x92120/x260911-002-KalasinEngineering/02_Electrical_and_eDrawing/05_Instrument_Manuals/CS-DS-01 pH Analyzer/Installation.jpg

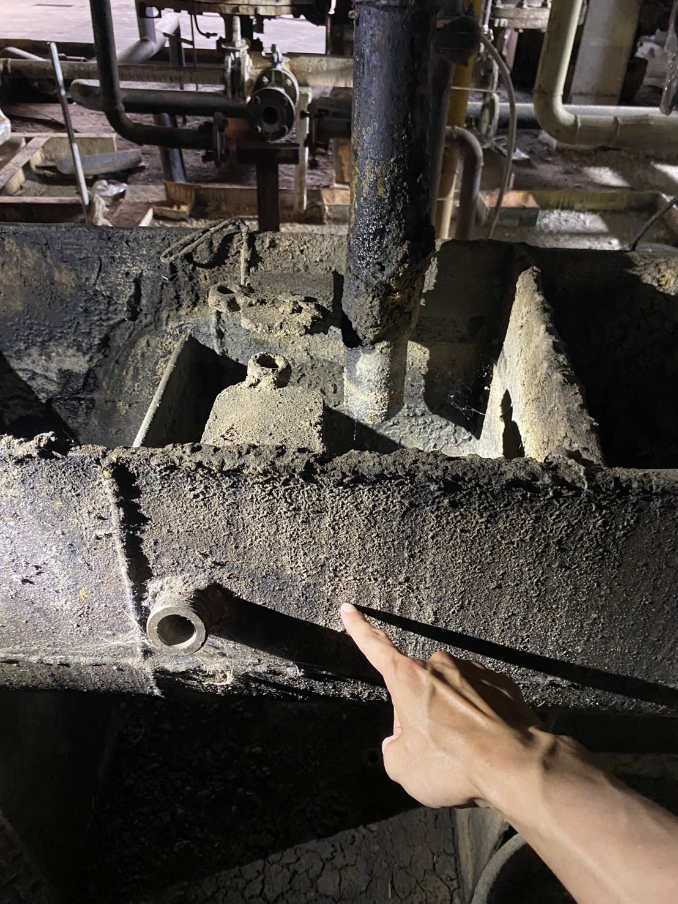
02_Electrical_and_eDrawing/05_Instrument_Manuals/CS-DS-01 pH Analyzer/Installation.jpg
