x92120/x260911-002-KalasinEngineering/02_Electrical_and_eDrawing/01_Source_Drawings_DWG/README.md

# 01_Source_Drawings_DWG — Original Vendor AutoCAD DWG Drawings

This directory contains the original vendor AutoCAD `.dwg` schematics, panel layouts, and wiring diagrams for the **Ingredion Kalasin Spray Dryer Plant** (Ref: `R5THS00138`).

---

## 📐 Source DWG File Inventory

| Filename | Description | Format |
| :--- | :--- | :---: |
| **`R5THS00138-000-SCD-10001_0.dwg`** | Master Control System Schematic Diagram | AutoCAD DWG |
| **`R5THS00138-FBR-LAY-20001_1.dwg`** | Silo Panel General Layout & Bill of Materials (BOM Rev 0) | AutoCAD DWG |
| **`R5THS00138-FBR-WIR-20001_3.dwg`** | Silo Panel Electrical Wiring Layout Diagram | AutoCAD DWG |
| **`R5THS00138-FBR-WIR-20001_3_recover.dwg`** | Recovered Backup Copy of Electrical Wiring Layout | AutoCAD DWG |

---

## 📌 Usage & Engineering Context

These drawings serve as the baseline source drawings provided by the vendor. They were used to extract wire numbers, device tags, terminal assignments, and panel layouts that feed into the automated DXF generation tools located in `04_Automation_Scripts`.
