x92120/x260911-002-KalasinEngineering/02_Electrical_and_eDrawing/03_CAD_Exports_DXF_SVG/README.md

# 03_CAD_Exports_DXF_SVG — Categorized DXF & SVG Drawing Deliverables

This directory contains categorized, production-grade AutoCAD DXF and SVG engineering drawing deliverables for the **Ingredion Kalasin Spray Dryer Plant**.

---

## 📁 Directory Layout & Sub-Module README Links

```text
03_CAD_Exports_DXF_SVG/
├── DI_Slot_Drawings/                     # 15 Digital Input (1756-IB32) Wiring Diagrams (One Slot per DXF)
│   └── README.md
├── DO_Slot_Drawings/                     # 9 Digital Output (1756-OB32 with SPDT Relay) Wiring Diagrams
│   └── README.md
├── IS_Barriers_CAD/                      # Pepperl+Fuchs Intrinsically Safe (IS) Barrier Schematics (DXF)
│   └── README.md
├── 01_PLC_IO_Wiring_DXF/                 # 40 Modular PLC I/O Schematics (KAL-JC-WIR-*)
├── 02_Instrument_Typical_DXF/            # 26 Instrument Hookup & Installation Typicals (KAL-JC-TYP-*)
├── 03_MCC_Panel_Layout/                  # 14 MCC Motor Control Center Panel Layouts (DXF + SVG)
├── 04_System_Architecture_CAD/           # 4 System & Network Architecture CAD Schematics
└── 05_SVG_Vector_Sheets/                 # 73 High-Fidelity SVG Presentation & Web Review Sheets
```

---

## 📊 Summary Breakdown

| Subfolder | Count | Format | Primary Content |
| :--- | :---: | :---: | :--- |
| **[DI_Slot_Drawings/](file:///e:/xApp-01/x260911-002-KalasinEngineering/02_Electrical_and_eDrawing/03_CAD_Exports_DXF_SVG/DI_Slot_Drawings/README.md)** | 15 | `.dxf` | Digital Input (1756-IB32) single-slot wiring schematics |
| **[DO_Slot_Drawings/](file:///e:/xApp-01/x260911-002-KalasinEngineering/02_Electrical_and_eDrawing/03_CAD_Exports_DXF_SVG/DO_Slot_Drawings/README.md)** | 9 | `.dxf` | Digital Output (1756-OB32 + Relay) single-slot wiring schematics |
| **[IS_Barriers_CAD/](file:///e:/xApp-01/x260911-002-KalasinEngineering/02_Electrical_and_eDrawing/03_CAD_Exports_DXF_SVG/IS_Barriers_CAD/README.md)** | 3 | `.dxf` | Pepperl+Fuchs K-System IS Barrier wiring diagrams |
| **01_PLC_IO_Wiring_DXF/** | 40 | `.dxf` | Full ControlLogix 1756 I/O wiring sheets (`KAL-JC-WIR-*`) |
| **02_Instrument_Typical_DXF/** | 26 | `.dxf` | Field instrument installation hookup drawings (`KAL-JC-TYP-*`) |
| **03_MCC_Panel_Layout/** | 14 | `.dxf`, `.svg` | Front elevation, internal GA, and panel layout sheets M1–M4 |
| **04_System_Architecture_CAD/** | 4 | `.dxf`, `.svg`, `.pdf` | Chassis C1–C8 slot-to-JB destination architecture |
| **05_SVG_Vector_Sheets/** | 73 | `.svg` | High-fidelity vector graphical presentation sheets |
