x92120/x260911-002-KalasinEngineering/03_IO_Lists_and_Schedules/IO_List-Bak/README.md

# IO_List-Bak — Historical Revisions & Master Excel Archives

This directory serves as the engineering archive for master Excel workbooks, tag revision history, change comparison audits, and printable PDF schedules for the **Ingredion Kalasin Spray Dryer Plant**.

---

## 📁 Key Deliverables & Historical Archives

### Master Reports & Workbooks
* **`Destination_IO_List_Master_Report.pdf`**: 82-Page master destination schedule (Print-ready PDF).
* **`Destination_IO_List_Master_Report.xlsx`**: Master 17-tab destination workbook.
* **`Chassis_and_Slot_IO_Source_Destination_Report.pdf`**: 99-Page master chassis & slot vector schedule.
* **`Chassis_IO_List_Per_Slot_Report.xlsx`**: Master 48-tab per-slot workbook.
* **`Instrument_IO_Mapping_with_Models_and_Cables.xlsx`**: Master instrument-to-cable schedule.
* **`IO_List_Sorted_by_Chassis_Slot.xlsx`**: Master hardware allocation sorted by chassis/slot.

### Revision Audits & Checklists
* **`IO_Comparison_Report_Tag35_vs_Dev36.xlsx`**: Tag audit and change verification report comparing Tag35 vs Dev36 releases.
* **`IO Check List.xlsx`** & **`IO Check List-1.xlsx`**: Quality assurance check sheets.
* **`Tags list PLC.xlsx`** & **`Tags list PLC-r02.xlsx`**: ControlLogix PLC tag databases.
* **`IO_List_xDev-R01-Tag35-1.xlsx` .. `Tag35-7.xlsx`**: Historical revision snapshots 1 through 7.
