x92120/x260911-002-KalasinEngineering/Datasheet/PF/README.md

# Datasheet/PF — Pepperl+Fuchs IS Barrier Technical Datasheets & DXF Page Exports

This folder contains official Pepperl+Fuchs K-System Intrinsically Safe (IS) Barrier technical datasheets in PDF format, alongside page-by-page converted AutoCAD `.dxf` CAD drawings.

---

## 📁 Document & DXF Register

| P+F Part No. | Model / Device Name | PDF Datasheet | Converted Master DXF | Converted DXF Page Files |
| :---: | :--- | :--- | :--- | :--- |
| **216711** | **HiC2821** Switch Amplifier (DI) | `216711_eng.pdf` | `PF_216711_HiC2821_DI_Master_All_Pages.dxf` | `PF_216711_HiC2821_DI_Page_01..05.dxf` |
| **233883** | **HiC2871** Solenoid Driver (DO) | `233883_eng.pdf` | `PF_233883_HiC2871_DO_Master_All_Pages.dxf` | `PF_233883_HiC2871_DO_Page_01..04.dxf` |
| **260436** | **HiCTB16** 16-Slot Motherboard | `260436_eng.pdf` | `PF_260436_HiCTB16_Master_All_Pages.dxf` | `PF_260436_HiCTB16_Page_01..05.dxf` |
| **321423** | **HiC2025** SMART Tx Supply (AI) | `321423_eng.pdf` | `PF_321423_HiC2025_AI_Master_All_Pages.dxf` | `PF_321423_HiC2025_AI_Page_01..05.dxf` |

---

## ⚙️ Conversion Utility

These DXF page drawings were rendered automatically from PDF datasheets using `04_Automation_Scripts/convert_pf_datasheet_to_dxf.py`.
