x92120/x260911-002-KalasinEngineering/02_Electrical_and_eDrawing/03_CAD_Exports_DXF_SVG/DI_Slot_Drawings/README.md

# DI_Slot_Drawings — Digital Input Slot CAD Drawings

This folder contains 15 individual AutoCAD `.dxf` wiring diagrams for ControlLogix 1756-IB32 32-Point 24VDC Digital Input modules.

---

## 📁 Drawing Inventory (15 DXF Files)

* `C1S4_DI_Wiring_Diagram.dxf` — Chassis 1, Slot 4 (1756-IB32)
* `C1S5_DI_Wiring_Diagram.dxf` — Chassis 1, Slot 5 (1756-IB32)
* `C1S6_DI_Wiring_Diagram.dxf` — Chassis 1, Slot 6 (1756-IB32)
* `C1S7_DI_Wiring_Diagram.dxf` — Chassis 1, Slot 7 (1756-IB32)
* `C2S1_DI_Wiring_Diagram.dxf` — Chassis 2, Slot 1 (1756-IB32)
* `C2S2_DI_Wiring_Diagram.dxf` — Chassis 2, Slot 2 (1756-IB32)
* `C2S3_DI_Wiring_Diagram.dxf` — Chassis 2, Slot 3 (1756-IB32)
* `C2S4_DI_Wiring_Diagram.dxf` — Chassis 2, Slot 4 (1756-IB32)
* `C2S5_DI_Wiring_Diagram.dxf` — Chassis 2, Slot 5 (1756-IB32)
* `C3S1_DI_Wiring_Diagram.dxf` — Chassis 3, Slot 1 (1756-IB32)
* `C3S2_DI_Wiring_Diagram.dxf` — Chassis 3, Slot 2 (1756-IB32)
* `C3S3_DI_Wiring_Diagram.dxf` — Chassis 3, Slot 3 (1756-IB32)
* `C4S1_DI_Wiring_Diagram.dxf` — Chassis 4, Slot 1 (1756-IB32)
* `C4S2_DI_Wiring_Diagram.dxf` — Chassis 4, Slot 2 (1756-IB32)
* `C4S3_DI_Wiring_Diagram.dxf` — Chassis 4, Slot 3 (1756-IB32)

---

## ⚙️ Technical Details

* **Hardware**: Rockwell Automation 1756-IB32 (36-Pin RTB).
* **Generation Script**: `04_Automation_Scripts/generate_di_slot_dxf_drawings.py`.
* **Template**: `eDrawingTemplate/template_DI-r02.dxf`.
