x92120/x260911-002-KalasinEngineering/02_Electrical_and_eDrawing/03_CAD_Exports_DXF_SVG/DO_Slot_Drawings/README.md

# DO_Slot_Drawings — Digital Output Slot CAD Drawings

This folder contains 9 individual AutoCAD `.dxf` wiring diagrams for ControlLogix 1756-OB32 32-Point 24VDC Digital Output modules (interfaced with SPDT interposing relays).

---

## 📁 Drawing Inventory (9 DXF Files)

* `C1S8_DO_Wiring_Diagram.dxf` — Chassis 1, Slot 8 (1756-OB32)
* `C1S9_DO_Wiring_Diagram.dxf` — Chassis 1, Slot 9 (1756-OB32)
* `C2S6_DO_Wiring_Diagram.dxf` — Chassis 2, Slot 6 (1756-OB32)
* `C2S7_DO_Wiring_Diagram.dxf` — Chassis 2, Slot 7 (1756-OB32)
* `C2S8_DO_Wiring_Diagram.dxf` — Chassis 2, Slot 8 (1756-OB32)
* `C3S4_DO_Wiring_Diagram.dxf` — Chassis 3, Slot 4 (1756-OB32)
* `C3S5_DO_Wiring_Diagram.dxf` — Chassis 3, Slot 5 (1756-OB32)
* `C4S4_DO_Wiring_Diagram.dxf` — Chassis 4, Slot 4 (1756-OB32)
* `C5S3_DO_Wiring_Diagram.dxf` — Chassis 5, Slot 3 (1756-OB32)

---

## ⚙️ Technical Details

* **Hardware**: Rockwell Automation 1756-OB32 with Finder / Phoenix Contact 24VDC SPDT Interposing Relays.
* **Generation Script**: `04_Automation_Scripts/generate_do_slot_dxf_drawings.py`.
* **Template**: `eDrawingTemplate/template_DO-r02.dxf`.
