x92120/x260911-002-KalasinEngineering/Panel_Layout/00_Panel_Layout_Master_Index.md

# Junction Box Panel Layout Drawings Master Register

**Project**: Sprint 18K TPA Spray Dryer / Jet Cooker  
**Client**: Ingredion (Thailand) Co., Ltd.  
**Contractor**: Kalasin Engineering Co., Ltd.  
**Source Directory**: `02_Electrical_and_eDrawing/02_ePlan_Exports/SPRINT 18K SPRAY DRYER`  
**Target Folder**: [`Panel_Layout`](file:///Users/x92120/xApp-001/x260911-002-KalasinEngineering/Panel_Layout)  

---

## 1. Junction Box Panel Layout Drawings (All 14 Enclosures)

| Sheet # | Junction Box ID | Enclosure Service & Location | Panel Layout DXF File | Original Sheet File | File Size |
| :---: | :--- | :--- | :--- | :--- | :---: |
| **10** | **RIO-Area 200** | Slurry Prep Remote I/O Marshalling Panel | [`Panel_Layout_RIO-Area_200.dxf`](file:///Users/x92120/xApp-001/x260911-002-KalasinEngineering/Panel_Layout/Panel_Layout_RIO-Area_200.dxf) | [`Sheet_10_RIO-Area_200_Panel_Layout.dxf`](file:///Users/x92120/xApp-001/x260911-002-KalasinEngineering/Panel_Layout/Sheet_10_RIO-Area_200_Panel_Layout.dxf) | 22.8 MB |
| **12** | **JB-401** | Infeed 2nd Floor Junction Box | [`Panel_Layout_JB-401.dxf`](file:///Users/x92120/xApp-001/x260911-002-KalasinEngineering/Panel_Layout/Panel_Layout_JB-401.dxf) | [`Sheet_12_JB-401_Panel_Layout.dxf`](file:///Users/x92120/xApp-001/x260911-002-KalasinEngineering/Panel_Layout/Sheet_12_JB-401_Panel_Layout.dxf) | 17.1 MB |
| **13** | **JB-402** | Infeed Ground Floor Junction Box | [`Panel_Layout_JB-402.dxf`](file:///Users/x92120/xApp-001/x260911-002-KalasinEngineering/Panel_Layout/Panel_Layout_JB-402.dxf) | [`Sheet_13_JB-402_Panel_Layout.dxf`](file:///Users/x92120/xApp-001/x260911-002-KalasinEngineering/Panel_Layout/Sheet_13_JB-402_Panel_Layout.dxf) | 8.6 MB |
| **14** | **JB-612** | Spray Dryer 3rd Floor Process Deck | [`Panel_Layout_JB-612.dxf`](file:///Users/x92120/xApp-001/x260911-002-KalasinEngineering/Panel_Layout/Panel_Layout_JB-612.dxf) | [`Sheet_14_JB-612_Panel_Layout.dxf`](file:///Users/x92120/xApp-001/x260911-002-KalasinEngineering/Panel_Layout/Sheet_14_JB-612_Panel_Layout.dxf) | 8.6 MB |
| **15** | **JB-618** | Exhaust Cyclone & Baghouse Deck | [`Panel_Layout_JB-618.dxf`](file:///Users/x92120/xApp-001/x260911-002-KalasinEngineering/Panel_Layout/Panel_Layout_JB-618.dxf) | [`Sheet_15_JB-618_Panel_Layout.dxf`](file:///Users/x92120/xApp-001/x260911-002-KalasinEngineering/Panel_Layout/Sheet_15_JB-618_Panel_Layout.dxf) | 6.9 MB |
| **16** | **IS-JB-612** | Intrinsically Safe Ex Deck (3rd Floor) | [`Panel_Layout_IS-JB-612.dxf`](file:///Users/x92120/xApp-001/x260911-002-KalasinEngineering/Panel_Layout/Panel_Layout_IS-JB-612.dxf) | [`Sheet_16_IS-JB-612_Panel_Layout.dxf`](file:///Users/x92120/xApp-001/x260911-002-KalasinEngineering/Panel_Layout/Sheet_16_IS-JB-612_Panel_Layout.dxf) | 3.6 MB |
| **17** | **IS-JB-618** | Intrinsically Safe Ex Cyclone Deck | [`Panel_Layout_IS-JB-618.dxf`](file:///Users/x92120/xApp-001/x260911-002-KalasinEngineering/Panel_Layout/Panel_Layout_IS-JB-618.dxf) | [`Sheet_17_IS-JB-618_Panel_Layout.dxf`](file:///Users/x92120/xApp-001/x260911-002-KalasinEngineering/Panel_Layout/Sheet_17_IS-JB-618_Panel_Layout.dxf) | 5.6 MB |
| **18** | **JB-601** | Feed Prep & Rotary Atomizer Deck | [`Panel_Layout_JB-601.dxf`](file:///Users/x92120/xApp-001/x260911-002-KalasinEngineering/Panel_Layout/Panel_Layout_JB-601.dxf) | [`Sheet_18_JB-601_Panel_Layout.dxf`](file:///Users/x92120/xApp-001/x260911-002-KalasinEngineering/Panel_Layout/Sheet_18_JB-601_Panel_Layout.dxf) | 11.1 MB |
| **19** | **JB-602** | Spray Dryer Chamber Tower | [`Panel_Layout_JB-602.dxf`](file:///Users/x92120/xApp-001/x260911-002-KalasinEngineering/Panel_Layout/Panel_Layout_JB-602.dxf) | [`Sheet_19_JB-602_Panel_Layout.dxf`](file:///Users/x92120/xApp-001/x260911-002-KalasinEngineering/Panel_Layout/Sheet_19_JB-602_Panel_Layout.dxf) | 15.4 MB |
| **20** | **JB-606** | Gas Burner & Process Air Heater Area | [`Panel_Layout_JB-606.dxf`](file:///Users/x92120/xApp-001/x260911-002-KalasinEngineering/Panel_Layout/Panel_Layout_JB-606.dxf) | [`Sheet_20_JB-606_Panel_Layout.dxf`](file:///Users/x92120/xApp-001/x260911-002-KalasinEngineering/Panel_Layout/Sheet_20_JB-606_Panel_Layout.dxf) | 2.2 MB |
| **21** | **JB-607** | Jet Cooker & Flash Tank Area | [`Panel_Layout_JB-607.dxf`](file:///Users/x92120/xApp-001/x260911-002-KalasinEngineering/Panel_Layout/Panel_Layout_JB-607.dxf) | [`Sheet_21_JB-607_Panel_Layout.dxf`](file:///Users/x92120/xApp-001/x260911-002-KalasinEngineering/Panel_Layout/Sheet_21_JB-607_Panel_Layout.dxf) | 34.2 MB |
| **22** | **JB-608** | Chemical Dosing & Additives Area | [`Panel_Layout_JB-608.dxf`](file:///Users/x92120/xApp-001/x260911-002-KalasinEngineering/Panel_Layout/Panel_Layout_JB-608.dxf) | [`Sheet_22_JB-608_Panel_Layout.dxf`](file:///Users/x92120/xApp-001/x260911-002-KalasinEngineering/Panel_Layout/Sheet_22_JB-608_Panel_Layout.dxf) | 0.88 MB |
| **23** | **IS-JB-603** | Intrinsically Safe Ex Tower Top Area | [`Panel_Layout_IS-JB-603.dxf`](file:///Users/x92120/xApp-001/x260911-002-KalasinEngineering/Panel_Layout/Panel_Layout_IS-JB-603.dxf) | [`Sheet_23_IS-JB-603_Panel_Layout.dxf`](file:///Users/x92120/xApp-001/x260911-002-KalasinEngineering/Panel_Layout/Sheet_23_IS-JB-603_Panel_Layout.dxf) | 5.2 MB |
| **24** | **IS-JB-608** | Intrinsically Safe Ex Flash Area | [`Panel_Layout_IS-JB-608.dxf`](file:///Users/x92120/xApp-001/x260911-002-KalasinEngineering/Panel_Layout/Panel_Layout_IS-JB-608.dxf) | [`Sheet_24_IS-JB-608_Panel_Layout.dxf`](file:///Users/x92120/xApp-001/x260911-002-KalasinEngineering/Panel_Layout/Sheet_24_IS-JB-608_Panel_Layout.dxf) | 3.9 MB |

---

## 2. Supporting Enclosure Drawings & BOM in `Panel_Legends_and_BOM/`

- **Sheet 09**: [`Sheet_09_Panel_Dimensions.dxf`](file:///Users/x92120/xApp-001/x260911-002-KalasinEngineering/Panel_Layout/Panel_Legends_and_BOM/Sheet_09_Panel_Dimensions.dxf) — Overall enclosure dimensions, mounting hole centers, and gland plate cutouts.
- **Sheet 11**: [`Sheet_11_RIO-Area_200_Panel_Legend.dxf`](file:///Users/x92120/xApp-001/x260911-002-KalasinEngineering/Panel_Layout/Panel_Legends_and_BOM/Sheet_11_RIO-Area_200_Panel_Legend.dxf) — Equipment legend and parts list for RIO-200.
- **Sheet 25**: [`Sheet_25_Summarized_Parts_List_BOM.dxf`](file:///Users/x92120/xApp-001/x260911-002-KalasinEngineering/Panel_Layout/Panel_Legends_and_BOM/Sheet_25_Summarized_Parts_List_BOM.dxf) — Complete Bill of Materials (BOM) for DIN rails, wire ducts, terminals, and grounding accessories.
- **Sheets 26 to 38**: `Sheet_26_Panel_Legend.dxf` through `Sheet_38_Panel_Legend.dxf` — Component legends and terminal block schedules for individual Junction Boxes.

---

## 3. Updated TAMCO CES-STL Enclosure Layouts

| Drawing Reference | Target Enclosure Model | Outer Dimensions (W x H x D) | Terminal Quantity & Type | Output Files |
| :--- | :--- | :--- | :--- | :--- |
| **IS-JB-603 / IS-JB-003** | **TAMCO CES-STL-02** (IP55 Stainless Steel) | **300 x 450 x 150 mm** | **30x Double-Level** (Phoenix Contact 3210567 = 60 wire terminations) | • [`PanelLayout_IS-JB-003-CES-STL.dxf`](file:///Users/x92120/xApp-001/x260911-002-KalasinEngineering/Panel_Layout/PanelLayout_IS-JB-003-CES-STL.dxf)<br>• [`PanelLayout_IS-JB-003-CES-STL.pdf`](file:///Users/x92120/xApp-001/x260911-002-KalasinEngineering/Panel_Layout/PanelLayout_IS-JB-003-CES-STL.pdf)<br>• [`PanelLayout_IS-JB-003-CES-STL.png`](file:///Users/x92120/xApp-001/x260911-002-KalasinEngineering/Panel_Layout/PanelLayout_IS-JB-003-CES-STL.png) |

> **Engineering Sizing Justification for IS-JB-603 (CES-STL-02)**:
> 1. **Terminal Strip Length**: 30 double-level terminals (5.2 mm each) + 2 end brackets + PE grounding clamp require ~185 mm mounting width.
> 2. **Wiring Ducts & Bending Radius**: Moving from original 200x300x150 mm to **300x450x150 mm** provides 50 mm clearance on each side for slotted wire ducts and generous 100+ mm top/bottom wire bending radius for 32 field instrument cables (16 DI + 16 AI).
> 3. **Intrinsically Safe (IS) Separation**: Meets IEC 60079-11 / IEC 60079-14 spacing requirements between IS terminal blocks and metallic enclosure sidewalls.
> 4. **Standardization**: Perfectly matches existing plant junction boxes `JB-402` and `IS-JB-618` (300 x 450 x 150 mm), streamlining spare parts and mounting brackets.

---

## 4. TAMCO Manufacturer Enclosure Libraries in `Panel_Layout/`

### A. TAMCO CES Stainless Series (CES-STL IP55)
- **Path**: [`TAMCO_CES_Stainless_Series/`](file:///Users/x92120/xApp-001/x260911-002-KalasinEngineering/Panel_Layout/TAMCO_CES_Stainless_Series/)
- **Documentation**: [`00_TAMCO_CES_Stainless_Series_Index.md`](file:///Users/x92120/xApp-001/x260911-002-KalasinEngineering/Panel_Layout/TAMCO_CES_Stainless_Series/00_TAMCO_CES_Stainless_Series_Index.md)
- **Excel Schedule**: [`TAMCO_CES_Stainless_Series_Catalog.xlsx`](file:///Users/x92120/xApp-001/x260911-002-KalasinEngineering/Panel_Layout/TAMCO_CES_Stainless_Series/TAMCO_CES_Stainless_Series_Catalog.xlsx)
- **Scope**: 14 Models (CES-STL-01 through 14) with full PDF datasheets, DWG CAD layouts, and DXF conversions.

### B. TAMCO CRS Series (CRS IP65 Compact Outdoor with Rain Canopy)
- **Path**: [`TAMCO_CRS_Series/`](file:///Users/x92120/xApp-001/x260911-002-KalasinEngineering/Panel_Layout/TAMCO_CRS_Series/)
- **Documentation**: [`00_TAMCO_CRS_Series_Index.md`](file:///Users/x92120/xApp-001/x260911-002-KalasinEngineering/Panel_Layout/TAMCO_CRS_Series/00_TAMCO_CRS_Series_Index.md)
- **Excel Schedule**: [`TAMCO_CRS_Series_Catalog.xlsx`](file:///Users/x92120/xApp-001/x260911-002-KalasinEngineering/Panel_Layout/TAMCO_CRS_Series/TAMCO_CRS_Series_Catalog.xlsx)
- **Scope**: 5 Models (CRS-01 through CRS-05) with full PDF datasheets, DWG CAD layouts, and DXF conversions.
