x92120/x260911-002-KalasinEngineering/Panel_Layout/TAMCO_CES_Stainless_Series/00_TAMCO_CES_Stainless_Series_Index.md

# TAMCO CES Stainless Series (CES-STL IP55) Enclosure Package

**Source URL**: [TAMCO Product Page](https://www.tamco.co.th/article/68afdff9421c340013316f25/content69f9b9c37569600013578f7868a3e55d24938a00131fc0fa_LP/69f9b9c37569600013578f78)  
**Manufacturer**: TAMCO (Thailand) Co., Ltd.  
**Series Designation**: CES-STL Stainless Steel Electrical Enclosure (Wall-Mount)  
**Ingress Protection Rating**: IP55  
**Directory Path**: [`Panel_Layout/TAMCO_CES_Stainless_Series/`](file:///Users/x92120/xApp-001/x260911-002-KalasinEngineering/Panel_Layout/TAMCO_CES_Stainless_Series/)

---

## 1. Product Overview

The **TAMCO CES Stainless Series (CES-STL)** is engineered for sanitary food & beverage, dairy, chemical, and demanding outdoor industrial environments where superior corrosion resistance and hygiene are required.

- **Material**: Stainless Steel Sheet AISI 304 (optional AISI 316L)
- **Protection**: IP55 Ingress Protection against dust and water jets
- **Sealing**: Continuous Polyurethane (PU) seamless gasket
- **Latching**: Stainless steel quarter-turn locking mechanism
- **Gland Plate / Flange**: Detachable bottom gland plate with gasket
- **Mounting**: Wall mounting brackets / direct rear enclosure mounting
- **Internal Plate**: Galvanized sheet steel sub-panel / mounting plate included

TAMCO CES-STL Enclosure

---

## 2. Master Model Dimension & File Matrix

| Item | Model Code | W (mm) | H (mm) | D (mm) | Datasheet (PDF) | CAD Drawing (DWG) | CAD Drawing (DXF) |
| :---: | :--- | :---: | :---: | :---: | :--- | :--- | :--- |
| **01** | **CES-STL-01** | 280 | 350 | 150 | [Datasheet_CES-STL-01.pdf](file:///Users/x92120/xApp-001/x260911-002-KalasinEngineering/Panel_Layout/TAMCO_CES_Stainless_Series/Datasheets_PDF/Datasheet_CES-STL-01.pdf) | [CES-STL-01-Layout.dwg](file:///Users/x92120/xApp-001/x260911-002-KalasinEngineering/Panel_Layout/TAMCO_CES_Stainless_Series/Drawings_DWG/CES-STL-01-Layout.dwg) | [CES-STL-01-Layout.dxf](file:///Users/x92120/xApp-001/x260911-002-KalasinEngineering/Panel_Layout/TAMCO_CES_Stainless_Series/Drawings_DXF/CES-STL-01-Layout.dxf) |
| **02** | **CES-STL-02** | 300 | 450 | 150 | [Datasheet_CES-STL-02.pdf](file:///Users/x92120/xApp-001/x260911-002-KalasinEngineering/Panel_Layout/TAMCO_CES_Stainless_Series/Datasheets_PDF/Datasheet_CES-STL-02.pdf) | [CES-STL-02-Layout.dwg](file:///Users/x92120/xApp-001/x260911-002-KalasinEngineering/Panel_Layout/TAMCO_CES_Stainless_Series/Drawings_DWG/CES-STL-02-Layout.dwg) | [CES-STL-02-Layout.dxf](file:///Users/x92120/xApp-001/x260911-002-KalasinEngineering/Panel_Layout/TAMCO_CES_Stainless_Series/Drawings_DXF/CES-STL-02-Layout.dxf) |
| **03** | **CES-STL-03** | 300 | 450 | 200 | [Datasheet_CES-STL-03.pdf](file:///Users/x92120/xApp-001/x260911-002-KalasinEngineering/Panel_Layout/TAMCO_CES_Stainless_Series/Datasheets_PDF/Datasheet_CES-STL-03.pdf) | [CES-STL-03-Layout.dwg](file:///Users/x92120/xApp-001/x260911-002-KalasinEngineering/Panel_Layout/TAMCO_CES_Stainless_Series/Drawings_DWG/CES-STL-03-Layout.dwg) | [CES-STL-03-Layout.dxf](file:///Users/x92120/xApp-001/x260911-002-KalasinEngineering/Panel_Layout/TAMCO_CES_Stainless_Series/Drawings_DXF/CES-STL-03-Layout.dxf) |
| **04** | **CES-STL-04** | 350 | 450 | 200 | [Datasheet_CES-STL-04.pdf](file:///Users/x92120/xApp-001/x260911-002-KalasinEngineering/Panel_Layout/TAMCO_CES_Stainless_Series/Datasheets_PDF/Datasheet_CES-STL-04.pdf) | [CES-STL-04-Layout.dwg](file:///Users/x92120/xApp-001/x260911-002-KalasinEngineering/Panel_Layout/TAMCO_CES_Stainless_Series/Drawings_DWG/CES-STL-04-Layout.dwg) | [CES-STL-04-Layout.dxf](file:///Users/x92120/xApp-001/x260911-002-KalasinEngineering/Panel_Layout/TAMCO_CES_Stainless_Series/Drawings_DXF/CES-STL-04-Layout.dxf) |
| **05** | **CES-STL-05** | 350 | 500 | 200 | [Datasheet_CES-STL-05.pdf](file:///Users/x92120/xApp-001/x260911-002-KalasinEngineering/Panel_Layout/TAMCO_CES_Stainless_Series/Datasheets_PDF/Datasheet_CES-STL-05.pdf) | [CES-STL-05-Layout.dwg](file:///Users/x92120/xApp-001/x260911-002-KalasinEngineering/Panel_Layout/TAMCO_CES_Stainless_Series/Drawings_DWG/CES-STL-05-Layout.dwg) | [CES-STL-05-Layout.dxf](file:///Users/x92120/xApp-001/x260911-002-KalasinEngineering/Panel_Layout/TAMCO_CES_Stainless_Series/Drawings_DXF/CES-STL-05-Layout.dxf) |
| **06** | **CES-STL-06** | 400 | 500 | 200 | [Datasheet_CES-STL-06.pdf](file:///Users/x92120/xApp-001/x260911-002-KalasinEngineering/Panel_Layout/TAMCO_CES_Stainless_Series/Datasheets_PDF/Datasheet_CES-STL-06.pdf) | [CES-STL-06-Layout.dwg](file:///Users/x92120/xApp-001/x260911-002-KalasinEngineering/Panel_Layout/TAMCO_CES_Stainless_Series/Drawings_DWG/CES-STL-06-Layout.dwg) | [CES-STL-06-Layout.dxf](file:///Users/x92120/xApp-001/x260911-002-KalasinEngineering/Panel_Layout/TAMCO_CES_Stainless_Series/Drawings_DXF/CES-STL-06-Layout.dxf) |
| **07** | **CES-STL-07** | 450 | 600 | 250 | [Datasheet_CES-STL-07.pdf](file:///Users/x92120/xApp-001/x260911-002-KalasinEngineering/Panel_Layout/TAMCO_CES_Stainless_Series/Datasheets_PDF/Datasheet_CES-STL-07.pdf) | [CES-STL-07-Layout.dwg](file:///Users/x92120/xApp-001/x260911-002-KalasinEngineering/Panel_Layout/TAMCO_CES_Stainless_Series/Drawings_DWG/CES-STL-07-Layout.dwg) | [CES-STL-07-Layout.dxf](file:///Users/x92120/xApp-001/x260911-002-KalasinEngineering/Panel_Layout/TAMCO_CES_Stainless_Series/Drawings_DXF/CES-STL-07-Layout.dxf) |
| **08** | **CES-STL-08** | 500 | 600 | 250 | [Datasheet_CES-STL-08.pdf](file:///Users/x92120/xApp-001/x260911-002-KalasinEngineering/Panel_Layout/TAMCO_CES_Stainless_Series/Datasheets_PDF/Datasheet_CES-STL-08.pdf) | [CES-STL-08-Layout.dwg](file:///Users/x92120/xApp-001/x260911-002-KalasinEngineering/Panel_Layout/TAMCO_CES_Stainless_Series/Drawings_DWG/CES-STL-08-Layout.dwg) | [CES-STL-08-Layout.dxf](file:///Users/x92120/xApp-001/x260911-002-KalasinEngineering/Panel_Layout/TAMCO_CES_Stainless_Series/Drawings_DXF/CES-STL-08-Layout.dxf) |
| **09** | **CES-STL-09** | 550 | 700 | 250 | [Datasheet_CES-STL-09.pdf](file:///Users/x92120/xApp-001/x260911-002-KalasinEngineering/Panel_Layout/TAMCO_CES_Stainless_Series/Datasheets_PDF/Datasheet_CES-STL-09.pdf) | [CES-STL-09-Layout.dwg](file:///Users/x92120/xApp-001/x260911-002-KalasinEngineering/Panel_Layout/TAMCO_CES_Stainless_Series/Drawings_DWG/CES-STL-09-Layout.dwg) | [CES-STL-09-Layout.dxf](file:///Users/x92120/xApp-001/x260911-002-KalasinEngineering/Panel_Layout/TAMCO_CES_Stainless_Series/Drawings_DXF/CES-STL-09-Layout.dxf) |
| **10** | **CES-STL-10** | 630 | 750 | 250 | [Datasheet_CES-STL-10.pdf](file:///Users/x92120/xApp-001/x260911-002-KalasinEngineering/Panel_Layout/TAMCO_CES_Stainless_Series/Datasheets_PDF/Datasheet_CES-STL-10.pdf) | [CES-STL-10-Layout.dwg](file:///Users/x92120/xApp-001/x260911-002-KalasinEngineering/Panel_Layout/TAMCO_CES_Stainless_Series/Drawings_DWG/CES-STL-10-Layout.dwg) | [CES-STL-10-Layout.dxf](file:///Users/x92120/xApp-001/x260911-002-KalasinEngineering/Panel_Layout/TAMCO_CES_Stainless_Series/Drawings_DXF/CES-STL-10-Layout.dxf) |
| **11** | **CES-STL-11** | 630 | 900 | 250 | [Datasheet_CES-STL-11.pdf](file:///Users/x92120/xApp-001/x260911-002-KalasinEngineering/Panel_Layout/TAMCO_CES_Stainless_Series/Datasheets_PDF/Datasheet_CES-STL-11.pdf) | [CES-STL-11-Layout.dwg](file:///Users/x92120/xApp-001/x260911-002-KalasinEngineering/Panel_Layout/TAMCO_CES_Stainless_Series/Drawings_DWG/CES-STL-11-Layout.dwg) | [CES-STL-11-Layout.dxf](file:///Users/x92120/xApp-001/x260911-002-KalasinEngineering/Panel_Layout/TAMCO_CES_Stainless_Series/Drawings_DXF/CES-STL-11-Layout.dxf) |
| **12** | **CES-STL-12** | 700 | 1100 | 250 | [Datasheet_CES-STL-12.pdf](file:///Users/x92120/xApp-001/x260911-002-KalasinEngineering/Panel_Layout/TAMCO_CES_Stainless_Series/Datasheets_PDF/Datasheet_CES-STL-12.pdf) | [CES-STL-12-Layout.dwg](file:///Users/x92120/xApp-001/x260911-002-KalasinEngineering/Panel_Layout/TAMCO_CES_Stainless_Series/Drawings_DWG/CES-STL-12-Layout.dwg) | [CES-STL-12-Layout.dxf](file:///Users/x92120/xApp-001/x260911-002-KalasinEngineering/Panel_Layout/TAMCO_CES_Stainless_Series/Drawings_DXF/CES-STL-12-Layout.dxf) |
| **13** | **CES-STL-13** | 800 | 1200 | 300 | [Datasheet_CES-STL-13.pdf](file:///Users/x92120/xApp-001/x260911-002-KalasinEngineering/Panel_Layout/TAMCO_CES_Stainless_Series/Datasheets_PDF/Datasheet_CES-STL-13.pdf) | [CES-STL-13-Layout.dwg](file:///Users/x92120/xApp-001/x260911-002-KalasinEngineering/Panel_Layout/TAMCO_CES_Stainless_Series/Drawings_DWG/CES-STL-13-Layout.dwg) | [CES-STL-13-Layout.dxf](file:///Users/x92120/xApp-001/x260911-002-KalasinEngineering/Panel_Layout/TAMCO_CES_Stainless_Series/Drawings_DWG/CES-STL-13-Layout.dxf) |
| **14** | **CES-STL-14** | 900 | 1200 | 300 | [Datasheet_CES-STL-14.pdf](file:///Users/x92120/xApp-001/x260911-002-KalasinEngineering/Panel_Layout/TAMCO_CES_Stainless_Series/Datasheets_PDF/Datasheet_CES-STL-14.pdf) | [CES-STL-14-Layout.dwg](file:///Users/x92120/xApp-001/x260911-002-KalasinEngineering/Panel_Layout/TAMCO_CES_Stainless_Series/Drawings_DWG/CES-STL-14-Layout.dwg) | [CES-STL-14-Layout.dxf](file:///Users/x92120/xApp-001/x260911-002-KalasinEngineering/Panel_Layout/TAMCO_CES_Stainless_Series/Drawings_DWG/CES-STL-14-Layout.dxf) |

---

## 3. Directory Structure

```text
Panel_Layout/TAMCO_CES_Stainless_Series/
├── 00_TAMCO_CES_Stainless_Series_Index.md
├── TAMCO_CES_Stainless_Series_Catalog.xlsx
├── Datasheets_PDF/
│   ├── Datasheet_CES-STL-01.pdf
│   ├── Datasheet_CES-STL-02.pdf
│   ├── ...
│   └── Datasheet_CES-STL-14.pdf
├── Drawings_DWG/
│   ├── CES-STL-01-Layout.dwg
│   ├── CES-STL-02-Layout.dwg
│   ├── ...
│   └── CES-STL-14-Layout.dwg
├── Drawings_DXF/
│   ├── CES-STL-01-Layout.dxf
│   ├── CES-STL-02-Layout.dxf
│   ├── ...
│   └── CES-STL-14-Layout.dxf
└── Product_Images/
    └── TAMCO_CES-STL_Enclosure.png
```
