x92120/x260911-002-KalasinEngineering/Panel_Layout/TAMCO_CRS_Series/00_TAMCO_CRS_Series_Index.md

# TAMCO CRS Series (CRS IP65 Compact Outdoor Enclosures with Integrated Canopy)

**Source URL**: [TAMCO CRS Series Product Page](https://www.tamco.co.th/%E0%B8%A3%E0%B8%B2%E0%B8%A2%E0%B8%A5%E0%B8%B0%E0%B9%80%E0%B8%AD%E0%B8%B5%E0%B8%A2%E0%B8%94/68afdff9421c340013316f25/CRS_Und_SERIES:!68a3e55d2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)  
**Manufacturer**: TAMCO (Thailand) Co., Ltd. / Thai Switchboard & Metal Work Co., Ltd.  
**Series Designation**: CRS Compact Outdoor Enclosure with Sloped Rain Canopy  
**Ingress Protection Rating**: IP65  
**Directory Path**: [`Panel_Layout/TAMCO_CRS_Series/`](file:///Users/x92120/xApp-001/x260911-002-KalasinEngineering/Panel_Layout/TAMCO_CRS_Series/)

---

## 1. Product Overview

The **TAMCO CRS Series** is designed specifically for harsh outdoor environments, outdoor process structures (such as Baghouse, Cyclone decks, and rooftop platforms), and washdown areas where rain, water runoff, and dust are present:

- **Integrated Sloped Rain Canopy**: Top rain shield prevents water pooling and direct dripping over the door gasket.
- **Protection**: IP65 Ingress Protection against water jets and heavy dust ingress.
- **Door Construction**: Formed concealed hinges with PU seamless gasket seal.
- **Latching**: Push-to-turn waterproof cam lock with key.
- **Gland Plate**: Detachable bottom gland plate with sealing gasket.
- **Mounting**: Wall mounting brackets / rear mounting holes.
- **Internal Plate**: Galvanized zinc-coated mounting sub-panel included.

TAMCO CRS Enclosure

---

## 2. Master Model Dimension & File Matrix

| Item | Model Code | W (mm) | H (mm) | D (mm) | Ingress Protection | Datasheet (PDF) | CAD Drawing (DWG) | CAD Drawing (DXF) |
| :---: | :--- | :---: | :---: | :---: | :---: | :--- | :--- | :--- |
| **01** | **CRS-01** | 280 | 405 | 150 | IP65 | [Datasheet_CRS-01.pdf](file:///Users/x92120/xApp-001/x260911-002-KalasinEngineering/Panel_Layout/TAMCO_CRS_Series/Datasheets_PDF/Datasheet_CRS-01.pdf) | [CRS-01-Layout.dwg](file:///Users/x92120/xApp-001/x260911-002-KalasinEngineering/Panel_Layout/TAMCO_CRS_Series/Drawings_DWG/CRS-01-Layout.dwg) | [CRS-01-Layout.dxf](file:///Users/x92120/xApp-001/x260911-002-KalasinEngineering/Panel_Layout/TAMCO_CRS_Series/Drawings_DXF/CRS-01-Layout.dxf) |
| **02** | **CRS-02** | 300 | 505 | 150 | IP65 | [Datasheet_CRS-02.pdf](file:///Users/x92120/xApp-001/x260911-002-KalasinEngineering/Panel_Layout/TAMCO_CRS_Series/Datasheets_PDF/Datasheet_CRS-02.pdf) | [CRS-02-Layout.dwg](file:///Users/x92120/xApp-001/x260911-002-KalasinEngineering/Panel_Layout/TAMCO_CRS_Series/Drawings_DWG/CRS-02-Layout.dwg) | [CRS-02-Layout.dxf](file:///Users/x92120/xApp-001/x260911-002-KalasinEngineering/Panel_Layout/TAMCO_CRS_Series/Drawings_DXF/CRS-02-Layout.dxf) |
| **03** | **CRS-03** | 300 | 505 | 200 | IP65 | [Datasheet_CRS-03.pdf](file:///Users/x92120/xApp-001/x260911-002-KalasinEngineering/Panel_Layout/TAMCO_CRS_Series/Datasheets_PDF/Datasheet_CRS-03.pdf) | [CRS-03-Layout.dwg](file:///Users/x92120/xApp-001/x260911-002-KalasinEngineering/Panel_Layout/TAMCO_CRS_Series/Drawings_DWG/CRS-03-Layout.dwg) | [CRS-03-Layout.dxf](file:///Users/x92120/xApp-001/x260911-002-KalasinEngineering/Panel_Layout/TAMCO_CRS_Series/Drawings_DXF/CRS-03-Layout.dxf) |
| **04** | **CRS-04** | 350 | 505 | 200 | IP65 | [Datasheet_CRS-04.pdf](file:///Users/x92120/xApp-001/x260911-002-KalasinEngineering/Panel_Layout/TAMCO_CRS_Series/Datasheets_PDF/Datasheet_CRS-04.pdf) | [CRS-04-Layout.dwg](file:///Users/x92120/xApp-001/x260911-002-KalasinEngineering/Panel_Layout/TAMCO_CRS_Series/Drawings_DWG/CRS-04-Layout.dwg) | [CRS-04-Layout.dxf](file:///Users/x92120/xApp-001/x260911-002-KalasinEngineering/Panel_Layout/TAMCO_CRS_Series/Drawings_DXF/CRS-04-Layout.dxf) |
| **05** | **CRS-05** | 350 | 555 | 200 | IP65 | [Datasheet_CRS-05.pdf](file:///Users/x92120/xApp-001/x260911-002-KalasinEngineering/Panel_Layout/TAMCO_CRS_Series/Datasheets_PDF/Datasheet_CRS-05.pdf) | [CRS-05-Layout.dwg](file:///Users/x92120/xApp-001/x260911-002-KalasinEngineering/Panel_Layout/TAMCO_CRS_Series/Drawings_DWG/CRS-05-Layout.dwg) | [CRS-05-Layout.dxf](file:///Users/x92120/xApp-001/x260911-002-KalasinEngineering/Panel_Layout/TAMCO_CRS_Series/Drawings_DXF/CRS-05-Layout.dxf) |

---

## 3. Directory Layout

```text
Panel_Layout/TAMCO_CRS_Series/
├── 00_TAMCO_CRS_Series_Index.md
├── TAMCO_CRS_Series_Catalog.xlsx
├── Datasheets_PDF/
│   ├── Datasheet_CRS-01.pdf
│   ├── Datasheet_CRS-02.pdf
│   ├── Datasheet_CRS-03.pdf
│   ├── Datasheet_CRS-04.pdf
│   └── Datasheet_CRS-05.pdf
├── Drawings_DWG/
│   ├── CRS-01-Layout.dwg
│   ├── CRS-02-Layout.dwg
│   ├── CRS-03-Layout.dwg
│   ├── CRS-04-Layout.dwg
│   └── CRS-05-Layout.dwg
├── Drawings_DXF/
│   ├── CRS-01-Layout.dxf
│   ├── CRS-02-Layout.dxf
│   ├── CRS-03-Layout.dxf
│   ├── CRS-04-Layout.dxf
│   └── CRS-05-Layout.dxf
└── Product_Images/
    └── TAMCO_CRS_Enclosure.png
```
