x92120/x260911-002-KalasinEngineering/02_Electrical_and_eDrawing/ePlanExport/SPRINT 18K SPRAY DRYER ELECTRICAL/ELECTRICAL_DRAWINGS_INDEX.md

# SPRINT 18K SPRAY DRYER ELECTRICAL DRAWINGS INDEX

**Source Directory:** `x900-eDrawing/ePlanExport/SPRINT 18K SPRAY DRYER ELECTRICAL`  
**Master Merged DXF File:** [`x260911-eDXF.dxf`](file:///e:/xApp-01/x260911-002-Kalasin-Process/x900-eDrawing/ePlanExport/SPRINT%2018K%20SPRAY%20DRYER%20ELECTRICAL/x260911-eDXF.dxf) | [`x260911-eDXF`](file:///e:/xApp-01/x260911-002-Kalasin-Process/x900-eDrawing/ePlanExport/SPRINT%2018K%20SPRAY%20DRYER%20ELECTRICAL/x260911-eDXF) (443 MB)  
**Total Drawing Files:** 39 Sheets  

| File | Sheet No. | Drawing / Page Title | Devices Count | Date | Designer |
|:---|:---:|:---|:---:|:---:|:---:|
| [1.dxf](file:///e:/xApp-01/x260911-002-Kalasin-Process/x900-eDrawing/ePlanExport/SPRINT 18K SPRAY DRYER ELECTRICAL/1.dxf) | **1** | Title page | 0 | 03/30/21 | EPL |
| [2.1.dxf](file:///e:/xApp-01/x260911-002-Kalasin-Process/x900-eDrawing/ePlanExport/SPRINT 18K SPRAY DRYER ELECTRICAL/2.1.dxf) | **2.1** | Table of contents : 33 - 38 | 0 | 09/20/26 | X9212 |
| [2.dxf](file:///e:/xApp-01/x260911-002-Kalasin-Process/x900-eDrawing/ePlanExport/SPRINT 18K SPRAY DRYER ELECTRICAL/2.dxf) | **2** | Table of contents : 1 - 32 | 0 | 09/20/26 | X9212 |
| [3.dxf](file:///e:/xApp-01/x260911-002-Kalasin-Process/x900-eDrawing/ePlanExport/SPRINT 18K SPRAY DRYER ELECTRICAL/3.dxf) | **3** | Power distribution | 18 | 08/10/26 | THUMWH |
| [4.dxf](file:///e:/xApp-01/x260911-002-Kalasin-Process/x900-eDrawing/ePlanExport/SPRINT 18K SPRAY DRYER ELECTRICAL/4.dxf) | **4** | Chassis 1 Slot 3 (Analog Input) | 1 | 09/01/26 | THUMWH |
| [5.dxf](file:///e:/xApp-01/x260911-002-Kalasin-Process/x900-eDrawing/ePlanExport/SPRINT 18K SPRAY DRYER ELECTRICAL/5.dxf) | **5** | Chassis 1 Slot 4 (Analog Input) | 1 | 09/01/26 | THUMWH |
| [6.dxf](file:///e:/xApp-01/x260911-002-Kalasin-Process/x900-eDrawing/ePlanExport/SPRINT 18K SPRAY DRYER ELECTRICAL/6.dxf) | **6** | Chassis 1 Slot 5 (Analog Input) | 1 | 08/25/26 | THUMWH |
| [7.dxf](file:///e:/xApp-01/x260911-002-Kalasin-Process/x900-eDrawing/ePlanExport/SPRINT 18K SPRAY DRYER ELECTRICAL/7.dxf) | **7** | Chassis 1 Slot 6 (Analog input) | 1 | 08/25/26 | THUMWH |
| [8.dxf](file:///e:/xApp-01/x260911-002-Kalasin-Process/x900-eDrawing/ePlanExport/SPRINT 18K SPRAY DRYER ELECTRICAL/8.dxf) | **8** | Chassis 1 Slot 7 (Analog input) | 1 | 08/25/26 | THUMWH |
| [9.dxf](file:///e:/xApp-01/x260911-002-Kalasin-Process/x900-eDrawing/ePlanExport/SPRINT 18K SPRAY DRYER ELECTRICAL/9.dxf) | **9** | Chassis 1 Slot 8 (Analog input) | 1 | 08/25/26 | THUMWH |
| [10.dxf](file:///e:/xApp-01/x260911-002-Kalasin-Process/x900-eDrawing/ePlanExport/SPRINT 18K SPRAY DRYER ELECTRICAL/10.dxf) | **10** | Chassis 1 Slot 9 (Analog input) | 1 | 08/25/26 | THUMWH |
| [11.dxf](file:///e:/xApp-01/x260911-002-Kalasin-Process/x900-eDrawing/ePlanExport/SPRINT 18K SPRAY DRYER ELECTRICAL/11.dxf) | **11** | Chassis 2 Slot 1 (Analog input) | 2 | 08/25/26 | THUMWH |
| [12.dxf](file:///e:/xApp-01/x260911-002-Kalasin-Process/x900-eDrawing/ePlanExport/SPRINT 18K SPRAY DRYER ELECTRICAL/12.dxf) | **12** | Chassis 2 Slot 2  (Analog Input) | 2 | 08/26/26 | THUMWH |
| [13.dxf](file:///e:/xApp-01/x260911-002-Kalasin-Process/x900-eDrawing/ePlanExport/SPRINT 18K SPRAY DRYER ELECTRICAL/13.dxf) | **13** | Chassis 2 Slot 3 (Analog Output) | 1 | 08/26/26 | THUMWH |
| [14.dxf](file:///e:/xApp-01/x260911-002-Kalasin-Process/x900-eDrawing/ePlanExport/SPRINT 18K SPRAY DRYER ELECTRICAL/14.dxf) | **14** | Chassis 2 Slot 4 (Digital Output) | 1 | 08/26/26 | THUMWH |
| [15.dxf](file:///e:/xApp-01/x260911-002-Kalasin-Process/x900-eDrawing/ePlanExport/SPRINT 18K SPRAY DRYER ELECTRICAL/15.dxf) | **15** | Chassis 2 Slot 5 (Digital Input) | 1 | 08/11/26 | THUMWH |
| [16.dxf](file:///e:/xApp-01/x260911-002-Kalasin-Process/x900-eDrawing/ePlanExport/SPRINT 18K SPRAY DRYER ELECTRICAL/16.dxf) | **16** | Chassis 2 Slot 6 (Digital Input) | 1 | 08/11/26 | THUMWH |
| [17.dxf](file:///e:/xApp-01/x260911-002-Kalasin-Process/x900-eDrawing/ePlanExport/SPRINT 18K SPRAY DRYER ELECTRICAL/17.dxf) | **17** | Chassis 2 Slot 7 (Digital Input) | 1 | 08/23/26 | THUMWH |
| [18.dxf](file:///e:/xApp-01/x260911-002-Kalasin-Process/x900-eDrawing/ePlanExport/SPRINT 18K SPRAY DRYER ELECTRICAL/18.dxf) | **18** | Chassis 2 Slot 8 (Digital input) | 3 | 08/23/26 | THUMWH |
| [19.dxf](file:///e:/xApp-01/x260911-002-Kalasin-Process/x900-eDrawing/ePlanExport/SPRINT 18K SPRAY DRYER ELECTRICAL/19.dxf) | **19** | Chassis 2 Slot 9 (Digital input) | 2 | 08/26/26 | THUMWH |
| [20.dxf](file:///e:/xApp-01/x260911-002-Kalasin-Process/x900-eDrawing/ePlanExport/SPRINT 18K SPRAY DRYER ELECTRICAL/20.dxf) | **20** | Chassis 3 Slot 1 (Digital Input) | 1 | 08/27/26 | THUMWH |
| [21.dxf](file:///e:/xApp-01/x260911-002-Kalasin-Process/x900-eDrawing/ePlanExport/SPRINT 18K SPRAY DRYER ELECTRICAL/21.dxf) | **21** | Chassis 3 Slot 2 (Digital Input) | 1 | 08/27/26 | THUMWH |
| [22.dxf](file:///e:/xApp-01/x260911-002-Kalasin-Process/x900-eDrawing/ePlanExport/SPRINT 18K SPRAY DRYER ELECTRICAL/22.dxf) | **22** | Chassis 3 Slot 3 (Digital Input) | 1 | 08/27/26 | THUMWH |
| [23.dxf](file:///e:/xApp-01/x260911-002-Kalasin-Process/x900-eDrawing/ePlanExport/SPRINT 18K SPRAY DRYER ELECTRICAL/23.dxf) | **23** | Chassis 3 Slot 4 (Digital Input) | 1 | 08/27/26 | THUMWH |
| [24.dxf](file:///e:/xApp-01/x260911-002-Kalasin-Process/x900-eDrawing/ePlanExport/SPRINT 18K SPRAY DRYER ELECTRICAL/24.dxf) | **24** | Chassis 3 Slot 5 (Digital Input) | 1 | 08/27/26 | THUMWH |
| [25.dxf](file:///e:/xApp-01/x260911-002-Kalasin-Process/x900-eDrawing/ePlanExport/SPRINT 18K SPRAY DRYER ELECTRICAL/25.dxf) | **25** | Chassis 3 Slot 6 (Digital Input) | 1 | 08/27/26 | THUMWH |
| [26.dxf](file:///e:/xApp-01/x260911-002-Kalasin-Process/x900-eDrawing/ePlanExport/SPRINT 18K SPRAY DRYER ELECTRICAL/26.dxf) | **26** | Chassis 3 Slot 7 (Digital Input) | 1 | 08/27/26 | THUMWH |
| [27.dxf](file:///e:/xApp-01/x260911-002-Kalasin-Process/x900-eDrawing/ePlanExport/SPRINT 18K SPRAY DRYER ELECTRICAL/27.dxf) | **27** | Chassis 3 Slot 8 (Digital Input) | 1 | 08/27/26 | THUMWH |
| [28.dxf](file:///e:/xApp-01/x260911-002-Kalasin-Process/x900-eDrawing/ePlanExport/SPRINT 18K SPRAY DRYER ELECTRICAL/28.dxf) | **28** | Chassis 3 Slot 9 (Digital Input) | 1 | 08/26/26 | THUMWH |
| [29.dxf](file:///e:/xApp-01/x260911-002-Kalasin-Process/x900-eDrawing/ePlanExport/SPRINT 18K SPRAY DRYER ELECTRICAL/29.dxf) | **29** | Chassis 4 Slot 1 (Digital Output) | 33 | 08/27/26 | THUMWH |
| [30.dxf](file:///e:/xApp-01/x260911-002-Kalasin-Process/x900-eDrawing/ePlanExport/SPRINT 18K SPRAY DRYER ELECTRICAL/30.dxf) | **30** | Chassis 4 Slot 2 (Digital Output) | 33 | 08/27/26 | THUMWH |
| [31.dxf](file:///e:/xApp-01/x260911-002-Kalasin-Process/x900-eDrawing/ePlanExport/SPRINT 18K SPRAY DRYER ELECTRICAL/31.dxf) | **31** | Chassis 4 Slot 3 (Digital Output) | 33 | 08/27/26 | THUMWH |
| [32.dxf](file:///e:/xApp-01/x260911-002-Kalasin-Process/x900-eDrawing/ePlanExport/SPRINT 18K SPRAY DRYER ELECTRICAL/32.dxf) | **32** | Chassis 4 Slot 4 (Digital Output) | 33 | 08/27/26 | THUMWH |
| [33.dxf](file:///e:/xApp-01/x260911-002-Kalasin-Process/x900-eDrawing/ePlanExport/SPRINT 18K SPRAY DRYER ELECTRICAL/33.dxf) | **33** | Chassis 4 Slot 5 (Digital Output) | 33 | 08/27/26 | THUMWH |
| [34.dxf](file:///e:/xApp-01/x260911-002-Kalasin-Process/x900-eDrawing/ePlanExport/SPRINT 18K SPRAY DRYER ELECTRICAL/34.dxf) | **34** | Chassis 4 Slot 6 (Digital Output) | 33 | 08/27/26 | THUMWH |
| [35.dxf](file:///e:/xApp-01/x260911-002-Kalasin-Process/x900-eDrawing/ePlanExport/SPRINT 18K SPRAY DRYER ELECTRICAL/35.dxf) | **35** | Chassis 5 Slot 1 (Digital Input) | 1 | 08/26/26 | THUMWH |
| [36.dxf](file:///e:/xApp-01/x260911-002-Kalasin-Process/x900-eDrawing/ePlanExport/SPRINT 18K SPRAY DRYER ELECTRICAL/36.dxf) | **36** | Chassis 5 Slot 2 (Digital Input) | 1 | 08/26/26 | THUMWH |
| [37.dxf](file:///e:/xApp-01/x260911-002-Kalasin-Process/x900-eDrawing/ePlanExport/SPRINT 18K SPRAY DRYER ELECTRICAL/37.dxf) | **37** | Chassis 5 Slot 3 (Digital Output) | 23 | 08/26/26 | THUMWH |
| [38.dxf](file:///e:/xApp-01/x260911-002-Kalasin-Process/x900-eDrawing/ePlanExport/SPRINT 18K SPRAY DRYER ELECTRICAL/38.dxf) | **38** | Chassis 5 Slot 4 (Analog input) | 2 | 08/26/26 | THUMWH |
| [R5THS00138-FBR-WIR-20001_3.dxf](file:///e:/xApp-01/x260911-002-Kalasin-Process/x900-eDrawing/ePlanExport/SPRINT 18K SPRAY DRYER ELECTRICAL/R5THS00138-FBR-WIR-20001_3.dxf) | **R5THS00138-FBR-WIR-20001_3** | (No title in attribute) | 0 |  |  |
