x92120/x260911-002-KalasinEngineering/02_Electrical_and_eDrawing/06_SCADA_Demo/PID_Loop_Control_Specification_Kalasin.pptx

INGREDION (THAILAND) CO., LTD. — KALASIN PLANT
Master PID Loop Control Specification
Project SPRINT: 18,000 TPA Spray Dryer Plant & Continuous Jet Cooker Unit
Complete Process Control Loop Architecture: 16 PID Loops | 5 Hardwired 4-20mA AO Valves & Burner Demand | 10 EtherNet/IP VFD Speed Controls | 1 Remote Utility AO | ControlLogix 5580 PIDE Platform

Document Ref: PRJ-2603001-PID-SPEC-R01 | Engineering Consultant: AEC Industrial Engineering | Rev 3.6 Master Aligned

🎯 CORE THERMAL LOOPS
5 Critical PID Loops
Direct Steam Jet Cooking (TCV-40222), Drying Air Inlet Temp (UY-FH-60210B), Pre-Heat Exchanger (TCV-60214), Steam Header (PCV-60201) & Camera Chilled Water (TCV-60202).

🛡️ DRAFT & AIR FLOW
4 Fast-Acting Loops
Drying Chamber Draft Pressure (PIC-60220 / FANE-21 VFD), Main Supply Air Flow (FIC-60210 / FANS-21), Burner Combustion Air Ratio (FIC-60211) & Conveying Fan (FIC-60201).

💧 QUALITY & MOISTURE
4 Process Loops
Chamber Outlet Temp / Moisture Cascade (TIC-60226 to PUPD-11 Slurry Pump VFD), Jet Cooker Slurry Mass Flow (FIC-40203) & pH Conditioning (pHTC-40201/40202).

⚡ HARDWARE ARCHITECTURE
ControlLogix 5580
1756-OF8 HART Module (Chassis C3 Slot 13), 20 PowerFlex VFDs over EtherNet/IP DLR (Chassis C7 Bus), 1756-IF16 HART Inputs & FT View SE Faceplates.

## Slide 2

PROCESS AUTOMATION & INSTRUMENTATION SPECIFICATION | INGREDION KALASIN — PROJECT SPRINT
PLANT PROCESS SCHEMATIC & PID CONTROL LOOP ALLOCATION MATRIX

ZONE 1 : SLURRY PREP & JET COOKER

pHTC-40201 / 40202
Slurry pH Adjustment
PV: pHT-40201/40202
CV: Dosing Pumps PD-40204/05
Target: 5.8 - 6.2 pH
P&ID: 325-01-402-PD-01

LIC-40203
Slurry Infeed Tank Level
PV: LT-40203 (0-100%)
CV: Upstream Feed Valve/Pump
Target: 60 - 75% Buffer
P&ID: 325-01-402-PD-02

FIC-40203
Jet Cooker Slurry Mass Flow
PV: FT-40221/40222 Coriolis
CV: PUCF-11 Feed Pump VFD
Target: 4.5 - 7.5 t/h
P&ID: 325-01-402-PD-02

TIC-40222 [CRITICAL]
Jet Cooker Steam Temp
PV: TT-40221/40222 Duplex RTD
CV: TCV-40222 (Samson 3241)
Target: 120 - 140 °C (Cooking)
Output: 4-20mA (C3S13,00)

ZONE 2 : DRYER AIR HEATING & STEAM

PIC-60201 [MASTER]
Steam Header Pressure
PV: PT-60201 (0-25 bar)
CV: PCV-60201 (Samson NPS 4")
Target: 16.0 bar(g) Steady
Output: 4-20mA (C3S13,03)

TIC-60214
Air Pre-Heater Temp (HXCH)
PV: TT-60214 (0-150°C)
CV: TCV-60214 (Samson NPS 2")
Target: 75 - 85 °C Pre-heat
Output: 4-20mA (C3S13,02)

TIC-60210 [THERMAL]
Dryer Inlet Air Temperature
PV: TT-60210/60211 (Hot Duct)
CV: UY-FH-60210B (BMS Demand)
Target: 185 - 205 °C Air Supply
Output: 4-20mA (C3S13,04)

FIC-60210 / 60211
Dryer Supply Air & Comb. Flow
PV: FT-60210/11 & PT-60216
CV: FANS-21 & FANC-21 VFDs
Target: 32,000 Nm³/h & Ratio
Interface: EtherNet/IP Bus

ZONE 3 : DRYING CHAMBER & DRAFT

PIC-60220 [SAFETY]
Chamber Draft Pressure
PV: PT-60220 (-10..+10 mbar)
CV: FANE-21 Exhaust Fan VFD
Target: -1.2 mbar (Negative Draft)
Fast-acting anti-puff loop

TIC-60226 / FIC-60205
Exhaust Temp / Moisture Cascade
PV: TT-60226 / TT-60240
CV: PUPD-11 Slurry Pump VFD
Target: 88 - 92 °C Outlet Air
Controls powder moisture ~6%

TIC-60202
Camera Purge Air Chilled Water
PV: TT-60202 (0-60°C)
CV: TCV-60202 (3-Way Samson)
Target: 22 - 25 °C Lens Cool
Output: 4-20mA (C3S13,01)

TIC-60215
Glycol Heat Recovery Loop
PV: TT-60215A/B Glycol Temp
CV: PUCF-21 Circulation Pump
Target: 60 °C Energy Recapture
Exhaust Dewpoint Protection

ZONE 4 : CONVEYING, LEV & UTILITY

FIC-60201
Powder Cooling Air Flow
PV: FT-60201 & PT-60203
CV: FANS-31 Conveying Fan VFD
Target: 18 - 22 m/s Velocity
Pneumatic Cyclone Discharge

PIC-61302
Silo & LEV Dust Extraction
PV: PT-61302 Vacuum Line
CV: BF-61302 LEV Blower VFD
Target: -15 mbar Negative Head
ATEX Dust Containment

LIC-61301
Packing Silo Level Balance
PV: LT-61301 Radar Level
CV: Cyclone Rotary Valves
Target: 20 - 80% Capacity
Continuous Bagging Feed

PIC-81001
Boiler Remote Setpoint Tracking
PV: Total Steam Demand (FT-60202)
CV: External Remote Setpoint
Target: Dynamic Steam Sync
Output: 4-20mA (RIO-200)

## Slide 3

PROCESS AUTOMATION & INSTRUMENTATION SPECIFICATION | INGREDION KALASIN — PROJECT SPRINT
AREA 402 : CONTINUOUS JET COOKER & SLURRY PREPARATION CONTROL LOOPS

JET COOKER THERMAL & HYDRAULIC CONTROL (P&ID: 325-01-402-PD-02)

TIC-40222 : Jet Cooker Direct Steam Cooking Temperature
• Process Variable (PV): Dual High-Precision RTDs TT-40221 & TT-40222 (Duplex Pt100, 0–150°C)
• Set Point (SP): Nominal 120.0 °C to 140.0 °C (Recipe selectable for complete starch gelatinization)
• Control Variable (CV): TCV-40222 (Samson Type 3241 Globe Valve w/ Trovis 3730-1 Positioner)
• Hardware Interface: 4–20 mA Analog Output @ Chassis C3 Slot 13 Channel 00 (TCV-40222_AO_1)
• Fail-Safe Action: Fail Closed (FC) / Spring Closes on power or air loss. High-speed steam shutoff
• Control Philosophy: Fast-acting reverse-acting PID (Increase steam increases temp). PIDE executed at 100ms periodic task with derivative filter. High/Low deviation alarms (+/- 2.0°C) with auto-interlock to slurry feed pump to prevent unburst starch discharge.

FIC-40203 : Jet Cooker Slurry Mass Feed Flow Rate Control
• Process Variable (PV): Coriolis Mass Flowmeter FT-40221 / FT-40222 (Dual channel mass flow + density)
• Set Point (SP): 4.50 to 7.50 t/h (Calibrated for exact reactor residence time)
• Control Variable (CV): PCY-40203 (Centrifugal Slurry Feed Pump PUCF-11 VFD Speed Reference)
• Hardware Interface: EtherNet/IP Industrial Bus link to MCC PowerFlex Drive (Chassis C7 Slot 00)
• Control Philosophy: Maintains constant mass flow regardless of slurry viscosity fluctuations. Tightly cascaded with Jet Cooker downstream infeed level (LT-40203) and interlocked with minimum flow switch FS-40205 to prevent pump cavitation.

SLURRY CONDITIONING & LEVEL BUFFER (P&ID: 325-01-402-PD-01)

pHTC-40201 & pHTC-40202 : pH Adjustment Tank 1 & Tank 2 Loops
• Process Variable (PV): pHT-40201 (Tank 1) & pHT-40202 (Tank 2) — Mettler Toledo InPro 3250i + M300
• Set Point (SP): 5.80 to 6.20 pH (Strict enzymatic / processing window for modified starch)
• Control Variable (CV): Acid / Caustic Dosing Pumps PD-40204 & PD-40205 (Stroke frequency / VSD)
• Hardware Interface: Modulated discrete pulse dosing / 4-20mA speed over RIO/MCC bus
• Control Philosophy: Dual-directional split-range neutralization PID. Non-linear gain scheduling applied around neutralization point (pH 7.0) to prevent severe reagent overshoot. Continuous automatic sensor cleaning cycle via SV-40201/02 water purge.

LIC-40201 / 40202 / 40203 : Buffer Tank Level Regulation
• Process Variable (PV): Hydrostatic / Radar Level Transmitters LT-40201, LT-40202, LT-40203 (0–100%)
• Set Point (SP): 65.0% Working Level (Provides 30-minute hydraulic buffer between units)
• Control Variable (CV): Slurry transfer valves XV-40201E / XV-40202F & transfer pumps PC-40201/02
• Safety Interlocks: Low-level cutoff (LSL) prevents pump dry-run; High-level cutoff (LSH) trips upstream feed and sounds audible plant horn.

## Slide 4

PROCESS AUTOMATION & INSTRUMENTATION SPECIFICATION | INGREDION KALASIN — PROJECT SPRINT
AREA 602 : SPRAY DRYER THERMAL & COMBUSTION CONTROL LOOPS

TIC-60210 : DRYER INLET AIR TEMP
Process Function:
Master Thermal Drying Energy Loop
Process Variable (PV):
TT-60210 & TT-60211 (Dual Duplex Thermocouples in Hot Air Duct DTHA-21, 0–300°C)
Set Point (SP):
185.0 °C to 205.0 °C (Product recipe dependent)
Control Variable (CV):
UY-FH-60210B (BMS Burner Demand Firing Rate 0–100%)
Hardware Channel:
4–20 mA AO @ Chassis C3 Slot 13 Channel 04
Actuator / Skid:
Direct-Fired Gas Air Heater AHTR-21 + Burner Controller
Fail-Safe State:
0% Firing Demand / Immediate Burner Trip on E-Stop
Tuning / Strategy:
High thermal inertia loop. Feedforward compensation from Main Airflow (FT-60210) dynamically adjusts fuel demand before duct temp sags. Interlocked with Burner Flame Safeguard.

TIC-60214 : AIR PRE-HEATER STEAM
Process Function:
Fresh Air Steam Pre-Heating (Energy Recovery)
Process Variable (PV):
TT-60214 (PT100 Transmitter downstream of Heat Exchanger HXCH-21, 0–150°C)
Set Point (SP):
75.0 °C to 85.0 °C (Pre-heat base temperature)
Control Variable (CV):
TCV-60214 (Samson Type 3241 Globe Valve, NPS 2", Class 300, Cv 47 + Trovis 3730-1)
Hardware Channel:
4–20 mA AO @ Chassis C3 Slot 13 Channel 02
Actuator / Skid:
Shell & Tube Steam Heat Exchanger HXCH-21
Fail-Safe State:
Fail Closed (FC) via internal mechanical spring
Tuning / Strategy:
Maximizes steam condensate energy before air enters gas burner, reducing LPG fuel consumption by up to 28%. Smooth PI control prevents thermal shock to exchanger tubes.

PIC-60201 : MAIN STEAM HEADER
Process Function:
Plant High-Pressure Steam Pressure Reducing Station
Process Variable (PV):
PT-60201 (Endress+Hauser Cerabar PMP51B, calibrated 0–25 bar(g)) + TT-60201 Temp
Set Point (SP):
16.0 bar(g) (Stable header supply pressure)
Control Variable (CV):
PCV-60201 (Samson Type 3241 Globe Valve, NPS 4", Class 300, Cv 190 + Trovis 3730-1)
Hardware Channel:
4–20 mA AO @ Chassis C3 Slot 13 Channel 03
Actuator / Skid:
Main Steam Header PRV Station (Area 602-PD-02)
Fail-Safe State:
Fail Closed (FC) / Tight Shut-off Class IV
Tuning / Strategy:
Fast-response pressure loop (50ms task). Mitigates boiler pressure surges (16–20 bar) down to stable 16.0 bar for the dryer coils and jet cooker, eliminating thermal hunting.

## Slide 5

PROCESS AUTOMATION & INSTRUMENTATION SPECIFICATION | INGREDION KALASIN — PROJECT SPRINT
AREA 602 : CHAMBER DRAFT, PRODUCT MOISTURE & OPTICAL COOLING LOOPS

PIC-60220 : CHAMBER DRAFT PRESSURE
Process Function:
Dryer Explosion & Dust Containment Safety Loop
Process Variable (PV):
PT-60220 (Chamber Differential Draft, -10.0 to +10.0 mbar range)
Set Point (SP):
-1.20 mbar (-120 Pa slight negative pressure)
Control Variable (CV):
BFY-60240 (Main Exhaust Fan FANE-21 VFD Speed Reference 0–50 Hz)
Hardware Channel:
EtherNet/IP Communication Bus to MCC (Chassis C7 Slot 00)
Safety Interlocks:
PSL-60220 Low Pressure Switch & PSH-60220 Chamber Overpressure Trip
Fail-Safe State:
Auto-Ramp to safe draft speed; immediate interlock trip on duct blockage
Control Strategy:
Highest safety priority in spray drying. If chamber goes positive (+mbar), hot flammable starch dust leaks into tower structure. High-speed anti-windup PIDE executes at 50ms with non-linear error filtering.

TIC-60226 : OUTLET TEMP / MOISTURE CASCADE
Process Function:
Final Starch Powder Moisture Regulation (~5.5-6.5%)
Process Variable (PV):
TT-60226 (Chamber Discharge Temp) & TT-60240 (Baghouse Inlet, 0–150°C)
Set Point (SP):
88.0 °C to 92.0 °C (Directly correlates to powder residual moisture)
Control Variable (CV):
PCY-60205 (High-Pressure Slurry Feed Pump PUPD-11 VFD Speed Reference)
Secondary Feedback:
16 Ultrasonic Flow Transmitters FT-60261FA..FT-60264FR (individual nozzles)
Hardware Channel:
EtherNet/IP Bus link to High Pressure Pump VFD (Area 602-PD-01)
Fail-Safe State:
Auto-cutback slurry feed upon high chamber moisture or flame loss
Control Strategy:
Master/Slave Cascade. Master temp loop adjusts slurry feed flow rate: If outlet temp drops (powder too wet), feed rate is automatically reduced; if outlet temp climbs, feed rate is increased.

TIC-60202 : CAMERA AIR CHILLED WATER
Process Function:
In-Chamber Optical Inspection Protection Loop
Process Variable (PV):
TT-60202 (Purge Air Temperature to High-Temp Camera ACAM-21, 0–60°C)
Set Point (SP):
22.0 °C to 25.0 °C (Maintains camera housing below electronics limit)
Control Variable (CV):
TCV-60202 / TV-60202 (Samson / ITQ40 3-Way Modulating Water Valve)
Hardware Channel:
4–20 mA AO @ Chassis C3 Slot 13 Channel 01 (TV-60202_AO_1)
Hardware Support:
FT-60207 (Purge Air Flow) & PT-60207 (Purge Air Pressure)
Fail-Safe State:
Fail-to-Port A (100% Chilled Water bypass to heat exchanger on power loss)
Control Strategy:
Standard PI loop modulating chilled water bypass. Prevents condensation fogging on optical lenses while protecting sensitive camera sensors from 200°C chamber ambient heat.

## Slide 6

PROCESS AUTOMATION & INSTRUMENTATION SPECIFICATION | INGREDION KALASIN — PROJECT SPRINT
AREA 602/613 & UTILITIES : HEAT RECOVERY, CONVEYING & BOILER SYNC

TIC-60215 : GLYCOL HEAT RECOVERY RUN-AROUND LOOP
• Process Service: Exhaust Waste Heat Recapture Skid (PUCF-21 / HXCR-21, P&ID: 325-01-602-PD-03)
• Process Variable (PV): TT-60215A & TT-60215B (Glycol Supply & Return Temp) + PT-60215 Pressure
• Set Point (SP): 55.0 °C to 65.0 °C (Maintains exhaust above acid/moisture condensation dew point)
• Control Variable (CV): PCY-60215 (Heat Recovery Centrifugal Circulation Pump PUCF-21 VFD Speed Reference)
• Control Strategy: Modulates 15% polypropylene glycol circulation rate between exhaust heat coil and fresh air preheater. Recovers up to 1.8 MW of thermal energy without fouling exhaust stack.

PIC-61302 : SILO VENTING & LEV DUST EXTRACTION VACUUM
• Process Service: Packaging Silo & Bagging Station Dust Capture (P&ID: 325-01-613-PD-01 to PD-05)
• Process Variable (PV): PT-61302 (Vacuum Duct Pressure) & DPT-61301/02 (Vent Filter Differential Pressure)
• Set Point (SP): -15.0 mbar Negative Pressure at LEV Pick-up Hoods
• Control Variable (CV): BFY-61302 (LEV Blower Fan BF-61302 VFD) & BFY-61303 (Fugitive Dust Fan VFD)
• Control Strategy: Maintains negative capture velocity across packing heads. Automatically triggers pulse-jet reverse air filter cleaning (SV-61310) when DPT exceeds 12.0 mbar.

FIC-60201 : POWDER COOLING & PNEUMATIC CONVEYING
• Process Service: Cyclone Discharge Powder Chilling & Conveying (P&ID: 325-01-602-PD-08)
• Process Variable (PV): FT-60201 (Cold Conveying Air Mass Flow) & PT-60203 (Duct Transport Pressure)
• Set Point (SP): 18.0 to 22.0 m/s Saltation Velocity (Prevents starch powder settling / line plugging)
• Control Variable (CV): BFY-60206 (Cooling / Conveying Fan FANS-31 VFD Speed Reference)
• Control Strategy: Rapidly cools warm powder exiting cyclone below starch glass transition point (45°C) to prevent caking and agglomeration during transfer to storage silos.

PIC-81001 : BOILER STEAM DEMAND REMOTE SETPOINT SYNC
• Process Service: Utility Boiler Steam Synchronization Skid (P&ID: 325-01-814-PD-01 / RIO-200)
• Process Variable (PV): Instantaneous Plant Steam Flow FT-60202 + FT-60203 & Steam Header Pressure PT-60201
• Set Point (SP): Dynamic Steam Demand Tracking (Feedforward compensation)
• Control Variable (CV): External Remote Setpoint (4–20 mA AO from RIO-200 to Boiler Modulation Skid)
• Control Strategy: Feedforward boiler firing setpoint sent before large steam valves (PCV-60201 / TCV-40222) ramp up, eliminating boiler pressure sags during plant startup and batch switching.

## Slide 7

PROCESS AUTOMATION & INSTRUMENTATION SPECIFICATION | INGREDION KALASIN — PROJECT SPRINT
MASTER PID LOOP ENGINEERING SCHEDULE & I/O ALLOCATION TABLE

Loop Tag | Process Service Description | P&ID Drawing | PV Sensor Tag(s) | Nominal SP | Final Control Element | I/O Interface | Action | Fail State
TIC-40222 | Jet Cooker Direct Steam Cooking Temp | 325-01-402-PD-02 | TT-40221 / TT-40222 | 120–140 °C | TCV-40222 (Samson 3241) | 4-20mA (C3S13,00) | Rev | Fail Closed
FIC-40203 | Jet Cooker Slurry Mass Flow Control | 325-01-402-PD-02 | FT-40221 / FT-40222 | 4.5–7.5 t/h | PUCF-11 Slurry Pump VFD | EtherNet/IP Bus | Rev | Stop on Fail
pHTC-40201 | pH Adjustment Tank 1 Conditioning | 325-01-402-PD-01 | pHT-40201 (0–14 pH) | 5.8–6.2 pH | PD-40204 Dosing Pump | Discrete/Speed | Split | Stop on Fail
pHTC-40202 | pH Adjustment Tank 2 Conditioning | 325-01-402-PD-01 | pHT-40202 (0–14 pH) | 5.8–6.2 pH | PD-40205 Dosing Pump | Discrete/Speed | Split | Stop on Fail
PIC-60201 | Spray Dryer Main Steam Header Press. | 325-01-602-PD-02 | PT-60201 (0–25 bar) | 16.0 bar(g) | PCV-60201 (Samson NPS 4") | 4-20mA (C3S13,03) | Rev | Fail Closed
TIC-60214 | Air Pre-Heater Steam Exchanger Temp | 325-01-602-PD-03 | TT-60214 (0–150°C) | 75–85 °C | TCV-60214 (Samson NPS 2") | 4-20mA (C3S13,02) | Rev | Fail Closed
TIC-60210 | Dryer Inlet Air Heating Temperature | 325-01-602-PD-06 | TT-60210 / TT-60211 | 185–205 °C | UY-FH-60210B (BMS Demand) | 4-20mA (C3S13,04) | Rev | 0% Demand
FIC-60210 | Main Supply Air Flow Rate Control | 325-01-602-PD-03 | FT-60210 / FT-60211 | 32,000 Nm³/h | FANS-21 Supply Fan VFD | EtherNet/IP Bus | Rev | Coast / Stop
FIC-60211 | Burner Combustion Air Flow / Ratio | 325-01-602-PD-03 | PT-60216 / TT-60216 | Ratio to Gas | FANC-21 Comb. Fan VFD | EtherNet/IP Bus | Rev | Coast / Purge
PIC-60220 | Dryer Chamber Draft Pressure (Safety) | 325-01-602-PD-04 | PT-60220 (-10..+10 mbar) | -1.20 mbar | FANE-21 Exhaust Fan VFD | EtherNet/IP Bus | Direct | Safe Ramp
TIC-60226 | Exhaust Temp / Moisture Cascade Loop | 325-01-602-PD-04 | TT-60226 / TT-60240 | 88–92 °C | PUPD-11 Slurry Pump VFD | EtherNet/IP Bus | Direct | Auto Cutback
TIC-60202 | Camera Purge Air Chilled Water Temp | 325-01-602-PD-07 | TT-60202 (0–60°C) | 22–25 °C | TCV-60202 (3-Way Valve) | 4-20mA (C3S13,01) | Direct | Fail Port A
TIC-60215 | Glycol Heat Recovery Circulation | 325-01-602-PD-03 | TT-60215A / TT-60215B | 55–65 °C | PUCF-21 Glycol Pump VFD | EtherNet/IP Bus | Rev | Modulate
FIC-60201 | Powder Cooling & Conveying Air Flow | 325-01-602-PD-08 | FT-60201 / PT-60203 | 18–22 m/s | FANS-31 Conveying Fan VFD | EtherNet/IP Bus | Rev | Coast / Stop
PIC-61302 | Packing Silo & LEV Extraction Vacuum | 325-01-613-PD-03 | PT-61302 (-50..0 mbar) | -15 mbar | BF-61302 LEV Blower VFD | EtherNet/IP Bus | Direct | Modulate
PIC-81001 | Boiler Steam Demand Remote Sync | 325-01-814-PD-01 | Total Steam (FT-60202) | Feedforward | Remote Setpoint to Boiler | 4-20mA (RIO-200) | Direct | Demand Safe

## Slide 8

PROCESS AUTOMATION & INSTRUMENTATION SPECIFICATION | INGREDION KALASIN — PROJECT SPRINT
ROCKWELL CONTROLLOGIX PIDE ARCHITECTURE & FACTORYTALK VIEW SE INTEGRATION

CONTROLLOGIX PIDE INSTRUCTION
Algorithm Type:
Enhanced PID (PIDE) in Function Block Diagram (FBD) / Periodic Tasks
Task Execution Rates:
• Pressure & Draft Loops (PIC-60220, PIC-60201): 50 ms Periodic Task
• Flow & Speed Loops (FIC-40203, FIC-60210): 100 ms Periodic Task
• Temperature & pH Loops (TIC-40222, TIC-60210): 250 ms Periodic Task
Operating Modes:
• Hand (Operator Manual CV override via HMI)
• Auto (Automatic regulation to Local Setpoint)
• Cascade (Remote Setpoint from supervisory cascade)
Anti-Windup & Clamping:
Built-in dynamic CV upper/lower limits (CVHighLimit = 100%, CVLowLimit = 0%) and programmable slew rate clamping (%/sec) to prevent actuator hammering.
Derivative Filtering:
Low-pass derivative filter applied to PV (not error) to eliminate electrical sensor noise spikes from kicking control output.

ADVANCED PROCESS STRATEGIES
Chamber Draft Feedforward:
Combines Exhaust Fan speed with Main Air Supply Fan speed feedforward (FANE-21 tracks FANS-21) to cancel transient draft surges during air startup.
Burner Firing Heat Decoupling:
Ratio decoupling between combustion airflow and gas demand (UY-FH-60210B) ensures stoichiometric flame profile during load ramps.
Slurry Moisture Cascade:
Outer Temperature Loop (TIC-60226) outputs Remote SP to Inner Slurry Mass Flow Loop (FIC-40205) for high-fidelity moisture containment.
Dual Duplex Sensor Validation:
High-temp RTDs/TCs (TT-40221/22 and TT-60210/11) utilize 2-out-of-2 deviation monitoring. Sensor drift (>3°C) generates preventive maintenance alarm.

FACTORYTALK VIEW SE HMI STANDARD
PlantPAx Faceplates:
Standardized ISA-101 high-performance HMI faceplates deployed across 3 Operator Workstations (OWS) and 1 EWS.
Operator Interaction:
• One-click Auto / Manual / Cascade toggling
• Visual SP / PV / CV real-time bar graphs
• Dedicated Tuning tab with P, I, D gains, Deadband & Filter coefficients
• Historical trending with 1-second sample rate
Alarm Management:
EEMUA 191 / ISA-18.2 compliant alarming:
• PV High-High (Emergency Interlock Trip)
• PV High / Low (Process Warning)
• Deviation Alarm (Control Loop Degradation)
• Transmitter Out-of-Range (Bad PV Quality)
