x92120/x260911-002-KalasinEngineering/02_Electrical_and_eDrawing/04_PDF_Reports_and_Drawings/JB_Report_IS-JB-603.pdf

INGREDION (THAILAND) CO., LTD. | PROJECT JET COOKER | AEC INDUSTRIAL ENGINEERING | REV. 3.6
ENCLOSURE: IS-JB-603 | TYPE: Intrinsically Safe Junction Box (Ex i / LS) | LOCATION: Spray Dryer 3rd Floor | SIZE: 300-200-150 mm
SUMMARY: Total Channels: 32 | Active: 22 | Spare: 10 (31.2%) | DI: 16 | DO: 0 | AI: 16 | AO: 0 | BUS: 0
No. | Terminal | Rack/Slot | Channel | I/O Module | Type Signal Characteristic Instrument Tag | | | PLC Tag Name | P&ID No. | Service / Equipment Description | Zone / Floor
1 | C3S01-X1 | C3/S1 | C3S01,00 | 1756-IB32-0 | DI | - | AT-40201 | AT-40201_DI_1 | - | - | Spray Dryer / 3rd
2 | C3S01-X1 | C3/S1 | C3S01,01 | 1756-IB32-1 | DI | - | AT-40202 | AT-40202_DI_1 | - | - | Spray Dryer / 3rd
3 | C3S01-X1 | C3/S1 | C3S01,02 | 1756-IB32-2 | DI | - | AT-40203 | AT-40203_DI_1 | - | - | Spray Dryer / 3rd
4 | C3S01-X1 | C3/S1 | C3S01,03 | 1756-IB32-3 | DI | Dry Contact | LSH-60230 | LSH-60230_DI_1 | 3-25-01-602-PD-04 | 0 | Spray Dryer / 1st
5 | C3S01-X1 | C3/S1 | C3S01,04 | 1756-IB32-4 | DI | Dry Contact | LSH-60231 | LSH-60231_DI_1 | 3-25-01-602-PD-04 | 0 | Spray Dryer / 1st
6 | C3S01-X1 | C3/S1 | C3S01,05 | 1756-IB32-5 | DI | Dry Contact | LSH-60240 | LSH-60240_DI_1 | 3-25-01-602-PD-05 | 0 | Spray Dryer / 1st
7 | C3S01-X1 | C3/S1 | C3S01,06 | 1756-IB32-6 | DI | - | PD-60202 | PD-60202_DI_1 | - | - | Spray Dryer / 3rd
8 | C3S04-X1 | C3/S4 | C3S04,00 | 1756-IF16-0 | AI | 4 - 20 mA | PT-60230 | PT-60230_AI_1 | 3-25-01-602-PD-04 | Pressure Transmitter | Spray Dryer / 4th
9 | C3S04-X1 | C3/S4 | C3S04,01 | 1756-IF16-1 | AI | 4 - 20 mA | PT-60231 | PT-60231_AI_1 | 3-25-01-602-PD-04 | Pressure Transmitter | Spray Dryer / 4th
10 | C3S01-X1 | C3/S1 | C3S01,07 | 1756-IB32-7 | DI | - | RV-60204 | RV-60204_DI_1 | - | - | Spray Dryer / 3rd
11 | C3S01-X1 | C3/S1 | C3S01,15 | 1756-IB32-15 | DI | - | Spare | Spare_DI_0 | - | Spare I/O Point | -
12 | C3S04-X1 | C3/S4 | C3S04,07 | 1756-IF16-7 | AI | - | Spare | Spare_AI_0 | - | Spare I/O Point | -
13 | C3S04-X1 | C3/S4 | C3S04,08 | 1756-IF16-8 | AI | - | Spare | Spare_AI_0 | - | Spare I/O Point | -
14 | C3S04-X1 | C3/S4 | C3S04,09 | 1756-IF16-9 | AI | - | Spare | Spare_AI_0 | - | Spare I/O Point | -
15 | C3S04-X1 | C3/S4 | C3S04,10 | 1756-IF16-10 | AI | - | Spare | Spare_AI_0 | - | Spare I/O Point | -
16 | C3S04-X1 | C3/S4 | C3S04,11 | 1756-IF16-11 | AI | - | Spare | Spare_AI_0 | - | Spare I/O Point | -
17 | C3S04-X1 | C3/S4 | C3S04,12 | 1756-IF16-12 | AI | - | Spare | Spare_AI_0 | - | Spare I/O Point | -
18 | C3S04-X1 | C3/S4 | C3S04,13 | 1756-IF16-13 | AI | - | Spare | Spare_AI_0 | - | Spare I/O Point | -
19 | C3S04-X1 | C3/S4 | C3S04,14 | 1756-IF16-14 | AI | - | Spare | Spare_AI_0 | - | Spare I/O Point | -
20 | C3S04-X1 | C3/S4 | C3S04,15 | 1756-IF16-15 | AI | - | Spare | Spare_AI_0 | - | Spare I/O Point | -
21 | C3S04-X1 | C3/S4 | C3S04,02 | 1756-IF16-2 | AI | 4 - 20 mA | TT-60224 | TT-60224_AI_1 | 3-25-01-602-PD-04 | 0 | Spray Dryer / 4th
22 | C3S04-X1 | C3/S4 | C3S04,03 | 1756-IF16-3 | AI | 4 - 20 mA | TT-60225 | TT-60225_AI_1 | 3-25-01-602-PD-04 | 0 | Spray Dryer / 3rd
23 | C3S04-X1 | C3/S4 | C3S04,04 | 1756-IF16-4 | AI | 4 - 20 mA | TT-60226 | TT-60226_AI_1 | 3-25-01-602-PD-04 | 0 | Spray Dryer / 2nd
24 | C3S04-X1 | C3/S4 | C3S04,05 | 1756-IF16-5 | AI | 4 - 20 mA | TT-60227 | TT-60227_AI_1 | 3-25-01-602-PD-04 | 0 | Spray Dryer / 1st
25 | C3S04-X1 | C3/S4 | C3S04,06 | 1756-IF16-6 | AI | 4 - 20 mA | TT-60230 | TT-60230_AI_1 | 3-25-01-602-PD-04 | 0 | Spray Dryer / 3rd
26 | C3S01-X1 | C3/S1 | C3S01,08 | 1756-IB32-8 | DI | Dry Contact | ZS-60201C | ZS-60201C_DI_1 | 3-25-01-602-PD-04 | 0 | Spray Dryer / 4th
27 | C3S01-X1 | C3/S1 | C3S01,09 | 1756-IB32-9 | DI | Dry Contact | ZS-60201D | ZS-60201D_DI_1 | 3-25-01-602-PD-04 | 0 | Spray Dryer / 4th
28 | C3S01-X1 | C3/S1 | C3S01,10 | 1756-IB32-10 | DI | Dry Contact | ZS-60201E | ZS-60201E_DI_1 | 3-25-01-602-PD-04 | 0 | Spray Dryer / 1st
29 | C3S01-X1 | C3/S1 | C3S01,11 | 1756-IB32-11 | DI | Dry Contact | ZS-60229 | ZS-60229_DI_1 | 3-25-01-602-PD-04 | 0 | Spray Dryer / 4th
30 | C3S01-X1 | C3/S1 | C3S01,12 | 1756-IB32-12 | DI | Dry Contact | ZS-60230 | ZS-60230_DI_1 | 3-25-01-602-PD-04 | 0 | Spray Dryer / 4th
31 | C3S01-X1 | C3/S1 | C3S01,13 | 1756-IB32-13 | DI | Dry Contact | ZS-60231A | ZS-60231A_DI_1 | 3-25-01-602-PD-05 | 0 | Spray Dryer / 4th
Doc No.: Instrument I/O List (Kalasin) - IS-JB-603 | Page 1 of 2 | CONFIDENTIAL | Generated: 2026-09-07

INGREDION (THAILAND) CO., LTD. | PROJECT JET COOKER | AEC INDUSTRIAL ENGINEERING | REV. 3.6
ENCLOSURE: IS-JB-603 | TYPE: Intrinsically Safe Junction Box (Ex i / LS) | LOCATION: Spray Dryer 3rd Floor | SIZE: 300-200-150 mm
SUMMARY: Total Channels: 32 | Active: 22 | Spare: 10 (31.2%) | DI: 16 | DO: 0 | AI: 16 | AO: 0 | BUS: 0
No. | Terminal | Rack/Slot | Channel | I/O Module | Type Signal Characteristic Instrument Tag | | | PLC Tag Name | P&ID No. | Service / Equipment Description | Zone / Floor
32 | C3S01-X1 | C3/S1 | C3S01,14 | 1756-IB32-14 | DI | Dry Contact | ZS-60231B | ZS-60231B_DI_1 | 3-25-01-602-PD-05 | 0 | Spray Dryer / 4th
Doc No.: Instrument I/O List (Kalasin) - IS-JB-603 | Page 2 of 2 | CONFIDENTIAL | Generated: 2026-09-07
