x92120/x260911-002-KalasinEngineering/02_Electrical_and_eDrawing/04_PDF_Reports_and_Drawings/JB_Report_IS-JB-608.pdf

INGREDION (THAILAND) CO., LTD. | PROJECT JET COOKER | AEC INDUSTRIAL ENGINEERING | REV. 3.6
ENCLOSURE: IS-JB-608 | TYPE: Intrinsically Safe Junction Box (Ex i / LS) | LOCATION: Spray Dryer 8th Floor | SIZE: 300-200-150 mm
SUMMARY: Total Channels: 32 | Active: 14 | Spare: 18 (56.2%) | DI: 16 | DO: 8 | AI: 8 | AO: 0 | BUS: 0
No. | Terminal | Rack/Slot | Channel | I/O Module | Type Signal Characteristic Instrument Tag | | | PLC Tag Name | P&ID No. | Service / Equipment Description | Zone / Floor
1 | C4S06-X1 | C4/S6 | C4S06,00 | 1756-IF16-0 | AI | 4 - 20 mA | PT-60220 | PT-60220_AI_1 | 3-25-01-602-PD-04 | Pressure Transmitter | Spray Dryer / 6th
2 | C4S01-X2 | C4/S1 | C4S01,23 | 1756-IB32-23 | DI | - | Spare | Spare_DI_0 | - | Spare I/O Point | -
3 | C4S01-X2 | C4/S1 | C4S01,24 | 1756-IB32-24 | DI | - | Spare | Spare_DI_0 | - | Spare I/O Point | -
4 | C4S01-X2 | C4/S1 | C4S01,25 | 1756-IB32-25 | DI | - | Spare | Spare_DI_0 | - | Spare I/O Point | -
5 | C4S01-X2 | C4/S1 | C4S01,26 | 1756-IB32-26 | DI | - | Spare | Spare_DI_0 | - | Spare I/O Point | -
6 | C4S01-X2 | C4/S1 | C4S01,27 | 1756-IB32-27 | DI | - | Spare | Spare_DI_0 | - | Spare I/O Point | -
7 | C4S01-X2 | C4/S1 | C4S01,28 | 1756-IB32-28 | DI | - | Spare | Spare_DI_0 | - | Spare I/O Point | -
8 | C4S01-X2 | C4/S1 | C4S01,29 | 1756-IB32-29 | DI | - | Spare | Spare_DI_0 | - | Spare I/O Point | -
9 | C4S01-X2 | C4/S1 | C4S01,30 | 1756-IB32-30 | DI | - | Spare | Spare_DI_0 | - | Spare I/O Point | -
10 | C4S01-X2 | C4/S1 | C4S01,31 | 1756-IB32-31 | DI | - | Spare | Spare_DI_0 | - | Spare I/O Point | -
11 | C4S04-X1 | C4/S4 | C4S04,09 | 1756-OB32-9 | DO | - | Spare | Spare_DO_0 | - | Spare I/O Point | -
12 | C4S04-X1 | C4/S4 | C4S04,10 | 1756-OB32-10 | DO | - | Spare | Spare_DO_0 | - | Spare I/O Point | -
13 | C4S04-X1 | C4/S4 | C4S04,11 | 1756-OB32-11 | DO | - | Spare | Spare_DO_0 | - | Spare I/O Point | -
14 | C4S04-X1 | C4/S4 | C4S04,12 | 1756-OB32-12 | DO | - | Spare | Spare_DO_0 | - | Spare I/O Point | -
15 | C4S04-X1 | C4/S4 | C4S04,13 | 1756-OB32-13 | DO | - | Spare | Spare_DO_0 | - | Spare I/O Point | -
16 | C4S04-X1 | C4/S4 | C4S04,14 | 1756-OB32-14 | DO | - | Spare | Spare_DO_0 | - | Spare I/O Point | -
17 | C4S04-X1 | C4/S4 | C4S04,15 | 1756-OB32-15 | DO | - | Spare | Spare_DO_0 | - | Spare I/O Point | -
18 | C4S05-X1 | C4/S5 | C4S05,06 | 1756-IF16-6 | AI | - | Spare | Spare_AI_0 | - | Spare I/O Point | -
19 | C4S05-X1 | C4/S5 | C4S05,07 | 1756-IF16-7 | AI | - | Spare | Spare_AI_0 | - | Spare I/O Point | -
20 | C4S06-X1 | C4/S6 | C4S06,01 | 1756-IF16-1 | AI | 4 - 20 mA | TT-60220 | TT-60220_AI_1 | 3-25-01-602-PD-04 | 0 | Spray Dryer / 6th
21 | C4S06-X1 | C4/S6 | C4S06,02 | 1756-IF16-2 | AI | 4 - 20 mA | TT-60221 | TT-60221_AI_1 | 3-25-01-602-PD-04 | 0 | Spray Dryer / 6th
22 | C4S06-X1 | C4/S6 | C4S06,03 | 1756-IF16-3 | AI | 4 - 20 mA | TT-60222 | TT-60222_AI_1 | 3-25-01-602-PD-04 | 0 | Spray Dryer / 5th
23 | C4S06-X1 | C4/S6 | C4S06,04 | 1756-IF16-4 | AI | 4 - 20 mA | TT-60223 | TT-60223_AI_1 | 3-25-01-602-PD-04 | 0 | Spray Dryer / 5th
24 | C4S04-X1 | C4/S4 | C4S04,08 | 1756-OB32-8 | DO | 4 - 20 mA | XA-60201 | XA-60201_DO_1 | 3-25-01-602-PD-03 | 0 | Spray Dryer / 5th
25 | C4S06-X1 | C4/S6 | C4S06,05 | 1756-IF16-5 | AI | 4 - 20 mA | XT-60201 | XT-60201_AI_1 | 3-25-01-602-PD-03 | 0 | Spray Dryer / 5th
26 | C4S01-X2 | C4/S1 | C4S01,16 | 1756-IB32-16 | DI | Dry Contact | ZS-60201A | ZS-60201A_DI_1 | 3-25-01-602-PD-04 | 0 | Spray Dryer / 6th
27 | C4S01-X2 | C4/S1 | C4S01,17 | 1756-IB32-17 | DI | Dry Contact | ZS-60201B | ZS-60201B_DI_1 | 3-25-01-602-PD-04 | 0 | Spray Dryer / 6th
28 | C4S01-X2 | C4/S1 | C4S01,18 | 1756-IB32-18 | DI | Dry Contact | ZS-60231C | ZS-60231C_DI_1 | 3-25-01-602-PD-04 | 0 | Spray Dryer / 5th
29 | C4S01-X2 | C4/S1 | C4S01,19 | 1756-IB32-19 | DI | Dry Contact | ZS-60231D | ZS-60231D_DI_1 | 3-25-01-602-PD-04 | 0 | Spray Dryer / 5th
30 | C4S01-X2 | C4/S1 | C4S01,20 | 1756-IB32-20 | DI | Dry Contact | ZS-60231E | ZS-60231E_DI_1 | 3-25-01-602-PD-05 | 0 | Spray Dryer / 5th
31 | C4S01-X2 | C4/S1 | C4S01,21 | 1756-IB32-21 | DI | Dry Contact | ZS-60231F | ZS-60231F_DI_1 | 3-25-01-602-PD-05 | 0 | Spray Dryer / 5th
Doc No.: Instrument I/O List (Kalasin) - IS-JB-608 | Page 1 of 2 | CONFIDENTIAL | Generated: 2026-09-07

INGREDION (THAILAND) CO., LTD. | PROJECT JET COOKER | AEC INDUSTRIAL ENGINEERING | REV. 3.6
ENCLOSURE: IS-JB-608 | TYPE: Intrinsically Safe Junction Box (Ex i / LS) | LOCATION: Spray Dryer 8th Floor | SIZE: 300-200-150 mm
SUMMARY: Total Channels: 32 | Active: 14 | Spare: 18 (56.2%) | DI: 16 | DO: 8 | AI: 8 | AO: 0 | BUS: 0
No. | Terminal | Rack/Slot | Channel | I/O Module | Type Signal Characteristic Instrument Tag | | | PLC Tag Name | P&ID No. | Service / Equipment Description | Zone / Floor
32 | C4S01-X2 | C4/S1 | C4S01,22 | 1756-IB32-22 | DI | Dry Contact | ZS-60240 | ZS-60240_DI_1 | 3-25-01-602-PD-05 | 0 | Spray Dryer / 6th
Doc No.: Instrument I/O List (Kalasin) - IS-JB-608 | Page 2 of 2 | CONFIDENTIAL | Generated: 2026-09-07
