x92120/x260911-002-KalasinEngineering/02_Electrical_and_eDrawing/04_PDF_Reports_and_Drawings/JB_Report_IS-JB-618.pdf

INGREDION (THAILAND) CO., LTD. | PROJECT JET COOKER | AEC INDUSTRIAL ENGINEERING | REV. 3.6
ENCLOSURE: IS-JB-618 | TYPE: Intrinsically Safe Junction Box (Ex i / LS) | LOCATION: Packing Tower 8th Floor | SIZE: 450-300-150 mm
SUMMARY: Total Channels: 44 | Active: 22 | Spare: 22 (50.0%) | DI: 32 | DO: 0 | AI: 12 | AO: 0 | BUS: 0
No. | Terminal | Rack/Slot | Channel | I/O Module | Type Signal Characteristic Instrument Tag | | | PLC Tag Name | P&ID No. | Service / Equipment Description | Zone / Floor
1 | C3S05-X1 | C3/S5 | C3S05,04 | 1756-IF16-4 | AI | 4 - 20 mA | DPT-61301 | DPT-61301_AI_1 | 3-25-01-613-PD-01 | Differential Pressure Transmitte | Packing Tower / ...
2 | C3S05-X1 | C3/S5 | C3S05,05 | 1756-IF16-5 | AI | 4 - 20 mA | DPT-61302 | DPT-61302_AI_1 | 3-25-01-613-PD-01 | Differential Pressure Transmitte | Packing Tower / ...
3 | C3S02-X1 | C3/S2 | C3S02,00 | 1756-IB32-0 | DI | - | ISV-61301 | ISV-61301_DI_1 | 3-25-01-613-PD-01 | - | Packing Tower / ...
4 | C3S02-X1 | C3/S2 | C3S02,01 | 1756-IB32-1 | DI | Dry Contact | LSH-61301 | LSH-61301_DI_1 | 3-25-01-613-PD-01 | 0 | Packing Tower / ...
5 | C3S02-X1 | C3/S2 | C3S02,02 | 1756-IB32-2 | DI | - | LSH-61303 | LSH-61303_DI_1 | 325-01-613-PD-01 | - | Packing Tower / ...
6 | C3S02-X1 | C3/S2 | C3S02,03 | 1756-IB32-3 | DI | Dry Contact | LSH-61306 | LSH-61306_DI_1 | 3-25-01-613-PD-01 | 0 | Packing Tower / ...
7 | C3S02-X1 | C3/S2 | C3S02,04 | 1756-IB32-4 | DI | Dry Contact | LSH-61308 | LSH-61308_DI_1 | 3-25-01-613-PD-01 | 0 | Packing Tower / ...
8 | C3S02-X1 | C3/S2 | C3S02,05 | 1756-IB32-5 | DI | Dry Contact | LSL-61302 | LSL-61302_DI_1 | 3-25-01-613-PD-01 | 0 | Packing Tower / ...
9 | C3S05-X1 | C3/S5 | C3S05,06 | 1756-IF16-6 | AI | 4 - 20 mA | LT-61301 | LT-61301_AI_1 | 3-25-01-613-PD-01 | Level Transmitter | Packing Tower / ...
10 | C3S02-X1 | C3/S2 | C3S02,06 | 1756-IB32-6 | DI | Dry Contact | PSE-61300 | PSE-61300_DI_1 | 3-25-01-613-PD-01 | 0 | Packing Tower / ...
11 | C3S02-X1 | C3/S2 | C3S02,07 | 1756-IB32-7 | DI | Dry Contact | PSE-61301 | PSE-61301_DI_1 | 3-25-01-613-PD-01 | 0 | Packing Tower / ...
12 | C3S02-X1 | C3/S2 | C3S02,08 | 1756-IB32-8 | DI | Dry Contact | PSE-61304 | PSE-61304_DI_1 | 3-25-01-613-PD-01 | 0 | Packing Tower / ...
13 | C3S02-X1 | C3/S2 | C3S02,09 | 1756-IB32-9 | DI | - | PSV-61301A | PSV-61301A_DI_1 | 325-01-613-PD-01 | - | Packing Tower / ...
14 | C3S02-X1 | C3/S2 | C3S02,10 | 1756-IB32-10 | DI | - | PSV-61301B | PSV-61301B_DI_1 | 325-01-613-PD-01 | - | Packing Tower / ...
15 | C3S05-X1 | C3/S5 | C3S05,07 | 1756-IF16-7 | AI | 4 - 20 mA | PT-61301 | PT-61301_AI_1 | 3-25-01-613-PD-01 | Pressure Transmitter | Packing Tower / ...
16 | C3S05-X1 | C3/S5 | C3S05,08 | 1756-IF16-8 | AI | 4 - 20 mA | PT-61303 | PT-61303_AI_1 | 3-25-01-613-PD-01 | Pressure Transmitter | Packing Tower / ...
17 | C3S05-X1 | C3/S5 | C3S05,09 | 1756-IF16-9 | AI | 4 - 20 mA | PT-61304 | PT-61304_AI_1 | 3-25-01-613-PD-01 | Pressure Transmitter | Packing Tower / ...
18 | C3S05-X1 | C3/S5 | C3S05,10 | 1756-IF16-10 | AI | 4 - 20 mA | PT-61305 | PT-61305_AI_1 | 3-25-01-613-PD-01 | Pressure Transmitter | Packing Tower / ...
19 | C3S02-X1 | C3/S2 | C3S02,13 | 1756-IB32-13 | DI | - | Spare | Spare_DI_0 | 3-25-01-613-PD-01 | Spare I/O Point | Packing Tower / ...
20 | C3S02-X1 | C3/S2 | C3S02,14 | 1756-IB32-14 | DI | - | Spare | Spare_DI_0 | 3-25-01-613-PD-01 | Spare I/O Point | Packing Tower / ...
21 | C3S02-X1 | C3/S2 | C3S02,15 | 1756-IB32-15 | DI | - | Spare | Spare_DI_0 | 3-25-01-613-PD-01 | Spare I/O Point | Packing Tower / ...
22 | C3S02-X2 | C3/S2 | C3S02,16 | 1756-IB32-16 | DI | - | Spare | Spare_DI_0 | 3-25-01-613-PD-01 | Spare I/O Point | Packing Tower / ...
23 | C3S02-X2 | C3/S2 | C3S02,17 | 1756-IB32-17 | DI | - | Spare | Spare_DI_0 | 3-25-01-613-PD-01 | Spare I/O Point | Packing Tower / ...
24 | C3S02-X2 | C3/S2 | C3S02,18 | 1756-IB32-18 | DI | - | Spare | Spare_DI_0 | 3-25-01-613-PD-01 | Spare I/O Point | Packing Tower / ...
25 | C3S02-X2 | C3/S2 | C3S02,19 | 1756-IB32-19 | DI | - | Spare | Spare_DI_0 | 3-25-01-613-PD-01 | Spare I/O Point | Packing Tower / ...
26 | C3S02-X2 | C3/S2 | C3S02,20 | 1756-IB32-20 | DI | - | Spare | Spare_DI_0 | 3-25-01-613-PD-01 | Spare I/O Point | Packing Tower / ...
27 | C3S02-X2 | C3/S2 | C3S02,21 | 1756-IB32-21 | DI | - | Spare | Spare_DI_0 | 3-25-01-613-PD-01 | Spare I/O Point | Packing Tower / ...
28 | C3S02-X2 | C3/S2 | C3S02,22 | 1756-IB32-22 | DI | - | Spare | Spare_DI_0 | 3-25-01-613-PD-01 | Spare I/O Point | Packing Tower / ...
29 | C3S02-X2 | C3/S2 | C3S02,23 | 1756-IB32-23 | DI | - | Spare | Spare_DI_0 | 3-25-01-613-PD-01 | Spare I/O Point | Packing Tower / ...
30 | C3S02-X2 | C3/S2 | C3S02,24 | 1756-IB32-24 | DI | - | Spare | Spare_DI_0 | 3-25-01-613-PD-01 | Spare I/O Point | Packing Tower / ...
31 | C3S02-X2 | C3/S2 | C3S02,25 | 1756-IB32-25 | DI | - | Spare | Spare_DI_0 | 3-25-01-613-PD-01 | Spare I/O Point | Packing Tower / ...
Doc No.: Instrument I/O List (Kalasin) - IS-JB-618 | Page 1 of 2 | CONFIDENTIAL | Generated: 2026-09-07

INGREDION (THAILAND) CO., LTD. | PROJECT JET COOKER | AEC INDUSTRIAL ENGINEERING | REV. 3.6
ENCLOSURE: IS-JB-618 | TYPE: Intrinsically Safe Junction Box (Ex i / LS) | LOCATION: Packing Tower 8th Floor | SIZE: 450-300-150 mm
SUMMARY: Total Channels: 44 | Active: 22 | Spare: 22 (50.0%) | DI: 32 | DO: 0 | AI: 12 | AO: 0 | BUS: 0
No. | Terminal | Rack/Slot | Channel | I/O Module | Type Signal Characteristic Instrument Tag | | | PLC Tag Name | P&ID No. | Service / Equipment Description | Zone / Floor
32 | C3S02-X2 | C3/S2 | C3S02,26 | 1756-IB32-26 | DI | - | Spare | Spare_DI_0 | 3-25-01-613-PD-01 | Spare I/O Point | Packing Tower / ...
33 | C3S02-X2 | C3/S2 | C3S02,27 | 1756-IB32-27 | DI | - | Spare | Spare_DI_0 | 3-25-01-613-PD-01 | Spare I/O Point | Packing Tower / ...
34 | C3S02-X2 | C3/S2 | C3S02,28 | 1756-IB32-28 | DI | - | Spare | Spare_DI_0 | 3-25-01-613-PD-01 | Spare I/O Point | Packing Tower / ...
35 | C3S02-X2 | C3/S2 | C3S02,29 | 1756-IB32-29 | DI | - | Spare | Spare_DI_0 | 3-25-01-613-PD-01 | Spare I/O Point | Packing Tower / ...
36 | C3S02-X2 | C3/S2 | C3S02,30 | 1756-IB32-30 | DI | - | Spare | Spare_DI_0 | 3-25-01-613-PD-01 | Spare I/O Point | Packing Tower / ...
37 | C3S02-X2 | C3/S2 | C3S02,31 | 1756-IB32-31 | DI | - | Spare | Spare_DI_0 | 3-25-01-613-PD-01 | Spare I/O Point | Packing Tower / ...
38 | C3S05-X1 | C3/S5 | C3S05,13 | 1756-IF16-13 | AI | - | Spare | Spare_AI_0 | - | Spare I/O Point | -
39 | C3S05-X1 | C3/S5 | C3S05,14 | 1756-IF16-14 | AI | - | Spare | Spare_AI_0 | - | Spare I/O Point | -
40 | C3S05-X1 | C3/S5 | C3S05,15 | 1756-IF16-15 | AI | - | Spare | Spare_AI_0 | - | Spare I/O Point | -
41 | C3S05-X1 | C3/S5 | C3S05,11 | 1756-IF16-11 | AI | 4 - 20 mA | TT-61301 | TT-61301_AI_1 | 3-25-01-613-PD-01 | 0 | Packing Tower / ...
42 | C3S05-X1 | C3/S5 | C3S05,12 | 1756-IF16-12 | AI | 4 - 20 mA | TT-61302 | TT-61302_AI_1 | 3-25-01-613-PD-01 | 0 | Packing Tower / ...
43 | C3S02-X1 | C3/S2 | C3S02,11 | 1756-IB32-11 | DI | Dry Contact | ZS-61310 | ZS-61310_DI_1 | 3-25-01-613-PD-01 | 0 | Packing Tower / ...
44 | C3S02-X1 | C3/S2 | C3S02,12 | 1756-IB32-12 | DI | Dry Contact | ZS-61311 | ZS-61311_DI_1 | 3-25-01-613-PD-01 | 0 | Packing Tower / ...
Doc No.: Instrument I/O List (Kalasin) - IS-JB-618 | Page 2 of 2 | CONFIDENTIAL | Generated: 2026-09-07
