x92120/x260911-002-KalasinEngineering/02_Electrical_and_eDrawing/04_PDF_Reports_and_Drawings/JB_Report_JB-402.pdf

INGREDION (THAILAND) CO., LTD. | PROJECT JET COOKER | AEC INDUSTRIAL ENGINEERING | REV. 3.6
ENCLOSURE: JB-402 | TYPE: Field Junction Box (Standard) | LOCATION: Jet Cooker 2nd Floor | SIZE: 450-300-150 mm
SUMMARY: Total Channels: 65 | Active: 41 | Spare: 24 (36.9%) | DI: 32 | DO: 16 | AI: 16 | AO: 1 | BUS: 0
No. | Terminal | Rack/Slot | Channel | I/O Module | Type Signal Characteristic Instrument Tag | | | PLC Tag Name | P&ID No. | Service / Equipment Description | Zone / Floor
1 | C2S01-X1 | C2/S1 | C2S01,00 | 1756-IB32-0 | DI | Dry Contact | FS-40204 | FS-40204_DI_1 | 325-01-402-PD-01 | Flow Switch | Jet Cooker / 2nd
2 | C2S01-X1 | C2/S1 | C2S01,01 | 1756-IB32-1 | DI | Dry Contact | FS-40205 | FS-40205_DI_1 | 325-01-402-PD-02 | Flow Switch | Jet Cooker / 2nd
3 | C2S01-X1 | C2/S1 | C2S01,02 | 1756-IB32-2 | DI | 4 - 20 mA,Pulse | FT-40221 | FT-40221_DI_1 | 325-01-402-PD-02 | Coriolis Flow Transmitter | Jet Cooker / 2nd
4 | C2S09-X1 | C2/S9 | C2S09,00 | 1756-IF16-0 | AI | 4 - 20 mA,Pulse | FT-40221 | FT-40221_AI_1 | 325-01-402-PD-02 | Coriolis Flow Transmitter | Jet Cooker / 2nd
5 | C2S09-X1 | C2/S9 | C2S09,01 | 1756-IF16-1 | AI | 4 - 20 mA,Pulse | FT-40221 | FT-40221_AI_2 | 325-01-402-PD-02 | Coriolis Flow Transmitter | Jet Cooker / 2nd
6 | C2S01-X1 | C2/S1 | C2S01,03 | 1756-IB32-3 | DI | 4 - 20 mA,Pulse | FT-40222 | FT-40222_DI_1 | 325-01-402-PD-02 | Coriolis Flow Transmitter | Jet Cooker / 2nd
7 | C2S09-X1 | C2/S9 | C2S09,02 | 1756-IF16-2 | AI | 4 - 20 mA,Pulse | FT-40222 | FT-40222_AI_1 | 325-01-402-PD-02 | Coriolis Flow Transmitter | Jet Cooker / 2nd
8 | C2S09-X1 | C2/S9 | C2S09,03 | 1756-IF16-3 | AI | 4 - 20 mA,Pulse | FT-40222 | FT-40222_AI_2 | 325-01-402-PD-02 | Coriolis Flow Transmitter | Jet Cooker / 2nd
9 | C2S01-X1 | C2/S1 | C2S01,04 | 1756-IB32-4 | DI | Dry Contact | HV-40207 | HV-40207_DI_1 | 325-01-402-PD-01 | Manual Valve With Position Switch | Jet Cooker / 2nd
10 | C2S01-X1 | C2/S1 | C2S01,05 | 1756-IB32-5 | DI | Dry Contact | HV-40208 | HV-40208_DI_1 | 325-01-402-PD-01 | Manual Valve With Position Switch | Jet Cooker / 2nd
11 | C2S09-X1 | C2/S9 | C2S09,04 | 1756-IF16-4 | AI | 4 - 20 mA | PT-40222 | PT-40222_AI_1 | 325-01-402-PD-02 | Pressure Transmitter | Jet Cooker / 2nd
12 | C2S01-X2 | C2/S1 | C2S01,24 | 1756-IB32-24 | DI | - | Spare | Spare_DI_2 | - | Spare I/O Point | Jet Cooker / 2nd
13 | C2S01-X2 | C2/S1 | C2S01,25 | 1756-IB32-25 | DI | - | Spare | Spare_DI_2 | - | Spare I/O Point | Jet Cooker / 2nd
14 | C2S01-X2 | C2/S1 | C2S01,26 | 1756-IB32-26 | DI | - | Spare | Spare_DI_2 | - | Spare I/O Point | Jet Cooker / 2nd
15 | C2S01-X2 | C2/S1 | C2S01,27 | 1756-IB32-27 | DI | - | Spare | Spare_DI_2 | - | Spare I/O Point | Jet Cooker / 2nd
16 | C2S01-X2 | C2/S1 | C2S01,28 | 1756-IB32-28 | DI | - | Spare | Spare_DI_2 | - | Spare I/O Point | Jet Cooker / 2nd
17 | C2S01-X2 | C2/S1 | C2S01,29 | 1756-IB32-29 | DI | - | Spare | Spare_DI_2 | - | Spare I/O Point | Jet Cooker / 2nd
18 | C2S01-X2 | C2/S1 | C2S01,30 | 1756-IB32-30 | DI | - | Spare | Spare_DI_2 | - | Spare I/O Point | Jet Cooker / 2nd
19 | C2S01-X2 | C2/S1 | C2S01,31 | 1756-IB32-31 | DI | - | Spare | Spare_DI_2 | - | Spare I/O Point | Jet Cooker / 2nd
20 | C2S06-X1 | C2/S6 | C2S06,09 | 1756-OB32-9 | DO | - | Spare | Spare_DO_0 | - | Spare I/O Point | -
21 | C2S06-X1 | C2/S6 | C2S06,10 | 1756-OB32-10 | DO | - | Spare | Spare_DO_0 | - | Spare I/O Point | -
22 | C2S06-X1 | C2/S6 | C2S06,11 | 1756-OB32-11 | DO | - | Spare | Spare_DO_0 | - | Spare I/O Point | -
23 | C2S06-X1 | C2/S6 | C2S06,12 | 1756-OB32-12 | DO | - | Spare | Spare_DO_0 | - | Spare I/O Point | -
24 | C2S06-X1 | C2/S6 | C2S06,13 | 1756-OB32-13 | DO | - | Spare | Spare_DO_0 | - | Spare I/O Point | -
25 | C2S06-X1 | C2/S6 | C2S06,14 | 1756-OB32-14 | DO | - | Spare | Spare_DO_0 | - | Spare I/O Point | -
26 | C2S06-X1 | C2/S6 | C2S06,15 | 1756-OB32-15 | DO | - | Spare | Spare_DO_0 | - | Spare I/O Point | -
27 | C2S09-X1 | C2/S9 | C2S09,07 | 1756-IF16-7 | AI | - | Spare | Spare_AI_0 | - | Spare I/O Point | -
28 | C2S09-X1 | C2/S9 | C2S09,08 | 1756-IF16-8 | AI | - | Spare | Spare_AI_0 | - | Spare I/O Point | -
29 | C2S09-X1 | C2/S9 | C2S09,09 | 1756-IF16-9 | AI | - | Spare | Spare_AI_0 | - | Spare I/O Point | -
30 | C2S09-X1 | C2/S9 | C2S09,10 | 1756-IF16-10 | AI | - | Spare | Spare_AI_0 | - | Spare I/O Point | -
31 | C2S09-X1 | C2/S9 | C2S09,11 | 1756-IF16-11 | AI | - | Spare | Spare_AI_0 | - | Spare I/O Point | -
Doc No.: Instrument I/O List (Kalasin) - JB-402 | Page 1 of 3 | CONFIDENTIAL | Generated: 2026-09-07

ENCLOSURE: JB-402 | TYPE: Field Junction Box (Standard) | LOCATION: Jet Cooker 2nd Floor | SIZE: 450-300-150 mm
SUMMARY: Total Channels: 65 | Active: 41 | Spare: 24 (36.9%) | DI: 32 | DO: 16 | AI: 16 | AO: 1 | BUS: 0
No. | Terminal | Rack/Slot | Channel | I/O Module | Type Signal Characteristic Instrument Tag | | | PLC Tag Name | P&ID No. | Service / Equipment Description | Zone / Floor
32 | C2S09-X1 | C2/S9 | C2S09,12 | 1756-IF16-12 | AI | - | Spare | Spare_AI_0 | - | Spare I/O Point | -
33 | C2S09-X1 | C2/S9 | C2S09,13 | 1756-IF16-13 | AI | - | Spare | Spare_AI_0 | - | Spare I/O Point | -
34 | C2S09-X1 | C2/S9 | C2S09,14 | 1756-IF16-14 | AI | - | Spare | Spare_AI_0 | - | Spare I/O Point | -
35 | C2S09-X1 | C2/S9 | C2S09,15 | 1756-IF16-15 | AI | - | Spare | Spare_AI_0 | - | Spare I/O Point | -
36 | C3S13-X1 | C3/S13 | C3S13,00 | 1756-OF8-0 | AO | 4 - 20 mA | TCV-40222 | TCV-40222_AO_1 | 325-01-402-PD-02 | 0 | Jet Cooker / 2nd
37 | C2S09-X1 | C2/S9 | C2S09,05 | 1756-IF16-5 | AI | 4 - 20 mA | TT-40221 | TT-40221_AI_1 | 325-01-402-PD-02 | 0 | Jet Cooker / 2nd
38 | C2S09-X1 | C2/S9 | C2S09,06 | 1756-IF16-6 | AI | 4 - 20 mA | TT-40222 | TT-40222_AI_1 | 325-01-402-PD-02 | 0 | Jet Cooker / 2nd
39 | C2S01-X1 | C2/S1 | C2S01,06 | 1756-IB32-6 | DI | 24 VDC energized | XV-40203F | XV-40203F_DI_1 | 325-01-402-PD-02 | 0 | Jet Cooker / 2nd
40 | C2S01-X1 | C2/S1 | C2S01,07 | 1756-IB32-7 | DI | 24 VDC energized | XV-40203F | XV-40203F_DI_2 | 325-01-402-PD-02 | 0 | Jet Cooker / 2nd
41 | C2S06-X1 | C2/S6 | C2S06,00 | 1756-OB32-0 | DO | 24 VDC energized | XV-40203F | XV-40203F_DO_1 | 325-01-402-PD-02 | 0 | Jet Cooker / 2nd
42 | C2S01-X1 | C2/S1 | C2S01,08 | 1756-IB32-8 | DI | 24 VDC energized | XV-40204B | XV-40204B_DI_1 | 325-01-402-PD-01 | 0 | Jet Cooker / 2nd
43 | C2S01-X1 | C2/S1 | C2S01,09 | 1756-IB32-9 | DI | 24 VDC energized | XV-40204B | XV-40204B_DI_2 | 325-01-402-PD-01 | 0 | Jet Cooker / 2nd
44 | C2S06-X1 | C2/S6 | C2S06,01 | 1756-OB32-1 | DO | 24 VDC energized | XV-40204B | XV-40204B_DO_1 | 325-01-402-PD-01 | 0 | Jet Cooker / 2nd
45 | C2S01-X1 | C2/S1 | C2S01,10 | 1756-IB32-10 | DI | 24 VDC energized | XV-40204C | XV-40204C_DI_1 | 325-01-402-PD-01 | 0 | Jet Cooker / 2nd
46 | C2S01-X1 | C2/S1 | C2S01,11 | 1756-IB32-11 | DI | 24 VDC energized | XV-40204C | XV-40204C_DI_2 | 325-01-402-PD-01 | 0 | Jet Cooker / 2nd
47 | C2S06-X1 | C2/S6 | C2S06,02 | 1756-OB32-2 | DO | 24 VDC energized | XV-40204C | XV-40204C_DO_1 | 325-01-402-PD-01 | 0 | Jet Cooker / 2nd
48 | C2S01-X1 | C2/S1 | C2S01,12 | 1756-IB32-12 | DI | 24 VDC energized | XV-40205A | XV-40205A_DI_1 | 325-01-402-PD-02 | 0 | Jet Cooker / 2nd
49 | C2S01-X1 | C2/S1 | C2S01,13 | 1756-IB32-13 | DI | 24 VDC energized | XV-40205A | XV-40205A_DI_2 | 325-01-402-PD-02 | 0 | Jet Cooker / 2nd
50 | C2S06-X1 | C2/S6 | C2S06,03 | 1756-OB32-3 | DO | 24 VDC energized | XV-40205A | XV-40205A_DO_1 | 325-01-402-PD-02 | 0 | Jet Cooker / 2nd
51 | C2S01-X1 | C2/S1 | C2S01,14 | 1756-IB32-14 | DI | 24 VDC energized | XV-40205B | XV-40205B_DI_1 | 325-01-402-PD-02 | 0 | Jet Cooker / 2nd
52 | C2S01-X1 | C2/S1 | C2S01,15 | 1756-IB32-15 | DI | 24 VDC energized | XV-40205B | XV-40205B_DI_2 | 325-01-402-PD-02 | 0 | Jet Cooker / 2nd
53 | C2S06-X1 | C2/S6 | C2S06,04 | 1756-OB32-4 | DO | 24 VDC energized | XV-40205B | XV-40205B_DO_1 | 325-01-402-PD-02 | 0 | Jet Cooker / 2nd
54 | C2S01-X2 | C2/S1 | C2S01,16 | 1756-IB32-16 | DI | 24 VDC energized | XV-40205C | XV-40205C_DI_1 | 325-01-402-PD-02 | 0 | Jet Cooker / 2nd
55 | C2S01-X2 | C2/S1 | C2S01,17 | 1756-IB32-17 | DI | 24 VDC energized | XV-40205C | XV-40205C_DI_2 | 325-01-402-PD-02 | 0 | Jet Cooker / 2nd
56 | C2S06-X1 | C2/S6 | C2S06,05 | 1756-OB32-5 | DO | 24 VDC energized | XV-40205C | XV-40205C_DO_1 | 325-01-402-PD-02 | 0 | Jet Cooker / 2nd
57 | C2S01-X2 | C2/S1 | C2S01,18 | 1756-IB32-18 | DI | 24 VDC energized | XV-40205D | XV-40205D_DI_1 | 325-01-402-PD-02 | 0 | Jet Cooker / 2nd
58 | C2S01-X2 | C2/S1 | C2S01,19 | 1756-IB32-19 | DI | 24 VDC energized | XV-40205D | XV-40205D_DI_2 | 325-01-402-PD-02 | 0 | Jet Cooker / 2nd
59 | C2S06-X1 | C2/S6 | C2S06,06 | 1756-OB32-6 | DO | 24 VDC energized | XV-40205D | XV-40205D_DO_1 | 325-01-402-PD-02 | 0 | Jet Cooker / 2nd
60 | C2S01-X2 | C2/S1 | C2S01,20 | 1756-IB32-20 | DI | 24 VDC energized | XV-40205F | XV-40205F_DI_1 | 325-01-402-PD-02 | 0 | Jet Cooker / 2nd
61 | C2S01-X2 | C2/S1 | C2S01,21 | 1756-IB32-21 | DI | 24 VDC energized | XV-40205F | XV-40205F_DI_2 | 325-01-402-PD-02 | 0 | Jet Cooker / 2nd
62 | C2S06-X1 | C2/S6 | C2S06,07 | 1756-OB32-7 | DO | 24 VDC energized | XV-40205F | XV-40205F_DO_1 | 325-01-402-PD-02 | 0 | Jet Cooker / 2nd
Doc No.: Instrument I/O List (Kalasin) - JB-402 | Page 2 of 3 | CONFIDENTIAL | Generated: 2026-09-07

ENCLOSURE: JB-402 | TYPE: Field Junction Box (Standard) | LOCATION: Jet Cooker 2nd Floor | SIZE: 450-300-150 mm
SUMMARY: Total Channels: 65 | Active: 41 | Spare: 24 (36.9%) | DI: 32 | DO: 16 | AI: 16 | AO: 1 | BUS: 0
No. | Terminal | Rack/Slot | Channel | I/O Module | Type Signal Characteristic Instrument Tag | | | PLC Tag Name | P&ID No. | Service / Equipment Description | Zone / Floor
63 | C2S01-X2 | C2/S1 | C2S01,22 | 1756-IB32-22 | DI | 24 VDC energized | XV-40222 | XV-40222_DI_1 | 325-01-402-PD-02 | 0 | Jet Cooker / 2nd
64 | C2S01-X2 | C2/S1 | C2S01,23 | 1756-IB32-23 | DI | 24 VDC energized | XV-40222 | XV-40222_DI_2 | - | 0 | Jet Cooker / 2nd
65 | C2S06-X1 | C2/S6 | C2S06,08 | 1756-OB32-8 | DO | 24 VDC energized | XV-40222 | XV-40222_DO_1 | 325-01-402-PD-02 | 0 | Jet Cooker / 2nd
Doc No.: Instrument I/O List (Kalasin) - JB-402 | Page 3 of 3 | CONFIDENTIAL | Generated: 2026-09-07
