x92120/x260911-002-KalasinEngineering/02_Electrical_and_eDrawing/04_PDF_Reports_and_Drawings/JB_Report_JB-602.pdf

INGREDION (THAILAND) CO., LTD. | PROJECT JET COOKER | AEC INDUSTRIAL ENGINEERING | REV. 3.6
ENCLOSURE: JB-602 | TYPE: Field Junction Box (Standard) | LOCATION: Spray Dryer 3rd Floor | SIZE: 800-600-250 mm
SUMMARY: Total Channels: 82 | Active: 57 | Spare: 25 (30.5%) | DI: 32 | DO: 16 | AI: 32 | AO: 2 | BUS: 0
No. | Terminal | Rack/Slot | Channel | I/O Module | Type Signal Characteristic Instrument Tag | | | PLC Tag Name | P&ID No. | Service / Equipment Description | Zone / Floor
1 | C2S10-X1 | C2/S10 | C2S10,00 | 1756-IF16-0 | AI | 4 - 20 mA | AT-60241 | AT-60241_AI_1 | 3-25-01-602-PD-05 | Dust Analyzer Transmitter | Spray Dryer / 5th
2 | C2S10-X1 | C2/S10 | C2S10,01 | 1756-IF16-1 | AI | 4 - 20 mA | DPT-60203 | DPT-60203_AI_1 | 3-25-01-602-PD-03 | Differential Pressure Transmitte | Spray Dryer / 5th
3 | C2S02-X1 | C2/S2 | C2S02,00 | 1756-IB32-0 | DI | 4 - 20 mA | FT-60202 | FT-60202_DI_1 | 3-25-01-602-PD-09 | 0 | Spray Dryer / 5th
4 | C2S10-X1 | C2/S10 | C2S10,02 | 1756-IF16-2 | AI | 4 - 20 mA | FT-60202 | FT-60202_AI_1 | 3-25-01-602-PD-09 | 0 | Spray Dryer / 5th
5 | C2S11-X1 | C2/S11 | C2S11,09 | 1756-IF16-9 | AI | 4 - 20 mA | FT-60210 | FT-60210_AI_1 | 3-25-01-602-PD-03 | 0 | Spray Dryer / 5th
6 | C2S11-X1 | C2/S11 | C2S11,11 | 1756-IF16-11 | AI | 4 - 20 mA | FT-60210 | FT-60210_AI_2 | 3-25-01-602-PD-03 | 0 | Spray Dryer / 5th
7 | C2S11-X1 | C2/S11 | C2S11,10 | 1756-IF16-10 | AI | 4 - 20 mA | FT-60211 | FT-60211_AI_1 | 3-25-01-602-PD-03 | 0 | Spray Dryer / 5th
8 | C2S11-X1 | C2/S11 | C2S11,12 | 1756-IF16-12 | AI | 4 - 20 mA | FT-60211 | FT-60211_AI_2 | 3-25-01-602-PD-03 | 0 | Spray Dryer / 5th
9 | C2S02-X1 | C2/S2 | C2S02,01 | 1756-IB32-1 | DI | Dry Contact | LSH-60251 | LSH-60251_DI_1 | 3-25-01-602-PD-04 | 0 | Spray Dryer / 4th
10 | C2S02-X1 | C2/S2 | C2S02,02 | 1756-IB32-2 | DI | Dry Contact | PSL-60220 | PSL-60220_DI_1 | 3-25-01-602-PD-04 | 0 | Spray Dryer / 5th
11 | C2S10-X1 | C2/S10 | C2S10,03 | 1756-IF16-3 | AI | 4 - 20 mA | PT-60210 | PT-60210_AI_1 | 3-25-01-602-PD-03 | Pressure Transmitter | Spray Dryer / 5th
12 | C2S10-X1 | C2/S10 | C2S10,04 | 1756-IF16-4 | AI | 4 - 20 mA | PT-60215 | PT-60215_AI_1 | 3-25-01-602-PD-03 | Pressure Transmitter | Spray Dryer / 5th
13 | C2S10-X1 | C2/S10 | C2S10,05 | 1756-IF16-5 | AI | 4 - 20 mA | PT-60216 | PT-60216_AI_1 | 3-25-01-602-PD-03 | Pressure Transmitter | Spray Dryer / 5th
14 | C2S10-X1 | C2/S10 | C2S10,06 | 1756-IF16-6 | AI | 4 - 20 mA | PT-60240 | PT-60240_AI_1 | 3-25-01-602-PD-05 | Pressure Transmitter | Spray Dryer / 5th
15 | C2S10-X1 | C2/S10 | C2S10,07 | 1756-IF16-7 | AI | 4 - 20 mA | PT-60241 | PT-60241_AI_1 | 3-25-01-602-PD-05 | Pressure Transmitter | Spray Dryer / 5th
16 | C2S02-X2 | C2/S2 | C2S02,23 | 1756-IB32-23 | DI | - | Spare | Spare_DI_0 | - | Spare I/O Point | -
17 | C2S02-X2 | C2/S2 | C2S02,24 | 1756-IB32-24 | DI | - | Spare | Spare_DI_0 | - | Spare I/O Point | -
18 | C2S02-X2 | C2/S2 | C2S02,25 | 1756-IB32-25 | DI | - | Spare | Spare_DI_0 | - | Spare I/O Point | -
19 | C2S02-X2 | C2/S2 | C2S02,26 | 1756-IB32-26 | DI | - | Spare | Spare_DI_0 | - | Spare I/O Point | -
20 | C2S02-X2 | C2/S2 | C2S02,27 | 1756-IB32-27 | DI | - | Spare | Spare_DI_0 | - | Spare I/O Point | -
21 | C2S02-X2 | C2/S2 | C2S02,28 | 1756-IB32-28 | DI | - | Spare | Spare_DI_0 | - | Spare I/O Point | -
22 | C2S02-X2 | C2/S2 | C2S02,29 | 1756-IB32-29 | DI | - | Spare | Spare_DI_0 | - | Spare I/O Point | -
23 | C2S02-X2 | C2/S2 | C2S02,30 | 1756-IB32-30 | DI | - | Spare | Spare_DI_0 | - | Spare I/O Point | -
24 | C2S02-X2 | C2/S2 | C2S02,31 | 1756-IB32-31 | DI | - | Spare | Spare_DI_0 | - | Spare I/O Point | -
25 | C2S06-X2 | C2/S6 | C2S06,19 | 1756-OB32-19 | DO | - | Spare | Spare_DO_0 | - | Spare I/O Point | Spray Dryer
26 | C2S06-X2 | C2/S6 | C2S06,20 | 1756-OB32-20 | DO | - | Spare | Spare_DO_0 | - | Spare I/O Point | Spray Dryer
27 | C2S06-X2 | C2/S6 | C2S06,21 | 1756-OB32-21 | DO | - | Spare | Spare_DO_0 | - | Spare I/O Point | Spray Dryer
28 | C2S06-X2 | C2/S6 | C2S06,22 | 1756-OB32-22 | DO | - | Spare | Spare_DO_0 | - | Spare I/O Point | Spray Dryer
29 | C2S06-X2 | C2/S6 | C2S06,23 | 1756-OB32-23 | DO | - | Spare | Spare_DO_0 | - | Spare I/O Point | Spray Dryer
30 | C2S06-X2 | C2/S6 | C2S06,24 | 1756-OB32-24 | DO | - | Spare | Spare_DO_0 | - | Spare I/O Point | Spray Dryer
31 | C2S06-X2 | C2/S6 | C2S06,25 | 1756-OB32-25 | DO | - | Spare | Spare_DO_0 | - | Spare I/O Point | Spray Dryer
Doc No.: Instrument I/O List (Kalasin) - JB-602 | Page 1 of 3 | CONFIDENTIAL | Generated: 2026-09-07

ENCLOSURE: JB-602 | TYPE: Field Junction Box (Standard) | LOCATION: Spray Dryer 3rd Floor | SIZE: 800-600-250 mm
SUMMARY: Total Channels: 82 | Active: 57 | Spare: 25 (30.5%) | DI: 32 | DO: 16 | AI: 32 | AO: 2 | BUS: 0
No. | Terminal | Rack/Slot | Channel | I/O Module | Type Signal Characteristic Instrument Tag | | | PLC Tag Name | P&ID No. | Service / Equipment Description | Zone / Floor
32 | C2S06-X2 | C2/S6 | C2S06,26 | 1756-OB32-26 | DO | - | Spare | Spare_DO_0 | - | Spare I/O Point | Spray Dryer
33 | C2S06-X2 | C2/S6 | C2S06,27 | 1756-OB32-27 | DO | - | Spare | Spare_DO_0 | - | Spare I/O Point | Spray Dryer
34 | C2S06-X2 | C2/S6 | C2S06,28 | 1756-OB32-28 | DO | - | Spare | Spare_DO_0 | - | Spare I/O Point | Spray Dryer
35 | C2S06-X2 | C2/S6 | C2S06,29 | 1756-OB32-29 | DO | - | Spare | Spare_DO_0 | - | Spare I/O Point | Spray Dryer
36 | C2S06-X2 | C2/S6 | C2S06,30 | 1756-OB32-30 | DO | - | Spare | Spare_DO_0 | - | Spare I/O Point | Spray Dryer
37 | C2S06-X2 | C2/S6 | C2S06,31 | 1756-OB32-31 | DO | - | Spare | Spare_DO_0 | - | Spare I/O Point | Spray Dryer
38 | C2S11-X1 | C2/S11 | C2S11,13 | 1756-IF16-13 | AI | - | Spare | Spare_AI_0 | - | Spare I/O Point | -
39 | C2S11-X1 | C2/S11 | C2S11,14 | 1756-IF16-14 | AI | - | Spare | Spare_AI_0 | - | Spare I/O Point | -
40 | C2S11-X1 | C2/S11 | C2S11,15 | 1756-IF16-15 | AI | - | Spare | Spare_AI_0 | - | Spare I/O Point | -
41 | C2S02-X1 | C2/S2 | C2S02,03 | 1756-IB32-3 | DI | Dry Contact | TSH-60230 | TSH-60230_DI_1 | 3-25-01-602-PD-04 | 0 | Spray Dryer / 3rd
42 | C2S02-X1 | C2/S2 | C2S02,04 | 1756-IB32-4 | DI | Dry Contact | TSH-60240 | TSH-60240_DI_1 | 3-25-01-602-PD-05 | 0 | Spray Dryer / 5th
43 | C2S02-X1 | C2/S2 | C2S02,05 | 1756-IB32-5 | DI | Dry Contact | TSH-60241A | TSH-60241A_DI_1 | 3-25-01-602-PD-05 | 0 | Spray Dryer / 4th
44 | C2S02-X1 | C2/S2 | C2S02,06 | 1756-IB32-6 | DI | Dry Contact | TSH-60242A | TSH-60242A_DI_1 | 3-25-01-602-PD-05 | 0 | Spray Dryer / 3rd
45 | C2S02-X1 | C2/S2 | C2S02,07 | 1756-IB32-7 | DI | Dry Contact | TSH-60243A | TSH-60243A_DI_1 | 3-25-01-602-PD-05 | 0 | Spray Dryer / 4th
46 | C2S02-X1 | C2/S2 | C2S02,08 | 1756-IB32-8 | DI | Dry Contact | TSL-60241B | TSL-60241B_DI_1 | 3-25-01-602-PD-05 | 0 | Spray Dryer / 4th
47 | C2S02-X1 | C2/S2 | C2S02,09 | 1756-IB32-9 | DI | Dry Contact | TSL-60242B | TSL-60242B_DI_1 | 3-25-01-602-PD-05 | 0 | Spray Dryer / 3rd
48 | C2S02-X1 | C2/S2 | C2S02,10 | 1756-IB32-10 | DI | Dry Contact | TSL-60243B | TSL-60243B_DI_1 | 3-25-01-602-PD-05 | 0 | Spray Dryer / 4th
49 | C2S10-X1 | C2/S10 | C2S10,08 | 1756-IF16-8 | AI | 4 - 20 mA | TT-60210 | TT-60210_AI_1 | 3-25-01-602-PD-03 | 0 | Spray Dryer / 5th
50 | C2S10-X1 | C2/S10 | C2S10,09 | 1756-IF16-9 | AI | - | TT-60210A | TT-60210A_AI_1 | 325-01-600-PD-03 | - | Spray Dryer / 5th
51 | C2S10-X1 | C2/S10 | C2S10,10 | 1756-IF16-10 | AI | - | TT-60210B | TT-60210B_AI_1 | 325-01-600-PD-03 | - | Spray Dryer / 5th
52 | C2S10-X1 | C2/S10 | C2S10,11 | 1756-IF16-11 | AI | 4 - 20 mA | TT-60211 | TT-60211_AI_1 | 3-25-01-602-PD-03 | 0 | Spray Dryer / 5th
53 | C2S10-X1 | C2/S10 | C2S10,12 | 1756-IF16-12 | AI | 4 - 20 mA | TT-60212A | TT-60212A_AI_1 | 3-25-01-602-PD-03 | 0 | Spray Dryer / 5th
54 | C2S10-X1 | C2/S10 | C2S10,13 | 1756-IF16-13 | AI | 4 - 20 mA | TT-60212B | TT-60212B_AI_1 | 3-25-01-602-PD-03 | 0 | Spray Dryer / 5th
55 | C2S10-X1 | C2/S10 | C2S10,14 | 1756-IF16-14 | AI | 4 - 20 mA | TT-60214 | TT-60214_AI_1 | 3-25-01-602-PD-03 | 0 | Spray Dryer / 5th
56 | C2S10-X1 | C2/S10 | C2S10,15 | 1756-IF16-15 | AI | 4 - 20 mA | TT-60215A | TT-60215A_AI_1 | 3-25-01-602-PD-03 | 0 | Spray Dryer / 5th
57 | C2S11-X1 | C2/S11 | C2S11,00 | 1756-IF16-0 | AI | 4 - 20 mA | TT-60215B | TT-60215B_AI_1 | 3-25-01-602-PD-03 | 0 | Spray Dryer / 5th
58 | C2S11-X1 | C2/S11 | C2S11,01 | 1756-IF16-1 | AI | 4 - 20 mA | TT-60216 | TT-60216_AI_1 | 3-25-01-602-PD-03 | 0 | Spray Dryer / 5th
59 | C2S11-X1 | C2/S11 | C2S11,02 | 1756-IF16-2 | AI | 4 - 20 mA | TT-60240 | TT-60240_AI_1 | 3-25-01-602-PD-05 | 0 | Spray Dryer / 5th
60 | C2S11-X1 | C2/S11 | C2S11,03 | 1756-IF16-3 | AI | 4 - 20 mA | TT-60241A | TT-60241A_AI_1 | 3-25-01-602-PD-05 | 0 | Spray Dryer / 5th
61 | C2S11-X1 | C2/S11 | C2S11,04 | 1756-IF16-4 | AI | 4 - 20 mA | TT-60241B | TT-60241B_AI_1 | 3-25-01-602-PD-05 | 0 | Spray Dryer / 5th
62 | C3S13-X1 | C3/S13 | C3S13,01 | 1756-OF8-1 | AO | - | TV-60202 | TV-60202_AO_1 | 3-25-01-602-PD-07 | - | Spray Dryer / 3rd
Doc No.: Instrument I/O List (Kalasin) - JB-602 | Page 2 of 3 | CONFIDENTIAL | Generated: 2026-09-07

ENCLOSURE: JB-602 | TYPE: Field Junction Box (Standard) | LOCATION: Spray Dryer 3rd Floor | SIZE: 800-600-250 mm
SUMMARY: Total Channels: 82 | Active: 57 | Spare: 25 (30.5%) | DI: 32 | DO: 16 | AI: 32 | AO: 2 | BUS: 0
No. | Terminal | Rack/Slot | Channel | I/O Module | Type Signal Characteristic Instrument Tag | | | PLC Tag Name | P&ID No. | Service / Equipment Description | Zone / Floor
63 | C3S13-X1 | C3/S13 | C3S13,02 | 1756-OF8-2 | AO | - | TV-60214 | TV-60214_AO_1 | 3-25-01-602-PD-03 | - | Spray Dryer / 5th
64 | C2S11-X1 | C2/S11 | C2S11,05 | 1756-IF16-5 | AI | 4 - 20 mA | VT-60210A | VT-60210A_AI_1 | 3-25-01-602-PD-03 | 0 | Spray Dryer / 5th
65 | C2S11-X1 | C2/S11 | C2S11,06 | 1756-IF16-6 | AI | 4 - 20 mA | VT-60210B | VT-60210B_AI_1 | 3-25-01-602-PD-03 | 0 | Spray Dryer / 5th
66 | C2S11-X1 | C2/S11 | C2S11,07 | 1756-IF16-7 | AI | 4 - 20 mA | VT-60241A | VT-60241A_AI_1 | 3-25-01-602-PD-05 | 0 | Spray Dryer / 5th
67 | C2S11-X1 | C2/S11 | C2S11,08 | 1756-IF16-8 | AI | 4 - 20 mA | VT-60241B | VT-60241B_AI_1 | 3-25-01-602-PD-05 | 0 | Spray Dryer / 5th
68 | C2S02-X1 | C2/S2 | C2S02,11 | 1756-IB32-11 | DI | Dry Contact | XA-60240A | XA-60240A_DI_1 | 325-01-600-PD-05 | 0 | Spray Dryer / 4th
69 | C2S02-X1 | C2/S2 | C2S02,12 | 1756-IB32-12 | DI | Dry Contact | XA-60240B | XA-60240B_DI_1 | 325-01-600-PD-05 | 0 | Spray Dryer / 4th
70 | C2S02-X1 | C2/S2 | C2S02,13 | 1756-IB32-13 | DI | Dry Contact | XA-60241A | XA-60241A_DI_1 | 325-01-600-PD-05 | 0 | Spray Dryer / 4th
71 | C2S02-X1 | C2/S2 | C2S02,14 | 1756-IB32-14 | DI | Dry Contact | XA-60241B | XA-60241B_DI_1 | 325-01-600-PD-05 | 0 | Spray Dryer / 4th
72 | C2S02-X1 | C2/S2 | C2S02,15 | 1756-IB32-15 | DI | Dry Contact | XA-60242A | XA-60242A_DI_1 | 325-01-600-PD-05 | 0 | Spray Dryer / 3rd
73 | C2S02-X2 | C2/S2 | C2S02,16 | 1756-IB32-16 | DI | Dry Contact | XA-60242B | XA-60242B_DI_1 | 325-01-600-PD-05 | 0 | Spray Dryer / 3rd
74 | C2S02-X2 | C2/S2 | C2S02,17 | 1756-IB32-17 | DI | Dry Contact | XA-60243A | XA-60243A_DI_1 | 325-01-600-PD-05 | 0 | Spray Dryer / 4th
75 | C2S02-X2 | C2/S2 | C2S02,18 | 1756-IB32-18 | DI | Dry Contact | XA-60243B | XA-60243B_DI_1 | 325-01-600-PD-05 | 0 | Spray Dryer / 4th
76 | C2S06-X2 | C2/S6 | C2S06,16 | 1756-OB32-16 | DO | Dry Contact | XS-60240B | XS-60240B_DO_1 | 325-01-600-PD-05 | 0 | Spray Dryer / 4th
77 | C2S02-X2 | C2/S2 | C2S02,19 | 1756-IB32-19 | DI | 24 VDC energized | XV-60214 | XV-60214_DI_1 | 3-25-01-602-PD-03 | 0 | Spray Dryer / 5th
78 | C2S02-X2 | C2/S2 | C2S02,20 | 1756-IB32-20 | DI | 24 VDC energized | XV-60214 | XV-60214_DI_2 | 3-25-01-602-PD-03 | 0 | Spray Dryer / 5th
79 | C2S06-X2 | C2/S6 | C2S06,17 | 1756-OB32-17 | DO | 24 VDC energized | XV-60214 | XV-60214_DO_1 | 3-25-01-602-PD-03 | 0 | Spray Dryer / 5th
80 | C2S02-X2 | C2/S2 | C2S02,21 | 1756-IB32-21 | DI | 24 VDC energized,... | XV-60241 | XV-60241_DI_1 | 3-25-01-602-PD-05 | 0 | Spray Dryer / 5th
81 | C2S02-X2 | C2/S2 | C2S02,22 | 1756-IB32-22 | DI | 24 VDC energized,... | XV-60241 | XV-60241_DI_2 | 3-25-01-602-PD-05 | 0 | Spray Dryer / 5th
82 | C2S06-X2 | C2/S6 | C2S06,18 | 1756-OB32-18 | DO | 24 VDC energized,... | XV-60241 | XV-60241_DO_1 | 3-25-01-602-PD-05 | 0 | Spray Dryer / 5th
Doc No.: Instrument I/O List (Kalasin) - JB-602 | Page 3 of 3 | CONFIDENTIAL | Generated: 2026-09-07
