x92120/x260911-002-KalasinEngineering/02_Electrical_and_eDrawing/04_PDF_Reports_and_Drawings/JB_Report_JB-608.pdf

INGREDION (THAILAND) CO., LTD. | PROJECT JET COOKER | AEC INDUSTRIAL ENGINEERING | REV. 3.6
ENCLOSURE: JB-608 | TYPE: Field Junction Box (Standard) | LOCATION: Spray Dryer 8th Floor | SIZE: 300-200-150 mm
SUMMARY: Total Channels: 6 | Active: 1 | Spare: 5 (83.3%) | DI: 0 | DO: 0 | AI: 6 | AO: 0 | BUS: 0
No. | Terminal | Rack/Slot | Channel | I/O Module | Type Signal Characteristic Instrument Tag | | | PLC Tag Name | P&ID No. | Service / Equipment Description | Zone / Floor
1 | C4S05-X1 | C4/S5 | C4S05,03 | 1756-IF16-3 | AI | - | Spare | Spare_AI_0 | - | Spare I/O Point | -
2 | C4S05-X1 | C4/S5 | C4S05,04 | 1756-IF16-4 | AI | - | Spare | Spare_AI_0 | - | Spare I/O Point | -
3 | C4S05-X1 | C4/S5 | C4S05,05 | 1756-IF16-5 | AI | - | Spare | Spare_AI_0 | - | Spare I/O Point | -
4 | C4S05-X1 | C4/S5 | C4S05,06 | 1756-IF16-6 | AI | - | Spare | Spare_AI_0 | - | Spare I/O Point | -
5 | C4S05-X1 | C4/S5 | C4S05,07 | 1756-IF16-7 | AI | - | Spare | Spare_AI_0 | - | Spare I/O Point | -
6 | C4S05-X1 | C4/S5 | C4S05,02 | 1756-IF16-2 | AI | 4 - 20 mA | TT-60245 | TT-60245_AI_1 | 3-25-01-602-PD-05 | 0 | Spray Dryer / 8th
Doc No.: Instrument I/O List (Kalasin) - JB-608 | Page 1 of 1 | CONFIDENTIAL | Generated: 2026-09-07
