x92120/x260911-002-KalasinEngineering/02_Electrical_and_eDrawing/04_PDF_Reports_and_Drawings/JB_Report_RIO-200.pdf

INGREDION (THAILAND) CO., LTD. | PROJECT JET COOKER | AEC INDUSTRIAL ENGINEERING | REV. 3.6
ENCLOSURE: RIO-200 | TYPE: Remote I/O Enclosure (RIO Panel) | LOCATION: Slurry - Out Building 2nd Floor | SIZE: 800-1000-400 mm
SUMMARY: Total Channels: 112 | Active: 57 | Spare: 55 (49.1%) | DI: 64 | DO: 32 | AI: 16 | AO: 0 | BUS: 0
No. | Terminal | Rack/Slot | Channel | I/O Module | Type Signal Characteristic Instrument Tag | | | PLC Tag Name | P&ID No. | Service / Equipment Description | Zone / Floor
1 | C5S04-X1 | C5/S4 | C5S04,00 | 1756-IF16-0 | AI | - | EXT-BIILER | EXT-BIILER_AI_1 | External Remote S... | - | Boiler System / 1st
2 | C5S01-X1 | C5/S1 | C5S01,00 | 1756-IB32-0 | DI | - | FS-20201 | FS-20201_DI_1 | 3-25-01-202-PD-01 | - | Slurry - Out Buildi...
3 | C5S01-X1 | C5/S1 | C5S01,01 | 1756-IB32-1 | DI | 4 - 20 mA,Pulse | FT-913201 | FT-913201_DI_1 | 3-25-01-913-PD-02 | 0 | LPG System / 1st
4 | C5S04-X1 | C5/S4 | C5S04,01 | 1756-IF16-1 | AI | 4 - 20 mA,Pulse | FT-913201 | FT-913201_AI_1 | 3-25-01-913-PD-02 | 0 | LPG System / 1st
5 | C5S04-X1 | C5/S4 | C5S04,02 | 1756-IF16-2 | AI | 4 - 20 mA,Pulse | FT-913201 | FT-913201_AI_2 | 3-25-01-913-PD-02 | 0 | LPG System / 1st
6 | C5S01-X1 | C5/S1 | C5S01,02 | 1756-IB32-2 | DI | 4 - 20 mA,Pulse | FT-936201 | FT-936201_DI_1 | 3-25-01-930-PD-08 | 0 | Process Water / ...
7 | C5S04-X1 | C5/S4 | C5S04,03 | 1756-IF16-3 | AI | 4 - 20 mA,Pulse | FT-936201 | FT-936201_AI_1 | 3-25-01-930-PD-08 | 0 | Process Water / ...
8 | C5S01-X1 | C5/S1 | C5S01,03 | 1756-IB32-3 | DI | 4 - 20 mA,Pulse | FT-936202 | FT-936202_DI_1 | 3-25-01-930-PD-07 | 0 | Process Water / ...
9 | C5S04-X1 | C5/S4 | C5S04,04 | 1756-IF16-4 | AI | 4 - 20 mA,Pulse | FT-936202 | FT-936202_AI_1 | 3-25-01-930-PD-07 | 0 | Process Water / ...
10 | C5S01-X1 | C5/S1 | C5S01,07 | 1756-IB32-7 | DI | Dry Contact | HV-20204 | HV-20204_DI_1 | 3-25-01-202-PD-01 | Manual Valve With Position Switch | Slurry - Out Buildi...
11 | C5S01-X1 | C5/S1 | C5S01,08 | 1756-IB32-8 | DI | Dry Contact | HV-20205 | HV-20205_DI_1 | 3-25-01-202-PD-01 | Manual Valve With Position Switch | Slurry - Out Buildi...
12 | C5S01-X1 | C5/S1 | C5S01,09 | 1756-IB32-9 | DI | Dry Contact | HV-20206 | HV-20206_DI_1 | 3-25-01-202-PD-01 | Manual Valve With Position Switch | Slurry - Out Buildi...
13 | C5S01-X1 | C5/S1 | C5S01,10 | 1756-IB32-10 | DI | Dry Contact | HV-20207 | HV-20207_DI_1 | 3-25-01-202-PD-01 | Manual Valve With Position Switch | Slurry - Out Buildi...
14 | C5S01-X1 | C5/S1 | C5S01,11 | 1756-IB32-11 | DI | Dry Contact | HV-20208 | HV-20208_DI_1 | 3-25-01-202-PD-02 | Manual Valve With Position Switch | Slurry - Out Buildi...
15 | C5S01-X1 | C5/S1 | C5S01,12 | 1756-IB32-12 | DI | Dry Contact | HV-20209 | HV-20209_DI_1 | 3-25-01-202-PD-02 | Manual Valve With Position Switch | Slurry - Out Buildi...
16 | C5S01-X1 | C5/S1 | C5S01,13 | 1756-IB32-13 | DI | Dry Contact | HV-20210 | HV-20210_DI_1 | 3-25-01-202-PD-02 | Manual Valve With Position Switch | Slurry - Out Buildi...
17 | C5S01-X1 | C5/S1 | C5S01,04 | 1756-IB32-4 | DI | Dry Contact | LSL-814201 | LSL-814201_DI_1 | 3-25-01-814-PD-01 | 0 | CIP Water Syste...
18 | C5S04-X1 | C5/S4 | C5S04,05 | 1756-IF16-5 | AI | 4 - 20 mA | LT-913201 | LT-913201_AI_1 | 3-25-01-913-PD-01 | Level Transmitter | LPG System / 1st
19 | C5S01-X1 | C5/S1 | C5S01,05 | 1756-IB32-5 | DI | - | PK-913201 | PK-913201_DI_1 | - | - | LPG System / 1st
20 | C5S01-X1 | C5/S1 | C5S01,06 | 1756-IB32-6 | DI | - | PK-913202 | PK-913202_DI_1 | - | - | LPG System / 1st
21 | C5S04-X1 | C5/S4 | C5S04,06 | 1756-IF16-6 | AI | 4 - 20 mA | PT-913201 | PT-913201_AI_1 | 3-25-01-913-PD-02 | Pressure Transmitter | LPG System / 1st
22 | C5S02-X1 | C5/S2 | C5S02,08 | 1756-IB32-8 | DI | - | Spare | Spare_DI_0 | - | Spare I/O Point | -
23 | C5S02-X1 | C5/S2 | C5S02,09 | 1756-IB32-9 | DI | - | Spare | Spare_DI_0 | - | Spare I/O Point | -
24 | C5S02-X1 | C5/S2 | C5S02,10 | 1756-IB32-10 | DI | - | Spare | Spare_DI_0 | - | Spare I/O Point | -
25 | C5S02-X1 | C5/S2 | C5S02,11 | 1756-IB32-11 | DI | - | Spare | Spare_DI_0 | - | Spare I/O Point | -
26 | C5S02-X1 | C5/S2 | C5S02,12 | 1756-IB32-12 | DI | - | Spare | Spare_DI_0 | - | Spare I/O Point | -
27 | C5S02-X1 | C5/S2 | C5S02,13 | 1756-IB32-13 | DI | - | Spare | Spare_DI_0 | - | Spare I/O Point | -
28 | C5S02-X1 | C5/S2 | C5S02,14 | 1756-IB32-14 | DI | - | Spare | Spare_DI_0 | - | Spare I/O Point | -
29 | C5S02-X1 | C5/S2 | C5S02,15 | 1756-IB32-15 | DI | - | Spare | Spare_DI_0 | - | Spare I/O Point | -
30 | C5S02-X2 | C5/S2 | C5S02,16 | 1756-IB32-16 | DI | - | Spare | Spare_DI_0 | - | Spare I/O Point | -
31 | C5S02-X2 | C5/S2 | C5S02,17 | 1756-IB32-17 | DI | - | Spare | Spare_DI_0 | - | Spare I/O Point | -
Doc No.: Instrument I/O List (Kalasin) - RIO-200 | Page 1 of 4 | CONFIDENTIAL | Generated: 2026-09-07

ENCLOSURE: RIO-200 | TYPE: Remote I/O Enclosure (RIO Panel) | LOCATION: Slurry - Out Building 2nd Floor | SIZE: 800-1000-400 mm
SUMMARY: Total Channels: 112 | Active: 57 | Spare: 55 (49.1%) | DI: 64 | DO: 32 | AI: 16 | AO: 0 | BUS: 0
No. | Terminal | Rack/Slot | Channel | I/O Module | Type Signal Characteristic Instrument Tag | | | PLC Tag Name | P&ID No. | Service / Equipment Description | Zone / Floor
32 | C5S02-X2 | C5/S2 | C5S02,18 | 1756-IB32-18 | DI | - | Spare | Spare_DI_0 | - | Spare I/O Point | -
33 | C5S02-X2 | C5/S2 | C5S02,19 | 1756-IB32-19 | DI | - | Spare | Spare_DI_0 | - | Spare I/O Point | -
34 | C5S02-X2 | C5/S2 | C5S02,20 | 1756-IB32-20 | DI | - | Spare | Spare_DI_0 | - | Spare I/O Point | -
35 | C5S02-X2 | C5/S2 | C5S02,21 | 1756-IB32-21 | DI | - | Spare | Spare_DI_0 | - | Spare I/O Point | -
36 | C5S02-X2 | C5/S2 | C5S02,22 | 1756-IB32-22 | DI | - | Spare | Spare_DI_0 | - | Spare I/O Point | -
37 | C5S02-X2 | C5/S2 | C5S02,23 | 1756-IB32-23 | DI | - | Spare | Spare_DI_0 | - | Spare I/O Point | -
38 | C5S02-X2 | C5/S2 | C5S02,24 | 1756-IB32-24 | DI | - | Spare | Spare_DI_0 | - | Spare I/O Point | -
39 | C5S02-X2 | C5/S2 | C5S02,25 | 1756-IB32-25 | DI | - | Spare | Spare_DI_0 | - | Spare I/O Point | -
40 | C5S02-X2 | C5/S2 | C5S02,26 | 1756-IB32-26 | DI | - | Spare | Spare_DI_0 | - | Spare I/O Point | -
41 | C5S02-X2 | C5/S2 | C5S02,27 | 1756-IB32-27 | DI | - | Spare | Spare_DI_0 | - | Spare I/O Point | -
42 | C5S02-X2 | C5/S2 | C5S02,28 | 1756-IB32-28 | DI | - | Spare | Spare_DI_0 | - | Spare I/O Point | -
43 | C5S02-X2 | C5/S2 | C5S02,29 | 1756-IB32-29 | DI | - | Spare | Spare_DI_0 | - | Spare I/O Point | -
44 | C5S02-X2 | C5/S2 | C5S02,30 | 1756-IB32-30 | DI | - | Spare | Spare_DI_0 | - | Spare I/O Point | -
45 | C5S02-X2 | C5/S2 | C5S02,31 | 1756-IB32-31 | DI | - | Spare | Spare_DI_0 | - | Spare I/O Point | -
46 | C5S03-X1 | C5/S3 | C5S03,08 | 1756-OB32-8 | DO | - | Spare | Spare_DO_0 | - | Spare I/O Point | -
47 | C5S03-X1 | C5/S3 | C5S03,09 | 1756-OB32-9 | DO | - | Spare | Spare_DO_0 | - | Spare I/O Point | -
48 | C5S03-X1 | C5/S3 | C5S03,10 | 1756-OB32-10 | DO | - | Spare | Spare_DO_0 | - | Spare I/O Point | -
49 | C5S03-X1 | C5/S3 | C5S03,11 | 1756-OB32-11 | DO | - | Spare | Spare_DO_0 | - | Spare I/O Point | -
50 | C5S03-X1 | C5/S3 | C5S03,12 | 1756-OB32-12 | DO | - | Spare | Spare_DO_0 | - | Spare I/O Point | -
51 | C5S03-X1 | C5/S3 | C5S03,13 | 1756-OB32-13 | DO | - | Spare | Spare_DO_0 | - | Spare I/O Point | -
52 | C5S03-X1 | C5/S3 | C5S03,14 | 1756-OB32-14 | DO | - | Spare | Spare_DO_0 | - | Spare I/O Point | -
53 | C5S03-X1 | C5/S3 | C5S03,15 | 1756-OB32-15 | DO | - | Spare | Spare_DO_0 | - | Spare I/O Point | -
54 | C5S03-X2 | C5/S3 | C5S03,16 | 1756-OB32-16 | DO | - | Spare | Spare_DO_0 | - | Spare I/O Point | -
55 | C5S03-X2 | C5/S3 | C5S03,17 | 1756-OB32-17 | DO | - | Spare | Spare_DO_0 | - | Spare I/O Point | -
56 | C5S03-X2 | C5/S3 | C5S03,18 | 1756-OB32-18 | DO | - | Spare | Spare_DO_0 | - | Spare I/O Point | -
57 | C5S03-X2 | C5/S3 | C5S03,19 | 1756-OB32-19 | DO | - | Spare | Spare_DO_0 | - | Spare I/O Point | -
58 | C5S03-X2 | C5/S3 | C5S03,20 | 1756-OB32-20 | DO | - | Spare | Spare_DO_0 | - | Spare I/O Point | -
59 | C5S03-X2 | C5/S3 | C5S03,21 | 1756-OB32-21 | DO | - | Spare | Spare_DO_0 | - | Spare I/O Point | -
60 | C5S03-X2 | C5/S3 | C5S03,22 | 1756-OB32-22 | DO | - | Spare | Spare_DO_0 | - | Spare I/O Point | -
61 | C5S03-X2 | C5/S3 | C5S03,23 | 1756-OB32-23 | DO | - | Spare | Spare_DO_0 | - | Spare I/O Point | -
62 | C5S03-X2 | C5/S3 | C5S03,24 | 1756-OB32-24 | DO | - | Spare | Spare_DO_0 | - | Spare I/O Point | -
Doc No.: Instrument I/O List (Kalasin) - RIO-200 | Page 2 of 4 | CONFIDENTIAL | Generated: 2026-09-07

ENCLOSURE: RIO-200 | TYPE: Remote I/O Enclosure (RIO Panel) | LOCATION: Slurry - Out Building 2nd Floor | SIZE: 800-1000-400 mm
SUMMARY: Total Channels: 112 | Active: 57 | Spare: 55 (49.1%) | DI: 64 | DO: 32 | AI: 16 | AO: 0 | BUS: 0
No. | Terminal | Rack/Slot | Channel | I/O Module | Type Signal Characteristic Instrument Tag | | | PLC Tag Name | P&ID No. | Service / Equipment Description | Zone / Floor
63 | C5S03-X2 | C5/S3 | C5S03,25 | 1756-OB32-25 | DO | - | Spare | Spare_DO_0 | - | Spare I/O Point | -
64 | C5S03-X2 | C5/S3 | C5S03,26 | 1756-OB32-26 | DO | - | Spare | Spare_DO_0 | - | Spare I/O Point | -
65 | C5S03-X2 | C5/S3 | C5S03,27 | 1756-OB32-27 | DO | - | Spare | Spare_DO_0 | - | Spare I/O Point | -
66 | C5S03-X2 | C5/S3 | C5S03,28 | 1756-OB32-28 | DO | - | Spare | Spare_DO_0 | - | Spare I/O Point | -
67 | C5S03-X2 | C5/S3 | C5S03,29 | 1756-OB32-29 | DO | - | Spare | Spare_DO_0 | - | Spare I/O Point | -
68 | C5S03-X2 | C5/S3 | C5S03,30 | 1756-OB32-30 | DO | - | Spare | Spare_DO_0 | - | Spare I/O Point | -
69 | C5S03-X2 | C5/S3 | C5S03,31 | 1756-OB32-31 | DO | - | Spare | Spare_DO_0 | - | Spare I/O Point | -
70 | C5S04-X1 | C5/S4 | C5S04,09 | 1756-IF16-9 | AI | - | Spare | Spare_AI_0 | 3-25-01-913-PD-02 | Spare I/O Point | LPG System / 1st
71 | C5S04-X1 | C5/S4 | C5S04,10 | 1756-IF16-10 | AI | - | Spare | Spare_AI_0 | 3-25-01-913-PD-02 | Spare I/O Point | LPG System / 1st
72 | C5S04-X1 | C5/S4 | C5S04,11 | 1756-IF16-11 | AI | - | Spare | Spare_AI_0 | 3-25-01-913-PD-02 | Spare I/O Point | LPG System / 1st
73 | C5S04-X1 | C5/S4 | C5S04,12 | 1756-IF16-12 | AI | - | Spare | Spare_AI_0 | 3-25-01-913-PD-02 | Spare I/O Point | LPG System / 1st
74 | C5S04-X1 | C5/S4 | C5S04,13 | 1756-IF16-13 | AI | - | Spare | Spare_AI_0 | 3-25-01-913-PD-02 | Spare I/O Point | LPG System / 1st
75 | C5S04-X1 | C5/S4 | C5S04,14 | 1756-IF16-14 | AI | - | Spare | Spare_AI_0 | - | Spare I/O Point | -
76 | C5S04-X1 | C5/S4 | C5S04,15 | 1756-IF16-15 | AI | - | Spare | Spare_AI_0 | - | Spare I/O Point | -
77 | C5S01-X1 | C5/S1 | C5S01,14 | 1756-IB32-14 | DI | Dry Contact | XA-80305A | XA-80305A_DI_1 | 325-01-803-PD-02 | 0 | LPG System / 1st
78 | C5S01-X1 | C5/S1 | C5S01,15 | 1756-IB32-15 | DI | Dry Contact | XA-80305B | XA-80305B_DI_1 | 325-01-803-PD-02 | 0 | LPG System / 1st
79 | C5S01-X2 | C5/S1 | C5S01,16 | 1756-IB32-16 | DI | Dry Contact | XA-80305C | XA-80305C_DI_1 | 325-01-803-PD-02 | 0 | LPG System / 1st
80 | C5S01-X2 | C5/S1 | C5S01,17 | 1756-IB32-17 | DI | Dry Contact | XA-80305D | XA-80305D_DI_1 | 325-01-803-PD-02 | 0 | LPG System / 1st
81 | C5S01-X2 | C5/S1 | C5S01,18 | 1756-IB32-18 | DI | Dry Contact | XA-80305E | XA-80305E_DI_1 | 325-01-803-PD-02 | 0 | LPG System / 1st
82 | C5S01-X2 | C5/S1 | C5S01,19 | 1756-IB32-19 | DI | Dry Contact | XA-80305F | XA-80305F_DI_1 | 325-01-803-PD-02 | 0 | LPG System / 1st
83 | C5S01-X2 | C5/S1 | C5S01,20 | 1756-IB32-20 | DI | Dry Contact | XA-80306A | XA-80306A_DI_1 | 325-01-803-PD-02 | 0 | LPG System / 1st
84 | C5S01-X2 | C5/S1 | C5S01,21 | 1756-IB32-21 | DI | Dry Contact | XA-80306B | XA-80306B_DI_1 | 325-01-803-PD-02 | 0 | LPG System / 1st
85 | C5S01-X2 | C5/S1 | C5S01,22 | 1756-IB32-22 | DI | Dry Contact | XA-80306C | XA-80306C_DI_1 | 325-01-803-PD-02 | 0 | LPG System / 1st
86 | C5S01-X2 | C5/S1 | C5S01,23 | 1756-IB32-23 | DI | Dry Contact | XA-80306D | XA-80306D_DI_1 | 325-01-803-PD-02 | 0 | LPG System / 1st
87 | C5S01-X2 | C5/S1 | C5S01,24 | 1756-IB32-24 | DI | Dry Contact | XA-80306E | XA-80306E_DI_1 | 325-01-803-PD-02 | 0 | LPG System / 1st
88 | C5S01-X2 | C5/S1 | C5S01,25 | 1756-IB32-25 | DI | Dry Contact | XA-80306F | XA-80306F_DI_1 | 325-01-803-PD-02 | 0 | LPG System / 1st
89 | C5S03-X1 | C5/S3 | C5S03,00 | 1756-OB32-0 | DO | 4 - 20 mA | XA-92201 | XA-92201_DO_1 | 3-25-01-922-PD-03 | 0 | Boiler System / 1st
90 | C5S04-X1 | C5/S4 | C5S04,07 | 1756-IF16-7 | AI | 4 - 20 mA | XT-92201 | XT-92201_AI_1 | 3-25-01-922-PD-03 | 0 | Boiler System / 1st
91 | C5S01-X2 | C5/S1 | C5S01,26 | 1756-IB32-26 | DI | 24 VDC energized | XV-20201 | XV-20201_DI_1 | 3-25-01-202-PD-01 | 0 | Slurry - Out Buildi...
92 | C5S01-X2 | C5/S1 | C5S01,27 | 1756-IB32-27 | DI | 24 VDC energized | XV-20201 | XV-20201_DI_2 | 3-25-01-202-PD-01 | 0 | Slurry - Out Buildi...
93 | C5S03-X1 | C5/S3 | C5S03,01 | 1756-OB32-1 | DO | 24 VDC energized | XV-20201 | XV-20201_DO_1 | 3-25-01-202-PD-01 | 0 | Slurry - Out Buildi...
Doc No.: Instrument I/O List (Kalasin) - RIO-200 | Page 3 of 4 | CONFIDENTIAL | Generated: 2026-09-07

ENCLOSURE: RIO-200 | TYPE: Remote I/O Enclosure (RIO Panel) | LOCATION: Slurry - Out Building 2nd Floor | SIZE: 800-1000-400 mm
SUMMARY: Total Channels: 112 | Active: 57 | Spare: 55 (49.1%) | DI: 64 | DO: 32 | AI: 16 | AO: 0 | BUS: 0
No. | Terminal | Rack/Slot | Channel | I/O Module | Type Signal Characteristic Instrument Tag | | | PLC Tag Name | P&ID No. | Service / Equipment Description | Zone / Floor
94 | C5S01-X2 | C5/S1 | C5S01,28 | 1756-IB32-28 | DI | 24 VDC energized | XV-20202 | XV-20202_DI_1 | 3-25-01-202-PD-01 | 0 | Slurry - Out Buildi...
95 | C5S01-X2 | C5/S1 | C5S01,29 | 1756-IB32-29 | DI | 24 VDC energized | XV-20202 | XV-20202_DI_2 | 3-25-01-202-PD-01 | 0 | Slurry - Out Buildi...
96 | C5S03-X1 | C5/S3 | C5S03,02 | 1756-OB32-2 | DO | 24 VDC energized | XV-20202 | XV-20202_DO_1 | 3-25-01-202-PD-01 | 0 | Slurry - Out Buildi...
97 | C5S01-X2 | C5/S1 | C5S01,30 | 1756-IB32-30 | DI | 24 VDC energized | XV-20203 | XV-20203_DI_1 | 3-25-01-202-PD-01 | 0 | Slurry - Out Buildi...
98 | C5S01-X2 | C5/S1 | C5S01,31 | 1756-IB32-31 | DI | 24 VDC energized | XV-20203 | XV-20203_DI_2 | 3-25-01-202-PD-01 | 0 | Slurry - Out Buildi...
99 | C5S03-X1 | C5/S3 | C5S03,03 | 1756-OB32-3 | DO | 24 VDC energized | XV-20203 | XV-20203_DO_1 | 3-25-01-202-PD-01 | 0 | Slurry - Out Buildi...
100 | C5S02-X1 | C5/S2 | C5S02,00 | 1756-IB32-0 | DI | 24 VDC energized | XV-20211 | XV-20211_DI_1 | 3-25-01-202-PD-01 | 0 | Slurry - Out Buildi...
101 | C5S02-X1 | C5/S2 | C5S02,01 | 1756-IB32-1 | DI | 24 VDC energized | XV-20211 | XV-20211_DI_2 | 3-25-01-202-PD-01 | 0 | Slurry - Out Buildi...
102 | C5S03-X1 | C5/S3 | C5S03,04 | 1756-OB32-4 | DO | 24 VDC energized | XV-20211 | XV-20211_DO_1 | 3-25-01-202-PD-01 | 0 | Slurry - Out Buildi...
103 | C5S02-X1 | C5/S2 | C5S02,02 | 1756-IB32-2 | DI | 24 VDC energized | XV-20212 | XV-20212_DI_1 | 3-25-01-202-PD-01 | 0 | Slurry - Out Buildi...
104 | C5S02-X1 | C5/S2 | C5S02,03 | 1756-IB32-3 | DI | 24 VDC energized | XV-20212 | XV-20212_DI_2 | 3-25-01-202-PD-01 | 0 | Slurry - Out Buildi...
105 | C5S03-X1 | C5/S3 | C5S03,05 | 1756-OB32-5 | DO | 24 VDC energized | XV-20212 | XV-20212_DO_1 | 3-25-01-202-PD-01 | 0 | Slurry - Out Buildi...
106 | C5S02-X1 | C5/S2 | C5S02,04 | 1756-IB32-4 | DI | 24 VDC energized | XV-20213 | XV-20213_DI_1 | 3-25-01-202-PD-01 | 0 | Slurry - Out Buildi...
107 | C5S02-X1 | C5/S2 | C5S02,05 | 1756-IB32-5 | DI | 24 VDC energized | XV-20213 | XV-20213_DI_2 | 3-25-01-202-PD-01 | 0 | Slurry - Out Buildi...
108 | C5S03-X1 | C5/S3 | C5S03,06 | 1756-OB32-6 | DO | 24 VDC energized | XV-20213 | XV-20213_DO_1 | 3-25-01-202-PD-01 | 0 | Slurry - Out Buildi...
109 | C5S02-X1 | C5/S2 | C5S02,06 | 1756-IB32-6 | DI | 24 VDC energized | XV-913201 | XV-913201_DI_1 | 3-25-01-913-PD-02 | 0 | LPG System / 1st
110 | C5S02-X1 | C5/S2 | C5S02,07 | 1756-IB32-7 | DI | 24 VDC energized | XV-913201 | XV-913201_DI_1 | 3-25-01-913-PD-02 | 0 | LPG System / 1st
111 | C5S03-X1 | C5/S3 | C5S03,07 | 1756-OB32-7 | DO | 24 VDC energized | XV-913201 | XV-913201_DO_1 | 3-25-01-913-PD-02 | 0 | LPG System / 1st
112 | C5S04-X1 | C5/S4 | C5S04,08 | 1756-IF16-8 | AI | 24 VDC energized | XV-913201 | XV-913201_AI_1 | 3-25-01-913-PD-02 | 0 | LPG System / 1st
Doc No.: Instrument I/O List (Kalasin) - RIO-200 | Page 4 of 4 | CONFIDENTIAL | Generated: 2026-09-07
