x92120/x260911-002-KalasinEngineering/03_IO_Lists_and_Schedules/IO_List-Bak/C1_C8_Slot_to_Destination_JB_Architecture_Diagram.pdf

# This page contains the following errors:

# error on line 276 at column 72: xmlParseEntityRef: no name

Below is a rendering of the page up to the first error.

9/29/26, 1:11 PM

file:///Users/x92120/xApp-001/x260911-002-KalasinEngineering/02_Electrical_and_eDrawing/03_CAD_Exports_DXF_SVG/C1_C8_Slot_to_Destination_JB_Archi… 1/3

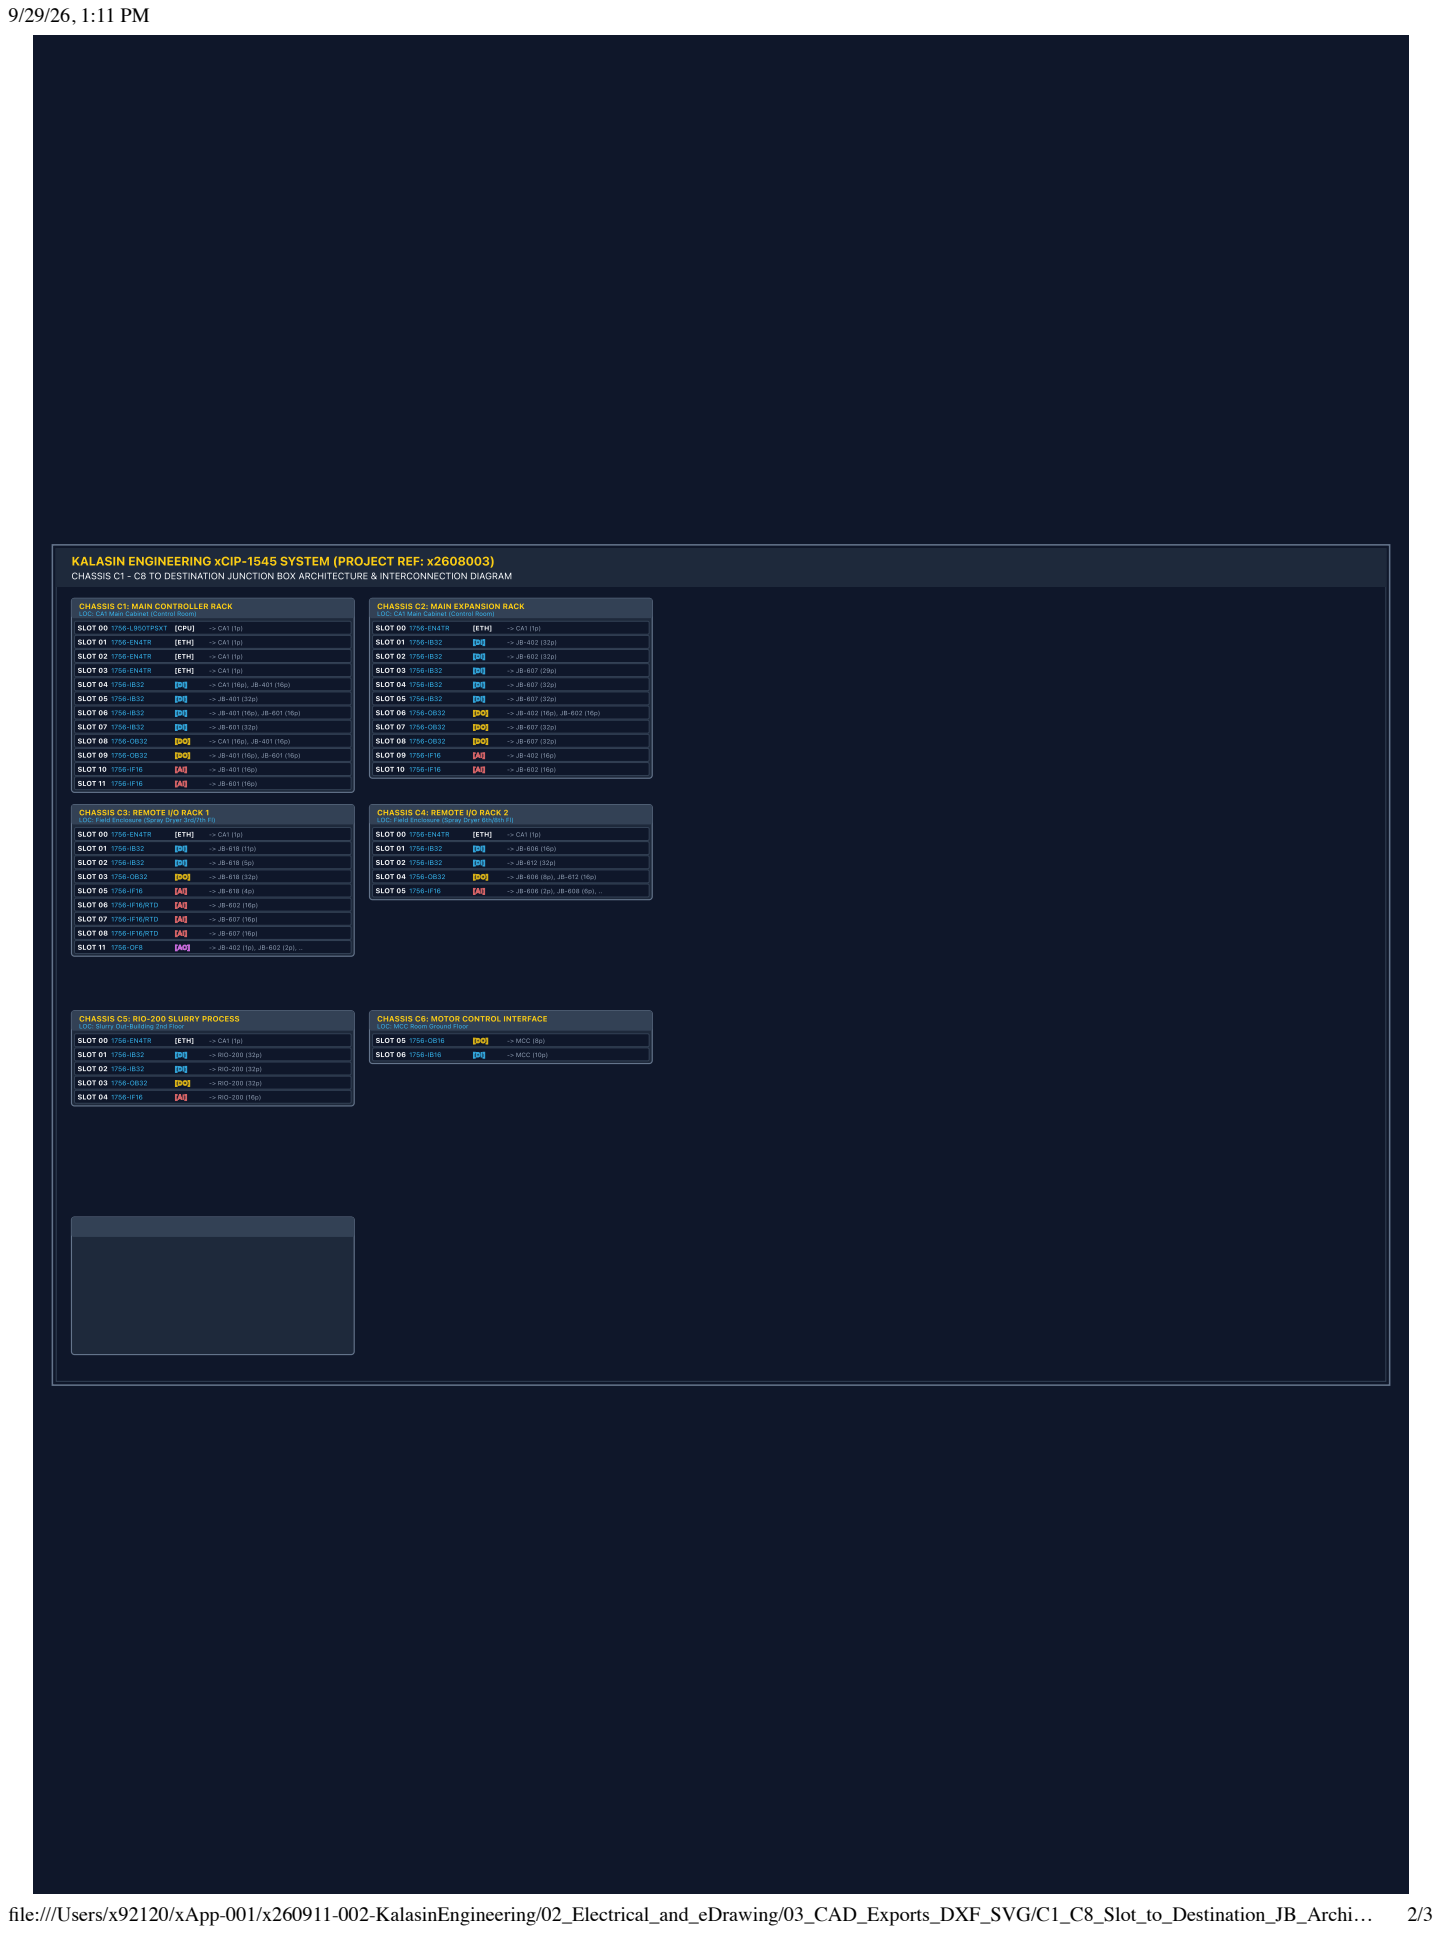
[picture p35: page 2]
SLOT 00 1756-L950TPSXT [CPU]; SLOT 01 1756-EN4TR; [ETH]; SLOT 02 1756-EN4TR; SLOT 03 1756-EN4TR; SLOT 04 1756-IB32; SLOT 05 1756-IB32; SLOT 06 1756-IB32; SLOT 07 1756-IB32; SLOT 08 1756-OB32; SLOT 09 1756-OB32; SLOT 10 1756-IF16; SLOT 11 1756-IF16; SLOT 00 1756-EN4TR; SLOT 01 1756-IB32; SLOT 02 1756-IB32; SLOT 03 1756-IB32; SLOT 06 1756-OB32; SLOT 07 1756-OB32; SLOT 09 1756-IF16; SLOT 03 1756-OB32; SLOT 05 1756-IF16; SLOT 06 1756-IF16/RTD; SLOT 07 1756-IF16/RTD; SLOT 08 1756-IF16/RTD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

KALASIN ENGINEERING xCIP-1545 SYSTEM (PROJECT REF: x2608003)
CHASSIS C1 - C8 TO DESTINATION JUNCTION BOX ARCHITECTURE & INTERCONNECTION DIAGRAM

CHASSIS C1: MAIN CONTROLLER RACK
LOC: CA1 Main Cabinet (Control Room)

CHASSIS C2: MAIN EXPANSION RACK

CHASSIS C3: REMOTE I/O RACK 1
LOC: Field Enclosure (Spray Dryer 3rd/7th Fl)

CHASSIS C4: REMOTE I/O RACK 2
LOC: Field Enclosure (Spray Dryer 6th/8th Fl)

CHASSIS C5: RIO-200 SLURRY PROCESS
LOC: Slurry Out-Building 2nd Floor

CHASSIS C6: MOTOR CONTROL INTERFACE
LOC: MCC Room Ground Floor

file:///Users/x92120/xApp-001/x260911-002-KalasinEngineering/02_Electrical_and_eDrawing/03_CAD_Exports_DXF_SVG/C1_C8_Slot_to_Destination_JB_Archi… 3/3
