x92120/x260911-002-KalasinEngineering/03_IO_Lists_and_Schedules/IO_List-Bak/Chassis_C1_Destination_and_IO_Summary_Report.pdf

KALASIN ENGINEERING | Turnkey xCIP-1545 Automation System (Ref: x2608003) | Chassis C1 Destination & I/O Summary Report | Page 1

## CHASSIS C1: DESTINATION ROUTING & I/O POINT SUMMARY

ROCKWELL 1756 CONTROLLOGIX PROCESSOR RACK (CA1) — POINT COUNT & FIELD ROUTING SCHEDULE

| Project: Kalasin xCIP Turnkey Controller: 1756-L950TPSXT Rack Enclosure: Control Cabinet CA1

## 1. Executive Summary & Routing Breakdown

TOTAL C1 CHANNELS

# 228 Points

Configured across Slots 00–11

ACTIVE SIGNALS

# 138 Points

60.5% Active Field Instruments

SPARE CAPACITY

# 90 Points

39.5% Expansion Reserve

DESTINATIONS

# 3 Locations

CA1, JB-401, JB-601

Destination | Plant Location / Role | Total Pts | Active | Spare | DI (24V) | DO (24V) | AI (4-20mA) | CPU / Comm
CA1 | Main Control Room (Local Cabinet Spares & Network) | 36 | 0 | 36 | 16 | 16 | 0 | 4
JB-401 | Infeed 2nd Floor (Raw Material Prep & Cooking Infeed) | 112 | 85 | 27 | 64 | 32 | 16 | 0
JB-601 | Spray Dryer 1st Floor (Chamber Bottom Discharge & Pumps) | 80 | 53 | 27 | 48 | 16 | 16 | 0
TOTAL | Chassis C1 Master Total | 228 | 138 | 90 | 128 | 64 | 32 | 4

## 2. Chassis C1 Slot-to-Destination Routing Schedule

Slot | Hardware Card | Type | Destination | Points | Active | Spare | Connected Equipment / Purpose
00 | 1756-L950TPSXT | CPU | CA1 | 1 | 0 | 1 | ControlLogix Main Controller Head
01 | 1756-EN4TR | ETH-1 | CA1 | 1 | 0 | 1 | Plant Network Port 1 (Enterprise / SCADA)
02 | 1756-EN4TR | ETH-2 | CA1 | 1 | 0 | 1 | DLR Device Level Ring Supervisor Node
03 | 1756-EN4TR | ETH-3 | CA1 | 1 | 0 | 1 | Historian & Auxiliary Communications Link
04 | 1756-IB32 | DI | CA1 | 16 | 0 | 16 | Local Cabinet Spare DI Bank (Channel 00–15)
04 | 1756-IB32 | DI | JB-401 | 16 | 16 | 0 | Infeed Flow & Limit Switches (FS-40101, FS-40102, ZS-40101)
05 | 1756-IB32 | DI | JB-401 | 32 | 32 | 0 | Infeed Level Switches (LSH/LSL-40101–08) & Valve Feedback
06 | 1756-IB32 | DI | JB-401 | 16 | 2 | 14 | Infeed Interlocks & Permissives
06 | 1756-IB32 | DI | JB-601 | 16 | 10 | 6 | Spray Dryer Chamber Bottom Level & Safety Switches
07 | 1756-IB32 | DI | JB-601 | 32 | 23 | 9 | Spray Dryer 1st Fl Flow & Pressure (FS-60101, PSH-60101)
08 | 1756-OB32 | DO | CA1 | 16 | 0 | 16 | Local Cabinet Spare DO Bank (Channel 00–15)
08 | 1756-OB32 | DO | JB-401 | 16 | 16 | 0 | Infeed Solenoid Valves (XV-40101–XV-40116)
Client: Ingredion (Thailand) Co., Ltd. / ISHITON | Document Ref: KAL-IO-REP-C1-001 | Source File: IO_List_xDev-R01-Tag35-7.xlsx | Approved Rev: 3.6

KALASIN ENGINEERING | Turnkey xCIP-1545 Automation System (Ref: x2608003) | Chassis C1 Destination & I/O Summary Report | Page 2
09 | 1756-OB32 | DO | JB-401 | 16 | 8 | 8 | Infeed Process Valves (XV-40117–XV-40124)
09 | 1756-OB32 | DO | JB-601 | 16 | 12 | 4 | Spray Dryer Discharge Solenoids (XV-60101–XV-60112)
10 | 1756-IF16 | AI | JB-401 | 16 | 11 | 5 | Infeed Transmitters (PT-40101, TT-40101–04, FT-40101)
11 | 1756-IF16 | AI | JB-601 | 16 | 8 | 8 | Spray Dryer 1st Fl Pressure & Temp (PT-60101, TT-60101–06)

KALASIN ENGINEERING | Turnkey xCIP-1545 Automation System (Ref: x2608003) | Chassis C1 Destination & I/O Summary Report | Page 3

## 3. Chassis C1 Complete Point-by-Point Wiring & Loop Schedule (228 Channels)

Slot | Pt | Terminal | Type | Tag | Description | Dest JB | P&ID No. | Status
00 | 00 | C1S00-X1 | CPU | SPARE | Spare Reserve Channel | CA1 | - | SPARE
01 | 00 | C1S01-X1 | ETH-1 | SPARE | Spare Reserve Channel | CA1 | - | SPARE
02 | 00 | C1S02-X1 | ETH-2 | SPARE | Spare Reserve Channel | CA1 | - | SPARE
03 | 00 | C1S03-X1 | ETH-3 | SPARE | Spare Reserve Channel | CA1 | - | SPARE
04 | 00 | C1S04-X1 | DI | SPARE | Spare Reserve Channel | CA1 | - | SPARE
04 | 01 | C1S04-X1 | DI | SPARE | Spare Reserve Channel | CA1 | - | SPARE
04 | 02 | C1S04-X1 | DI | SPARE | Spare Reserve Channel | CA1 | - | SPARE
04 | 03 | C1S04-X1 | DI | SPARE | Spare Reserve Channel | CA1 | - | SPARE
04 | 04 | C1S04-X1 | DI | SPARE | Spare Reserve Channel | CA1 | - | SPARE
04 | 05 | C1S04-X1 | DI | SPARE | Spare Reserve Channel | CA1 | - | SPARE
04 | 06 | C1S04-X1 | DI | SPARE | Spare Reserve Channel | CA1 | - | SPARE
04 | 07 | C1S04-X1 | DI | SPARE | Spare Reserve Channel | CA1 | - | SPARE
04 | 08 | C1S04-X1 | DI | SPARE | Spare Reserve Channel | CA1 | - | SPARE
04 | 09 | C1S04-X1 | DI | SPARE | Spare Reserve Channel | CA1 | - | SPARE
04 | 10 | C1S04-X1 | DI | SPARE | Spare Reserve Channel | CA1 | - | SPARE
04 | 11 | C1S04-X1 | DI | SPARE | Spare Reserve Channel | CA1 | - | SPARE
04 | 12 | C1S04-X1 | DI | SPARE | Spare Reserve Channel | CA1 | - | SPARE
04 | 13 | C1S04-X1 | DI | SPARE | Spare Reserve Channel | CA1 | - | SPARE
04 | 14 | C1S04-X1 | DI | SPARE | Spare Reserve Channel | CA1 | - | SPARE
04 | 15 | C1S04-X1 | DI | SPARE | Spare Reserve Channel | CA1 | - | SPARE
04 | 16 | C1S04-X2 | DI | FSL-40201 | Flow Switch | JB-401 | - | ACTIVE
04 | 17 | C1S04-X2 | DI | FSL-40202 | Flow Switch | JB-401 | - | ACTIVE
04 | 18 | C1S04-X2 | DI | FT-40201 | Coriolis Flow Transmitter | JB-401 | 325-01-400-PD-02 | ACTIVE
04 | 19 | C1S04-X2 | DI | FT-40202 | Magnetic Flow Transmitter | JB-401 | 325-01-400-PD-02 | ACTIVE
04 | 20 | C1S04-X2 | DI | HV-40201 | Manual Valve With Position Switch | JB-401 | 325-01-400-PD-01 | ACTIVE
04 | 21 | C1S04-X2 | DI | HV-40202 | Manual Valve With Position Switch | JB-401 | 325-01-400-PD-01 | ACTIVE
04 | 22 | C1S04-X2 | DI | HV-40203 | Manual Valve With Position Switch | JB-401 | 325-01-400-PD-01 | ACTIVE
04 | 23 | C1S04-X2 | DI | HV-40204 | Manual Valve With Position Switch | JB-401 | 325-01-400-PD-01 | ACTIVE
04 | 24 | C1S04-X2 | DI | HV-40205 | Manual Valve With Position Switch | JB-401 | 325-01-400-PD-01 | ACTIVE
04 | 25 | C1S04-X2 | DI | HV-40206 | Manual Valve With Position Switch | JB-401 | 325-01-400-PD-01 | ACTIVE
04 | 26 | C1S04-X2 | DI | XV-40201A | - | JB-401 | - | ACTIVE

KALASIN ENGINEERING | Turnkey xCIP-1545 Automation System (Ref: x2608003) | Chassis C1 Destination & I/O Summary Report | Page 4
04 | 27 | C1S04-X2 | DI | XV-40201A | - | JB-401 | - | ACTIVE
04 | 28 | C1S04-X2 | DI | XV-40201B | - | JB-401 | 325-01-400-PD-01 | ACTIVE
04 | 29 | C1S04-X2 | DI | XV-40201B | - | JB-401 | 325-01-400-PD-01 | ACTIVE
04 | 30 | C1S04-X2 | DI | XV-40201C | - | JB-401 | 325-01-400-PD-01 | ACTIVE
04 | 31 | C1S04-X2 | DI | XV-40201C | - | JB-401 | 325-01-400-PD-01 | ACTIVE
05 | 00 | C1S05-X1 | DI | XV-40201D | - | JB-401 | 325-01-400-PD-01 | ACTIVE
05 | 01 | C1S05-X1 | DI | XV-40201D | - | JB-401 | 325-01-400-PD-01 | ACTIVE
05 | 02 | C1S05-X1 | DI | XV-40201E | - | JB-401 | 325-01-400-PD-01 | ACTIVE
05 | 03 | C1S05-X1 | DI | XV-40201E | - | JB-401 | 325-01-400-PD-01 | ACTIVE
05 | 04 | C1S05-X1 | DI | XV-40201F | - | JB-401 | 325-01-400-PD-01 | ACTIVE
05 | 05 | C1S05-X1 | DI | XV-40201F | - | JB-401 | 325-01-400-PD-01 | ACTIVE
05 | 06 | C1S05-X1 | DI | XV-40201G | - | JB-401 | 325-01-400-PD-01 | ACTIVE
05 | 07 | C1S05-X1 | DI | XV-40201G | - | JB-401 | 325-01-400-PD-01 | ACTIVE
05 | 08 | C1S05-X1 | DI | XV-40201H | - | JB-401 | 325-01-400-PD-01 | ACTIVE
05 | 09 | C1S05-X1 | DI | XV-40201H | - | JB-401 | 325-01-400-PD-01 | ACTIVE
05 | 11 | C1S05-X1 | DI | XV-40202A | - | JB-401 | 325-01-400-PD-01 | ACTIVE
05 | 12 | C1S05-X1 | DI | XV-40202B | - | JB-401 | 325-01-400-PD-01 | ACTIVE
05 | 13 | C1S05-X1 | DI | XV-40202B | - | JB-401 | 325-01-400-PD-01 | ACTIVE
05 | 14 | C1S05-X1 | DI | XV-40202C | - | JB-401 | 325-01-400-PD-01 | ACTIVE
05 | 15 | C1S05-X1 | DI | XV-40202C | - | JB-401 | 325-01-400-PD-01 | ACTIVE
05 | 16 | C1S05-X2 | DI | XV-40202D | - | JB-401 | 325-01-400-PD-01 | ACTIVE
05 | 17 | C1S05-X2 | DI | XV-40202D | - | JB-401 | 325-01-400-PD-01 | ACTIVE

KALASIN ENGINEERING | Turnkey xCIP-1545 Automation System (Ref: x2608003) | Chassis C1 Destination & I/O Summary Report | Page 5
05 | 18 | C1S05-X2 | DI | XV-40202E | - | JB-401 | 325-01-400-PD-01 | ACTIVE
05 | 19 | C1S05-X2 | DI | XV-40202A | - | JB-401 | 325-01-400-PD-01 | ACTIVE
05 | 19 | C1S05-X2 | DI | XV-40202E | - | JB-401 | 325-01-400-PD-01 | ACTIVE
05 | 20 | C1S05-X2 | DI | XV-40202F | - | JB-401 | 325-01-400-PD-01 | ACTIVE
05 | 21 | C1S05-X2 | DI | XV-40202F | - | JB-401 | 325-01-400-PD-01 | ACTIVE
05 | 22 | C1S05-X2 | DI | XV-40202G | - | JB-401 | 325-01-400-PD-01 | ACTIVE
05 | 23 | C1S05-X2 | DI | XV-40202G | - | JB-401 | 325-01-400-PD-01 | ACTIVE
05 | 24 | C1S05-X2 | DI | XV-40202H | - | JB-401 | 325-01-400-PD-01 | ACTIVE
05 | 25 | C1S05-X2 | DI | XV-40202H | - | JB-401 | 325-01-400-PD-01 | ACTIVE
05 | 26 | C1S05-X2 | DI | XV-40203B | - | JB-401 | 325-01-400-PD-02 | ACTIVE
05 | 27 | C1S05-X2 | DI | XV-40203B | - | JB-401 | 325-01-400-PD-02 | ACTIVE
05 | 28 | C1S05-X2 | DI | XV-40203C | - | JB-401 | 325-01-400-PD-02 | ACTIVE
05 | 29 | C1S05-X2 | DI | XV-40203C | - | JB-401 | 325-01-400-PD-02 | ACTIVE
05 | 30 | C1S05-X2 | DI | XV-40203D | - | JB-401 | 325-01-400-PD-02 | ACTIVE
05 | 31 | C1S05-X2 | DI | XV-40203D | - | JB-401 | 325-01-400-PD-02 | ACTIVE
06 | 00 | C1S06-X1 | DI | XV-40203E | - | JB-401 | 325-01-400-PD-02 | ACTIVE
06 | 01 | C1S06-X1 | DI | XV-40203E | - | JB-401 | 325-01-400-PD-02 | ACTIVE
06 | 02 | C1S06-X1 | DI | SPARE | Spare Reserve Channel | JB-401 | | SPARE
06 | 03 | C1S06-X1 | DI | SPARE | Spare Reserve Channel | JB-401 | | SPARE
06 | 04 | C1S06-X1 | DI | SPARE | Spare Reserve Channel | JB-401 | | SPARE
06 | 05 | C1S06-X1 | DI | SPARE | Spare Reserve Channel | JB-401 | | SPARE
06 | 06 | C1S06-X1 | DI | SPARE | Spare Reserve Channel | JB-401 | | SPARE
06 | 07 | C1S06-X1 | DI | SPARE | Spare Reserve Channel | JB-401 | | SPARE
06 | 08 | C1S06-X1 | DI | SPARE | Spare Reserve Channel | JB-401 | | SPARE
06 | 09 | C1S06-X1 | DI | SPARE | Spare Reserve Channel | JB-401 | | SPARE
06 | 10 | C1S06-X1 | DI | SPARE | Spare Reserve Channel | JB-401 | | SPARE

KALASIN ENGINEERING | Turnkey xCIP-1545 Automation System (Ref: x2608003) | Chassis C1 Destination & I/O Summary Report | Page 6
06 | 11 | C1S06-X1 | DI | SPARE | Spare Reserve Channel | JB-401 | | SPARE
06 | 12 | C1S06-X1 | DI | SPARE | Spare Reserve Channel | JB-401 | | SPARE
06 | 13 | C1S06-X1 | DI | SPARE | Spare Reserve Channel | JB-401 | | SPARE
06 | 14 | C1S06-X1 | DI | SPARE | Spare Reserve Channel | JB-401 | | SPARE
06 | 15 | C1S06-X1 | DI | SPARE | Spare Reserve Channel | JB-401 | | SPARE
06 | 16 | C1S06-X2 | DI | ES-60202 | - | JB-601 | 325-01-600-PD-01 | ACTIVE
06 | 17 | C1S06-X2 | DI | FS-60205 | Flow Switch | JB-601 | 325-01-600-PD-01 | ACTIVE
06 | 18 | C1S06-X2 | DI | LSL-60201 | - | JB-601 | 325-01-600-PD-11 | ACTIVE
06 | 19 | C1S06-X2 | DI | SV-60201 | - | JB-601 | 325-01-600-PD-08 | ACTIVE
06 | 20 | C1S06-X2 | DI | SV-60201 | - | JB-601 | 325-01-600-PD-08 | ACTIVE
06 | 21 | C1S06-X2 | DI | SV-60202 | - | JB-601 | 325-01-600-PD-08 | ACTIVE
06 | 22 | C1S06-X2 | DI | SV-60202 | - | JB-601 | 325-01-600-PD-08 | ACTIVE
06 | 23 | C1S06-X2 | DI | SV-60203 | - | JB-601 | 325-01-600-PD-08 | ACTIVE
06 | 24 | C1S06-X2 | DI | SV-60203 | - | JB-601 | 325-01-600-PD-08 | ACTIVE
06 | 25 | C1S06-X2 | DI | VS-60205 | Vibration Switch | JB-601 | 325-01-600-PD-01 | ACTIVE
06 | 26 | C1S06-X2 | DI | SPARE | Spare Reserve Channel | JB-601 | | SPARE
06 | 27 | C1S06-X2 | DI | SPARE | Spare Reserve Channel | JB-601 | | SPARE
06 | 28 | C1S06-X2 | DI | SPARE | Spare Reserve Channel | JB-601 | | SPARE
06 | 29 | C1S06-X2 | DI | SPARE | Spare Reserve Channel | JB-601 | | SPARE
06 | 30 | C1S06-X2 | DI | SPARE | Spare Reserve Channel | JB-601 | | SPARE
06 | 31 | C1S06-X2 | DI | SPARE | Spare Reserve Channel | JB-601 | | SPARE
07 | 00 | C1S07-X1 | DI | XA-60202A | - | JB-601 | 325-01-600-PD-08 | ACTIVE
07 | 01 | C1S07-X1 | DI | XA-60202B | - | JB-601 | 325-01-600-PD-08 | ACTIVE
07 | 02 | C1S07-X1 | DI | XA-60202C | - | JB-601 | 325-01-600-PD-08 | ACTIVE
07 | 03 | C1S07-X1 | DI | XA-60202D | - | JB-601 | 325-01-600-PD-08 | ACTIVE
07 | 04 | C1S07-X1 | DI | XA-60202E | - | JB-601 | 325-01-600-PD-08 | ACTIVE
07 | 05 | C1S07-X1 | DI | XA-60202F | - | JB-601 | 325-01-600-PD-08 | ACTIVE

KALASIN ENGINEERING | Turnkey xCIP-1545 Automation System (Ref: x2608003) | Chassis C1 Destination & I/O Summary Report | Page 7
07 | 06 | C1S07-X1 | DI | XA-60202G | - | JB-601 | 325-01-600-PD-08 | ACTIVE
07 | 07 | C1S07-X1 | DI | XA-60202H | - | JB-601 | 325-01-600-PD-08 | ACTIVE
07 | 08 | C1S07-X1 | DI | XA-60202I | - | JB-601 | 325-01-600-PD-08 | ACTIVE
07 | 09 | C1S07-X1 | DI | XA-60202J | - | JB-601 | 325-01-600-PD-08 | ACTIVE
07 | 10 | C1S07-X1 | DI | XA-60202K | - | JB-601 | 325-01-600-PD-08 | ACTIVE
07 | 11 | C1S07-X1 | DI | XA-60202L | - | JB-601 | 325-01-600-PD-08 | ACTIVE
07 | 12 | C1S07-X1 | DI | XA-60202M | - | JB-601 | 325-01-600-PD-08 | ACTIVE
07 | 13 | C1S07-X1 | DI | XV-60202 | - | JB-601 | 325-01-600-PD-11 | ACTIVE
07 | 14 | C1S07-X1 | DI | XV-60202 | - | JB-601 | 325-01-600-PD-11 | ACTIVE
07 | 15 | C1S07-X1 | DI | XV-60205A | - | JB-601 | 325-01-600-PD-01 | ACTIVE
07 | 16 | C1S07-X2 | DI | XV-60205A | - | JB-601 | 325-01-600-PD-01 | ACTIVE
07 | 17 | C1S07-X2 | DI | XV-60240D | - | JB-601 | 325-01-600-PD-05 | ACTIVE
07 | 18 | C1S07-X2 | DI | XV-60240D | - | JB-601 | 325-01-600-PD-08 | ACTIVE
07 | 19 | C1S07-X2 | DI | XV-60240D | - | JB-601 | 325-01-600-PD-05 | ACTIVE
07 | 20 | C1S07-X2 | DI | XV-60240D | - | JB-601 | 325-01-600-PD-08 | ACTIVE
07 | 21 | C1S07-X2 | DI | YA-60205 | - | JB-601 | 325-01-600-PD-01 | ACTIVE
07 | 22 | C1S07-X2 | DI | YI-60205 | - | JB-601 | 325-01-600-PD-01 | ACTIVE
07 | 23 | C1S07-X2 | DI | SPARE | Spare Reserve Channel | JB-601 | - | SPARE
07 | 24 | C1S07-X2 | DI | SPARE | Spare Reserve Channel | JB-601 | - | SPARE
07 | 25 | C1S07-X2 | DI | SPARE | Spare Reserve Channel | JB-601 | - | SPARE
07 | 26 | C1S07-X2 | DI | SPARE | Spare Reserve Channel | JB-601 | - | SPARE
07 | 27 | C1S07-X2 | DI | SPARE | Spare Reserve Channel | JB-601 | - | SPARE
07 | 28 | C1S07-X2 | DI | SPARE | Spare Reserve Channel | JB-601 | - | SPARE
07 | 29 | C1S07-X2 | DI | SPARE | Spare Reserve Channel | JB-601 | - | SPARE
07 | 30 | C1S07-X2 | DI | SPARE | Spare Reserve Channel | JB-601 | - | SPARE
07 | 31 | C1S07-X2 | DI | SPARE | Spare Reserve Channel | JB-601 | - | SPARE

KALASIN ENGINEERING | Turnkey xCIP-1545 Automation System (Ref: x2608003) | Chassis C1 Destination & I/O Summary Report | Page 8
08 | 00 | C1S08-X1 | DO | SPARE | Spare Reserve Channel | CA1 | | SPARE
08 | 01 | C1S08-X1 | DO | SPARE | Spare Reserve Channel | CA1 | | SPARE
08 | 02 | C1S08-X1 | DO | SPARE | Spare Reserve Channel | CA1 | | SPARE
08 | 03 | C1S08-X1 | DO | SPARE | Spare Reserve Channel | CA1 | | SPARE
08 | 04 | C1S08-X1 | DO | SPARE | Spare Reserve Channel | CA1 | | SPARE
08 | 05 | C1S08-X1 | DO | SPARE | Spare Reserve Channel | CA1 | | SPARE
08 | 06 | C1S08-X1 | DO | SPARE | Spare Reserve Channel | CA1 | | SPARE
08 | 07 | C1S08-X1 | DO | SPARE | Spare Reserve Channel | CA1 | | SPARE
08 | 08 | C1S08-X1 | DO | SPARE | Spare Reserve Channel | CA1 | | SPARE
08 | 09 | C1S08-X1 | DO | SPARE | Spare Reserve Channel | CA1 | | SPARE
08 | 10 | C1S08-X1 | DO | SPARE | Spare Reserve Channel | CA1 | | SPARE
08 | 11 | C1S08-X1 | DO | SPARE | Spare Reserve Channel | CA1 | | SPARE
08 | 12 | C1S08-X1 | DO | SPARE | Spare Reserve Channel | CA1 | | SPARE
08 | 13 | C1S08-X1 | DO | SPARE | Spare Reserve Channel | CA1 | | SPARE
08 | 14 | C1S08-X1 | DO | SPARE | Spare Reserve Channel | CA1 | | SPARE
08 | 15 | C1S08-X1 | DO | SPARE | Spare Reserve Channel | CA1 | | SPARE
08 | 16 | C1S08-X2 | DO | XV-40202E | - | JB-401 | 325-01-400-PD-01 | ACTIVE
08 | 17 | C1S08-X2 | DO | XV-40202F | - | JB-401 | 325-01-400-PD-01 | ACTIVE
08 | 18 | C1S08-X2 | DO | XV-40202G | - | JB-401 | 325-01-400-PD-01 | ACTIVE
08 | 19 | C1S08-X2 | DO | XV-40202H | - | JB-401 | 325-01-400-PD-01 | ACTIVE
08 | 20 | C1S08-X2 | DO | XV-40203B | - | JB-401 | 325-01-400-PD-02 | ACTIVE
08 | 21 | C1S08-X2 | DO | XV-40203C | - | JB-401 | 325-01-400-PD-02 | ACTIVE
08 | 22 | C1S08-X2 | DO | XV-40203D | - | JB-401 | 325-01-400-PD-02 | ACTIVE
08 | 23 | C1S08-X2 | DO | XV-40203E | - | JB-401 | 325-01-400-PD-02 | ACTIVE
08 | 24 | C1S08-X2 | DO | SV-40201 | - | JB-401 | 325-01-400-PD-01 | ACTIVE
08 | 25 | C1S08-X2 | DO | SV-40202 | - | JB-401 | 325-01-400-PD-01 | ACTIVE
08 | 26 | C1S08-X2 | DO | SV-40203 | - | JB-401 | 325-01-400-PD-01 | ACTIVE
08 | 27 | C1S08-X2 | DO | SV-40204 | - | JB-401 | 325-01-400-PD-01 | ACTIVE
08 | 28 | C1S08-X2 | DO | XV-40201A | - | JB-401 | - | ACTIVE
08 | 29 | C1S08-X2 | DO | XV-40201B | - | JB-401 | 325-01-400-PD-01 | ACTIVE

KALASIN ENGINEERING | Turnkey xCIP-1545 Automation System (Ref: x2608003) | Chassis C1 Destination & I/O Summary Report | Page 9
08 | 30 | C1S08-X2 | DO | XV-40201C | - | JB-401 | 325-01-400-PD-01 | ACTIVE
08 | 31 | C1S08-X2 | DO | XV-40201D | - | JB-401 | 325-01-400-PD-01 | ACTIVE
09 | 00 | C1S09-X1 | DO | XV-40201E | - | JB-401 | 325-01-400-PD-01 | ACTIVE
09 | 01 | C1S09-X1 | DO | XV-40201F | - | JB-401 | 325-01-400-PD-01 | ACTIVE
09 | 02 | C1S09-X1 | DO | XV-40201G | - | JB-401 | 325-01-400-PD-01 | ACTIVE
09 | 03 | C1S09-X1 | DO | XV-40201H | - | JB-401 | 325-01-400-PD-01 | ACTIVE
09 | 04 | C1S09-X1 | DO | XV-40202A | - | JB-401 | 325-01-400-PD-01 | ACTIVE
09 | 05 | C1S09-X1 | DO | XV-40202B | - | JB-401 | 325-01-400-PD-01 | ACTIVE
09 | 06 | C1S09-X1 | DO | XV-40202C | - | JB-401 | 325-01-400-PD-01 | ACTIVE
09 | 07 | C1S09-X1 | DO | XV-40202D | - | JB-401 | 325-01-400-PD-01 | ACTIVE
09 | 08 | C1S09-X1 | DO | SPARE | Spare Reserve Channel | JB-401 | | SPARE
09 | 09 | C1S09-X1 | DO | SPARE | Spare Reserve Channel | JB-401 | | SPARE
09 | 10 | C1S09-X1 | DO | SPARE | Spare Reserve Channel | JB-401 | | SPARE
09 | 11 | C1S09-X1 | DO | SPARE | Spare Reserve Channel | JB-401 | | SPARE
09 | 12 | C1S09-X1 | DO | SPARE | Spare Reserve Channel | JB-401 | | SPARE
09 | 13 | C1S09-X1 | DO | SPARE | Spare Reserve Channel | JB-401 | | SPARE
09 | 14 | C1S09-X1 | DO | SPARE | Spare Reserve Channel | JB-401 | | SPARE
09 | 15 | C1S09-X1 | DO | SPARE | Spare Reserve Channel | JB-401 | | SPARE
09 | 16 | C1S09-X2 | DO | SV-60201 | - | JB-601 | 325-01-600-PD-08 | ACTIVE
09 | 17 | C1S09-X2 | DO | SV-60202 | - | JB-601 | 325-01-600-PD-08 | ACTIVE
09 | 18 | C1S09-X2 | DO | SV-60230 | - | JB-601 | 325-01-600-PD-04 | ACTIVE
09 | 19 | C1S09-X2 | DO | SV-60203 | - | JB-601 | 325-01-600-PD-08 | ACTIVE
09 | 20 | C1S09-X2 | DO | SV-60240A | - | JB-601 | 325-01-600-PD-05 | ACTIVE
09 | 21 | C1S09-X2 | DO | SV-60231 | - | JB-601 | 325-01-600-PD-04 | ACTIVE
09 | 22 | C1S09-X2 | DO | SV-60240B | - | JB-601 | 325-01-600-PD-05 | ACTIVE
09 | 23 | C1S09-X2 | DO | SV-60240C | - | JB-601 | 325-01-600-PD-05 | ACTIVE

KALASIN ENGINEERING | Turnkey xCIP-1545 Automation System (Ref: x2608003) | Chassis C1 Destination & I/O Summary Report | Page 10
09 | 24 | C1S09-X2 | DO | XV-60240D | - | JB-601 | 325-01-600-PD-05 | ACTIVE
09 | 25 | C1S09-X2 | DO | XV-60251 | - | JB-601 | 325-01-600-PD-01 | ACTIVE
09 | 26 | C1S09-X2 | DO | XV-60202 | - | JB-601 | 325-01-600-PD-11 | ACTIVE
09 | 27 | C1S09-X2 | DO | XV-60205A | - | JB-601 | 325-01-600-PD-01 | ACTIVE
09 | 28 | C1S09-X2 | DO | SPARE | Spare Reserve Channel | JB-601 | | SPARE
09 | 29 | C1S09-X2 | DO | SPARE | Spare Reserve Channel | JB-601 | | SPARE
09 | 30 | C1S09-X2 | DO | SPARE | Spare Reserve Channel | JB-601 | | SPARE
09 | 31 | C1S09-X2 | DO | SPARE | Spare Reserve Channel | JB-601 | | SPARE
10 | 00 | C1S10-X1 | AI | FT-40201 | Coriolis Flow Transmitter | JB-401 | 325-01-400-PD-02 | ACTIVE
10 | 01 | C1S10-X1 | AI | FT-40201 | Coriolis Flow Transmitter | JB-401 | 325-01-400-PD-02 | ACTIVE
10 | 02 | C1S10-X1 | AI | FT-40202 | Magnetic Flow Transmitter | JB-401 | 325-01-400-PD-02 | ACTIVE
10 | 03 | C1S10-X1 | AI | LT-40203 | Level Transmitter | JB-401 | 325-01-400-PD-02 | ACTIVE
10 | 04 | C1S10-X1 | AI | LT-40201 | Level Transmitter | JB-401 | 325-01-400-PD-01 | ACTIVE
10 | 05 | C1S10-X1 | AI | LT-40202 | Level Transmitter | JB-401 | 325-01-400-PD-01 | ACTIVE
10 | 06 | C1S10-X1 | AI | pHT-40201 | PH Transmitter | JB-401 | 325-01-400-PD-01 | ACTIVE
10 | 07 | C1S10-X1 | AI | pHT-40202 | PH Transmitter | JB-401 | 325-01-400-PD-01 | ACTIVE
10 | 08 | C1S10-X1 | AI | PT-40201 | Pressure Transmitter | JB-401 | 325-01-400-PD-02 | ACTIVE
10 | 09 | C1S10-X1 | AI | PT-40202 | Pressure Transmitter | JB-401 | 325-01-400-PD-02 | ACTIVE
10 | 10 | C1S10-X1 | AI | PT-60202 | Pressure Transmitter | JB-401 | 325-01-600-PD-01 | ACTIVE
10 | 11 | C1S10-X1 | AI | SPARE | Spare Reserve Channel | JB-401 | | SPARE
10 | 12 | C1S10-X1 | AI | SPARE | Spare Reserve Channel | JB-401 | | SPARE
10 | 13 | C1S10-X1 | AI | SPARE | Spare Reserve Channel | JB-401 | | SPARE
10 | 14 | C1S10-X1 | AI | SPARE | Spare Reserve Channel | JB-401 | | SPARE
10 | 15 | C1S10-X1 | AI | SPARE | Spare Reserve Channel | JB-401 | | SPARE
11 | 00 | C1S11-X1 | AI | DPI-60240 | - | JB-601 | 325-01-600-PD-05 | ACTIVE
11 | 01 | C1S11-X1 | AI | DPT-60202 | Differential Pressure Transmitte | JB-601 | 325-01-600-PD-08 | ACTIVE

KALASIN ENGINEERING | Turnkey xCIP-1545 Automation System (Ref: x2608003) | Chassis C1 Destination & I/O Summary Report | Page 11
11 | 02 | C1S11-X1 | AI | FT-60201 | - | JB-601 | 325-01-600-PD-08 | ACTIVE
11 | 03 | C1S11-X1 | AI | FT-60204 | - | JB-601 | 325-01-600-PD-10 | ACTIVE
11 | 04 | C1S11-X1 | AI | FT-61307 | - | JB-601 | - | ACTIVE
11 | 05 | C1S11-X1 | AI | PT-60203 | Pressure Transmitter | JB-601 | 325-01-600-PD-08 | ACTIVE
11 | 06 | C1S11-X1 | AI | PT-60204 | Pressure Transmitter | JB-601 | 325-01-600-PD-10 | ACTIVE
11 | 07 | C1S11-X1 | AI | PT-60205 | Pressure Transmitter | JB-601 | 325-01-600-PD-01 | ACTIVE
11 | 08 | C1S11-X1 | AI | SPARE | Spare Reserve Channel | JB-601 | | SPARE
11 | 09 | C1S11-X1 | AI | SPARE | Spare Reserve Channel | JB-601 | | SPARE
11 | 10 | C1S11-X1 | AI | SPARE | Spare Reserve Channel | JB-601 | | SPARE
11 | 11 | C1S11-X1 | AI | SPARE | Spare Reserve Channel | JB-601 | | SPARE
11 | 12 | C1S11-X1 | AI | SPARE | Spare Reserve Channel | JB-601 | | SPARE
11 | 13 | C1S11-X1 | AI | SPARE | Spare Reserve Channel | JB-601 | | SPARE
11 | 14 | C1S11-X1 | AI | SPARE | Spare Reserve Channel | JB-601 | | SPARE
11 | 15 | C1S11-X1 | AI | SPARE | Spare Reserve Channel | JB-601 | | SPARE
