x92120/x260911-002-KalasinEngineering/02_Electrical_and_eDrawing/04_PDF_Reports_and_Drawings/individual_sheets_pdf/KAL-JC-TYP-Sheet_02.pdf

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
INGREDION (THAILAND) CO., LTD.
KALASIN STARCH PLANT - JET COOKER PROJECT

### AEC INDUSTRIAL ENGINEERING

SYSTEMS INTEGRATION & AUTOMATION

### INSTRUMENT TEMPLATE DRAWING DIRECTORY

INSTRUMENT HOOK-UP & TYPICAL LOOP DIAGRAM

### DWG NO: KAL-JC-TYP-000-IDX

REV: 3.6 DATE: 2026-09-08

DRAWN: AEC-ENG

CHECKED: LEAD-PE

STATUS: APPROVED

SCALE: N.T.S.

PROJECT NO:

R5THS00138-JC

| SHEET NO: 02 / 25

## MASTER DRAWING INDEX - 23 INSTRUMENT HOOK-UP & LOOP DIAGRAM TEMPLATES

SHT | DRAWING NO | EQUIPMENT CATEGORY / TEMPLATE TITLE | REV | STATUS
03 | KAL-JC-TYP-001 | DUST / PARTICULATE ANALYZER HOOK-UP & LO.. Mfr: ENVEA / PCME | Model: PCME QAL 991 (Electrodynamic | 3.6 | APPROVED
04 | KAL-JC-TYP-002 | COMBUSTIBLE LEL GAS DETECTOR HOOK-UP & L..
| | Mfr: Sensidyne / SmartGas | Model: 925FGD Explosionproof Hydroc
3.6 | APPROVED
05 | KAL-JC-TYP-003 | pH ANALYTICAL MEASUREMENT LOOP HOOK-UP &..
| | Mfr: Mettler Toledo | Model: M300G2 4-Wire Transmitter +
3.6 | APPROVED
06 | KAL-JC-TYP-004 | DIFFERENTIAL PRESSURE GAUGE HOOK-UP & ME..
| | Mfr: Ashcroft | Model: Model 1132 (Piston-Type Diff
3.6 | APPROVED
07 | KAL-JC-TYP-005 | DIFFERENTIAL PRESSURE TRANSMITTER HOOK-U..
| | Mfr: Endress+Hauser | Model: Deltabar PMD55B (Piezoresist
3.6 | APPROVED
08 | KAL-JC-TYP-006 | CORIOLIS MASS FLOWMETER HOOK-UP & LOOP D..
| | Mfr: Endress+Hauser | Model: Promass E 300 (8E3B50 / Dual
3.6 | APPROVED
09 | KAL-JC-TYP-007 | ELECTROMAGNETIC FLOWMETER HOOK-UP & LOOP..
| | Mfr: Endress+Hauser | Model: Promag P 300 (5P3B50 / 80 /
3.6 | APPROVED
10 | KAL-JC-TYP-008 | VORTEX STEAM FLOWMETER HOOK-UP & LOOP DI..
| | Mfr: Endress+Hauser | Model: Prowirl F 200 (7F2C80 / 1H w
3.6 | APPROVED
11 | KAL-JC-TYP-009 | THERMAL MASS GAS FLOWMETER HOOK-UP & LOO..
| | Mfr: Endress+Hauser | Model: t-mass F 300 / I 300 (6F3B /
3.6 | APPROVED
12 | KAL-JC-TYP-010 | ULTRASONIC CLAMP-ON FLOWMETER HOOK-UP & ..
| | Mfr: Keyence | Model: FD-H Series (FD-H20 / FD-H32
3.6 | APPROVED
13 | KAL-JC-TYP-011 | MANUAL HAND VALVE POSITION SWITCH HOOK-U..
| | Mfr: TeroFox / APL-HKC | Model: TF-20DFS Ball Valve + APL-21
3.6 | APPROVED
14 | KAL-JC-TYP-012 | LIQUID LEVEL SWITCH (VIBRATING FORK) HOO..
| | Mfr: Endress+Hauser | Model: Liquiphant FTL51B (Tuning Fo
3.6 | APPROVED
15 | KAL-JC-TYP-013 | SOLID LEVEL SWITCH (POWDER FORK) HOOK-UP..
| | Mfr: Endress+Hauser | Model: Soliphant FTM51 (Vibrating F
3.6 | APPROVED
SHT | DRAWING NO | EQUIPMENT CATEGORY / TEMPLATE TITLE | REV | STATUS
16 | KAL-JC-TYP-014 | RADAR LEVEL TRANSMITTER (80 GHz) HOOK-UP.. Mfr: Endress+Hauser | Model: Micropilot FMR67B (80 GHz Hi | 3.6 | APPROVED
17 | KAL-JC-TYP-015 | PRESSURE GAUGE & SIPHON HOOK-UP & MECHAN..
| | Mfr: Ashcroft | Model: Model T5500 (100mm Dial All-
3.6 | APPROVED
18 | KAL-JC-TYP-016 | ELECTRONIC PRESSURE SWITCH HOOK-UP & LOO..
| | Mfr: Endress+Hauser | Model: Ceraphant PTC31B (Ceramic Se
3.6 | APPROVED
19 | KAL-JC-TYP-017 | PRESSURE TRANSMITTER HOOK-UP & LOOP DIAG..
| | Mfr: Endress+Hauser | Model: Cerabar PMP51B / PMC51B (Met
3.6 | APPROVED
20 | KAL-JC-TYP-018 | BIMETAL TEMPERATURE GAUGE & THERMOWELL H..
| | Mfr: Ashcroft | Model: Model FI (100mm Dial Everyan
3.6 | APPROVED
21 | KAL-JC-TYP-019 | TEMPERATURE TRANSMITTER (RTD Pt100) HOOK..
| | Mfr: Endress+Hauser | Model: iTEMP TMT71 + Omnigrad M TM4
3.6 | APPROVED
22 | KAL-JC-TYP-020 | PNEUMATIC ON-OFF CONTROL VALVE HOOK-UP &..
| | Mfr: TeroFox / El-O-Matic | Model: TF-20DFS Ball Valve + F-Seri
3.6 | APPROVED
23 | KAL-JC-TYP-021 | MODULATING GLOBE CONTROL VALVE HOOK-UP &..
| | Mfr: Samson | Model: Type 3241 Globe Valve + Trov
3.6 | APPROVED
24 | KAL-JC-TYP-022 | ELECTRONIC TEMPERATURE SWITCH HOOK-UP & ..
| | Mfr: Endress+Hauser | Model: Thermophant TTR35 (Compact P
3.6 | APPROVED
25 | KAL-JC-TYP-023 | PNEUMATIC TURBINE VIBRATOR HOOK-UP & LOO..
| | Mfr: Netter Vibration | Model: NCT 5 Pneumatic Turbine Vibr
3.6 | APPROVED
