x92120/x260911-002-KalasinEngineering/01_Network_Design/05_Drawings_and_Schematics/README.md

# 05_Drawings_and_Schematics — Network Master Drawings & HTML Viewers

This directory contains the master vector network drawings, AutoCAD DXF files, print-ready PDFs, high-resolution PNGs, and interactive HTML viewers for the **Ingredion Kalasin Spray Dryer Plant** network architecture.

---

## 🎨 Master Deliverable Drawings

### 1. SPRINT 18K Control Layout & System Architecture
Matching hand-drawn engineering draft `S__103251990`:
* 📐 **AutoCAD DXF (R2010)**: [SPRINT_18K_Control_Layout_System_Architecture.dxf](file:///e:/xApp-01/x260911-002-KalasinEngineering/01_Network_Design/05_Drawings_and_Schematics/SPRINT_18K_Control_Layout_System_Architecture.dxf)
* 🎨 **Vector SVG**: [SPRINT_18K_Control_Layout_System_Architecture.svg](file:///e:/xApp-01/x260911-002-KalasinEngineering/01_Network_Design/05_Drawings_and_Schematics/SPRINT_18K_Control_Layout_System_Architecture.svg)
* 📄 **Printable PDF (A1/A2 Landscape)**: [SPRINT_18K_Control_Layout_System_Architecture.pdf](file:///e:/xApp-01/x260911-002-KalasinEngineering/01_Network_Design/05_Drawings_and_Schematics/SPRINT_18K_Control_Layout_System_Architecture.pdf)
* 🖼️ **High-Res PNG**: [SPRINT_18K_Control_Layout_System_Architecture.png](file:///e:/xApp-01/x260911-002-KalasinEngineering/01_Network_Design/05_Drawings_and_Schematics/SPRINT_18K_Control_Layout_System_Architecture.png)
* 🌐 **Interactive Web Viewer**: [Viewer_SPRINT_18K_Control_Layout.html](file:///e:/xApp-01/x260911-002-KalasinEngineering/01_Network_Design/05_Drawings_and_Schematics/Viewer_SPRINT_18K_Control_Layout.html)
* ⚙️ **Python Generator Script**: [build_sprint18k_control_layout_dxf.py](file:///e:/xApp-01/x260911-002-KalasinEngineering/01_Network_Design/05_Drawings_and_Schematics/build_sprint18k_control_layout_dxf.py)

### 2. ControlLogix 5-Chassis DLR Network & 13-Slot Rack Redesign
* 🎨 **Vector SVG**: [ControlLogix_5Chassis_DLR_Network_and_Rack_Design.svg](file:///e:/xApp-01/x260911-002-KalasinEngineering/01_Network_Design/05_Drawings_and_Schematics/ControlLogix_5Chassis_DLR_Network_and_Rack_Design.svg)
* 📄 **Printable PDF**: [ControlLogix_5Chassis_DLR_Network_and_Rack_Design.pdf](file:///e:/xApp-01/x260911-002-KalasinEngineering/01_Network_Design/05_Drawings_and_Schematics/ControlLogix_5Chassis_DLR_Network_and_Rack_Design.pdf)
* 🖼️ **High-Res PNG**: [ControlLogix_5Chassis_DLR_Network_and_Rack_Design.png](file:///e:/xApp-01/x260911-002-KalasinEngineering/01_Network_Design/05_Drawings_and_Schematics/ControlLogix_5Chassis_DLR_Network_and_Rack_Design.png)
* 🌐 **Interactive Web Viewer**: [Viewer_Network_and_Rack_Design.html](file:///e:/xApp-01/x260911-002-KalasinEngineering/01_Network_Design/05_Drawings_and_Schematics/Viewer_Network_and_Rack_Design.html)
* ⚙️ **Python Generator Script**: [generate_network_and_slot_svg.py](file:///e:/xApp-01/x260911-002-KalasinEngineering/01_Network_Design/05_Drawings_and_Schematics/generate_network_and_slot_svg.py)

### 3. Redundant Cisco Core Switches & Redundant Server Infrastructure
HSRP v2, Dual-Homing, MCC Trunk, Server Fiber:
* 🎨 **Vector SVG**: [Redundant_Cisco_Core_and_Server_Network_Diagram.svg](file:///e:/xApp-01/x260911-002-KalasinEngineering/01_Network_Design/05_Drawings_and_Schematics/Redundant_Cisco_Core_and_Server_Network_Diagram.svg)
* 📄 **Printable PDF (A1/A2 Landscape)**: [Redundant_Cisco_Core_and_Server_Network_Diagram.pdf](file:///e:/xApp-01/x260911-002-KalasinEngineering/01_Network_Design/05_Drawings_and_Schematics/Redundant_Cisco_Core_and_Server_Network_Diagram.pdf)
* 🖼️ **Ultra High-Res PNG**: [Redundant_Cisco_Core_and_Server_Network_Diagram.png](file:///e:/xApp-01/x260911-002-KalasinEngineering/01_Network_Design/05_Drawings_and_Schematics/Redundant_Cisco_Core_and_Server_Network_Diagram.png)
* 🌐 **Interactive Web Viewer**: [Viewer_Redundant_Network_Diagram.html](file:///e:/xApp-01/x260911-002-KalasinEngineering/01_Network_Design/05_Drawings_and_Schematics/Viewer_Redundant_Network_Diagram.html)
* ⚙️ **Python Generator Script**: [build_redundant_network_diagram.py](file:///e:/xApp-01/x260911-002-KalasinEngineering/01_Network_Design/05_Drawings_and_Schematics/build_redundant_network_diagram.py)
