x92120/x260911-002-KalasinEngineering/01_Network_Design/05_Drawings_and_Schematics/Viewer_Redundant_Network_Diagram.html

# Ingredion Kalasin — Redundant Cisco & Server Infrastructure DWG-260911-NET-02 (LIGHT STYLE)

HSRP v2 Layer-3 High Availability • Server Dual-Homing & Heartbeat • MCC 802.1Q Trunk • 10G Server Fiber

➕ Zoom In ➖ Zoom Out 🎯 Fit Screen 🔄 100% 📄 View PDF 🖼️ View PNG

VLAN 10: SCADA Servers (HSRP .1)

VLAN 20: HMI Clients (HSRP .1)

VLAN 30: PLC Control (HSRP .1)

VLAN 50: MCC Drives Trunk (HSRP .1)

10G Fiber: Server Room

Heartbeat: 10.10.10.x/30 Direct

100%
