x92120/x260911-002-KalasinEngineering/02_Electrical_and_eDrawing/06_SCADA_Demo/Automation_Architecture_Project_SPRINT_Kalasin.pptx

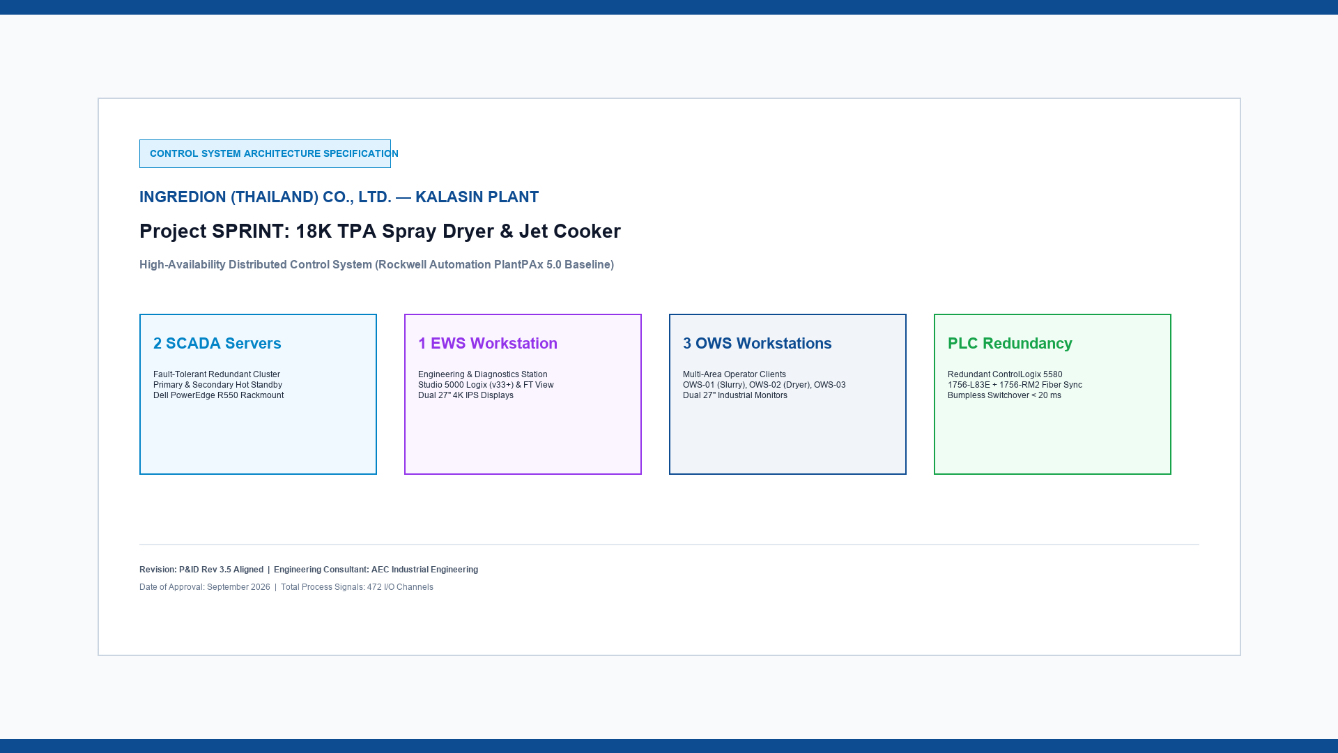
[picture p36: figure]

## Slide 2

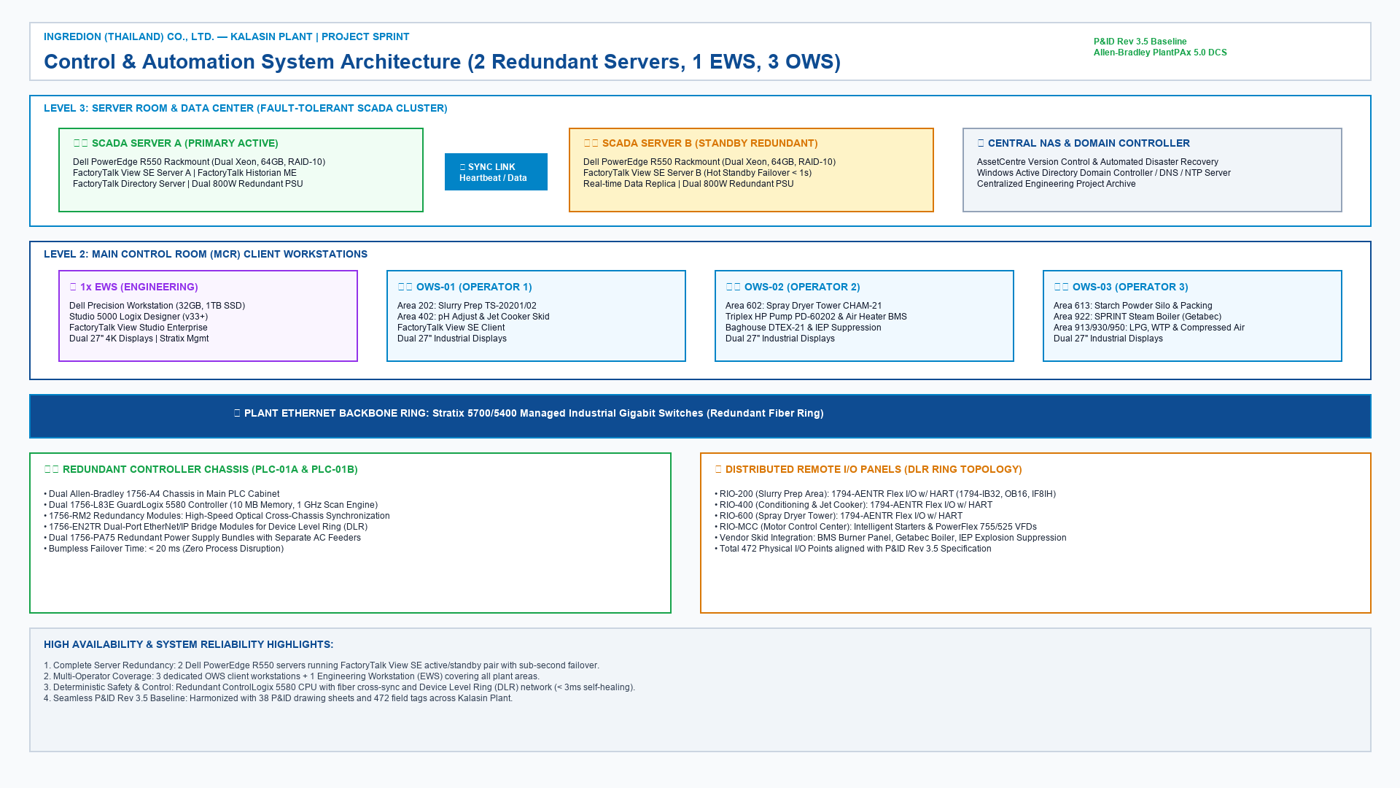
[picture p37: figure]

## Slide 3

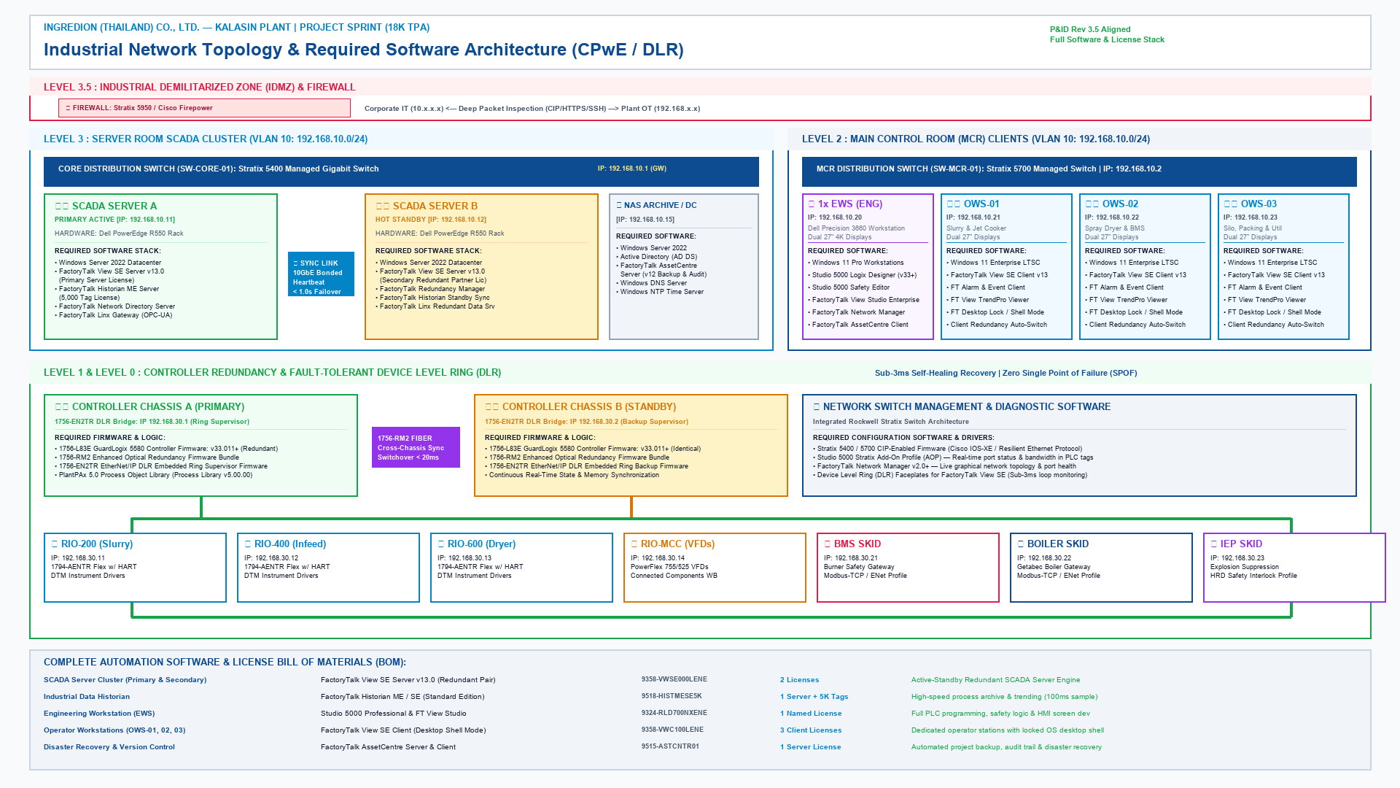
[picture p38: figure]

## Slide 4

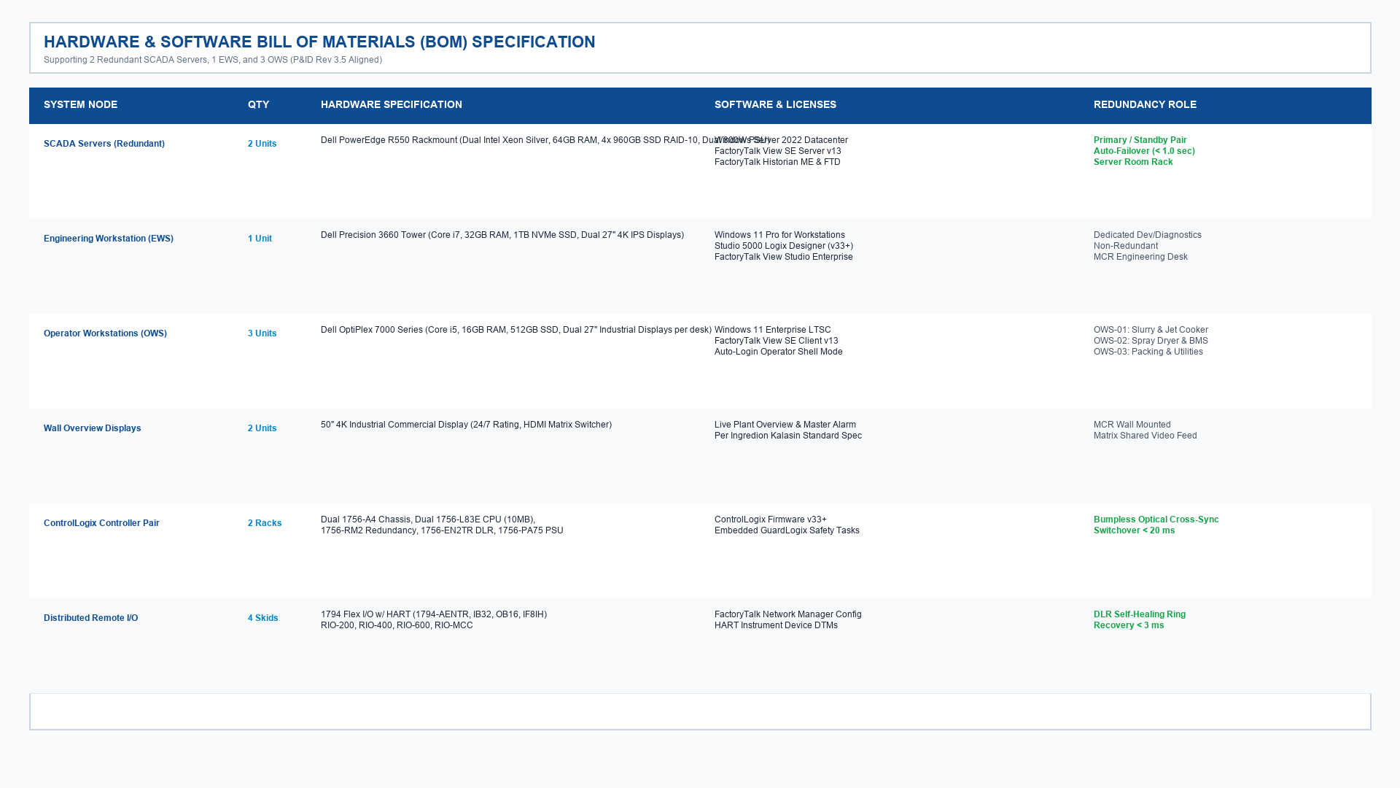
[picture p39: figure]

## Slide 5

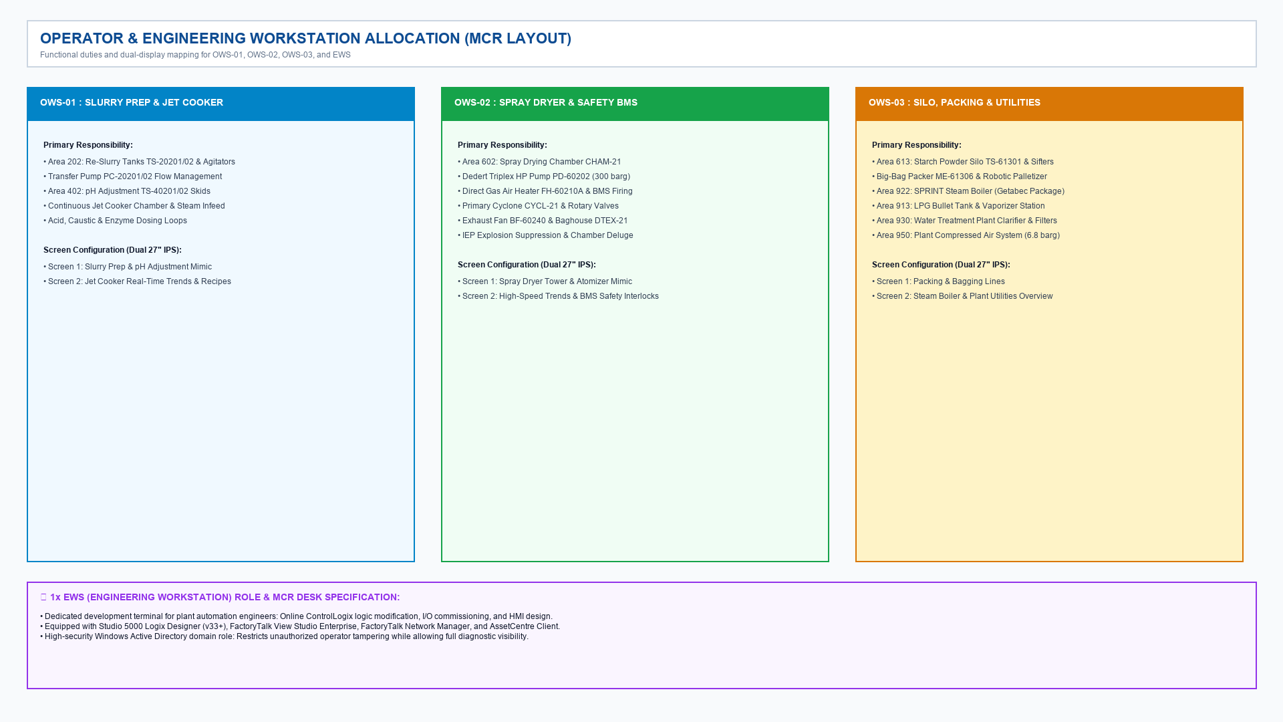
[picture p40: figure]

## Slide 6

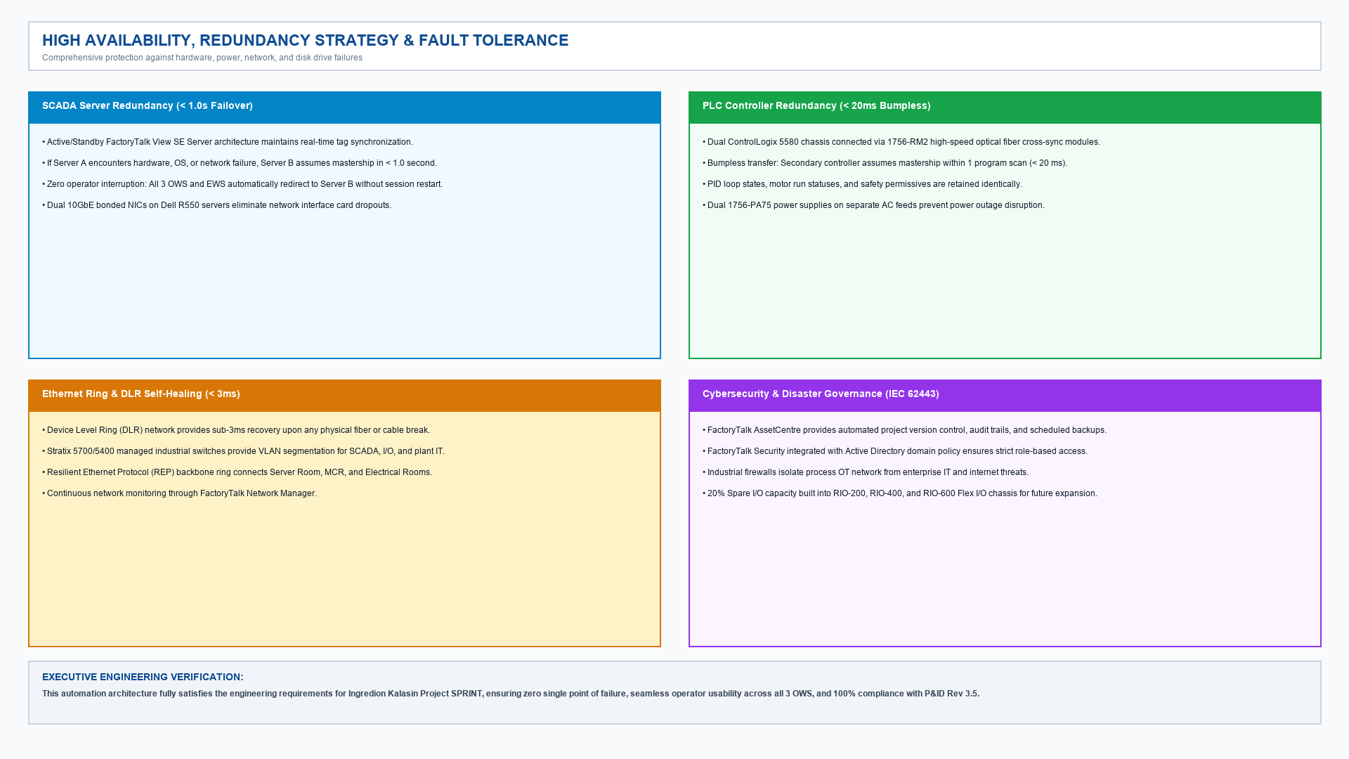
[picture p41: figure]

## Slide 7

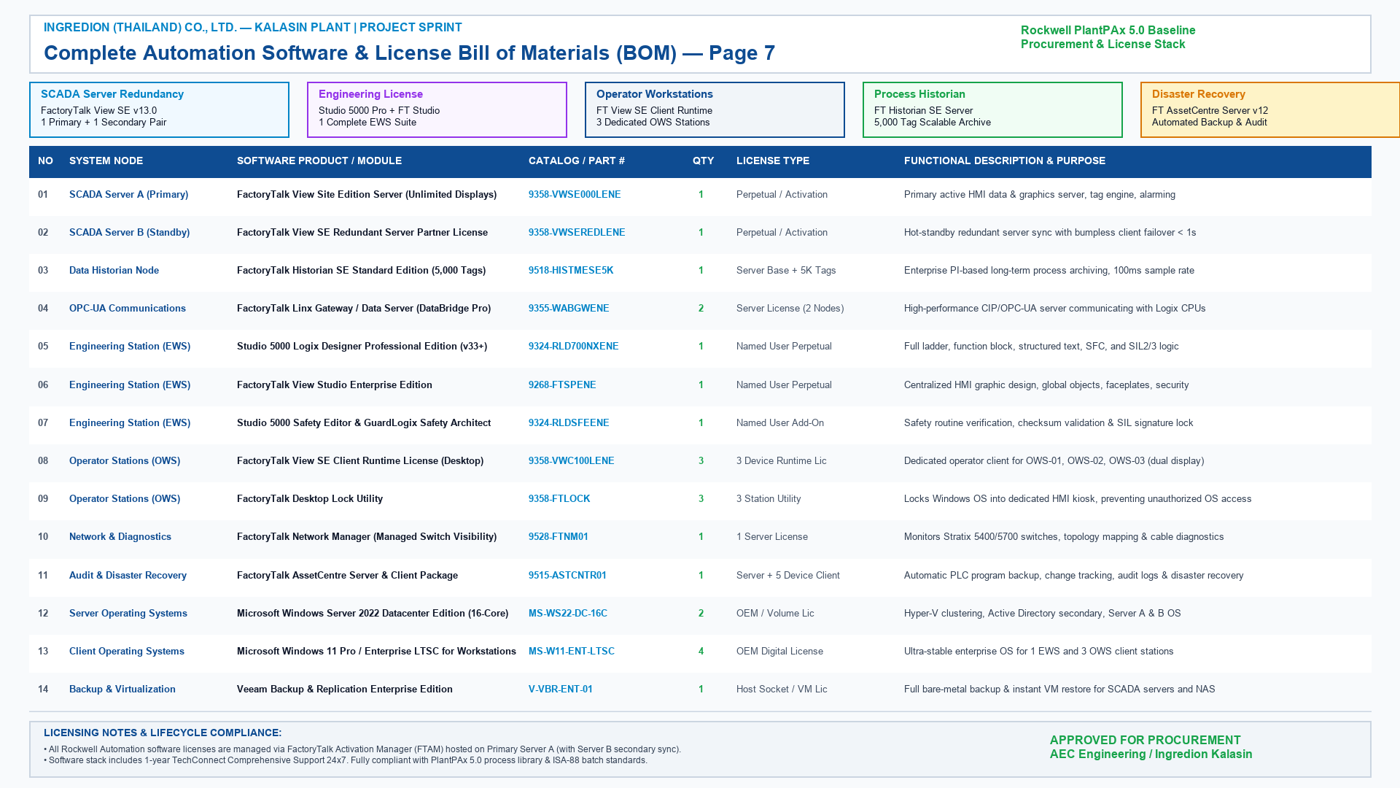
[picture p42: figure]
