x92120/x260911-002-KalasinEngineering/02_Electrical_and_eDrawing/04_PDF_Reports_and_Drawings/JB_Report_CA1.pdf

INGREDION (THAILAND) CO., LTD. | PROJECT JET COOKER | AEC INDUSTRIAL ENGINEERING | REV. 3.6
ENCLOSURE: CA1 | TYPE: Main Control Cabinet (PLC CA1) | LOCATION: Main Control Cabinet | SIZE: 1600-2000-800 mm
SUMMARY: Total Channels: 32 | Active: 0 | Spare: 32 (100.0%) | DI: 16 | DO: 16 | AI: 0 | AO: 0 | BUS: 0
No. | Terminal | Rack/Slot | Channel | I/O Module | Type Signal Characteristic Instrument Tag | | | PLC Tag Name | P&ID No. | Service / Equipment Description | Zone / Floor
1 | C1S03-X1 | C1/S3 | C1S03,00 | 1756-IB32-0 | DI | - | Spare | Spare_DI_0 | - | Spare I/O Point | Main Control Cab...
2 | C1S03-X1 | C1/S3 | C1S03,01 | 1756-IB32-1 | DI | - | Spare | Spare_DI_0 | - | Spare I/O Point | Main Control Cab...
3 | C1S03-X1 | C1/S3 | C1S03,02 | 1756-IB32-2 | DI | - | Spare | Spare_DI_0 | - | Spare I/O Point | Main Control Cab...
4 | C1S03-X1 | C1/S3 | C1S03,03 | 1756-IB32-3 | DI | - | Spare | Spare_DI_0 | - | Spare I/O Point | Main Control Cab...
5 | C1S03-X1 | C1/S3 | C1S03,04 | 1756-IB32-4 | DI | - | Spare | Spare_DI_0 | - | Spare I/O Point | Main Control Cab...
6 | C1S03-X1 | C1/S3 | C1S03,05 | 1756-IB32-5 | DI | - | Spare | Spare_DI_0 | - | Spare I/O Point | Main Control Cab...
7 | C1S03-X1 | C1/S3 | C1S03,06 | 1756-IB32-6 | DI | - | Spare | Spare_DI_0 | - | Spare I/O Point | Main Control Cab...
8 | C1S03-X1 | C1/S3 | C1S03,07 | 1756-IB32-7 | DI | - | Spare | Spare_DI_0 | - | Spare I/O Point | Main Control Cab...
9 | C1S03-X1 | C1/S3 | C1S03,08 | 1756-IB32-8 | DI | - | Spare | Spare_DI_0 | - | Spare I/O Point | Main Control Cab...
10 | C1S03-X1 | C1/S3 | C1S03,09 | 1756-IB32-9 | DI | - | Spare | Spare_DI_0 | - | Spare I/O Point | Main Control Cab...
11 | C1S03-X1 | C1/S3 | C1S03,10 | 1756-IB32-10 | DI | - | Spare | Spare_DI_0 | - | Spare I/O Point | Main Control Cab...
12 | C1S03-X1 | C1/S3 | C1S03,11 | 1756-IB32-11 | DI | - | Spare | Spare_DI_0 | - | Spare I/O Point | Main Control Cab...
13 | C1S03-X1 | C1/S3 | C1S03,12 | 1756-IB32-12 | DI | - | Spare | Spare_DI_0 | - | Spare I/O Point | Main Control Cab...
14 | C1S03-X1 | C1/S3 | C1S03,13 | 1756-IB32-13 | DI | - | Spare | Spare_DI_0 | - | Spare I/O Point | Main Control Cab...
15 | C1S03-X1 | C1/S3 | C1S03,14 | 1756-IB32-14 | DI | - | Spare | Spare_DI_0 | - | Spare I/O Point | Main Control Cab...
16 | C1S03-X1 | C1/S3 | C1S03,15 | 1756-IB32-15 | DI | - | Spare | Spare_DI_0 | - | Spare I/O Point | Main Control Cab...
17 | C1S07-X1 | C1/S7 | C1S07,00 | 1756-OB32-0 | DO | - | Spare | Spare_DO_0 | - | Spare I/O Point | -
18 | C1S07-X1 | C1/S7 | C1S07,01 | 1756-OB32-1 | DO | - | Spare | Spare_DO_0 | - | Spare I/O Point | -
19 | C1S07-X1 | C1/S7 | C1S07,02 | 1756-OB32-2 | DO | - | Spare | Spare_DO_0 | - | Spare I/O Point | -
20 | C1S07-X1 | C1/S7 | C1S07,03 | 1756-OB32-3 | DO | - | Spare | Spare_DO_0 | - | Spare I/O Point | -
21 | C1S07-X1 | C1/S7 | C1S07,04 | 1756-OB32-4 | DO | - | Spare | Spare_DO_0 | - | Spare I/O Point | -
22 | C1S07-X1 | C1/S7 | C1S07,05 | 1756-OB32-5 | DO | - | Spare | Spare_DO_0 | - | Spare I/O Point | -
23 | C1S07-X1 | C1/S7 | C1S07,06 | 1756-OB32-6 | DO | - | Spare | Spare_DO_0 | - | Spare I/O Point | -
24 | C1S07-X1 | C1/S7 | C1S07,07 | 1756-OB32-7 | DO | - | Spare | Spare_DO_0 | - | Spare I/O Point | -
25 | C1S07-X1 | C1/S7 | C1S07,08 | 1756-OB32-8 | DO | - | Spare | Spare_DO_0 | - | Spare I/O Point | -
26 | C1S07-X1 | C1/S7 | C1S07,09 | 1756-OB32-9 | DO | - | Spare | Spare_DO_0 | - | Spare I/O Point | -
27 | C1S07-X1 | C1/S7 | C1S07,10 | 1756-OB32-10 | DO | - | Spare | Spare_DO_0 | - | Spare I/O Point | -
28 | C1S07-X1 | C1/S7 | C1S07,11 | 1756-OB32-11 | DO | - | Spare | Spare_DO_0 | - | Spare I/O Point | -
29 | C1S07-X1 | C1/S7 | C1S07,12 | 1756-OB32-12 | DO | - | Spare | Spare_DO_0 | - | Spare I/O Point | -
30 | C1S07-X1 | C1/S7 | C1S07,13 | 1756-OB32-13 | DO | - | Spare | Spare_DO_0 | - | Spare I/O Point | -
31 | C1S07-X1 | C1/S7 | C1S07,14 | 1756-OB32-14 | DO | - | Spare | Spare_DO_0 | - | Spare I/O Point | -
Doc No.: Instrument I/O List (Kalasin) - CA1 | Page 1 of 2 | CONFIDENTIAL | Generated: 2026-09-07

INGREDION (THAILAND) CO., LTD. | PROJECT JET COOKER | AEC INDUSTRIAL ENGINEERING | REV. 3.6
ENCLOSURE: CA1 | TYPE: Main Control Cabinet (PLC CA1) | LOCATION: Main Control Cabinet | SIZE: 1600-2000-800 mm
SUMMARY: Total Channels: 32 | Active: 0 | Spare: 32 (100.0%) | DI: 16 | DO: 16 | AI: 0 | AO: 0 | BUS: 0
No. | Terminal | Rack/Slot | Channel | I/O Module | Type Signal Characteristic Instrument Tag | | | PLC Tag Name | P&ID No. | Service / Equipment Description | Zone / Floor
32 | C1S07-X1 | C1/S7 | C1S07,15 | 1756-OB32-15 | DO | - | Spare | Spare_DO_0 | - | Spare I/O Point | -
Doc No.: Instrument I/O List (Kalasin) - CA1 | Page 2 of 2 | CONFIDENTIAL | Generated: 2026-09-07
