x92120/x260911-002-KalasinEngineering/02_Electrical_and_eDrawing/04_PDF_Reports_and_Drawings/JB_Report_IS-JB-612.pdf

INGREDION (THAILAND) CO., LTD. | PROJECT JET COOKER | AEC INDUSTRIAL ENGINEERING | REV. 3.6
ENCLOSURE: IS-JB-612 | TYPE: Intrinsically Safe Junction Box (Ex i / LS) | LOCATION: Packing Tower 2th Floor | SIZE: 300-200-150 mm
SUMMARY: Total Channels: 41 | Active: 17 | Spare: 24 (58.5%) | DI: 31 | DO: 0 | AI: 10 | AO: 0 | BUS: 0
No. | Terminal | Rack/Slot | Channel | I/O Module | Type Signal Characteristic Instrument Tag | | | PLC Tag Name | P&ID No. | Service / Equipment Description | Zone / Floor
1 | C4S06-X1 | C4/S6 | C4S06,06 | 1756-IF16-6 | AI | 4 - 20 mA | DPT-61310 | DPT-61310_AI_1 | 3-25-01-613-PD-03 | Differential Pressure Transmitte | Packing Tower / ...
2 | C4S06-X1 | C4/S6 | C4S06,07 | 1756-IF16-7 | AI | - | DPT-61312 | DPT-61312_AI_1 | 3-25-01-613-PD-05 | - | Packing Tower / ...
3 | C4S03-X1 | C4/S3 | C4S03,00 | 1756-IB32-0 | DI | Dry Contact | ISV-61303 | ISV-61303_DI_1 | 3-25-01-613-PD-03 | 0 | Packing Tower / ...
4 | C4S03-X1 | C4/S3 | C4S03,01 | 1756-IB32-1 | DI | Dry Contact | ISV-61304 | ISV-61304_DI_1 | 3-25-01-613-PD-05 | 0 | Packing Tower / ...
5 | C4S03-X1 | C4/S3 | C4S03,02 | 1756-IB32-2 | DI | Dry Contact | LSH-61304 | LSH-61304_DI_1 | 3-25-01-613-PD-03 | 0 | Packing Tower / ...
6 | C4S03-X1 | C4/S3 | C4S03,03 | 1756-IB32-3 | DI | Dry Contact | LSH-61305 | LSH-61305_DI_1 | 3-25-01-613-PD-05 | 0 | Packing Tower / ...
7 | C4S03-X1 | C4/S3 | C4S03,04 | 1756-IB32-4 | DI | Dry Contact | LSH-61307 | LSH-61307_DI_1 | 3-25-01-613-PD-01 | 0 | Packing Tower / ...
8 | C4S03-X1 | C4/S3 | C4S03,05 | 1756-IB32-5 | DI | Dry Contact | LSH-61312 | LSH-61312_DI_1 | 3-25-01-613-PD-05 | 0 | Packing Tower / ...
9 | C4S03-X1 | C4/S3 | C4S03,06 | 1756-IB32-6 | DI | Dry Contact | PSE-61302 | PSE-61302_DI_1 | 3-25-01-613-PD-03 | 0 | Packing Tower / ...
10 | C4S03-X1 | C4/S3 | C4S03,07 | 1756-IB32-7 | DI | Dry Contact | PSE-61303 | PSE-61303_DI_1 | 3-25-01-613-PD-05 | 0 | Packing Tower / ...
11 | C4S03-X1 | C4/S3 | C4S03,09 | 1756-IB32-9 | DI | - | RV-61301 | RV-61301_DI_1 | - | - | Packing Tower / ...
12 | C4S03-X1 | C4/S3 | C4S03,10 | 1756-IB32-10 | DI | - | RV-61304 | RV-61304_DI_1 | - | - | Packing Tower / ...
13 | C4S03-X1 | C4/S3 | C4S03,11 | 1756-IB32-11 | DI | - | RV-61305 | RV-61305_DI_1 | - | - | Packing Tower / ...
14 | C4S03-X1 | C4/S3 | C4S03,12 | 1756-IB32-12 | DI | - | SC-61301 | SC-61301_DI_1 | - | - | Packing Tower / ...
15 | C4S03-X1 | C4/S3 | C4S03,13 | 1756-IB32-13 | DI | - | SC-61302 | SC-61302_DI_1 | - | - | Packing Tower / ...
16 | C4S03-X2 | C4/S3 | C4S03,16 | 1756-IB32-16 | DI | - | Spare | Spare_DI_0 | - | Spare I/O Point | -
17 | C4S03-X2 | C4/S3 | C4S03,17 | 1756-IB32-17 | DI | - | Spare | Spare_DI_0 | - | Spare I/O Point | -
18 | C4S03-X2 | C4/S3 | C4S03,18 | 1756-IB32-18 | DI | - | Spare | Spare_DI_0 | - | Spare I/O Point | -
19 | C4S03-X2 | C4/S3 | C4S03,19 | 1756-IB32-19 | DI | - | Spare | Spare_DI_0 | - | Spare I/O Point | -
20 | C4S03-X2 | C4/S3 | C4S03,20 | 1756-IB32-20 | DI | - | Spare | Spare_DI_0 | - | Spare I/O Point | -
21 | C4S03-X2 | C4/S3 | C4S03,21 | 1756-IB32-21 | DI | - | Spare | Spare_DI_0 | - | Spare I/O Point | -
22 | C4S03-X2 | C4/S3 | C4S03,22 | 1756-IB32-22 | DI | - | Spare | Spare_DI_0 | - | Spare I/O Point | -
23 | C4S03-X2 | C4/S3 | C4S03,23 | 1756-IB32-23 | DI | - | Spare | Spare_DI_0 | - | Spare I/O Point | -
24 | C4S03-X2 | C4/S3 | C4S03,24 | 1756-IB32-24 | DI | - | Spare | Spare_DI_0 | - | Spare I/O Point | -
25 | C4S03-X2 | C4/S3 | C4S03,25 | 1756-IB32-25 | DI | - | Spare | Spare_DI_0 | - | Spare I/O Point | -
26 | C4S03-X2 | C4/S3 | C4S03,26 | 1756-IB32-26 | DI | - | Spare | Spare_DI_0 | - | Spare I/O Point | -
27 | C4S03-X2 | C4/S3 | C4S03,27 | 1756-IB32-27 | DI | - | Spare | Spare_DI_0 | - | Spare I/O Point | -
28 | C4S03-X2 | C4/S3 | C4S03,28 | 1756-IB32-28 | DI | - | Spare | Spare_DI_0 | - | Spare I/O Point | -
29 | C4S03-X2 | C4/S3 | C4S03,29 | 1756-IB32-29 | DI | - | Spare | Spare_DI_0 | - | Spare I/O Point | -
30 | C4S03-X2 | C4/S3 | C4S03,30 | 1756-IB32-30 | DI | - | Spare | Spare_DI_0 | - | Spare I/O Point | -
31 | C4S03-X2 | C4/S3 | C4S03,31 | 1756-IB32-31 | DI | - | Spare | Spare_DI_0 | - | Spare I/O Point | -
Doc No.: Instrument I/O List (Kalasin) - IS-JB-612 | Page 1 of 2 | CONFIDENTIAL | Generated: 2026-09-07

INGREDION (THAILAND) CO., LTD. | PROJECT JET COOKER | AEC INDUSTRIAL ENGINEERING | REV. 3.6
ENCLOSURE: IS-JB-612 | TYPE: Intrinsically Safe Junction Box (Ex i / LS) | LOCATION: Packing Tower 2th Floor | SIZE: 300-200-150 mm
SUMMARY: Total Channels: 41 | Active: 17 | Spare: 24 (58.5%) | DI: 31 | DO: 0 | AI: 10 | AO: 0 | BUS: 0
No. | Terminal | Rack/Slot | Channel | I/O Module | Type Signal Characteristic Instrument Tag | | | PLC Tag Name | P&ID No. | Service / Equipment Description | Zone / Floor
32 | C4S05-X1 | C4/S5 | C4S05,14 | 1756-IF16-14 | AI | - | Spare | Spare_AI_0 | - | Spare I/O Point | -
33 | C4S05-X1 | C4/S5 | C4S05,14 | 1756-IF16-14 | AI | - | Spare | Spare_AI_0 | - | Spare I/O Point | -
34 | C4S05-X1 | C4/S5 | C4S05,14 | 1756-IF16-14 | AI | - | Spare | Spare_AI_0 | - | Spare I/O Point | -
35 | C4S05-X1 | C4/S5 | C4S05,14 | 1756-IF16-14 | AI | - | Spare | Spare_AI_0 | - | Spare I/O Point | -
36 | C4S05-X1 | C4/S5 | C4S05,14 | 1756-IF16-14 | AI | - | Spare | Spare_AI_0 | - | Spare I/O Point | -
37 | C4S05-X1 | C4/S5 | C4S05,14 | 1756-IF16-14 | AI | - | Spare | Spare_AI_0 | - | Spare I/O Point | -
38 | C4S05-X1 | C4/S5 | C4S05,14 | 1756-IF16-14 | AI | - | Spare | Spare_AI_0 | - | Spare I/O Point | -
39 | C4S05-X1 | C4/S5 | C4S05,14 | 1756-IF16-14 | AI | - | Spare | Spare_AI_0 | - | Spare I/O Point | -
40 | C4S03-X1 | C4/S3 | C4S03,14 | 1756-IB32-14 | DI | Dry Contact | ZS-61312 | ZS-61312_DI_1 | 3-25-01-613-PD-01 | 0 | Packing Tower / ...
41 | C4S03-X1 | C4/S3 | C4S03,15 | 1756-IB32-15 | DI | Dry Contact | ZS-61313 | ZS-61313_DI_1 | 3-25-01-613-PD-01 | 0 | Packing Tower / ...
Doc No.: Instrument I/O List (Kalasin) - IS-JB-612 | Page 2 of 2 | CONFIDENTIAL | Generated: 2026-09-07
