x92120/x260911-002-KalasinEngineering/02_Electrical_and_eDrawing/04_PDF_Reports_and_Drawings/JB_Report_JB-601.pdf

INGREDION (THAILAND) CO., LTD. | PROJECT JET COOKER | AEC INDUSTRIAL ENGINEERING | REV. 3.6
ENCLOSURE: JB-601 | TYPE: Field Junction Box (Standard) | LOCATION: Spray Dryer 1st Floor | SIZE: 500-400-200 mm
SUMMARY: Total Channels: 85 | Active: 58 | Spare: 27 (31.8%) | DI: 51 | DO: 17 | AI: 16 | AO: 0 | BUS: 1
No. | Terminal | Rack/Slot | Channel | I/O Module | Type Signal Characteristic Instrument Tag | | | PLC Tag Name | P&ID No. | Service / Equipment Description | Zone / Floor
1 | C1S10-X1 | C1/S10 | C1S10,00 | 1756-IF16-0 | AI | 4 - 20 mA | DPI-60240 | DPI-60240_AI_1 | 325-01-600-PD-05 | 0 | Spray Dryer / 1st
2 | C1S10-X1 | C1/S10 | C1S10,01 | 1756-IF16-1 | AI | 4 - 20 mA | DPT-60202 | DPT-60202_AI_1 | 3-25-01-602-PD-08 | Differential Pressure Transmitte | Spray Dryer / 1st
3 | C1S05-X2 | C1/S5 | C1S05,16 | 1756-IB32-16 | DI | 0 | ES-60202 | ES-60202_DI_1 | 325-01-600-PD-01 | 0 | Spray Dryer / 1st
4 | C1S05-X2 | C1/S5 | C1S05,17 | 1756-IB32-17 | DI | 0 | FS-60205 | FS-60205_DI_1 | 3-25-01-602-PD-01 | Flow Switch | Spray Dryer / 1st
5 | C1S10-X1 | C1/S10 | C1S10,02 | 1756-IF16-2 | AI | 4 - 20 mA | FT-60201 | FT-60201_AI_1 | 3-25-01-602-PD-08 | 0 | Spray Dryer / 1st
6 | C1S10-X1 | C1/S10 | C1S10,03 | 1756-IF16-3 | AI | 4 - 20 mA | FT-60204 | FT-60204_AI_1 | 3-25-01-602-PD-10 | 0 | Spray Dryer / 1st
7 | C1S10-X1 | C1/S10 | C1S10,04 | 1756-IF16-4 | AI | 4 - 20 mA | FT-61307 | FT-61307_AI_1 | 3-25-01-613-PD-04 | 0 | Spray Dryer / 1st
8 | C1S05-X2 | C1/S5 | C1S05,18 | 1756-IB32-18 | DI | Dry Contact | LSL-60201 | LSL-60201_DI_1 | 3-25-01-602-PD-11 | 0 | Spray Dryer / 1st
9 | C7S00- | C7/S0 | C7S00,00 | - | BUS | BUS | PCY-60205 | PCY-60205_BUS_1 | 325-01-600-PD-01 | - | Spray Dryer / 1st
10 | C7S02- | C7/S2 | C7S02,03 | - | DI | - | PCY-60205 | PCY-60205_DI_1 | 325-01-600-PD-01 | - | Spray Dryer / 1st
11 | C7S02- | C7/S2 | C7S02,04 | - | DI | - | PCY-60205 | PCY-60205_DI_2 | 325-01-600-PD-01 | - | Spray Dryer / 1st
12 | C7S03- | C7/S3 | C7S03,25 | - | DI | - | PCY-60205 | PCY-60205_DI_3 | 325-01-600-PD-01 | - | Spray Dryer / 1st
13 | C7S06- | C7/S6 | C7S06,31 | - | DO | - | PCY-60205 | PCY-60205_DO_1 | 325-01-600-PD-01 | - | Spray Dryer / 1st
14 | C1S10-X1 | C1/S10 | C1S10,05 | 1756-IF16-5 | AI | 4 - 20 mA | PT-60203 | PT-60203_AI_1 | 3-25-01-602-PD-08 | Pressure Transmitter | Spray Dryer / 1st
15 | C1S10-X1 | C1/S10 | C1S10,06 | 1756-IF16-6 | AI | 4 - 20 mA | PT-60204 | PT-60204_AI_1 | 3-25-01-602-PD-10 | Pressure Transmitter | Spray Dryer / 1st
16 | C1S10-X1 | C1/S10 | C1S10,07 | 1756-IF16-7 | AI | 4 - 20 mA | PT-60205 | PT-60205_AI_1 | 3-25-01-602-PD-01 | Pressure Transmitter | Spray Dryer / 1st
17 | C1S05-X2 | C1/S5 | C1S05,26 | 1756-IB32-26 | DI | - | Spare | Spare_DI_0 | - | Spare I/O Point | -
18 | C1S05-X2 | C1/S5 | C1S05,27 | 1756-IB32-27 | DI | - | Spare | Spare_DI_0 | - | Spare I/O Point | -
19 | C1S05-X2 | C1/S5 | C1S05,28 | 1756-IB32-28 | DI | - | Spare | Spare_DI_0 | - | Spare I/O Point | -
20 | C1S05-X2 | C1/S5 | C1S05,29 | 1756-IB32-29 | DI | - | Spare | Spare_DI_0 | - | Spare I/O Point | -
21 | C1S05-X2 | C1/S5 | C1S05,30 | 1756-IB32-30 | DI | - | Spare | Spare_DI_0 | - | Spare I/O Point | -
22 | C1S05-X2 | C1/S5 | C1S05,31 | 1756-IB32-31 | DI | - | Spare | Spare_DI_0 | - | Spare I/O Point | -
23 | C1S06-X2 | C1/S6 | C1S06,23 | 1756-IB32-23 | DI | - | Spare | Spare_DI_0 | - | Spare I/O Point | Spray Dryer / 1st
24 | C1S06-X2 | C1/S6 | C1S06,24 | 1756-IB32-24 | DI | - | Spare | Spare_DI_0 | - | Spare I/O Point | Spray Dryer / 1st
25 | C1S06-X2 | C1/S6 | C1S06,25 | 1756-IB32-25 | DI | - | Spare | Spare_DI_0 | - | Spare I/O Point | Spray Dryer / 1st
26 | C1S06-X2 | C1/S6 | C1S06,26 | 1756-IB32-26 | DI | - | Spare | Spare_DI_0 | - | Spare I/O Point | Spray Dryer / 1st
27 | C1S06-X2 | C1/S6 | C1S06,27 | 1756-IB32-27 | DI | - | Spare | Spare_DI_0 | - | Spare I/O Point | Spray Dryer / 1st
28 | C1S06-X2 | C1/S6 | C1S06,28 | 1756-IB32-28 | DI | - | Spare | Spare_DI_0 | - | Spare I/O Point | Spray Dryer / 1st
29 | C1S06-X2 | C1/S6 | C1S06,29 | 1756-IB32-29 | DI | - | Spare | Spare_DI_0 | - | Spare I/O Point | Spray Dryer / 1st
30 | C1S06-X2 | C1/S6 | C1S06,30 | 1756-IB32-30 | DI | - | Spare | Spare_DI_0 | - | Spare I/O Point | Spray Dryer / 1st
31 | C1S06-X2 | C1/S6 | C1S06,31 | 1756-IB32-31 | DI | - | Spare | Spare_DI_0 | - | Spare I/O Point | Spray Dryer / 1st
Doc No.: Instrument I/O List (Kalasin) - JB-601 | Page 1 of 3 | CONFIDENTIAL | Generated: 2026-09-07

ENCLOSURE: JB-601 | TYPE: Field Junction Box (Standard) | LOCATION: Spray Dryer 1st Floor | SIZE: 500-400-200 mm
SUMMARY: Total Channels: 85 | Active: 58 | Spare: 27 (31.8%) | DI: 51 | DO: 17 | AI: 16 | AO: 0 | BUS: 1
No. | Terminal | Rack/Slot | Channel | I/O Module | Type Signal Characteristic Instrument Tag | | | PLC Tag Name | P&ID No. | Service / Equipment Description | Zone / Floor
32 | C1S08-X2 | C1/S8 | C1S08,28 | 1756-OB32-28 | DO | - | Spare | Spare_DO_0 | - | Spare I/O Point | -
33 | C1S08-X2 | C1/S8 | C1S08,29 | 1756-OB32-29 | DO | - | Spare | Spare_DO_0 | - | Spare I/O Point | -
34 | C1S08-X2 | C1/S8 | C1S08,30 | 1756-OB32-30 | DO | - | Spare | Spare_DO_0 | - | Spare I/O Point | -
35 | C1S08-X2 | C1/S8 | C1S08,31 | 1756-OB32-31 | DO | - | Spare | Spare_DO_0 | - | Spare I/O Point | -
36 | C1S10-X1 | C1/S10 | C1S10,08 | 1756-IF16-8 | AI | - | Spare | Spare_AI_0 | - | Spare I/O Point | -
37 | C1S10-X1 | C1/S10 | C1S10,09 | 1756-IF16-9 | AI | - | Spare | Spare_AI_0 | - | Spare I/O Point | -
38 | C1S10-X1 | C1/S10 | C1S10,10 | 1756-IF16-10 | AI | - | Spare | Spare_AI_0 | - | Spare I/O Point | -
39 | C1S10-X1 | C1/S10 | C1S10,11 | 1756-IF16-11 | AI | - | Spare | Spare_AI_0 | - | Spare I/O Point | -
40 | C1S10-X1 | C1/S10 | C1S10,12 | 1756-IF16-12 | AI | - | Spare | Spare_AI_0 | - | Spare I/O Point | -
41 | C1S10-X1 | C1/S10 | C1S10,13 | 1756-IF16-13 | AI | - | Spare | Spare_AI_0 | - | Spare I/O Point | -
42 | C1S10-X1 | C1/S10 | C1S10,14 | 1756-IF16-14 | AI | - | Spare | Spare_AI_0 | - | Spare I/O Point | -
43 | C1S10-X1 | C1/S10 | C1S10,15 | 1756-IF16-15 | AI | - | Spare | Spare_AI_0 | - | Spare I/O Point | -
44 | C1S05-X2 | C1/S5 | C1S05,19 | 1756-IB32-19 | DI | 24 VDC energized | SV-60201 | SV-60201_DI_1 | 3-25-01-602-PD-08 | 0 | Spray Dryer / 1st
45 | C1S05-X2 | C1/S5 | C1S05,20 | 1756-IB32-20 | DI | 24 VDC energized | SV-60201 | SV-60201_DI_2 | 3-25-01-602-PD-08 | 0 | Spray Dryer / 1st
46 | C1S08-X2 | C1/S8 | C1S08,16 | 1756-OB32-16 | DO | 24 VDC energized | SV-60201 | SV-60201_DO_1 | 3-25-01-602-PD-08 | 0 | Spray Dryer / 1st
47 | C1S05-X2 | C1/S5 | C1S05,21 | 1756-IB32-21 | DI | 24 VDC energized | SV-60202 | SV-60202_DI_1 | 3-25-01-602-PD-08 | 0 | Spray Dryer / 1st
48 | C1S05-X2 | C1/S5 | C1S05,22 | 1756-IB32-22 | DI | 24 VDC energized | SV-60202 | SV-60202_DI_2 | 3-25-01-602-PD-08 | 0 | Spray Dryer / 1st
49 | C1S08-X2 | C1/S8 | C1S08,17 | 1756-OB32-17 | DO | 24 VDC energized | SV-60202 | SV-60202_DO_1 | 3-25-01-602-PD-08 | 0 | Spray Dryer / 1st
50 | C1S05-X2 | C1/S5 | C1S05,23 | 1756-IB32-23 | DI | 24 VDC energized | SV-60203 | SV-60203_DI_1 | 3-25-01-602-PD-08 | 0 | Spray Dryer / 1st
51 | C1S05-X2 | C1/S5 | C1S05,24 | 1756-IB32-24 | DI | 24 VDC energized | SV-60203 | SV-60203_DI_2 | 3-25-01-602-PD-08 | 0 | Spray Dryer / 1st
52 | C1S08-X2 | C1/S8 | C1S08,19 | 1756-OB32-19 | DO | 24 VDC energized | SV-60203 | SV-60203_DO_1 | 3-25-01-602-PD-08 | 0 | Spray Dryer / 1st
53 | C1S08-X2 | C1/S8 | C1S08,18 | 1756-OB32-18 | DO | 24 VDC energized | SV-60230 | SV-60230_DO_1 | 3-25-01-602-PD-04 | 0 | Spray Dryer / 1st
54 | C1S08-X2 | C1/S8 | C1S08,21 | 1756-OB32-21 | DO | 24 VDC energized | SV-60231 | SV-60231_DO_1 | 3-25-01-602-PD-04 | 0 | Spray Dryer / 1st
55 | C1S08-X2 | C1/S8 | C1S08,20 | 1756-OB32-20 | DO | 24 VDC energized | SV-60240A | SV-60240A_DO_1 | 3-25-01-602-PD-05 | 0 | Spray Dryer / 1st
56 | C1S08-X2 | C1/S8 | C1S08,22 | 1756-OB32-22 | DO | 24 VDC energized | SV-60240B | SV-60240B_DO_1 | 3-25-01-602-PD-05 | 0 | Spray Dryer / 1st
57 | C1S08-X2 | C1/S8 | C1S08,23 | 1756-OB32-23 | DO | 24 VDC energized | SV-60240C | SV-60240C_DO_1 | 3-25-01-602-PD-05 | 0 | Spray Dryer / 1st
58 | C1S05-X2 | C1/S5 | C1S05,25 | 1756-IB32-25 | DI | Dry Contact | VS-60205 | VS-60205_DI_1 | 3-25-01-602-PD-01 | Vibration Switch | Spray Dryer / 1st
59 | C1S06-X1 | C1/S6 | C1S06,00 | 1756-IB32-0 | DI | Dry Contact | XA-60202A | XA-60202A_DI_1 | 325-01-600-PD-08 | 0 | Spray Dryer / 1st
60 | C1S06-X1 | C1/S6 | C1S06,01 | 1756-IB32-1 | DI | Dry Contact | XA-60202B | XA-60202B_DI_1 | 325-01-600-PD-08 | 0 | Spray Dryer / 1st
61 | C1S06-X1 | C1/S6 | C1S06,02 | 1756-IB32-2 | DI | Dry Contact | XA-60202C | XA-60202C_DI_1 | 325-01-600-PD-08 | 0 | Spray Dryer / 1st
62 | C1S06-X1 | C1/S6 | C1S06,03 | 1756-IB32-3 | DI | Dry Contact | XA-60202D | XA-60202D_DI_1 | 325-01-600-PD-08 | 0 | Spray Dryer / 1st
Doc No.: Instrument I/O List (Kalasin) - JB-601 | Page 2 of 3 | CONFIDENTIAL | Generated: 2026-09-07

ENCLOSURE: JB-601 | TYPE: Field Junction Box (Standard) | LOCATION: Spray Dryer 1st Floor | SIZE: 500-400-200 mm
SUMMARY: Total Channels: 85 | Active: 58 | Spare: 27 (31.8%) | DI: 51 | DO: 17 | AI: 16 | AO: 0 | BUS: 1
No. | Terminal | Rack/Slot | Channel | I/O Module | Type Signal Characteristic Instrument Tag | | | PLC Tag Name | P&ID No. | Service / Equipment Description | Zone / Floor
63 | C1S06-X1 | C1/S6 | C1S06,04 | 1756-IB32-4 | DI | Dry Contact | XA-60202E | XA-60202E_DI_1 | 325-01-600-PD-08 | 0 | Spray Dryer / 1st
64 | C1S06-X1 | C1/S6 | C1S06,05 | 1756-IB32-5 | DI | Dry Contact | XA-60202F | XA-60202F_DI_1 | 325-01-600-PD-08 | 0 | Spray Dryer / 1st
65 | C1S06-X1 | C1/S6 | C1S06,06 | 1756-IB32-6 | DI | Dry Contact | XA-60202G | XA-60202G_DI_1 | 325-01-600-PD-08 | 0 | Spray Dryer / 1st
66 | C1S06-X1 | C1/S6 | C1S06,07 | 1756-IB32-7 | DI | Dry Contact | XA-60202H | XA-60202H_DI_1 | 325-01-600-PD-08 | 0 | Spray Dryer / 1st
67 | C1S06-X1 | C1/S6 | C1S06,08 | 1756-IB32-8 | DI | - | XA-60202I | XA-60202I_DI_1 | 325-01-600-PD-08 | - | Spray Dryer / 1st
68 | C1S06-X1 | C1/S6 | C1S06,09 | 1756-IB32-9 | DI | Dry Contact | XA-60202J | XA-60202J_DI_1 | 325-01-600-PD-08 | 0 | Spray Dryer / 1st
69 | C1S06-X1 | C1/S6 | C1S06,10 | 1756-IB32-10 | DI | Dry Contact | XA-60202K | XA-60202K_DI_1 | 325-01-600-PD-08 | 0 | Spray Dryer / 1st
70 | C1S06-X1 | C1/S6 | C1S06,11 | 1756-IB32-11 | DI | Dry Contact | XA-60202L | XA-60202L_DI_1 | 325-01-600-PD-08 | 0 | Spray Dryer / 1st
71 | C1S06-X1 | C1/S6 | C1S06,12 | 1756-IB32-12 | DI | Dry Contact | XA-60202M | XA-60202M_DI_1 | 325-01-600-PD-08 | 0 | Spray Dryer / 1st
72 | C1S06-X1 | C1/S6 | C1S06,13 | 1756-IB32-13 | DI | 24 VDC energized | XV-60202 | XV-60202_DI_1 | 3-25-01-602-PD-11 | 0 | Spray Dryer / 1st
73 | C1S06-X1 | C1/S6 | C1S06,14 | 1756-IB32-14 | DI | 24 VDC energized | XV-60202 | XV-60202_DI_2 | 3-25-01-602-PD-11 | 0 | Spray Dryer / 1st
74 | C1S08-X2 | C1/S8 | C1S08,26 | 1756-OB32-26 | DO | 24 VDC energized | XV-60202 | XV-60202_DO_1 | 3-25-01-602-PD-11 | 0 | Spray Dryer / 1st
75 | C1S06-X1 | C1/S6 | C1S06,15 | 1756-IB32-15 | DI | 24 VDC energized,... | XV-60205A | XV-60205A_DI_1 | 3-25-01-602-PD-01 | 0 | Spray Dryer / 1st
76 | C1S06-X2 | C1/S6 | C1S06,16 | 1756-IB32-16 | DI | 24 VDC energized,... | XV-60205A | XV-60205A_DI_2 | 3-25-01-602-PD-01 | 0 | Spray Dryer / 1st
77 | C1S08-X2 | C1/S8 | C1S08,27 | 1756-OB32-27 | DO | 24 VDC energized,... | XV-60205A | XV-60205A_DO_1 | 3-25-01-602-PD-01 | 0 | Spray Dryer / 1st
78 | C1S06-X2 | C1/S6 | C1S06,17 | 1756-IB32-17 | DI | - | XV-60240D | XV-60240D_DI_1 | 325-01-600-PD-05 | - | Spray Dryer / 1st
79 | C1S06-X2 | C1/S6 | C1S06,18 | 1756-IB32-18 | DI | - | XV-60240D | XV-60240D_DI_2 | 3-25-01-602-PD-05 | - | Spray Dryer / 1st
80 | C1S06-X2 | C1/S6 | C1S06,19 | 1756-IB32-19 | DI | - | XV-60240D | XV-60240D_DI_1 | 325-01-600-PD-05 | - | Spray Dryer / 1st
81 | C1S06-X2 | C1/S6 | C1S06,20 | 1756-IB32-20 | DI | - | XV-60240D | XV-60240D_DI_2 | 3-25-01-602-PD-05 | - | Spray Dryer / 1st
82 | C1S08-X2 | C1/S8 | C1S08,24 | 1756-OB32-24 | DO | - | XV-60240D | XV-60240D_DO_1 | 325-01-600-PD-05 | - | Spray Dryer / 1st
83 | C1S08-X2 | C1/S8 | C1S08,25 | 1756-OB32-25 | DO | 24 VDC energized | XV-60251 | XV-60251_DO_1 | 3-25-01-602-PD-01 | 0 | Infeed Tank / 1st
84 | C1S06-X2 | C1/S6 | C1S06,21 | 1756-IB32-21 | DI | 0 | YA-60205 | YA-60205_DI_1 | 325-01-600-PD-01 | 0 | Spray Dryer / 1st
85 | C1S06-X2 | C1/S6 | C1S06,22 | 1756-IB32-22 | DI | 0 | YI-60205 | YI-60205_DI_1 | 325-01-600-PD-01 | 0 | Spray Dryer / 1st
Doc No.: Instrument I/O List (Kalasin) - JB-601 | Page 3 of 3 | CONFIDENTIAL | Generated: 2026-09-07
