x92120/x260911-002-KalasinEngineering/02_Electrical_and_eDrawing/04_PDF_Reports_and_Drawings/JB_Report_JB-606.pdf

INGREDION (THAILAND) CO., LTD. | PROJECT JET COOKER | AEC INDUSTRIAL ENGINEERING | REV. 3.6
ENCLOSURE: JB-606 | TYPE: Field Junction Box (Standard) | LOCATION: Spray Dryer 6th Floor | SIZE: 300-200-150 mm
SUMMARY: Total Channels: 26 | Active: 7 | Spare: 19 (73.1%) | DI: 16 | DO: 8 | AI: 2 | AO: 0 | BUS: 0
No. | Terminal | Rack/Slot | Channel | I/O Module | Type Signal Characteristic Instrument Tag | | | PLC Tag Name | P&ID No. | Service / Equipment Description | Zone / Floor
1 | C4S05-X1 | C4/S5 | C4S05,00 | 1756-IF16-0 | AI | 4 - 20 mA | DPT-60201 | DPT-60201_AI_1 | 3-25-01-602-PD-09 | Differential Pressure Transmitte | Spray Dryer / 6th
2 | C4S01-X1 | C4/S1 | C4S01,00 | 1756-IB32-0 | DI | 4 - 20 mA | FT-60203 | FT-60203_DI_1 | 3-25-01-602-PD-09 | 0 | Spray Dryer / 6th
3 | C4S05-X1 | C4/S5 | C4S05,01 | 1756-IF16-1 | AI | 4 - 20 mA | FT-60203 | FT-60203_AI_1 | 3-25-01-602-PD-09 | 0 | Spray Dryer / 6th
4 | C4S01-X1 | C4/S1 | C4S01,01 | 1756-IB32-1 | DI | Dry Contact | LSH-60250 | LSH-60250_DI_1 | 3-25-01-602-PD-05 | 0 | Spray Dryer / 6th
5 | C4S01-X1 | C4/S1 | C4S01,04 | 1756-IB32-4 | DI | - | Spare | Spare_DI_0 | - | Spare I/O Point | -
6 | C4S01-X1 | C4/S1 | C4S01,05 | 1756-IB32-5 | DI | - | Spare | Spare_DI_0 | - | Spare I/O Point | -
7 | C4S01-X1 | C4/S1 | C4S01,06 | 1756-IB32-6 | DI | - | Spare | Spare_DI_0 | - | Spare I/O Point | -
8 | C4S01-X1 | C4/S1 | C4S01,07 | 1756-IB32-7 | DI | - | Spare | Spare_DI_0 | - | Spare I/O Point | -
9 | C4S01-X1 | C4/S1 | C4S01,08 | 1756-IB32-8 | DI | - | Spare | Spare_DI_0 | - | Spare I/O Point | -
10 | C4S01-X1 | C4/S1 | C4S01,09 | 1756-IB32-9 | DI | - | Spare | Spare_DI_0 | - | Spare I/O Point | -
11 | C4S01-X1 | C4/S1 | C4S01,10 | 1756-IB32-10 | DI | - | Spare | Spare_DI_0 | - | Spare I/O Point | -
12 | C4S01-X1 | C4/S1 | C4S01,11 | 1756-IB32-11 | DI | - | Spare | Spare_DI_0 | - | Spare I/O Point | -
13 | C4S01-X1 | C4/S1 | C4S01,12 | 1756-IB32-12 | DI | - | Spare | Spare_DI_0 | - | Spare I/O Point | -
14 | C4S01-X1 | C4/S1 | C4S01,13 | 1756-IB32-13 | DI | - | Spare | Spare_DI_0 | - | Spare I/O Point | -
15 | C4S01-X1 | C4/S1 | C4S01,14 | 1756-IB32-14 | DI | - | Spare | Spare_DI_0 | - | Spare I/O Point | -
16 | C4S01-X1 | C4/S1 | C4S01,15 | 1756-IB32-15 | DI | - | Spare | Spare_DI_0 | - | Spare I/O Point | -
17 | C4S04-X1 | C4/S4 | C4S04,01 | 1756-OB32-1 | DO | - | Spare | Spare_DO_0 | - | Spare I/O Point | Spray Dryer
18 | C4S04-X1 | C4/S4 | C4S04,02 | 1756-OB32-2 | DO | - | Spare | Spare_DO_0 | - | Spare I/O Point | Spray Dryer
19 | C4S04-X1 | C4/S4 | C4S04,03 | 1756-OB32-3 | DO | - | Spare | Spare_DO_0 | - | Spare I/O Point | Spray Dryer
20 | C4S04-X1 | C4/S4 | C4S04,04 | 1756-OB32-4 | DO | - | Spare | Spare_DO_0 | - | Spare I/O Point | Spray Dryer
21 | C4S04-X1 | C4/S4 | C4S04,05 | 1756-OB32-5 | DO | - | Spare | Spare_DO_0 | - | Spare I/O Point | Spray Dryer
22 | C4S04-X1 | C4/S4 | C4S04,06 | 1756-OB32-6 | DO | - | Spare | Spare_DO_0 | - | Spare I/O Point | Spray Dryer
23 | C4S04-X1 | C4/S4 | C4S04,07 | 1756-OB32-7 | DO | - | Spare | Spare_DO_0 | - | Spare I/O Point | Spray Dryer
24 | C4S04-X1 | C4/S4 | C4S04,00 | 1756-OB32-0 | DO | 24 VDC energized | SV-60220 | SV-60220_DO_1 | 3-25-01-602-PD-04 | 0 | Spray Dryer / 6th
25 | C4S01-X1 | C4/S1 | C4S01,02 | 1756-IB32-2 | DI | Dry Contact | XA-60261 | XA-60261_DI_1 | 325-01-600-PD-05 | 0 | Spray Dryer / 6th
26 | C4S01-X1 | C4/S1 | C4S01,03 | 1756-IB32-3 | DI | Dry Contact | XA-60262 | XA-60262_DI_1 | 325-01-600-PD-05 | 0 | Spray Dryer / 6th
Doc No.: Instrument I/O List (Kalasin) - JB-606 | Page 1 of 1 | CONFIDENTIAL | Generated: 2026-09-07
