x92120/x260911-002-KalasinEngineering/02_Electrical_and_eDrawing/04_PDF_Reports_and_Drawings/JB_Report_JB-607.pdf

INGREDION (THAILAND) CO., LTD. | PROJECT JET COOKER | AEC INDUSTRIAL ENGINEERING | REV. 3.6
ENCLOSURE: JB-607 | TYPE: Field Junction Box (Standard) | LOCATION: Spray Dryer 7th Floor | SIZE: 800-600-250 mm
SUMMARY: Total Channels: 195 | Active: 151 | Spare: 44 (22.6%) | DI: 93 | DO: 64 | AI: 32 | AO: 5 | BUS: 1
No. | Terminal | Rack/Slot | Channel | I/O Module | Type Signal Characteristic Instrument Tag | | | PLC Tag Name | P&ID No. | Service / Equipment Description | Zone / Floor
1 | C7S00- | C7/S0 | C7S00,00 | - | BUS | BUS | COM-FH-60210B | COM-FH-60210B_BUS... | 325-01-600-PD-06 | 0 | Spray Dryer / 7th
2 | C2S12-X1 | C2/S12 | C2S12,00 | 1756-IF16-0 | AI | 4 - 20 mA | FT-60207 | FT-60207_AI_1 | 3-25-01-602-PD-07 | 0 | Spray Dryer / 7th
3 | C2S12-X1 | C2/S12 | C2S12,01 | 1756-IF16-1 | AI | 4 - 20 mA | FT-60221 | FT-60221_AI_1 | 3-25-01-602-PD-04 | 0 | Spray Dryer / 7th
4 | C2S12-X1 | C2/S12 | C2S12,02 | 1756-IF16-2 | AI | 4 - 20 mA | FT-60261FA | FT-60261FA_AI_1 | 3-25-01-602-PD-02 | 0 | Spray Dryer / 7th
5 | C2S12-X1 | C2/S12 | C2S12,03 | 1756-IF16-3 | AI | 4 - 20 mA | FT-60261FB | FT-60261FB_AI_1 | 3-25-01-602-PD-02 | 0 | Spray Dryer / 7th
6 | C2S12-X1 | C2/S12 | C2S12,04 | 1756-IF16-4 | AI | 4 - 20 mA | FT-60261FC | FT-60261FC_AI_1 | 3-25-01-602-PD-02 | 0 | Spray Dryer / 7th
7 | C2S12-X1 | C2/S12 | C2S12,05 | 1756-IF16-5 | AI | 4 - 20 mA | FT-60261FD | FT-60261FD_AI_1 | 3-25-01-602-PD-02 | 0 | Spray Dryer / 7th
8 | C2S12-X1 | C2/S12 | C2S12,06 | 1756-IF16-6 | AI | 4 - 20 mA | FT-60262FE | FT-60262FE_AI_1 | 3-25-01-602-PD-02 | 0 | Spray Dryer / 7th
9 | C2S12-X1 | C2/S12 | C2S12,07 | 1756-IF16-7 | AI | 4 - 20 mA | FT-60262FF | FT-60262FF_AI_1 | 3-25-01-602-PD-02 | 0 | Spray Dryer / 7th
10 | C2S12-X1 | C2/S12 | C2S12,08 | 1756-IF16-8 | AI | 4 - 20 mA | FT-60262FG | FT-60262FG_AI_1 | 3-25-01-602-PD-02 | 0 | Spray Dryer / 7th
11 | C2S12-X1 | C2/S12 | C2S12,09 | 1756-IF16-9 | AI | 4 - 20 mA | FT-60262FH | FT-60262FH_AI_1 | 3-25-01-602-PD-02 | 0 | Spray Dryer / 7th
12 | C2S12-X1 | C2/S12 | C2S12,10 | 1756-IF16-10 | AI | 4 - 20 mA | FT-60263FJ | FT-60263FJ_AI_1 | 3-25-01-602-PD-02 | 0 | Spray Dryer / 7th
13 | C2S12-X1 | C2/S12 | C2S12,11 | 1756-IF16-11 | AI | 4 - 20 mA | FT-60263FK | FT-60263FK_AI_1 | 3-25-01-602-PD-02 | 0 | Spray Dryer / 7th
14 | C2S12-X1 | C2/S12 | C2S12,12 | 1756-IF16-12 | AI | 4 - 20 mA | FT-60263FL | FT-60263FL_AI_1 | 3-25-01-602-PD-02 | 0 | Spray Dryer / 7th
15 | C2S12-X1 | C2/S12 | C2S12,13 | 1756-IF16-13 | AI | 4 - 20 mA | FT-60263FM | FT-60263FM_AI_1 | 3-25-01-602-PD-02 | 0 | Spray Dryer / 7th
16 | C2S12-X1 | C2/S12 | C2S12,14 | 1756-IF16-14 | AI | 4 - 20 mA | FT-60264FN | FT-60264FN_AI_1 | 3-25-01-602-PD-02 | 0 | Spray Dryer / 7th
17 | C2S12-X1 | C2/S12 | C2S12,15 | 1756-IF16-15 | AI | 4 - 20 mA | FT-60264FP | FT-60264FP_AI_1 | 3-25-01-602-PD-02 | 0 | Spray Dryer / 7th
18 | C2S13-X1 | C2/S13 | C2S13,00 | 1756-IF16-0 | AI | 4 - 20 mA | FT-60264FQ | FT-60264FQ_AI_1 | 3-25-01-602-PD-02 | 0 | Spray Dryer / 7th
19 | C2S13-X1 | C2/S13 | C2S13,01 | 1756-IF16-1 | AI | 4 - 20 mA | FT-60264FR | FT-60264FR_AI_1 | 3-25-01-602-PD-02 | 0 | Spray Dryer / 7th
20 | C2S13-X1 | C2/S13 | C2S13,02 | 1756-IF16-2 | AI | 4 - 20 mA | PT-60201 | PT-60201_AI_1 | 3-25-01-602-PD-02 | Pressure Transmitter | Spray Dryer / 7th
21 | C2S13-X1 | C2/S13 | C2S13,03 | 1756-IF16-3 | AI | 4 - 20 mA | PT-60207 | PT-60207_AI_1 | 3-25-01-602-PD-07 | Pressure Transmitter | Spray Dryer / 7th
22 | C2S13-X1 | C2/S13 | C2S13,04 | 1756-IF16-4 | AI | 4 - 20 mA | PT-60221 | PT-60221_AI_1 | 3-25-01-602-PD-04 | Pressure Transmitter | Spray Dryer / 7th
23 | C2S13-X1 | C2/S13 | C2S13,05 | 1756-IF16-5 | AI | 4 - 20 mA | PT-60221 | PT-60221_AI_1 | 3-25-01-602-PD-04 | Pressure Transmitter | Spray Dryer / 7th
24 | C3S13-X1 | C3/S13 | C3S13,03 | 1756-OF8-3 | AO | - | PV-60201 | PV-60201_AO_1 | 3-25-01-602-PD-02 | - | Spray Dryer / 7th
25 | C2S05-X2 | C2/S5 | C2S05,20 | 1756-IB32-20 | DI | - | Spare | Spare_DI_0 | - | Spare I/O Point | Spray Dryer
26 | C2S05-X2 | C2/S5 | C2S05,21 | 1756-IB32-21 | DI | - | Spare | Spare_DI_0 | - | Spare I/O Point | Spray Dryer
27 | C2S05-X2 | C2/S5 | C2S05,22 | 1756-IB32-22 | DI | - | Spare | Spare_DI_0 | - | Spare I/O Point | Spray Dryer
28 | C2S05-X2 | C2/S5 | C2S05,23 | 1756-IB32-23 | DI | - | Spare | Spare_DI_0 | - | Spare I/O Point | Spray Dryer
29 | C2S05-X2 | C2/S5 | C2S05,24 | 1756-IB32-24 | DI | - | Spare | Spare_DI_0 | - | Spare I/O Point | Spray Dryer
30 | C2S05-X2 | C2/S5 | C2S05,25 | 1756-IB32-25 | DI | - | Spare | Spare_DI_0 | - | Spare I/O Point | Spray Dryer
31 | C2S05-X2 | C2/S5 | C2S05,26 | 1756-IB32-26 | DI | - | Spare | Spare_DI_0 | - | Spare I/O Point | Spray Dryer
Doc No.: Instrument I/O List (Kalasin) - JB-607 | Page 1 of 7 | CONFIDENTIAL | Generated: 2026-09-07

ENCLOSURE: JB-607 | TYPE: Field Junction Box (Standard) | LOCATION: Spray Dryer 7th Floor | SIZE: 800-600-250 mm
SUMMARY: Total Channels: 195 | Active: 151 | Spare: 44 (22.6%) | DI: 93 | DO: 64 | AI: 32 | AO: 5 | BUS: 1
No. | Terminal | Rack/Slot | Channel | I/O Module | Type Signal Characteristic Instrument Tag | | | PLC Tag Name | P&ID No. | Service / Equipment Description | Zone / Floor
32 | C2S05-X2 | C2/S5 | C2S05,27 | 1756-IB32-27 | DI | - | Spare | Spare_DI_0 | - | Spare I/O Point | Spray Dryer
33 | C2S05-X2 | C2/S5 | C2S05,28 | 1756-IB32-28 | DI | - | Spare | Spare_DI_0 | - | Spare I/O Point | Spray Dryer
34 | C2S05-X2 | C2/S5 | C2S05,29 | 1756-IB32-29 | DI | - | Spare | Spare_DI_0 | - | Spare I/O Point | Spray Dryer
35 | C2S05-X2 | C2/S5 | C2S05,30 | 1756-IB32-30 | DI | - | Spare | Spare_DI_0 | - | Spare I/O Point | Spray Dryer
36 | C2S05-X2 | C2/S5 | C2S05,31 | 1756-IB32-31 | DI | - | Spare | Spare_DI_0 | - | Spare I/O Point | Spray Dryer
37 | C2S07-X2 | C2/S7 | C2S07,31 | 1756-OB32-31 | DO | - | Spare | Spare_DO_0 | - | Spare I/O Point | -
38 | C2S08-X1 | C2/S8 | C2S08,09 | 1756-OB32-9 | DO | - | Spare | Spare_DO_0 | - | Spare I/O Point | -
39 | C2S08-X1 | C2/S8 | C2S08,10 | 1756-OB32-10 | DO | - | Spare | Spare_DO_0 | - | Spare I/O Point | -
40 | C2S08-X1 | C2/S8 | C2S08,11 | 1756-OB32-11 | DO | - | Spare | Spare_DO_0 | - | Spare I/O Point | -
41 | C2S08-X1 | C2/S8 | C2S08,12 | 1756-OB32-12 | DO | - | Spare | Spare_DO_0 | - | Spare I/O Point | -
42 | C2S08-X1 | C2/S8 | C2S08,13 | 1756-OB32-13 | DO | - | Spare | Spare_DO_0 | - | Spare I/O Point | -
43 | C2S08-X1 | C2/S8 | C2S08,14 | 1756-OB32-14 | DO | - | Spare | Spare_DO_0 | - | Spare I/O Point | -
44 | C2S08-X1 | C2/S8 | C2S08,15 | 1756-OB32-15 | DO | - | Spare | Spare_DO_0 | - | Spare I/O Point | -
45 | C2S08-X2 | C2/S8 | C2S08,16 | 1756-OB32-16 | DO | - | Spare | Spare_DO_0 | - | Spare I/O Point | -
46 | C2S08-X2 | C2/S8 | C2S08,17 | 1756-OB32-17 | DO | - | Spare | Spare_DO_0 | - | Spare I/O Point | -
47 | C2S08-X2 | C2/S8 | C2S08,18 | 1756-OB32-18 | DO | - | Spare | Spare_DO_0 | - | Spare I/O Point | -
48 | C2S08-X2 | C2/S8 | C2S08,19 | 1756-OB32-19 | DO | - | Spare | Spare_DO_0 | - | Spare I/O Point | -
49 | C2S08-X2 | C2/S8 | C2S08,20 | 1756-OB32-20 | DO | - | Spare | Spare_DO_0 | - | Spare I/O Point | -
50 | C2S08-X2 | C2/S8 | C2S08,21 | 1756-OB32-21 | DO | - | Spare | Spare_DO_0 | - | Spare I/O Point | -
51 | C2S08-X2 | C2/S8 | C2S08,22 | 1756-OB32-22 | DO | - | Spare | Spare_DO_0 | - | Spare I/O Point | -
52 | C2S08-X2 | C2/S8 | C2S08,23 | 1756-OB32-23 | DO | - | Spare | Spare_DO_0 | - | Spare I/O Point | -
53 | C2S08-X2 | C2/S8 | C2S08,24 | 1756-OB32-24 | DO | - | Spare | Spare_DO_0 | - | Spare I/O Point | -
54 | C2S08-X2 | C2/S8 | C2S08,25 | 1756-OB32-25 | DO | - | Spare | Spare_DO_0 | - | Spare I/O Point | -
55 | C2S08-X2 | C2/S8 | C2S08,26 | 1756-OB32-26 | DO | - | Spare | Spare_DO_0 | - | Spare I/O Point | -
56 | C2S08-X2 | C2/S8 | C2S08,27 | 1756-OB32-27 | DO | - | Spare | Spare_DO_0 | - | Spare I/O Point | -
57 | C2S08-X2 | C2/S8 | C2S08,28 | 1756-OB32-28 | DO | - | Spare | Spare_DO_0 | - | Spare I/O Point | -
58 | C2S08-X2 | C2/S8 | C2S08,29 | 1756-OB32-29 | DO | - | Spare | Spare_DO_0 | - | Spare I/O Point | -
59 | C2S08-X2 | C2/S8 | C2S08,30 | 1756-OB32-30 | DO | - | Spare | Spare_DO_0 | - | Spare I/O Point | -
60 | C2S08-X2 | C2/S8 | C2S08,31 | 1756-OB32-31 | DO | - | Spare | Spare_DO_0 | - | Spare I/O Point | -
61 | C2S13-X1 | C2/S13 | C2S13,11 | 1756-IF16-11 | AI | - | Spare | Spare_AI_0 | - | Spare I/O Point | -
62 | C2S13-X1 | C2/S13 | C2S13,12 | 1756-IF16-12 | AI | - | Spare | Spare_AI_0 | - | Spare I/O Point | -
Doc No.: Instrument I/O List (Kalasin) - JB-607 | Page 2 of 7 | CONFIDENTIAL | Generated: 2026-09-07

ENCLOSURE: JB-607 | TYPE: Field Junction Box (Standard) | LOCATION: Spray Dryer 7th Floor | SIZE: 800-600-250 mm
SUMMARY: Total Channels: 195 | Active: 151 | Spare: 44 (22.6%) | DI: 93 | DO: 64 | AI: 32 | AO: 5 | BUS: 1
No. | Terminal | Rack/Slot | Channel | I/O Module | Type Signal Characteristic Instrument Tag | | | PLC Tag Name | P&ID No. | Service / Equipment Description | Zone / Floor
63 | C2S13-X1 | C2/S13 | C2S13,13 | 1756-IF16-13 | AI | - | Spare | Spare_AI_0 | - | Spare I/O Point | -
64 | C2S13-X1 | C2/S13 | C2S13,14 | 1756-IF16-14 | AI | - | Spare | Spare_AI_0 | - | Spare I/O Point | -
65 | C2S13-X1 | C2/S13 | C2S13,15 | 1756-IF16-15 | AI | - | Spare | Spare_AI_0 | - | Spare I/O Point | -
66 | C3S13-X1 | C3/S13 | C3S13,05 | 1756-OF8-5 | AO | - | Spare | Spare_AO_0 | - | Spare I/O Point | -
67 | C3S13-X1 | C3/S13 | C3S13,06 | 1756-OF8-6 | AO | - | Spare | Spare_AO_0 | - | Spare I/O Point | -
68 | C3S13-X1 | C3/S13 | C3S13,07 | 1756-OF8-7 | AO | - | Spare | Spare_AO_0 | - | Spare I/O Point | -
69 | C2S03-X1 | C2/S3 | C2S03,08 | 1756-IB32-8 | DI | 24 VDC energized | SV-60207 | SV-60207_DI_1 | 3-25-01-602-PD-07 | 0 | Spray Dryer / 7th
70 | C2S03-X1 | C2/S3 | C2S03,09 | 1756-IB32-9 | DI | 24 VDC energized | SV-60207 | SV-60207_DI_2 | 3-25-01-602-PD-07 | 0 | Spray Dryer / 7th
71 | C2S07-X1 | C2/S7 | C2S07,00 | 1756-OB32-0 | DO | 24 VDC energized | SV-60207 | SV-60207_DO_1 | 3-25-01-602-PD-07 | 0 | Spray Dryer / 7th
72 | C2S13-X1 | C2/S13 | C2S13,06 | 1756-IF16-6 | AI | 4 - 20 mA | TI-FH-60210 | TI-FH-60210_AI_1 | 325-01-600-PD-06 | 0 | Spray Dryer / 7th
73 | C2S13-X1 | C2/S13 | C2S13,07 | 1756-IF16-7 | AI | 4 - 20 mA | TT-60201 | TT-60201_AI_1 | 3-25-01-602-PD-02 | 0 | Spray Dryer / 7th
74 | C2S13-X1 | C2/S13 | C2S13,08 | 1756-IF16-8 | AI | 4 - 20 mA | TT-60202 | TT-60202_AI_1 | 3-25-01-602-PD-07 | 0 | Spray Dryer / 7th
75 | C2S13-X1 | C2/S13 | C2S13,09 | 1756-IF16-9 | AI | 4 - 20 mA | TT-60207 | TT-60207_AI_1 | 3-25-01-602-PD-07 | 0 | Spray Dryer / 7th
76 | C2S13-X1 | C2/S13 | C2S13,10 | 1756-IF16-10 | AI | 4 - 20 mA | UY-FH-60210A | UY-FH-60210A_AI_1 | 325-01-600-PD-06 | 0 | Spray Dryer / 7th
77 | C3S13-X1 | C3/S13 | C3S13,04 | 1756-OF8-4 | AO | 4 - 20 mA | UY-FH-60210B | UY-FH-60210B_AO_1 | 325-01-600-PD-06 | 0 | Spray Dryer / 7th
78 | C2S03-X1 | C2/S3 | C2S03,00 | 1756-IB32-0 | DI | Dry Contact | XA-FH-60210A | XA-FH-60210A_DI_1 | 325-01-600-PD-06 | 0 | Spray Dryer / 7th
79 | C2S03-X1 | C2/S3 | C2S03,01 | 1756-IB32-1 | DI | Dry Contact | XA-FH-60210B | XA-FH-60210B_DI_1 | 325-01-600-PD-06 | 0 | Spray Dryer / 7th
80 | C2S03-X1 | C2/S3 | C2S03,02 | 1756-IB32-2 | DI | Dry Contact | XA-FH-60210C | XA-FH-60210C_DI_1 | 325-01-600-PD-06 | 0 | Spray Dryer / 7th
81 | C2S03-X1 | C2/S3 | C2S03,03 | 1756-IB32-3 | DI | Dry Contact | XA-FH-60210D | XA-FH-60210D_DI_1 | 325-01-600-PD-06 | 0 | Spray Dryer / 7th
82 | C2S03-X1 | C2/S3 | C2S03,04 | 1756-IB32-4 | DI | Dry Contact | XA-FH-60210E | XA-FH-60210E_DI_1 | 325-01-600-PD-06 | 0 | Spray Dryer / 7th
83 | C2S07-X1 | C2/S7 | C2S07,01 | 1756-OB32-1 | DO | Dry Contact | XS-FH-60210C | XS-FH-60210C_DO_1 | 325-01-600-PD-06 | 0 | Spray Dryer / 7th
84 | C2S07-X1 | C2/S7 | C2S07,02 | 1756-OB32-2 | DO | Dry Contact | XS-FH-60210D | XS-FH-60210D_DO_1 | 325-01-600-PD-06 | 0 | Spray Dryer / 7th
85 | C2S03-X2 | C2/S3 | C2S03,16 | 1756-IB32-16 | DI | 24 VDC energized | XV-60201 | XV-60201_DI_1 | 3-25-01-602-PD-02 | 0 | Spray Dryer / 7th
86 | C2S03-X2 | C2/S3 | C2S03,17 | 1756-IB32-17 | DI | 24 VDC energized | XV-60201 | XV-60201_DI_2 | 3-25-01-602-PD-02 | 0 | Spray Dryer / 7th
87 | C2S07-X1 | C2/S7 | C2S07,03 | 1756-OB32-3 | DO | 24 VDC energized | XV-60201 | XV-60201_DO_1 | 3-25-01-602-PD-02 | 0 | Spray Dryer / 7th
88 | C2S03-X2 | C2/S3 | C2S03,20 | 1756-IB32-20 | DI | - | XV-60261 | XV-60261_DI_1 | 325-01-600-PD-02 | - | Spray Dryer / 7th
89 | C2S03-X2 | C2/S3 | C2S03,21 | 1756-IB32-21 | DI | - | XV-60261 | XV-60261_DI_2 | 325-01-600-PD-02 | - | Spray Dryer / 7th
90 | C2S07-X1 | C2/S7 | C2S07,04 | 1756-OB32-4 | DO | - | XV-60261 | XV-60261_DO_1 | 325-01-600-PD-02 | - | Spray Dryer / 7th
91 | C2S03-X2 | C2/S3 | C2S03,24 | 1756-IB32-24 | DI | 24 VDC energized,... | XV-60261FA | XV-60261FA_DI_1 | 3-25-01-602-PD-02 | 0 | Spray Dryer / 7th
92 | C2S03-X2 | C2/S3 | C2S03,25 | 1756-IB32-25 | DI | 24 VDC energized,... | XV-60261FA | XV-60261FA_DI_2 | 3-25-01-602-PD-02 | 0 | Spray Dryer / 7th
93 | C2S07-X1 | C2/S7 | C2S07,05 | 1756-OB32-5 | DO | 24 VDC energized,... | XV-60261FA | XV-60261FA_DO_1 | 3-25-01-602-PD-02 | 0 | Spray Dryer / 7th
Doc No.: Instrument I/O List (Kalasin) - JB-607 | Page 3 of 7 | CONFIDENTIAL | Generated: 2026-09-07

ENCLOSURE: JB-607 | TYPE: Field Junction Box (Standard) | LOCATION: Spray Dryer 7th Floor | SIZE: 800-600-250 mm
SUMMARY: Total Channels: 195 | Active: 151 | Spare: 44 (22.6%) | DI: 93 | DO: 64 | AI: 32 | AO: 5 | BUS: 1
No. | Terminal | Rack/Slot | Channel | I/O Module | Type Signal Characteristic Instrument Tag | | | PLC Tag Name | P&ID No. | Service / Equipment Description | Zone / Floor
94 | C2S03-X2 | C2/S3 | C2S03,28 | 1756-IB32-28 | DI | 24 VDC energized,... | XV-60261FB | XV-60261FB_DI_1 | 3-25-01-602-PD-02 | 0 | Spray Dryer / 7th
95 | C2S03-X2 | C2/S3 | C2S03,29 | 1756-IB32-29 | DI | 24 VDC energized,... | XV-60261FB | XV-60261FB_DI_2 | 3-25-01-602-PD-02 | 0 | Spray Dryer / 7th
96 | C2S07-X1 | C2/S7 | C2S07,06 | 1756-OB32-6 | DO | 24 VDC energized,... | XV-60261FB | XV-60261FB_DO_1 | 3-25-01-602-PD-02 | 0 | Spray Dryer / 7th
97 | C2S04-X1 | C2/S4 | C2S04,00 | 1756-IB32-0 | DI | 24 VDC energized,... | XV-60261FC | XV-60261FC_DI_1 | 3-25-01-602-PD-02 | 0 | Spray Dryer / 7th
98 | C2S04-X1 | C2/S4 | C2S04,01 | 1756-IB32-1 | DI | 24 VDC energized,... | XV-60261FC | XV-60261FC_DI_2 | 3-25-01-602-PD-02 | 0 | Spray Dryer / 7th
99 | C2S07-X1 | C2/S7 | C2S07,07 | 1756-OB32-7 | DO | 24 VDC energized,... | XV-60261FC | XV-60261FC_DO_1 | 3-25-01-602-PD-02 | 0 | Spray Dryer / 7th
100 | C2S04-X1 | C2/S4 | C2S04,04 | 1756-IB32-4 | DI | 24 VDC energized,... | XV-60261FD | XV-60261FD_DI_1 | 3-25-01-602-PD-02 | 0 | Spray Dryer / 7th
101 | C2S04-X1 | C2/S4 | C2S04,05 | 1756-IB32-5 | DI | 24 VDC energized,... | XV-60261FD | XV-60261FD_DI_2 | 3-25-01-602-PD-02 | 0 | Spray Dryer / 7th
102 | C2S07-X1 | C2/S7 | C2S07,08 | 1756-OB32-8 | DO | 24 VDC energized,... | XV-60261FD | XV-60261FD_DO_1 | 3-25-01-602-PD-02 | 0 | Spray Dryer / 7th
103 | C2S04-X1 | C2/S4 | C2S04,08 | 1756-IB32-8 | DI | 24 VDC energized,... | XV-60261SA | XV-60261SA_DI_1 | 3-25-01-602-PD-02 | 0 | Spray Dryer / 7th
104 | C2S04-X1 | C2/S4 | C2S04,09 | 1756-IB32-9 | DI | 24 VDC energized,... | XV-60261SA | XV-60261SA_DI_2 | 3-25-01-602-PD-02 | 0 | Spray Dryer / 7th
105 | C2S07-X1 | C2/S7 | C2S07,09 | 1756-OB32-9 | DO | 24 VDC energized,... | XV-60261SA | XV-60261SA_DO_1 | 3-25-01-602-PD-02 | 0 | Spray Dryer / 7th
106 | C2S04-X1 | C2/S4 | C2S04,10 | 1756-IB32-10 | DI | 24 VDC energized,... | XV-60261SB | XV-60261SB_DI_1 | 3-25-01-602-PD-02 | 0 | Spray Dryer / 7th
107 | C2S04-X1 | C2/S4 | C2S04,11 | 1756-IB32-11 | DI | 24 VDC energized,... | XV-60261SB | XV-60261SB_DI_2 | 3-25-01-602-PD-02 | 0 | Spray Dryer / 7th
108 | C2S07-X1 | C2/S7 | C2S07,10 | 1756-OB32-10 | DO | 24 VDC energized,... | XV-60261SB | XV-60261SB_DO_1 | 3-25-01-602-PD-02 | 0 | Spray Dryer / 7th
109 | C2S04-X1 | C2/S4 | C2S04,12 | 1756-IB32-12 | DI | 24 VDC energized,... | XV-60261SC | XV-60261SC_DI_1 | 3-25-01-602-PD-02 | 0 | Spray Dryer / 7th
110 | C2S04-X1 | C2/S4 | C2S04,13 | 1756-IB32-13 | DI | 24 VDC energized,... | XV-60261SC | XV-60261SC_DI_2 | 3-25-01-602-PD-02 | 0 | Spray Dryer / 7th
111 | C2S07-X1 | C2/S7 | C2S07,11 | 1756-OB32-11 | DO | 24 VDC energized,... | XV-60261SC | XV-60261SC_DO_1 | 3-25-01-602-PD-02 | 0 | Spray Dryer / 7th
112 | C2S04-X1 | C2/S4 | C2S04,14 | 1756-IB32-14 | DI | 24 VDC energized,... | XV-60261SD | XV-60261SD_DI_1 | 3-25-01-602-PD-02 | 0 | Spray Dryer / 7th
113 | C2S04-X1 | C2/S4 | C2S04,15 | 1756-IB32-15 | DI | 24 VDC energized,... | XV-60261SD | XV-60261SD_DI_2 | 3-25-01-602-PD-02 | 0 | Spray Dryer / 7th
114 | C2S07-X1 | C2/S7 | C2S07,12 | 1756-OB32-12 | DO | 24 VDC energized,... | XV-60261SD | XV-60261SD_DO_1 | 3-25-01-602-PD-02 | 0 | Spray Dryer / 7th
115 | C2S04-X2 | C2/S4 | C2S04,16 | 1756-IB32-16 | DI | - | XV-60262 | XV-60262_DI_1 | 325-01-600-PD-02 | - | Spray Dryer / 7th
116 | C2S04-X2 | C2/S4 | C2S04,17 | 1756-IB32-17 | DI | - | XV-60262 | XV-60262_DI_2 | 325-01-600-PD-02 | - | Spray Dryer / 7th
117 | C2S07-X1 | C2/S7 | C2S07,13 | 1756-OB32-13 | DO | - | XV-60262 | XV-60262_DO_1 | 325-01-600-PD-02 | - | Spray Dryer / 7th
118 | C2S04-X2 | C2/S4 | C2S04,18 | 1756-IB32-18 | DI | 24 VDC energized,... | XV-60262FE | XV-60262FE_DI_1 | 3-25-01-602-PD-02 | 0 | Spray Dryer / 7th
119 | C2S04-X2 | C2/S4 | C2S04,19 | 1756-IB32-19 | DI | 24 VDC energized,... | XV-60262FE | XV-60262FE_DI_2 | 3-25-01-602-PD-02 | 0 | Spray Dryer / 7th
120 | C2S07-X1 | C2/S7 | C2S07,14 | 1756-OB32-14 | DO | 24 VDC energized,... | XV-60262FE | XV-60262FE_DO_1 | 3-25-01-602-PD-02 | 0 | Spray Dryer / 7th
121 | C2S04-X2 | C2/S4 | C2S04,20 | 1756-IB32-20 | DI | 24 VDC energized,... | XV-60262FF | XV-60262FF_DI_1 | 3-25-01-602-PD-02 | 0 | Spray Dryer / 7th
122 | C2S04-X2 | C2/S4 | C2S04,21 | 1756-IB32-21 | DI | 24 VDC energized,... | XV-60262FF | XV-60262FF_DI_2 | 3-25-01-602-PD-02 | 0 | Spray Dryer / 7th
123 | C2S07-X1 | C2/S7 | C2S07,15 | 1756-OB32-15 | DO | 24 VDC energized,... | XV-60262FF | XV-60262FF_DO_1 | 3-25-01-602-PD-02 | 0 | Spray Dryer / 7th
124 | C2S04-X2 | C2/S4 | C2S04,22 | 1756-IB32-22 | DI | 24 VDC energized,... | XV-60262FG | XV-60262FG_DI_1 | 3-25-01-602-PD-02 | 0 | Spray Dryer / 7th
Doc No.: Instrument I/O List (Kalasin) - JB-607 | Page 4 of 7 | CONFIDENTIAL | Generated: 2026-09-07

ENCLOSURE: JB-607 | TYPE: Field Junction Box (Standard) | LOCATION: Spray Dryer 7th Floor | SIZE: 800-600-250 mm
SUMMARY: Total Channels: 195 | Active: 151 | Spare: 44 (22.6%) | DI: 93 | DO: 64 | AI: 32 | AO: 5 | BUS: 1
No. | Terminal | Rack/Slot | Channel | I/O Module | Type Signal Characteristic Instrument Tag | | | PLC Tag Name | P&ID No. | Service / Equipment Description | Zone / Floor
125 | C2S04-X2 | C2/S4 | C2S04,23 | 1756-IB32-23 | DI | 24 VDC energized,... | XV-60262FG | XV-60262FG_DI_2 | 3-25-01-602-PD-02 | 0 | Spray Dryer / 7th
126 | C2S07-X2 | C2/S7 | C2S07,16 | 1756-OB32-16 | DO | 24 VDC energized,... | XV-60262FG | XV-60262FG_DO_1 | 3-25-01-602-PD-02 | 0 | Spray Dryer / 7th
127 | C2S04-X2 | C2/S4 | C2S04,24 | 1756-IB32-24 | DI | 24 VDC energized,... | XV-60262FH | XV-60262FH_DI_1 | 3-25-01-602-PD-02 | 0 | Spray Dryer / 7th
128 | C2S04-X2 | C2/S4 | C2S04,25 | 1756-IB32-25 | DI | 24 VDC energized,... | XV-60262FH | XV-60262FH_DI_2 | 3-25-01-602-PD-02 | 0 | Spray Dryer / 7th
129 | C2S07-X2 | C2/S7 | C2S07,17 | 1756-OB32-17 | DO | 24 VDC energized,... | XV-60262FH | XV-60262FH_DO_1 | 3-25-01-602-PD-02 | 0 | Spray Dryer / 7th
130 | C2S04-X2 | C2/S4 | C2S04,26 | 1756-IB32-26 | DI | 24 VDC energized,... | XV-60262SE | XV-60262SE_DI_1 | 3-25-01-602-PD-02 | 0 | Spray Dryer / 7th
131 | C2S04-X2 | C2/S4 | C2S04,27 | 1756-IB32-27 | DI | 24 VDC energized,... | XV-60262SE | XV-60262SE_DI_2 | 3-25-01-602-PD-02 | 0 | Spray Dryer / 7th
132 | C2S07-X2 | C2/S7 | C2S07,18 | 1756-OB32-18 | DO | 24 VDC energized,... | XV-60262SE | XV-60262SE_DO_1 | 3-25-01-602-PD-02 | 0 | Spray Dryer / 7th
133 | C2S04-X2 | C2/S4 | C2S04,28 | 1756-IB32-28 | DI | 24 VDC energized,... | XV-60262SF | XV-60262SF_DI_1 | 3-25-01-602-PD-02 | 0 | Spray Dryer / 7th
134 | C2S04-X2 | C2/S4 | C2S04,29 | 1756-IB32-29 | DI | 24 VDC energized,... | XV-60262SF | XV-60262SF_DI_2 | 3-25-01-602-PD-02 | 0 | Spray Dryer / 7th
135 | C2S07-X2 | C2/S7 | C2S07,19 | 1756-OB32-19 | DO | 24 VDC energized,... | XV-60262SF | XV-60262SF_DO_1 | 3-25-01-602-PD-02 | 0 | Spray Dryer / 7th
136 | C2S04-X2 | C2/S4 | C2S04,30 | 1756-IB32-30 | DI | 24 VDC energized,... | XV-60262SG | XV-60262SG_DI_1 | 3-25-01-602-PD-02 | 0 | Spray Dryer / 7th
137 | C2S04-X2 | C2/S4 | C2S04,31 | 1756-IB32-31 | DI | 24 VDC energized,... | XV-60262SG | XV-60262SG_DI_2 | 3-25-01-602-PD-02 | 0 | Spray Dryer / 7th
138 | C2S07-X2 | C2/S7 | C2S07,20 | 1756-OB32-20 | DO | 24 VDC energized,... | XV-60262SG | XV-60262SG_DO_1 | 3-25-01-602-PD-02 | 0 | Spray Dryer / 7th
139 | C2S05-X1 | C2/S5 | C2S05,00 | 1756-IB32-0 | DI | 24 VDC energized,... | XV-60262SH | XV-60262SH_DI_1 | 3-25-01-602-PD-02 | 0 | Spray Dryer / 7th
140 | C2S05-X1 | C2/S5 | C2S05,01 | 1756-IB32-1 | DI | 24 VDC energized,... | XV-60262SH | XV-60262SH_DI_2 | 3-25-01-602-PD-02 | 0 | Spray Dryer / 7th
141 | C2S07-X2 | C2/S7 | C2S07,21 | 1756-OB32-21 | DO | 24 VDC energized,... | XV-60262SH | XV-60262SH_DO_1 | 3-25-01-602-PD-02 | 0 | Spray Dryer / 7th
142 | C2S05-X1 | C2/S5 | C2S05,02 | 1756-IB32-2 | DI | - | XV-60263 | XV-60263_DI_1 | 325-01-600-PD-02 | - | Spray Dryer / 7th
143 | C2S05-X1 | C2/S5 | C2S05,03 | 1756-IB32-3 | DI | - | XV-60263 | XV-60263_DI_2 | 325-01-600-PD-02 | - | Spray Dryer / 7th
144 | C2S07-X2 | C2/S7 | C2S07,22 | 1756-OB32-22 | DO | - | XV-60263 | XV-60263_DO_1 | 325-01-600-PD-02 | - | Spray Dryer / 7th
145 | C2S05-X1 | C2/S5 | C2S05,04 | 1756-IB32-4 | DI | 24 VDC energized,... | XV-60263FJ | XV-60263FJ_DI_1 | 3-25-01-602-PD-02 | 0 | Spray Dryer / 7th
146 | C2S05-X1 | C2/S5 | C2S05,05 | 1756-IB32-5 | DI | 24 VDC energized,... | XV-60263FJ | XV-60263FJ_DI_2 | 3-25-01-602-PD-02 | 0 | Spray Dryer / 7th
147 | C2S07-X2 | C2/S7 | C2S07,23 | 1756-OB32-23 | DO | 24 VDC energized,... | XV-60263FJ | XV-60263FJ_DO_1 | 3-25-01-602-PD-02 | 0 | Spray Dryer / 7th
148 | C2S05-X1 | C2/S5 | C2S05,06 | 1756-IB32-6 | DI | 24 VDC energized,... | XV-60263FK | XV-60263FK_DI_1 | 3-25-01-602-PD-02 | 0 | Spray Dryer / 7th
149 | C2S05-X1 | C2/S5 | C2S05,07 | 1756-IB32-7 | DI | 24 VDC energized,... | XV-60263FK | XV-60263FK_DI_2 | 3-25-01-602-PD-02 | 0 | Spray Dryer / 7th
150 | C2S07-X2 | C2/S7 | C2S07,24 | 1756-OB32-24 | DO | 24 VDC energized,... | XV-60263FK | XV-60263FK_DO_1 | 3-25-01-602-PD-02 | 0 | Spray Dryer / 7th
151 | C2S05-X1 | C2/S5 | C2S05,08 | 1756-IB32-8 | DI | 24 VDC energized,... | XV-60263FL | XV-60263FL_DI_1 | 3-25-01-602-PD-02 | 0 | Spray Dryer / 7th
152 | C2S05-X1 | C2/S5 | C2S05,09 | 1756-IB32-9 | DI | 24 VDC energized,... | XV-60263FL | XV-60263FL_DI_2 | 3-25-01-602-PD-02 | 0 | Spray Dryer / 7th
153 | C2S07-X2 | C2/S7 | C2S07,25 | 1756-OB32-25 | DO | 24 VDC energized,... | XV-60263FL | XV-60263FL_DO_1 | 3-25-01-602-PD-02 | 0 | Spray Dryer / 7th
154 | C2S05-X1 | C2/S5 | C2S05,10 | 1756-IB32-10 | DI | 24 VDC energized,... | XV-60263FM | XV-60263FM_DI_1 | 3-25-01-602-PD-02 | 0 | Spray Dryer / 7th
155 | C2S05-X1 | C2/S5 | C2S05,11 | 1756-IB32-11 | DI | 24 VDC energized,... | XV-60263FM | XV-60263FM_DI_2 | 3-25-01-602-PD-02 | 0 | Spray Dryer / 7th
Doc No.: Instrument I/O List (Kalasin) - JB-607 | Page 5 of 7 | CONFIDENTIAL | Generated: 2026-09-07
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
