x92120/x260911-002-KalasinEngineering/02_Electrical_and_eDrawing/04_PDF_Reports_and_Drawings/JB_Report_JB-612.pdf

INGREDION (THAILAND) CO., LTD. | PROJECT JET COOKER | AEC INDUSTRIAL ENGINEERING | REV. 3.6
ENCLOSURE: JB-612 | TYPE: Field Junction Box (Standard) | LOCATION: Packing Tower 2th Floor | SIZE: 450-300-150 mm
SUMMARY: Total Channels: 57 | Active: 37 | Spare: 20 (35.1%) | DI: 32 | DO: 16 | AI: 8 | AO: 0 | BUS: 1
No. | Terminal | Rack/Slot | Channel | I/O Module | Type Signal Characteristic Instrument Tag | | | PLC Tag Name | P&ID No. | Service / Equipment Description | Zone / Floor
1 | C7S00- | C7/S0 | C7S00,00 | - | BUS | BUS | Communication S... | Communication Signa... | 325-01-613-PD-02 | - | Packing Tower / ...
2 | C4S02-X1 | C4/S2 | C4S02,00 | 1756-IB32-0 | DI | Dry Contact | PSL-61305 | PSL-61305_DI_1 | 3-25-01-613-PD-03 | 0 | Packing Tower / ...
3 | C4S02-X1 | C4/S2 | C4S02,01 | 1756-IB32-1 | DI | Dry Contact | PSL-61306 | PSL-61306_DI_1 | 3-25-01-613-PD-05 | 0 | Packing Tower / ...
4 | C4S05-X1 | C4/S5 | C4S05,08 | 1756-IF16-8 | AI | 4 - 20 mA | PT-61302 | PT-61302_AI_1 | 3-25-01-613-PD-03 | Pressure Transmitter | Packing Tower / ...
5 | C4S05-X1 | C4/S5 | C4S05,12 | 1756-IF16-12 | AI | 4 - 20 mA | PT-61302 | PT-61302_AI_1 | 3-25-01-613-PD-03 | Pressure Transmitter | Packing Tower / ...
6 | C4S05-X1 | C4/S5 | C4S05,09 | 1756-IF16-9 | AI | 4 - 20 mA | PT-61309 | PT-61309_AI_1 | 3-25-01-613-PD-04 | Pressure Transmitter | Packing Tower / ...
7 | C4S05-X1 | C4/S5 | C4S05,13 | 1756-IF16-13 | AI | 4 - 20 mA | PT-61309 | PT-61309_AI_1 | 3-25-01-613-PD-04 | Pressure Transmitter | Packing Tower / ...
8 | C4S02-X1 | C4/S2 | C4S02,02 | 1756-IB32-2 | DI | - | PVM-61301 | PVM-61301_DI_1 | 325-01-613-PD-03 | - | Packing Tower / ...
9 | C4S02-X1 | C4/S2 | C4S02,03 | 1756-IB32-3 | DI | - | PVM-61301 | PVM-61301_DI_2 | 325-01-613-PD-03 | - | Packing Tower / ...
10 | C4S04-X2 | C4/S4 | C4S04,16 | 1756-OB32-16 | DO | - | PVM-61301 | PVM-61301_DO_1 | 325-01-613-PD-03 | - | Packing Tower / ...
11 | C4S04-X2 | C4/S4 | C4S04,17 | 1756-OB32-17 | DO | - | PVM-61301 | PVM-61301_DO_2 | 325-01-613-PD-03 | - | Packing Tower / ...
12 | C4S02-X2 | C4/S2 | C4S02,17 | 1756-IB32-17 | DI | - | Spare | Spare_DI_0 | - | Spare I/O Point | -
13 | C4S02-X2 | C4/S2 | C4S02,18 | 1756-IB32-18 | DI | - | Spare | Spare_DI_0 | - | Spare I/O Point | -
14 | C4S02-X2 | C4/S2 | C4S02,19 | 1756-IB32-19 | DI | - | Spare | Spare_DI_0 | - | Spare I/O Point | -
15 | C4S02-X2 | C4/S2 | C4S02,20 | 1756-IB32-20 | DI | - | Spare | Spare_DI_0 | - | Spare I/O Point | -
16 | C4S02-X2 | C4/S2 | C4S02,21 | 1756-IB32-21 | DI | - | Spare | Spare_DI_0 | - | Spare I/O Point | -
17 | C4S02-X2 | C4/S2 | C4S02,22 | 1756-IB32-22 | DI | - | Spare | Spare_DI_0 | - | Spare I/O Point | -
18 | C4S02-X2 | C4/S2 | C4S02,23 | 1756-IB32-23 | DI | - | Spare | Spare_DI_0 | - | Spare I/O Point | -
19 | C4S02-X2 | C4/S2 | C4S02,24 | 1756-IB32-24 | DI | - | Spare | Spare_DI_0 | - | Spare I/O Point | -
20 | C4S02-X2 | C4/S2 | C4S02,25 | 1756-IB32-25 | DI | - | Spare | Spare_DI_0 | - | Spare I/O Point | -
21 | C4S02-X2 | C4/S2 | C4S02,26 | 1756-IB32-26 | DI | - | Spare | Spare_DI_0 | - | Spare I/O Point | -
22 | C4S02-X2 | C4/S2 | C4S02,27 | 1756-IB32-27 | DI | - | Spare | Spare_DI_0 | - | Spare I/O Point | -
23 | C4S02-X2 | C4/S2 | C4S02,28 | 1756-IB32-28 | DI | - | Spare | Spare_DI_0 | - | Spare I/O Point | -
24 | C4S02-X2 | C4/S2 | C4S02,29 | 1756-IB32-29 | DI | - | Spare | Spare_DI_0 | - | Spare I/O Point | -
25 | C4S02-X2 | C4/S2 | C4S02,30 | 1756-IB32-30 | DI | - | Spare | Spare_DI_0 | - | Spare I/O Point | -
26 | C4S02-X2 | C4/S2 | C4S02,31 | 1756-IB32-31 | DI | - | Spare | Spare_DI_0 | - | Spare I/O Point | -
27 | C4S04-X2 | C4/S4 | C4S04,31 | 1756-OB32-31 | DO | - | Spare | Spare_DO_0 | - | Spare I/O Point | Packing Tower
28 | C4S05-X1 | C4/S5 | C4S05,10 | 1756-IF16-10 | AI | - | Spare | Spare_AI_0 | - | Spare I/O Point | -
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
