x92120/x260911-002-KalasinEngineering/01_Network_Design/05_Drawings_and_Schematics/ControlLogix_5Chassis_DLR_Network_and_Rack_Design.png

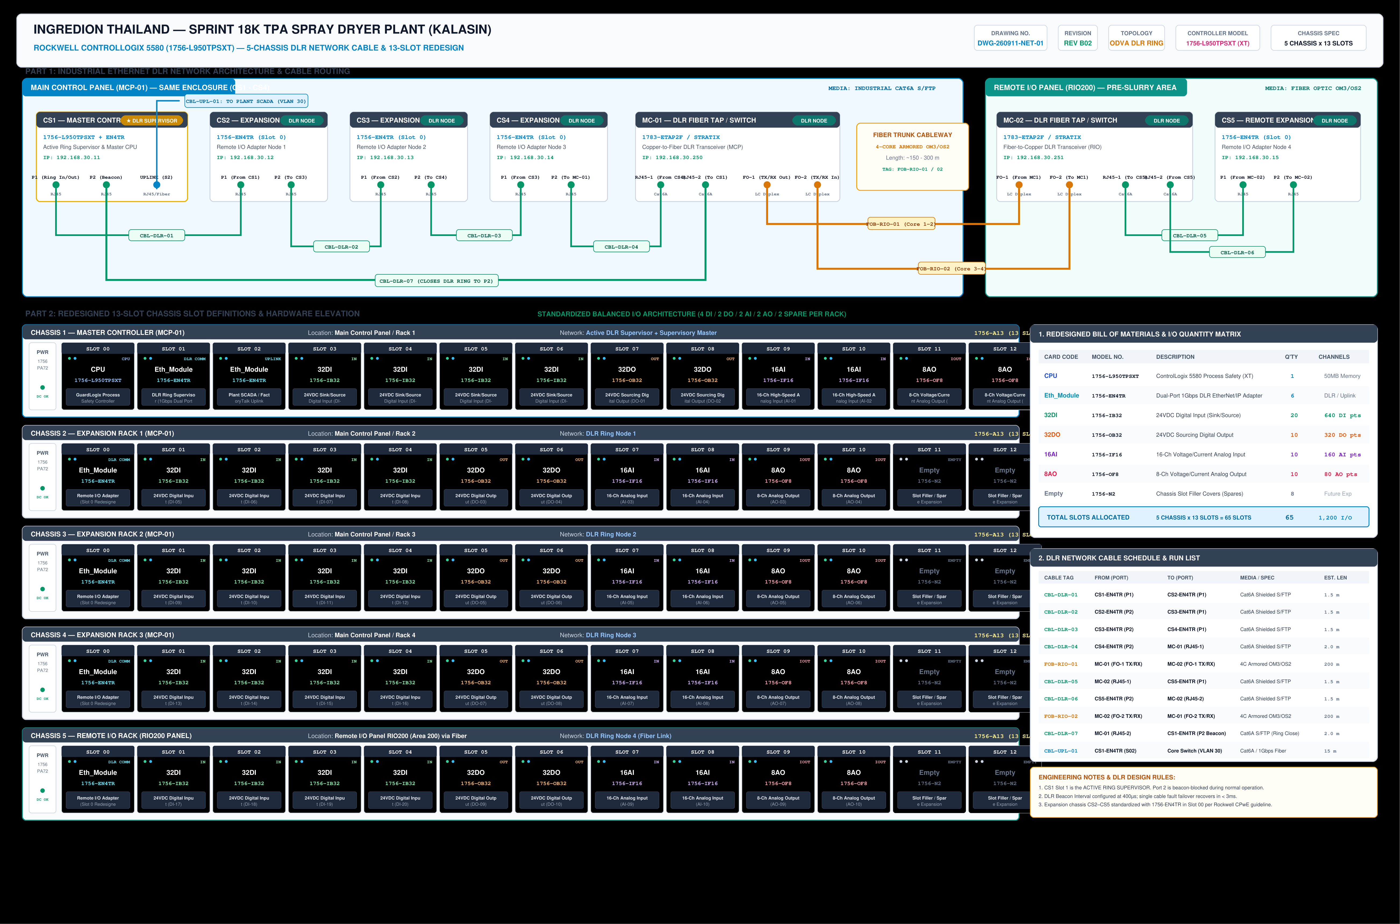
01_Network_Design/05_Drawings_and_Schematics/ControlLogix_5Chassis_DLR_Network_and_Rack_Design.png
