x92120/x260911-002-KalasinEngineering/01_Network_Design/05_Drawings_and_Schematics/Redundant_Cisco_Core_and_Server_Network_Diagram.png

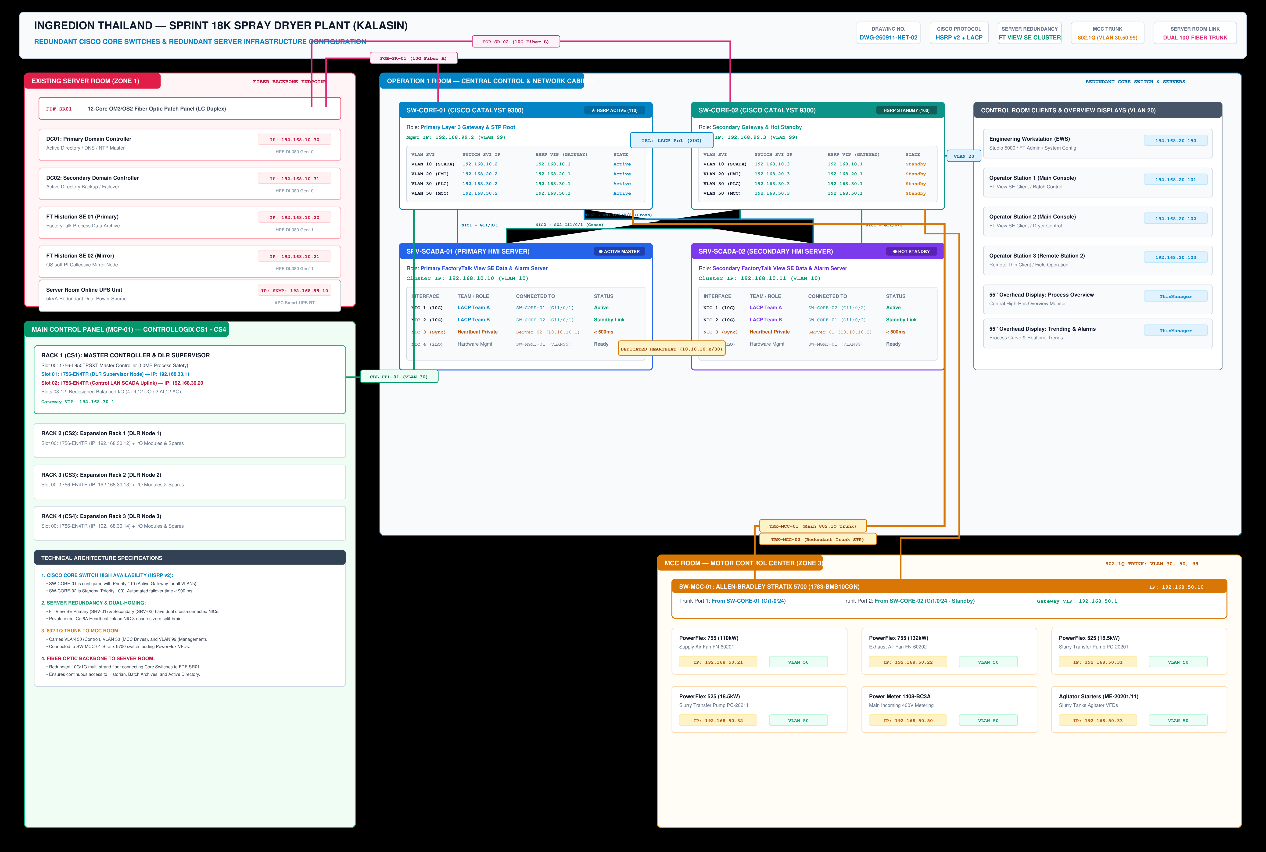
01_Network_Design/05_Drawings_and_Schematics/Redundant_Cisco_Core_and_Server_Network_Diagram.png
