x92120/x260911-002-KalasinEngineering/01_Network_Design/05_Drawings_and_Schematics/SPRINT_18K_Control_Layout_System_Architecture.png

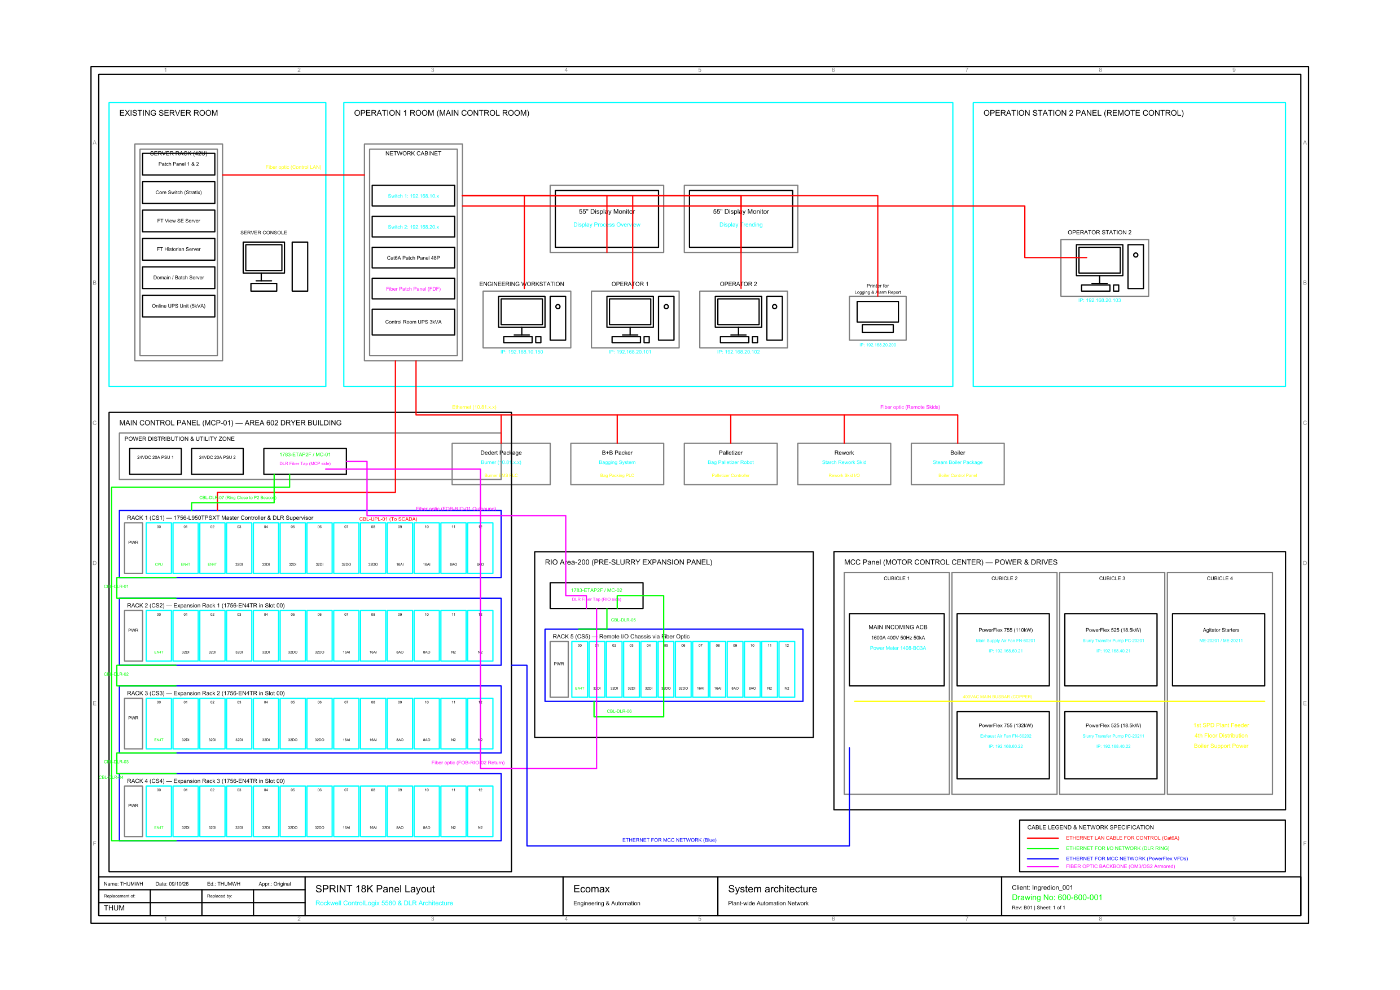
01_Network_Design/05_Drawings_and_Schematics/SPRINT_18K_Control_Layout_System_Architecture.png
