x92120/x260911-002-KalasinEngineering/02_Electrical_and_eDrawing/04_PDF_Reports_and_Drawings/cable_schedule_slide_8.png

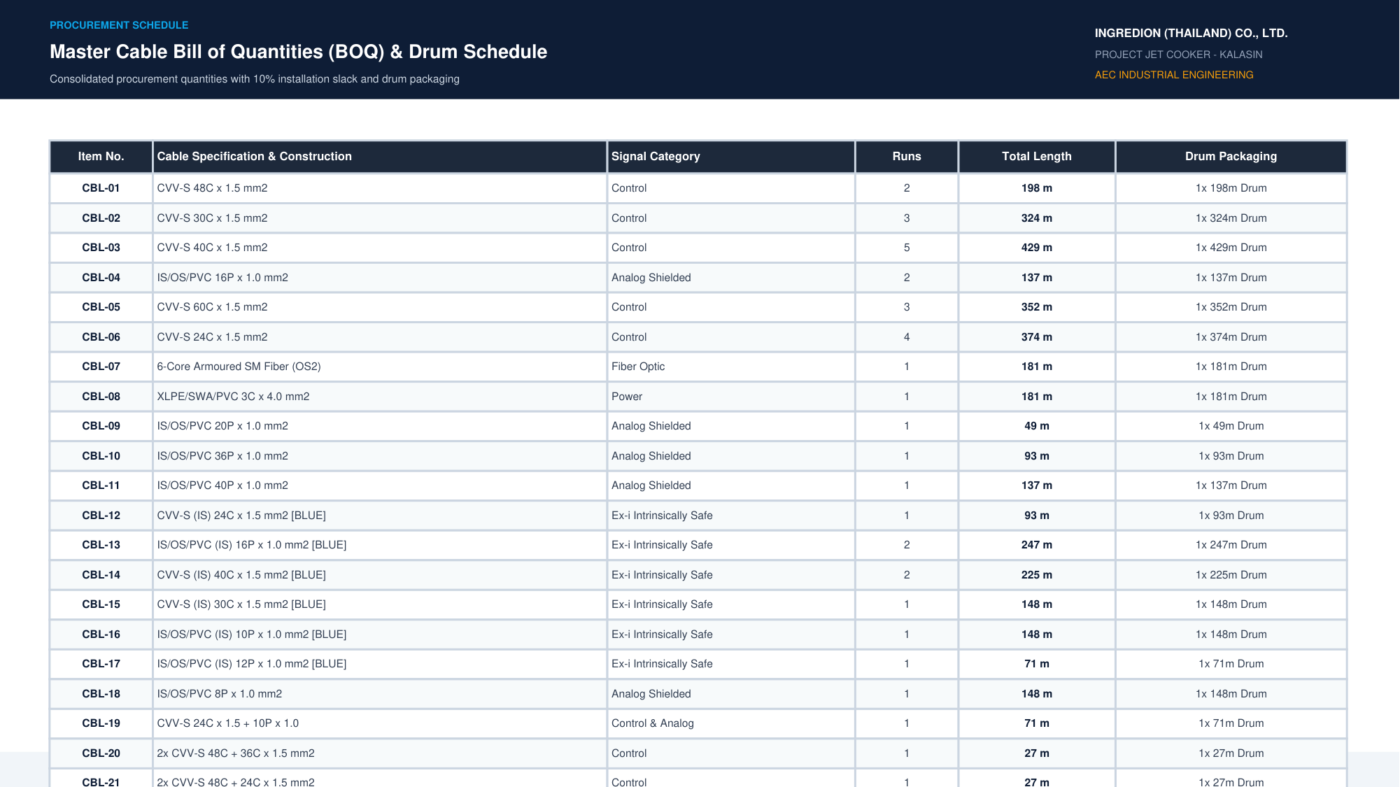
02_Electrical_and_eDrawing/04_PDF_Reports_and_Drawings/cable_schedule_slide_8.png
