x92120/x260911-002-KalasinEngineering/02_Electrical_and_eDrawing/06_SCADA_Demo/01_Plant_Overview_HMI.png

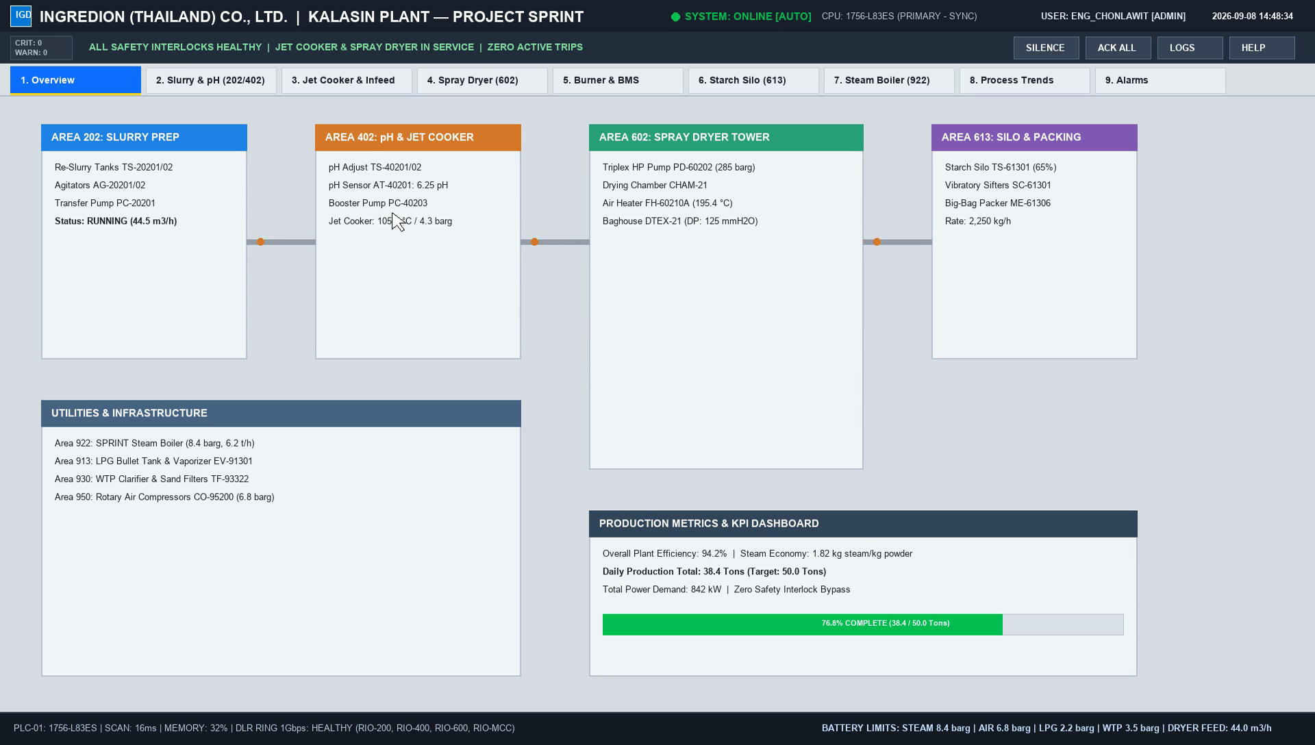
02_Electrical_and_eDrawing/06_SCADA_Demo/01_Plant_Overview_HMI.png
