x92120/x260911-002-KalasinEngineering/02_Electrical_and_eDrawing/06_SCADA_Demo/02_Area202_402_Slurry_JetCooker.png

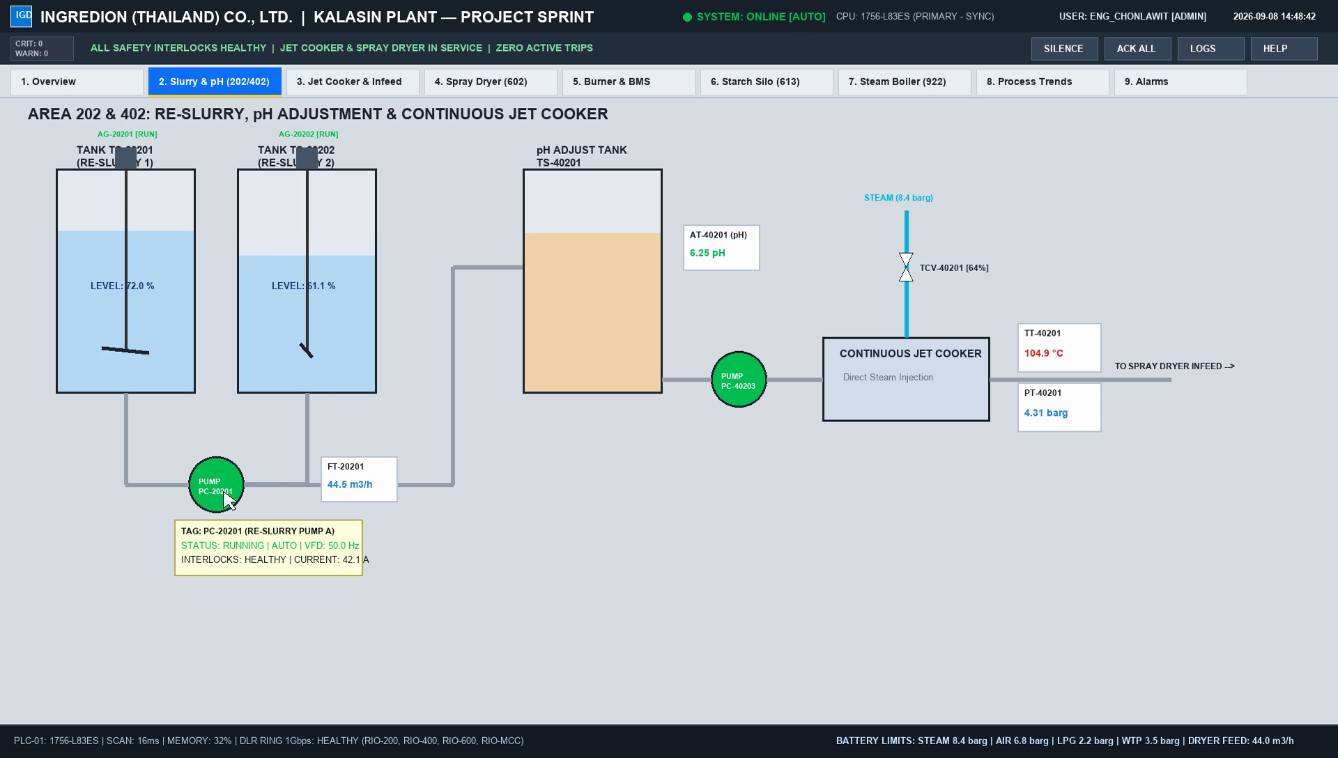
02_Electrical_and_eDrawing/06_SCADA_Demo/02_Area202_402_Slurry_JetCooker.png
