x92120/x260911-002-KalasinEngineering/02_Electrical_and_eDrawing/06_SCADA_Demo/03_Area602_Spray_Dryer_Tower.png

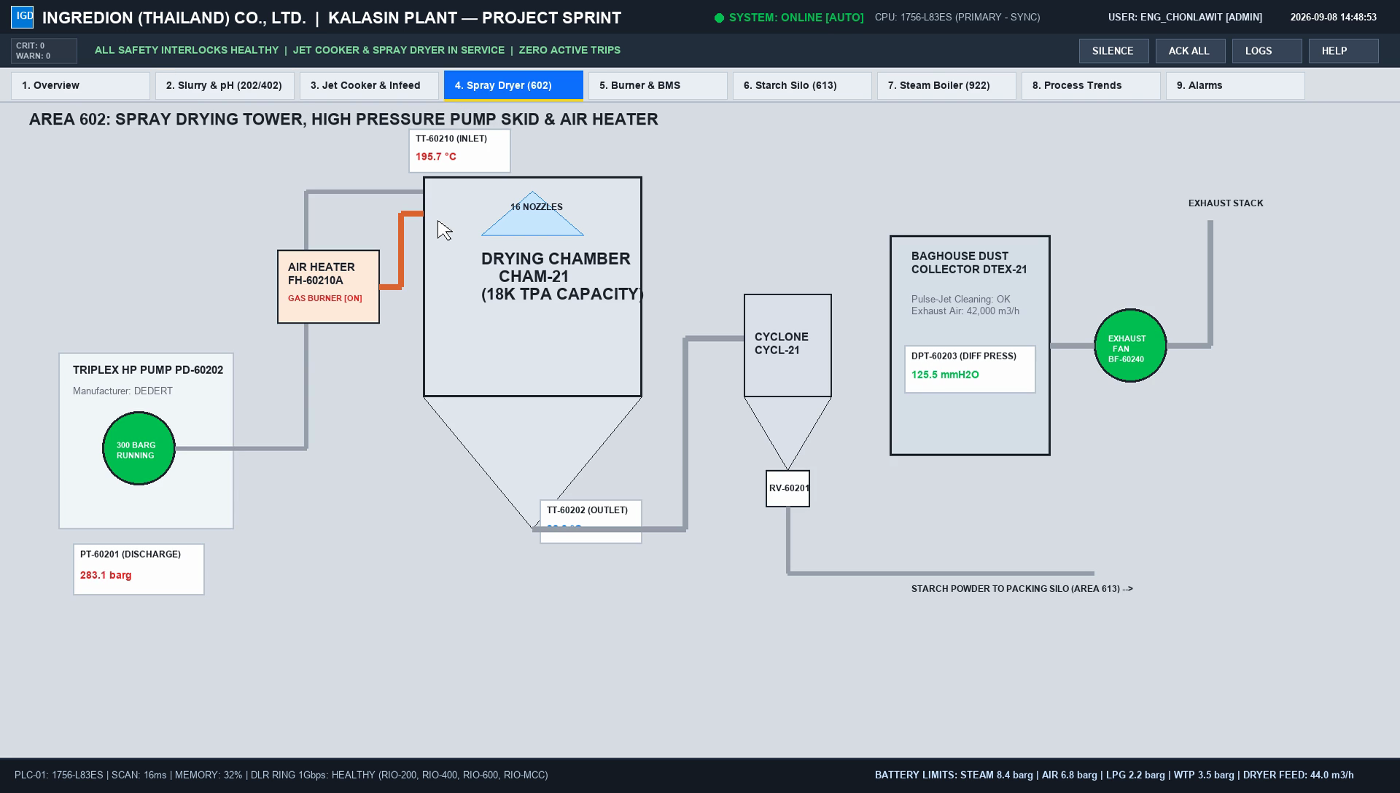
02_Electrical_and_eDrawing/06_SCADA_Demo/03_Area602_Spray_Dryer_Tower.png
