x92120/x260911-002-KalasinEngineering/02_Electrical_and_eDrawing/06_SCADA_Demo/04_PlantPAx_Faceplate_Interaction.png

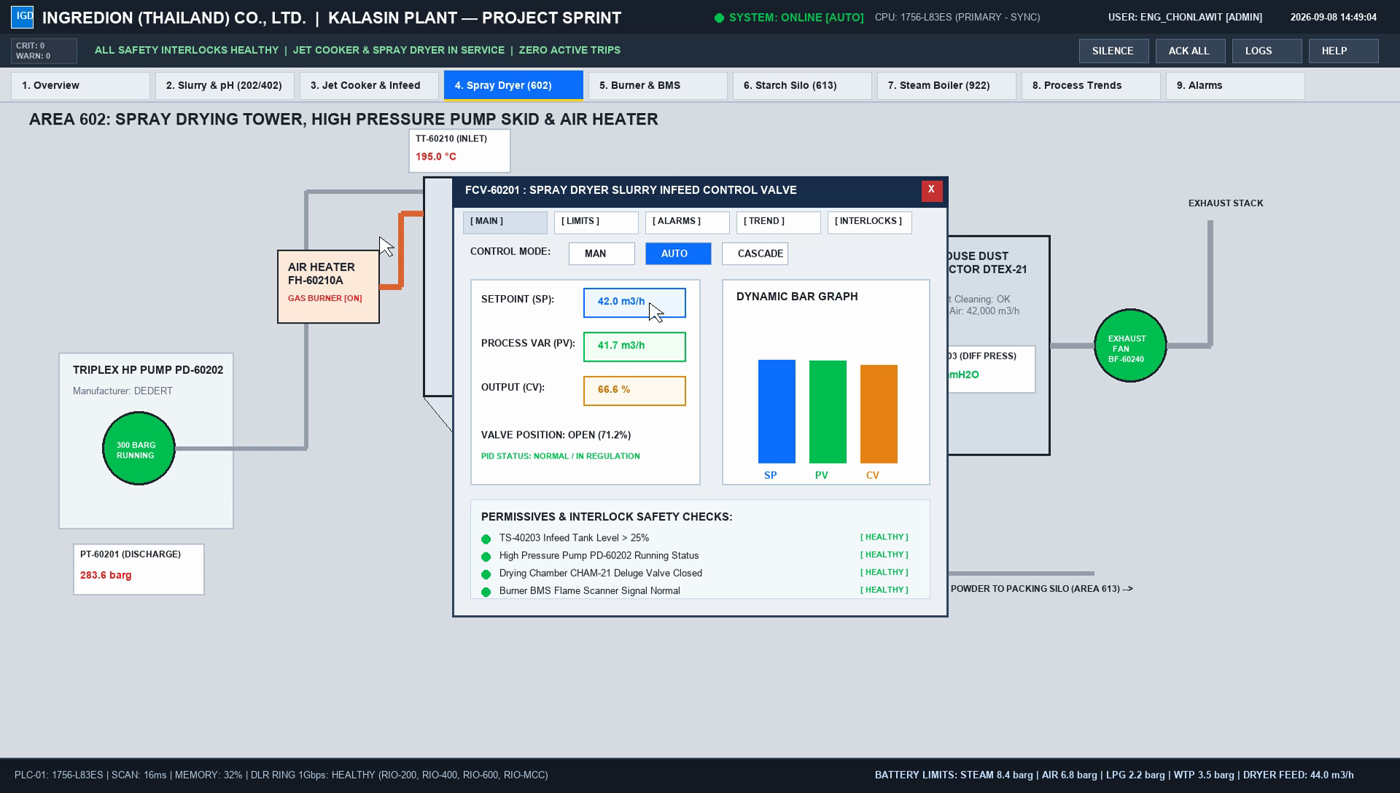
02_Electrical_and_eDrawing/06_SCADA_Demo/04_PlantPAx_Faceplate_Interaction.png
