x92120/x260911-002-KalasinEngineering/02_Electrical_and_eDrawing/06_SCADA_Demo/05_Active_Alarm_Warning_Event.png

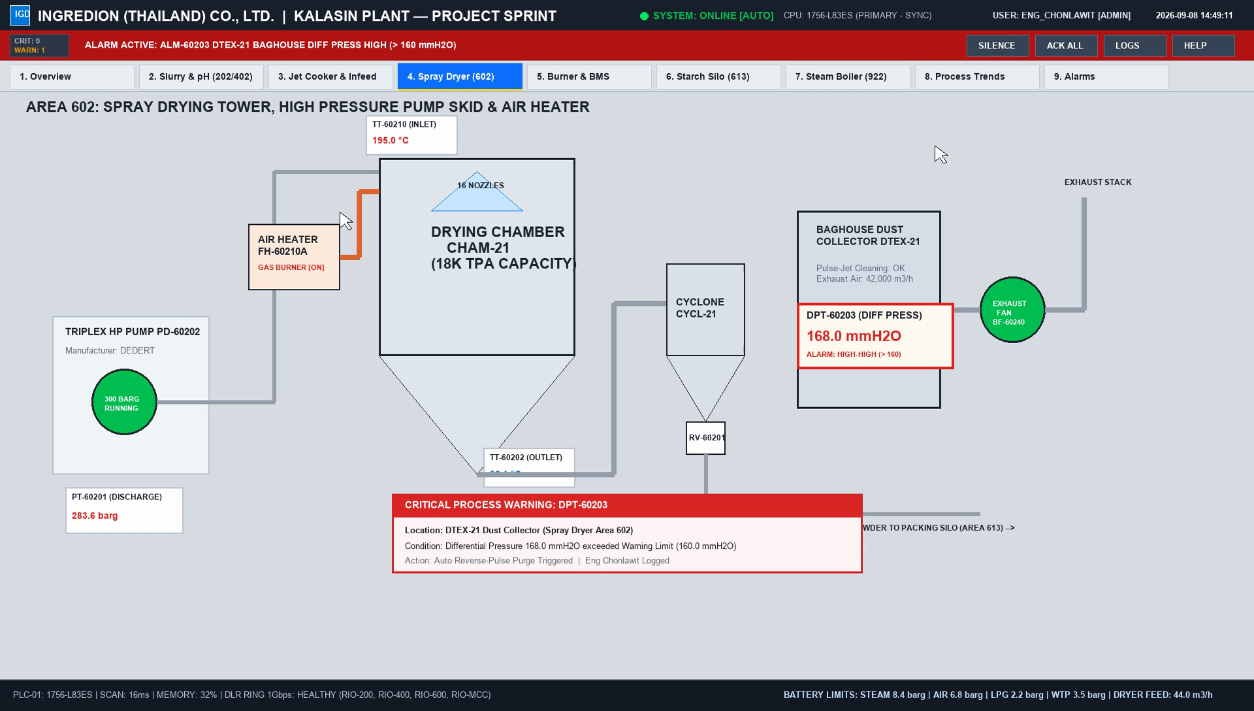
02_Electrical_and_eDrawing/06_SCADA_Demo/05_Active_Alarm_Warning_Event.png
