x92120/x260911-002-KalasinEngineering/02_Electrical_and_eDrawing/06_SCADA_Demo/06_RealTime_Process_Trends.png

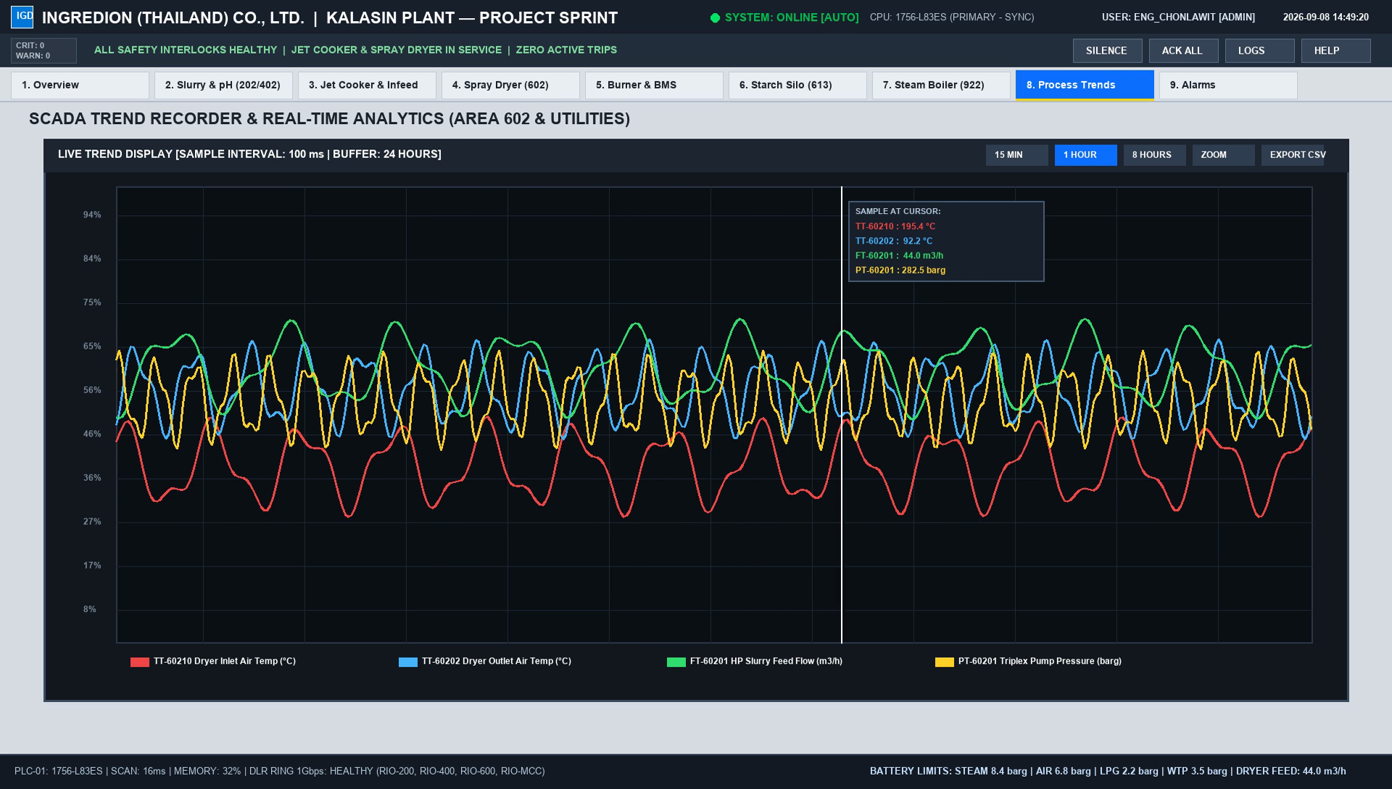
02_Electrical_and_eDrawing/06_SCADA_Demo/06_RealTime_Process_Trends.png
