x92120/x260911-002-KalasinEngineering/02_Electrical_and_eDrawing/06_SCADA_Demo/Automation_Architecture_Slide_Diagram.png

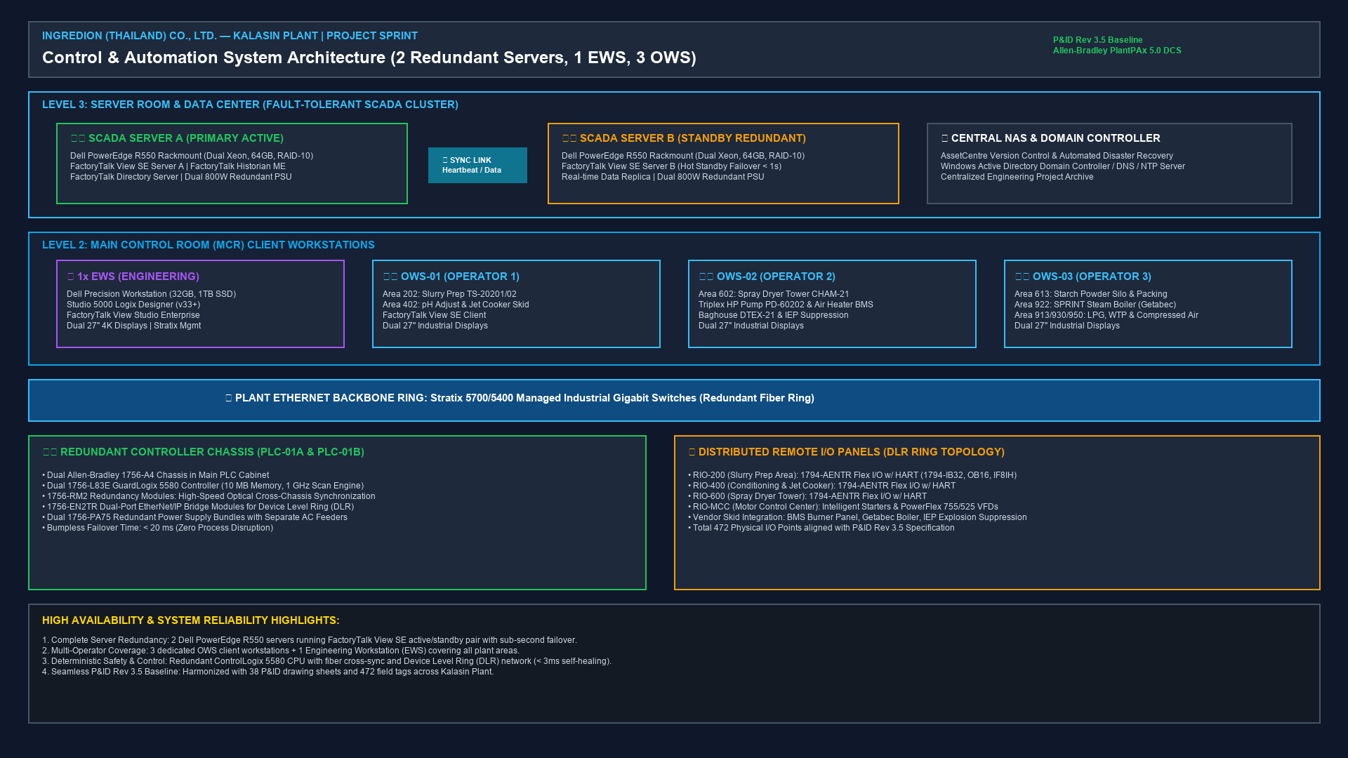
02_Electrical_and_eDrawing/06_SCADA_Demo/Automation_Architecture_Slide_Diagram.png
