x92120/x260911-002-KalasinEngineering/02_Electrical_and_eDrawing/Panel_Layout/PanelLayout_IS-JB-003-CES-STL.png

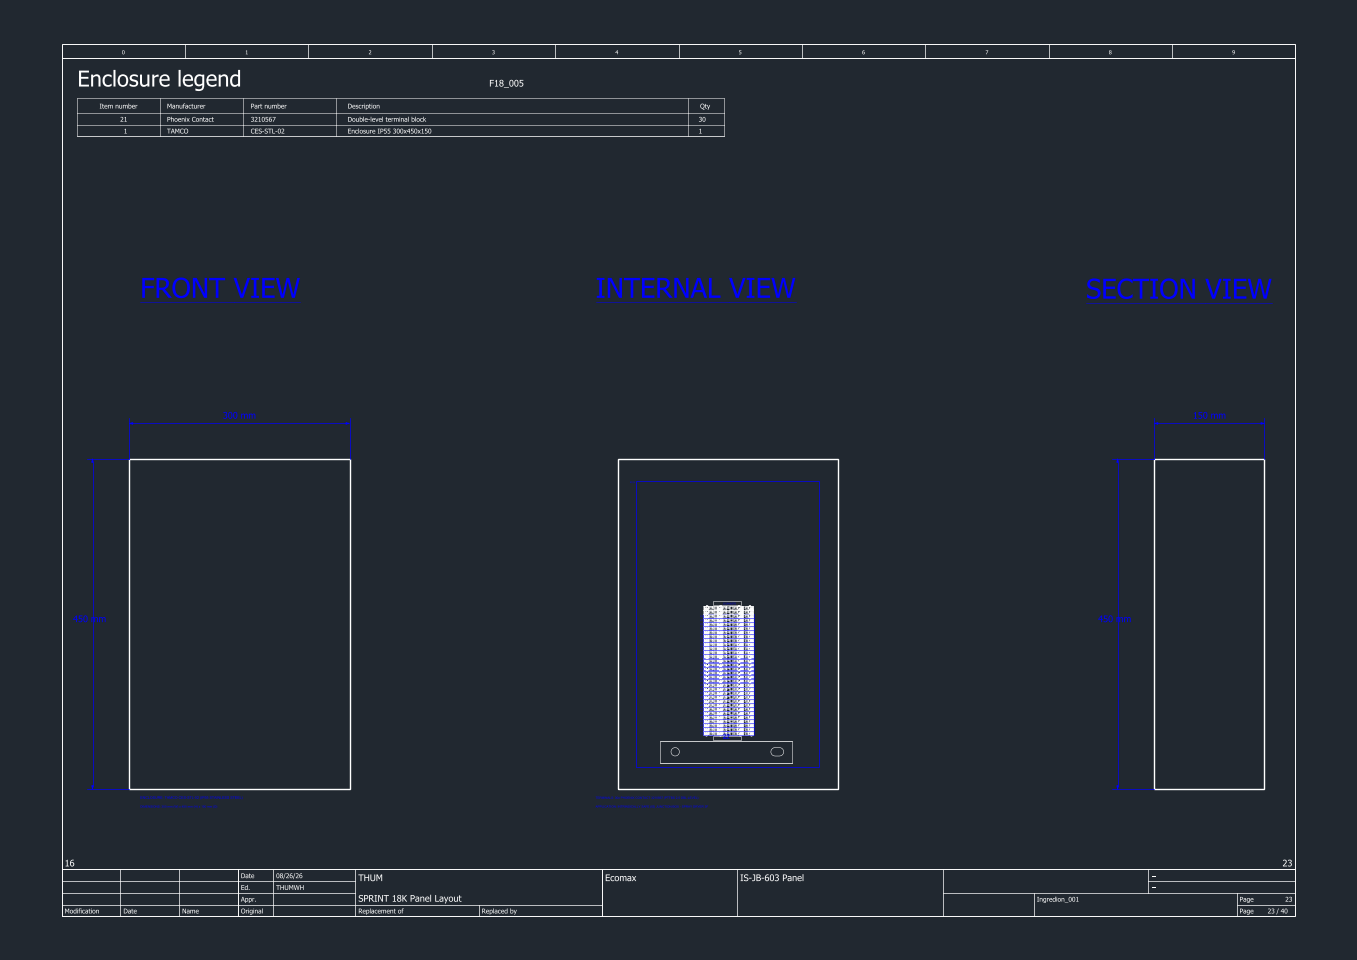
02_Electrical_and_eDrawing/Panel_Layout/PanelLayout_IS-JB-003-CES-STL.png
