x92120/x260911-002-KalasinEngineering/02_Electrical_and_eDrawing/Panel_Layout/TAMCO_CES_Stainless_Series/Product_Images/TAMCO_CES-STL_Enclosure.png

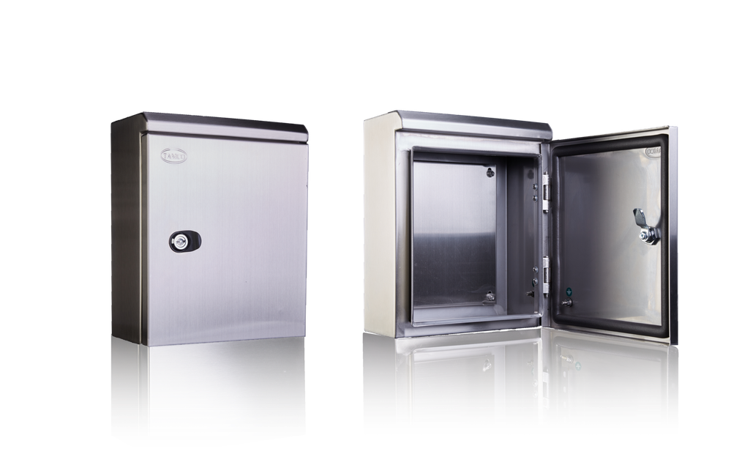
02_Electrical_and_eDrawing/Panel_Layout/TAMCO_CES_Stainless_Series/Product_Images/TAMCO_CES-STL_Enclosure.png
