x92120/x260911-002-KalasinEngineering/02_Electrical_and_eDrawing/Panel_Layout/TAMCO_CRS_Series/Product_Images/TAMCO_CRS_Enclosure.png

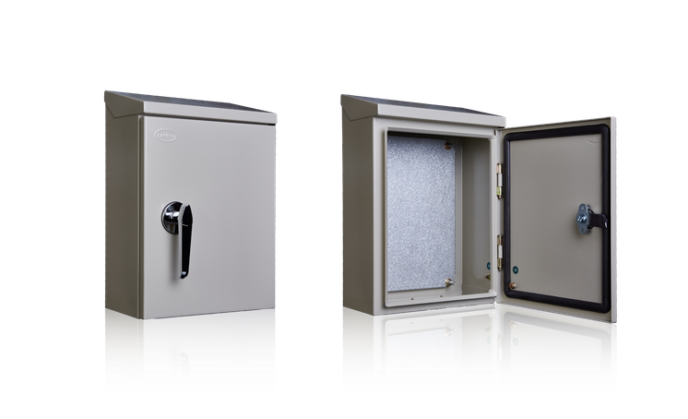
02_Electrical_and_eDrawing/Panel_Layout/TAMCO_CRS_Series/Product_Images/TAMCO_CRS_Enclosure.png
