x92120/x260911-002-KalasinEngineering/06_Enclosure_Ventilation_Calculation/assets/airflow_vs_temperature_curve.png

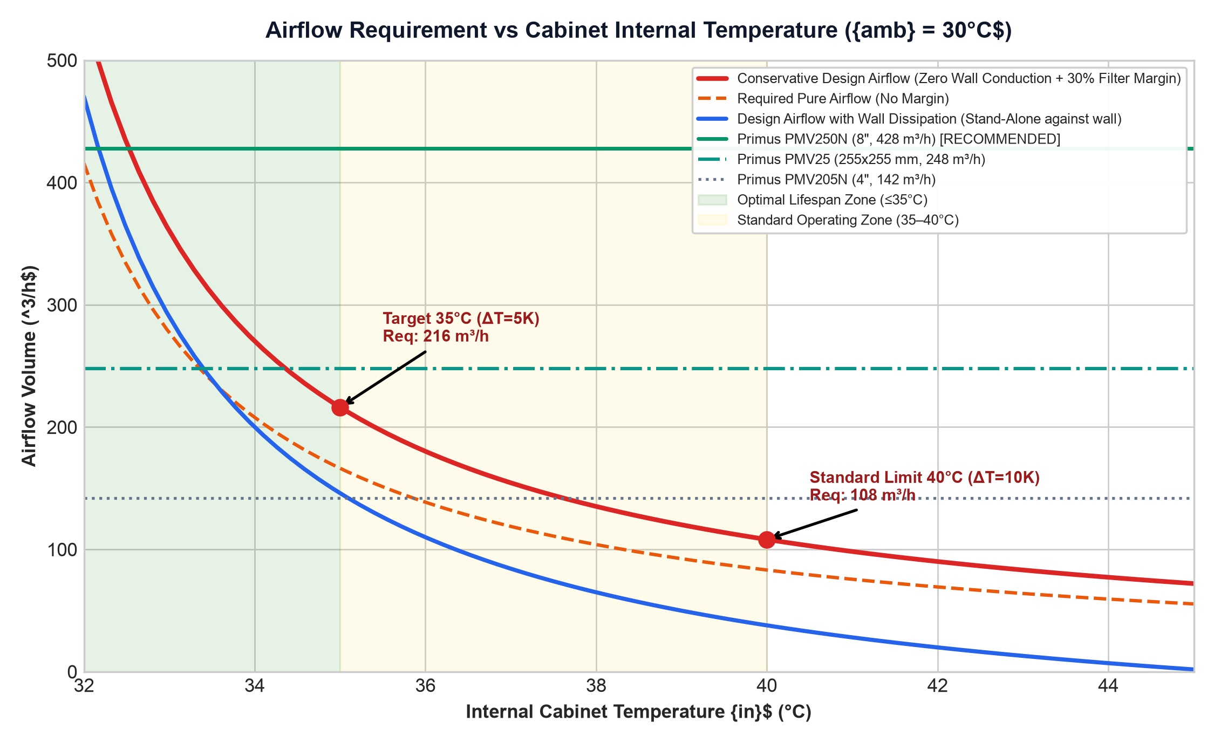
06_Enclosure_Ventilation_Calculation/assets/airflow_vs_temperature_curve.png
