x92120/x260911-002-KalasinEngineering/06_Enclosure_Ventilation_Calculation/assets/enclosure_ventilation_diagram.png

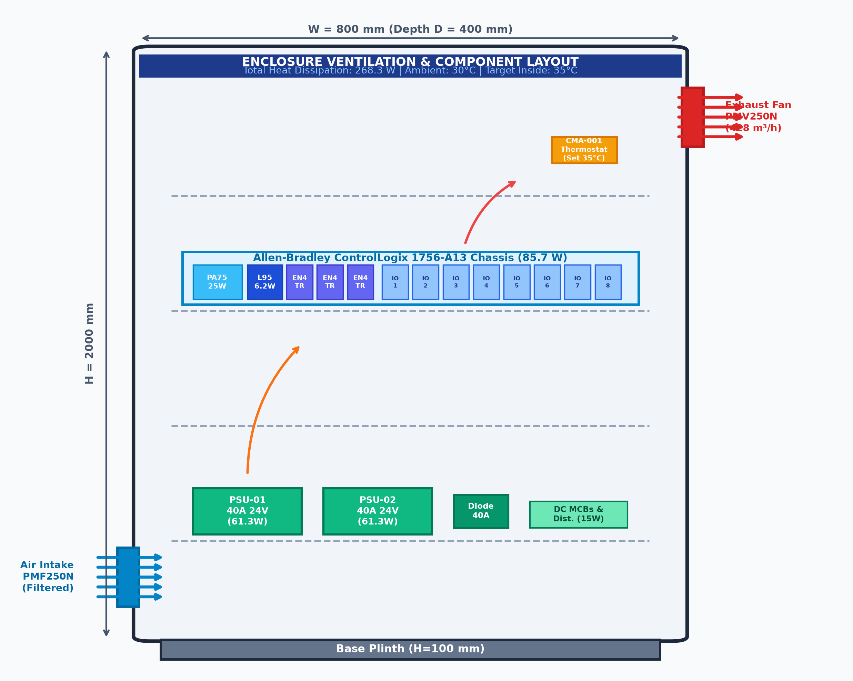
06_Enclosure_Ventilation_Calculation/assets/enclosure_ventilation_diagram.png
