x92120/x260911-002-KalasinEngineering/06_Enclosure_Ventilation_Calculation/assets/page_3.png

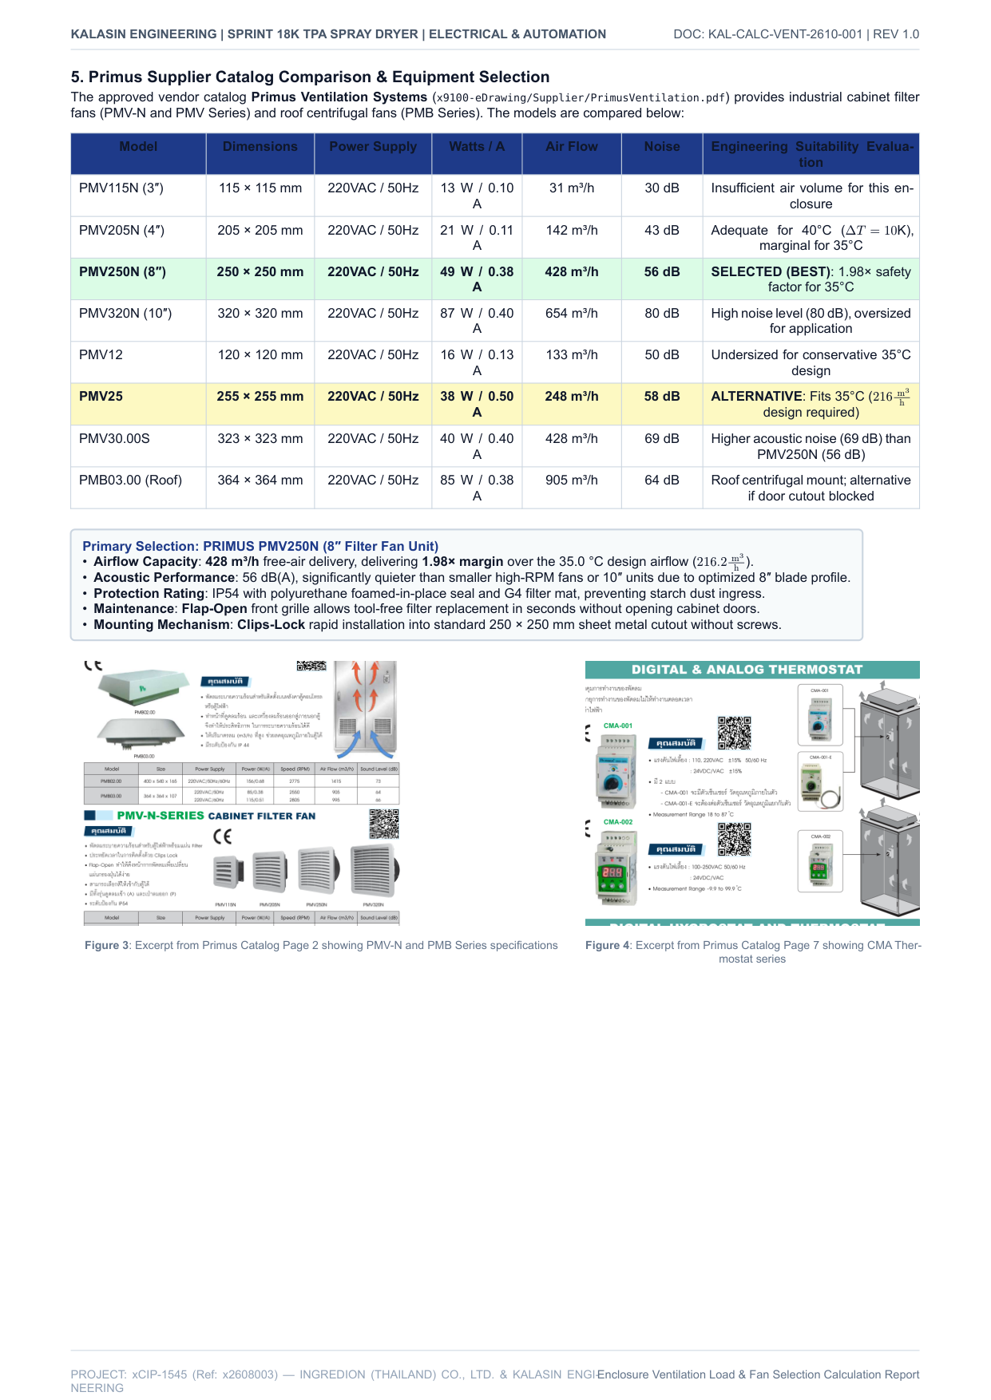
06_Enclosure_Ventilation_Calculation/assets/page_3.png
