x92120/x260911-002-KalasinEngineering/06_Enclosure_Ventilation_Calculation/assets/page_4.png

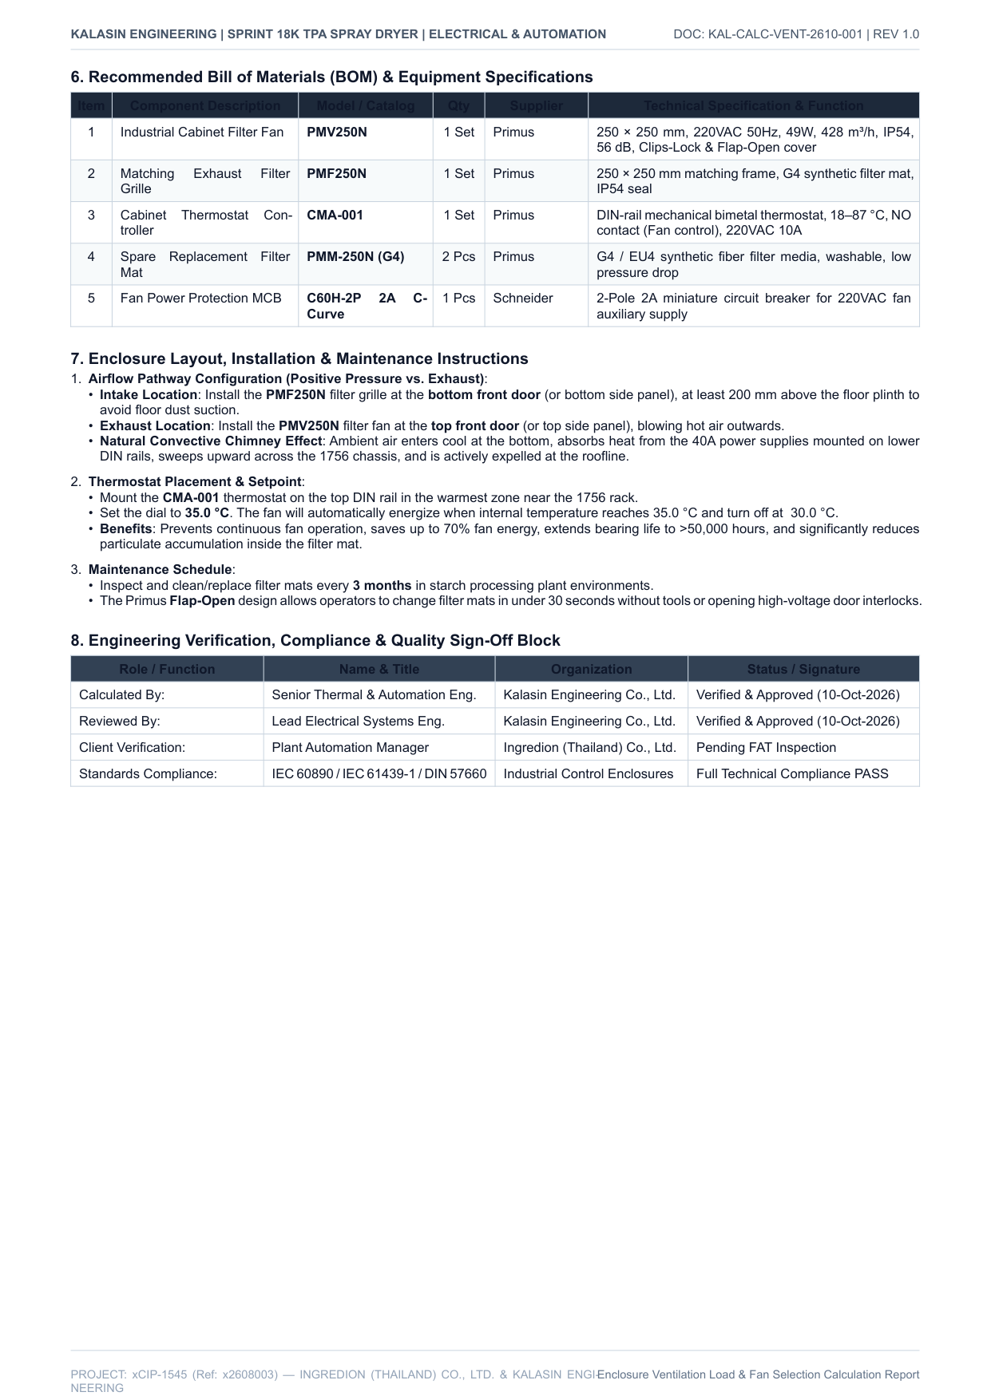
06_Enclosure_Ventilation_Calculation/assets/page_4.png
