x92120/x260911-002-KalasinEngineering/06_Enclosure_Ventilation_Calculation/assets/primus_page_7_full.png

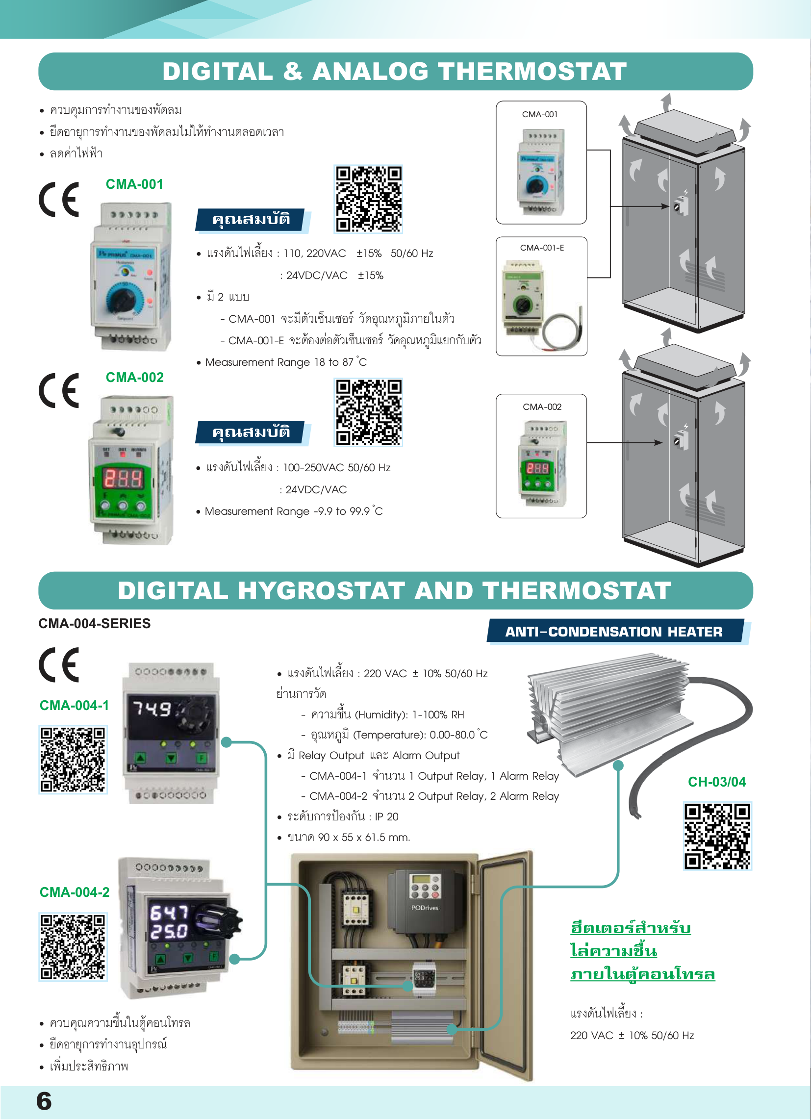
06_Enclosure_Ventilation_Calculation/assets/primus_page_7_full.png
