x92120/x260911-002-KalasinEngineering/05-LoopTest/Loop_Test_Plan_and_Schedule.xlsx

Sheet: 00_Executive_Summary
KALASIN ENGINEERING | xCIP-1545 AUTOMATION SYSTEM (Ref: x2608003)
MASTER INSTRUMENT LOOP TESTING PLAN, PROCEDURE & COMMISSIONING SCHEDULE — SPRINT 18K TPA SPRAY DRYER / JET COOKER
TOTAL INSTRUMENT LOOPS |  | COLD LOOP INSPECTION |  | HOT LOOP CALIBRATION |  | COMMISSIONING SCHEDULE |  | STANDARD COMPLIANCE |  | PUNCHLIST TRACKING
560 Loops |  | 100% Verified |  | 5-Point Simulation |  | 4 Weeks (20 Days) |  | IEC 62381 / ISA |  | Cat A & B System
Master Client Schedule Rev 3.6a |  | Continuity, Megger 500VDC, Polarity |  | 0%, 25%, 50%, 75%, 100% Range |  | Mobilization to Client Handover |  | Field Instrument Loop Check Standard |  | 100% Pre-commissioning Sign-off
1. LOOP TESTING SCOPE & SUBSYSTEM WORK BREAKDOWN
Subsystem / Plant Area | Target Field Enclosures | Associated PLC Rack | Total Loops | Discrete DI/DO | Analog AI/AO | Hazardous Area Zone | Primary Test Protocol | Estimated Duration | Scheduled Window | Responsible Team Lead | Witness / QA/QC | Status
Jet Cooker Infeed & Pre-Treatment | JB-401 (Floor 2F) | Chassis C1 (Panel P1) | 96 | 74 | 22 | Safe Area | Cold + 4-20mA Flow/Press Sim | 3 Working Days | Week 1 (Day 3–5) | Lead Inst. Eng (Kalasin) | Ingredion QA/QC | READY FOR EXECUTION
Jet Cooker Thermal Cooking Skid | JB-402 (Floor 2F) | Chassis C2 (Panel P2) | 48 | 33 | 15 | Safe Area | Temp RTD + Steam PRV Stroke | 2 Working Days | Week 2 (Day 6–7) | Senior Comm. Eng | Ingredion QA/QC | READY FOR EXECUTION
Spray Dryer Base & Powder Discharge | JB-601 (Floor 1F) | Chassis C1 (Panel P1) | 61 | 45 | 16 | Safe Area | Rotary Valve + Pressure Trans | 2 Working Days | Week 2 (Day 8–9) | Lead Inst. Eng (Kalasin) | Ingredion QA/QC | READY FOR EXECUTION
Spray Dryer Cyclone & Exhaust Section | JB-602 (Floor 3F) | Chassis C2 (Panel P2) | 86 | 26 | 60 | Safe Area | Diff Pressure DP + Temp RTDs | 3 Working Days | Week 2 (Day 9–10) | Senior Comm. Eng | Ingredion QA/QC | READY FOR EXECUTION
Spray Dryer Direct Burner & Air Heater | JB-606 (Floor 6F) | Chassis C3 (Panel P3) | 9 | 5 | 4 | Classified / Burner | Combustible Gas + Thermal Flow | 1 Working Day | Week 3 (Day 11) | Lead Inst. Eng (Kalasin) | Burner Specialist | READY FOR EXECUTION
Spray Dryer Main Mid-Tower Section | JB-607, JB-608 (4F) | Chassis C2 & C3 (P2/P3) | 179 | 121 | 58 | Dust Zone 22 (Ext) | High-Density Transmitters & Valves | 4 Working Days | Week 3 (Day 12–14) | Lead Inst. Eng (Kalasin) | Ingredion QA/QC | READY FOR EXECUTION
Spray Dryer Upper Tower & Atomizer | JB-612 (Floor 6/8F) | Chassis C4 (Panel P4) | 40 | 32 | 8 | Dust Zone 21/22 | Atomizer Speed + Vent Pressure | 2 Working Days | Week 3 (Day 14–15) | Senior Comm. Eng | Ingredion QA/QC | READY FOR EXECUTION
Packing Tower Feed & Silo Discharge | JB-618 (Packing) | Chassis C3 (Panel P3) | 29 | 21 | 8 | Dust Zone 22 | Powder Silo Fork + Sieve DI | 2 Working Days | Week 4 (Day 16–17) | Lead Inst. Eng (Kalasin) | Ingredion QA/QC | READY FOR EXECUTION
Hazardous Area Intrinsically Safe Loops | IS-JB-603/608/612/618 | Chassis C4 (P4 IS) | 99 | 50 | 49 | ATEX Zone 1/21 (Ex ia) | P&F IS Barrier Insulation & Loop Check | 3 Working Days | Week 4 (Day 17–18) | Ex-Certified Inspector | TUV / Client Safety | READY FOR EXECUTION
Slurry Preparation Outbuilding | RIO-200 (Slurry 2F) | Chassis C5 (RIO-200) | 66 | 48 | 18 | Safe Area | 1Gbps DLR Ring + Slurry pH/Mass Flow | 2 Working Days | Week 4 (Day 18–19) | Senior Comm. Eng | Ingredion QA/QC | READY FOR EXECUTION
Integrated Interlocks & Handover | CA1 Central MCP | Master Chassis C1-C5 | 560 | 334 | 226 | Central Control | Full ESD Trip & SCADA Graphic Verification | 2 Working Days | Week 4 (Day 19–20) | Project Commissioning Mgr | Ingredion Project Mgr | PLANNED
2. REQUIRED TEST INSTRUMENTS, CALIBRATORS & COMMISSIONING TOOL SPECIFICATIONS
Item # | Equipment Description | Manufacturer & Model | Calibration Parameter | Operating Range | Accuracy / Tolerance | Valid Calibration Certificate | Calibration Expiry Date | Dedicated Testing Purpose | Quantity Required | Serial Number | Certification Agency | Status
1 | Precision Documenting Process Calibrator | Fluke 754 | 4-20mA, Volts, RTD, TC, HART | -10 to 55 mA / 0-30V / Pt100 | ±0.01% of Reading | ISO/IEC 17025 Certified | 31-DEC-2026 | Analog 4-20mA 5-Point Loop Simulation & HART Config | 2 Units | FLK-754-98421 | NIST / Thai Metrology | CERTIFIED ACTIVE
2 | Precision Digital Pressure Calibrator | Druck DPI 611 | Gauge & Differential Pressure | -1 to 20 bar (Hydraulic/Pneu) | ±0.0185% FS | ISO/IEC 17025 Certified | 15-NOV-2026 | Pressure & Differential Transmitter Calibration Check | 1 Unit | DRK-611-34901 | Baker Hughes Cal Lab | CERTIFIED ACTIVE
3 | True RMS Digital Industrial Multimeter | Fluke 87V | AC/DC Volts, Amps, Resistance, Continuity | 0 - 1000V DC / 0 - 20A / 50MΩ | ±0.05% Accuracy | Factory Calibrated | 28-FEB-2027 | Cold continuity check, 24VDC loop power verification | 3 Units | FLK-87V-11204 | Fluke Service Center | CERTIFIED ACTIVE
4 | High-Voltage Insulation Resistance Tester | Megger MIT410/2 | Insulation Resistance @ 250V/500VDC | 10 kΩ to 100 GΩ | ±2% ±2 digits | Annual Certified | 15-JAN-2027 | Pre-power cable insulation & shield isolation (>20MΩ) | 2 Units | MEG-410-88319 | Megger Calibration Lab | CERTIFIED ACTIVE
5 | Pneumatic Hand Test Pump w/ Vernier | Ralston Instruments AP-002 | Pneumatic Air Pressure / Vacuum | 0 to 300 psi (20 bar) | Fine Vernier 0.01 psi | Traceable Reference | 31-DEC-2026 | Field Pressure Transmitter 5-point mechanical test | 2 Units | RAL-AP-55201 | Ralston Metrology | CERTIFIED ACTIVE
6 | Industrial 2-Way VHF/UHF Radios | Motorola Mototrbo DP4801e | Intrinsically Safe ATEX Comms | 136 - 174 MHz | ATEX Gas/Dust Certified | Radio License Compliant | Permanent | Direct Field-to-Control Room voice coordination | 6 Units | MOT-DP-4801-SET | NBTC Thailand | INSPECTED ACTIVE

Sheet: 03_Loop_Test_Master_List
KALASIN ENGINEERING | MASTER INSTRUMENT LOOP TESTING & CALIBRATION VERIFICATION SCHEDULE
Point-by-Point Field Loop Check Record (Rev. 3.6a Master) Cross-Referenced with CAD Loop Typical Diagrams (DWG/DXF)
Item # | Active Tag No. | Legacy Tag | P&ID No. | Instrument Service Description | Instrument Type / Name | Signal Type | Calibrated Range | CAD Typical ID | CAD Strip Type | CAD DWG Reference | Field Junction Box | Terminal Block ID | PLC Rack / Slot | Wire Tag (PLC Side) | Wire Tag (Terminal Side) | PLC Tag Name | Cold Continuity (<2Ω) | Cold Megger (>20MΩ) | Hot Power (24VDC) | Calibration 0% (4mA) | Calibration 50% (12mA) | Calibration 100% (20mA) | Stroke / Trip Response | Testing Status | QA/QC Sign-off & Date
1 | AT-60241 | - | 325-01-602-PD-05 | Dust Analyzer Transmitter for Exhaust Duct (DTEX-22) | Dust Analyzer Transmitter | 4 - 20 mA | 5000 mg | TYP-AI-02 | TBAI | LOOP DIAGRAM WRING.dwg | JB-602 | P2-TBAI2-1(B) | C2/C2S10 | C2S10-1/P2-TBAI2-1(B) | P2-TBAI2-1(B)/C2S10-1 | AT-60241_AI_1 | [ ] Pass | ____ MΩ | [ ] 24V | ____ mA | ____ mA | ____ mA | [ ] Pass | READY FOR TEST | Pending Sign-off
2 | DPT-60201 | DPT-60901 | 325-01-602-PD-09 | Steam filter pressure | Differential Pressure Transmitter | 4 - 20 mA | 0-1 barg | TYP-AI-01 | TBAI | LOOP DIAGRAM WRING.dwg | JB-606 | P3-TBAI1-15(B) | C3/C3S6 | C3S6-33/P3-TBAI1-15(B) | P3-TBAI1-15(B)/C3S6-33 | DPT-60201_AI_1 | [ ] Pass | ____ MΩ | [ ] 24V | ____ mA | ____ mA | ____ mA | [ ] Pass | READY FOR TEST | Pending Sign-off
3 | DPT-61301 | - | 325-01-613-PD-01 | Vent filter pressure | Differential Pressure Transmitter | 4 - 20 mA | - | TYP-AI-01 | TBAI | LOOP DIAGRAM WRING.dwg | IS-JB-618 | P4-TBAI2-5(B) | C4/C4S6 | C4S6-11/P4-TBAI2-5(B) | P4-TBAI2-5(B)/C4S6-11 | DPT-61301_AI_1 | [ ] Pass | ____ MΩ | [ ] 24V | ____ mA | ____ mA | ____ mA | [ ] Pass | READY FOR TEST | Pending Sign-off
4 | DPT-61302 | - | 325-01-613-PD-01 | Vent filter pressure | Differential Pressure Transmitter | 4 - 20 mA | - | TYP-AI-01 | TBAI | LOOP DIAGRAM WRING.dwg | IS-JB-618 | P4-TBAI2-6(B) | C4/C4S6 | C4S6-13/P4-TBAI2-6(B) | P4-TBAI2-6(B)/C4S6-13 | DPT-61302_AI_1 | [ ] Pass | ____ MΩ | [ ] 24V | ____ mA | ____ mA | ____ mA | [ ] Pass | READY FOR TEST | Pending Sign-off
5 | DPT-61310 | - | 325-01-613-PD-03 | Vent filter pressure | Differential Pressure Transmitter | 4 - 20 mA | - | TYP-AI-01 | TBAI | LOOP DIAGRAM WRING.dwg | IS-JB-612 | P4-TBAI2-1(B) | C4/C4S6 | C4S6-1/P4-TBAI2-1(B) | P4-TBAI2-1(B)/C4S6-1 | DPT-61310_AI_1 | [ ] Pass | ____ MΩ | [ ] 24V | ____ mA | ____ mA | ____ mA | [ ] Pass | READY FOR TEST | Pending Sign-off
6 | DPT-61312 | - | 325-01-613-PD-05 | Vent filter pressure | Differential Pressure Transmitter | 4 - 20 mA | - | TYP-AI-01 | TBAI | LOOP DIAGRAM WRING.dwg | IS-JB-612 | P4-TBAI2-2(B) | C4/C4S6 | C4S6-3/P4-TBAI2-2(B) | P4-TBAI2-2(B)/C4S6-3 | DPT-61312_AI_1 | [ ] Pass | ____ MΩ | [ ] 24V | ____ mA | ____ mA | ____ mA | [ ] Pass | READY FOR TEST | Pending Sign-off
7 | DPT-60202 | - | 325-01-602-PD-08 | Gas Pressure Differential Transmitter for Air Filter (FICA-31) | Differential Pressure Transmitter | 4 - 20 mA | -100 to 500 mBar | TYP-AI-01 | TBAI | LOOP DIAGRAM WRING.dwg | JB-601 | P1-TBAI2-2(B) | C1/C1S11 | C1S11-3/P1-TBAI2-2(B) | P1-TBAI2-2(B)/C1S11-3 | DPT-60202_AI_1 | [ ] Pass | ____ MΩ | [ ] 24V | ____ mA | ____ mA | ____ mA | [ ] Pass | READY FOR TEST | Pending Sign-off
8 | DPT-60203 | - | 325-01-602-PD-03 | Gas Pressure Differential Transmitter for Air Filter (FICA-21) | Differential Pressure Transmitter | 4 - 20 mA | -100 to 500 mBar | TYP-AI-01 | TBAI | LOOP DIAGRAM WRING.dwg | JB-602 | P2-TBAI2-2(B) | C2/C2S10 | C2S10-3/P2-TBAI2-2(B) | P2-TBAI2-2(B)/C2S10-3 | DPT-60203_AI_1 | [ ] Pass | ____ MΩ | [ ] 24V | ____ mA | ____ mA | ____ mA | [ ] Pass | READY FOR TEST | Pending Sign-off
9 | FSL-20201 |  | 325-01-202-PD-01 | Slurry low flow | Flow Switch | Dry Contact | - | TYP-DI-01 | TBDI | PANEL WIRING DIAGRAM.dwg | PLC | - | - | - | - | - | [ ] Pass | ____ MΩ | [ ] 24V | ____ mA | ____ mA | ____ mA | [ ] Pass | RESERVE ALLOC | Pending Sign-off
10 | FSL-40201 |  | 325-01-402-PD-01 | Slurry low flow | Flow Switch | Dry Contact | - | TYP-DI-01 | TBDI | PANEL WIRING DIAGRAM.dwg | JB-401 | P1-TBDI1-17 | C1/C1S4 | C1S4-19/P1-TBDI1-17 | P1-TBDI1-17/C1S4-19 | FSL-40201_DI_1 | [ ] Pass | ____ MΩ | [ ] 24V | ____ mA | ____ mA | ____ mA | [ ] Pass | READY FOR TEST | Pending Sign-off
11 | FSL-40202 |  | 325-01-402-PD-01 | Slurry low flow | Flow Switch | Dry Contact | - | TYP-DI-01 | TBDI | PANEL WIRING DIAGRAM.dwg | JB-401 | P1-TBDI1-18 | C1/C1S4 | C1S4-20/P1-TBDI1-18 | P1-TBDI1-18/C1S4-20 | FSL-40202_DI_1 | [ ] Pass | ____ MΩ | [ ] 24V | ____ mA | ____ mA | ____ mA | [ ] Pass | READY FOR TEST | Pending Sign-off
12 | FS-40204 |  | 325-01-402-PD-01 | Jet Cooker | Flow Switch | Dry Contact | - | TYP-DI-01 | TBDI | PANEL WIRING DIAGRAM.dwg | JB-402 | P2-TBDI1-1 | C2/C2S1 | C2S1-1/P2-TBDI1-1 | P2-TBDI1-1/C2S1-1 | FS-40204_DI_1 | [ ] Pass | ____ MΩ | [ ] 24V | ____ mA | ____ mA | ____ mA | [ ] Pass | READY FOR TEST | Pending Sign-off
13 | FS-40205 |  | 325-01-402-PD-02 | Jet Cooker | Flow Switch | Dry Contact | - | TYP-DI-01 | TBDI | PANEL WIRING DIAGRAM.dwg | JB-402 | P2-TBDI1-2 | C2/C2S1 | C2S1-2/P2-TBDI1-2 | P2-TBDI1-2/C2S1-2 | FS-40205_DI_1 | [ ] Pass | ____ MΩ | [ ] 24V | ____ mA | ____ mA | ____ mA | [ ] Pass | READY FOR TEST | Pending Sign-off
14 | FT-40201 | - | 325-01-402-PD-02 | Slurry flowrate & density check transfer line | Coriolis Flow Transmitter | 4 - 20 mA,Pulse | 0-15 m³/hr | TYP-DI-01 | TBDI | PANEL WIRING DIAGRAM.dwg | JB-401 | P1-TBDI1-19 | C1/C1S4 | C1S4-21/P1-TBDI1-19 | P1-TBDI1-19/C1S4-21 | FT-40201_DI_1 | [ ] Pass | ____ MΩ | [ ] 24V | ____ mA | ____ mA | ____ mA | [ ] Pass | READY FOR TEST | Pending Sign-off
15 | FT-40202 | - | 325-01-402-PD-02 | Feed Slurry Flow Transmitter for Pipe (PIPE) | Magnetic Flow Transmitter | 4 - 20 mA,Pulse | 0 to 8,000 m³/hr | TYP-AI-02 | TBAI | LOOP DIAGRAM WRING.dwg | JB-401 | P1-TBDI1-20 | C1/C1S4 | C1S4-22/P1-TBDI1-20 | P1-TBDI1-20/C1S4-22 | FT-40202_DI_1 | [ ] Pass | ____ MΩ | [ ] 24V | ____ mA | ____ mA | ____ mA | [ ] Pass | READY FOR TEST | Pending Sign-off
16 | FT-40221 |  | 325-01-402-PD-02 | Jet Cooker | Coriolis Flow Transmitter | 4 - 20 mA,Pulse | 0-6 m³/hr | TYP-DI-01 | TBDI | PANEL WIRING DIAGRAM.dwg | JB-402 | P2-TBDI1-3 | C2/C2S1 | C2S1-3/P2-TBDI1-3 | P2-TBDI1-3/C2S1-3 | FT-40221_DI_1 | [ ] Pass | ____ MΩ | [ ] 24V | ____ mA | ____ mA | ____ mA | [ ] Pass | READY FOR TEST | Pending Sign-off
17 | FT-40222 |  | 325-01-402-PD-02 | Jet Cooker | Coriolis Flow Transmitter | 4 - 20 mA,Pulse | 0-850 kg/hr | TYP-DI-01 | TBDI | PANEL WIRING DIAGRAM.dwg | JB-402 | P2-TBDI1-4 | C2/C2S1 | C2S1-4/P2-TBDI1-4 | P2-TBDI1-4/C2S1-4 | FT-40222_DI_1 | [ ] Pass | ____ MΩ | [ ] 24V | ____ mA | ____ mA | ____ mA | [ ] Pass | READY FOR TEST | Pending Sign-off
18 | FT-60221 | - | 325-01-602-PD-04 | Cool air Flow | Thermal Mass Flow Transmitter | 4 - 20 mA | 2500 m3/h | TYP-AI-02 | TBAI | LOOP DIAGRAM WRING.dwg | JB-607 | P3-TBAI2-2(B) | C3/C3S7 | C3S7-3/P3-TBAI2-2(B) | P3-TBAI2-2(B)/C3S7-3 | FT-60221_AI_1 | [ ] Pass | ____ MΩ | [ ] 24V | ____ mA | ____ mA | ____ mA | [ ] Pass | READY FOR TEST | Pending Sign-off
19 | FT-60201 | - | 325-01-602-PD-08 | Gas Flow Transmitter for Cooling Conveying Cold Air Duct (DTCA-32) | Thermal Mass Flow Transmitter | 4 - 20 mA | 70000 m3/h | TYP-AI-02 | TBAI | LOOP DIAGRAM WRING.dwg | JB-601 | P1-TBAI2-3(B) | C1/C1S11 | C1S11-5/P1-TBAI2-3(B) | P1-TBAI2-3(B)/C1S11-5 | FT-60201_AI_1 | [ ] Pass | ____ MΩ | [ ] 24V | ____ mA | ____ mA | ____ mA | [ ] Pass | READY FOR TEST | Pending Sign-off
20 | FT-60210 | - | 325-01-602-PD-03 | Gas Flow Element for Dryer Hot Air Duct (DTHA-21B) | Thermal Mass Flow Transmitter | 4 - 20 mA | 126000 m3/h | TYP-GEN-01 | TBCI | LOOP DIAGRAM WRING.dwg | JB-602 | P3-TBAI1-10(B) | C3/C3S6 | C3S6-21/P3-TBAI1-10(B) | P3-TBAI1-10(B)/C3S6-21 | FT-60210_AI_1 | [ ] Pass | ____ MΩ | [ ] 24V | ____ mA | ____ mA | ____ mA | [ ] Pass | READY FOR TEST | Pending Sign-off
21 | FT-60211 | - | 325-01-602-PD-03 | Gas Flow Element for Dryer Hot Air Duct (DTHA-21A) | Thermal Mass Flow Transmitter | 4 - 20 mA | 126000 m3/h | TYP-GEN-01 | TBCI | LOOP DIAGRAM WRING.dwg | JB-602 | P3-TBAI1-11(B) | C3/C3S6 | C3S6-23/P3-TBAI1-11(B) | P3-TBAI1-11(B)/C3S6-23 | FT-60211_AI_1 | [ ] Pass | ____ MΩ | [ ] 24V | ____ mA | ____ mA | ____ mA | [ ] Pass | READY FOR TEST | Pending Sign-off
22 | FT-60261FA | - | 325-01-602-PD-02 | Feed Slurry Flow Transmitter for Nozzle #1 (AMTV-11A) | Ultrasonic Flow Transmitter | 4 - 20 mA | 0 to 100 l/h | TYP-AI-02 | TBAI | LOOP DIAGRAM WRING.dwg | JB-607 | P3-TBAI2-3(B) | C3/C3S7 | C3S7-5/P3-TBAI2-3(B) | P3-TBAI2-3(B)/C3S7-5 | FT-60261FA_AI_1 | [ ] Pass | ____ MΩ | [ ] 24V | ____ mA | ____ mA | ____ mA | [ ] Pass | READY FOR TEST | Pending Sign-off
23 | FT-60261FB | - | 325-01-602-PD-02 | Feed Slurry Flow Transmitter for Nozzle #2 (AMTV-11A) | Ultrasonic Flow Transmitter | 4 - 20 mA | 0 to 100 l/h | TYP-AI-02 | TBAI | LOOP DIAGRAM WRING.dwg | JB-607 | P3-TBAI2-4(B) | C3/C3S7 | C3S7-7/P3-TBAI2-4(B) | P3-TBAI2-4(B)/C3S7-7 | FT-60261FB_AI_1 | [ ] Pass | ____ MΩ | [ ] 24V | ____ mA | ____ mA | ____ mA | [ ] Pass | READY FOR TEST | Pending Sign-off
24 | FT-60261FC | - | 325-01-602-PD-02 | Feed Slurry Flow Transmitter for Nozzle #3 (AMTV-11A) | Ultrasonic Flow Transmitter | 4 - 20 mA | 0 to 100 l/h | TYP-AI-02 | TBAI | LOOP DIAGRAM WRING.dwg | JB-607 | P3-TBAI2-5(B) | C3/C3S7 | C3S7-11/P3-TBAI2-5(B) | P3-TBAI2-5(B)/C3S7-11 | FT-60261FC_AI_1 | [ ] Pass | ____ MΩ | [ ] 24V | ____ mA | ____ mA | ____ mA | [ ] Pass | READY FOR TEST | Pending Sign-off
25 | FT-60261FD | - | 325-01-602-PD-02 | Feed Slurry Flow Transmitter for Nozzle #4 (AMTV-11A) | Ultrasonic Flow Transmitter | 4 - 20 mA | 0 to 100 l/h | TYP-AI-02 | TBAI | LOOP DIAGRAM WRING.dwg | JB-607 | P3-TBAI2-6(B) | C3/C3S7 | C3S7-13/P3-TBAI2-6(B) | P3-TBAI2-6(B)/C3S7-13 | FT-60261FD_AI_1 | [ ] Pass | ____ MΩ | [ ] 24V | ____ mA | ____ mA | ____ mA | [ ] Pass | READY FOR TEST | Pending Sign-off
26 | FT-60262FE | - | 325-01-602-PD-02 | Feed Slurry Flow Transmitter for Nozzle #5 (AMTV-11B) | Ultrasonic Flow Transmitter | 4 - 20 mA | 0 to 100 l/h | TYP-AI-02 | TBAI | LOOP DIAGRAM WRING.dwg | JB-607 | P3-TBAI2-7(B) | C3/C3S7 | C3S7-15/P3-TBAI2-7(B) | P3-TBAI2-7(B)/C3S7-15 | FT-60262FE_AI_1 | [ ] Pass | ____ MΩ | [ ] 24V | ____ mA | ____ mA | ____ mA | [ ] Pass | READY FOR TEST | Pending Sign-off
27 | FT-60262FF | - | 325-01-602-PD-02 | Feed Slurry Flow Transmitter for Nozzle #6 (AMTV-11B) | Ultrasonic Flow Transmitter | 4 - 20 mA | 0 to 100 l/h | TYP-AI-02 | TBAI | LOOP DIAGRAM WRING.dwg | JB-607 | P3-TBAI2-8(B) | C3/C3S7 | C3S7-17/P3-TBAI2-8(B) | P3-TBAI2-8(B)/C3S7-17 | FT-60262FF_AI_1 | [ ] Pass | ____ MΩ | [ ] 24V | ____ mA | ____ mA | ____ mA | [ ] Pass | READY FOR TEST | Pending Sign-off
28 | FT-60262FG | - | 325-01-602-PD-02 | Feed Slurry Flow Transmitter for Nozzle #7 (AMTV-11B) | Ultrasonic Flow Transmitter | 4 - 20 mA | 0 to 100 l/h | TYP-AI-02 | TBAI | LOOP DIAGRAM WRING.dwg | JB-607 | P3-TBAI2-9(B) | C3/C3S7 | C3S7-19/P3-TBAI2-9(B) | P3-TBAI2-9(B)/C3S7-19 | FT-60262FG_AI_1 | [ ] Pass | ____ MΩ | [ ] 24V | ____ mA | ____ mA | ____ mA | [ ] Pass | READY FOR TEST | Pending Sign-off
29 | FT-60262FH | - | 325-01-602-PD-02 | Feed Slurry Flow Transmitter for Nozzle #8 (AMTV-11B) | Ultrasonic Flow Transmitter | 4 - 20 mA | 0 to 100 l/h | TYP-AI-02 | TBAI | LOOP DIAGRAM WRING.dwg | JB-607 | P3-TBAI2-10(B) | C3/C3S7 | C3S7-21/P3-TBAI2-10(B) | P3-TBAI2-10(B)/C3S7-21 | FT-60262FH_AI_1 | [ ] Pass | ____ MΩ | [ ] 24V | ____ mA | ____ mA | ____ mA | [ ] Pass | READY FOR TEST | Pending Sign-off
30 | FT-60263FJ | - | 325-01-602-PD-02 | Feed Slurry Flow Transmitter for Nozzle #9 (AMTV-11C) | Ultrasonic Flow Transmitter | 4 - 20 mA | 0 to 100 l/h | TYP-AI-02 | TBAI | LOOP DIAGRAM WRING.dwg | JB-607 | P3-TBAI2-11(B) | C3/C3S7 | C3S7-23/P3-TBAI2-11(B) | P3-TBAI2-11(B)/C3S7-23 | FT-60263FJ_AI_1 | [ ] Pass | ____ MΩ | [ ] 24V | ____ mA | ____ mA | ____ mA | [ ] Pass | READY FOR TEST | Pending Sign-off
31 | FT-60263FK | - | 325-01-602-PD-02 | Feed Slurry Flow Transmitter for Nozzle #10 (AMTV-11C) | Ultrasonic Flow Transmitter | 4 - 20 mA | 0 to 100 l/h | TYP-AI-02 | TBAI | LOOP DIAGRAM WRING.dwg | JB-607 | P3-TBAI2-12(B) | C3/C3S7 | C3S7-25/P3-TBAI2-12(B) | P3-TBAI2-12(B)/C3S7-25 | FT-60263FK_AI_1 | [ ] Pass | ____ MΩ | [ ] 24V | ____ mA | ____ mA | ____ mA | [ ] Pass | READY FOR TEST | Pending Sign-off
32 | FT-60263FL | - | 325-01-602-PD-02 | Feed Slurry Flow Transmitter for Nozzle #11 (AMTV-11C) | Ultrasonic Flow Transmitter | 4 - 20 mA | 0 to 100 l/h | TYP-AI-02 | TBAI | LOOP DIAGRAM WRING.dwg | JB-607 | P3-TBAI2-13(B) | C3/C3S7 | C3S7-29/P3-TBAI2-13(B) | P3-TBAI2-13(B)/C3S7-29 | FT-60263FL_AI_1 | [ ] Pass | ____ MΩ | [ ] 24V | ____ mA | ____ mA | ____ mA | [ ] Pass | READY FOR TEST | Pending Sign-off
33 | FT-60263FM | - | 325-01-602-PD-02 | Feed Slurry Flow Transmitter for Nozzle #12 (AMTV-11C) | Ultrasonic Flow Transmitter | 4 - 20 mA | 0 to 100 l/h | TYP-AI-02 | TBAI | LOOP DIAGRAM WRING.dwg | JB-607 | P3-TBAI2-14(B) | C3/C3S7 | C3S7-31/P3-TBAI2-14(B) | P3-TBAI2-14(B)/C3S7-31 | FT-60263FM_AI_1 | [ ] Pass | ____ MΩ | [ ] 24V | ____ mA | ____ mA | ____ mA | [ ] Pass | READY FOR TEST | Pending Sign-off
34 | FT-60264FN | - | 325-01-602-PD-02 | Feed Slurry Flow Transmitter for Nozzle #13 (AMTV-11D) | Ultrasonic Flow Transmitter | 4 - 20 mA | 0 to 100 l/h | TYP-AI-02 | TBAI | LOOP DIAGRAM WRING.dwg | JB-607 | P3-TBAI2-15(B) | C3/C3S7 | C3S7-33/P3-TBAI2-15(B) | P3-TBAI2-15(B)/C3S7-33 | FT-60264FN_AI_1 | [ ] Pass | ____ MΩ | [ ] 24V | ____ mA | ____ mA | ____ mA | [ ] Pass | READY FOR TEST | Pending Sign-off
35 | FT-60264FP | - | 325-01-602-PD-02 | Feed Slurry Flow Transmitter for Nozzle #14 (AMTV-11D) | Ultrasonic Flow Transmitter | 4 - 20 mA | 0 to 100 l/h | TYP-AI-02 | TBAI | LOOP DIAGRAM WRING.dwg | JB-607 | P3-TBAI2-16(B) | C3/C3S7 | C3S7-35/P3-TBAI2-16(B) | P3-TBAI2-16(B)/C3S7-35 | FT-60264FP_AI_1 | [ ] Pass | ____ MΩ | [ ] 24V | ____ mA | ____ mA | ____ mA | [ ] Pass | READY FOR TEST | Pending Sign-off
36 | FT-60264FQ | - | 325-01-602-PD-02 | Feed Slurry Flow Transmitter for Nozzle #15 (AMTV-11D) | Ultrasonic Flow Transmitter | 4 - 20 mA | 0 to 100 l/h | TYP-AI-02 | TBAI | LOOP DIAGRAM WRING.dwg | JB-607 | P3-TBAI3-1(B) | C3/C3S8 | C3S8-1/P3-TBAI3-1(B) | P3-TBAI3-1(B)/C3S8-1 | FT-60264FQ_AI_1 | [ ] Pass | ____ MΩ | [ ] 24V | ____ mA | ____ mA | ____ mA | [ ] Pass | READY FOR TEST | Pending Sign-off
37 | FT-60264FR | - | 325-01-602-PD-02 | Feed Slurry Flow Transmitter for Nozzle #16 (AMTV-11D) | Ultrasonic Flow Transmitter | 4 - 20 mA | 0 to 100 l/h | TYP-AI-02 | TBAI | LOOP DIAGRAM WRING.dwg | JB-607 | P3-TBAI3-2(B) | C3/C3S8 | C3S8-3/P3-TBAI3-2(B) | P3-TBAI3-2(B)/C3S8-3 | FT-60264FR_AI_1 | [ ] Pass | ____ MΩ | [ ] 24V | ____ mA | ____ mA | ____ mA | [ ] Pass | READY FOR TEST | Pending Sign-off
38 | FT-61307 | - | 325-01-613-PD-04 | Compressed air Flow | Thermal Mass Flow Transmitter | 4 - 20 mA | 0 - 1000 m3/hr | TYP-AI-02 | TBAI | LOOP DIAGRAM WRING.dwg | JB-601 | P1-TBAI2-5(B) | C1/C1S11 | C1S11-11/P1-TBAI2-5(B) | P1-TBAI2-5(B)/C1S11-11 | FT-61307_AI_1 | [ ] Pass | ____ MΩ | [ ] 24V | ____ mA | ____ mA | ____ mA | [ ] Pass | READY FOR TEST | Pending Sign-off
39 | FT-60203 | FT-60901 | 325-01-602-PD-09 | Culinary steam feed to Spray dryer | Vortex Flow Transmitter | 4 - 20 mA | 0 - 7000 kg/hr | TYP-AI-02 | TBAI | LOOP DIAGRAM WRING.dwg | JB-606 | P3-TBDI1-17 | C3/C3S1 | C3S1-19/P3-TBDI1-17 | P3-TBDI1-17/C3S1-19 | FT-60203_DI_1 | [ ] Pass | ____ MΩ | [ ] 24V | ____ mA | ____ mA | ____ mA | [ ] Pass | READY FOR TEST | Pending Sign-off
40 | FT-60202 | FT-60902 | 325-01-602-PD-09 | Steam feed to Spray dryer | Vortex Flow Transmitter | 4 - 20 mA | 0 - 2000 kg/hr | TYP-AI-02 | TBAI | LOOP DIAGRAM WRING.dwg | JB-602 | P2-TBDI2-1 | C2/C2S2 | C2S2-1/P2-TBDI2-1 | P2-TBDI2-1/C2S2-1 | FT-60202_DI_1 | [ ] Pass | ____ MΩ | [ ] 24V | ____ mA | ____ mA | ____ mA | [ ] Pass | READY FOR TEST | Pending Sign-off
41 | FT-60204 | FT-61101 | 325-01-602-PD-10 | Compressed air Flow | Thermal Mass Flow Transmitter | 4 - 20 mA | 0 - 1000 m3/hr | TYP-AI-02 | TBAI | LOOP DIAGRAM WRING.dwg | JB-601 | P1-TBAI2-4(B) | C1/C1S11 | C1S11-7/P1-TBAI2-4(B) | P1-TBAI2-4(B)/C1S11-7 | FT-60204_AI_1 | [ ] Pass | ____ MΩ | [ ] 24V | ____ mA | ____ mA | ____ mA | [ ] Pass | READY FOR TEST | Pending Sign-off
42 | FT-936201 | FT-90301 | 325-01-930-PD-01 | Process Water | Magnetic Flow Transmitter | 4 - 20 mA,Pulse | 0-1000kg/m³ | TYP-AI-02 | TBAI | LOOP DIAGRAM WRING.dwg | RIO-200 | P5-TBDI1-3 | C5/C5S1 | C5S1-3/P5-TBDI1-3 | P5-TBDI1-3/C5S1-3 | FT-936201_DI_1 | [ ] Pass | ____ MΩ | [ ] 24V | ____ mA | ____ mA | ____ mA | [ ] Pass | READY FOR TEST | Pending Sign-off
43 | FT-936202 | FT-93001 | 325-01-930-PD-02 | Process Water | Magnetic Flow Transmitter | 4 - 20 mA,Pulse | 0 - 20 m3/ hr | TYP-AI-02 | TBAI | LOOP DIAGRAM WRING.dwg | RIO-200 | P5-TBDI1-4 | C5/C5S1 | C5S1-4/P5-TBDI1-4 | P5-TBDI1-4/C5S1-4 | FT-936202_DI_1 | [ ] Pass | ____ MΩ | [ ] 24V | ____ mA | ____ mA | ____ mA | [ ] Pass | READY FOR TEST | Pending Sign-off
44 | HS-61307A | - | 325-01-613-PD-03 | Start/Stop | Hand Switch | Dry Contact | - | TYP-GEN-01 | TBCI | LOOP DIAGRAM WRING.dwg | PLC | - | - | - | - | - | [ ] Pass | ____ MΩ | [ ] 24V | ____ mA | ____ mA | ____ mA | [ ] Pass | RESERVE ALLOC | Pending Sign-off
45 | HS-61307B | - | 325-01-613-PD-03 | Start/Stop | Hand Switch | Dry Contact | - | TYP-GEN-01 | TBCI | LOOP DIAGRAM WRING.dwg | PLC | - | - | - | - | - | [ ] Pass | ____ MΩ | [ ] 24V | ____ mA | ____ mA | ____ mA | [ ] Pass | RESERVE ALLOC | Pending Sign-off
46 | HS-61307C | - | 325-01-613-PD-03 | Start/Stop | Hand Switch | Dry Contact | - | TYP-GEN-01 | TBCI | LOOP DIAGRAM WRING.dwg | PLC | - | - | - | - | - | [ ] Pass | ____ MΩ | [ ] 24V | ____ mA | ____ mA | ____ mA | [ ] Pass | RESERVE ALLOC | Pending Sign-off
47 | HS-61307D | - | 325-01-613-PD-03 | Start/Stop | Hand Switch | Dry Contact | - | TYP-GEN-01 | TBCI | LOOP DIAGRAM WRING.dwg | PLC | - | - | - | - | - | [ ] Pass | ____ MΩ | [ ] 24V | ____ mA | ____ mA | ____ mA | [ ] Pass | RESERVE ALLOC | Pending Sign-off
48 | HS-61307E | - | 325-01-613-PD-03 | Start/Stop | Hand Switch | Dry Contact | - | TYP-GEN-01 | TBCI | LOOP DIAGRAM WRING.dwg | PLC | - | - | - | - | - | [ ] Pass | ____ MΩ | [ ] 24V | ____ mA | ____ mA | ____ mA | [ ] Pass | RESERVE ALLOC | Pending Sign-off
49 | HS-61307F | - | 325-01-613-PD-03 | Start/Stop | Hand Switch | Dry Contact | - | TYP-GEN-01 | TBCI | LOOP DIAGRAM WRING.dwg | PLC | - | - | - | - | - | [ ] Pass | ____ MΩ | [ ] 24V | ____ mA | ____ mA | ____ mA | [ ] Pass | RESERVE ALLOC | Pending Sign-off
50 | HS-61307G | - | 325-01-613-PD-03 | Start/Stop | Hand Switch | Dry Contact | - | TYP-GEN-01 | TBCI | LOOP DIAGRAM WRING.dwg | PLC | - | - | - | - | - | [ ] Pass | ____ MΩ | [ ] 24V | ____ mA | ____ mA | ____ mA | [ ] Pass | RESERVE ALLOC | Pending Sign-off
51 | HS-61307H | - | 325-01-613-PD-03 | Start/Stop | Hand Switch | Dry Contact | - | TYP-GEN-01 | TBCI | LOOP DIAGRAM WRING.dwg | PLC | - | - | - | - | - | [ ] Pass | ____ MΩ | [ ] 24V | ____ mA | ____ mA | ____ mA | [ ] Pass | RESERVE ALLOC | Pending Sign-off
52 | HS-61307I | - | 325-01-613-PD-03 | Start/Stop | Hand Switch | Dry Contact | - | TYP-GEN-01 | TBCI | LOOP DIAGRAM WRING.dwg | PLC | - | - | - | - | - | [ ] Pass | ____ MΩ | [ ] 24V | ____ mA | ____ mA | ____ mA | [ ] Pass | RESERVE ALLOC | Pending Sign-off
53 | HS-61307J | - | 325-01-613-PD-03 | Start/Stop | Hand Switch | Dry Contact | - | TYP-GEN-01 | TBCI | LOOP DIAGRAM WRING.dwg | PLC | - | - | - | - | - | [ ] Pass | ____ MΩ | [ ] 24V | ____ mA | ____ mA | ____ mA | [ ] Pass | RESERVE ALLOC | Pending Sign-off
54 | HS-61307K | - | 325-01-613-PD-03 | Start/Stop | Hand Switch | Dry Contact | - | TYP-GEN-01 | TBCI | LOOP DIAGRAM WRING.dwg | PLC | - | - | - | - | - | [ ] Pass | ____ MΩ | [ ] 24V | ____ mA | ____ mA | ____ mA | [ ] Pass | RESERVE ALLOC | Pending Sign-off
55 | HS-61307L | - | 325-01-613-PD-03 | Start/Stop | Hand Switch | Dry Contact | - | TYP-GEN-01 | TBCI | LOOP DIAGRAM WRING.dwg | PLC | - | - | - | - | - | [ ] Pass | ____ MΩ | [ ] 24V | ____ mA | ____ mA | ____ mA | [ ] Pass | RESERVE ALLOC | Pending Sign-off
56 | HS-61307M | - | 325-01-613-PD-03 | Start/Stop | Hand Switch | Dry Contact | - | TYP-GEN-01 | TBCI | LOOP DIAGRAM WRING.dwg | PLC | - | - | - | - | - | [ ] Pass | ____ MΩ | [ ] 24V | ____ mA | ____ mA | ____ mA | [ ] Pass | RESERVE ALLOC | Pending Sign-off
57 | HS-61307N | - | 325-01-613-PD-03 | Start/Stop | Hand Switch | Dry Contact | - | TYP-GEN-01 | TBCI | LOOP DIAGRAM WRING.dwg | PLC | - | - | - | - | - | [ ] Pass | ____ MΩ | [ ] 24V | ____ mA | ____ mA | ____ mA | [ ] Pass | RESERVE ALLOC | Pending Sign-off
58 | HS-61307O | - | 325-01-613-PD-03 | Start/Stop | Hand Switch | Dry Contact | - | TYP-GEN-01 | TBCI | LOOP DIAGRAM WRING.dwg | PLC | - | - | - | - | - | [ ] Pass | ____ MΩ | [ ] 24V | ____ mA | ____ mA | ____ mA | [ ] Pass | RESERVE ALLOC | Pending Sign-off
59 | HS-61307P | - | 325-01-613-PD-03 | Start/Stop | Hand Switch | Dry Contact | - | TYP-GEN-01 | TBCI | LOOP DIAGRAM WRING.dwg | PLC | - | - | - | - | - | [ ] Pass | ____ MΩ | [ ] 24V | ____ mA | ____ mA | ____ mA | [ ] Pass | RESERVE ALLOC | Pending Sign-off
60 | HS-61307Q | - | 325-01-613-PD-03 | Start/Stop | Hand Switch | Dry Contact | - | TYP-GEN-01 | TBCI | LOOP DIAGRAM WRING.dwg | PLC | - | - | - | - | - | [ ] Pass | ____ MΩ | [ ] 24V | ____ mA | ____ mA | ____ mA | [ ] Pass | RESERVE ALLOC | Pending Sign-off
61 | HS-61307R | - | 325-01-613-PD-03 | Start/Stop | Hand Switch | Dry Contact | - | TYP-GEN-01 | TBCI | LOOP DIAGRAM WRING.dwg | PLC | - | - | - | - | - | [ ] Pass | ____ MΩ | [ ] 24V | ____ mA | ____ mA | ____ mA | [ ] Pass | RESERVE ALLOC | Pending Sign-off
62 | HV-40203 | HV-4106 | 325-01-402-PD-01 | Slurry Drain tank TS-40201 | Valve With Position Switch | Dry Contact | On-Off | TYP-DI-01 | TBDI | PANEL WIRING DIAGRAM.dwg | JB-401 | P1-TBDI1-23 | C1/C1S4 | C1S4-25/P1-TBDI1-23 | P1-TBDI1-23/C1S4-25 | HV-40203_DI_1 | [ ] Pass | ____ MΩ | [ ] 24V | ____ mA | ____ mA | ____ mA | [ ] Pass | READY FOR TEST | Pending Sign-off
63 | HV-40201 | HV-4108 | 325-01-402-PD-01 | Slurry Drain line | Valve With Position Switch | Dry Contact | On-Off | TYP-DI-01 | TBDI | PANEL WIRING DIAGRAM.dwg | JB-401 | P1-TBDI1-21 | C1/C1S4 | C1S4-23/P1-TBDI1-21 | P1-TBDI1-21/C1S4-23 | HV-40201_DI_1 | [ ] Pass | ____ MΩ | [ ] 24V | ____ mA | ____ mA | ____ mA | [ ] Pass | READY FOR TEST | Pending Sign-off
64 | HV-40204 | HV-4126 | 325-01-402-PD-01 | Slurry Drain tank TS-40202 | Valve With Position Switch | Dry Contact | On-Off | TYP-DI-01 | TBDI | PANEL WIRING DIAGRAM.dwg | JB-401 | P1-TBDI1-24 | C1/C1S4 | C1S4-26/P1-TBDI1-24 | P1-TBDI1-24/C1S4-26 | HV-40204_DI_1 | [ ] Pass | ____ MΩ | [ ] 24V | ____ mA | ____ mA | ____ mA | [ ] Pass | READY FOR TEST | Pending Sign-off
65 | HV-40202 | HV-4128 | 325-01-402-PD-01 | Slurry Drain line | Valve With Position Switch | Dry Contact | On-Off | TYP-DI-01 | TBDI | PANEL WIRING DIAGRAM.dwg | JB-401 | P1-TBDI1-22 | C1/C1S4 | C1S4-24/P1-TBDI1-22 | P1-TBDI1-22/C1S4-24 | HV-40202_DI_1 | [ ] Pass | ____ MΩ | [ ] 24V | ____ mA | ____ mA | ____ mA | [ ] Pass | READY FOR TEST | Pending Sign-off
66 | HV-40206 | HV-4208 | 325-01-402-PD-01 | Slurry Drain tank TS-40203 | Valve With Position Switch | Dry Contact | On-Off | TYP-DI-01 | TBDI | PANEL WIRING DIAGRAM.dwg | JB-401 | P1-TBDI1-26 | C1/C1S4 | C1S4-28/P1-TBDI1-26 | P1-TBDI1-26/C1S4-28 | HV-40206_DI_1 | [ ] Pass | ____ MΩ | [ ] 24V | ____ mA | ____ mA | ____ mA | [ ] Pass | READY FOR TEST | Pending Sign-off
67 | HV-40205 | HV-4210 | 325-01-402-PD-01 | Slurry Drain line | Valve With Position Switch | Dry Contact | On-Off | TYP-DI-01 | TBDI | PANEL WIRING DIAGRAM.dwg | JB-401 | P1-TBDI1-25 | C1/C1S4 | C1S4-27/P1-TBDI1-25 | P1-TBDI1-25/C1S4-27 | HV-40205_DI_1 | [ ] Pass | ____ MΩ | [ ] 24V | ____ mA | ____ mA | ____ mA | [ ] Pass | READY FOR TEST | Pending Sign-off
68 | HV-40207 |  | 325-01-402-PD-01 | Jet Cooker | Valve With Position Switch | Dry Contact | On-Off | TYP-DI-01 | TBDI | PANEL WIRING DIAGRAM.dwg | JB-402 | P2-TBDI1-5 | C2/C2S1 | C2S1-5/P2-TBDI1-5 | P2-TBDI1-5/C2S1-5 | HV-40207_DI_1 | [ ] Pass | ____ MΩ | [ ] 24V | ____ mA | ____ mA | ____ mA | [ ] Pass | READY FOR TEST | Pending Sign-off
69 | HV-40208 |  | 325-01-402-PD-01 | Jet Cooker | Valve With Position Switch | Dry Contact | On-Off | TYP-DI-01 | TBDI | PANEL WIRING DIAGRAM.dwg | JB-402 | P2-TBDI1-6 | C2/C2S1 | C2S1-6/P2-TBDI1-6 | P2-TBDI1-6/C2S1-6 | HV-40208_DI_1 | [ ] Pass | ____ MΩ | [ ] 24V | ____ mA | ____ mA | ____ mA | [ ] Pass | READY FOR TEST | Pending Sign-off
70 | LSH-60230 | - | 325-01-602-PD-04 | Powder Level Switch High for Cyclone (CYCL-21) | Level switch | Dry Contact | - | TYP-DI-01 | TBDI | PANEL WIRING DIAGRAM.dwg | IS-JB-603 | P4-TBDI1-4 | C4/C4S1 | C4S1-4/P4-TBDI1-4 | P4-TBDI1-4/C4S1-4 | LSH-60230_DI_1 | [ ] Pass | ____ MΩ | [ ] 24V | ____ mA | ____ mA | ____ mA | [ ] Pass | READY FOR TEST | Pending Sign-off
71 | LSH-60231 | - | 325-01-602-PD-04 | Powder Level Switch High for Cyclone (CYCL-22) | Level switch | Dry Contact | - | TYP-DI-01 | TBDI | PANEL WIRING DIAGRAM.dwg | IS-JB-603 | P4-TBDI1-5 | C4/C4S1 | C4S1-5/P4-TBDI1-5 | P4-TBDI1-5/C4S1-5 | LSH-60231_DI_1 | [ ] Pass | ____ MΩ | [ ] 24V | ____ mA | ____ mA | ____ mA | [ ] Pass | READY FOR TEST | Pending Sign-off
72 | LSH-60240 | - | 325-01-602-PD-05 | Powder Level Switch High for Bag House (BGHS-21) | Level switch | Dry Contact | - | TYP-DI-01 | TBDI | PANEL WIRING DIAGRAM.dwg | IS-JB-603 | P4-TBDI1-6 | C4/C4S1 | C4S1-6/P4-TBDI1-6 | P4-TBDI1-6/C4S1-6 | LSH-60240_DI_1 | [ ] Pass | ____ MΩ | [ ] 24V | ____ mA | ____ mA | ____ mA | [ ] Pass | READY FOR TEST | Pending Sign-off
73 | LSH-60250 | - | 325-01-602-PD-05 | Water Level Switch High for Fire Deluge Pipe (FWDP-21) | Level switch | Dry Contact | - | TYP-DI-01 | TBDI | PANEL WIRING DIAGRAM.dwg | JB-606 | P3-TBDI1-18 | C3/C3S1 | C3S1-20/P3-TBDI1-18 | P3-TBDI1-18/C3S1-20 | LSH-60250_DI_1 | [ ] Pass | ____ MΩ | [ ] 24V | ____ mA | ____ mA | ____ mA | [ ] Pass | READY FOR TEST | Pending Sign-off
74 | LSH-60251 | - | 325-01-602-PD-04 | Water Level Switch High for Fire Deluge Pipe (FWDP-22) | Level switch | Dry Contact | - | TYP-DI-01 | TBDI | PANEL WIRING DIAGRAM.dwg | JB-602 | P2-TBDI2-2 | C2/C2S2 | C2S2-2/P2-TBDI2-2 | P2-TBDI2-2/C2S2-2 | LSH-60251_DI_1 | [ ] Pass | ____ MΩ | [ ] 24V | ____ mA | ____ mA | ____ mA | [ ] Pass | READY FOR TEST | Pending Sign-off
75 | LSL-60201 | LSL-61101 | 325-01-602-PD-11 | Level low switch | Level switch | Dry Contact | - | TYP-DI-01 | TBDI | PANEL WIRING DIAGRAM.dwg | JB-601 | P1-TBDI3-19 | C1/C1S6 | C1S6-21/P1-TBDI3-19 | P1-TBDI3-19/C1S6-21 | LSL-60201_DI_1 | [ ] Pass | ____ MΩ | [ ] 24V | ____ mA | ____ mA | ____ mA | [ ] Pass | READY FOR TEST | Pending Sign-off
76 | LSH-61301 | - | 325-01-613-PD-01 | Level alarm high | Level switch | Dry Contact | - | TYP-DI-01 | TBDI | PANEL WIRING DIAGRAM.dwg | IS-JB-618 | P4-TBDI3-2 | C4/C4S3 | C4S3-2/P4-TBDI3-2 | P4-TBDI3-2/C4S3-2 | LSH-61301_DI_1 | [ ] Pass | ____ MΩ | [ ] 24V | ____ mA | ____ mA | ____ mA | [ ] Pass | READY FOR TEST | Pending Sign-off
77 | LSL-61302 | - | 325-01-613-PD-01 | Level alarm low | Level switch | Dry Contact | - | TYP-DI-01 | TBDI | PANEL WIRING DIAGRAM.dwg | IS-JB-618 | P4-TBDI3-6 | C4/C4S3 | C4S3-6/P4-TBDI3-6 | P4-TBDI3-6/C4S3-6 | LSL-61302_DI_1 | [ ] Pass | ____ MΩ | [ ] 24V | ____ mA | ____ mA | ____ mA | [ ] Pass | READY FOR TEST | Pending Sign-off
78 | LS-61303 | - | 325-01-613-PD-01 | Level switch | Level switch | Dry Contact | - | TYP-DI-01 | TBDI | PANEL WIRING DIAGRAM.dwg | JB-618 | P3-TBDI3-5 | C3/C3S3 | C3S3-5/P3-TBDI3-5 | P3-TBDI3-5/C3S3-5 | LS-61303_DI_1 | [ ] Pass | ____ MΩ | [ ] 24V | ____ mA | ____ mA | ____ mA | [ ] Pass | READY FOR TEST | Pending Sign-off
79 | LSH-61304 | - | 325-01-613-PD-03 | Big bag level alarm high | Level switch | Dry Contact | - | TYP-DI-01 | TBDI | PANEL WIRING DIAGRAM.dwg | IS-JB-612 | P4-TBDI2-3 | C4/C4S2 | C4S2-3/P4-TBDI2-3 | P4-TBDI2-3/C4S2-3 | LSH-61304_DI_1 | [ ] Pass | ____ MΩ | [ ] 24V | ____ mA | ____ mA | ____ mA | [ ] Pass | READY FOR TEST | Pending Sign-off
80 | LSH-61305 | - | 325-01-613-PD-05 | Big bag level alarm high | Level switch | Dry Contact | - | TYP-DI-01 | TBDI | PANEL WIRING DIAGRAM.dwg | IS-JB-612 | P4-TBDI2-4 | C4/C4S2 | C4S2-4/P4-TBDI2-4 | P4-TBDI2-4/C4S2-4 | LSH-61305_DI_1 | [ ] Pass | ____ MΩ | [ ] 24V | ____ mA | ____ mA | ____ mA | [ ] Pass | READY FOR TEST | Pending Sign-off
81 | LSH-61306 | - | 325-01-613-PD-01 | Level alarm high | Level switch | Dry Contact | - | TYP-DI-01 | TBDI | PANEL WIRING DIAGRAM.dwg | IS-JB-618 | P4-TBDI3-4 | C4/C4S3 | C4S3-4/P4-TBDI3-4 | P4-TBDI3-4/C4S3-4 | LSH-61306_DI_1 | [ ] Pass | ____ MΩ | [ ] 24V | ____ mA | ____ mA | ____ mA | [ ] Pass | READY FOR TEST | Pending Sign-off
82 | LSH-61307 |  | 325-01-613-PD-01 | High Level alarm reject screen | Level switch | Dry Contact | - | TYP-DI-01 | TBDI | PANEL WIRING DIAGRAM.dwg | IS-JB-612 | P4-TBDI2-5 | C4/C4S2 | C4S2-5/P4-TBDI2-5 | P4-TBDI2-5/C4S2-5 | LSH-61307_DI_1 | [ ] Pass | ____ MΩ | [ ] 24V | ____ mA | ____ mA | ____ mA | [ ] Pass | READY FOR TEST | Pending Sign-off
83 | LSH-61308 |  | 325-01-613-PD-01 | High Level alarm Cooling cyclone | Level switch | Dry Contact | - | TYP-DI-01 | TBDI | PANEL WIRING DIAGRAM.dwg | IS-JB-618 | P4-TBDI3-5 | C4/C4S3 | C4S3-5/P4-TBDI3-5 | P4-TBDI3-5/C4S3-5 | LSH-61308_DI_1 | [ ] Pass | ____ MΩ | [ ] 24V | ____ mA | ____ mA | ____ mA | [ ] Pass | READY FOR TEST | Pending Sign-off
84 | LSH-61312 | - | 325-01-613-PD-05 | Level alarm high | Level switch | Dry Contact | - | TYP-DI-01 | TBDI | PANEL WIRING DIAGRAM.dwg | IS-JB-612 | P4-TBDI2-6 | C4/C4S2 | C4S2-6/P4-TBDI2-6 | P4-TBDI2-6/C4S2-6 | LSH-61312_DI_1 | [ ] Pass | ____ MΩ | [ ] 24V | ____ mA | ____ mA | ____ mA | [ ] Pass | READY FOR TEST | Pending Sign-off
85 | LSL-814201 | LSL-81001 | 325-01-814-PD-01 | Low Level alarm |  | Dry Contact | - | TYP-DI-01 | TBDI | PANEL WIRING DIAGRAM.dwg | RIO-200 | P5-TBDI1-5 | C5/C5S1 | C5S1-5/P5-TBDI1-5 | P5-TBDI1-5/C5S1-5 | LSL-814201_DI_1 | [ ] Pass | ____ MΩ | [ ] 24V | ____ mA | ____ mA | ____ mA | [ ] Pass | READY FOR TEST | Pending Sign-off
86 | LT-40201 | LT-40101 | 325-01-402-PD-01 | Level transmitter in pH Adjustment tank 1 | Level transmitter | 4 - 20 mA | 0 - 10 m. | TYP-AI-01 | TBAI | LOOP DIAGRAM WRING.dwg | JB-401 | P1-TBAI1-5(B) | C1/C1S10 | C1S10-11/P1-TBAI1-5(B) | P1-TBAI1-5(B)/C1S10-11 | LT-40201_AI_1 | [ ] Pass | ____ MΩ | [ ] 24V | ____ mA | ____ mA | ____ mA | [ ] Pass | READY FOR TEST | Pending Sign-off
87 | LT-40202 | LT-40102 | 325-01-402-PD-01 | Level transmitter in pH Adjustment tank 2 | Level transmitter | 4 - 20 mA | 0 - 10 m. | TYP-AI-01 | TBAI | LOOP DIAGRAM WRING.dwg | JB-401 | P1-TBAI1-6(B) | C1/C1S10 | C1S10-13/P1-TBAI1-6(B) | P1-TBAI1-6(B)/C1S10-13 | LT-40202_AI_1 | [ ] Pass | ____ MΩ | [ ] 24V | ____ mA | ____ mA | ____ mA | [ ] Pass | READY FOR TEST | Pending Sign-off
88 | LT-40203 | LT-40201 | 325-01-402-PD-02 | Level transmitter in Spray dryer infeed tank | Level transmitter | 4 - 20 mA | 0 - 10 m. | TYP-AI-01 | TBAI | LOOP DIAGRAM WRING.dwg | JB-401 | P1-TBAI1-4(B) | C1/C1S10 | C1S10-7/P1-TBAI1-4(B) | P1-TBAI1-4(B)/C1S10-7 | LT-40203_AI_1 | [ ] Pass | ____ MΩ | [ ] 24V | ____ mA | ____ mA | ____ mA | [ ] Pass | READY FOR TEST | Pending Sign-off
89 | LT-61301 | - | 325-01-613-PD-01 | Level powder in silo | Level transmitter | 4 - 20 mA | - | TYP-AI-01 | TBAI | LOOP DIAGRAM WRING.dwg | IS-JB-618 | P4-TBAI2-7(B) | C4/C4S6 | C4S6-15/P4-TBAI2-7(B) | P4-TBAI2-7(B)/C4S6-15 | LT-61301_AI_1 | [ ] Pass | ____ MΩ | [ ] 24V | ____ mA | ____ mA | ____ mA | [ ] Pass | READY FOR TEST | Pending Sign-off
90 | pHT-40201 | pHT-40101 | 325-01-402-PD-01 | pH analyzer in pH Adjustment tank 1 | pH Analyzer | 4 - 20 mA | 0-14 | TYP-AI-01 | TBAI | LOOP DIAGRAM WRING.dwg | JB-401 | P1-TBAI1-7(B) | C1/C1S10 | C1S10-15/P1-TBAI1-7(B) | P1-TBAI1-7(B)/C1S10-15 | pHT-40201_AI_1 | [ ] Pass | ____ MΩ | [ ] 24V | ____ mA | ____ mA | ____ mA | [ ] Pass | READY FOR TEST | Pending Sign-off
91 | pHT-40202 | pHT-40102 | 325-01-402-PD-01 | pH analyzer in pH Adjustment tank 2 | pH Analyzer | 4 - 20 mA | 0-14 | TYP-AI-01 | TBAI | LOOP DIAGRAM WRING.dwg | JB-401 | P1-TBAI1-8(B) | C1/C1S10 | C1S10-17/P1-TBAI1-8(B) | P1-TBAI1-8(B)/C1S10-17 | pHT-40202_AI_1 | [ ] Pass | ____ MΩ | [ ] 24V | ____ mA | ____ mA | ____ mA | [ ] Pass | READY FOR TEST | Pending Sign-off
92 | PSL-60220 | - | 325-01-602-PD-04 | Gas Pressure Switch Low for Spray Chamber (CHAM-21) | Pressure switch | Dry Contact | -0.01 mbar | TYP-DI-01 | TBDI | PANEL WIRING DIAGRAM.dwg | JB-602 | P2-TBDI2-3 | C2/C2S2 | C2S2-3/P2-TBDI2-3 | P2-TBDI2-3/C2S2-3 | PSL-60220_DI_1 | [ ] Pass | ____ MΩ | [ ] 24V | ____ mA | ____ mA | ____ mA | [ ] Pass | READY FOR TEST | Pending Sign-off
93 | PSL-61301 |  | 325-01-613-PD-01 | Pressure alarm low | Pressure switch | Dry Contact | 0.3-0.7barg | TYP-DI-01 | TBDI | PANEL WIRING DIAGRAM.dwg | JB-618 | P3-TBDI3-6 | C3/C3S3 | C3S3-6/P3-TBDI3-6 | P3-TBDI3-6/C3S3-6 | PSL-61301_DI_1 | [ ] Pass | ____ MΩ | [ ] 24V | ____ mA | ____ mA | ____ mA | [ ] Pass | READY FOR TEST | Pending Sign-off
94 | PSL-61302 | - | 325-01-613-PD-01 | Pressure alarm low | Pressure switch | Dry Contact | 40 mbarg | TYP-DI-01 | TBDI | PANEL WIRING DIAGRAM.dwg | JB-618 | P3-TBDI3-7 | C3/C3S3 | C3S3-7/P3-TBDI3-7 | P3-TBDI3-7/C3S3-7 | PSL-61302_DI_1 | [ ] Pass | ____ MΩ | [ ] 24V | ____ mA | ____ mA | ____ mA | [ ] Pass | READY FOR TEST | Pending Sign-off
95 | PSL-61305 | - | 325-01-613-PD-03 | Pressure alarm low | Pressure switch | Dry Contact | - | TYP-DI-01 | TBDI | PANEL WIRING DIAGRAM.dwg | JB-612 | P3-TBDI2-1 | C3/C3S2 | C3S2-1/P3-TBDI2-1 | P3-TBDI2-1/C3S2-1 | PSL-61305_DI_1 | [ ] Pass | ____ MΩ | [ ] 24V | ____ mA | ____ mA | ____ mA | [ ] Pass | READY FOR TEST | Pending Sign-off
96 | PSL-61306 | - | 325-01-613-PD-05 | Pressure alarm low | Pressure switch | Dry Contact | - | TYP-DI-01 | TBDI | PANEL WIRING DIAGRAM.dwg | JB-612 | P3-TBDI2-2 | C3/C3S2 | C3S2-2/P3-TBDI2-2 | P3-TBDI2-2/C3S2-2 | PSL-61306_DI_1 | [ ] Pass | ____ MΩ | [ ] 24V | ____ mA | ____ mA | ____ mA | [ ] Pass | READY FOR TEST | Pending Sign-off
97 | PSL-61311 | - | 325-01-613-PD-04 | Pressure alarm low | Pressure switch | Dry Contact | - | TYP-DI-01 | TBDI | PANEL WIRING DIAGRAM.dwg | JB-618 | P3-TBDI3-8 | C3/C3S3 | C3S3-8/P3-TBDI3-8 | P3-TBDI3-8/C3S3-8 | PSL-61311_DI_1 | [ ] Pass | ____ MΩ | [ ] 24V | ____ mA | ____ mA | ____ mA | [ ] Pass | READY FOR TEST | Pending Sign-off
98 | PT-40201 | - | 325-01-402-PD-02 | Pressure Transmitter for Inlet Filter Strainer (FSTR-11) | Pressure Transmitter | 4 - 20 mA | -100 to 500 mBar | TYP-AI-01 | TBAI | LOOP DIAGRAM WRING.dwg | JB-401 | P1-TBAI1-9(B) | C1/C1S10 | C1S10-19/P1-TBAI1-9(B) | P1-TBAI1-9(B)/C1S10-19 | PT-40201_AI_1 | [ ] Pass | ____ MΩ | [ ] 24V | ____ mA | ____ mA | ____ mA | [ ] Pass | READY FOR TEST | Pending Sign-off
99 | PT-40202 | - | 325-01-402-PD-02 | Feed Slurry Pressure Transmitter for Pipe (PIPE) | Pressure Transmitter | 4 - 20 mA | 0 - 10'barg | TYP-AI-01 | TBAI | LOOP DIAGRAM WRING.dwg | JB-401 | P1-TBAI1-10(B) | C1/C1S10 | C1S10-21/P1-TBAI1-10(B) | P1-TBAI1-10(B)/C1S10-21 | PT-40202_AI_1 | [ ] Pass | ____ MΩ | [ ] 24V | ____ mA | ____ mA | ____ mA | [ ] Pass | READY FOR TEST | Pending Sign-off
100 | PT-40222 |  | 325-01-402-PD-02 | Jet Cooker | Pressure Transmitter | 4 - 20 mA | 0 - 12'barg | TYP-AI-01 | TBAI | LOOP DIAGRAM WRING.dwg | JB-402 | P2-TBAI1-5(B) | C2/C2S9 | C2S9-11/P2-TBAI1-5(B) | P2-TBAI1-5(B)/C2S9-11 | PT-40222_AI_1 | [ ] Pass | ____ MΩ | [ ] 24V | ____ mA | ____ mA | ____ mA | [ ] Pass | READY FOR TEST | Pending Sign-off
101 | PT-60201 | - | 325-01-602-PD-02 | Steam feed to Spray dryer | Pressure Transmitter | 4 - 20 mA | 0 - 20 bar | TYP-AI-01 | TBAI | LOOP DIAGRAM WRING.dwg | JB-607 | P3-TBAI3-3(B) | C3/C3S8 | C3S8-5/P3-TBAI3-3(B) | P3-TBAI3-3(B)/C3S8-5 | PT-60201_AI_1 | [ ] Pass | ____ MΩ | [ ] 24V | ____ mA | ____ mA | ____ mA | [ ] Pass | READY FOR TEST | Pending Sign-off
102 | PT-60202 | - | 325-01-602-PD-01 | Feed Slurry Pressure Transmitter for High Pressure Pump Outlet (PUPD-11) | Pressure Transmitter | 4 - 20 mA | 0 to 500 bar | TYP-AI-01 | TBAI | LOOP DIAGRAM WRING.dwg | JB-401 | P1-TBAI1-11(B) | C1/C1S10 | C1S10-23/P1-TBAI1-11(B) | P1-TBAI1-11(B)/C1S10-23 | PT-60202_AI_1 | [ ] Pass | ____ MΩ | [ ] 24V | ____ mA | ____ mA | ____ mA | [ ] Pass | READY FOR TEST | Pending Sign-off
103 | PT-60203 | - | 325-01-602-PD-08 | Gas Pressure Transmitter for Cool Air Duct (DTCA-32) | Pressure Transmitter | 4 - 20 mA | 0 - 0.1 mbar | TYP-AI-01 | TBAI | LOOP DIAGRAM WRING.dwg | JB-601 | P1-TBAI2-6(B) | C1/C1S11 | C1S11-13/P1-TBAI2-6(B) | P1-TBAI2-6(B)/C1S11-13 | PT-60203_AI_1 | [ ] Pass | ____ MΩ | [ ] 24V | ____ mA | ____ mA | ____ mA | [ ] Pass | READY FOR TEST | Pending Sign-off
104 | PT-60210 | - | 325-01-602-PD-03 | Gas Pressure Transmitter for Hot Air Duct (DTHA-21) | Pressure Transmitter | 4 - 20 mA | 0 - 0.1 mbar | TYP-AI-01 | TBAI | LOOP DIAGRAM WRING.dwg | JB-602 | P2-TBAI2-4(B) | C2/C2S10 | C2S10-7/P2-TBAI2-4(B) | P2-TBAI2-4(B)/C2S10-7 | PT-60210_AI_1 | [ ] Pass | ____ MΩ | [ ] 24V | ____ mA | ____ mA | ____ mA | [ ] Pass | READY FOR TEST | Pending Sign-off
105 | PT-60215 | - | 325-01-602-PD-03 | 15% Polypropylene Glycol Pressure Indicator Transmitter for Heat Recovery Pumping Skid (PUCF-21) | Pressure Transmitter | 4 - 20 mA | 0 - 6 bar | TYP-AI-01 | TBAI | LOOP DIAGRAM WRING.dwg | JB-602 | P2-TBAI2-5(B) | C2/C2S10 | C2S10-11/P2-TBAI2-5(B) | P2-TBAI2-5(B)/C2S10-11 | PT-60215_AI_1 | [ ] Pass | ____ MΩ | [ ] 24V | ____ mA | ____ mA | ____ mA | [ ] Pass | READY FOR TEST | Pending Sign-off
106 | PT-60216 | - | 325-01-602-PD-03 | Gas Pressure Transmitter for Combustion Air Burner Duct (DTCB-21) | Pressure Transmitter | 4 - 20 mA | 0 - 100 mbar | TYP-AI-01 | TBAI | LOOP DIAGRAM WRING.dwg | JB-602 | P2-TBAI2-6(B) | C2/C2S10 | C2S10-13/P2-TBAI2-6(B) | P2-TBAI2-6(B)/C2S10-13 | PT-60216_AI_1 | [ ] Pass | ____ MΩ | [ ] 24V | ____ mA | ____ mA | ____ mA | [ ] Pass | READY FOR TEST | Pending Sign-off
107 | PT-60220 | - | 325-01-602-PD-04 | Gas Pressure Transmitter for Chamber (CHAM-21) | Pressure Transmitter | 4 - 20 mA | -100 - 100 mbar | TYP-AI-01 | TBAI | LOOP DIAGRAM WRING.dwg | IS-JB-608 | P4-TBAI1-9(B) | C4/C4S5 | C4S5-19/P4-TBAI1-9(B) | P4-TBAI1-9(B)/C4S5-19 | PT-60220_AI_1 | [ ] Pass | ____ MΩ | [ ] 24V | ____ mA | ____ mA | ____ mA | [ ] Pass | READY FOR TEST | Pending Sign-off
108 | PT-60221 | - | 325-01-602-PD-04 | Gas Pressure Transmitter for Cooling Air Duct (DTCA-25) | Pressure Transmitter | 4 - 20 mA | 0 - 0.1 mbar | TYP-AI-01 | TBAI | LOOP DIAGRAM WRING.dwg | JB-607 | P3-TBAI3-5(B) | C3/C3S8 | C3S8-11/P3-TBAI3-5(B) | P3-TBAI3-5(B)/C3S8-11 | PT-60221_AI_1 | [ ] Pass | ____ MΩ | [ ] 24V | ____ mA | ____ mA | ____ mA | [ ] Pass | READY FOR TEST | Pending Sign-off
109 | PT-60230 | - | 325-01-602-PD-04 | Gas Pressure Transmitter for Conveying Duct (DTCO-21) | Pressure Transmitter | 4 - 20 mA | 0 - 0.1 mbar | TYP-AI-01 | TBAI | LOOP DIAGRAM WRING.dwg | IS-JB-603 | P4-TBAI1-1(B) | C4/C4S5 | C4S5-1/P4-TBAI1-1(B) | P4-TBAI1-1(B)/C4S5-1 | PT-60230_AI_1 | [ ] Pass | ____ MΩ | [ ] 24V | ____ mA | ____ mA | ____ mA | [ ] Pass | READY FOR TEST | Pending Sign-off
110 | PT-60231 | - | 325-01-602-PD-04 | Gas Pressure Transmitter for Cyclone Exhaust Duct (DTCE-21) | Pressure Transmitter | 4 - 20 mA | -100 to 200 mbar | TYP-AI-01 | TBAI | LOOP DIAGRAM WRING.dwg | IS-JB-603 | P4-TBAI1-2(B) | C4/C4S5 | C4S5-3/P4-TBAI1-2(B) | P4-TBAI1-2(B)/C4S5-3 | PT-60231_AI_1 | [ ] Pass | ____ MΩ | [ ] 24V | ____ mA | ____ mA | ____ mA | [ ] Pass | READY FOR TEST | Pending Sign-off
111 | PT-60240 | - | 325-01-602-PD-05 | Gas Pressure Transmitter for Bag House Exhaust Duct (DTEX-22) | Pressure Transmitter | 4 - 20 mA | -100 to 200 mbar | TYP-AI-01 | TBAI | LOOP DIAGRAM WRING.dwg | JB-602 | P2-TBAI2-7(B) | C2/C2S10 | C2S10-15/P2-TBAI2-7(B) | P2-TBAI2-7(B)/C2S10-15 | PT-60240_AI_1 | [ ] Pass | ____ MΩ | [ ] 24V | ____ mA | ____ mA | ____ mA | [ ] Pass | READY FOR TEST | Pending Sign-off
112 | PT-60241 | - | 325-01-602-PD-05 | Gas Pressure Transmitter for Exhaust Fan (FANE-21) | Pressure Transmitter | 4 - 20 mA | 0 - 0.1 mbar | TYP-AI-01 | TBAI | LOOP DIAGRAM WRING.dwg | JB-602 | P2-TBAI2-8(B) | C2/C2S10 | C2S10-17/P2-TBAI2-8(B) | P2-TBAI2-8(B)/C2S10-17 | PT-60241_AI_1 | [ ] Pass | ____ MΩ | [ ] 24V | ____ mA | ____ mA | ____ mA | [ ] Pass | READY FOR TEST | Pending Sign-off
113 | PT-60204 | PT-61101 | 325-01-602-PD-10 | Pressure transmitter | Pressure Transmitter | 4 - 20 mA | 0 - 10 barg | TYP-AI-01 | TBAI | LOOP DIAGRAM WRING.dwg | JB-601 | P1-TBAI2-7(B) | C1/C1S11 | C1S11-15/P1-TBAI2-7(B) | P1-TBAI2-7(B)/C1S11-15 | PT-60204_AI_1 | [ ] Pass | ____ MΩ | [ ] 24V | ____ mA | ____ mA | ____ mA | [ ] Pass | READY FOR TEST | Pending Sign-off
114 | PT-61301 | - | 325-01-613-PD-01 | Pressure in silo | Pressure Transmitter | 4 - 20 mA | 0 - 1 barg | TYP-AI-01 | TBAI | LOOP DIAGRAM WRING.dwg | IS-JB-618 | P4-TBAI2-8(B) | C4/C4S6 | C4S6-17/P4-TBAI2-8(B) | P4-TBAI2-8(B)/C4S6-17 | PT-61301_AI_1 | [ ] Pass | ____ MΩ | [ ] 24V | ____ mA | ____ mA | ____ mA | [ ] Pass | READY FOR TEST | Pending Sign-off
115 | PT-61302 | - | 325-01-613-PD-03 | Pressure in vacuum line | Pressure Transmitter | 4 - 20 mA | -100 - 100 mbarg | TYP-AI-01 | TBAI | LOOP DIAGRAM WRING.dwg | JB-612 | P3-TBAI4-9(B) | C3/C3S9 | C3S9-19/P3-TBAI4-9(B) | P3-TBAI4-9(B)/C3S9-19 | PT-61302_AI_1 | [ ] Pass | ____ MΩ | [ ] 24V | ____ mA | ____ mA | ____ mA | [ ] Pass | READY FOR TEST | Pending Sign-off
116 | PT-61303 | - | 325-01-613-PD-01 | Powder Pressure Transmitter for Cooling / Conveyor Cyclone (CYCL-31) | Pressure Transmitter | 4 - 20 mA | -100 to 200 mbar | TYP-AI-01 | TBAI | LOOP DIAGRAM WRING.dwg | JB-618 | P3-TBAI4-1(B) | C3/C3S9 | C3S9-1/P3-TBAI4-1(B) | P3-TBAI4-1(B)/C3S9-1 | PT-61303_AI_1 | [ ] Pass | ____ MΩ | [ ] 24V | ____ mA | ____ mA | ____ mA | [ ] Pass | READY FOR TEST | Pending Sign-off
117 | PT-61304 | - | 325-01-613-PD-01 | Gas Pressure Transmitter for Storage Bin Cyclone Inlet Duct (CYCL-31) | Pressure Transmitter | 4 - 20 mA | -100 to 200 mbar | TYP-AI-01 | TBAI | LOOP DIAGRAM WRING.dwg | IS-JB-618 | P4-TBAI2-10(B) | C4/C4S6 | C4S6-21/P4-TBAI2-10(B) | P4-TBAI2-10(B)/C4S6-21 | PT-61304_AI_1 | [ ] Pass | ____ MΩ | [ ] 24V | ____ mA | ____ mA | ____ mA | [ ] Pass | READY FOR TEST | Pending Sign-off
118 | PT-61305 | - | 325-01-613-PD-01 | Gas Pressure Transmitter for Exhaust Duct (DTEX-31) | Pressure Transmitter | 4 - 20 mA | -100 to 200 mbar | TYP-AI-01 | TBAI | LOOP DIAGRAM WRING.dwg | IS-JB-618 | P4-TBAI2-11(B) | C4/C4S6 | C4S6-23/P4-TBAI2-11(B) | P4-TBAI2-11(B)/C4S6-23 | PT-61305_AI_1 | [ ] Pass | ____ MΩ | [ ] 24V | ____ mA | ____ mA | ____ mA | [ ] Pass | READY FOR TEST | Pending Sign-off
119 | PT-61309 | - | 325-01-613-PD-04 | Pressure transmitter | Pressure Transmitter | 4 - 20 mA | 0 - 10 barg | TYP-AI-01 | TBAI | LOOP DIAGRAM WRING.dwg | JB-612 | P3-TBAI4-10(B) | C3/C3S9 | C3S9-21/P3-TBAI4-10(B) | P3-TBAI4-10(B)/C3S9-21 | PT-61309_AI_1 | [ ] Pass | ____ MΩ | [ ] 24V | ____ mA | ____ mA | ____ mA | [ ] Pass | READY FOR TEST | Pending Sign-off
120 | PCV-60201 | PV-60201 | 325-01-602-PD-02 | Steam feed to Spray dryer | Automatic Control valve | 4 - 20 mA | 0 - 100% | TYP-AO-01 | TBAO | LOOP DIAGRAM WRING.dwg | JB-607 | P3-TBAO1-4 | C3/C3S12 | C3S12-19/P3-TBAO1-4 | P3-TBAO1-4/C3S12-19 | PV-60201_AO_1 | [ ] Pass | ____ MΩ | [ ] 24V | ____ mA | ____ mA | ____ mA | [ ] Pass | READY FOR TEST | Pending Sign-off
121 | SV-40201 | SV-40101 | 325-01-402-PD-01 | Water service pH analyzer in pH Adjustment tank 1 | Solenoid valve | 24 VDC energized | On-Off | TYP-DO-01 | TBDO | PANEL WIRING DIAGRAM.dwg | JB-401 | P1-TBRL1-25 | C1/C1S8 | C1S8-27/P1-TBRL1-25 | P1-TBRL1-25/C1S8-27 | SV-40201_DO_1 | [ ] Pass | ____ MΩ | [ ] 24V | ____ mA | ____ mA | ____ mA | [ ] Pass | READY FOR TEST | Pending Sign-off
122 | SV-40202 | SV-40102 | 325-01-402-PD-01 | Water service pH analyzer in pH Adjustment tank 2 | Solenoid valve | 24 VDC energized | On-Off | TYP-DO-01 | TBDO | PANEL WIRING DIAGRAM.dwg | JB-401 | P1-TBRL1-26 | C1/C1S8 | C1S8-28/P1-TBRL1-26 | P1-TBRL1-26/C1S8-28 | SV-40202_DO_1 | [ ] Pass | ____ MΩ | [ ] 24V | ____ mA | ____ mA | ____ mA | [ ] Pass | READY FOR TEST | Pending Sign-off
123 | SV-40203 | SV-40103 | 325-01-402-PD-01 | Air service pH analyzer in pH Adjustment tank 1 | Solenoid valve | 24 VDC energized | On-Off | TYP-DO-01 | TBDO | PANEL WIRING DIAGRAM.dwg | JB-401 | P1-TBRL1-27 | C1/C1S8 | C1S8-29/P1-TBRL1-27 | P1-TBRL1-27/C1S8-29 | SV-40203_DO_1 | [ ] Pass | ____ MΩ | [ ] 24V | ____ mA | ____ mA | ____ mA | [ ] Pass | READY FOR TEST | Pending Sign-off
124 | SV-40204 | SV-40104 | 325-01-402-PD-01 | Air service pH analyzer in pH Adjustment tank 2 | Solenoid valve | 24 VDC energized | On-Off | TYP-DO-01 | TBDO | PANEL WIRING DIAGRAM.dwg | JB-401 | P1-TBRL1-28 | C1/C1S8 | C1S8-30/P1-TBRL1-28 | P1-TBRL1-28/C1S8-30 | SV-40204_DO_1 | [ ] Pass | ____ MΩ | [ ] 24V | ____ mA | ____ mA | ____ mA | [ ] Pass | READY FOR TEST | Pending Sign-off
125 | SV-60220 | - | 325-01-602-PD-04 | PA On/Off Valve for Chamber PSE purge air (CHAM-21) | Solenoid valve | 24 VDC energized | On-Off | TYP-DO-01 | TBDO | PANEL WIRING DIAGRAM.dwg | JB-606 | P3-TBRL1-9 | C3/C3S4 | C3S4-9/P3-TBRL1-9 | P3-TBRL1-9/C3S4-9 | SV-60220_DO_1 | [ ] Pass | ____ MΩ | [ ] 24V | ____ mA | ____ mA | ____ mA | [ ] Pass | READY FOR TEST | Pending Sign-off
126 | SV-60230 | - | 325-01-602-PD-04 | PA On/Off Valve for Cyclone Air Hammer 27 (CYCL-21) | Solenoid valve | 24 VDC energized | On-Off | TYP-DO-01 | TBDO | PANEL WIRING DIAGRAM.dwg | JB-601 | P1-TBRL2-19 | C1/C1S9 | C1S9-21/P1-TBRL2-19 | P1-TBRL2-19/C1S9-21 | SV-60230_DO_1 | [ ] Pass | ____ MΩ | [ ] 24V | ____ mA | ____ mA | ____ mA | [ ] Pass | READY FOR TEST | Pending Sign-off
127 | SV-60231 | - | 325-01-602-PD-04 | PA On/Off Valve for Cyclone Air Hammer 28 (CYCL-22) | Solenoid valve | 24 VDC energized | On-Off | TYP-DO-01 | TBDO | PANEL WIRING DIAGRAM.dwg | JB-601 | P1-TBRL2-22 | C1/C1S9 | C1S9-24/P1-TBRL2-22 | P1-TBRL2-22/C1S9-24 | SV-60231_DO_1 | [ ] Pass | ____ MΩ | [ ] 24V | ____ mA | ____ mA | ____ mA | [ ] Pass | READY FOR TEST | Pending Sign-off
128 | SV-60240A | - | 325-01-602-PD-05 | PA On/Off Valve for Cyclone Air Hammer 29A (BGHS-21) | Solenoid valve | 24 VDC energized | On-Off | TYP-DO-01 | TBDO | PANEL WIRING DIAGRAM.dwg | JB-601 | P1-TBRL2-21 | C1/C1S9 | C1S9-23/P1-TBRL2-21 | P1-TBRL2-21/C1S9-23 | SV-60240A_DO_1 | [ ] Pass | ____ MΩ | [ ] 24V | ____ mA | ____ mA | ____ mA | [ ] Pass | READY FOR TEST | Pending Sign-off
129 | SV-60240B | - | 325-01-602-PD-05 | PA On/Off Valve for Cyclone Air Hammer 29B (BGHS-21) | Solenoid valve | 24 VDC energized | On-Off | TYP-DO-01 | TBDO | PANEL WIRING DIAGRAM.dwg | JB-601 | P1-TBRL2-23 | C1/C1S9 | C1S9-25/P1-TBRL2-23 | P1-TBRL2-23/C1S9-25 | SV-60240B_DO_1 | [ ] Pass | ____ MΩ | [ ] 24V | ____ mA | ____ mA | ____ mA | [ ] Pass | READY FOR TEST | Pending Sign-off
130 | SV-60240C | - | 325-01-602-PD-05 | PA On/Off Valve for Cyclone Air Hammer 29C (BGHS-21) | Solenoid valve | 24 VDC energized | On-Off | TYP-DO-01 | TBDO | PANEL WIRING DIAGRAM.dwg | JB-601 | P1-TBRL2-24 | C1/C1S9 | C1S9-26/P1-TBRL2-24 | P1-TBRL2-24/C1S9-26 | SV-60240C_DO_1 | [ ] Pass | ____ MΩ | [ ] 24V | ____ mA | ____ mA | ____ mA | [ ] Pass | READY FOR TEST | Pending Sign-off
131 | SV-61301 | - | 325-01-613-PD-01 | Timer compress air pluse solenoid valve | Solenoid valve | 24 VDC energized | On-Off | TYP-DO-01 | TBDO | PANEL WIRING DIAGRAM.dwg | JB-618 | P3-TBRL2-3 | C3/C3S5 | C3S5-3/P3-TBRL2-3 | P3-TBRL2-3/C3S5-3 | SV-61301_DO_1 | [ ] Pass | ____ MΩ | [ ] 24V | ____ mA | ____ mA | ____ mA | [ ] Pass | READY FOR TEST | Pending Sign-off
132 | SV-61302 | - | 325-01-613-PD-01 | Air service | Solenoid valve | 24 VDC energized | On-Off | TYP-DO-01 | TBDO | PANEL WIRING DIAGRAM.dwg | JB-618 | P3-TBRL2-4 | C3/C3S5 | C3S5-4/P3-TBRL2-4 | P3-TBRL2-4/C3S5-4 | SV-61302_DO_1 | [ ] Pass | ____ MΩ | [ ] 24V | ____ mA | ____ mA | ____ mA | [ ] Pass | READY FOR TEST | Pending Sign-off
132 | SV-61306 |  | 325-01-613-PD-01 | Air service | Solenoid valve | 24 VDC energized | On-Off | TYP-DO-01 | TBDO | PANEL WIRING DIAGRAM.dwg | JB-618 | P3-TBRL2-8 | C3/C3S5 | C3S5-8/P3-TBRL2-8 | P3-TBRL2-8/C3S5-8 | SV-61306_DO_1 | [ ] Pass | ____ MΩ | [ ] 24V | ____ mA | ____ mA | ____ mA | [ ] Pass | READY FOR TEST | Pending Sign-off
133 | SV-61303 | - | 325-01-613-PD-01 | Timer compress air pluse solenoid valve | Solenoid valve | 24 VDC energized | On-Off | TYP-DO-01 | TBDO | PANEL WIRING DIAGRAM.dwg | JB-618 | P3-TBRL2-5 | C3/C3S5 | C3S5-5/P3-TBRL2-5 | P3-TBRL2-5/C3S5-5 | SV-61303_DO_1 | [ ] Pass | ____ MΩ | [ ] 24V | ____ mA | ____ mA | ____ mA | [ ] Pass | READY FOR TEST | Pending Sign-off
134 | SV-61305 | - | 325-01-613-PD-01 | Air service | Solenoid valve | 24 VDC energized | On-Off | TYP-DO-01 | TBDO | PANEL WIRING DIAGRAM.dwg | JB-618 | P3-TBRL2-7 | C3/C3S5 | C3S5-7/P3-TBRL2-7 | P3-TBRL2-7/C3S5-7 | SV-61305_DO_1 | [ ] Pass | ____ MΩ | [ ] 24V | ____ mA | ____ mA | ____ mA | [ ] Pass | READY FOR TEST | Pending Sign-off
135 | SV-61308 | - | 325-01-613-PD-03 | Timer compress air pluse solenoid valve | Solenoid valve | 24 VDC energized | On-Off | TYP-DO-01 | TBDO | PANEL WIRING DIAGRAM.dwg | JB-612 | P3-TBRL1-20 | C3/C3S4 | C3S4-22/P3-TBRL1-20 | P3-TBRL1-20/C3S4-22 | SV-61308_DO_1 | [ ] Pass | ____ MΩ | [ ] 24V | ____ mA | ____ mA | ____ mA | [ ] Pass | READY FOR TEST | Pending Sign-off
136 | SV-61309 | - | 325-01-613-PD-03 | Air service | Solenoid valve | 24 VDC energized | On-Off | TYP-DO-01 | TBDO | PANEL WIRING DIAGRAM.dwg | JB-612 | P3-TBRL1-21 | C3/C3S4 | C3S4-23/P3-TBRL1-21 | P3-TBRL1-21/C3S4-23 | SV-61309_DO_1 | [ ] Pass | ____ MΩ | [ ] 24V | ____ mA | ____ mA | ____ mA | [ ] Pass | READY FOR TEST | Pending Sign-off
137 | SV-61310 | - | 325-01-613-PD-05 | Timer compress air pluse solenoid valve | Solenoid valve | 24 VDC energized | On-Off | TYP-DO-01 | TBDO | PANEL WIRING DIAGRAM.dwg | JB-612 | P3-TBRL1-22 | C3/C3S4 | C3S4-24/P3-TBRL1-22 | P3-TBRL1-22/C3S4-24 | SV-61310_DO_1 | [ ] Pass | ____ MΩ | [ ] 24V | ____ mA | ____ mA | ____ mA | [ ] Pass | READY FOR TEST | Pending Sign-off
138 | SV-61311 | - | 325-01-613-PD-05 | Air service | Solenoid valve | 24 VDC energized | On-Off | TYP-DO-01 | TBDO | PANEL WIRING DIAGRAM.dwg | JB-612 | P3-TBRL1-23 | C3/C3S4 | C3S4-25/P3-TBRL1-23 | P3-TBRL1-23/C3S4-25 | SV-61311_DO_1 | [ ] Pass | ____ MΩ | [ ] 24V | ____ mA | ____ mA | ____ mA | [ ] Pass | READY FOR TEST | Pending Sign-off
139 | TSH-60230 | - | 325-01-602-PD-04 | Gas and Powder Temperature Switch High for Conveying Duct (DTCO-21) | Temperature Switch | Dry Contact | 0 - 140 C | TYP-DI-01 | TBDI | PANEL WIRING DIAGRAM.dwg | JB-602 | P2-TBDI2-4 | C2/C2S2 | C2S2-4/P2-TBDI2-4 | P2-TBDI2-4/C2S2-4 | TSH-60230_DI_1 | [ ] Pass | ____ MΩ | [ ] 24V | ____ mA | ____ mA | ____ mA | [ ] Pass | READY FOR TEST | Pending Sign-off
140 | TSH-60240 | - | 325-01-602-PD-05 | Gas and Powder Temperature Switch High for Exhaust Duct (DTEX-22) | Temperature Switch | Dry Contact | 0 - 140 C | TYP-DI-01 | TBDI | PANEL WIRING DIAGRAM.dwg | JB-602 | P2-TBDI2-5 | C2/C2S2 | C2S2-5/P2-TBDI2-5 | P2-TBDI2-5/C2S2-5 | TSH-60240_DI_1 | [ ] Pass | ____ MΩ | [ ] 24V | ____ mA | ____ mA | ____ mA | [ ] Pass | READY FOR TEST | Pending Sign-off
141 | TT-40221 |  | 325-01-402-PD-02 | Jet Cooker | Temperature Transmitter | 4 - 20 mA | 0 - 120 C | TYP-AI-01 | TBAI | LOOP DIAGRAM WRING.dwg | JB-402 | P2-TBAI1-6(B) | C2/C2S9 | C2S9-13/P2-TBAI1-6(B) | P2-TBAI1-6(B)/C2S9-13 | TT-40221_AI_1 | [ ] Pass | ____ MΩ | [ ] 24V | ____ mA | ____ mA | ____ mA | [ ] Pass | READY FOR TEST | Pending Sign-off
142 | TT-40222 |  | 325-01-402-PD-02 | Jet Cooker | Temperature Transmitter | 4 - 20 mA | 0 - 200 C | TYP-AI-01 | TBAI | LOOP DIAGRAM WRING.dwg | JB-402 | P2-TBAI1-7(B) | C2/C2S9 | C2S9-15/P2-TBAI1-7(B) | P2-TBAI1-7(B)/C2S9-15 | TT-40222_AI_1 | [ ] Pass | ____ MΩ | [ ] 24V | ____ mA | ____ mA | ____ mA | [ ] Pass | READY FOR TEST | Pending Sign-off
143 | TT-60201 | - | 325-01-602-PD-02 | Steam feed to Spray dryer | Temperature Transmitter | 4 - 20 mA | 0 - 300 C | TYP-AI-01 | TBAI | LOOP DIAGRAM WRING.dwg | JB-607 | P3-TBAI3-8(B) | C3/C3S8 | C3S8-17/P3-TBAI3-8(B) | P3-TBAI3-8(B)/C3S8-17 | TT-60201_AI_1 | [ ] Pass | ____ MΩ | [ ] 24V | ____ mA | ____ mA | ____ mA | [ ] Pass | READY FOR TEST | Pending Sign-off
144 | TT-60210 | - | 325-01-602-PD-03 | Gas Temperature Element for Hot Air Duct (DTHA-21) | Temperature Transmitter | 4 - 20 mA | 0 - 400'°C | TYP-AI-01 | TBAI | LOOP DIAGRAM WRING.dwg | JB-602 | P2-TBAI2-9(B) | C2/C2S10 | C2S10-19/P2-TBAI2-9(B) | P2-TBAI2-9(B)/C2S10-19 | TT-60210_AI_1 | [ ] Pass | ____ MΩ | [ ] 24V | ____ mA | ____ mA | ____ mA | [ ] Pass | READY FOR TEST | Pending Sign-off
145 | TT-60210A | TT-60212A | 325-01-602-PD-03 | Bearing Temperature Transmitter for Main Supply Air Fan (FANS-21) | Temperature Transmitter | 4 - 20 mA | 0 - 100 C | TYP-AI-01 | TBAI | LOOP DIAGRAM WRING.dwg | JB-602 | P2-TBAI2-10(B) | C2/C2S10 | C2S10-21/P2-TBAI2-10(B) | P2-TBAI2-10(B)/C2S10-21 | TT-60210A_AI_1 | [ ] Pass | ____ MΩ | [ ] 24V | ____ mA | ____ mA | ____ mA | [ ] Pass | READY FOR TEST | Pending Sign-off
146 | TT-60210B | TT-60212B | 325-01-602-PD-03 | Bearing Temperature Transmitter for Main Supply Air Fan (FANS-21) | Temperature Transmitter | 4 - 20 mA | 0 - 100 C | TYP-AI-01 | TBAI | LOOP DIAGRAM WRING.dwg | JB-602 | P2-TBAI2-11(B) | C2/C2S10 | C2S10-23/P2-TBAI2-11(B) | P2-TBAI2-11(B)/C2S10-23 | TT-60210B_AI_1 | [ ] Pass | ____ MΩ | [ ] 24V | ____ mA | ____ mA | ____ mA | [ ] Pass | READY FOR TEST | Pending Sign-off
147 | TT-60211 | - | 325-01-602-PD-03 | Gas Temperature Element for Hot Air Duct (DTHA-21) | Temperature Transmitter | 4 - 20 mA | 0 - 400'°C | TYP-AI-01 | TBAI | LOOP DIAGRAM WRING.dwg | JB-602 | P2-TBAI2-12(B) | C2/C2S10 | C2S10-25/P2-TBAI2-12(B) | P2-TBAI2-12(B)/C2S10-25 | TT-60211_AI_1 | [ ] Pass | ____ MΩ | [ ] 24V | ____ mA | ____ mA | ____ mA | [ ] Pass | READY FOR TEST | Pending Sign-off
148 | TT-60214 | - | 325-01-602-PD-03 | Steam Temperature Transmitter for Cold Air Duct (DTCA-23) | Temperature Transmitter | 4 - 20 mA | -10 to 250°C | TYP-AI-01 | TBAI | LOOP DIAGRAM WRING.dwg | JB-602 | P2-TBAI2-15(B) | C2/C2S10 | C2S10-33/P2-TBAI2-15(B) | P2-TBAI2-15(B)/C2S10-33 | TT-60214_AI_1 | [ ] Pass | ____ MΩ | [ ] 24V | ____ mA | ____ mA | ____ mA | [ ] Pass | READY FOR TEST | Pending Sign-off
149 | TT-60215A | - | 325-01-602-PD-03 | Liquid Temperature Transmitter for Heat Recovery (HXCR-21) | Temperature Transmitter | 4 - 20 mA | -10 to 150°C | TYP-AI-01 | TBAI | LOOP DIAGRAM WRING.dwg | JB-602 | P2-TBAI2-16(B) | C2/C2S10 | C2S10-35/P2-TBAI2-16(B) | P2-TBAI2-16(B)/C2S10-35 | TT-60215A_AI_1 | [ ] Pass | ____ MΩ | [ ] 24V | ____ mA | ____ mA | ____ mA | [ ] Pass | READY FOR TEST | Pending Sign-off
150 | TT-60215B | - | 325-01-602-PD-03 | Liquid Temperature Transmitter for Heat Recovery (HXCR-21) | Temperature Transmitter | 4 - 20 mA | -10 to 150°C | TYP-AI-01 | TBAI | LOOP DIAGRAM WRING.dwg | JB-602 | P3-TBAI1-1(B) | C3/C3S6 | C3S6-1/P3-TBAI1-1(B) | P3-TBAI1-1(B)/C3S6-1 | TT-60215B_AI_1 | [ ] Pass | ____ MΩ | [ ] 24V | ____ mA | ____ mA | ____ mA | [ ] Pass | READY FOR TEST | Pending Sign-off
151 | TT-60216 | - | 325-01-602-PD-03 | Gas Temperature Transmitter for Combustion Air Burner Duct (DTCB-21) | Temperature Transmitter | 4 - 20 mA | 0 - 200'°C | TYP-AI-01 | TBAI | LOOP DIAGRAM WRING.dwg | JB-602 | P3-TBAI1-2(B) | C3/C3S6 | C3S6-3/P3-TBAI1-2(B) | P3-TBAI1-2(B)/C3S6-3 | TT-60216_AI_1 | [ ] Pass | ____ MΩ | [ ] 24V | ____ mA | ____ mA | ____ mA | [ ] Pass | READY FOR TEST | Pending Sign-off
152 | TT-60220 | - | 325-01-602-PD-04 | Gas and Powder Temperature Transmitter for Spray Chamber (CHAM-21) | Temperature Transmitter | 4 - 20 mA | 0 - 400'°C | TYP-AI-01 | TBAI | LOOP DIAGRAM WRING.dwg | IS-JB-608 | P4-TBAI1-10(B) | C4/C4S5 | C4S5-21/P4-TBAI1-10(B) | P4-TBAI1-10(B)/C4S5-21 | TT-60220_AI_1 | [ ] Pass | ____ MΩ | [ ] 24V | ____ mA | ____ mA | ____ mA | [ ] Pass | READY FOR TEST | Pending Sign-off
153 | TT-60221 | - | 325-01-602-PD-04 | Gas and Powder Temperature Transmitter for Spray Chamber (CHAM-21) | Temperature Transmitter | 4 - 20 mA | 0 - 400'°C | TYP-AI-01 | TBAI | LOOP DIAGRAM WRING.dwg | IS-JB-608 | P4-TBAI1-11(B) | C4/C4S5 | C4S5-23/P4-TBAI1-11(B) | P4-TBAI1-11(B)/C4S5-23 | TT-60221_AI_1 | [ ] Pass | ____ MΩ | [ ] 24V | ____ mA | ____ mA | ____ mA | [ ] Pass | READY FOR TEST | Pending Sign-off
154 | TT-60222 | - | 325-01-602-PD-04 | Gas and Powder Temperature Transmitter for Spray Chamber (CHAM-21) | Temperature Transmitter | 4 - 20 mA | 0 - 400'°C | TYP-AI-01 | TBAI | LOOP DIAGRAM WRING.dwg | IS-JB-608 | P4-TBAI1-12(B) | C4/C4S5 | C4S5-25/P4-TBAI1-12(B) | P4-TBAI1-12(B)/C4S5-25 | TT-60222_AI_1 | [ ] Pass | ____ MΩ | [ ] 24V | ____ mA | ____ mA | ____ mA | [ ] Pass | READY FOR TEST | Pending Sign-off
155 | TT-60223 | - | 325-01-602-PD-04 | Gas and Powder Temperature Transmitter for Spray Chamber (CHAM-21) | Temperature Transmitter | 4 - 20 mA | 0 - 400'°C | TYP-AI-01 | TBAI | LOOP DIAGRAM WRING.dwg | IS-JB-608 | P4-TBAI1-13(B) | C4/C4S5 | C4S5-29/P4-TBAI1-13(B) | P4-TBAI1-13(B)/C4S5-29 | TT-60223_AI_1 | [ ] Pass | ____ MΩ | [ ] 24V | ____ mA | ____ mA | ____ mA | [ ] Pass | READY FOR TEST | Pending Sign-off
156 | TT-60224 | - | 325-01-602-PD-04 | Gas and Powder Temperature Transmitter for Spray Chamber (CHAM-21) | Temperature Transmitter | 4 - 20 mA | 0 - 400'°C | TYP-AI-01 | TBAI | LOOP DIAGRAM WRING.dwg | IS-JB-603 | P4-TBAI1-3(B) | C4/C4S5 | C4S5-5/P4-TBAI1-3(B) | P4-TBAI1-3(B)/C4S5-5 | TT-60224_AI_1 | [ ] Pass | ____ MΩ | [ ] 24V | ____ mA | ____ mA | ____ mA | [ ] Pass | READY FOR TEST | Pending Sign-off
157 | TT-60225 | - | 325-01-602-PD-04 | Gas and Powder Temperature Transmitter for Spray Chamber (CHAM-21) | Temperature Transmitter | 4 - 20 mA | 0 - 400'°C | TYP-AI-01 | TBAI | LOOP DIAGRAM WRING.dwg | IS-JB-603 | P4-TBAI1-4(B) | C4/C4S5 | C4S5-7/P4-TBAI1-4(B) | P4-TBAI1-4(B)/C4S5-7 | TT-60225_AI_1 | [ ] Pass | ____ MΩ | [ ] 24V | ____ mA | ____ mA | ____ mA | [ ] Pass | READY FOR TEST | Pending Sign-off
158 | TT-60226 | - | 325-01-602-PD-04 | Gas and Powder Temperature Transmitter for Spray Chamber (CHAM-21) | Temperature Transmitter | 4 - 20 mA | 0 - 400'°C | TYP-AI-01 | TBAI | LOOP DIAGRAM WRING.dwg | IS-JB-603 | P4-TBAI1-5(B) | C4/C4S5 | C4S5-11/P4-TBAI1-5(B) | P4-TBAI1-5(B)/C4S5-11 | TT-60226_AI_1 | [ ] Pass | ____ MΩ | [ ] 24V | ____ mA | ____ mA | ____ mA | [ ] Pass | READY FOR TEST | Pending Sign-off
159 | TT-60227 | - | 325-01-602-PD-04 | Gas and Powder Temperature Transmitter for Spray Chamber (CHAM-21) | Temperature Transmitter | 4 - 20 mA | 0 - 400'°C | TYP-AI-01 | TBAI | LOOP DIAGRAM WRING.dwg | IS-JB-603 | P4-TBAI1-6(B) | C4/C4S5 | C4S5-13/P4-TBAI1-6(B) | P4-TBAI1-6(B)/C4S5-13 | TT-60227_AI_1 | [ ] Pass | ____ MΩ | [ ] 24V | ____ mA | ____ mA | ____ mA | [ ] Pass | READY FOR TEST | Pending Sign-off
160 | TT-60230 | - | 325-01-602-PD-04 | Gas and Powder Temperature Transmitter for Conveying Duct (DTCO-21) | Temperature Transmitter | 4 - 20 mA | 0 - 400'°C | TYP-AI-01 | TBAI | LOOP DIAGRAM WRING.dwg | IS-JB-603 | P4-TBAI1-7(B) | C4/C4S5 | C4S5-15/P4-TBAI1-7(B) | P4-TBAI1-7(B)/C4S5-15 | TT-60230_AI_1 | [ ] Pass | ____ MΩ | [ ] 24V | ____ mA | ____ mA | ____ mA | [ ] Pass | READY FOR TEST | Pending Sign-off
161 | TT-60240 | - | 325-01-602-PD-05 | Gas Temperature Transmitter for Exhaust Fan (FANE-21) | Temperature Transmitter | 4 - 20 mA | 0 - 400'°C | TYP-AI-01 | TBAI | LOOP DIAGRAM WRING.dwg | JB-602 | P3-TBAI1-3(B) | C3/C3S6 | C3S6-5/P3-TBAI1-3(B) | P3-TBAI1-3(B)/C3S6-5 | TT-60240_AI_1 | [ ] Pass | ____ MΩ | [ ] 24V | ____ mA | ____ mA | ____ mA | [ ] Pass | READY FOR TEST | Pending Sign-off
162 | TT-60241A | - | 325-01-602-PD-05 | Bearing Temperature Transmitter for Main Exhaust Air Fan (FANE-21) | Temperature Transmitter | 4 - 20 mA | 0 - 100 C | TYP-AI-01 | TBAI | LOOP DIAGRAM WRING.dwg | JB-602 | P3-TBAI1-4(B) | C3/C3S6 | C3S6-7/P3-TBAI1-4(B) | P3-TBAI1-4(B)/C3S6-7 | TT-60241A_AI_1 | [ ] Pass | ____ MΩ | [ ] 24V | ____ mA | ____ mA | ____ mA | [ ] Pass | READY FOR TEST | Pending Sign-off
163 | TT-60241B | - | 325-01-602-PD-05 | Bearing Temperature Transmitter for Main Exhaust Air Fan (FANE-21) | Temperature Transmitter | 4 - 20 mA | 0 - 100 C | TYP-AI-01 | TBAI | LOOP DIAGRAM WRING.dwg | JB-602 | P3-TBAI1-5(B) | C3/C3S6 | C3S6-11/P3-TBAI1-5(B) | P3-TBAI1-5(B)/C3S6-11 | TT-60241B_AI_1 | [ ] Pass | ____ MΩ | [ ] 24V | ____ mA | ____ mA | ____ mA | [ ] Pass | READY FOR TEST | Pending Sign-off
164 | TT-60245 | - | 325-01-602-PD-05 | Gas Temperature Transmitter for Exhaust Stack (DTXS-21) | Temperature Transmitter | 4 - 20 mA | -10 to 150°C | TYP-AI-01 | TBAI | LOOP DIAGRAM WRING.dwg | JB-608 | P3-TBAI3-16(B) | C3/C3S8 | C3S8-35/P3-TBAI3-16(B) | P3-TBAI3-16(B)/C3S8-35 | TT-60245_AI_1 | [ ] Pass | ____ MΩ | [ ] 24V | ____ mA | ____ mA | ____ mA | [ ] Pass | READY FOR TEST | Pending Sign-off
165 | TT-60202 | TT-60702 | 325-01-602-PD-07 | Compress air temp to camera | Temperature Transmitter | 4 - 20 mA | 0 - 40 C | TYP-AI-01 | TBAI | LOOP DIAGRAM WRING.dwg | JB-607 | P3-TBAI3-9(B) | C3/C3S8 | C3S8-19/P3-TBAI3-9(B) | P3-TBAI3-9(B)/C3S8-19 | TT-60202_AI_1 | [ ] Pass | ____ MΩ | [ ] 24V | ____ mA | ____ mA | ____ mA | [ ] Pass | READY FOR TEST | Pending Sign-off
166 | TT-61301 | - | 325-01-613-PD-01 | Gas Temperature Transmitter for Cold Air Duct (DTCA-32) | Temperature Transmitter | 4 - 20 mA | 0 - 400'°C | TYP-AI-01 | TBAI | LOOP DIAGRAM WRING.dwg | IS-JB-618 | P4-TBAI2-12(B) | C4/C4S6 | C4S6-25/P4-TBAI2-12(B) | P4-TBAI2-12(B)/C4S6-25 | TT-61301_AI_1 | [ ] Pass | ____ MΩ | [ ] 24V | ____ mA | ____ mA | ____ mA | [ ] Pass | READY FOR TEST | Pending Sign-off
167 | TT-61302 | - | 325-01-613-PD-01 | Gas and Powder Temperature Transmitter for Cooling Cyclone (CYCL-31) | Temperature Transmitter | 4 - 20 mA | 0 - 400'°C | TYP-AI-01 | TBAI | LOOP DIAGRAM WRING.dwg | IS-JB-618 | P4-TBAI2-13(B) | C4/C4S6 | C4S6-29/P4-TBAI2-13(B) | P4-TBAI2-13(B)/C4S6-29 | TT-61302_AI_1 | [ ] Pass | ____ MΩ | [ ] 24V | ____ mA | ____ mA | ____ mA | [ ] Pass | READY FOR TEST | Pending Sign-off
168 | TCV-40222 |  | 325-01-402-PD-02 | Jet Cooker | Automatic Control valve | 4 - 20 mA | 0 - 100% | TYP-AO-01 | TBAO | LOOP DIAGRAM WRING.dwg | JB-402 | P3-TBAO1-1 | C3/C3S12 | C3S12-3/P3-TBAO1-1 | P3-TBAO1-1/C3S12-3 | TCV-40222_AO_1 | [ ] Pass | ____ MΩ | [ ] 24V | ____ mA | ____ mA | ____ mA | [ ] Pass | READY FOR TEST | Pending Sign-off
169 | TCV-60214 | TV-60214 | 325-01-602-PD-03 | Steam Temperature Valve for Pre-Heat Steam Heat Exchanger (HXCH-21) | Automatic Control valve | 4 - 20 mA | 0 - 100% | TYP-AO-01 | TBAO | LOOP DIAGRAM WRING.dwg | JB-602 | P3-TBAO1-3 | C3/C3S12 | C3S12-13/P3-TBAO1-3 | P3-TBAO1-3/C3S12-13 | TV-60214_AO_1 | [ ] Pass | ____ MΩ | [ ] 24V | ____ mA | ____ mA | ____ mA | [ ] Pass | READY FOR TEST | Pending Sign-off
170 | TCV-60202 | TV-60702 | 325-01-602-PD-07 | Chiller water control valve | 3-way Control valve | 4 - 20 mA | 0 - 100% | TYP-AO-01 | TBAO | LOOP DIAGRAM WRING.dwg | PLC | - | - | - | - | - | [ ] Pass | ____ MΩ | [ ] 24V | ____ mA | ____ mA | ____ mA | [ ] Pass | RESERVE ALLOC | Pending Sign-off
171 | VT-60210A | - | 325-01-602-PD-03 | Vibration Transmitter for Main Supply Air Fan (FANS-21) | Vibration Transmitter | 4 - 20 mA | mm/sec | TYP-AI-01 | TBAI | LOOP DIAGRAM WRING.dwg | JB-602 | P3-TBAI1-6(B) | C3/C3S6 | C3S6-13/P3-TBAI1-6(B) | P3-TBAI1-6(B)/C3S6-13 | VT-60210A_AI_1 | [ ] Pass | ____ MΩ | [ ] 24V | ____ mA | ____ mA | ____ mA | [ ] Pass | READY FOR TEST | Pending Sign-off
172 | VT-60210B | - | 325-01-602-PD-03 | Vibration Transmitter for Main Supply Air Fan (FANS-21) | Vibration Transmitter | 4 - 20 mA | mm/sec | TYP-AI-01 | TBAI | LOOP DIAGRAM WRING.dwg | JB-602 | P3-TBAI1-7(B) | C3/C3S6 | C3S6-15/P3-TBAI1-7(B) | P3-TBAI1-7(B)/C3S6-15 | VT-60210B_AI_1 | [ ] Pass | ____ MΩ | [ ] 24V | ____ mA | ____ mA | ____ mA | [ ] Pass | READY FOR TEST | Pending Sign-off
173 | VT-60241A | - | 325-01-602-PD-05 | Vibration Transmitter for Main Exhaust Air Fan (FANE-21) | Vibration Transmitter | 4 - 20 mA | mm/sec | TYP-AI-01 | TBAI | LOOP DIAGRAM WRING.dwg | JB-602 | P3-TBAI1-8(B) | C3/C3S6 | C3S6-17/P3-TBAI1-8(B) | P3-TBAI1-8(B)/C3S6-17 | VT-60241A_AI_1 | [ ] Pass | ____ MΩ | [ ] 24V | ____ mA | ____ mA | ____ mA | [ ] Pass | READY FOR TEST | Pending Sign-off
174 | VT-60241B | - | 325-01-602-PD-05 | Vibration Transmitter for Main Exhaust Air Fan (FANE-21) | Vibration Transmitter | 4 - 20 mA | mm/sec | TYP-AI-01 | TBAI | LOOP DIAGRAM WRING.dwg | JB-602 | P3-TBAI1-9(B) | C3/C3S6 | C3S6-19/P3-TBAI1-9(B) | P3-TBAI1-9(B)/C3S6-19 | VT-60241B_AI_1 | [ ] Pass | ____ MΩ | [ ] 24V | ____ mA | ____ mA | ____ mA | [ ] Pass | READY FOR TEST | Pending Sign-off
175 | XT-60201 | XT-60301 | 325-01-402-PD-03 | LEL gas analyzer | Gas detector | 4 - 20 mA | 0-10%LEL | TYP-AI-01 | TBAI | LOOP DIAGRAM WRING.dwg | IS-JB-608 | P4-TBAI1-14(B) | C4/C4S5 | C4S5-31/P4-TBAI1-14(B) | P4-TBAI1-14(B)/C4S5-31 | XT-60201_AI_1 | [ ] Pass | ____ MΩ | [ ] 24V | ____ mA | ____ mA | ____ mA | [ ] Pass | READY FOR TEST | Pending Sign-off
176 | XA-60201 | XA-60301 | 325-01-402-PD-03 | LEL gas Buzzer Alarm | Gas detector | 4 - 20 mA | 0-10%LEL | TYP-DO-01 | TBDO | PANEL WIRING DIAGRAM.dwg | IS-JB-608 | P4-TBRL1-9 | C4/C4S4 | C4S4-9/P4-TBRL1-9 | P4-TBRL1-9/C4S4-9 | XA-60201_DO_1 | [ ] Pass | ____ MΩ | [ ] 24V | ____ mA | ____ mA | ____ mA | [ ] Pass | READY FOR TEST | Pending Sign-off
177 | XT-92201 | - | 325-01-923-PD-03 | LEL gas analyzer | Gas detector | 4 - 20 mA | 0-10%LEL | TYP-AI-01 | TBAI | LOOP DIAGRAM WRING.dwg | RIO-200 | P5-TBAI1-8(B) | C5/C5S4 | C5S4-17/P5-TBAI1-8(B) | P5-TBAI1-8(B)/C5S4-17 | XT-92201_AI_1 | [ ] Pass | ____ MΩ | [ ] 24V | ____ mA | ____ mA | ____ mA | [ ] Pass | READY FOR TEST | Pending Sign-off
178 | XA-92201 | - | 325-01-923-PD-03 | LEL gas Buzzer Alarm | Gas detector | 4 - 20 mA | 0-10%LEL | TYP-DO-01 | TBDO | PANEL WIRING DIAGRAM.dwg | RIO-200 | P5-TBRL1-1 | C5/C5S3 | C5S3-1/P5-TBRL1-1 | P5-TBRL1-1/C5S3-1 | XA-92201_DO_1 | [ ] Pass | ____ MΩ | [ ] 24V | ____ mA | ____ mA | ____ mA | [ ] Pass | READY FOR TEST | Pending Sign-off
179 | XV-40201A | XV-40101A | 325-01-402-PD-01 | Slurry feed-in pH Adjustment tank 1 | Automatic on/off valve | 24 VDC energized | On-Off | TYP-DO-01 | TBDO | PANEL WIRING DIAGRAM.dwg | JB-401 | P1-TBDI1-27 | C1/C1S4 | C1S4-29/P1-TBDI1-27 | P1-TBDI1-27/C1S4-29 | XV-40201A_DI_1 | [ ] Pass | ____ MΩ | [ ] 24V | ____ mA | ____ mA | ____ mA | [ ] Pass | READY FOR TEST | Pending Sign-off
180 | XV-40201B | XV-40101B | 325-01-402-PD-01 | Slurry feed-out pH Adjustment tank 1 | Automatic on/off valve | 24 VDC energized | On-Off | TYP-DO-01 | TBDO | PANEL WIRING DIAGRAM.dwg | JB-401 | P1-TBDI1-29 | C1/C1S4 | C1S4-31/P1-TBDI1-29 | P1-TBDI1-29/C1S4-31 | XV-40201B_DI_1 | [ ] Pass | ____ MΩ | [ ] 24V | ____ mA | ____ mA | ____ mA | [ ] Pass | READY FOR TEST | Pending Sign-off
181 | XV-40201C | XV-40101C | 325-01-402-PD-01 | Water washing line outlet pH Adjustment tank 1 | Automatic on/off valve | 24 VDC energized | On-Off | TYP-DO-01 | TBDO | PANEL WIRING DIAGRAM.dwg | JB-401 | P1-TBDI1-31 | C1/C1S4 | C1S4-33/P1-TBDI1-31 | P1-TBDI1-31/C1S4-33 | XV-40201C_DI_1 | [ ] Pass | ____ MΩ | [ ] 24V | ____ mA | ____ mA | ____ mA | [ ] Pass | READY FOR TEST | Pending Sign-off
182 | XV-40201D | XV-40101D | 325-01-402-PD-01 | Slurry circulation pH Adjustment tank 1 | Automatic on/off valve | 24 VDC energized | On-Off | TYP-DO-01 | TBDO | PANEL WIRING DIAGRAM.dwg | JB-401 | P1-TBDI2-1 | C1/C1S5 | C1S5-1/P1-TBDI2-1 | P1-TBDI2-1/C1S5-1 | XV-40201D_DI_1 | [ ] Pass | ____ MΩ | [ ] 24V | ____ mA | ____ mA | ____ mA | [ ] Pass | READY FOR TEST | Pending Sign-off
183 | XV-40201E | XV-40101E | 325-01-402-PD-01 | Slurry pH Adjustment tank 1 transfer to pH Adjustment tank 2 | Automatic on/off valve | 24 VDC energized | On-Off | TYP-DO-01 | TBDO | PANEL WIRING DIAGRAM.dwg | JB-401 | P1-TBDI2-3 | C1/C1S5 | C1S5-3/P1-TBDI2-3 | P1-TBDI2-3/C1S5-3 | XV-40201E_DI_1 | [ ] Pass | ____ MΩ | [ ] 24V | ____ mA | ____ mA | ____ mA | [ ] Pass | READY FOR TEST | Pending Sign-off
184 | XV-40201F | XV-40101F | 325-01-402-PD-01 | Slurry feed-to spray dry tank | Automatic on/off valve | 24 VDC energized | On-Off | TYP-DO-01 | TBDO | PANEL WIRING DIAGRAM.dwg | JB-401 | P1-TBDI2-5 | C1/C1S5 | C1S5-5/P1-TBDI2-5 | P1-TBDI2-5/C1S5-5 | XV-40201F_DI_1 | [ ] Pass | ____ MΩ | [ ] 24V | ____ mA | ____ mA | ____ mA | [ ] Pass | READY FOR TEST | Pending Sign-off
185 | XV-40201G | XV-40101G | 325-01-402-PD-01 | CIP water washing pH Adjustment tank 1 | Automatic on/off valve | 24 VDC energized | On-Off | TYP-DO-01 | TBDO | PANEL WIRING DIAGRAM.dwg | JB-401 | P1-TBDI2-7 | C1/C1S5 | C1S5-7/P1-TBDI2-7 | P1-TBDI2-7/C1S5-7 | XV-40201G_DI_1 | [ ] Pass | ____ MΩ | [ ] 24V | ____ mA | ____ mA | ____ mA | [ ] Pass | READY FOR TEST | Pending Sign-off
186 | XV-40201H | XV-40101H | 325-01-402-PD-01 | CIP Hight pressure water washing pH Adjustment tank 1 | Automatic on/off valve | 24 VDC energized | On-Off | TYP-DO-01 | TBDO | PANEL WIRING DIAGRAM.dwg | JB-401 | P1-TBDI2-9 | C1/C1S5 | C1S5-9/P1-TBDI2-9 | P1-TBDI2-9/C1S5-9 | XV-40201H_DI_1 | [ ] Pass | ____ MΩ | [ ] 24V | ____ mA | ____ mA | ____ mA | [ ] Pass | READY FOR TEST | Pending Sign-off
187 | XV-40202A | XV-40102A | 325-01-402-PD-01 | Slurry feed-in pH Adjustment tank 2 | Automatic on/off valve | 24 VDC energized | On-Off | TYP-DO-01 | TBDO | PANEL WIRING DIAGRAM.dwg | JB-401 | P1-TBDI2-11 | C1/C1S5 | C1S5-11/P1-TBDI2-11 | P1-TBDI2-11/C1S5-11 | XV-40202A_DI_2 | [ ] Pass | ____ MΩ | [ ] 24V | ____ mA | ____ mA | ____ mA | [ ] Pass | READY FOR TEST | Pending Sign-off
188 | XV-40202B | XV-40102B | 325-01-402-PD-01 | Slurry feed-out pH Adjustment tank 2 | Automatic on/off valve | 24 VDC energized | On-Off | TYP-DO-01 | TBDO | PANEL WIRING DIAGRAM.dwg | JB-401 | P1-TBDI2-12 | C1/C1S5 | C1S5-12/P1-TBDI2-12 | P1-TBDI2-12/C1S5-12 | XV-40202B_DI_1 | [ ] Pass | ____ MΩ | [ ] 24V | ____ mA | ____ mA | ____ mA | [ ] Pass | READY FOR TEST | Pending Sign-off
189 | XV-40202C | XV-40102C | 325-01-402-PD-01 | Water washing line outlet pH Adjustment tank 2 | Automatic on/off valve | 24 VDC energized | On-Off | TYP-DO-01 | TBDO | PANEL WIRING DIAGRAM.dwg | JB-401 | P1-TBDI2-14 | C1/C1S5 | C1S5-14/P1-TBDI2-14 | P1-TBDI2-14/C1S5-14 | XV-40202C_DI_1 | [ ] Pass | ____ MΩ | [ ] 24V | ____ mA | ____ mA | ____ mA | [ ] Pass | READY FOR TEST | Pending Sign-off
190 | XV-40202D | XV-40102D | 325-01-402-PD-01 | Slurry circulation pH Adjustment tank 2 | Automatic on/off valve | 24 VDC energized | On-Off | TYP-DO-01 | TBDO | PANEL WIRING DIAGRAM.dwg | JB-401 | P1-TBDI2-16 | C1/C1S5 | C1S5-16/P1-TBDI2-16 | P1-TBDI2-16/C1S5-16 | XV-40202D_DI_1 | [ ] Pass | ____ MΩ | [ ] 24V | ____ mA | ____ mA | ____ mA | [ ] Pass | READY FOR TEST | Pending Sign-off
191 | XV-40202E | XV-40102E | 325-01-402-PD-01 | Slurry pH Adjustment tank 2 transfer to pH Adjustment tank 1 | Automatic on/off valve | 24 VDC energized | On-Off | TYP-DO-01 | TBDO | PANEL WIRING DIAGRAM.dwg | JB-401 | P1-TBDI2-18 | C1/C1S5 | C1S5-20/P1-TBDI2-18 | P1-TBDI2-18/C1S5-20 | XV-40202E_DI_1 | [ ] Pass | ____ MΩ | [ ] 24V | ____ mA | ____ mA | ____ mA | [ ] Pass | READY FOR TEST | Pending Sign-off
192 | XV-40202F | XV-40102F | 325-01-402-PD-01 | Slurry feed-to spray dry tank | Automatic on/off valve | 24 VDC energized | On-Off | TYP-DO-01 | TBDO | PANEL WIRING DIAGRAM.dwg | JB-401 | P1-TBDI2-21 | C1/C1S5 | C1S5-23/P1-TBDI2-21 | P1-TBDI2-21/C1S5-23 | XV-40202F_DI_1 | [ ] Pass | ____ MΩ | [ ] 24V | ____ mA | ____ mA | ____ mA | [ ] Pass | READY FOR TEST | Pending Sign-off
193 | XV-40202G | XV-40102G | 325-01-402-PD-01 | CIP water washing pH Adjustment tank 2 | Automatic on/off valve | 24 VDC energized | On-Off | TYP-DO-01 | TBDO | PANEL WIRING DIAGRAM.dwg | JB-401 | P1-TBDI2-23 | C1/C1S5 | C1S5-25/P1-TBDI2-23 | P1-TBDI2-23/C1S5-25 | XV-40202G_DI_1 | [ ] Pass | ____ MΩ | [ ] 24V | ____ mA | ____ mA | ____ mA | [ ] Pass | READY FOR TEST | Pending Sign-off
194 | XV-40202H | XV-40102H | 325-01-402-PD-01 | CIP Hight pressure water washing pH Adjustment tank 2 | Automatic on/off valve | 24 VDC energized | On-Off | TYP-DO-01 | TBDO | PANEL WIRING DIAGRAM.dwg | JB-401 | P1-TBDI2-25 | C1/C1S5 | C1S5-27/P1-TBDI2-25 | P1-TBDI2-25/C1S5-27 | XV-40202H_DI_1 | [ ] Pass | ____ MΩ | [ ] 24V | ____ mA | ____ mA | ____ mA | [ ] Pass | READY FOR TEST | Pending Sign-off
195 | XV-40203B | XV-40201B | 325-01-402-PD-02 | Slurry feed-out Spray dryer infeed tank | Automatic on/off valve | 24 VDC energized | On-Off | TYP-DO-01 | TBDO | PANEL WIRING DIAGRAM.dwg | JB-401 | P1-TBDI2-27 | C1/C1S5 | C1S5-29/P1-TBDI2-27 | P1-TBDI2-27/C1S5-29 | XV-40203B_DI_1 | [ ] Pass | ____ MΩ | [ ] 24V | ____ mA | ____ mA | ____ mA | [ ] Pass | READY FOR TEST | Pending Sign-off
196 | XV-40203C | XV-40201C | 325-01-402-PD-02 | Water washing line outlet Spray dryer infeed tank | Automatic on/off valve | 24 VDC energized | On-Off | TYP-DO-01 | TBDO | PANEL WIRING DIAGRAM.dwg | JB-401 | P1-TBDI2-29 | C1/C1S5 | C1S5-31/P1-TBDI2-29 | P1-TBDI2-29/C1S5-31 | XV-40203C_DI_1 | [ ] Pass | ____ MΩ | [ ] 24V | ____ mA | ____ mA | ____ mA | [ ] Pass | READY FOR TEST | Pending Sign-off
197 | XV-40203D | XV-40201D | 325-01-402-PD-02 | CIP water washing Spray dryer infeed tank | Automatic on/off valve | 24 VDC energized | On-Off | TYP-DO-01 | TBDO | PANEL WIRING DIAGRAM.dwg | JB-401 | P1-TBDI2-31 | C1/C1S5 | C1S5-33/P1-TBDI2-31 | P1-TBDI2-31/C1S5-33 | XV-40203D_DI_1 | [ ] Pass | ____ MΩ | [ ] 24V | ____ mA | ____ mA | ____ mA | [ ] Pass | READY FOR TEST | Pending Sign-off
198 | XV-40203E | XV-40201E | 325-01-402-PD-02 | CIP hight pressure water washing Spray dryer infeed tank | Automatic on/off valve | 24 VDC energized | On-Off | TYP-DO-01 | TBDO | PANEL WIRING DIAGRAM.dwg | JB-401 | P1-TBDI3-1 | C1/C1S6 | C1S6-1/P1-TBDI3-1 | P1-TBDI3-1/C1S6-1 | XV-40203E_DI_1 | [ ] Pass | ____ MΩ | [ ] 24V | ____ mA | ____ mA | ____ mA | [ ] Pass | READY FOR TEST | Pending Sign-off
199 | XV-40203F |  | 325-01-402-PD-02 | Jet Cooker | Automatic on/off valve | 24 VDC energized | On-Off | TYP-DO-01 | TBDO | PANEL WIRING DIAGRAM.dwg | JB-402 | P2-TBDI1-7 | C2/C2S1 | C2S1-7/P2-TBDI1-7 | P2-TBDI1-7/C2S1-7 | XV-40203F_DI_1 | [ ] Pass | ____ MΩ | [ ] 24V | ____ mA | ____ mA | ____ mA | [ ] Pass | READY FOR TEST | Pending Sign-off
200 | XV-40204B |  | 325-01-402-PD-01 | Jet Cooker | Automatic on/off valve | 24 VDC energized | On-Off | TYP-DO-01 | TBDO | PANEL WIRING DIAGRAM.dwg | JB-402 | P2-TBDI1-9 | C2/C2S1 | C2S1-9/P2-TBDI1-9 | P2-TBDI1-9/C2S1-9 | XV-40204B_DI_1 | [ ] Pass | ____ MΩ | [ ] 24V | ____ mA | ____ mA | ____ mA | [ ] Pass | READY FOR TEST | Pending Sign-off
201 | XV-40204C |  | 325-01-402-PD-01 | Jet Cooker | Automatic on/off valve | 24 VDC energized | On-Off | TYP-DO-01 | TBDO | PANEL WIRING DIAGRAM.dwg | JB-402 | P2-TBDI1-11 | C2/C2S1 | C2S1-11/P2-TBDI1-11 | P2-TBDI1-11/C2S1-11 | XV-40204C_DI_1 | [ ] Pass | ____ MΩ | [ ] 24V | ____ mA | ____ mA | ____ mA | [ ] Pass | READY FOR TEST | Pending Sign-off
202 | XV-40205A |  | 325-01-402-PD-02 | Jet Cooker | Automatic on/off valve | 24 VDC energized | On-Off | TYP-DO-01 | TBDO | PANEL WIRING DIAGRAM.dwg | JB-402 | P2-TBDI1-13 | C2/C2S1 | C2S1-13/P2-TBDI1-13 | P2-TBDI1-13/C2S1-13 | XV-40205A_DI_1 | [ ] Pass | ____ MΩ | [ ] 24V | ____ mA | ____ mA | ____ mA | [ ] Pass | READY FOR TEST | Pending Sign-off
203 | XV-40205B |  | 325-01-402-PD-02 | Jet Cooker | Automatic on/off valve | 24 VDC energized | On-Off | TYP-DO-01 | TBDO | PANEL WIRING DIAGRAM.dwg | JB-402 | P2-TBDI1-15 | C2/C2S1 | C2S1-15/P2-TBDI1-15 | P2-TBDI1-15/C2S1-15 | XV-40205B_DI_1 | [ ] Pass | ____ MΩ | [ ] 24V | ____ mA | ____ mA | ____ mA | [ ] Pass | READY FOR TEST | Pending Sign-off
204 | XV-40205C |  | 325-01-402-PD-02 | Jet Cooker | Automatic on/off valve | 24 VDC energized | On-Off | TYP-DO-01 | TBDO | PANEL WIRING DIAGRAM.dwg | JB-402 | P2-TBDI1-17 | C2/C2S1 | C2S1-19/P2-TBDI1-17 | P2-TBDI1-17/C2S1-19 | XV-40205C_DI_1 | [ ] Pass | ____ MΩ | [ ] 24V | ____ mA | ____ mA | ____ mA | [ ] Pass | READY FOR TEST | Pending Sign-off
205 | XV-40205D |  | 325-01-402-PD-02 | Jet Cooker | Automatic on/off valve | 24 VDC energized | On-Off | TYP-DO-01 | TBDO | PANEL WIRING DIAGRAM.dwg | JB-402 | P2-TBDI1-19 | C2/C2S1 | C2S1-21/P2-TBDI1-19 | P2-TBDI1-19/C2S1-21 | XV-40205D_DI_1 | [ ] Pass | ____ MΩ | [ ] 24V | ____ mA | ____ mA | ____ mA | [ ] Pass | READY FOR TEST | Pending Sign-off
206 | XV-40205F |  | 325-01-402-PD-02 | Jet Cooker | Automatic on/off valve | 24 VDC energized | On-Off | TYP-DO-01 | TBDO | PANEL WIRING DIAGRAM.dwg | JB-402 | P2-TBDI1-21 | C2/C2S1 | C2S1-23/P2-TBDI1-21 | P2-TBDI1-21/C2S1-23 | XV-40205F_DI_1 | [ ] Pass | ____ MΩ | [ ] 24V | ____ mA | ____ mA | ____ mA | [ ] Pass | READY FOR TEST | Pending Sign-off
207 | XV-40222 |  | 325-01-402-PD-02 | Jet Cooker | Automatic on/off valve | 24 VDC energized | On-Off | TYP-DO-01 | TBDO | PANEL WIRING DIAGRAM.dwg | JB-402 | P2-TBDI1-23 | C2/C2S1 | C2S1-25/P2-TBDI1-23 | P2-TBDI1-23/C2S1-25 | XV-40222_DI_1 | [ ] Pass | ____ MΩ | [ ] 24V | ____ mA | ____ mA | ____ mA | [ ] Pass | READY FOR TEST | Pending Sign-off
208 | XV-60201 | - | 325-01-602-PD-02 | Steam feed to Spray dryer | Automatic on/off valve | 24 VDC energized | On-Off | TYP-DO-01 | TBDO | PANEL WIRING DIAGRAM.dwg | JB-607 | P2-TBDI3-17 | C2/C2S3 | C2S3-19/P2-TBDI3-17 | P2-TBDI3-17/C2S3-19 | XV-60201_DI_1 | [ ] Pass | ____ MΩ | [ ] 24V | ____ mA | ____ mA | ____ mA | [ ] Pass | READY FOR TEST | Pending Sign-off
209 | XV-60251 | - | 325-01-602-PD-01 | Liquid On/Off Valve for Drain Pipe (PIPE) | Automatic on/off valve | 24 VDC energized | On-Off | TYP-DO-01 | TBDO | PANEL WIRING DIAGRAM.dwg | JB-601 | P1-TBRL2-26 | C1/C1S9 | C1S9-28/P1-TBRL2-26 | P1-TBRL2-26/C1S9-28 | XV-60251_DO_1 | [ ] Pass | ____ MΩ | [ ] 24V | ____ mA | ____ mA | ____ mA | [ ] Pass | READY FOR TEST | Pending Sign-off
210 | XV-60214 | XV-60301 | 325-01-602-PD-03 | Steam feed to Spray dryer | Automatic on/off valve | 24 VDC energized | On-Off | TYP-DO-01 | TBDO | PANEL WIRING DIAGRAM.dwg | JB-602 | P2-TBDI2-20 | C2/C2S2 | C2S2-22/P2-TBDI2-20 | P2-TBDI2-20/C2S2-22 | XV-60214_DI_1 | [ ] Pass | ____ MΩ | [ ] 24V | ____ mA | ____ mA | ____ mA | [ ] Pass | READY FOR TEST | Pending Sign-off
211 | XV-60202 | XV-61101 | 325-01-602-PD-11 | High Pressure Water On/Off Valve for Drain Pipe | Automatic on/off valve | 24 VDC energized | On-Off | TYP-DO-01 | TBDO | PANEL WIRING DIAGRAM.dwg | JB-601 | P1-TBDI4-14 | C1/C1S7 | C1S7-14/P1-TBDI4-14 | P1-TBDI4-14/C1S7-14 | XV-60202_DI_1 | [ ] Pass | ____ MΩ | [ ] 24V | ____ mA | ____ mA | ____ mA | [ ] Pass | READY FOR TEST | Pending Sign-off
212 | XV-61301 | HV-61301 | 325-01-613-PD-01 | Product feed-out Packing silo | Automatic on/off valve | 24 VDC energized | On-Off | TYP-DO-01 | TBDO | PANEL WIRING DIAGRAM.dwg | JB-618 | P3-TBDI3-11 | C3/C3S3 | C3S3-11/P3-TBDI3-11 | P3-TBDI3-11/C3S3-11 | XV-61301_DI_1 | [ ] Pass | ____ MΩ | [ ] 24V | ____ mA | ____ mA | ____ mA | [ ] Pass | READY FOR TEST | Pending Sign-off
213 | XV-61302 | - | 325-01-613-PD-02 | Dust collector feed vent | Automatic on/off valve | 24 VDC energized | On-Off | TYP-DO-01 | TBDO | PANEL WIRING DIAGRAM.dwg | JB-612 | P3-TBDI2-14 | C3/C3S2 | C3S2-14/P3-TBDI2-14 | P3-TBDI2-14/C3S2-14 | XV-61302_DI_1 | [ ] Pass | ____ MΩ | [ ] 24V | ____ mA | ____ mA | ____ mA | [ ] Pass | READY FOR TEST | Pending Sign-off
214 | XV-61303 | - | 325-01-613-PD-02 | Dust collector feed from packer | Automatic on/off valve | 24 VDC energized | On-Off | TYP-DO-01 | TBDO | PANEL WIRING DIAGRAM.dwg | JB-612 | P3-TBDI2-16 | C3/C3S2 | C3S2-16/P3-TBDI2-16 | P3-TBDI2-16/C3S2-16 | XV-61303_DI_1 | [ ] Pass | ____ MΩ | [ ] 24V | ____ mA | ____ mA | ____ mA | [ ] Pass | READY FOR TEST | Pending Sign-off
215 | DV-61301 |  | 325-01-613-PD-01 | On/Off Valve for Diverter Valve DV-61301 | Automatic on/off valve | 24 VDC energized | On-Off | TYP-DO-01 | TBDO | PANEL WIRING DIAGRAM.dwg | JB-618 | P3-TBDI3-1 | C3/C3S3 | C3S3-1/P3-TBDI3-1 | P3-TBDI3-1/C3S3-1 | DV-61301_DI_1 | [ ] Pass | ____ MΩ | [ ] 24V | ____ mA | ____ mA | ____ mA | [ ] Pass | READY FOR TEST | Pending Sign-off
216 | DV-61302 |  | 325-01-613-PD-01 | On/Off Valve for Diverter Valve DV-61302 | Automatic on/off valve | 24 VDC energized | On-Off | TYP-DO-01 | TBDO | PANEL WIRING DIAGRAM.dwg | JB-618 | P3-TBDI3-3 | C3/C3S3 | C3S3-3/P3-TBDI3-3 | P3-TBDI3-3/C3S3-3 | DV-61302_DI_1 | [ ] Pass | ____ MΩ | [ ] 24V | ____ mA | ____ mA | ____ mA | [ ] Pass | READY FOR TEST | Pending Sign-off
217 | ZS-60201A | - | 325-01-602-PD-04 | Limit Switch for CHAM-21 (Spray Chamber) | Limit Switch | Dry Contact | On-Off | TYP-DI-01 | TBDI | PANEL WIRING DIAGRAM.dwg | IS-JB-608 | P4-TBDI1-17 | C4/C4S1 | C4S1-19/P4-TBDI1-17 | P4-TBDI1-17/C4S1-19 | ZS-60201A_DI_1 | [ ] Pass | ____ MΩ | [ ] 24V | ____ mA | ____ mA | ____ mA | [ ] Pass | READY FOR TEST | Pending Sign-off
218 | ZS-60201B | - | 325-01-602-PD-04 | Limit Switch for CHAM-21 (Spray Chamber) | Limit Switch | Dry Contact | On-Off | TYP-DI-01 | TBDI | PANEL WIRING DIAGRAM.dwg | IS-JB-608 | P4-TBDI1-18 | C4/C4S1 | C4S1-20/P4-TBDI1-18 | P4-TBDI1-18/C4S1-20 | ZS-60201B_DI_1 | [ ] Pass | ____ MΩ | [ ] 24V | ____ mA | ____ mA | ____ mA | [ ] Pass | READY FOR TEST | Pending Sign-off
219 | ZS-60201C | - | 325-01-602-PD-04 | Limit Switch for CHAM-21 (Spray Chamber) | Limit Switch | Dry Contact | On-Off | TYP-DI-01 | TBDI | PANEL WIRING DIAGRAM.dwg | IS-JB-603 | P4-TBDI1-9 | C4/C4S1 | C4S1-9/P4-TBDI1-9 | P4-TBDI1-9/C4S1-9 | ZS-60201C_DI_1 | [ ] Pass | ____ MΩ | [ ] 24V | ____ mA | ____ mA | ____ mA | [ ] Pass | READY FOR TEST | Pending Sign-off
220 | ZS-60201D | - | 325-01-602-PD-04 | Limit Switch for CHAM-21 (Spray Chamber) | Limit Switch | Dry Contact | On-Off | TYP-DI-01 | TBDI | PANEL WIRING DIAGRAM.dwg | IS-JB-603 | P4-TBDI1-10 | C4/C4S1 | C4S1-10/P4-TBDI1-10 | P4-TBDI1-10/C4S1-10 | ZS-60201D_DI_1 | [ ] Pass | ____ MΩ | [ ] 24V | ____ mA | ____ mA | ____ mA | [ ] Pass | READY FOR TEST | Pending Sign-off
221 | ZS-60201E | - | 325-01-602-PD-04 | Limit Switch for CHAM-21 (Spray Chamber) | Limit Switch | Dry Contact | On-Off | TYP-DI-01 | TBDI | PANEL WIRING DIAGRAM.dwg | IS-JB-603 | P4-TBDI1-11 | C4/C4S1 | C4S1-11/P4-TBDI1-11 | P4-TBDI1-11/C4S1-11 | ZS-60201E_DI_1 | [ ] Pass | ____ MΩ | [ ] 24V | ____ mA | ____ mA | ____ mA | [ ] Pass | READY FOR TEST | Pending Sign-off
222 | ZS-60229 |  | 325-01-602-PD-04 | Limit Switch for CY-60230 (Door Service) | Limit Switch | Switch PNP | On-Off | TYP-DI-01 | TBDI | PANEL WIRING DIAGRAM.dwg | IS-JB-603 | P4-TBDI1-12 | C4/C4S1 | C4S1-12/P4-TBDI1-12 | P4-TBDI1-12/C4S1-12 | ZS-60229_DI_1 | [ ] Pass | ____ MΩ | [ ] 24V | ____ mA | ____ mA | ____ mA | [ ] Pass | READY FOR TEST | Pending Sign-off
223 | ZS-60230 |  | 325-01-602-PD-04 | Limit Switch for CY-60231 (Door Service) | Limit Switch | Switch PNP | On-Off | TYP-DI-01 | TBDI | PANEL WIRING DIAGRAM.dwg | IS-JB-603 | P4-TBDI1-13 | C4/C4S1 | C4S1-13/P4-TBDI1-13 | P4-TBDI1-13/C4S1-13 | ZS-60230_DI_1 | [ ] Pass | ____ MΩ | [ ] 24V | ____ mA | ____ mA | ____ mA | [ ] Pass | READY FOR TEST | Pending Sign-off
224 | ZS-60231A | - | 325-01-602-PD-05 | Gas Limit Switch for DTEX-21 (Bag House Face Spectacle Inserted) | Limit Switch | Dry Contact | On-Off | TYP-DI-01 | TBDI | PANEL WIRING DIAGRAM.dwg | IS-JB-603 | P4-TBDI1-14 | C4/C4S1 | C4S1-14/P4-TBDI1-14 | P4-TBDI1-14/C4S1-14 | ZS-60231A_DI_1 | [ ] Pass | ____ MΩ | [ ] 24V | ____ mA | ____ mA | ____ mA | [ ] Pass | READY FOR TEST | Pending Sign-off
225 | ZS-60231B | - | 325-01-602-PD-05 | Gas Limit Switch for DTEX-21 (Bag House Face Blind Inserted) | Limit Switch | Dry Contact | On-Off | TYP-DI-01 | TBDI | PANEL WIRING DIAGRAM.dwg | IS-JB-603 | P4-TBDI1-15 | C4/C4S1 | C4S1-15/P4-TBDI1-15 | P4-TBDI1-15/C4S1-15 | ZS-60231B_DI_1 | [ ] Pass | ____ MΩ | [ ] 24V | ____ mA | ____ mA | ____ mA | [ ] Pass | READY FOR TEST | Pending Sign-off
226 | ZS-60231C | - | 325-01-602-PD-05 | Gas Limit Switch for DTEX-23 (Bag House By-Pass Inlet Spool Inserted) | Limit Switch | Switch PNP | On-Off | TYP-DI-01 | TBDI | PANEL WIRING DIAGRAM.dwg | IS-JB-608 | P4-TBDI1-19 | C4/C4S1 | C4S1-21/P4-TBDI1-19 | P4-TBDI1-19/C4S1-21 | ZS-60231C_DI_1 | [ ] Pass | ____ MΩ | [ ] 24V | ____ mA | ____ mA | ____ mA | [ ] Pass | READY FOR TEST | Pending Sign-off
227 | ZS-60231D | - | 325-01-602-PD-05 | Gas Limit Switch for DTEX-23 (Bag House By-Pass Inlet Blind Inserted) | Limit Switch | Switch PNP | On-Off | TYP-DI-01 | TBDI | PANEL WIRING DIAGRAM.dwg | IS-JB-608 | P4-TBDI1-20 | C4/C4S1 | C4S1-22/P4-TBDI1-20 | P4-TBDI1-20/C4S1-22 | ZS-60231D_DI_1 | [ ] Pass | ____ MΩ | [ ] 24V | ____ mA | ____ mA | ____ mA | [ ] Pass | READY FOR TEST | Pending Sign-off
228 | ZS-60231E | - | 325-01-602-PD-05 | Gas Limit Switch for DTEX-23 (Bag House By-Pass Outlet Spool Inserted) | Limit Switch | Switch PNP | On-Off | TYP-DI-01 | TBDI | PANEL WIRING DIAGRAM.dwg | IS-JB-608 | P4-TBDI1-21 | C4/C4S1 | C4S1-23/P4-TBDI1-21 | P4-TBDI1-21/C4S1-23 | ZS-60231E_DI_1 | [ ] Pass | ____ MΩ | [ ] 24V | ____ mA | ____ mA | ____ mA | [ ] Pass | READY FOR TEST | Pending Sign-off
229 | ZS-60231F | - | 325-01-602-PD-05 | Gas Limit Switch for DTEX-23 (Bag House By-Pass Outlet Blind Inserted) | Limit Switch | Switch PNP | On-Off | TYP-DI-01 | TBDI | PANEL WIRING DIAGRAM.dwg | IS-JB-608 | P4-TBDI1-22 | C4/C4S1 | C4S1-24/P4-TBDI1-22 | P4-TBDI1-22/C4S1-24 | ZS-60231F_DI_1 | [ ] Pass | ____ MΩ | [ ] 24V | ____ mA | ____ mA | ____ mA | [ ] Pass | READY FOR TEST | Pending Sign-off
230 | ZS-60240 |  | 325-01-602-PD-05 | Limit Switch for FA-60240 (Door Service) | Limit Switch | Switch PNP | On-Off | TYP-DI-01 | TBDI | PANEL WIRING DIAGRAM.dwg | IS-JB-608 | P4-TBDI1-23 | C4/C4S1 | C4S1-25/P4-TBDI1-23 | P4-TBDI1-23/C4S1-25 | ZS-60240_DI_1 | [ ] Pass | ____ MΩ | [ ] 24V | ____ mA | ____ mA | ____ mA | [ ] Pass | READY FOR TEST | Pending Sign-off
231 | ZS-61310 | - | 325-01-613-PD-01 | Position Magnet Door | Limit Switch | Dry Contact | On-Off | TYP-DI-01 | TBDI | PANEL WIRING DIAGRAM.dwg | IS-JB-618 | P4-TBDI3-12 | C4/C4S3 | C4S3-12/P4-TBDI3-12 | P4-TBDI3-12/C4S3-12 | ZS-61310_DI_1 | [ ] Pass | ____ MΩ | [ ] 24V | ____ mA | ____ mA | ____ mA | [ ] Pass | READY FOR TEST | Pending Sign-off
232 | ZS-61311 | - | 325-01-613-PD-01 | Position Magnet Door | Limit Switch | Dry Contact | On-Off | TYP-DI-01 | TBDI | PANEL WIRING DIAGRAM.dwg | IS-JB-618 | P4-TBDI3-13 | C4/C4S3 | C4S3-13/P4-TBDI3-13 | P4-TBDI3-13/C4S3-13 | ZS-61311_DI_1 | [ ] Pass | ____ MΩ | [ ] 24V | ____ mA | ____ mA | ____ mA | [ ] Pass | READY FOR TEST | Pending Sign-off
233 | ZS-61312 | - | 325-01-613-PD-01 | Position Magnet Door | Limit Switch | Dry Contact | On-Off | TYP-DI-01 | TBDI | PANEL WIRING DIAGRAM.dwg | IS-JB-612 | P4-TBDI2-14 | C4/C4S2 | C4S2-14/P4-TBDI2-14 | P4-TBDI2-14/C4S2-14 | ZS-61312_DI_1 | [ ] Pass | ____ MΩ | [ ] 24V | ____ mA | ____ mA | ____ mA | [ ] Pass | READY FOR TEST | Pending Sign-off
234 | ZS-61313 | - | 325-01-613-PD-01 | Position Magnet Door | Limit Switch | Dry Contact | On-Off | TYP-DI-01 | TBDI | PANEL WIRING DIAGRAM.dwg | IS-JB-612 | P4-TBDI2-15 | C4/C4S2 | C4S2-15/P4-TBDI2-15 | P4-TBDI2-15/C4S2-15 | ZS-61313_DI_1 | [ ] Pass | ____ MΩ | [ ] 24V | ____ mA | ____ mA | ____ mA | [ ] Pass | READY FOR TEST | Pending Sign-off
235 |  | - | - | Lototo-01 | Position switch | Dry Contact | On-Off | TYP-DI-01 | TBDI | PANEL WIRING DIAGRAM.dwg | PLC | - | - | - | - | - | [ ] Pass | ____ MΩ | [ ] 24V | ____ mA | ____ mA | ____ mA | [ ] Pass | RESERVE ALLOC | Pending Sign-off
236 |  | - | - | Lototo-02 | Position switch | Dry Contact | On-Off | TYP-DI-01 | TBDI | PANEL WIRING DIAGRAM.dwg | PLC | - | - | - | - | - | [ ] Pass | ____ MΩ | [ ] 24V | ____ mA | ____ mA | ____ mA | [ ] Pass | RESERVE ALLOC | Pending Sign-off
237 |  | - | - | Lototo-03 | Position switch | Dry Contact | On-Off | TYP-DI-01 | TBDI | PANEL WIRING DIAGRAM.dwg | PLC | - | - | - | - | - | [ ] Pass | ____ MΩ | [ ] 24V | ____ mA | ____ mA | ____ mA | [ ] Pass | RESERVE ALLOC | Pending Sign-off
238 |  | - | - | Lototo-04 | Position switch | Dry Contact | On-Off | TYP-DI-01 | TBDI | PANEL WIRING DIAGRAM.dwg | PLC | - | - | - | - | - | [ ] Pass | ____ MΩ | [ ] 24V | ____ mA | ____ mA | ____ mA | [ ] Pass | RESERVE ALLOC | Pending Sign-off
239 |  | - | - | Lototo-05 | Position switch | Dry Contact | On-Off | TYP-DI-01 | TBDI | PANEL WIRING DIAGRAM.dwg | PLC | - | - | - | - | - | [ ] Pass | ____ MΩ | [ ] 24V | ____ mA | ____ mA | ____ mA | [ ] Pass | RESERVE ALLOC | Pending Sign-off
240 |  | - | - | Lototo-06 | Position switch | Dry Contact | On-Off | TYP-DI-01 | TBDI | PANEL WIRING DIAGRAM.dwg | PLC | - | - | - | - | - | [ ] Pass | ____ MΩ | [ ] 24V | ____ mA | ____ mA | ____ mA | [ ] Pass | RESERVE ALLOC | Pending Sign-off
241 |  | - | - | Lototo-07 | Position switch | Dry Contact | On-Off | TYP-DI-01 | TBDI | PANEL WIRING DIAGRAM.dwg | PLC | - | - | - | - | - | [ ] Pass | ____ MΩ | [ ] 24V | ____ mA | ____ mA | ____ mA | [ ] Pass | RESERVE ALLOC | Pending Sign-off
242 |  | - | - | Lototo-08 | Position switch | Dry Contact | On-Off | TYP-DI-01 | TBDI | PANEL WIRING DIAGRAM.dwg | PLC | - | - | - | - | - | [ ] Pass | ____ MΩ | [ ] 24V | ____ mA | ____ mA | ____ mA | [ ] Pass | RESERVE ALLOC | Pending Sign-off
243 |  | - | - | Lototo-09 | Position switch | Dry Contact | On-Off | TYP-DI-01 | TBDI | PANEL WIRING DIAGRAM.dwg | PLC | - | - | - | - | - | [ ] Pass | ____ MΩ | [ ] 24V | ____ mA | ____ mA | ____ mA | [ ] Pass | RESERVE ALLOC | Pending Sign-off
244 |  | - | - | Lototo-10 | Position switch | Dry Contact | On-Off | TYP-DI-01 | TBDI | PANEL WIRING DIAGRAM.dwg | PLC | - | - | - | - | - | [ ] Pass | ____ MΩ | [ ] 24V | ____ mA | ____ mA | ____ mA | [ ] Pass | RESERVE ALLOC | Pending Sign-off
245 |  | - | - | Lototo-11 | Position switch | Dry Contact | On-Off | TYP-DI-01 | TBDI | PANEL WIRING DIAGRAM.dwg | PLC | - | - | - | - | - | [ ] Pass | ____ MΩ | [ ] 24V | ____ mA | ____ mA | ____ mA | [ ] Pass | RESERVE ALLOC | Pending Sign-off
246 |  | - | - | Lototo-12 | Position switch | Dry Contact | On-Off | TYP-DI-01 | TBDI | PANEL WIRING DIAGRAM.dwg | PLC | - | - | - | - | - | [ ] Pass | ____ MΩ | [ ] 24V | ____ mA | ____ mA | ____ mA | [ ] Pass | RESERVE ALLOC | Pending Sign-off
246 | ES-60201 |  | - | Emergency stop activated @ Spray Nozzle 7th Floor | E-Stop Swtich | Dry Contact | On-Off | TYP-DI-01 | TBDI | PANEL WIRING DIAGRAM.dwg | PLC | - | - | - | - | - | [ ] Pass | ____ MΩ | [ ] 24V | ____ mA | ____ mA | ____ mA | [ ] Pass | RESERVE ALLOC | Pending Sign-off
246 | ES-60202 |  | - | Emergency stop activated @ Sight glass 6th Floor | E-Stop Swtich | Dry Contact | On-Off | TYP-DI-01 | TBDI | PANEL WIRING DIAGRAM.dwg | JB-601 | P1-TBDI3-17 | C1/C1S6 | C1S6-19/P1-TBDI3-17 | P1-TBDI3-17/C1S6-19 | ES-60202_DI_1 | [ ] Pass | ____ MΩ | [ ] 24V | ____ mA | ____ mA | ____ mA | [ ] Pass | READY FOR TEST | Pending Sign-off
246 | ES-60203 |  | - | Emergency stop activated @ Control Room | E-Stop Swtich | Dry Contact | On-Off | TYP-DI-01 | TBDI | PANEL WIRING DIAGRAM.dwg | PLC | - | - | - | - | - | [ ] Pass | ____ MΩ | [ ] 24V | ____ mA | ____ mA | ____ mA | [ ] Pass | RESERVE ALLOC | Pending Sign-off
246 | ES-61301 |  | - | Emergency stop activated @ SC-61301,SC-61302 | E-Stop Swtich | Dry Contact | On-Off | TYP-DI-01 | TBDI | PANEL WIRING DIAGRAM.dwg | PLC | - | - | - | - | - | [ ] Pass | ____ MΩ | [ ] 24V | ____ mA | ____ mA | ____ mA | [ ] Pass | RESERVE ALLOC | Pending Sign-off
247 | DEDERT SUPPLY EQUIPMENT | - | - |  |  | - | - | TYP-MECH | N/A | Standard Mechanical Typical | Local Dial | - | - | - | - | - | [ ] Pass | ____ MΩ | [ ] 24V | ____ mA | ____ mA | ____ mA | [ ] Pass | MECHANICAL | Pending Sign-off
248 | FT-60207 | FT-60701 | 325-01-602-PD-07 | Instr. Air Flow Transmitter for Camera #4 (ACAM-21) | Flow Transmitter | 4 - 20 mA | - | TYP-AI-02 | TBAI | LOOP DIAGRAM WRING.dwg | JB-607 | P3-TBAI2-1(B) | C3/C3S7 | C3S7-1/P3-TBAI2-1(B) | P3-TBAI2-1(B)/C3S7-1 | FT-60207_AI_1 | [ ] Pass | ____ MΩ | [ ] 24V | ____ mA | ____ mA | ____ mA | [ ] Pass | READY FOR TEST | Pending Sign-off
249 | PT-60207 | PT-60701 | 325-01-602-PD-07 | Instr. Air Pressure Transmitter for Camera #4 (ACAM-21) | Pressure Transmitter | 4 - 20 mA | - | TYP-AI-01 | TBAI | LOOP DIAGRAM WRING.dwg | JB-607 | P3-TBAI3-4(B) | C3/C3S8 | C3S8-7/P3-TBAI3-4(B) | P3-TBAI3-4(B)/C3S8-7 | PT-60207_AI_1 | [ ] Pass | ____ MΩ | [ ] 24V | ____ mA | ____ mA | ____ mA | [ ] Pass | READY FOR TEST | Pending Sign-off
250 | XV-60240D | SV-60240D | 325-01-602-PD-05 | PA On/Off Valve for Bag House Tank Valve (BGHS-21) | On/Off Valve | 24 VDC energized,Dry Contact | On-Off | TYP-DO-01 | TBDO | PANEL WIRING DIAGRAM.dwg | JB-601 | P1-TBDI4-18 | C1/C1S7 | C1S7-20/P1-TBDI4-18 | P1-TBDI4-18/C1S7-20 | XV-60240D_DI_1 | [ ] Pass | ____ MΩ | [ ] 24V | ____ mA | ____ mA | ____ mA | [ ] Pass | READY FOR TEST | Pending Sign-off
251 | SV-60207 | SV-60701 | 325-01-602-PD-07 | Instr. Air On/Off Valve for Camera #4 (ACAM-21) | On/Off Valve | 24 VDC energized | On-Off | TYP-DO-01 | TBDO | PANEL WIRING DIAGRAM.dwg | JB-607 | P2-TBDI3-9 | C2/C2S3 | C2S3-9/P2-TBDI3-9 | P2-TBDI3-9/C2S3-9 | SV-60207_DI_1 | [ ] Pass | ____ MΩ | [ ] 24V | ____ mA | ____ mA | ____ mA | [ ] Pass | READY FOR TEST | Pending Sign-off
252 | SV-60201 | - | 325-01-602-PD-08 | PA On/Off Valve for Cyclone-21 Rotary Valve (RVAL-21) | On/Off Valve | 24 VDC energized | On-Off | TYP-DO-01 | TBDO | PANEL WIRING DIAGRAM.dwg | JB-601 | P1-TBDI3-20 | C1/C1S6 | C1S6-22/P1-TBDI3-20 | P1-TBDI3-20/C1S6-22 | SV-60201_DI_1 | [ ] Pass | ____ MΩ | [ ] 24V | ____ mA | ____ mA | ____ mA | [ ] Pass | READY FOR TEST | Pending Sign-off
 | SSL-60201 |  | 325-01-602-PD-08 | Speed Switch Low for Bin Cyclone Rotary Valve (RVAL-21) | Low Speed Switch | Switch PNP | On-Off | TYP-DI-01 | TBDI | PANEL WIRING DIAGRAM.dwg | PLC | - | - | - | - | - | [ ] Pass | ____ MΩ | [ ] 24V | ____ mA | ____ mA | ____ mA | [ ] Pass | RESERVE ALLOC | Pending Sign-off
 | ZS-60201 |  | 325-01-602-PD-08 | Position - Rotary Valve (RVAL-21/ RV-60201) Casing Closed | Position switch | Dry Contact | On-Off | TYP-DI-01 | TBDI | PANEL WIRING DIAGRAM.dwg | PLC | - | - | - | - | - | [ ] Pass | ____ MΩ | [ ] 24V | ____ mA | ____ mA | ____ mA | [ ] Pass | RESERVE ALLOC | Pending Sign-off
253 | SV-60202 | - | 325-01-602-PD-08 | PA On/Off Valve for Cyclone-22 Rotary Valve (RVAL-22) | On/Off Valve | 24 VDC energized | On-Off | TYP-DO-01 | TBDO | PANEL WIRING DIAGRAM.dwg | JB-601 | P1-TBDI3-22 | C1/C1S6 | C1S6-24/P1-TBDI3-22 | P1-TBDI3-22/C1S6-24 | SV-60202_DI_1 | [ ] Pass | ____ MΩ | [ ] 24V | ____ mA | ____ mA | ____ mA | [ ] Pass | READY FOR TEST | Pending Sign-off
 | SSL-60202 |  | 325-01-602-PD-08 | Speed Switch Low for Bin Cyclone Rotary Valve (RVAL-22) | Low Speed Switch | Switch PNP | On-Off | TYP-DI-01 | TBDI | PANEL WIRING DIAGRAM.dwg | PLC | - | - | - | - | - | [ ] Pass | ____ MΩ | [ ] 24V | ____ mA | ____ mA | ____ mA | [ ] Pass | RESERVE ALLOC | Pending Sign-off
 | ZS-60202 |  | 325-01-602-PD-08 | Position - Rotary Valve (RVAL-22/ RV-60202) Casing Closed | Position switch | Dry Contact | On-Off | TYP-DI-01 | TBDI | PANEL WIRING DIAGRAM.dwg | PLC | - | - | - | - | - | [ ] Pass | ____ MΩ | [ ] 24V | ____ mA | ____ mA | ____ mA | [ ] Pass | RESERVE ALLOC | Pending Sign-off
254 | SV-60203 | - | 325-01-602-PD-08 | PA On/Off Valve for Bag House Rotary Valve (RVAL-23) | On/Off Valve | 24 VDC energized | On-Off | TYP-DO-01 | TBDO | PANEL WIRING DIAGRAM.dwg | JB-601 | P1-TBDI3-24 | C1/C1S6 | C1S6-26/P1-TBDI3-24 | P1-TBDI3-24/C1S6-26 | SV-60203_DI_1 | [ ] Pass | ____ MΩ | [ ] 24V | ____ mA | ____ mA | ____ mA | [ ] Pass | READY FOR TEST | Pending Sign-off
 | SSL-60203 |  | 325-01-602-PD-08 | Speed Switch Low for Bin Cyclone Rotary Valve (RVAL-23) | Low Speed Switch | Switch PNP | On-Off | TYP-DI-01 | TBDI | PANEL WIRING DIAGRAM.dwg | PLC | - | - | - | - | - | [ ] Pass | ____ MΩ | [ ] 24V | ____ mA | ____ mA | ____ mA | [ ] Pass | RESERVE ALLOC | Pending Sign-off
 | ZS-60203 |  | 325-01-602-PD-08 | Position - Rotary Valve (RVAL-23/ RV-60203) Casing Closed | Position switch | Dry Contact | On-Off | TYP-DI-01 | TBDI | PANEL WIRING DIAGRAM.dwg | PLC | - | - | - | - | - | [ ] Pass | ____ MΩ | [ ] 24V | ____ mA | ____ mA | ____ mA | [ ] Pass | RESERVE ALLOC | Pending Sign-off
255 | SV-61304 | - | 325-01-613-PD-01 | PA On/Off Valve for Conveying Cooler Cyclone-31 Rotary Valve (RV-61304) | On/Off Valve | 24 VDC energized | On-Off | TYP-DO-01 | TBDO | PANEL WIRING DIAGRAM.dwg | JB-618 | P3-TBDI3-9 | C3/C3S3 | C3S3-9/P3-TBDI3-9 | P3-TBDI3-9/C3S3-9 | SV-61304_DI_1 | [ ] Pass | ____ MΩ | [ ] 24V | ____ mA | ____ mA | ____ mA | [ ] Pass | READY FOR TEST | Pending Sign-off
 | SSL-61304 |  | 325-01-613-PD-01 | Speed Switch Low for Bin Cyclone Rotary Valve (RVAL-31) | Low Speed Switch | Switch PNP | On-Off | TYP-DI-01 | TBDI | PANEL WIRING DIAGRAM.dwg | PLC | - | - | - | - | - | [ ] Pass | ____ MΩ | [ ] 24V | ____ mA | ____ mA | ____ mA | [ ] Pass | RESERVE ALLOC | Pending Sign-off
 | ZS-61304 |  | 325-01-613-PD-01 | Position - Rotary Valve (RVAL-31/ RV-61304) Casing Closed | Position switch | Dry Contact | On-Off | TYP-DI-01 | TBDI | PANEL WIRING DIAGRAM.dwg | PLC | - | - | - | - | - | [ ] Pass | ____ MΩ | [ ] 24V | ____ mA | ____ mA | ____ mA | [ ] Pass | RESERVE ALLOC | Pending Sign-off
256 | TT-60207 | TT-60701 | 325-01-602-PD-07 | Instr. Air Temperature Transmitter for Air Manifold - Camera #4 (ACAM-21) | Temperature Transmitter | 4 - 20 mA | - | TYP-AI-01 | TBAI | LOOP DIAGRAM WRING.dwg | JB-607 | P3-TBAI3-10(B) | C3/C3S8 | C3S8-21/P3-TBAI3-10(B) | P3-TBAI3-10(B)/C3S8-21 | TT-60207_AI_1 | [ ] Pass | ____ MΩ | [ ] 24V | ____ mA | ____ mA | ____ mA | [ ] Pass | READY FOR TEST | Pending Sign-off
257 | XV-60261FA | - | 325-01-602-PD-02 | Feed Slurry On/Off Valve for Nozzle #1 (ATVM-11A) | On/Off Valve | 24 VDC energized,Dry Contact | On-Off | TYP-DO-01 | TBDO | PANEL WIRING DIAGRAM.dwg | JB-607 | P2-TBDI3-25 | C2/C2S3 | C2S3-27/P2-TBDI3-25 | P2-TBDI3-25/C2S3-27 | XV-60261FA_DI_1 | [ ] Pass | ____ MΩ | [ ] 24V | ____ mA | ____ mA | ____ mA | [ ] Pass | READY FOR TEST | Pending Sign-off
258 | XV-60261FB | - | 325-01-602-PD-02 | Feed Slurry On/Off Valve for Nozzle #2 (ATVM-11A) | On/Off Valve | 24 VDC energized,Dry Contact | On-Off | TYP-DO-01 | TBDO | PANEL WIRING DIAGRAM.dwg | JB-607 | P2-TBDI3-29 | C2/C2S3 | C2S3-31/P2-TBDI3-29 | P2-TBDI3-29/C2S3-31 | XV-60261FB_DI_1 | [ ] Pass | ____ MΩ | [ ] 24V | ____ mA | ____ mA | ____ mA | [ ] Pass | READY FOR TEST | Pending Sign-off
259 | XV-60261FC | - | 325-01-602-PD-02 | Feed Slurry On/Off Valve for Nozzle #3 (ATVM-11A) | On/Off Valve | 24 VDC energized,Dry Contact | On-Off | TYP-DO-01 | TBDO | PANEL WIRING DIAGRAM.dwg | JB-607 | P2-TBDI4-1 | C2/C2S4 | C2S4-1/P2-TBDI4-1 | P2-TBDI4-1/C2S4-1 | XV-60261FC_DI_1 | [ ] Pass | ____ MΩ | [ ] 24V | ____ mA | ____ mA | ____ mA | [ ] Pass | READY FOR TEST | Pending Sign-off
260 | XV-60261FD | - | 325-01-602-PD-02 | Feed Slurry On/Off Valve for Nozzle #4 (ATVM-11A) | On/Off Valve | 24 VDC energized,Dry Contact | On-Off | TYP-DO-01 | TBDO | PANEL WIRING DIAGRAM.dwg | JB-607 | P2-TBDI4-5 | C2/C2S4 | C2S4-5/P2-TBDI4-5 | P2-TBDI4-5/C2S4-5 | XV-60261FD_DI_1 | [ ] Pass | ____ MΩ | [ ] 24V | ____ mA | ____ mA | ____ mA | [ ] Pass | READY FOR TEST | Pending Sign-off
261 | XV-60261SA | - | 325-01-602-PD-02 | Steam On/Off Valve for Nozzle #1 (ATVM-11A) | On/Off Valve | 24 VDC energized,Dry Contact | On-Off | TYP-DO-01 | TBDO | PANEL WIRING DIAGRAM.dwg | JB-607 | P2-TBDI4-9 | C2/C2S4 | C2S4-9/P2-TBDI4-9 | P2-TBDI4-9/C2S4-9 | XV-60261SA_DI_1 | [ ] Pass | ____ MΩ | [ ] 24V | ____ mA | ____ mA | ____ mA | [ ] Pass | READY FOR TEST | Pending Sign-off
262 | XV-60261SB | - | 325-01-602-PD-02 | Steam On/Off Valve for Nozzle #2 (ATVM-11A) | On/Off Valve | 24 VDC energized,Dry Contact | On-Off | TYP-DO-01 | TBDO | PANEL WIRING DIAGRAM.dwg | JB-607 | P2-TBDI4-11 | C2/C2S4 | C2S4-11/P2-TBDI4-11 | P2-TBDI4-11/C2S4-11 | XV-60261SB_DI_1 | [ ] Pass | ____ MΩ | [ ] 24V | ____ mA | ____ mA | ____ mA | [ ] Pass | READY FOR TEST | Pending Sign-off
263 | XV-60261SC | - | 325-01-602-PD-02 | Steam On/Off Valve for Nozzle #3 (ATVM-11A) | On/Off Valve | 24 VDC energized,Dry Contact | On-Off | TYP-DO-01 | TBDO | PANEL WIRING DIAGRAM.dwg | JB-607 | P2-TBDI4-13 | C2/C2S4 | C2S4-13/P2-TBDI4-13 | P2-TBDI4-13/C2S4-13 | XV-60261SC_DI_1 | [ ] Pass | ____ MΩ | [ ] 24V | ____ mA | ____ mA | ____ mA | [ ] Pass | READY FOR TEST | Pending Sign-off
264 | XV-60261SD | - | 325-01-602-PD-02 | Steam On/Off Valve for Nozzle #4 (ATVM-11A) | On/Off Valve | 24 VDC energized,Dry Contact | On-Off | TYP-DO-01 | TBDO | PANEL WIRING DIAGRAM.dwg | JB-607 | P2-TBDI4-15 | C2/C2S4 | C2S4-15/P2-TBDI4-15 | P2-TBDI4-15/C2S4-15 | XV-60261SD_DI_1 | [ ] Pass | ____ MΩ | [ ] 24V | ____ mA | ____ mA | ____ mA | [ ] Pass | READY FOR TEST | Pending Sign-off
265 | XV-60262FE | - | 325-01-602-PD-02 | Feed Slurry On/Off Valve for Nozzle #5 (ATVM-11B) | On/Off Valve | 24 VDC energized,Dry Contact | On-Off | TYP-DO-01 | TBDO | PANEL WIRING DIAGRAM.dwg | JB-607 | P2-TBDI4-19 | C2/C2S4 | C2S4-21/P2-TBDI4-19 | P2-TBDI4-19/C2S4-21 | XV-60262FE_DI_1 | [ ] Pass | ____ MΩ | [ ] 24V | ____ mA | ____ mA | ____ mA | [ ] Pass | READY FOR TEST | Pending Sign-off
266 | XV-60262FF | - | 325-01-602-PD-02 | Feed Slurry On/Off Valve for Nozzle #6 (ATVM-11B) | On/Off Valve | 24 VDC energized,Dry Contact | On-Off | TYP-DO-01 | TBDO | PANEL WIRING DIAGRAM.dwg | JB-607 | P2-TBDI4-21 | C2/C2S4 | C2S4-23/P2-TBDI4-21 | P2-TBDI4-21/C2S4-23 | XV-60262FF_DI_1 | [ ] Pass | ____ MΩ | [ ] 24V | ____ mA | ____ mA | ____ mA | [ ] Pass | READY FOR TEST | Pending Sign-off
267 | XV-60262FG | - | 325-01-602-PD-02 | Feed Slurry On/Off Valve for Nozzle #7 (ATVM-11B) | On/Off Valve | 24 VDC energized,Dry Contact | On-Off | TYP-DO-01 | TBDO | PANEL WIRING DIAGRAM.dwg | JB-607 | P2-TBDI4-23 | C2/C2S4 | C2S4-25/P2-TBDI4-23 | P2-TBDI4-23/C2S4-25 | XV-60262FG_DI_1 | [ ] Pass | ____ MΩ | [ ] 24V | ____ mA | ____ mA | ____ mA | [ ] Pass | READY FOR TEST | Pending Sign-off
268 | XV-60262FH | - | 325-01-602-PD-02 | Feed Slurry On/Off Valve for Nozzle #8 (ATVM-11B) | On/Off Valve | 24 VDC energized,Dry Contact | On-Off | TYP-DO-01 | TBDO | PANEL WIRING DIAGRAM.dwg | JB-607 | P2-TBDI4-25 | C2/C2S4 | C2S4-27/P2-TBDI4-25 | P2-TBDI4-25/C2S4-27 | XV-60262FH_DI_1 | [ ] Pass | ____ MΩ | [ ] 24V | ____ mA | ____ mA | ____ mA | [ ] Pass | READY FOR TEST | Pending Sign-off
269 | XV-60262SE | - | 325-01-602-PD-02 | Steam On/Off Valve for Nozzle #5 (ATVM-11B) | On/Off Valve | 24 VDC energized,Dry Contact | On-Off | TYP-DO-01 | TBDO | PANEL WIRING DIAGRAM.dwg | JB-607 | P2-TBDI4-27 | C2/C2S4 | C2S4-29/P2-TBDI4-27 | P2-TBDI4-27/C2S4-29 | XV-60262SE_DI_1 | [ ] Pass | ____ MΩ | [ ] 24V | ____ mA | ____ mA | ____ mA | [ ] Pass | READY FOR TEST | Pending Sign-off
270 | XV-60262SF | - | 325-01-602-PD-02 | Steam On/Off Valve for Nozzle #6 (ATVM-11B) | On/Off Valve | 24 VDC energized,Dry Contact | On-Off | TYP-DO-01 | TBDO | PANEL WIRING DIAGRAM.dwg | JB-607 | P2-TBDI4-29 | C2/C2S4 | C2S4-31/P2-TBDI4-29 | P2-TBDI4-29/C2S4-31 | XV-60262SF_DI_1 | [ ] Pass | ____ MΩ | [ ] 24V | ____ mA | ____ mA | ____ mA | [ ] Pass | READY FOR TEST | Pending Sign-off
271 | XV-60262SG | - | 325-01-602-PD-02 | Steam On/Off Valve for Nozzle #7 (ATVM-11B) | On/Off Valve | 24 VDC energized,Dry Contact | On-Off | TYP-DO-01 | TBDO | PANEL WIRING DIAGRAM.dwg | JB-607 | P2-TBDI4-31 | C2/C2S4 | C2S4-33/P2-TBDI4-31 | P2-TBDI4-31/C2S4-33 | XV-60262SG_DI_1 | [ ] Pass | ____ MΩ | [ ] 24V | ____ mA | ____ mA | ____ mA | [ ] Pass | READY FOR TEST | Pending Sign-off
272 | XV-60262SH | - | 325-01-602-PD-02 | Steam On/Off Valve for Nozzle #8 (ATVM-11B) | On/Off Valve | 24 VDC energized,Dry Contact | On-Off | TYP-DO-01 | TBDO | PANEL WIRING DIAGRAM.dwg | JB-607 | P2-TBDI5-1 | C2/C2S5 | C2S5-1/P2-TBDI5-1 | P2-TBDI5-1/C2S5-1 | XV-60262SH_DI_1 | [ ] Pass | ____ MΩ | [ ] 24V | ____ mA | ____ mA | ____ mA | [ ] Pass | READY FOR TEST | Pending Sign-off
273 | XV-60263FJ | - | 325-01-602-PD-02 | Feed Slurry On/Off Valve for Nozzle #9 (ATVM-11C) | On/Off Valve | 24 VDC energized,Dry Contact | On-Off | TYP-DO-01 | TBDO | PANEL WIRING DIAGRAM.dwg | JB-607 | P2-TBDI5-5 | C2/C2S5 | C2S5-5/P2-TBDI5-5 | P2-TBDI5-5/C2S5-5 | XV-60263FJ_DI_1 | [ ] Pass | ____ MΩ | [ ] 24V | ____ mA | ____ mA | ____ mA | [ ] Pass | READY FOR TEST | Pending Sign-off
274 | XV-60263FK | - | 325-01-602-PD-02 | Feed Slurry On/Off Valve for Nozzle #10 (ATVM-11C) | On/Off Valve | 24 VDC energized,Dry Contact | On-Off | TYP-DO-01 | TBDO | PANEL WIRING DIAGRAM.dwg | JB-607 | P2-TBDI5-7 | C2/C2S5 | C2S5-7/P2-TBDI5-7 | P2-TBDI5-7/C2S5-7 | XV-60263FK_DI_1 | [ ] Pass | ____ MΩ | [ ] 24V | ____ mA | ____ mA | ____ mA | [ ] Pass | READY FOR TEST | Pending Sign-off
275 | XV-60263FL | - | 325-01-602-PD-02 | Feed Slurry On/Off Valve for Nozzle #11 (ATVM-11C) | On/Off Valve | 24 VDC energized,Dry Contact | On-Off | TYP-DO-01 | TBDO | PANEL WIRING DIAGRAM.dwg | JB-607 | P2-TBDI5-9 | C2/C2S5 | C2S5-9/P2-TBDI5-9 | P2-TBDI5-9/C2S5-9 | XV-60263FL_DI_1 | [ ] Pass | ____ MΩ | [ ] 24V | ____ mA | ____ mA | ____ mA | [ ] Pass | READY FOR TEST | Pending Sign-off
276 | XV-60263FM | - | 325-01-602-PD-02 | Feed Slurry On/Off Valve for Nozzle #12 (ATVM-11C) | On/Off Valve | 24 VDC energized,Dry Contact | On-Off | TYP-DO-01 | TBDO | PANEL WIRING DIAGRAM.dwg | JB-607 | P2-TBDI5-11 | C2/C2S5 | C2S5-11/P2-TBDI5-11 | P2-TBDI5-11/C2S5-11 | XV-60263FM_DI_1 | [ ] Pass | ____ MΩ | [ ] 24V | ____ mA | ____ mA | ____ mA | [ ] Pass | READY FOR TEST | Pending Sign-off
277 | XV-60263SJ | - | 325-01-602-PD-02 | Steam On/Off Valve for Nozzle #9 (ATVM-11C) | On/Off Valve | 24 VDC energized,Dry Contact | On-Off | TYP-DO-01 | TBDO | PANEL WIRING DIAGRAM.dwg | JB-607 | P2-TBDI5-13 | C2/C2S5 | C2S5-13/P2-TBDI5-13 | P2-TBDI5-13/C2S5-13 | XV-60263SJ_DI_1 | [ ] Pass | ____ MΩ | [ ] 24V | ____ mA | ____ mA | ____ mA | [ ] Pass | READY FOR TEST | Pending Sign-off
278 | XV-60263SK | - | 325-01-602-PD-02 | Steam On/Off Valve for Nozzle #10 (ATVM-11C) | On/Off Valve | 24 VDC energized,Dry Contact | On-Off | TYP-DO-01 | TBDO | PANEL WIRING DIAGRAM.dwg | JB-607 | P2-TBDI5-15 | C2/C2S5 | C2S5-15/P2-TBDI5-15 | P2-TBDI5-15/C2S5-15 | XV-60263SK_DI_1 | [ ] Pass | ____ MΩ | [ ] 24V | ____ mA | ____ mA | ____ mA | [ ] Pass | READY FOR TEST | Pending Sign-off
279 | XV-60263SL | - | 325-01-602-PD-02 | Steam On/Off Valve for Nozzle #11 (ATVM-11C) | On/Off Valve | 24 VDC energized,Dry Contact | On-Off | TYP-DO-01 | TBDO | PANEL WIRING DIAGRAM.dwg | JB-607 | P2-TBDI5-17 | C2/C2S5 | C2S5-19/P2-TBDI5-17 | P2-TBDI5-17/C2S5-19 | XV-60263SL_DI_1 | [ ] Pass | ____ MΩ | [ ] 24V | ____ mA | ____ mA | ____ mA | [ ] Pass | READY FOR TEST | Pending Sign-off
280 | XV-60263SM | - | 325-01-602-PD-02 | Steam On/Off Valve for Nozzle #12 (ATVM-11C) | On/Off Valve | 24 VDC energized,Dry Contact | On-Off | TYP-DO-01 | TBDO | PANEL WIRING DIAGRAM.dwg | JB-607 | P2-TBDI5-19 | C2/C2S5 | C2S5-21/P2-TBDI5-19 | P2-TBDI5-19/C2S5-21 | XV-60263SM_DI_1 | [ ] Pass | ____ MΩ | [ ] 24V | ____ mA | ____ mA | ____ mA | [ ] Pass | READY FOR TEST | Pending Sign-off
281 | XV-60264FN | - | 325-01-602-PD-02 | Feed Slurry On/Off Valve for Nozzle #13 (ATVM-11D) | On/Off Valve | 24 VDC energized,Dry Contact | On-Off | TYP-DO-01 | TBDO | PANEL WIRING DIAGRAM.dwg | JB-607 | P2-TBDI3-13 | C2/C2S3 | C2S3-13/P2-TBDI3-13 | P2-TBDI3-13/C2S3-13 | XV-60264FN_DI_1 | [ ] Pass | ____ MΩ | [ ] 24V | ____ mA | ____ mA | ____ mA | [ ] Pass | READY FOR TEST | Pending Sign-off
282 | XV-60264FP | - | 325-01-602-PD-02 | Feed Slurry On/Off Valve for Nozzle #14 (ATVM-11D) | On/Off Valve | 24 VDC energized,Dry Contact | On-Off | TYP-DO-01 | TBDO | PANEL WIRING DIAGRAM.dwg | JB-607 | P2-TBDI3-15 | C2/C2S3 | C2S3-15/P2-TBDI3-15 | P2-TBDI3-15/C2S3-15 | XV-60264FP_DI_1 | [ ] Pass | ____ MΩ | [ ] 24V | ____ mA | ____ mA | ____ mA | [ ] Pass | READY FOR TEST | Pending Sign-off
283 | XV-60264FQ | - | 325-01-602-PD-02 | Feed Slurry On/Off Valve for Nozzle #15 (ATVM-11D) | On/Off Valve | 24 VDC energized,Dry Contact | On-Off | TYP-DO-01 | TBDO | PANEL WIRING DIAGRAM.dwg | JB-607 | P2-TBDI3-19 | C2/C2S3 | C2S3-21/P2-TBDI3-19 | P2-TBDI3-19/C2S3-21 | XV-60264FQ_DI_1 | [ ] Pass | ____ MΩ | [ ] 24V | ____ mA | ____ mA | ____ mA | [ ] Pass | READY FOR TEST | Pending Sign-off
284 | XV-60264FR | - | 325-01-602-PD-02 | Feed Slurry On/Off Valve for Nozzle #16 (ATVM-11D) | On/Off Valve | 24 VDC energized,Dry Contact | On-Off | TYP-DO-01 | TBDO | PANEL WIRING DIAGRAM.dwg | JB-607 | P2-TBDI3-23 | C2/C2S3 | C2S3-25/P2-TBDI3-23 | P2-TBDI3-23/C2S3-25 | XV-60264FR_DI_1 | [ ] Pass | ____ MΩ | [ ] 24V | ____ mA | ____ mA | ____ mA | [ ] Pass | READY FOR TEST | Pending Sign-off
285 | XV-60264SN | - | 325-01-602-PD-02 | Steam On/Off Valve for Nozzle #13 (ATVM-11D) | On/Off Valve | 24 VDC energized,Dry Contact | On-Off | TYP-DO-01 | TBDO | PANEL WIRING DIAGRAM.dwg | JB-607 | P2-TBDI3-27 | C2/C2S3 | C2S3-29/P2-TBDI3-27 | P2-TBDI3-27/C2S3-29 | XV-60264SN_DI_1 | [ ] Pass | ____ MΩ | [ ] 24V | ____ mA | ____ mA | ____ mA | [ ] Pass | READY FOR TEST | Pending Sign-off
286 | XV-60264SP | - | 325-01-602-PD-02 | Steam On/Off Valve for Nozzle #14 (ATVM-11D) | On/Off Valve | 24 VDC energized,Dry Contact | On-Off | TYP-DO-01 | TBDO | PANEL WIRING DIAGRAM.dwg | JB-607 | P2-TBDI3-31 | C2/C2S3 | C2S3-33/P2-TBDI3-31 | P2-TBDI3-31/C2S3-33 | XV-60264SP_DI_1 | [ ] Pass | ____ MΩ | [ ] 24V | ____ mA | ____ mA | ____ mA | [ ] Pass | READY FOR TEST | Pending Sign-off
287 | XV-60264SQ | - | 325-01-602-PD-02 | Steam On/Off Valve for Nozzle #15 (ATVM-11D) | On/Off Valve | 24 VDC energized,Dry Contact | On-Off | TYP-DO-01 | TBDO | PANEL WIRING DIAGRAM.dwg | JB-607 | P2-TBDI4-3 | C2/C2S4 | C2S4-3/P2-TBDI4-3 | P2-TBDI4-3/C2S4-3 | XV-60264SQ_DI_1 | [ ] Pass | ____ MΩ | [ ] 24V | ____ mA | ____ mA | ____ mA | [ ] Pass | READY FOR TEST | Pending Sign-off
288 | XV-60264SR | - | 325-01-602-PD-02 | Steam On/Off Valve for Nozzle #16 (ATVM-11D) | On/Off Valve | 24 VDC energized,Dry Contact | On-Off | TYP-DO-01 | TBDO | PANEL WIRING DIAGRAM.dwg | JB-607 | P2-TBDI4-7 | C2/C2S4 | C2S4-7/P2-TBDI4-7 | P2-TBDI4-7/C2S4-7 | XV-60264SR_DI_1 | [ ] Pass | ____ MΩ | [ ] 24V | ____ mA | ____ mA | ____ mA | [ ] Pass | READY FOR TEST | Pending Sign-off
289 | XV-60261DA |  | 325-01-602-PD-02 | Slurry Drain On/Off Valve for ATVM-11A | On/Off Valve | 24 VDC energized,Dry Contact | On-Off | TYP-DO-01 | TBDO | PANEL WIRING DIAGRAM.dwg | PLC | - | - | - | - | - | [ ] Pass | ____ MΩ | [ ] 24V | ____ mA | ____ mA | ____ mA | [ ] Pass | RESERVE ALLOC | Pending Sign-off

Sheet: 04_ITP_Inspection_Plan
KALASIN ENGINEERING | INSPECTION & TEST PLAN (ITP) — INSTRUMENTATION & CONTROL SYSTEMS
Quality Assurance & Control Verification Matrix (H = Hold Point, W = Witness Point, R = Review of Records)
Item # | Activity / Inspection Description | Reference Standard / Spec | Acceptance Criteria | Verifying Document | Contractor (Kalasin) | Client (Ingredion) | Third Party / TUV | Milestone Stage
1 | Receiving Inspection of Field Instruments & Transmitters | Project Instrument Datasheets | Damage-free, correct model, serial no., tag plate | Material Receiving Report (MRR) | H (Perform) | W (Witness) | R (Review) | Pre-Installation
2 | Cable Tray, Conduit & Field Gland Integrity Inspection | IEC 60079-14 / NEC 500 | Proper earthing, fire stops, Ex d/e rated glands | Cable Installation Record | H (Perform) | W (Witness) | R (Review) | Pre-Commissioning
3 | Field Instrument Mechanical Mounting & Impulse Piping | P&ID / Hook-up Drawings | Vibration-free, correct slopes, 5-valve manifolds tight | Mechanical Completion Cert | H (Perform) | W (Witness) | R (Review) | Pre-Commissioning
4 | Cable Continuity & Insulation Resistance (Megger Test) | IEC 62381 Clause 5.2 | Core-Core & Core-Earth > 20 MΩ @ 500VDC | Cold Loop Check Sheet | H (Perform) | W (Witness) | R (Review) | Loop Test Phase 1
5 | Shield Single-Point Earthing & Barrier Ground Bar | ISA-RP60.8 / IEC 60079-11 | Single-point earth at CA1 only. IS ground < 1.0 Ω | Earthing Test Certificate | H (Perform) | H (Hold) | W (Witness) | Loop Test Phase 1
6 | Hot Loop 24VDC Power Verification & Polarity Check | ControlLogix Wiring Diagram | Voltage 24VDC ±10%. Correct polarity without shorts | Power-Up Inspection Log | H (Perform) | R (Review) | R (Review) | Loop Test Phase 2
7 | Analog Transmitter 5-Point Calibration Simulation (AI) | IEC 62381 Clause 5.3 | Accuracy ≤ ±0.5% span at 0, 25, 50, 75, 100% | Loop Calibration Record | H (Perform) | W (Witness) | R (Review) | Loop Test Phase 3
8 | Control Valve Modulation Stroke & Fail-Safe Test (AO) | ISA-75.05 / IEC 60534 | Stroke error ≤ 1.0%. Fail-safe action < 2 sec | Valve Stroke Test Sheet | H (Perform) | H (Hold) | R (Review) | Loop Test Phase 4
9 | Discrete Limit Switch & Solenoid Valve Function Check | P&ID & Logic Diagram | 100% position switch fidelity & travel time < 3 sec | Discrete Check Sheet | H (Perform) | W (Witness) | R (Review) | Loop Test Phase 4
10 | Safety Interlock Trip & Emergency Shutdown (ESD) Test | Process Cause & Effect Matrix | 100% trip execution, alarm banner flashing, horn | Safety Trip Protocol | H (Perform) | H (Hold) | H (Hold) | Loop Test Phase 5
11 | SCADA Graphic HMI Representation & Alarm Logging | SCADA Architecture Spec | Real-time updates, engineering units, alarm logs | HMI Verification Log | H (Perform) | W (Witness) | R (Review) | Loop Test Phase 5
12 | Punchlist Clearance (Category A Zero-Defect Handover) | Contract Commissioning Spec | Zero Category A items. Cat B clearance schedule agreed | Punchlist Clearance Form | H (Perform) | H (Hold) | R (Review) | Final Handover
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
