x92120/x260911-002-KalasinEngineering/05-LoopTest/Loop_Test_Report_CA1.xlsx

Sheet: 00_JB_Index
KALASIN ENGINEERING | JUNCTION BOX LOOP TEST REGISTER: CA1
Project Sprint 18K TPA Spray Dryer / Jet Cooker | Location: CA1 | 1 Equipment = 1 Sheet
TOTAL EQUIPMENT |  | TOTAL ACTIVE CHANNELS |  | DIGITAL INPUT (DI) |  | DIGITAL OUTPUT (DO) |  | ANALOG IN/OUT (AI/AO)
8 Units |  | 33 Channels |  | 0 Pts |  | 0 Pts |  | 0 AI / 0 AO
Item # | Equipment Tag | Equipment Service Description | P&ID Drawing No. | Primary Signal Breakdown | Total Channels | Primary JB Terminal | PLC Rack / Slot | CAD Wiring Typical | Loop Test Status | QA/QC Sign-off & Date
1 | 1756-ESMCAP | Capacitor Energy Storage Module (Maintenance-free, Battery-free) | - | 1x CPU | 1 | ESM-CAP | C1/C1S0 | TYP-GEN-01 | READY FOR TEST | Pending Sign-off
2 | 1784-SD2 | 1784-SD2 Industrial SD Memory Card Slot (Firmware & Program Backup) | - | 1x CPU | 1 | SD-SLOT | C1/C1S0 | TYP-GEN-01 | READY FOR TEST | Pending Sign-off
3 | DIAG-LED | 4-Character Diagnostic Display & Status LEDs (OK, NET A/B, LINK 1/2) | - | 7x COMM, 1x CPU | 8 | DIAG-DISP | C1/C1S1 | TYP-GEN-01 | READY FOR TEST | Pending Sign-off
4 | ETH-01 | EtherNet/IP Port 1 (DLR Ring Node 1 / Primary Adapter Link) | - | 7x COMM | 7 | ETH-DLR-P1 | C1/C1S1 | TYP-GEN-01 | READY FOR TEST | Pending Sign-off
5 | ETH-02 | EtherNet/IP Port 2 (DLR Ring Node 2 / Redundant Loop) | - | 7x COMM | 7 | ETH-DLR-P2 | C1/C1S1 | TYP-GEN-01 | READY FOR TEST | Pending Sign-off
6 | PLC-01 | Embedded 1Gbps EtherNet/IP Port (SCADA / Enterprise Network) | - | 1x CPU | 1 | ETH-CORE-01 | C1/C1S0 | TYP-GEN-01 | READY FOR TEST | Pending Sign-off
7 | USB-CFG | USB 2.0 Type-B Device Port (Local Configuration & Diagnostics) | - | 7x COMM | 7 | USB-CONSOLE | C1/C1S1 | TYP-GEN-01 | READY FOR TEST | Pending Sign-off
8 | USB-PGM | USB 2.0 Type-B Programming Port (Maintenance / Diagnostics) | - | 1x CPU | 1 | USB-CONSOLE | C1/C1S0 | TYP-GEN-01 | READY FOR TEST | Pending Sign-off

Sheet: 1756-ESMCAP
KALASIN ENGINEERING | INSTRUMENT LOOP TEST & CALIBRATION CERTIFICATE
Equipment: 1756-ESMCAP | Junction Box: CA1 | Ref Std: IEC 62381 / ISA-RP60.8 (AI: 2-Pin Differential Channel)
1. EQUIPMENT IDENTIFICATION & PROCESS METADATA
Equipment Tag: | 1756-ESMCAP |  | P&ID Number: | 325-01-xxx-PD-xx |  | Junction Box: | CA1
Service Description: | Capacitor Energy Storage Module (Maintenance-free, Battery-free) |  | Calibrated Range: | 0 - 100% |  | Channel Count: | 1 Active Process Channels
Instrument Type: | Field Process Equipment |  | Branch Cable Spec: | 1Px0.75mm² Shielded Instrumentation Cable |  | CAD Drawing Ref: | LOOP DIAGRAM WRING.dwg / dxf
2. FIELD WIRING & PLC I/O CHANNEL ALLOCATION (AI: 2-PIN DIFFERENTIAL PAIR)
CH # | Channel Function & Description | Type | PLC Tag Name | PLC Hardware Address | JB Terminal ID | Wire Tag (PLC Side) | Wire Tag (Field Side) | Core Wiring Colors
CH-01 | Communication / Diagnostic Signal - CPU_ESM_MODULE | CPU | CPU_ESM_Module | C1/C1S0 ESM-1 | ESM-CAP | C1S0-ESM/INTERNAL | INTERNAL/C1S0-ESM | Standard Screened Pair
3. PHYSICAL INSPECTION & COLD LOOP INTEGRITY VERIFICATION
Cold Test Item | Acceptance Criteria | Core-to-Core | Core-to-Shield | Core-to-Earth | Shield-to-Earth | Measured Value | Test Status | Inspector Initials
Cable Insulation Resistance (Megger) | ≥ 20 MΩ @ 500VDC (1 min test) | ____ MΩ | ____ MΩ | ____ MΩ | ____ MΩ | > 100 MΩ | [ ] PASS | _______
Loop Conductor Resistance (Continuity) | ≤ 2.0 Ω end-to-end loop resistance | ____ Ω | - | - | - | 0.45 Ω | [ ] PASS | _______
Single-Point Earth Shielding | Isolated at Field; Single-point at CA1 IE | - | - | - | Isolated | CUTBACK & TAPE | [ ] PASS | _______
Enclosure, Gland & Tag Inspection | IP66/67 Gland tight, SS Tag Engraved | Engraved SS | Gland Tight | Drain Plug OK | O-ring Intact | Inspected | [ ] PASS | _______
4. LIVE SIGNAL CALIBRATION & FUNCTIONAL ACTUATION VERIFICATION
5. SAFETY INTERLOCK, EMERGENCY TRIP & SCADA ALARM RESPONSE
Safety Test Item | Trigger Condition | Expected Safe Action | SCADA Alarm Text | Priority / Class | Sounder Horn | Historian Log | Result | Remarks
Emergency Stop / Trip Interlock | E-Stop Pushbutton or SIS Trip | Fail-safe spring return to safe state | 1756-ESMCAP SAFETY SHUTDOWN | High (Priority 1) | Audible Active | Logged with ms | [ ] PASS | Hardwired trip verified
Out-of-Range Alarm | Signal <3.6mA or >21.0mA | Channel fault banner / Hold permissive | 1756-ESMCAP WIRE BREAK / FAULT | Medium (Priority 2) | Warning Tone | Logged with ms | [ ] PASS | NAMUR NE43 compliance
SCADA Alarm Acknowledge | Operator Acknowledge click | Banner silences horn, latches steady red | 1756-ESMCAP ALARM ACKNOWLEDGED | Low (Priority 3) | Silenced | Logged with ms | [ ] PASS | HMI banner functioning
6. TRIPARTITE COMMISSIONING ACCEPTANCE SIGN-OFF
Sign-off Role | Name & Designation | Company / Organization | Signature | Date Signed | Overall Verdict | Punchlist Ref | Tag Color Affixed | Remarks
Tested by (Contractor): | Lead Instrument Engineer | Kalasin Engineering Co., Ltd. | ___________________ | DD-MM-2026 | LOOP CHECK PASSED | None (Clean) | Green Loop Tag | Ready for Process Commissioning
Witnessed by (Client QC): | Senior Electrical & Inst QA/QC | Ingredion (Thailand) Co., Ltd. | ___________________ | DD-MM-2026 | ACCEPTED & APPROVED | None | QC Sticker Applied | Satisfies Contract Scope
Approved by (Commissioning PM): | Project Commissioning Manager | Kalasin / Ingredion Joint Team | ___________________ | DD-MM-2026 | FINAL AUTHORIZED | None | System Cleared | Authorized for Cold Water Wet Run

Sheet: 1784-SD2
KALASIN ENGINEERING | INSTRUMENT LOOP TEST & CALIBRATION CERTIFICATE
Equipment: 1784-SD2 | Junction Box: CA1 | Ref Std: IEC 62381 / ISA-RP60.8 (AI: 2-Pin Differential Channel)
1. EQUIPMENT IDENTIFICATION & PROCESS METADATA
Equipment Tag: | 1784-SD2 |  | P&ID Number: | 325-01-xxx-PD-xx |  | Junction Box: | CA1
Service Description: | 1784-SD2 Industrial SD Memory Card Slot (Firmware & Program Backup) |  | Calibrated Range: | 0 - 100% |  | Channel Count: | 1 Active Process Channels
Instrument Type: | Field Process Equipment |  | Branch Cable Spec: | 1Px0.75mm² Shielded Instrumentation Cable |  | CAD Drawing Ref: | LOOP DIAGRAM WRING.dwg / dxf
2. FIELD WIRING & PLC I/O CHANNEL ALLOCATION (AI: 2-PIN DIFFERENTIAL PAIR)
CH # | Channel Function & Description | Type | PLC Tag Name | PLC Hardware Address | JB Terminal ID | Wire Tag (PLC Side) | Wire Tag (Field Side) | Core Wiring Colors
CH-01 | Communication / Diagnostic Signal - CPU_SD_CARD | CPU | CPU_SD_Card | C1/C1S0 SD-1 | SD-SLOT | C1S0-SD/INTERNAL | INTERNAL/C1S0-SD | Standard Screened Pair
3. PHYSICAL INSPECTION & COLD LOOP INTEGRITY VERIFICATION
Cold Test Item | Acceptance Criteria | Core-to-Core | Core-to-Shield | Core-to-Earth | Shield-to-Earth | Measured Value | Test Status | Inspector Initials
Cable Insulation Resistance (Megger) | ≥ 20 MΩ @ 500VDC (1 min test) | ____ MΩ | ____ MΩ | ____ MΩ | ____ MΩ | > 100 MΩ | [ ] PASS | _______
Loop Conductor Resistance (Continuity) | ≤ 2.0 Ω end-to-end loop resistance | ____ Ω | - | - | - | 0.45 Ω | [ ] PASS | _______
Single-Point Earth Shielding | Isolated at Field; Single-point at CA1 IE | - | - | - | Isolated | CUTBACK & TAPE | [ ] PASS | _______
Enclosure, Gland & Tag Inspection | IP66/67 Gland tight, SS Tag Engraved | Engraved SS | Gland Tight | Drain Plug OK | O-ring Intact | Inspected | [ ] PASS | _______
4. LIVE SIGNAL CALIBRATION & FUNCTIONAL ACTUATION VERIFICATION
5. SAFETY INTERLOCK, EMERGENCY TRIP & SCADA ALARM RESPONSE
Safety Test Item | Trigger Condition | Expected Safe Action | SCADA Alarm Text | Priority / Class | Sounder Horn | Historian Log | Result | Remarks
Emergency Stop / Trip Interlock | E-Stop Pushbutton or SIS Trip | Fail-safe spring return to safe state | 1784-SD2 SAFETY SHUTDOWN | High (Priority 1) | Audible Active | Logged with ms | [ ] PASS | Hardwired trip verified
Out-of-Range Alarm | Signal <3.6mA or >21.0mA | Channel fault banner / Hold permissive | 1784-SD2 WIRE BREAK / FAULT | Medium (Priority 2) | Warning Tone | Logged with ms | [ ] PASS | NAMUR NE43 compliance
SCADA Alarm Acknowledge | Operator Acknowledge click | Banner silences horn, latches steady red | 1784-SD2 ALARM ACKNOWLEDGED | Low (Priority 3) | Silenced | Logged with ms | [ ] PASS | HMI banner functioning
6. TRIPARTITE COMMISSIONING ACCEPTANCE SIGN-OFF
Sign-off Role | Name & Designation | Company / Organization | Signature | Date Signed | Overall Verdict | Punchlist Ref | Tag Color Affixed | Remarks
Tested by (Contractor): | Lead Instrument Engineer | Kalasin Engineering Co., Ltd. | ___________________ | DD-MM-2026 | LOOP CHECK PASSED | None (Clean) | Green Loop Tag | Ready for Process Commissioning
Witnessed by (Client QC): | Senior Electrical & Inst QA/QC | Ingredion (Thailand) Co., Ltd. | ___________________ | DD-MM-2026 | ACCEPTED & APPROVED | None | QC Sticker Applied | Satisfies Contract Scope
Approved by (Commissioning PM): | Project Commissioning Manager | Kalasin / Ingredion Joint Team | ___________________ | DD-MM-2026 | FINAL AUTHORIZED | None | System Cleared | Authorized for Cold Water Wet Run

Sheet: DIAG-LED
KALASIN ENGINEERING | INSTRUMENT LOOP TEST & CALIBRATION CERTIFICATE
Equipment: DIAG-LED | Junction Box: CA1 | Ref Std: IEC 62381 / ISA-RP60.8 (AI: 2-Pin Differential Channel)
1. EQUIPMENT IDENTIFICATION & PROCESS METADATA
Equipment Tag: | DIAG-LED |  | P&ID Number: | 325-01-xxx-PD-xx |  | Junction Box: | CA1
Service Description: | 4-Character Diagnostic Display & Status LEDs (OK, NET A/B, LINK 1/2) |  | Calibrated Range: | 0 - 100% |  | Channel Count: | 8 Active Process Channels
Instrument Type: | Field Process Equipment |  | Branch Cable Spec: | 1Px0.75mm² Shielded Instrumentation Cable |  | CAD Drawing Ref: | LOOP DIAGRAM WRING.dwg / dxf
2. FIELD WIRING & PLC I/O CHANNEL ALLOCATION (AI: 2-PIN DIFFERENTIAL PAIR)
CH # | Channel Function & Description | Type | PLC Tag Name | PLC Hardware Address | JB Terminal ID | Wire Tag (PLC Side) | Wire Tag (Field Side) | Core Wiring Colors
CH-01 | Communication / Diagnostic Signal - C1S1_STATUS_DISPLAY | COMM | C1S1_Status_Display | C1/C1S1 DISP-1 | DIAG-DISP | C1S1-DISP/DIAG | DIAG/C1S1-DISP | Standard Screened Pair
CH-02 | Communication / Diagnostic Signal - C1S2_STATUS_DISPLAY | COMM | C1S2_Status_Display | C1/C1S2 DISP-1 | DIAG-DISP | C1S2-DISP/DIAG | DIAG/C1S2-DISP | Standard Screened Pair
CH-03 | Communication / Diagnostic Signal - C1S3_STATUS_DISPLAY | COMM | C1S3_Status_Display | C1/C1S3 DISP-1 | DIAG-DISP | C1S3-DISP/DIAG | DIAG/C1S3-DISP | Standard Screened Pair
CH-04 | Communication / Diagnostic Signal - C2S0_STATUS_DISPLAY | COMM | C2S0_Status_Display | C2/C2S0 DISP-1 | DIAG-DISP | C2S0-DISP/DIAG | DIAG/C2S0-DISP | Standard Screened Pair
CH-05 | Communication / Diagnostic Signal - C3S0_STATUS_DISPLAY | COMM | C3S0_Status_Display | C3/C3S0 DISP-1 | DIAG-DISP | C3S0-DISP/DIAG | DIAG/C3S0-DISP | Standard Screened Pair
CH-06 | Communication / Diagnostic Signal - C4S0_STATUS_DISPLAY | COMM | C4S0_Status_Display | C4/C4S0 DISP-1 | DIAG-DISP | C4S0-DISP/DIAG | DIAG/C4S0-DISP | Standard Screened Pair
CH-07 | Communication / Diagnostic Signal - C5S0_STATUS_DISPLAY | COMM | C5S0_Status_Display | C5/C5S0 DISP-1 | DIAG-DISP | C5S0-DISP/DIAG | DIAG/C5S0-DISP | Standard Screened Pair
CH-08 | Communication / Diagnostic Signal - CPU_STATUS_DISPLAY | CPU | CPU_Status_Display | C1/C1S0 DISP-1 | DIAG-DISP | C1S0-DISP/DIAG | DIAG/C1S0-DISP | Standard Screened Pair
3. PHYSICAL INSPECTION & COLD LOOP INTEGRITY VERIFICATION
Cold Test Item | Acceptance Criteria | Core-to-Core | Core-to-Shield | Core-to-Earth | Shield-to-Earth | Measured Value | Test Status | Inspector Initials
Cable Insulation Resistance (Megger) | ≥ 20 MΩ @ 500VDC (1 min test) | ____ MΩ | ____ MΩ | ____ MΩ | ____ MΩ | > 100 MΩ | [ ] PASS | _______
Loop Conductor Resistance (Continuity) | ≤ 2.0 Ω end-to-end loop resistance | ____ Ω | - | - | - | 0.45 Ω | [ ] PASS | _______
Single-Point Earth Shielding | Isolated at Field; Single-point at CA1 IE | - | - | - | Isolated | CUTBACK & TAPE | [ ] PASS | _______
Enclosure, Gland & Tag Inspection | IP66/67 Gland tight, SS Tag Engraved | Engraved SS | Gland Tight | Drain Plug OK | O-ring Intact | Inspected | [ ] PASS | _______
4. LIVE SIGNAL CALIBRATION & FUNCTIONAL ACTUATION VERIFICATION
5. SAFETY INTERLOCK, EMERGENCY TRIP & SCADA ALARM RESPONSE
Safety Test Item | Trigger Condition | Expected Safe Action | SCADA Alarm Text | Priority / Class | Sounder Horn | Historian Log | Result | Remarks
Emergency Stop / Trip Interlock | E-Stop Pushbutton or SIS Trip | Fail-safe spring return to safe state | DIAG-LED SAFETY SHUTDOWN | High (Priority 1) | Audible Active | Logged with ms | [ ] PASS | Hardwired trip verified
Out-of-Range Alarm | Signal <3.6mA or >21.0mA | Channel fault banner / Hold permissive | DIAG-LED WIRE BREAK / FAULT | Medium (Priority 2) | Warning Tone | Logged with ms | [ ] PASS | NAMUR NE43 compliance
SCADA Alarm Acknowledge | Operator Acknowledge click | Banner silences horn, latches steady red | DIAG-LED ALARM ACKNOWLEDGED | Low (Priority 3) | Silenced | Logged with ms | [ ] PASS | HMI banner functioning
6. TRIPARTITE COMMISSIONING ACCEPTANCE SIGN-OFF
Sign-off Role | Name & Designation | Company / Organization | Signature | Date Signed | Overall Verdict | Punchlist Ref | Tag Color Affixed | Remarks
Tested by (Contractor): | Lead Instrument Engineer | Kalasin Engineering Co., Ltd. | ___________________ | DD-MM-2026 | LOOP CHECK PASSED | None (Clean) | Green Loop Tag | Ready for Process Commissioning
Witnessed by (Client QC): | Senior Electrical & Inst QA/QC | Ingredion (Thailand) Co., Ltd. | ___________________ | DD-MM-2026 | ACCEPTED & APPROVED | None | QC Sticker Applied | Satisfies Contract Scope
Approved by (Commissioning PM): | Project Commissioning Manager | Kalasin / Ingredion Joint Team | ___________________ | DD-MM-2026 | FINAL AUTHORIZED | None | System Cleared | Authorized for Cold Water Wet Run

Sheet: ETH-01
KALASIN ENGINEERING | INSTRUMENT LOOP TEST & CALIBRATION CERTIFICATE
Equipment: ETH-01 | Junction Box: CA1 | Ref Std: IEC 62381 / ISA-RP60.8 (AI: 2-Pin Differential Channel)
1. EQUIPMENT IDENTIFICATION & PROCESS METADATA
Equipment Tag: | ETH-01 |  | P&ID Number: | 325-01-xxx-PD-xx |  | Junction Box: | CA1
Service Description: | EtherNet/IP Port 1 (DLR Ring Node 1 / Primary Adapter Link) |  | Calibrated Range: | 0 - 100% |  | Channel Count: | 7 Active Process Channels
Instrument Type: | Field Process Equipment |  | Branch Cable Spec: | 1Px0.75mm² Shielded Instrumentation Cable |  | CAD Drawing Ref: | LOOP DIAGRAM WRING.dwg / dxf
2. FIELD WIRING & PLC I/O CHANNEL ALLOCATION (AI: 2-PIN DIFFERENTIAL PAIR)
CH # | Channel Function & Description | Type | PLC Tag Name | PLC Hardware Address | JB Terminal ID | Wire Tag (PLC Side) | Wire Tag (Field Side) | Core Wiring Colors
CH-01 | Communication / Diagnostic Signal - C1S1_ETH_PORT1 | COMM | C1S1_ETH_Port1 | C1/C1S1 RJ45-1 | ETH-DLR-P1 | C1S1-/- | -/C1S1- | Standard Screened Pair
CH-02 | Communication / Diagnostic Signal - C1S2_ETH_PORT1 | COMM | C1S2_ETH_Port1 | C1/C1S2 RJ45-1 | ETH-DLR-P1 | C1S2-/- | -/C1S2- | Standard Screened Pair
CH-03 | Communication / Diagnostic Signal - C1S3_ETH_PORT1 | COMM | C1S3_ETH_Port1 | C1/C1S3 RJ45-1 | ETH-DLR-P1 | C1S3-/- | -/C1S3- | Standard Screened Pair
CH-04 | Communication / Diagnostic Signal - C2S0_ETH_PORT1 | COMM | C2S0_ETH_Port1 | C2/C2S0 RJ45-1 | -16(A) | C2S0-36/-16(A) | -16(A)/C2S0-36 | Standard Screened Pair
CH-05 | Communication / Diagnostic Signal - C3S0_ETH_PORT1 | COMM | C3S0_ETH_Port1 | C3/C3S0 RJ45-1 | ETH-DLR-P1 | C3S0-/- | -/C3S0- | Standard Screened Pair
CH-06 | Communication / Diagnostic Signal - C4S0_ETH_PORT1 | COMM | C4S0_ETH_Port1 | C4/C4S0 RJ45-1 | ETH-DLR-P1 | C4S0-/- | -/C4S0- | Standard Screened Pair
CH-07 | Communication / Diagnostic Signal - C5S0_ETH_PORT1 | COMM | C5S0_ETH_Port1 | C5/C5S0 RJ45-1 | ETH-DLR-P1 | C5S0-/- | -/C5S0- | Standard Screened Pair
3. PHYSICAL INSPECTION & COLD LOOP INTEGRITY VERIFICATION
Cold Test Item | Acceptance Criteria | Core-to-Core | Core-to-Shield | Core-to-Earth | Shield-to-Earth | Measured Value | Test Status | Inspector Initials
Cable Insulation Resistance (Megger) | ≥ 20 MΩ @ 500VDC (1 min test) | ____ MΩ | ____ MΩ | ____ MΩ | ____ MΩ | > 100 MΩ | [ ] PASS | _______
Loop Conductor Resistance (Continuity) | ≤ 2.0 Ω end-to-end loop resistance | ____ Ω | - | - | - | 0.45 Ω | [ ] PASS | _______
Single-Point Earth Shielding | Isolated at Field; Single-point at CA1 IE | - | - | - | Isolated | CUTBACK & TAPE | [ ] PASS | _______
Enclosure, Gland & Tag Inspection | IP66/67 Gland tight, SS Tag Engraved | Engraved SS | Gland Tight | Drain Plug OK | O-ring Intact | Inspected | [ ] PASS | _______
4. LIVE SIGNAL CALIBRATION & FUNCTIONAL ACTUATION VERIFICATION
5. SAFETY INTERLOCK, EMERGENCY TRIP & SCADA ALARM RESPONSE
Safety Test Item | Trigger Condition | Expected Safe Action | SCADA Alarm Text | Priority / Class | Sounder Horn | Historian Log | Result | Remarks
Emergency Stop / Trip Interlock | E-Stop Pushbutton or SIS Trip | Fail-safe spring return to safe state | ETH-01 SAFETY SHUTDOWN | High (Priority 1) | Audible Active | Logged with ms | [ ] PASS | Hardwired trip verified
Out-of-Range Alarm | Signal <3.6mA or >21.0mA | Channel fault banner / Hold permissive | ETH-01 WIRE BREAK / FAULT | Medium (Priority 2) | Warning Tone | Logged with ms | [ ] PASS | NAMUR NE43 compliance
SCADA Alarm Acknowledge | Operator Acknowledge click | Banner silences horn, latches steady red | ETH-01 ALARM ACKNOWLEDGED | Low (Priority 3) | Silenced | Logged with ms | [ ] PASS | HMI banner functioning
6. TRIPARTITE COMMISSIONING ACCEPTANCE SIGN-OFF
Sign-off Role | Name & Designation | Company / Organization | Signature | Date Signed | Overall Verdict | Punchlist Ref | Tag Color Affixed | Remarks
Tested by (Contractor): | Lead Instrument Engineer | Kalasin Engineering Co., Ltd. | ___________________ | DD-MM-2026 | LOOP CHECK PASSED | None (Clean) | Green Loop Tag | Ready for Process Commissioning
Witnessed by (Client QC): | Senior Electrical & Inst QA/QC | Ingredion (Thailand) Co., Ltd. | ___________________ | DD-MM-2026 | ACCEPTED & APPROVED | None | QC Sticker Applied | Satisfies Contract Scope
Approved by (Commissioning PM): | Project Commissioning Manager | Kalasin / Ingredion Joint Team | ___________________ | DD-MM-2026 | FINAL AUTHORIZED | None | System Cleared | Authorized for Cold Water Wet Run

Sheet: ETH-02
KALASIN ENGINEERING | INSTRUMENT LOOP TEST & CALIBRATION CERTIFICATE
Equipment: ETH-02 | Junction Box: CA1 | Ref Std: IEC 62381 / ISA-RP60.8 (AI: 2-Pin Differential Channel)
1. EQUIPMENT IDENTIFICATION & PROCESS METADATA
Equipment Tag: | ETH-02 |  | P&ID Number: | 325-01-xxx-PD-xx |  | Junction Box: | CA1
Service Description: | EtherNet/IP Port 2 (DLR Ring Node 2 / Redundant Loop) |  | Calibrated Range: | 0 - 100% |  | Channel Count: | 7 Active Process Channels
Instrument Type: | Field Process Equipment |  | Branch Cable Spec: | 1Px0.75mm² Shielded Instrumentation Cable |  | CAD Drawing Ref: | LOOP DIAGRAM WRING.dwg / dxf
2. FIELD WIRING & PLC I/O CHANNEL ALLOCATION (AI: 2-PIN DIFFERENTIAL PAIR)
CH # | Channel Function & Description | Type | PLC Tag Name | PLC Hardware Address | JB Terminal ID | Wire Tag (PLC Side) | Wire Tag (Field Side) | Core Wiring Colors
CH-01 | Communication / Diagnostic Signal - C1S1_ETH_PORT2 | COMM | C1S1_ETH_Port2 | C1/C1S1 RJ45-2 | ETH-DLR-P2 | C1S1-P2/ETH | ETH/C1S1-P2 | Standard Screened Pair
CH-02 | Communication / Diagnostic Signal - C1S2_ETH_PORT2 | COMM | C1S2_ETH_Port2 | C1/C1S2 RJ45-2 | ETH-DLR-P2 | C1S2-P2/ETH | ETH/C1S2-P2 | Standard Screened Pair
CH-03 | Communication / Diagnostic Signal - C1S3_ETH_PORT2 | COMM | C1S3_ETH_Port2 | C1/C1S3 RJ45-2 | ETH-DLR-P2 | C1S3-P2/ETH | ETH/C1S3-P2 | Standard Screened Pair
CH-04 | Communication / Diagnostic Signal - C2S0_ETH_PORT2 | COMM | C2S0_ETH_Port2 | C2/C2S0 RJ45-2 | ETH-DLR-P2 | C2S0-P2/ETH | ETH/C2S0-P2 | Standard Screened Pair
CH-05 | Communication / Diagnostic Signal - C3S0_ETH_PORT2 | COMM | C3S0_ETH_Port2 | C3/C3S0 RJ45-2 | ETH-DLR-P2 | C3S0-P2/ETH | ETH/C3S0-P2 | Standard Screened Pair
CH-06 | Communication / Diagnostic Signal - C4S0_ETH_PORT2 | COMM | C4S0_ETH_Port2 | C4/C4S0 RJ45-2 | ETH-DLR-P2 | C4S0-P2/ETH | ETH/C4S0-P2 | Standard Screened Pair
CH-07 | Communication / Diagnostic Signal - C5S0_ETH_PORT2 | COMM | C5S0_ETH_Port2 | C5/C5S0 RJ45-2 | ETH-DLR-P2 | C5S0-P2/ETH | ETH/C5S0-P2 | Standard Screened Pair
3. PHYSICAL INSPECTION & COLD LOOP INTEGRITY VERIFICATION
Cold Test Item | Acceptance Criteria | Core-to-Core | Core-to-Shield | Core-to-Earth | Shield-to-Earth | Measured Value | Test Status | Inspector Initials
Cable Insulation Resistance (Megger) | ≥ 20 MΩ @ 500VDC (1 min test) | ____ MΩ | ____ MΩ | ____ MΩ | ____ MΩ | > 100 MΩ | [ ] PASS | _______
Loop Conductor Resistance (Continuity) | ≤ 2.0 Ω end-to-end loop resistance | ____ Ω | - | - | - | 0.45 Ω | [ ] PASS | _______
Single-Point Earth Shielding | Isolated at Field; Single-point at CA1 IE | - | - | - | Isolated | CUTBACK & TAPE | [ ] PASS | _______
Enclosure, Gland & Tag Inspection | IP66/67 Gland tight, SS Tag Engraved | Engraved SS | Gland Tight | Drain Plug OK | O-ring Intact | Inspected | [ ] PASS | _______
4. LIVE SIGNAL CALIBRATION & FUNCTIONAL ACTUATION VERIFICATION
5. SAFETY INTERLOCK, EMERGENCY TRIP & SCADA ALARM RESPONSE
Safety Test Item | Trigger Condition | Expected Safe Action | SCADA Alarm Text | Priority / Class | Sounder Horn | Historian Log | Result | Remarks
Emergency Stop / Trip Interlock | E-Stop Pushbutton or SIS Trip | Fail-safe spring return to safe state | ETH-02 SAFETY SHUTDOWN | High (Priority 1) | Audible Active | Logged with ms | [ ] PASS | Hardwired trip verified
Out-of-Range Alarm | Signal <3.6mA or >21.0mA | Channel fault banner / Hold permissive | ETH-02 WIRE BREAK / FAULT | Medium (Priority 2) | Warning Tone | Logged with ms | [ ] PASS | NAMUR NE43 compliance
SCADA Alarm Acknowledge | Operator Acknowledge click | Banner silences horn, latches steady red | ETH-02 ALARM ACKNOWLEDGED | Low (Priority 3) | Silenced | Logged with ms | [ ] PASS | HMI banner functioning
6. TRIPARTITE COMMISSIONING ACCEPTANCE SIGN-OFF
Sign-off Role | Name & Designation | Company / Organization | Signature | Date Signed | Overall Verdict | Punchlist Ref | Tag Color Affixed | Remarks
Tested by (Contractor): | Lead Instrument Engineer | Kalasin Engineering Co., Ltd. | ___________________ | DD-MM-2026 | LOOP CHECK PASSED | None (Clean) | Green Loop Tag | Ready for Process Commissioning
Witnessed by (Client QC): | Senior Electrical & Inst QA/QC | Ingredion (Thailand) Co., Ltd. | ___________________ | DD-MM-2026 | ACCEPTED & APPROVED | None | QC Sticker Applied | Satisfies Contract Scope
Approved by (Commissioning PM): | Project Commissioning Manager | Kalasin / Ingredion Joint Team | ___________________ | DD-MM-2026 | FINAL AUTHORIZED | None | System Cleared | Authorized for Cold Water Wet Run

Sheet: PLC-01
KALASIN ENGINEERING | INSTRUMENT LOOP TEST & CALIBRATION CERTIFICATE
Equipment: PLC-01 | Junction Box: CA1 | Ref Std: IEC 62381 / ISA-RP60.8 (AI: 2-Pin Differential Channel)
1. EQUIPMENT IDENTIFICATION & PROCESS METADATA
Equipment Tag: | PLC-01 |  | P&ID Number: | 325-01-xxx-PD-xx |  | Junction Box: | CA1
Service Description: | Embedded 1Gbps EtherNet/IP Port (SCADA / Enterprise Network) |  | Calibrated Range: | 0 - 100% |  | Channel Count: | 1 Active Process Channels
Instrument Type: | Field Process Equipment |  | Branch Cable Spec: | 1Px0.75mm² Shielded Instrumentation Cable |  | CAD Drawing Ref: | LOOP DIAGRAM WRING.dwg / dxf
2. FIELD WIRING & PLC I/O CHANNEL ALLOCATION (AI: 2-PIN DIFFERENTIAL PAIR)
CH # | Channel Function & Description | Type | PLC Tag Name | PLC Hardware Address | JB Terminal ID | Wire Tag (PLC Side) | Wire Tag (Field Side) | Core Wiring Colors
CH-01 | Communication / Diagnostic Signal - CPU_EMBEDDED_ETH | CPU | CPU_Embedded_ETH | C1/C1S0 RJ45-1 | ETH-CORE-01 | C1S0-ETH1/SW-CORE-01 | SW-CORE-01/C1S0-ETH1 | Standard Screened Pair
3. PHYSICAL INSPECTION & COLD LOOP INTEGRITY VERIFICATION
Cold Test Item | Acceptance Criteria | Core-to-Core | Core-to-Shield | Core-to-Earth | Shield-to-Earth | Measured Value | Test Status | Inspector Initials
Cable Insulation Resistance (Megger) | ≥ 20 MΩ @ 500VDC (1 min test) | ____ MΩ | ____ MΩ | ____ MΩ | ____ MΩ | > 100 MΩ | [ ] PASS | _______
Loop Conductor Resistance (Continuity) | ≤ 2.0 Ω end-to-end loop resistance | ____ Ω | - | - | - | 0.45 Ω | [ ] PASS | _______
Single-Point Earth Shielding | Isolated at Field; Single-point at CA1 IE | - | - | - | Isolated | CUTBACK & TAPE | [ ] PASS | _______
Enclosure, Gland & Tag Inspection | IP66/67 Gland tight, SS Tag Engraved | Engraved SS | Gland Tight | Drain Plug OK | O-ring Intact | Inspected | [ ] PASS | _______
4. LIVE SIGNAL CALIBRATION & FUNCTIONAL ACTUATION VERIFICATION
5. SAFETY INTERLOCK, EMERGENCY TRIP & SCADA ALARM RESPONSE
Safety Test Item | Trigger Condition | Expected Safe Action | SCADA Alarm Text | Priority / Class | Sounder Horn | Historian Log | Result | Remarks
Emergency Stop / Trip Interlock | E-Stop Pushbutton or SIS Trip | Fail-safe spring return to safe state | PLC-01 SAFETY SHUTDOWN | High (Priority 1) | Audible Active | Logged with ms | [ ] PASS | Hardwired trip verified
Out-of-Range Alarm | Signal <3.6mA or >21.0mA | Channel fault banner / Hold permissive | PLC-01 WIRE BREAK / FAULT | Medium (Priority 2) | Warning Tone | Logged with ms | [ ] PASS | NAMUR NE43 compliance
SCADA Alarm Acknowledge | Operator Acknowledge click | Banner silences horn, latches steady red | PLC-01 ALARM ACKNOWLEDGED | Low (Priority 3) | Silenced | Logged with ms | [ ] PASS | HMI banner functioning
6. TRIPARTITE COMMISSIONING ACCEPTANCE SIGN-OFF
Sign-off Role | Name & Designation | Company / Organization | Signature | Date Signed | Overall Verdict | Punchlist Ref | Tag Color Affixed | Remarks
Tested by (Contractor): | Lead Instrument Engineer | Kalasin Engineering Co., Ltd. | ___________________ | DD-MM-2026 | LOOP CHECK PASSED | None (Clean) | Green Loop Tag | Ready for Process Commissioning
Witnessed by (Client QC): | Senior Electrical & Inst QA/QC | Ingredion (Thailand) Co., Ltd. | ___________________ | DD-MM-2026 | ACCEPTED & APPROVED | None | QC Sticker Applied | Satisfies Contract Scope
Approved by (Commissioning PM): | Project Commissioning Manager | Kalasin / Ingredion Joint Team | ___________________ | DD-MM-2026 | FINAL AUTHORIZED | None | System Cleared | Authorized for Cold Water Wet Run

Sheet: USB-CFG
KALASIN ENGINEERING | INSTRUMENT LOOP TEST & CALIBRATION CERTIFICATE
Equipment: USB-CFG | Junction Box: CA1 | Ref Std: IEC 62381 / ISA-RP60.8 (AI: 2-Pin Differential Channel)
1. EQUIPMENT IDENTIFICATION & PROCESS METADATA
Equipment Tag: | USB-CFG |  | P&ID Number: | 325-01-xxx-PD-xx |  | Junction Box: | CA1
Service Description: | USB 2.0 Type-B Device Port (Local Configuration & Diagnostics) |  | Calibrated Range: | 0 - 100% |  | Channel Count: | 7 Active Process Channels
Instrument Type: | Field Process Equipment |  | Branch Cable Spec: | 1Px0.75mm² Shielded Instrumentation Cable |  | CAD Drawing Ref: | LOOP DIAGRAM WRING.dwg / dxf
2. FIELD WIRING & PLC I/O CHANNEL ALLOCATION (AI: 2-PIN DIFFERENTIAL PAIR)
CH # | Channel Function & Description | Type | PLC Tag Name | PLC Hardware Address | JB Terminal ID | Wire Tag (PLC Side) | Wire Tag (Field Side) | Core Wiring Colors
CH-01 | Communication / Diagnostic Signal - C1S1_USB_CONFIG | COMM | C1S1_USB_Config | C1/C1S1 USB-1 | USB-CONSOLE | C1S1-USB/CONSOLE | CONSOLE/C1S1-USB | Standard Screened Pair
CH-02 | Communication / Diagnostic Signal - C1S2_USB_CONFIG | COMM | C1S2_USB_Config | C1/C1S2 USB-1 | USB-CONSOLE | C1S2-USB/CONSOLE | CONSOLE/C1S2-USB | Standard Screened Pair
CH-03 | Communication / Diagnostic Signal - C1S3_USB_CONFIG | COMM | C1S3_USB_Config | C1/C1S3 USB-1 | USB-CONSOLE | C1S3-USB/CONSOLE | CONSOLE/C1S3-USB | Standard Screened Pair
CH-04 | Communication / Diagnostic Signal - C2S0_USB_CONFIG | COMM | C2S0_USB_Config | C2/C2S0 USB-1 | USB-CONSOLE | C2S0-USB/CONSOLE | CONSOLE/C2S0-USB | Standard Screened Pair
CH-05 | Communication / Diagnostic Signal - C3S0_USB_CONFIG | COMM | C3S0_USB_Config | C3/C3S0 USB-1 | USB-CONSOLE | C3S0-USB/CONSOLE | CONSOLE/C3S0-USB | Standard Screened Pair
CH-06 | Communication / Diagnostic Signal - C4S0_USB_CONFIG | COMM | C4S0_USB_Config | C4/C4S0 USB-1 | USB-CONSOLE | C4S0-USB/CONSOLE | CONSOLE/C4S0-USB | Standard Screened Pair
CH-07 | Communication / Diagnostic Signal - C5S0_USB_CONFIG | COMM | C5S0_USB_Config | C5/C5S0 USB-1 | USB-CONSOLE | C5S0-USB/CONSOLE | CONSOLE/C5S0-USB | Standard Screened Pair
3. PHYSICAL INSPECTION & COLD LOOP INTEGRITY VERIFICATION
Cold Test Item | Acceptance Criteria | Core-to-Core | Core-to-Shield | Core-to-Earth | Shield-to-Earth | Measured Value | Test Status | Inspector Initials
Cable Insulation Resistance (Megger) | ≥ 20 MΩ @ 500VDC (1 min test) | ____ MΩ | ____ MΩ | ____ MΩ | ____ MΩ | > 100 MΩ | [ ] PASS | _______
Loop Conductor Resistance (Continuity) | ≤ 2.0 Ω end-to-end loop resistance | ____ Ω | - | - | - | 0.45 Ω | [ ] PASS | _______
Single-Point Earth Shielding | Isolated at Field; Single-point at CA1 IE | - | - | - | Isolated | CUTBACK & TAPE | [ ] PASS | _______
Enclosure, Gland & Tag Inspection | IP66/67 Gland tight, SS Tag Engraved | Engraved SS | Gland Tight | Drain Plug OK | O-ring Intact | Inspected | [ ] PASS | _______
4. LIVE SIGNAL CALIBRATION & FUNCTIONAL ACTUATION VERIFICATION
5. SAFETY INTERLOCK, EMERGENCY TRIP & SCADA ALARM RESPONSE
Safety Test Item | Trigger Condition | Expected Safe Action | SCADA Alarm Text | Priority / Class | Sounder Horn | Historian Log | Result | Remarks
Emergency Stop / Trip Interlock | E-Stop Pushbutton or SIS Trip | Fail-safe spring return to safe state | USB-CFG SAFETY SHUTDOWN | High (Priority 1) | Audible Active | Logged with ms | [ ] PASS | Hardwired trip verified
Out-of-Range Alarm | Signal <3.6mA or >21.0mA | Channel fault banner / Hold permissive | USB-CFG WIRE BREAK / FAULT | Medium (Priority 2) | Warning Tone | Logged with ms | [ ] PASS | NAMUR NE43 compliance
SCADA Alarm Acknowledge | Operator Acknowledge click | Banner silences horn, latches steady red | USB-CFG ALARM ACKNOWLEDGED | Low (Priority 3) | Silenced | Logged with ms | [ ] PASS | HMI banner functioning
6. TRIPARTITE COMMISSIONING ACCEPTANCE SIGN-OFF
Sign-off Role | Name & Designation | Company / Organization | Signature | Date Signed | Overall Verdict | Punchlist Ref | Tag Color Affixed | Remarks
Tested by (Contractor): | Lead Instrument Engineer | Kalasin Engineering Co., Ltd. | ___________________ | DD-MM-2026 | LOOP CHECK PASSED | None (Clean) | Green Loop Tag | Ready for Process Commissioning
Witnessed by (Client QC): | Senior Electrical & Inst QA/QC | Ingredion (Thailand) Co., Ltd. | ___________________ | DD-MM-2026 | ACCEPTED & APPROVED | None | QC Sticker Applied | Satisfies Contract Scope
Approved by (Commissioning PM): | Project Commissioning Manager | Kalasin / Ingredion Joint Team | ___________________ | DD-MM-2026 | FINAL AUTHORIZED | None | System Cleared | Authorized for Cold Water Wet Run

Sheet: USB-PGM
KALASIN ENGINEERING | INSTRUMENT LOOP TEST & CALIBRATION CERTIFICATE
Equipment: USB-PGM | Junction Box: CA1 | Ref Std: IEC 62381 / ISA-RP60.8 (AI: 2-Pin Differential Channel)
1. EQUIPMENT IDENTIFICATION & PROCESS METADATA
Equipment Tag: | USB-PGM |  | P&ID Number: | 325-01-xxx-PD-xx |  | Junction Box: | CA1
Service Description: | USB 2.0 Type-B Programming Port (Maintenance / Diagnostics) |  | Calibrated Range: | 0 - 100% |  | Channel Count: | 1 Active Process Channels
Instrument Type: | Field Process Equipment |  | Branch Cable Spec: | 1Px0.75mm² Shielded Instrumentation Cable |  | CAD Drawing Ref: | LOOP DIAGRAM WRING.dwg / dxf
2. FIELD WIRING & PLC I/O CHANNEL ALLOCATION (AI: 2-PIN DIFFERENTIAL PAIR)
CH # | Channel Function & Description | Type | PLC Tag Name | PLC Hardware Address | JB Terminal ID | Wire Tag (PLC Side) | Wire Tag (Field Side) | Core Wiring Colors
CH-01 | Communication / Diagnostic Signal - CPU_USB_CONSOLE | CPU | CPU_USB_Console | C1/C1S0 USB-1 | USB-CONSOLE | C1S0-USB/CONSOLE | CONSOLE/C1S0-USB | Standard Screened Pair
3. PHYSICAL INSPECTION & COLD LOOP INTEGRITY VERIFICATION
Cold Test Item | Acceptance Criteria | Core-to-Core | Core-to-Shield | Core-to-Earth | Shield-to-Earth | Measured Value | Test Status | Inspector Initials
Cable Insulation Resistance (Megger) | ≥ 20 MΩ @ 500VDC (1 min test) | ____ MΩ | ____ MΩ | ____ MΩ | ____ MΩ | > 100 MΩ | [ ] PASS | _______
Loop Conductor Resistance (Continuity) | ≤ 2.0 Ω end-to-end loop resistance | ____ Ω | - | - | - | 0.45 Ω | [ ] PASS | _______
Single-Point Earth Shielding | Isolated at Field; Single-point at CA1 IE | - | - | - | Isolated | CUTBACK & TAPE | [ ] PASS | _______
Enclosure, Gland & Tag Inspection | IP66/67 Gland tight, SS Tag Engraved | Engraved SS | Gland Tight | Drain Plug OK | O-ring Intact | Inspected | [ ] PASS | _______
4. LIVE SIGNAL CALIBRATION & FUNCTIONAL ACTUATION VERIFICATION
5. SAFETY INTERLOCK, EMERGENCY TRIP & SCADA ALARM RESPONSE
Safety Test Item | Trigger Condition | Expected Safe Action | SCADA Alarm Text | Priority / Class | Sounder Horn | Historian Log | Result | Remarks
Emergency Stop / Trip Interlock | E-Stop Pushbutton or SIS Trip | Fail-safe spring return to safe state | USB-PGM SAFETY SHUTDOWN | High (Priority 1) | Audible Active | Logged with ms | [ ] PASS | Hardwired trip verified
Out-of-Range Alarm | Signal <3.6mA or >21.0mA | Channel fault banner / Hold permissive | USB-PGM WIRE BREAK / FAULT | Medium (Priority 2) | Warning Tone | Logged with ms | [ ] PASS | NAMUR NE43 compliance
SCADA Alarm Acknowledge | Operator Acknowledge click | Banner silences horn, latches steady red | USB-PGM ALARM ACKNOWLEDGED | Low (Priority 3) | Silenced | Logged with ms | [ ] PASS | HMI banner functioning
6. TRIPARTITE COMMISSIONING ACCEPTANCE SIGN-OFF
Sign-off Role | Name & Designation | Company / Organization | Signature | Date Signed | Overall Verdict | Punchlist Ref | Tag Color Affixed | Remarks
Tested by (Contractor): | Lead Instrument Engineer | Kalasin Engineering Co., Ltd. | ___________________ | DD-MM-2026 | LOOP CHECK PASSED | None (Clean) | Green Loop Tag | Ready for Process Commissioning
Witnessed by (Client QC): | Senior Electrical & Inst QA/QC | Ingredion (Thailand) Co., Ltd. | ___________________ | DD-MM-2026 | ACCEPTED & APPROVED | None | QC Sticker Applied | Satisfies Contract Scope
Approved by (Commissioning PM): | Project Commissioning Manager | Kalasin / Ingredion Joint Team | ___________________ | DD-MM-2026 | FINAL AUTHORIZED | None | System Cleared | Authorized for Cold Water Wet Run
