x92120/x260911-002-KalasinEngineering/05-LoopTest/Loop_Test_Report_IS-JB-603.xlsx

Sheet: 00_JB_Index
KALASIN ENGINEERING | JUNCTION BOX LOOP TEST REGISTER: IS-JB-603
Project Sprint 18K TPA Spray Dryer / Jet Cooker | Location: IS-JB-603 | 1 Equipment = 1 Sheet
TOTAL EQUIPMENT |  | TOTAL ACTIVE CHANNELS |  | DIGITAL INPUT (DI) |  | DIGITAL OUTPUT (DO) |  | ANALOG IN/OUT (AI/AO)
22 Units |  | 22 Channels |  | 15 Pts |  | 0 Pts |  | 7 AI / 0 AO
Item # | Equipment Tag | Equipment Service Description | P&ID Drawing No. | Primary Signal Breakdown | Total Channels | Primary JB Terminal | PLC Rack / Slot | CAD Wiring Typical | Loop Test Status | QA/QC Sign-off & Date
1 | AT-40201 | Start / Stop Command for VSD AT-40201 | 325-01-402-PD-01 | 1x DI | 1 | P4-TBDI1-1 | C4/C4S1 | TYP-IS-01 / BARRIER | READY FOR TEST | Pending Sign-off
2 | AT-40202 | Start / Stop Command for VSD AT-40202 | 325-01-402-PD-01 | 1x DI | 1 | P4-TBDI1-2 | C4/C4S1 | TYP-IS-01 / BARRIER | READY FOR TEST | Pending Sign-off
3 | AT-40203 | Start / Stop Command for VSD AT-40203 | 325-01-402-PD-02 | 1x DI | 1 | P4-TBDI1-3 | C4/C4S1 | TYP-IS-01 / BARRIER | READY FOR TEST | Pending Sign-off
4 | LSH-60230 | Powder Level Switch High for Cyclone (CYCL-21) | 325-01-602-PD-04 | 1x DI | 1 | P4-TBDI1-4 | C4/C4S1 | TYP-DI-01 / SWITCH | READY FOR TEST | Pending Sign-off
5 | LSH-60231 | Powder Level Switch High for Cyclone (CYCL-22) | 325-01-602-PD-04 | 1x DI | 1 | P4-TBDI1-5 | C4/C4S1 | TYP-DI-01 / SWITCH | READY FOR TEST | Pending Sign-off
6 | LSH-60240 | Powder Level Switch High for Bag House (BGHS-21) | 325-01-602-PD-05 | 1x DI | 1 | P4-TBDI1-6 | C4/C4S1 | TYP-DI-01 / SWITCH | READY FOR TEST | Pending Sign-off
7 | PD-60202 | IN-6 | - | 1x DI | 1 | P4-TBDI1-7 | C4/C4S1 | TYP-IS-01 / BARRIER | READY FOR TEST | Pending Sign-off
8 | PT-60230 | Gas Pressure Transmitter for Conveying Duct (DTCO-21) | 325-01-602-PD-04 | 1x AI | 1 | P4-TBAI1-1(A/B) | C4/C4S5 | TYP-AI-01 / 2-WIRE | READY FOR TEST | Pending Sign-off
9 | PT-60231 | Gas Pressure Transmitter for Cyclone Exhaust Duct (DTCE-21) | 325-01-602-PD-04 | 1x AI | 1 | P4-TBAI1-2(A/B) | C4/C4S5 | TYP-AI-01 / 2-WIRE | READY FOR TEST | Pending Sign-off
10 | RV-60204 | IN-7 | - | 1x DI (Solenoid + FB) | 1 | P4-TBDI1-8 | C4/C4S1 | TYP-IS-01 / BARRIER | READY FOR TEST | Pending Sign-off
11 | TT-60224 | Gas and Powder Temperature Transmitter for Spray Chamber (CHAM-21) | 325-01-602-PD-04 | 1x AI | 1 | P4-TBAI1-3(A/B) | C4/C4S5 | TYP-AI-01 / 2-WIRE | READY FOR TEST | Pending Sign-off
12 | TT-60225 | Gas and Powder Temperature Transmitter for Spray Chamber (CHAM-21) | 325-01-602-PD-04 | 1x AI | 1 | P4-TBAI1-4(A/B) | C4/C4S5 | TYP-AI-01 / 2-WIRE | READY FOR TEST | Pending Sign-off
13 | TT-60226 | Gas and Powder Temperature Transmitter for Spray Chamber (CHAM-21) | 325-01-602-PD-04 | 1x AI | 1 | P4-TBAI1-5(A/B) | C4/C4S5 | TYP-AI-01 / 2-WIRE | READY FOR TEST | Pending Sign-off
14 | TT-60227 | Gas and Powder Temperature Transmitter for Spray Chamber (CHAM-21) | 325-01-602-PD-04 | 1x AI | 1 | P4-TBAI1-6(A/B) | C4/C4S5 | TYP-AI-01 / 2-WIRE | READY FOR TEST | Pending Sign-off
15 | TT-60230 | Gas and Powder Temperature Transmitter for Conveying Duct (DTCO-21) | 325-01-602-PD-04 | 1x AI | 1 | P4-TBAI1-7(A/B) | C4/C4S5 | TYP-AI-01 / 2-WIRE | READY FOR TEST | Pending Sign-off
16 | ZS-60201C | Limit Switch for CHAM-21 (Spray Chamber) | 325-01-602-PD-04 | 1x DI | 1 | P4-TBDI1-9 | C4/C4S1 | TYP-IS-01 / BARRIER | READY FOR TEST | Pending Sign-off
17 | ZS-60201D | Limit Switch for CHAM-21 (Spray Chamber) | 325-01-602-PD-04 | 1x DI | 1 | P4-TBDI1-10 | C4/C4S1 | TYP-IS-01 / BARRIER | READY FOR TEST | Pending Sign-off
18 | ZS-60201E | Limit Switch for CHAM-21 (Spray Chamber) | 325-01-602-PD-04 | 1x DI | 1 | P4-TBDI1-11 | C4/C4S1 | TYP-IS-01 / BARRIER | READY FOR TEST | Pending Sign-off
19 | ZS-60229 | Limit Switch for CY-60230 (Door Service) | 325-01-602-PD-04 | 1x DI | 1 | P4-TBDI1-12 | C4/C4S1 | TYP-IS-01 / BARRIER | READY FOR TEST | Pending Sign-off
20 | ZS-60230 | Limit Switch for CY-60231 (Door Service) | 325-01-602-PD-04 | 1x DI | 1 | P4-TBDI1-13 | C4/C4S1 | TYP-IS-01 / BARRIER | READY FOR TEST | Pending Sign-off
21 | ZS-60231A | Gas Limit Switch for DTEX-21 (Bag House Face Spectacle Inserted) | 325-01-602-PD-05 | 1x DI | 1 | P4-TBDI1-14 | C4/C4S1 | TYP-IS-01 / BARRIER | READY FOR TEST | Pending Sign-off
22 | ZS-60231B | Gas Limit Switch for DTEX-21 (Bag House Face Blind Inserted) | 325-01-602-PD-05 | 1x DI | 1 | P4-TBDI1-15 | C4/C4S1 | TYP-IS-01 / BARRIER | READY FOR TEST | Pending Sign-off

Sheet: AT-40201
KALASIN ENGINEERING | INSTRUMENT LOOP TEST & CALIBRATION CERTIFICATE
Equipment: AT-40201 | Junction Box: IS-JB-603 | Ref Std: IEC 62381 / ISA-RP60.8 (AI: 2-Pin Differential Channel)
1. EQUIPMENT IDENTIFICATION & PROCESS METADATA
Equipment Tag: | AT-40201 |  | P&ID Number: | 325-01-402-PD-01 |  | Junction Box: | IS-JB-603
Service Description: | Start / Stop Command for VSD AT-40201 |  | Calibrated Range: | On-Off |  | Channel Count: | 1 Active Process Channels
Instrument Type: | Field Process Equipment |  | Branch Cable Spec: | 1Px0.75mm² Shielded Instrumentation Cable |  | CAD Drawing Ref: | LOOP DIAGRAM WRING.dwg / dxf
2. FIELD WIRING & PLC I/O CHANNEL ALLOCATION (AI: 2-PIN DIFFERENTIAL PAIR)
CH # | Channel Function & Description | Type | PLC Tag Name | PLC Hardware Address | JB Terminal ID | Wire Tag (PLC Side) | Wire Tag (Field Side) | Core Wiring Colors
CH-01 | Discrete Input Status Contact (24VDC DI) - AT-40201_DI_1 | DI | AT-40201_DI_1 | C4/C4S1 1 | P4-TBDI1-1 | C4S1-1/P4-TBDI1-1 | P4-TBDI1-1/C4S1-1 | White (Sig), Grey (24VDC)
PWR | Instrument Auxiliary Power Supply (24VDC / 220VAC) | PWR | AT-40201_PWR | CA1 PSU1/2 Redundant Bus | IS-JB-603-TB24V / 0V | CA1-PSU-24V | AT-40201-V+ | Brown (+), Blue (-)
3. PHYSICAL INSPECTION & COLD LOOP INTEGRITY VERIFICATION
Cold Test Item | Acceptance Criteria | Core-to-Core | Core-to-Shield | Core-to-Earth | Shield-to-Earth | Measured Value | Test Status | Inspector Initials
Cable Insulation Resistance (Megger) | ≥ 20 MΩ @ 500VDC (1 min test) | ____ MΩ | ____ MΩ | ____ MΩ | ____ MΩ | > 100 MΩ | [ ] PASS | _______
Loop Conductor Resistance (Continuity) | ≤ 2.0 Ω end-to-end loop resistance | ____ Ω | - | - | - | 0.45 Ω | [ ] PASS | _______
Single-Point Earth Shielding | Isolated at Field; Single-point at CA1 IE | - | - | - | Isolated | CUTBACK & TAPE | [ ] PASS | _______
Enclosure, Gland & Tag Inspection | IP66/67 Gland tight, SS Tag Engraved | Engraved SS | Gland Tight | Drain Plug OK | O-ring Intact | Inspected | [ ] PASS | _______
4. LIVE SIGNAL CALIBRATION & FUNCTIONAL ACTUATION VERIFICATION
4.1 DISCRETE ACTUATION & FEEDBACK STATUS VERIFICATION
Signal Item | Command / State | Field Voltage / Contact | PLC Bit Status | SCADA Graphic State | Feedback Travel Angle | Response Time | Result | Remarks
Discrete Field Sensor | Normal Condition | 24.0 VDC / Contact Closed | Bit = 1 (Healthy) | Status Healthy (Green) | - | < 0.1 sec | [ ] PASS | Normal state confirmed
Discrete Field Sensor | Trip / Alarm Condition | 0.0 VDC / Contact Open | Bit = 0 (Tripped) | Status Alarm (Red Blink) | - | < 0.1 sec | [ ] PASS | Alarm latching confirmed
5. SAFETY INTERLOCK, EMERGENCY TRIP & SCADA ALARM RESPONSE
Safety Test Item | Trigger Condition | Expected Safe Action | SCADA Alarm Text | Priority / Class | Sounder Horn | Historian Log | Result | Remarks
Emergency Stop / Trip Interlock | E-Stop Pushbutton or SIS Trip | Fail-safe spring return to safe state | AT-40201 SAFETY SHUTDOWN | High (Priority 1) | Audible Active | Logged with ms | [ ] PASS | Hardwired trip verified
Out-of-Range Alarm | Signal <3.6mA or >21.0mA | Channel fault banner / Hold permissive | AT-40201 WIRE BREAK / FAULT | Medium (Priority 2) | Warning Tone | Logged with ms | [ ] PASS | NAMUR NE43 compliance
SCADA Alarm Acknowledge | Operator Acknowledge click | Banner silences horn, latches steady red | AT-40201 ALARM ACKNOWLEDGED | Low (Priority 3) | Silenced | Logged with ms | [ ] PASS | HMI banner functioning
6. TRIPARTITE COMMISSIONING ACCEPTANCE SIGN-OFF
Sign-off Role | Name & Designation | Company / Organization | Signature | Date Signed | Overall Verdict | Punchlist Ref | Tag Color Affixed | Remarks
Tested by (Contractor): | Lead Instrument Engineer | Kalasin Engineering Co., Ltd. | ___________________ | DD-MM-2026 | LOOP CHECK PASSED | None (Clean) | Green Loop Tag | Ready for Process Commissioning
Witnessed by (Client QC): | Senior Electrical & Inst QA/QC | Ingredion (Thailand) Co., Ltd. | ___________________ | DD-MM-2026 | ACCEPTED & APPROVED | None | QC Sticker Applied | Satisfies Contract Scope
Approved by (Commissioning PM): | Project Commissioning Manager | Kalasin / Ingredion Joint Team | ___________________ | DD-MM-2026 | FINAL AUTHORIZED | None | System Cleared | Authorized for Cold Water Wet Run

Sheet: AT-40202
KALASIN ENGINEERING | INSTRUMENT LOOP TEST & CALIBRATION CERTIFICATE
Equipment: AT-40202 | Junction Box: IS-JB-603 | Ref Std: IEC 62381 / ISA-RP60.8 (AI: 2-Pin Differential Channel)
1. EQUIPMENT IDENTIFICATION & PROCESS METADATA
Equipment Tag: | AT-40202 |  | P&ID Number: | 325-01-402-PD-01 |  | Junction Box: | IS-JB-603
Service Description: | Start / Stop Command for VSD AT-40202 |  | Calibrated Range: | On-Off |  | Channel Count: | 1 Active Process Channels
Instrument Type: | Field Process Equipment |  | Branch Cable Spec: | 1Px0.75mm² Shielded Instrumentation Cable |  | CAD Drawing Ref: | LOOP DIAGRAM WRING.dwg / dxf
2. FIELD WIRING & PLC I/O CHANNEL ALLOCATION (AI: 2-PIN DIFFERENTIAL PAIR)
CH # | Channel Function & Description | Type | PLC Tag Name | PLC Hardware Address | JB Terminal ID | Wire Tag (PLC Side) | Wire Tag (Field Side) | Core Wiring Colors
CH-01 | Discrete Input Status Contact (24VDC DI) - AT-40202_DI_1 | DI | AT-40202_DI_1 | C4/C4S1 2 | P4-TBDI1-2 | C4S1-2/P4-TBDI1-2 | P4-TBDI1-2/C4S1-2 | White (Sig), Grey (24VDC)
PWR | Instrument Auxiliary Power Supply (24VDC / 220VAC) | PWR | AT-40202_PWR | CA1 PSU1/2 Redundant Bus | IS-JB-603-TB24V / 0V | CA1-PSU-24V | AT-40202-V+ | Brown (+), Blue (-)
3. PHYSICAL INSPECTION & COLD LOOP INTEGRITY VERIFICATION
Cold Test Item | Acceptance Criteria | Core-to-Core | Core-to-Shield | Core-to-Earth | Shield-to-Earth | Measured Value | Test Status | Inspector Initials
Cable Insulation Resistance (Megger) | ≥ 20 MΩ @ 500VDC (1 min test) | ____ MΩ | ____ MΩ | ____ MΩ | ____ MΩ | > 100 MΩ | [ ] PASS | _______
Loop Conductor Resistance (Continuity) | ≤ 2.0 Ω end-to-end loop resistance | ____ Ω | - | - | - | 0.45 Ω | [ ] PASS | _______
Single-Point Earth Shielding | Isolated at Field; Single-point at CA1 IE | - | - | - | Isolated | CUTBACK & TAPE | [ ] PASS | _______
Enclosure, Gland & Tag Inspection | IP66/67 Gland tight, SS Tag Engraved | Engraved SS | Gland Tight | Drain Plug OK | O-ring Intact | Inspected | [ ] PASS | _______
4. LIVE SIGNAL CALIBRATION & FUNCTIONAL ACTUATION VERIFICATION
4.1 DISCRETE ACTUATION & FEEDBACK STATUS VERIFICATION
Signal Item | Command / State | Field Voltage / Contact | PLC Bit Status | SCADA Graphic State | Feedback Travel Angle | Response Time | Result | Remarks
Discrete Field Sensor | Normal Condition | 24.0 VDC / Contact Closed | Bit = 1 (Healthy) | Status Healthy (Green) | - | < 0.1 sec | [ ] PASS | Normal state confirmed
Discrete Field Sensor | Trip / Alarm Condition | 0.0 VDC / Contact Open | Bit = 0 (Tripped) | Status Alarm (Red Blink) | - | < 0.1 sec | [ ] PASS | Alarm latching confirmed
5. SAFETY INTERLOCK, EMERGENCY TRIP & SCADA ALARM RESPONSE
Safety Test Item | Trigger Condition | Expected Safe Action | SCADA Alarm Text | Priority / Class | Sounder Horn | Historian Log | Result | Remarks
Emergency Stop / Trip Interlock | E-Stop Pushbutton or SIS Trip | Fail-safe spring return to safe state | AT-40202 SAFETY SHUTDOWN | High (Priority 1) | Audible Active | Logged with ms | [ ] PASS | Hardwired trip verified
Out-of-Range Alarm | Signal <3.6mA or >21.0mA | Channel fault banner / Hold permissive | AT-40202 WIRE BREAK / FAULT | Medium (Priority 2) | Warning Tone | Logged with ms | [ ] PASS | NAMUR NE43 compliance
SCADA Alarm Acknowledge | Operator Acknowledge click | Banner silences horn, latches steady red | AT-40202 ALARM ACKNOWLEDGED | Low (Priority 3) | Silenced | Logged with ms | [ ] PASS | HMI banner functioning
6. TRIPARTITE COMMISSIONING ACCEPTANCE SIGN-OFF
Sign-off Role | Name & Designation | Company / Organization | Signature | Date Signed | Overall Verdict | Punchlist Ref | Tag Color Affixed | Remarks
Tested by (Contractor): | Lead Instrument Engineer | Kalasin Engineering Co., Ltd. | ___________________ | DD-MM-2026 | LOOP CHECK PASSED | None (Clean) | Green Loop Tag | Ready for Process Commissioning
Witnessed by (Client QC): | Senior Electrical & Inst QA/QC | Ingredion (Thailand) Co., Ltd. | ___________________ | DD-MM-2026 | ACCEPTED & APPROVED | None | QC Sticker Applied | Satisfies Contract Scope
Approved by (Commissioning PM): | Project Commissioning Manager | Kalasin / Ingredion Joint Team | ___________________ | DD-MM-2026 | FINAL AUTHORIZED | None | System Cleared | Authorized for Cold Water Wet Run

Sheet: AT-40203
KALASIN ENGINEERING | INSTRUMENT LOOP TEST & CALIBRATION CERTIFICATE
Equipment: AT-40203 | Junction Box: IS-JB-603 | Ref Std: IEC 62381 / ISA-RP60.8 (AI: 2-Pin Differential Channel)
1. EQUIPMENT IDENTIFICATION & PROCESS METADATA
Equipment Tag: | AT-40203 |  | P&ID Number: | 325-01-402-PD-02 |  | Junction Box: | IS-JB-603
Service Description: | Start / Stop Command for VSD AT-40203 |  | Calibrated Range: | On-Off |  | Channel Count: | 1 Active Process Channels
Instrument Type: | Field Process Equipment |  | Branch Cable Spec: | 1Px0.75mm² Shielded Instrumentation Cable |  | CAD Drawing Ref: | LOOP DIAGRAM WRING.dwg / dxf
2. FIELD WIRING & PLC I/O CHANNEL ALLOCATION (AI: 2-PIN DIFFERENTIAL PAIR)
CH # | Channel Function & Description | Type | PLC Tag Name | PLC Hardware Address | JB Terminal ID | Wire Tag (PLC Side) | Wire Tag (Field Side) | Core Wiring Colors
CH-01 | Discrete Input Status Contact (24VDC DI) - AT-40203_DI_1 | DI | AT-40203_DI_1 | C4/C4S1 3 | P4-TBDI1-3 | C4S1-3/P4-TBDI1-3 | P4-TBDI1-3/C4S1-3 | White (Sig), Grey (24VDC)
PWR | Instrument Auxiliary Power Supply (24VDC / 220VAC) | PWR | AT-40203_PWR | CA1 PSU1/2 Redundant Bus | IS-JB-603-TB24V / 0V | CA1-PSU-24V | AT-40203-V+ | Brown (+), Blue (-)
3. PHYSICAL INSPECTION & COLD LOOP INTEGRITY VERIFICATION
Cold Test Item | Acceptance Criteria | Core-to-Core | Core-to-Shield | Core-to-Earth | Shield-to-Earth | Measured Value | Test Status | Inspector Initials
Cable Insulation Resistance (Megger) | ≥ 20 MΩ @ 500VDC (1 min test) | ____ MΩ | ____ MΩ | ____ MΩ | ____ MΩ | > 100 MΩ | [ ] PASS | _______
Loop Conductor Resistance (Continuity) | ≤ 2.0 Ω end-to-end loop resistance | ____ Ω | - | - | - | 0.45 Ω | [ ] PASS | _______
Single-Point Earth Shielding | Isolated at Field; Single-point at CA1 IE | - | - | - | Isolated | CUTBACK & TAPE | [ ] PASS | _______
Enclosure, Gland & Tag Inspection | IP66/67 Gland tight, SS Tag Engraved | Engraved SS | Gland Tight | Drain Plug OK | O-ring Intact | Inspected | [ ] PASS | _______
4. LIVE SIGNAL CALIBRATION & FUNCTIONAL ACTUATION VERIFICATION
4.1 DISCRETE ACTUATION & FEEDBACK STATUS VERIFICATION
Signal Item | Command / State | Field Voltage / Contact | PLC Bit Status | SCADA Graphic State | Feedback Travel Angle | Response Time | Result | Remarks
Discrete Field Sensor | Normal Condition | 24.0 VDC / Contact Closed | Bit = 1 (Healthy) | Status Healthy (Green) | - | < 0.1 sec | [ ] PASS | Normal state confirmed
Discrete Field Sensor | Trip / Alarm Condition | 0.0 VDC / Contact Open | Bit = 0 (Tripped) | Status Alarm (Red Blink) | - | < 0.1 sec | [ ] PASS | Alarm latching confirmed
5. SAFETY INTERLOCK, EMERGENCY TRIP & SCADA ALARM RESPONSE
Safety Test Item | Trigger Condition | Expected Safe Action | SCADA Alarm Text | Priority / Class | Sounder Horn | Historian Log | Result | Remarks
Emergency Stop / Trip Interlock | E-Stop Pushbutton or SIS Trip | Fail-safe spring return to safe state | AT-40203 SAFETY SHUTDOWN | High (Priority 1) | Audible Active | Logged with ms | [ ] PASS | Hardwired trip verified
Out-of-Range Alarm | Signal <3.6mA or >21.0mA | Channel fault banner / Hold permissive | AT-40203 WIRE BREAK / FAULT | Medium (Priority 2) | Warning Tone | Logged with ms | [ ] PASS | NAMUR NE43 compliance
SCADA Alarm Acknowledge | Operator Acknowledge click | Banner silences horn, latches steady red | AT-40203 ALARM ACKNOWLEDGED | Low (Priority 3) | Silenced | Logged with ms | [ ] PASS | HMI banner functioning
6. TRIPARTITE COMMISSIONING ACCEPTANCE SIGN-OFF
Sign-off Role | Name & Designation | Company / Organization | Signature | Date Signed | Overall Verdict | Punchlist Ref | Tag Color Affixed | Remarks
Tested by (Contractor): | Lead Instrument Engineer | Kalasin Engineering Co., Ltd. | ___________________ | DD-MM-2026 | LOOP CHECK PASSED | None (Clean) | Green Loop Tag | Ready for Process Commissioning
Witnessed by (Client QC): | Senior Electrical & Inst QA/QC | Ingredion (Thailand) Co., Ltd. | ___________________ | DD-MM-2026 | ACCEPTED & APPROVED | None | QC Sticker Applied | Satisfies Contract Scope
Approved by (Commissioning PM): | Project Commissioning Manager | Kalasin / Ingredion Joint Team | ___________________ | DD-MM-2026 | FINAL AUTHORIZED | None | System Cleared | Authorized for Cold Water Wet Run

Sheet: LSH-60230
KALASIN ENGINEERING | INSTRUMENT LOOP TEST & CALIBRATION CERTIFICATE
Equipment: LSH-60230 | Junction Box: IS-JB-603 | Ref Std: IEC 62381 / ISA-RP60.8 (AI: 2-Pin Differential Channel)
1. EQUIPMENT IDENTIFICATION & PROCESS METADATA
Equipment Tag: | LSH-60230 |  | P&ID Number: | 325-01-602-PD-04 |  | Junction Box: | IS-JB-603
Service Description: | Powder Level Switch High for Cyclone (CYCL-21) |  | Calibrated Range: | 0 - 100% |  | Channel Count: | 1 Active Process Channels
Instrument Type: | Level switch |  | Branch Cable Spec: | 1Px0.75mm² Shielded Instrumentation Cable |  | CAD Drawing Ref: | LOOP DIAGRAM WRING.dwg / dxf
2. FIELD WIRING & PLC I/O CHANNEL ALLOCATION (AI: 2-PIN DIFFERENTIAL PAIR)
CH # | Channel Function & Description | Type | PLC Tag Name | PLC Hardware Address | JB Terminal ID | Wire Tag (PLC Side) | Wire Tag (Field Side) | Core Wiring Colors
CH-01 | Liquid / Powder Level Switch Trip Status (DI) | DI | LSH-60230_DI_1 | C4/C4S1 4 | P4-TBDI1-4 | C4S1-4/P4-TBDI1-4 | P4-TBDI1-4/C4S1-4 | White (Sig), Grey (24VDC)
3. PHYSICAL INSPECTION & COLD LOOP INTEGRITY VERIFICATION
Cold Test Item | Acceptance Criteria | Core-to-Core | Core-to-Shield | Core-to-Earth | Shield-to-Earth | Measured Value | Test Status | Inspector Initials
Cable Insulation Resistance (Megger) | ≥ 20 MΩ @ 500VDC (1 min test) | ____ MΩ | ____ MΩ | ____ MΩ | ____ MΩ | > 100 MΩ | [ ] PASS | _______
Loop Conductor Resistance (Continuity) | ≤ 2.0 Ω end-to-end loop resistance | ____ Ω | - | - | - | 0.45 Ω | [ ] PASS | _______
Single-Point Earth Shielding | Isolated at Field; Single-point at CA1 IE | - | - | - | Isolated | CUTBACK & TAPE | [ ] PASS | _______
Enclosure, Gland & Tag Inspection | IP66/67 Gland tight, SS Tag Engraved | Engraved SS | Gland Tight | Drain Plug OK | O-ring Intact | Inspected | [ ] PASS | _______
4. LIVE SIGNAL CALIBRATION & FUNCTIONAL ACTUATION VERIFICATION
4.1 DISCRETE ACTUATION & FEEDBACK STATUS VERIFICATION
Signal Item | Command / State | Field Voltage / Contact | PLC Bit Status | SCADA Graphic State | Feedback Travel Angle | Response Time | Result | Remarks
Discrete Field Sensor | Normal Condition | 24.0 VDC / Contact Closed | Bit = 1 (Healthy) | Status Healthy (Green) | - | < 0.1 sec | [ ] PASS | Normal state confirmed
Discrete Field Sensor | Trip / Alarm Condition | 0.0 VDC / Contact Open | Bit = 0 (Tripped) | Status Alarm (Red Blink) | - | < 0.1 sec | [ ] PASS | Alarm latching confirmed
5. SAFETY INTERLOCK, EMERGENCY TRIP & SCADA ALARM RESPONSE
Safety Test Item | Trigger Condition | Expected Safe Action | SCADA Alarm Text | Priority / Class | Sounder Horn | Historian Log | Result | Remarks
Emergency Stop / Trip Interlock | E-Stop Pushbutton or SIS Trip | Fail-safe spring return to safe state | LSH-60230 SAFETY SHUTDOWN | High (Priority 1) | Audible Active | Logged with ms | [ ] PASS | Hardwired trip verified
Out-of-Range Alarm | Signal <3.6mA or >21.0mA | Channel fault banner / Hold permissive | LSH-60230 WIRE BREAK / FAULT | Medium (Priority 2) | Warning Tone | Logged with ms | [ ] PASS | NAMUR NE43 compliance
SCADA Alarm Acknowledge | Operator Acknowledge click | Banner silences horn, latches steady red | LSH-60230 ALARM ACKNOWLEDGED | Low (Priority 3) | Silenced | Logged with ms | [ ] PASS | HMI banner functioning
6. TRIPARTITE COMMISSIONING ACCEPTANCE SIGN-OFF
Sign-off Role | Name & Designation | Company / Organization | Signature | Date Signed | Overall Verdict | Punchlist Ref | Tag Color Affixed | Remarks
Tested by (Contractor): | Lead Instrument Engineer | Kalasin Engineering Co., Ltd. | ___________________ | DD-MM-2026 | LOOP CHECK PASSED | None (Clean) | Green Loop Tag | Ready for Process Commissioning
Witnessed by (Client QC): | Senior Electrical & Inst QA/QC | Ingredion (Thailand) Co., Ltd. | ___________________ | DD-MM-2026 | ACCEPTED & APPROVED | None | QC Sticker Applied | Satisfies Contract Scope
Approved by (Commissioning PM): | Project Commissioning Manager | Kalasin / Ingredion Joint Team | ___________________ | DD-MM-2026 | FINAL AUTHORIZED | None | System Cleared | Authorized for Cold Water Wet Run

Sheet: LSH-60231
KALASIN ENGINEERING | INSTRUMENT LOOP TEST & CALIBRATION CERTIFICATE
Equipment: LSH-60231 | Junction Box: IS-JB-603 | Ref Std: IEC 62381 / ISA-RP60.8 (AI: 2-Pin Differential Channel)
1. EQUIPMENT IDENTIFICATION & PROCESS METADATA
Equipment Tag: | LSH-60231 |  | P&ID Number: | 325-01-602-PD-04 |  | Junction Box: | IS-JB-603
Service Description: | Powder Level Switch High for Cyclone (CYCL-22) |  | Calibrated Range: | 0 - 100% |  | Channel Count: | 1 Active Process Channels
Instrument Type: | Level switch |  | Branch Cable Spec: | 1Px0.75mm² Shielded Instrumentation Cable |  | CAD Drawing Ref: | LOOP DIAGRAM WRING.dwg / dxf
2. FIELD WIRING & PLC I/O CHANNEL ALLOCATION (AI: 2-PIN DIFFERENTIAL PAIR)
CH # | Channel Function & Description | Type | PLC Tag Name | PLC Hardware Address | JB Terminal ID | Wire Tag (PLC Side) | Wire Tag (Field Side) | Core Wiring Colors
CH-01 | Liquid / Powder Level Switch Trip Status (DI) | DI | LSH-60231_DI_1 | C4/C4S1 5 | P4-TBDI1-5 | C4S1-5/P4-TBDI1-5 | P4-TBDI1-5/C4S1-5 | White (Sig), Grey (24VDC)
3. PHYSICAL INSPECTION & COLD LOOP INTEGRITY VERIFICATION
Cold Test Item | Acceptance Criteria | Core-to-Core | Core-to-Shield | Core-to-Earth | Shield-to-Earth | Measured Value | Test Status | Inspector Initials
Cable Insulation Resistance (Megger) | ≥ 20 MΩ @ 500VDC (1 min test) | ____ MΩ | ____ MΩ | ____ MΩ | ____ MΩ | > 100 MΩ | [ ] PASS | _______
Loop Conductor Resistance (Continuity) | ≤ 2.0 Ω end-to-end loop resistance | ____ Ω | - | - | - | 0.45 Ω | [ ] PASS | _______
Single-Point Earth Shielding | Isolated at Field; Single-point at CA1 IE | - | - | - | Isolated | CUTBACK & TAPE | [ ] PASS | _______
Enclosure, Gland & Tag Inspection | IP66/67 Gland tight, SS Tag Engraved | Engraved SS | Gland Tight | Drain Plug OK | O-ring Intact | Inspected | [ ] PASS | _______
4. LIVE SIGNAL CALIBRATION & FUNCTIONAL ACTUATION VERIFICATION
4.1 DISCRETE ACTUATION & FEEDBACK STATUS VERIFICATION
Signal Item | Command / State | Field Voltage / Contact | PLC Bit Status | SCADA Graphic State | Feedback Travel Angle | Response Time | Result | Remarks
Discrete Field Sensor | Normal Condition | 24.0 VDC / Contact Closed | Bit = 1 (Healthy) | Status Healthy (Green) | - | < 0.1 sec | [ ] PASS | Normal state confirmed
Discrete Field Sensor | Trip / Alarm Condition | 0.0 VDC / Contact Open | Bit = 0 (Tripped) | Status Alarm (Red Blink) | - | < 0.1 sec | [ ] PASS | Alarm latching confirmed
5. SAFETY INTERLOCK, EMERGENCY TRIP & SCADA ALARM RESPONSE
Safety Test Item | Trigger Condition | Expected Safe Action | SCADA Alarm Text | Priority / Class | Sounder Horn | Historian Log | Result | Remarks
Emergency Stop / Trip Interlock | E-Stop Pushbutton or SIS Trip | Fail-safe spring return to safe state | LSH-60231 SAFETY SHUTDOWN | High (Priority 1) | Audible Active | Logged with ms | [ ] PASS | Hardwired trip verified
Out-of-Range Alarm | Signal <3.6mA or >21.0mA | Channel fault banner / Hold permissive | LSH-60231 WIRE BREAK / FAULT | Medium (Priority 2) | Warning Tone | Logged with ms | [ ] PASS | NAMUR NE43 compliance
SCADA Alarm Acknowledge | Operator Acknowledge click | Banner silences horn, latches steady red | LSH-60231 ALARM ACKNOWLEDGED | Low (Priority 3) | Silenced | Logged with ms | [ ] PASS | HMI banner functioning
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
