x92120/x260911-002-KalasinEngineering/05-LoopTest/Loop_Test_Report_IS-JB-608.xlsx

Sheet: 00_JB_Index
KALASIN ENGINEERING | JUNCTION BOX LOOP TEST REGISTER: IS-JB-608
Project Sprint 18K TPA Spray Dryer / Jet Cooker | Location: IS-JB-608 | 1 Equipment = 1 Sheet
TOTAL EQUIPMENT |  | TOTAL ACTIVE CHANNELS |  | DIGITAL INPUT (DI) |  | DIGITAL OUTPUT (DO) |  | ANALOG IN/OUT (AI/AO)
14 Units |  | 14 Channels |  | 7 Pts |  | 1 Pts |  | 6 AI / 0 AO
Item # | Equipment Tag | Equipment Service Description | P&ID Drawing No. | Primary Signal Breakdown | Total Channels | Primary JB Terminal | PLC Rack / Slot | CAD Wiring Typical | Loop Test Status | QA/QC Sign-off & Date
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
