x92120/x260911-002-KalasinEngineering/02_Electrical_and_eDrawing/Panel_Layout/TAMCO_CRS_Series/Drawings_DXF/CRS-03-Layout.dxf

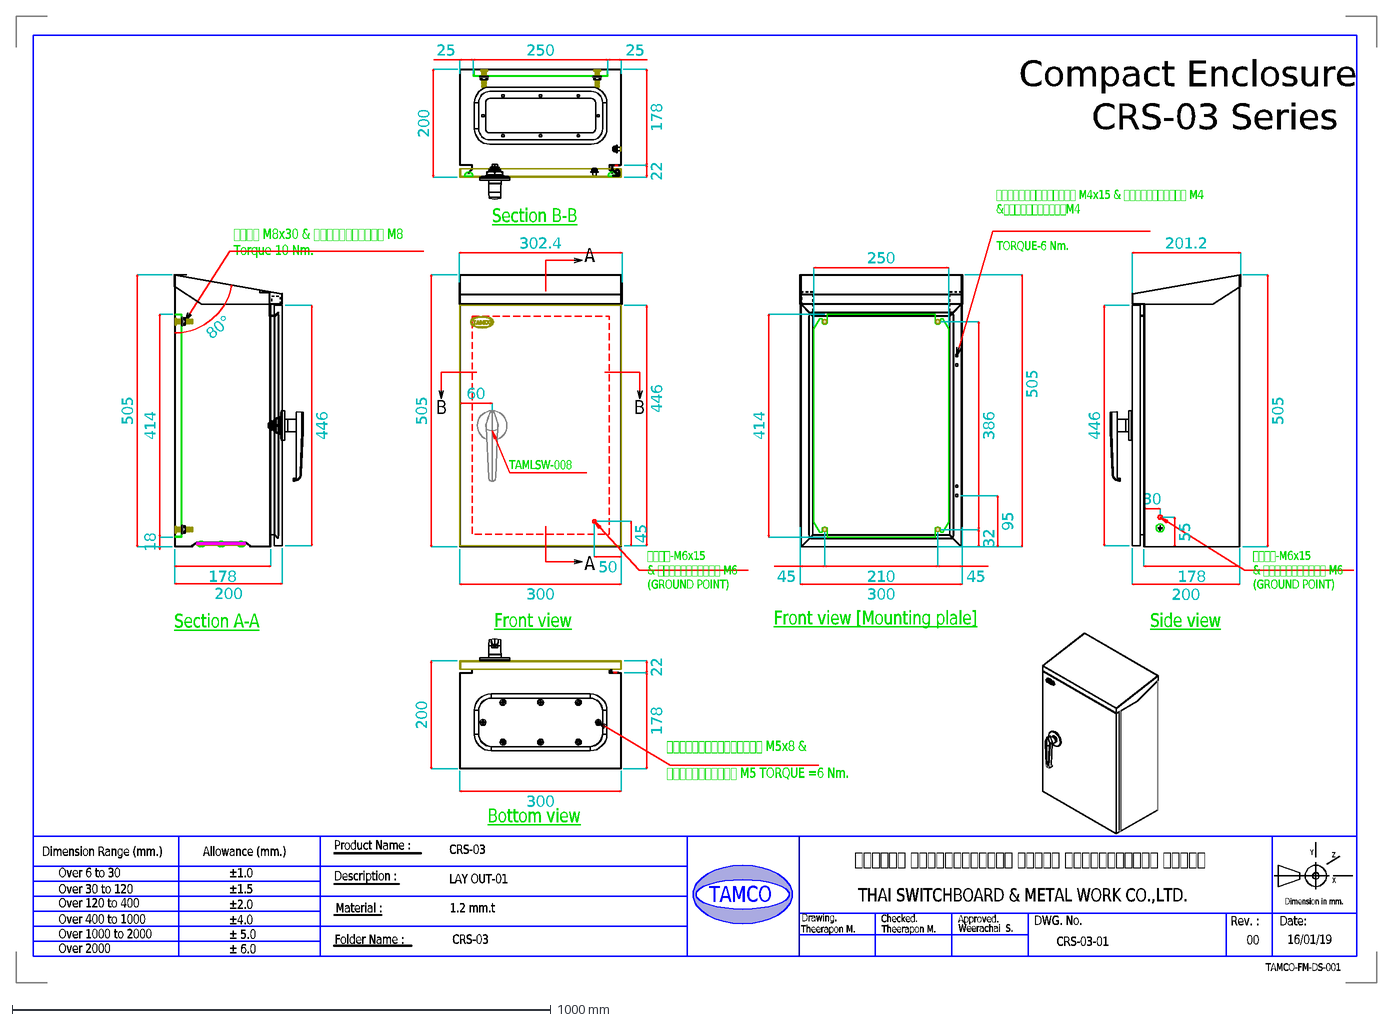
[picture p95: CAD file, 2026-10-07]
02_Electrical_and_eDrawing/Panel_Layout/TAMCO_CRS_Series/Drawings_DXF/CRS-03-Layout.dxf
DWG. No.
THAI SWITCHBOARD & METAL WORK CO.,LTD.
Checked.
Approved.
16/01/19
Date:
Drawing.
Product Name :
Description :
Material :
Folder Name :
Rev. :
00
TAMCO-FM-DS-001
CRS-03-01
1.2 mm.t
CRS-03
Theerapon M.
Weerachai S.
LAY OUT-01
Dimension Range (mm.)
Over 6 to 30
Over 30 to 120
Over 120 to 400
Over 400 to 1000
Over 1000 to 2000
Over 2000
Allowance (mm.)
±1.5
±1.0
±2.0
±4.0
± 5.0
± 6.0
TAMCO
Z
X
Y
Dimension in mm.
Compact Enclosure
CRS-03 Series
200
505
201.2
60
TAMLSW-008
446
300
178
18
414
302.4
250
386
32
45
210
A
B
50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
