x92120/x260911-002-KalasinEngineering/Panel_Layout/Panel_Layout_JB-612.dxf

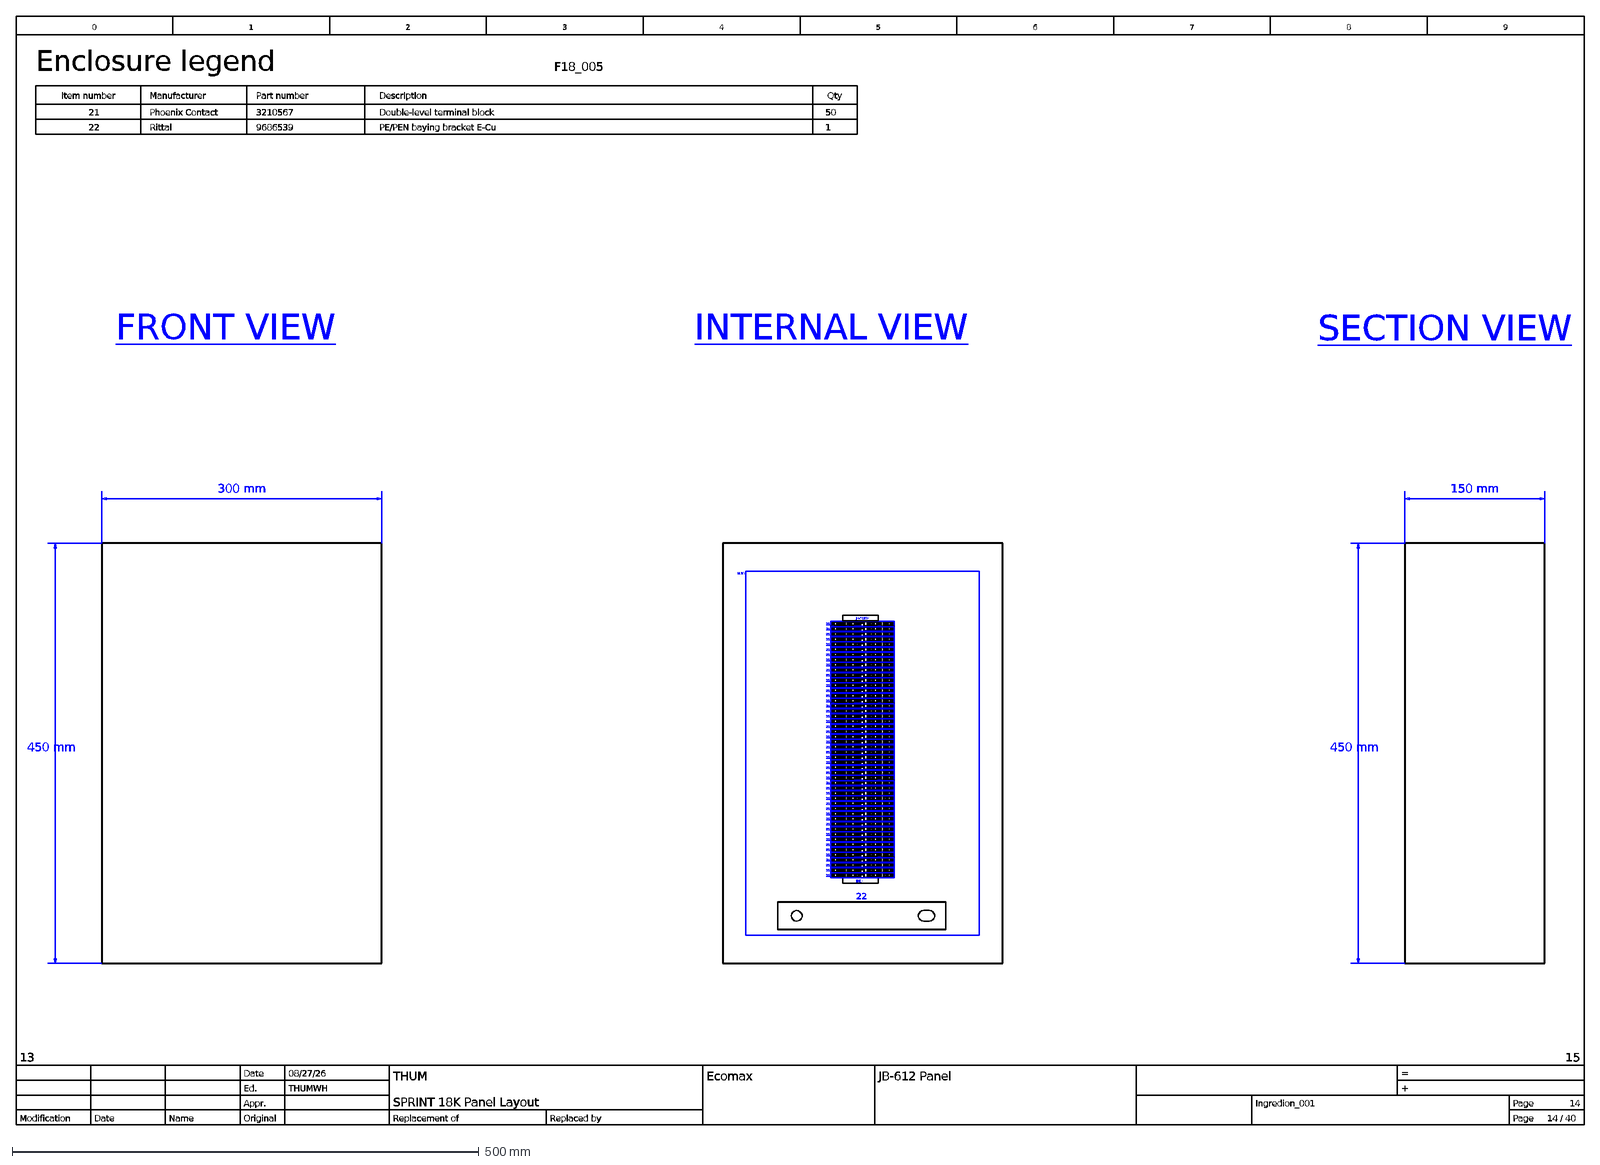
[picture p97: CAD file, 2026-10-07]
Panel_Layout/Panel_Layout_JB-612.dxf
SPRINT 18K Panel Layout
13
Ingredion_001
THUM
THUMWH
JB-612 Panel
1
0
7
6
8
9
3
40
15
4
08/27/26
Ecomax
14
2
5
Page
Ed.
Original
+
Date
Replaced by
Modification
Appr.
Replacement of
=
Name
/
Enclosure legend
F18_005
Part number
Manufacturer
Item number
Qty
Description
Phoenix Contact
3210567
21
50
Double-level terminal block
Rittal
9686539
22
PE/PEN baying bracket E-Cu
END
450 mm
300 mm
150 mm
FRONT VIEW
INTERNAL VIEW
SECTION VIEW
JB-612TB
M.30
