x92120/x260911-002-KalasinEngineering/Panel_Layout/Panel_Legends_and_BOM/Sheet_25_Summarized_Parts_List_BOM.dxf

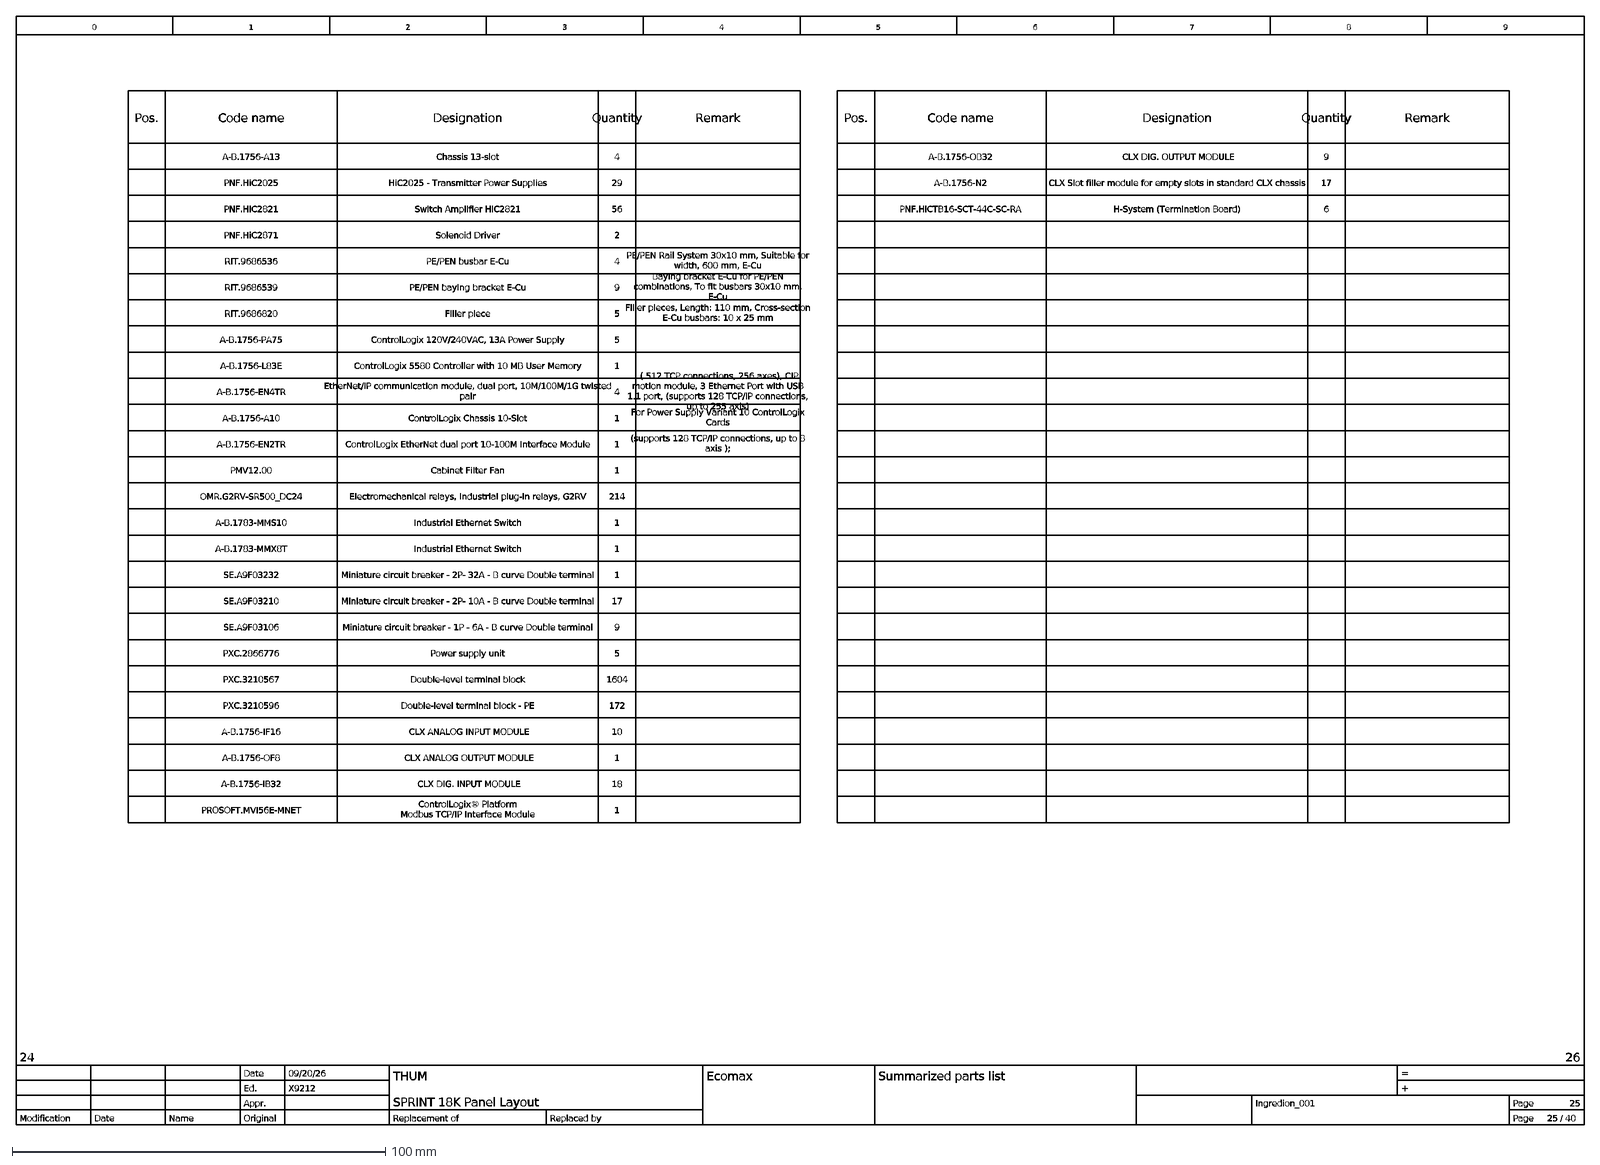
[picture p98: CAD file, 2026-10-07]
Panel_Layout/Panel_Legends_and_BOM/Sheet_25_Summarized_Parts_List_BOM.dxf
Designation
Quantity
Remark
Pos.
Code name
SPRINT 18K Panel Layout
24
Ingredion_001
THUM
X9212
Summarized parts list
1
0
7
6
8
9
3
40
26
4
09/20/26
Ecomax
25
2
5
Page
Ed.
Original
+
Date
Replaced by
Modification
Appr.
Replacement of
=
Name
/
Chassis 13-slot
A-B.1756-A13
HiC2025 - Transmitter Power Supplies
PNF.HiC2025
29
Switch Amplifier HiC2821
PNF.HiC2821
56
Solenoid Driver
PNF.HiC2871
PE/PEN busbar E-Cu
RIT.9686536
PE/PEN Rail System 30x10 mm, Suitable for width, 600 mm, E-Cu
PE/PEN baying bracket E-Cu
RIT.9686539
Filler piece
RIT.9686820
ControlLogix 120V/240VAC, 13A Power Supply
A-B.1756-PA75
ControlLogix 5580 Controller with 10 MB User Memory
A-B.1756-L83E
EtherNet/IP communication module, dual port, 10M/100M/1G twisted pair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
