x92120/x260911-002-KalasinEngineering/Panel_Layout/TAMCO_CES_Stainless_Series/Drawings_DXF/CES-STL-12-Layout.dxf

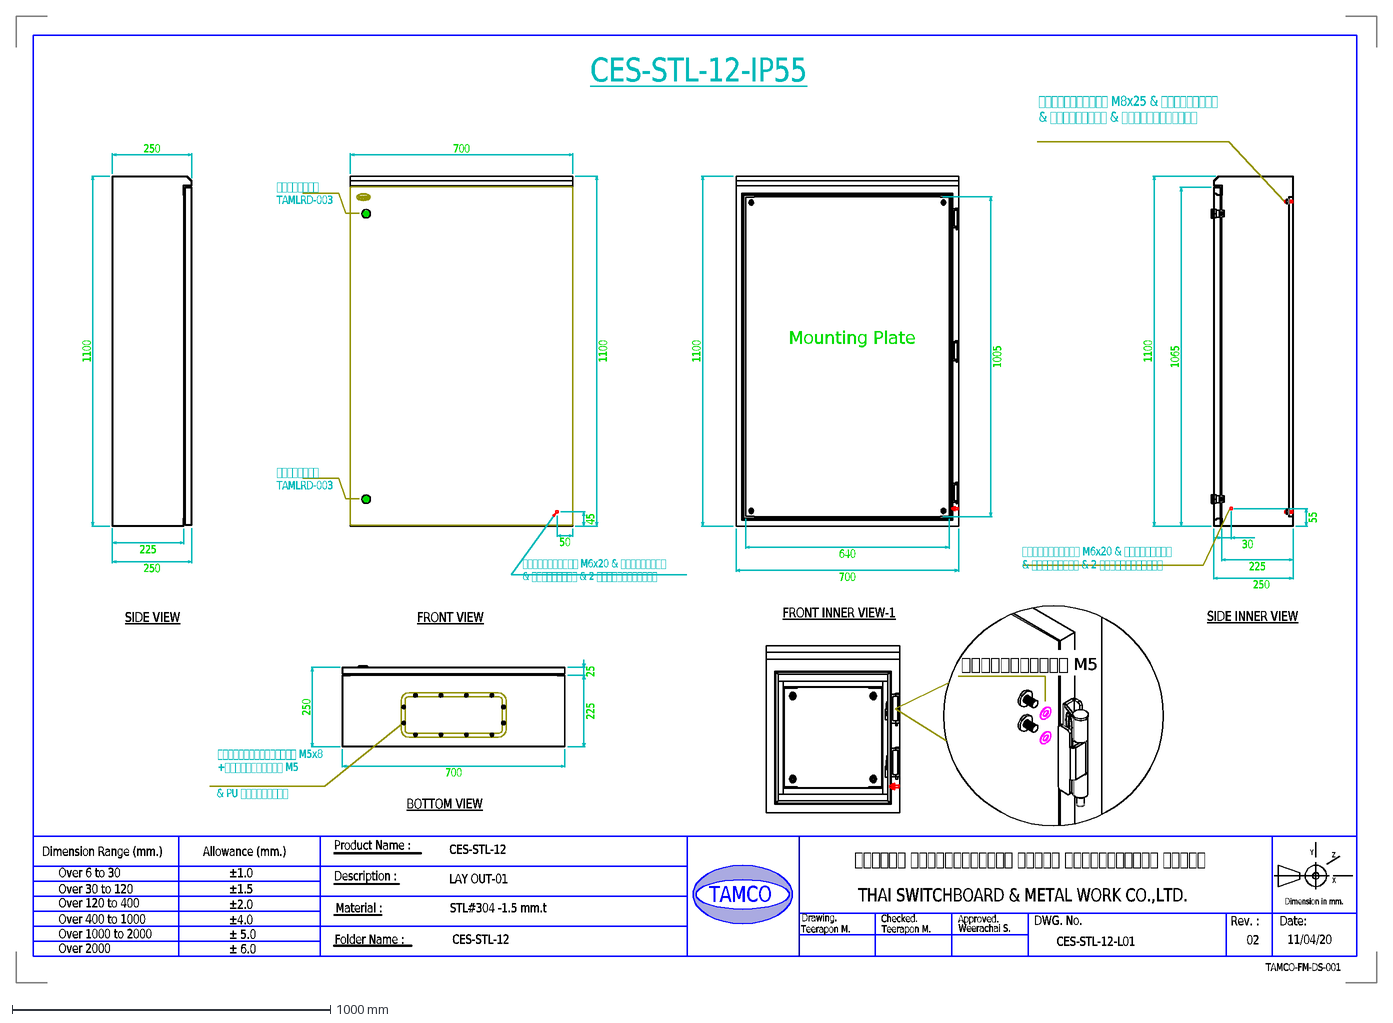
[picture p99: CAD file, 2026-10-07]
Panel_Layout/TAMCO_CES_Stainless_Series/Drawings_DXF/CES-STL-12-Layout.dxf
DWG. No.
THAI SWITCHBOARD & METAL WORK CO.,LTD.
Checked.
Approved.
Date:
Drawing.
Product Name :
Description :
Material :
Folder Name :
Rev. :
TAMCO-FM-DS-001
CES-STL-12
Weerachai S.
LAY OUT-01
Dimension Range (mm.)
Over 6 to 30
Over 30 to 120
Over 120 to 400
Over 400 to 1000
Over 1000 to 2000
Over 2000
Allowance (mm.)
±1.5
±1.0
±2.0
±4.0
± 5.0
± 6.0
TAMCO
Teerapon M.
Z
X
Y
Dimension in mm.
11/04/20
02
CES-STL-12-L01
STL#304 -1.5 mm.t
CES-STL-12-IP55
1100
250
225
25
700
1065
SIDE VIEW
FRONT VIEW
SIDE INNER VIEW
BOTTOM VIEW
55
30
FRONT INNER VIEW-1
Mounting Plate
640
1005
50
45
