x92120/x260911-002-KalasinEngineering/02_Electrical_and_eDrawing/02_ePlan_Exports/SPRINT 18K SPRAY DRYER/1.dxf

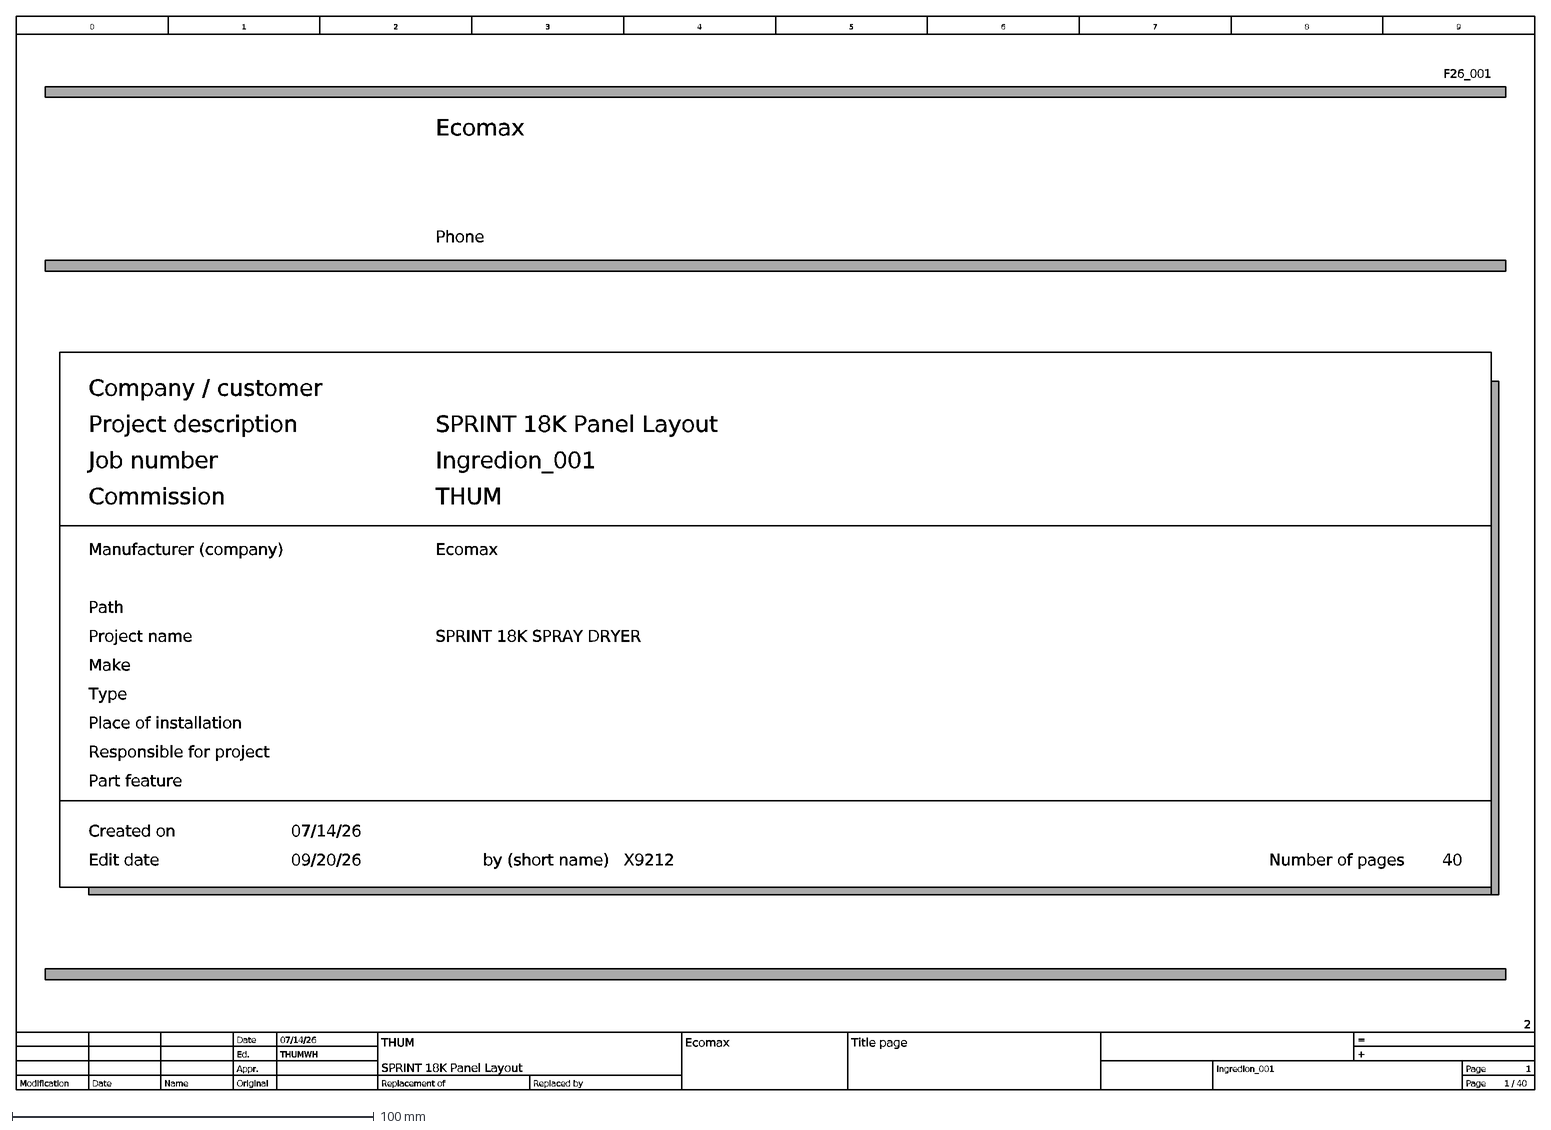
[picture p100: CAD file, 2026-10-07]
02_Electrical_and_eDrawing/02_ePlan_Exports/SPRINT 18K SPRAY DRYER/1.dxf
Ecomax
SPRINT 18K Panel Layout
07/14/26
Ingredion_001
40
F26_001
X9212
SPRINT 18K SPRAY DRYER
09/20/26
THUM
Project description
Number of pages
Commission
Edit date
Created on
Job number
Make
Part feature
Path
Manufacturer (company)
Project name
Responsible for project
Phone
Type
Company / customer
Place of installation
by (short name)
THUMWH
Title page
1
0
7
6
8
9
3
2
4
5
Page
Ed.
Original
+
Date
Replaced by
Modification
Appr.
Replacement of
=
Name
/
