x92120/x260911-002-KalasinEngineering/02_Electrical_and_eDrawing/03_CAD_Exports_DXF_SVG/01_PLC_IO_Wiring_DXF/KAL-JC-WIR-00002_Sheet02_Index.dxf

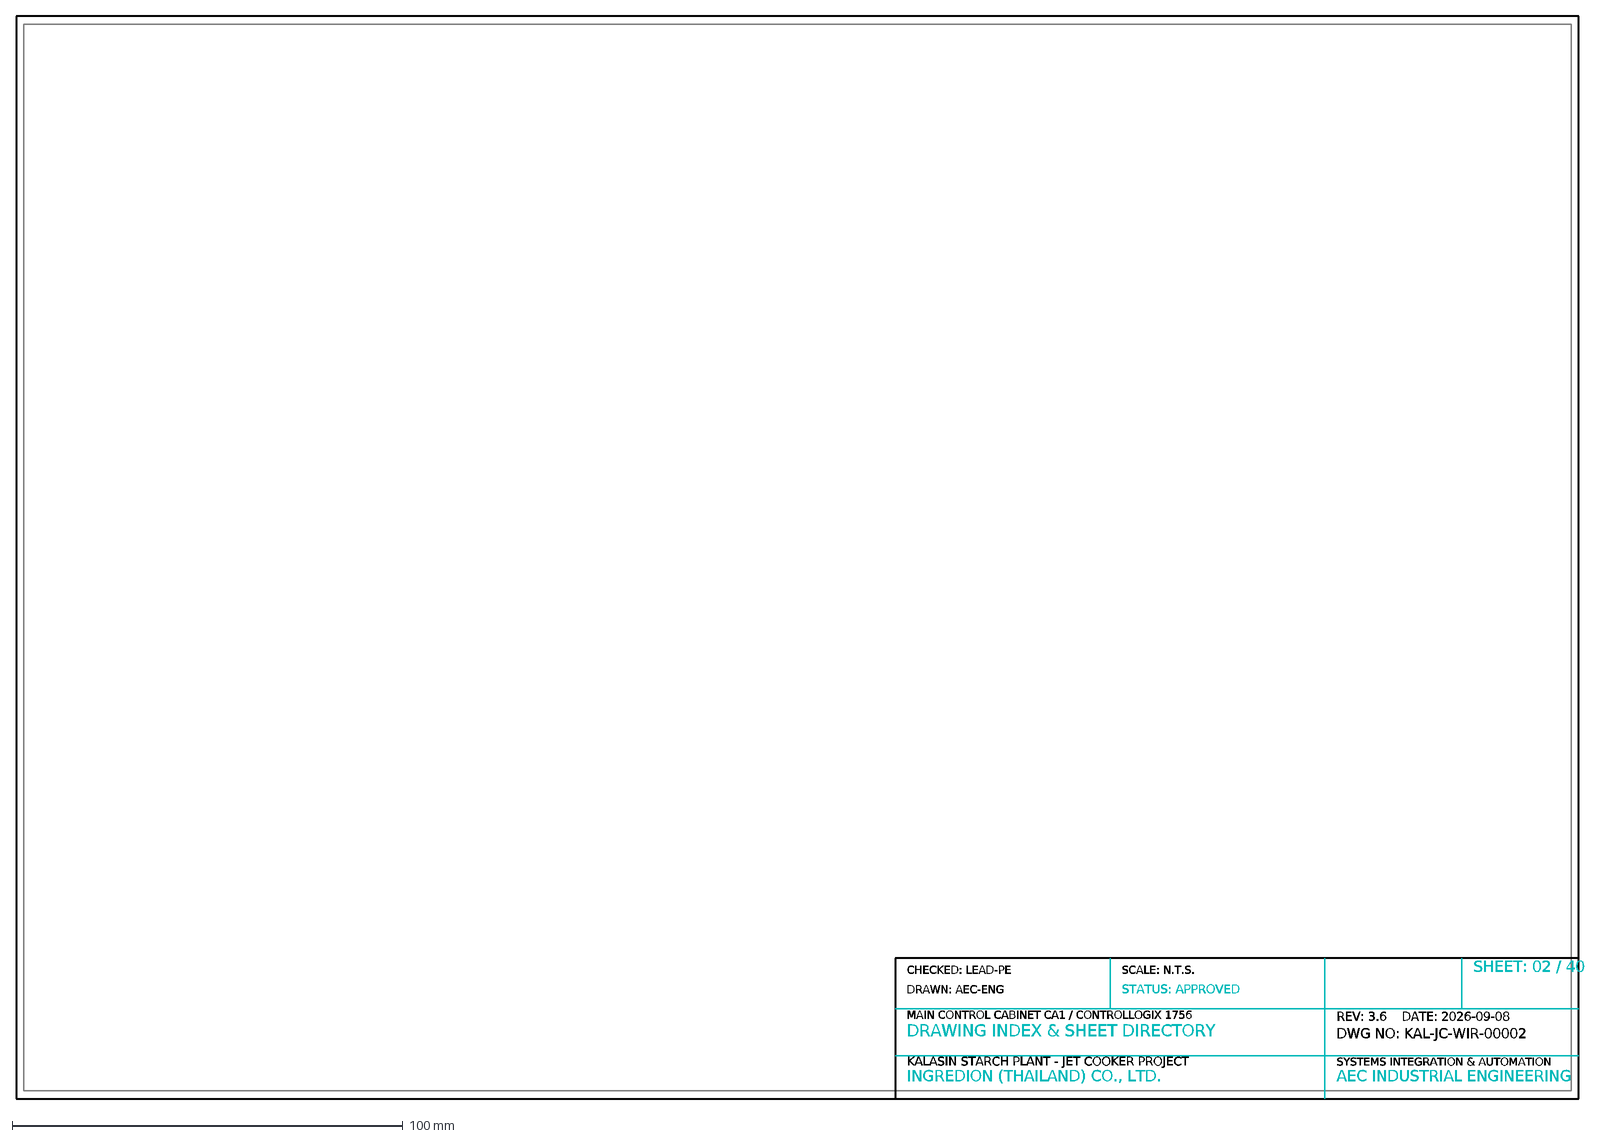
[picture p101: CAD file, 2026-09-29]
02_Electrical_and_eDrawing/03_CAD_Exports_DXF_SVG/01_PLC_IO_Wiring_DXF/KAL-JC-WIR-00002_Sheet02_Index.dxf
INGREDION (THAILAND) CO., LTD.
KALASIN STARCH PLANT - JET COOKER PROJECT
AEC INDUSTRIAL ENGINEERING
SYSTEMS INTEGRATION & AUTOMATION
DRAWING INDEX & SHEET DIRECTORY
MAIN CONTROL CABINET CA1 / CONTROLLOGIX 1756
DWG NO: KAL-JC-WIR-00002
REV: 3.6 DATE: 2026-09-08
DRAWN: AEC-ENG
CHECKED: LEAD-PE
STATUS: APPROVED
SCALE: N.T.S.
SHEET: 02 / 40
