x92120/x260911-002-KalasinEngineering/02_Electrical_and_eDrawing/03_CAD_Exports_DXF_SVG/02_Instrument_Typical_DXF/KAL-JC-TYP-023_Sheet25_TYP-23_Pneumatic_Turbine_Vibrator.dxf

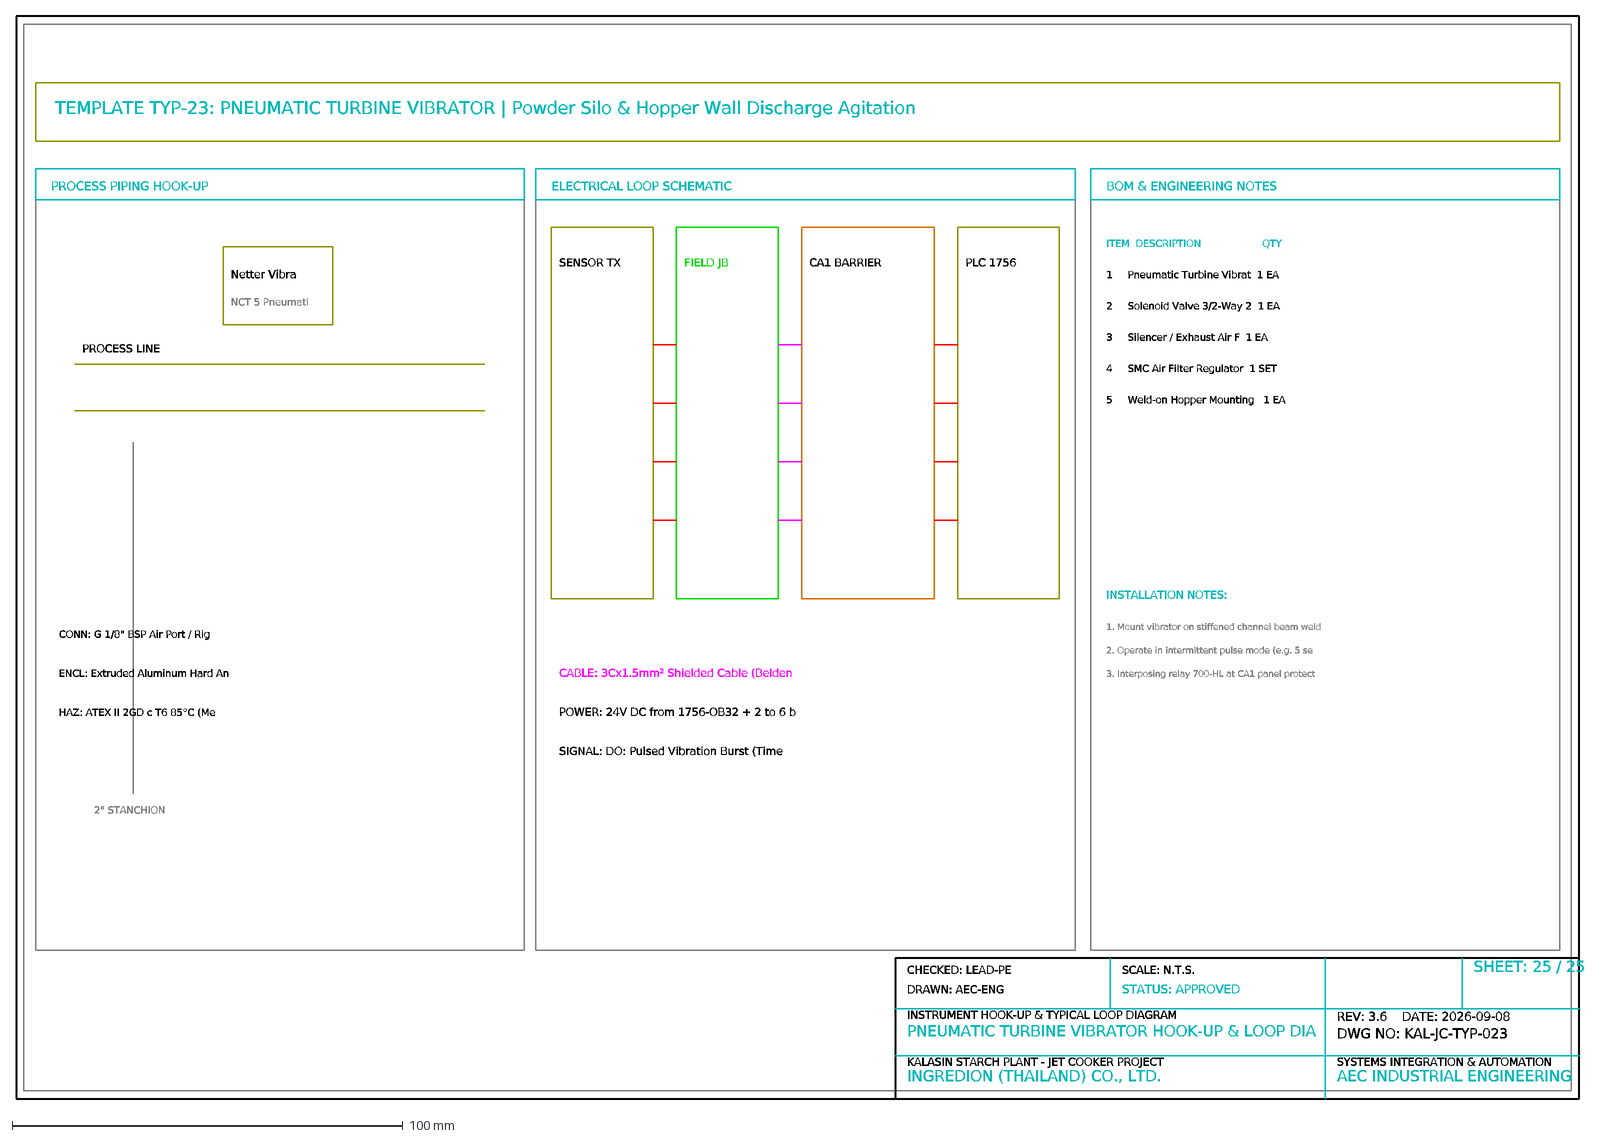
[picture p102: CAD file, 2026-09-29]
02_Electrical_and_eDrawing/03_CAD_Exports_DXF_SVG/02_Instrument_Typical_DXF/KAL-JC-TYP-023_Sheet25_TYP-23_Pneumatic_Turbine_Vibrator.dxf
INGREDION (THAILAND) CO., LTD.
KALASIN STARCH PLANT - JET COOKER PROJECT
AEC INDUSTRIAL ENGINEERING
SYSTEMS INTEGRATION & AUTOMATION
PNEUMATIC TURBINE VIBRATOR HOOK-UP & LOOP DIA
INSTRUMENT HOOK-UP & TYPICAL LOOP DIAGRAM
DWG NO: KAL-JC-TYP-023
REV: 3.6 DATE: 2026-09-08
DRAWN: AEC-ENG
CHECKED: LEAD-PE
STATUS: APPROVED
SCALE: N.T.S.
SHEET: 25 / 25
TEMPLATE TYP-23: PNEUMATIC TURBINE VIBRATOR | Powder Silo & Hopper Wall Discharge Agitation
PROCESS PIPING HOOK-UP
PROCESS LINE
Netter Vibra
NCT 5 Pneumati
2" STANCHION
CONN: G 1/8" BSP Air Port / Rig
ENCL: Extruded Aluminum Hard An
HAZ: ATEX II 2GD c T6 85°C (Me
ELECTRICAL LOOP SCHEMATIC
SENSOR TX
FIELD JB
CA1 BARRIER
PLC 1756
CABLE: 3Cx1.5mm² Shielded Cable (Belden
POWER: 24V DC from 1756-OB32 + 2 to 6 b
SIGNAL: DO: Pulsed Vibration Burst (Time
BOM & ENGINEERING NOTES
ITEM DESCRIPTION QTY
1 Pneumatic Turbine Vibrat 1 EA
2 Solenoid Valve 3/2-Way 2 1 EA
3 Silencer / Exhaust Air F 1 EA
4 SMC Air Filter Regulator 1 SET
5 Weld-on Hopper Mounting 1 EA
INSTALLATION NOTES:
1. Mount vibrator on stiffened channel beam weld
2. Operate in intermittent pulse mode (e.g. 5 se
3. Interposing relay 700-HL at CA1 panel protect
