x92120/x260911-002-KalasinEngineering/02_Electrical_and_eDrawing/03_CAD_Exports_DXF_SVG/IS_Barriers_CAD/KAL-JC-IS-003_HiC2025_SMART_Transmitter_Power_Supply_AI.dxf

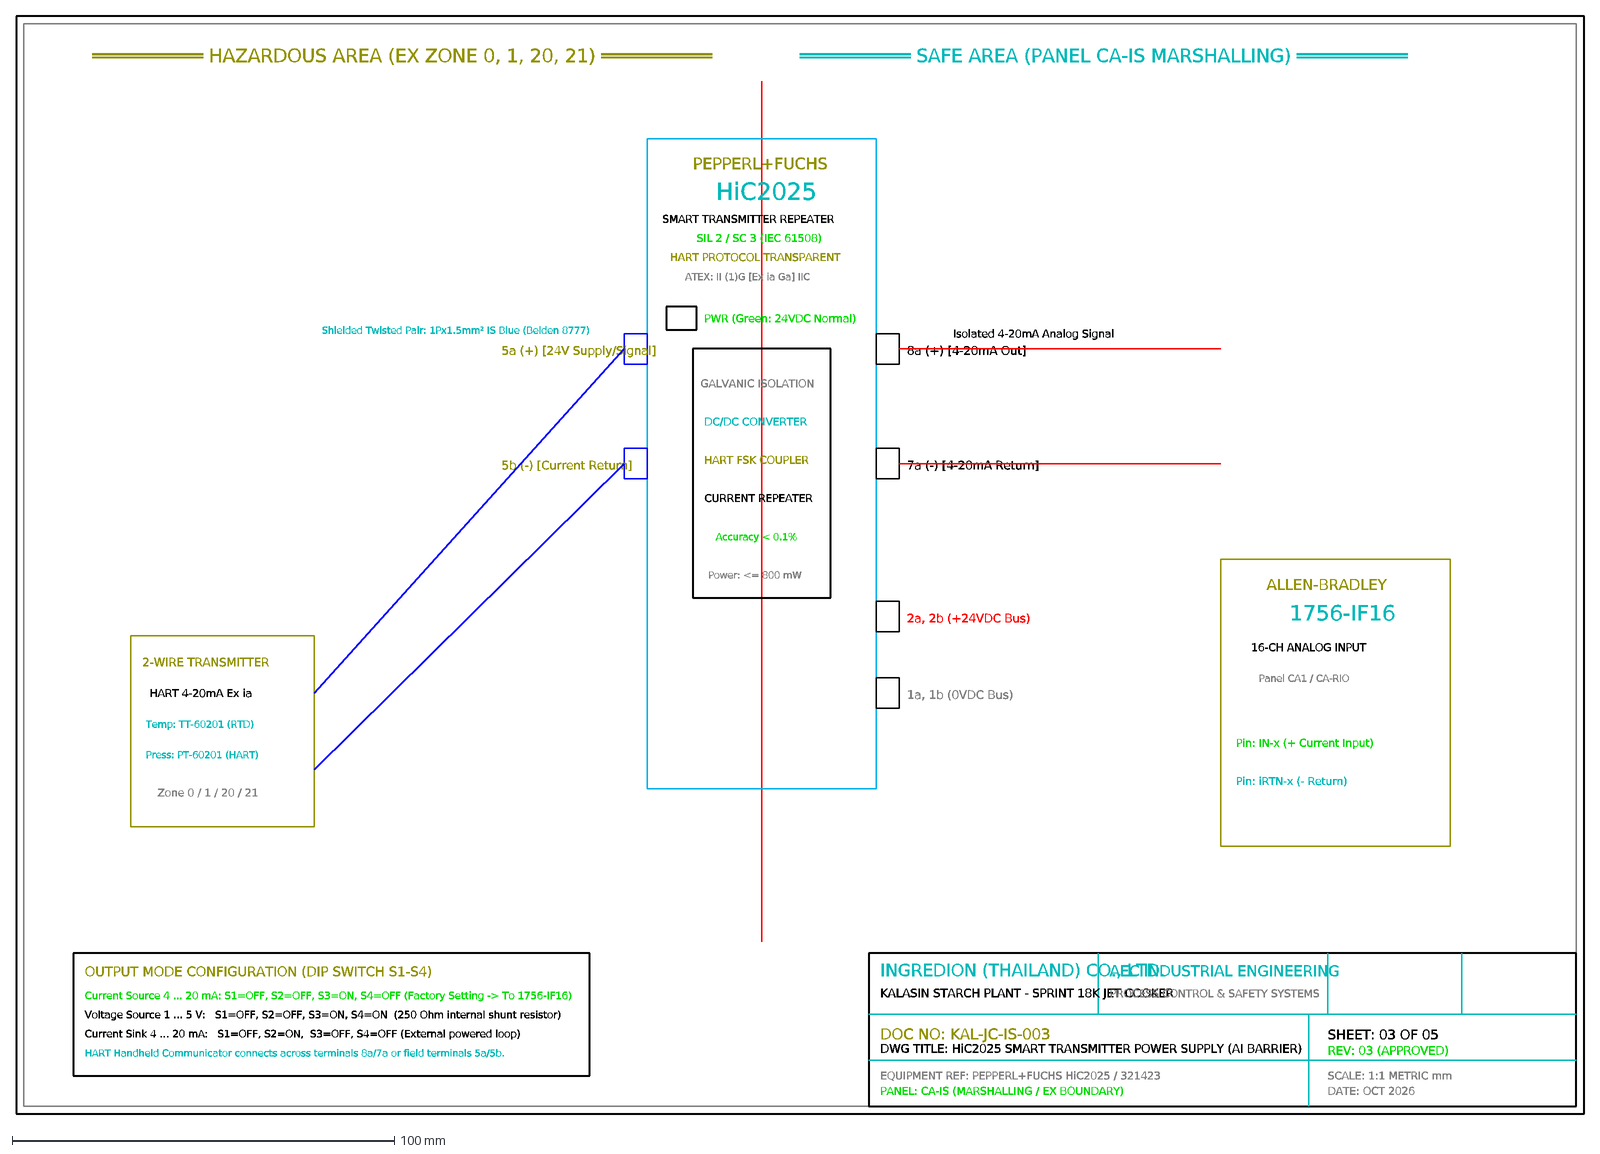
[picture p104: CAD file, 2026-10-05]
02_Electrical_and_eDrawing/03_CAD_Exports_DXF_SVG/IS_Barriers_CAD/KAL-JC-IS-003_HiC2025_SMART_Transmitter_Power_Supply_AI.dxf
INGREDION (THAILAND) CO., LTD.
KALASIN STARCH PLANT - SPRINT 18K JET COOKER
AEC INDUSTRIAL ENGINEERING
PROCESS CONTROL & SAFETY SYSTEMS
DOC NO: KAL-JC-IS-003
DWG TITLE: HiC2025 SMART TRANSMITTER POWER SUPPLY (AI BARRIER)
EQUIPMENT REF: PEPPERL+FUCHS HiC2025 / 321423
PANEL: CA-IS (MARSHALLING / EX BOUNDARY)
SHEET: 03 OF 05
REV: 03 (APPROVED)
SCALE: 1:1 METRIC mm
DATE: OCT 2026
══════════ HAZARDOUS AREA (EX ZONE 0, 1, 20, 21) ══════════
══════════ SAFE AREA (PANEL CA-IS MARSHALLING) ══════════
PEPPERL+FUCHS
HiC2025
SMART TRANSMITTER REPEATER
SIL 2 / SC 3 (IEC 61508)
HART PROTOCOL TRANSPARENT
ATEX: II (1)G [Ex ia Ga] IIC
GALVANIC ISOLATION
DC/DC CONVERTER
HART FSK COUPLER
CURRENT REPEATER
Accuracy < 0.1%
Power: <= 800 mW
PWR (Green: 24VDC Normal)
5a (+) [24V Supply/Signal]
5b (-) [Current Return]
8a (+) [4-20mA Out]
7a (-) [4-20mA Return]
2a, 2b (+24VDC Bus)
1a, 1b (0VDC Bus)
2-WIRE TRANSMITTER
HART 4-20mA Ex ia
Temp: TT-60201 (RTD)
Press: PT-60201 (HART)
Zone 0 / 1 / 20 / 21
Shielded Twisted Pair: 1Px1.5mm² IS Blue (Belden 8777)
ALLEN-BRADLEY
1756-IF16
16-CH ANALOG INPUT
Panel CA1 / CA-RIO
Pin: IN-x (+ Current Input)
Pin: iRTN-x (- Return)
Isolated 4-20mA Analog Signal
OUTPUT MODE CONFIGURATION (DIP SWITCH S1-S4)
Current Source 4 ... 20 mA: S1=OFF, S2=OFF, S3=ON, S4=OFF (Factory Setting -> To 1756-IF16)
Voltage Source 1 ... 5 V: S1=OFF, S2=OFF, S3=ON, S4=ON (250 Ohm internal shunt resistor)
Current Sink 4 ... 20 mA: S1=OFF, S2=ON, S3=OFF, S4=OFF (External powered loop)
HART Handheld Communicator connects across terminals 8a/7a or field terminals 5a/5b.
