x92120/x260911-002-KalasinEngineering/02_Electrical_and_eDrawing/Panel_Layout/Panel_Legends_and_BOM/Sheet_36_Panel_Legend.dxf

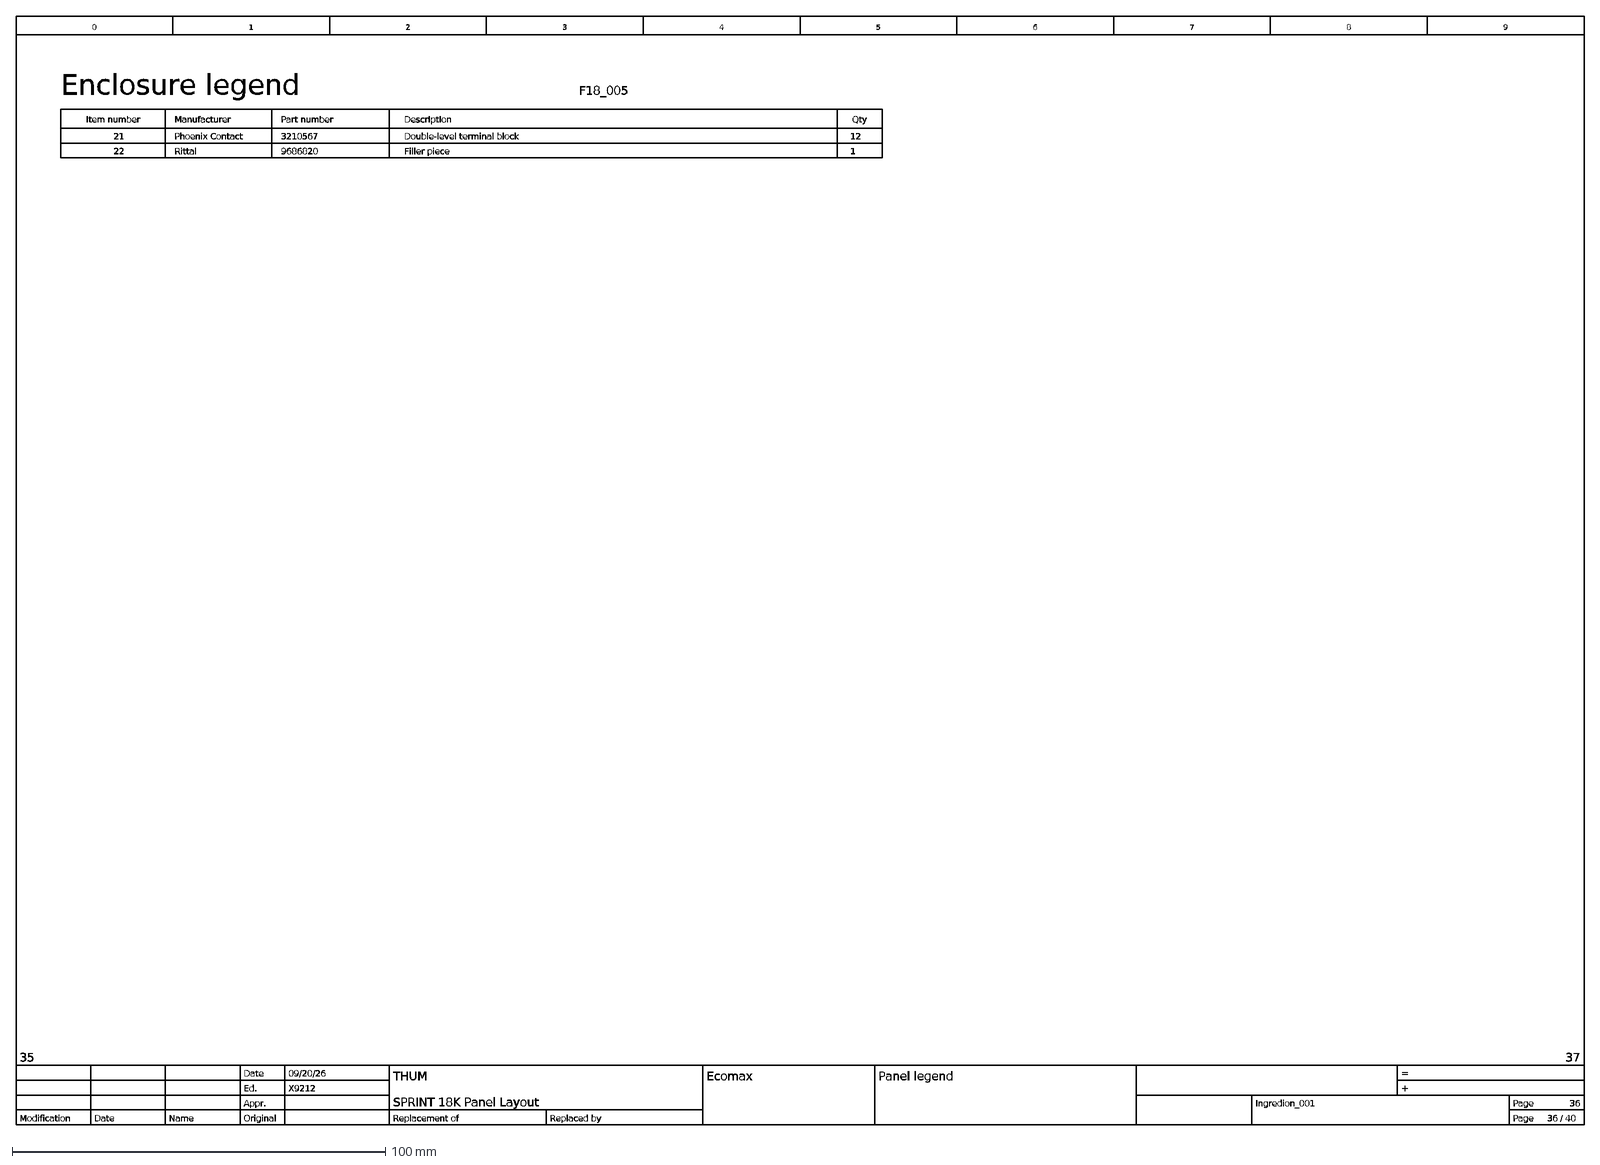
[picture p106: CAD file, 2026-10-07]
02_Electrical_and_eDrawing/Panel_Layout/Panel_Legends_and_BOM/Sheet_36_Panel_Legend.dxf
SPRINT 18K Panel Layout
35
Ingredion_001
THUM
X9212
Panel legend
1
0
7
6
8
9
3
40
37
4
09/20/26
Ecomax
36
2
5
Page
Ed.
Original
+
Date
Replaced by
Modification
Appr.
Replacement of
=
Name
/
Enclosure legend
F18_005
Part number
Manufacturer
Item number
Qty
Description
Phoenix Contact
3210567
21
12
Double-level terminal block
Rittal
9686820
22
Filler piece
