x92120/x260911-002-KalasinEngineering/02_Electrical_and_eDrawing/Panel_Layout/TAMCO_CRS_Series/Drawings_DXF/CRS-01-Layout.dxf

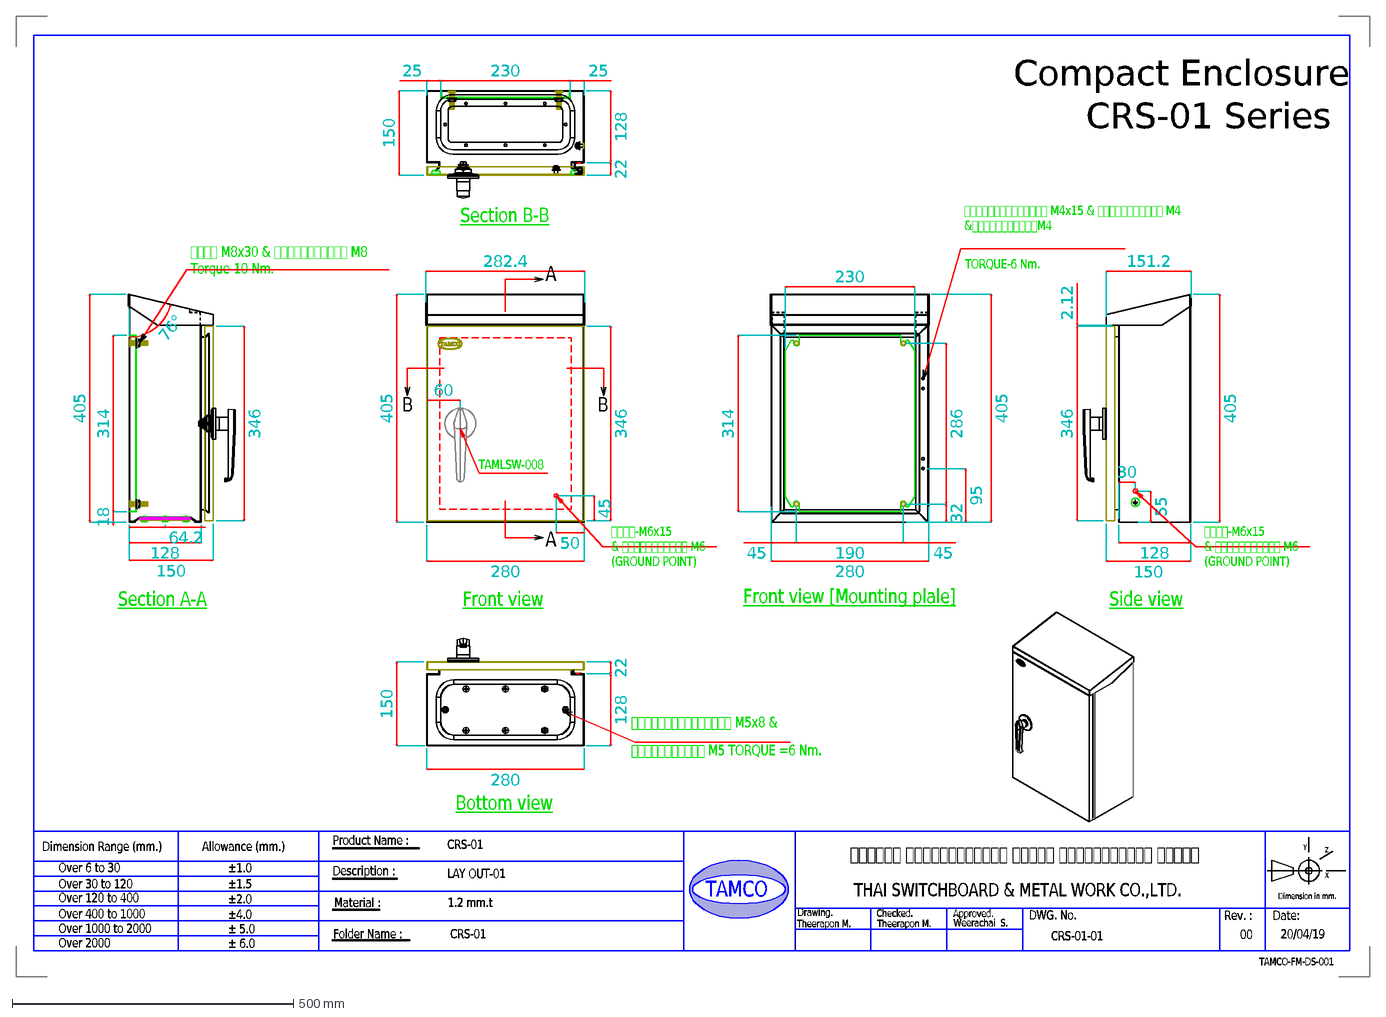
[picture p108: CAD file, 2026-10-07]
02_Electrical_and_eDrawing/Panel_Layout/TAMCO_CRS_Series/Drawings_DXF/CRS-01-Layout.dxf
DWG. No.
THAI SWITCHBOARD & METAL WORK CO.,LTD.
Checked.
Approved.
20/04/19
Date:
Drawing.
Product Name :
Description :
Material :
Folder Name :
Rev. :
00
TAMCO-FM-DS-001
CRS-01-01
1.2 mm.t
CRS-01
Theerapon M.
Weerachai S.
LAY OUT-01
Dimension Range (mm.)
Over 6 to 30
Over 30 to 120
Over 120 to 400
Over 400 to 1000
Over 1000 to 2000
Over 2000
Allowance (mm.)
±1.5
±1.0
±2.0
±4.0
± 5.0
± 6.0
TAMCO
Z
X
Y
Dimension in mm.
Compact Enclosure
CRS-01 Series
150
405
2.12
151.2
60
TAMLSW-008
30
55
346
280
128
64.2
18
314
76°
282.4
230
286
32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
