x92120/x260911-002-KalasinEngineering/Datasheet/PF/PF_260436_HiCTB16_Page_04.dxf

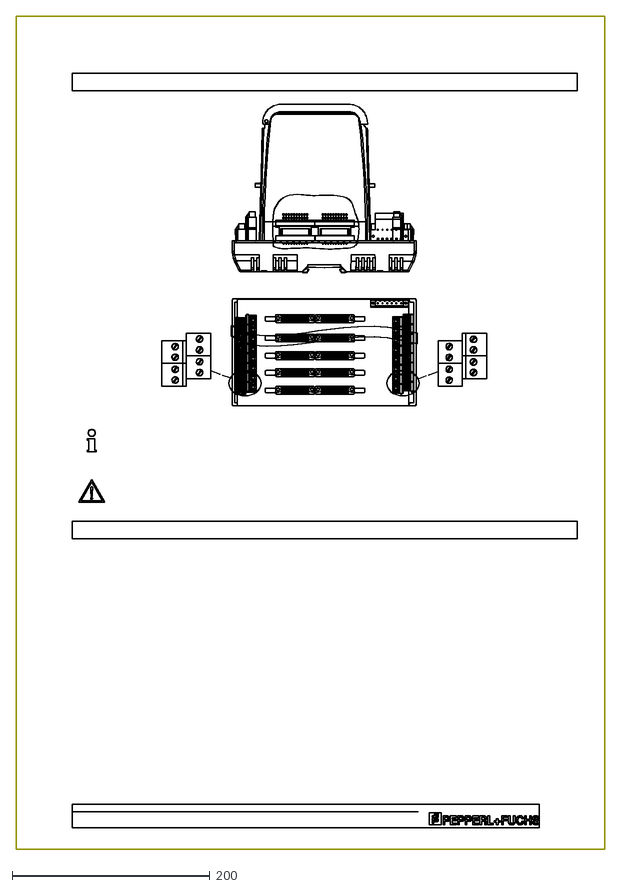
[picture p109: CAD file, 2026-10-05]
Datasheet/PF/PF_260436_HiCTB16_Page_04.dxf
595.0 x 842.0
