x92120/x260911-002-KalasinEngineering/Panel_Layout/Panel_Layout_JB-606.dxf

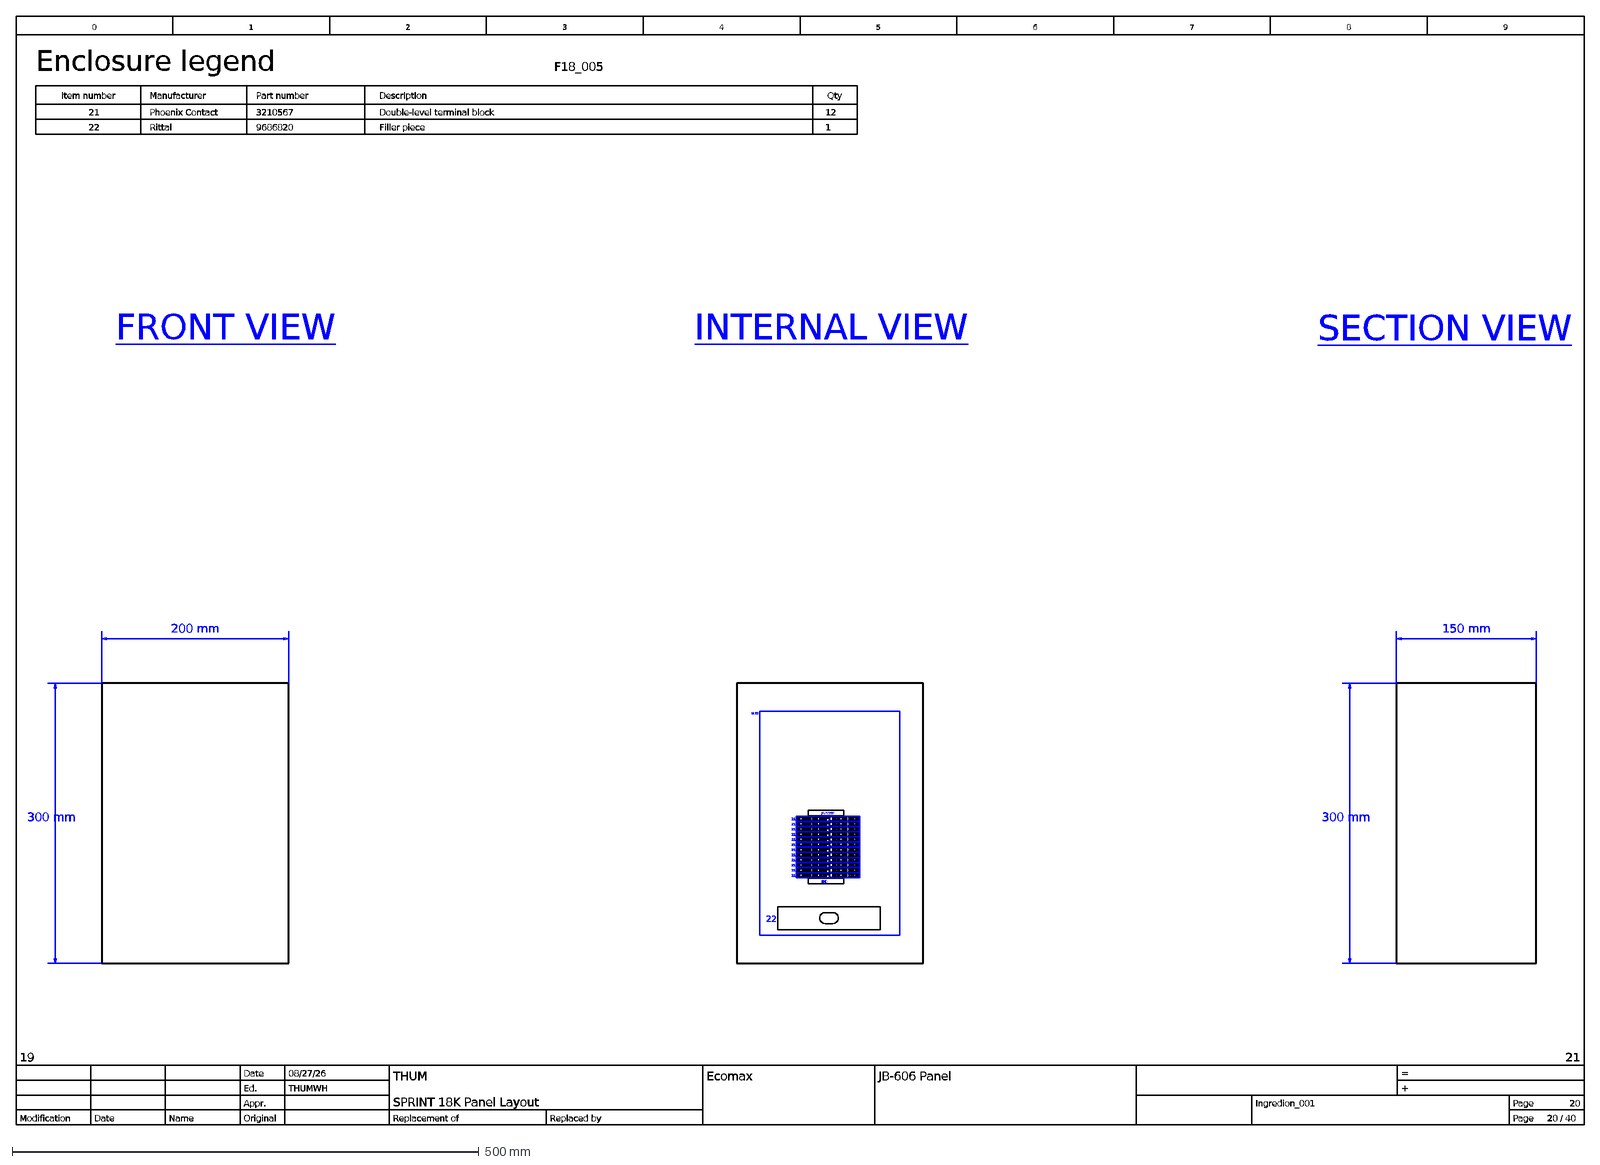
[picture p110: CAD file, 2026-10-07]
Panel_Layout/Panel_Layout_JB-606.dxf
SPRINT 18K Panel Layout
19
Ingredion_001
THUM
THUMWH
JB-606 Panel
1
0
7
6
8
9
3
40
21
4
08/27/26
Ecomax
20
2
5
Page
Ed.
Original
+
Date
Replaced by
Modification
Appr.
Replacement of
=
Name
/
Enclosure legend
F18_005
Part number
Manufacturer
Item number
Qty
Description
Phoenix Contact
3210567
12
Double-level terminal block
Rittal
9686820
22
Filler piece
JB-606TB
END
FRONT VIEW
SECTION VIEW
INTERNAL VIEW
200 mm
300 mm
150 mm
M.32
