x92120/x260911-002-KalasinEngineering/Panel_Layout/Panel_Legends_and_BOM/Sheet_11_RIO-Area_200_Panel_Legend.dxf

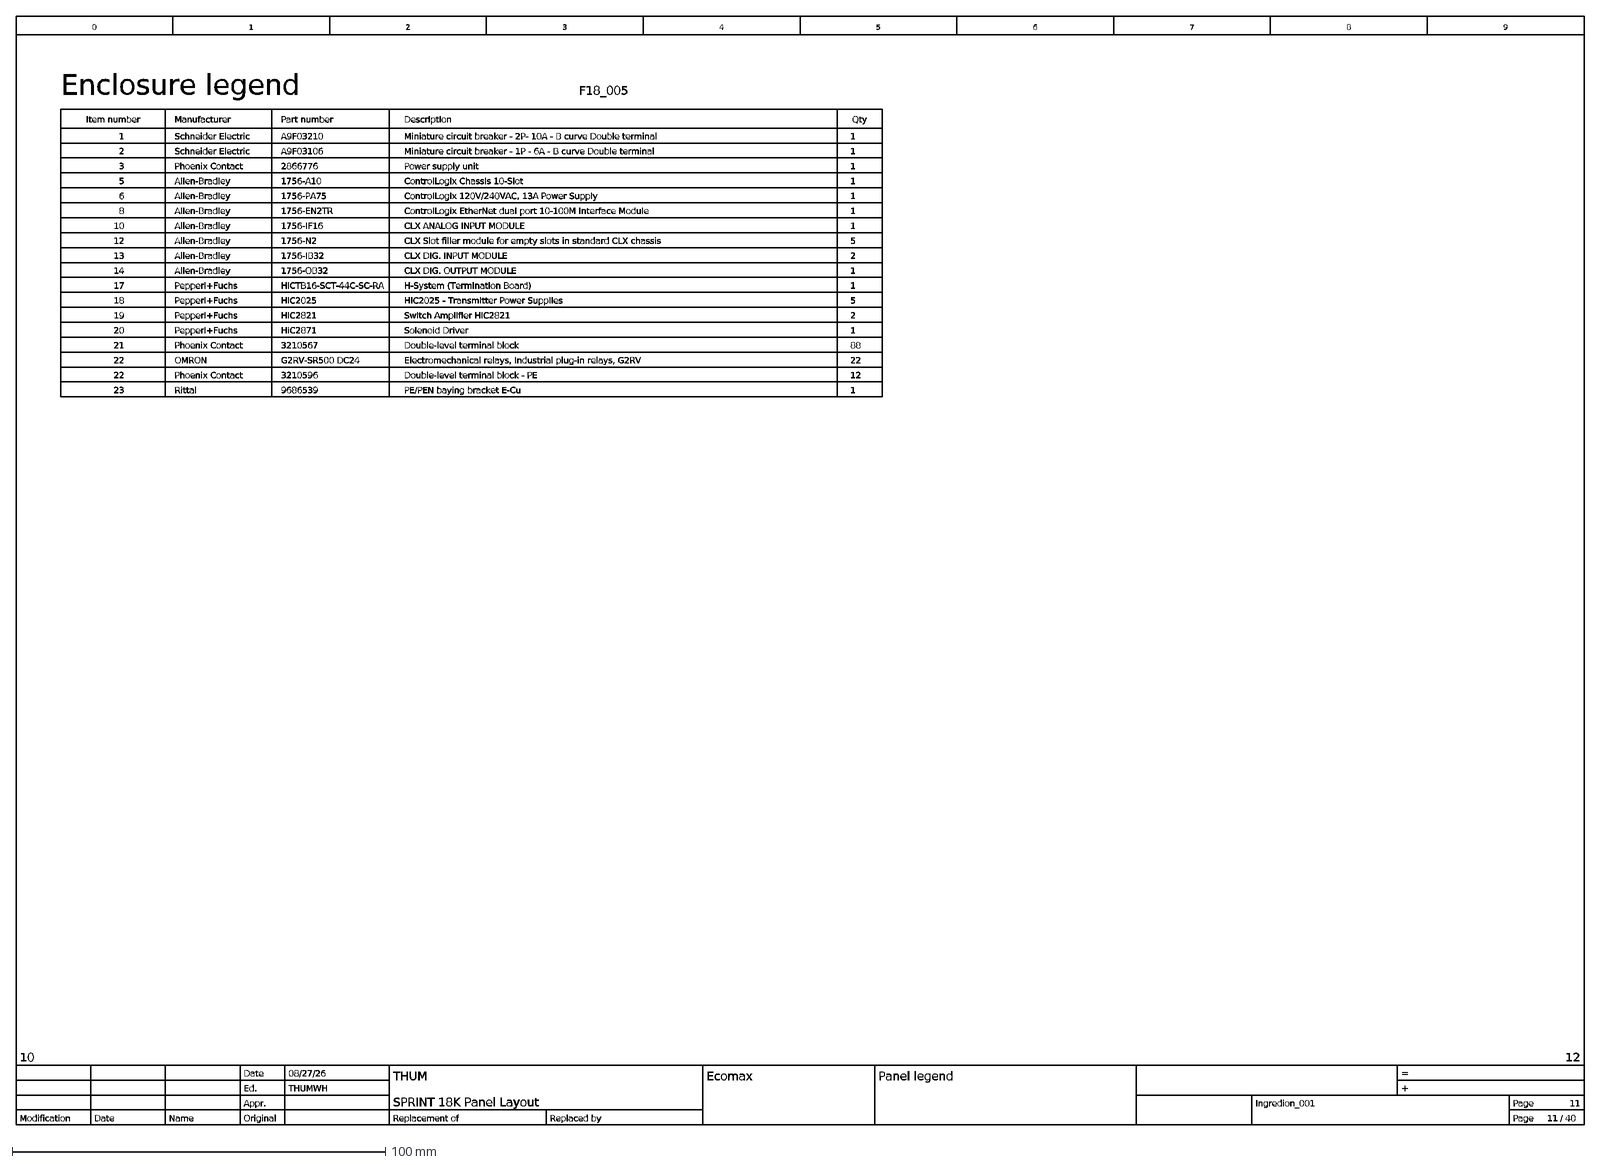
[picture p111: CAD file, 2026-10-07]
Panel_Layout/Panel_Legends_and_BOM/Sheet_11_RIO-Area_200_Panel_Legend.dxf
SPRINT 18K Panel Layout
10
Ingredion_001
THUM
THUMWH
Panel legend
1
0
7
6
8
9
3
40
12
4
08/27/26
Ecomax
11
2
5
Page
Ed.
Original
+
Date
Replaced by
Modification
Appr.
Replacement of
=
Name
/
Enclosure legend
F18_005
Part number
Manufacturer
Item number
Qty
Description
Schneider Electric
A9F03210
Miniature circuit breaker - 2P- 10A - B curve Double terminal
A9F03106
Miniature circuit breaker - 1P - 6A - B curve Double terminal
Phoenix Contact
2866776
Power supply unit
Allen-Bradley
1756-A10
ControlLogix Chassis 10-Slot
1756-PA75
ControlLogix 120V/240VAC, 13A Power Supply
1756-EN2TR
ControlLogix EtherNet dual port 10-100M Interface Module
1756-IF16
CLX ANALOG INPUT MODULE
1756-N2
CLX Slot filler module for empty slots in standard CLX chassis
1756-IB32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
