x92120/x260911-002-KalasinEngineering/Panel_Layout/TAMCO_CES_Stainless_Series/Drawings_DXF/CES-STL-07-Layout.dxf

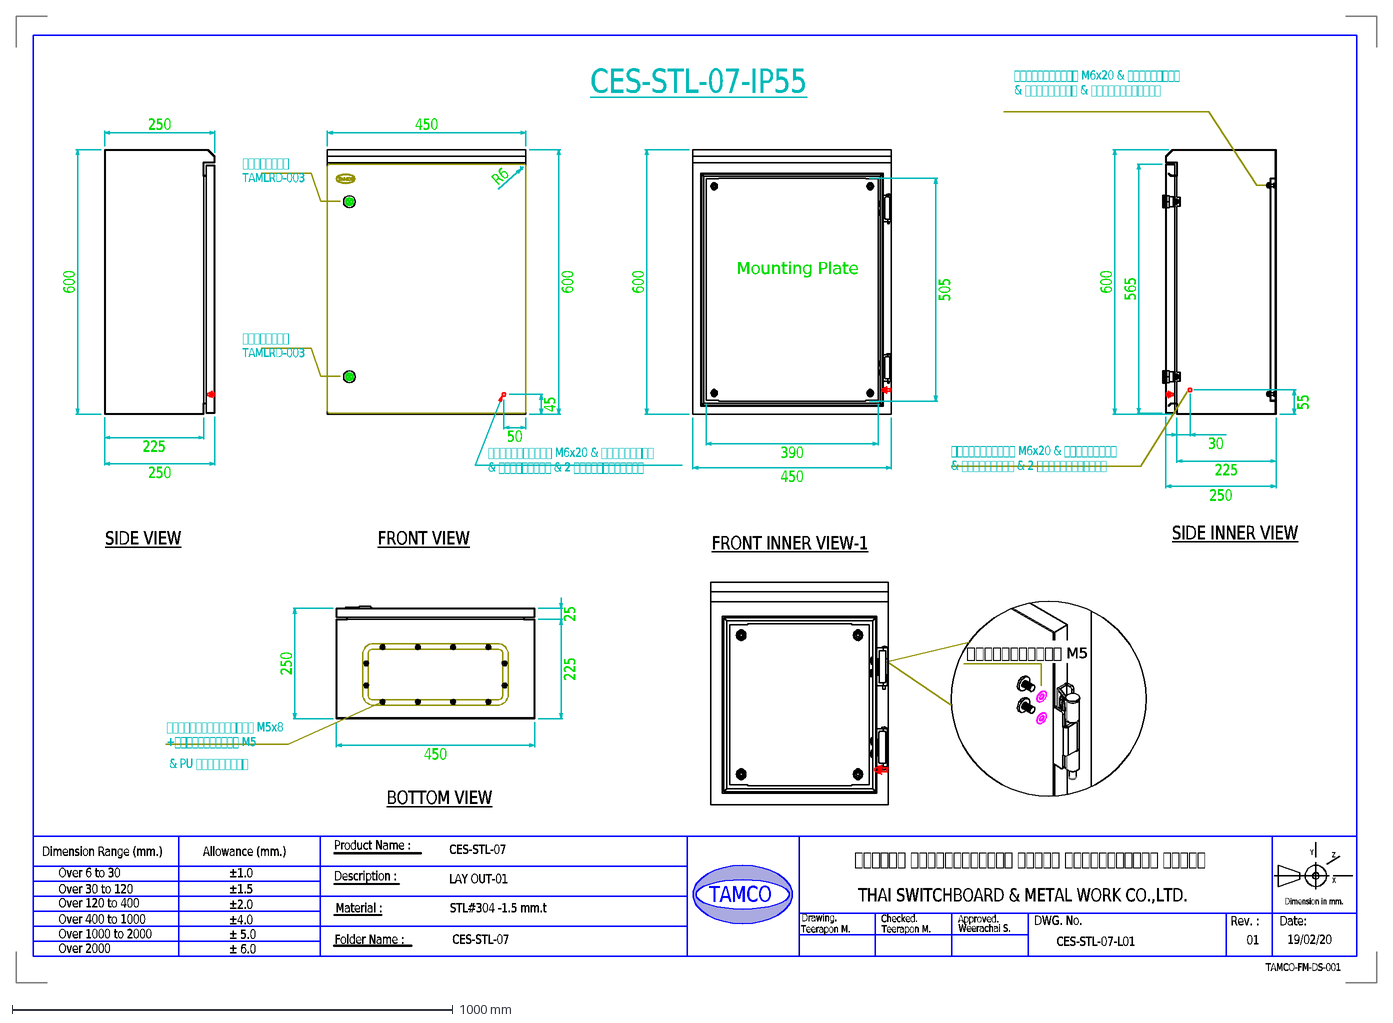
[picture p112: CAD file, 2026-10-07]
Panel_Layout/TAMCO_CES_Stainless_Series/Drawings_DXF/CES-STL-07-Layout.dxf
DWG. No.
THAI SWITCHBOARD & METAL WORK CO.,LTD.
Checked.
Approved.
Date:
Drawing.
Product Name :
Description :
Material :
Folder Name :
Rev. :
TAMCO-FM-DS-001
CES-STL-07
Weerachai S.
LAY OUT-01
Dimension Range (mm.)
Over 6 to 30
Over 30 to 120
Over 120 to 400
Over 400 to 1000
Over 1000 to 2000
Over 2000
Allowance (mm.)
±1.5
±1.0
±2.0
±4.0
± 5.0
± 6.0
TAMCO
Teerapon M.
Z
X
Y
Dimension in mm.
19/02/20
01
CES-STL-07-L01
STL#304 -1.5 mm.t
CES-STL-07-IP55
600
250
225
25
450
565
SIDE VIEW
FRONT VIEW
SIDE INNER VIEW
BOTTOM VIEW
55
30
FRONT INNER VIEW-1
Mounting Plate
390
505
R6
50
45
