x92120/x260911-002-KalasinEngineering/Panel_Layout/TAMCO_CRS_Series/Drawings_DXF/CRS-04-Layout.dxf

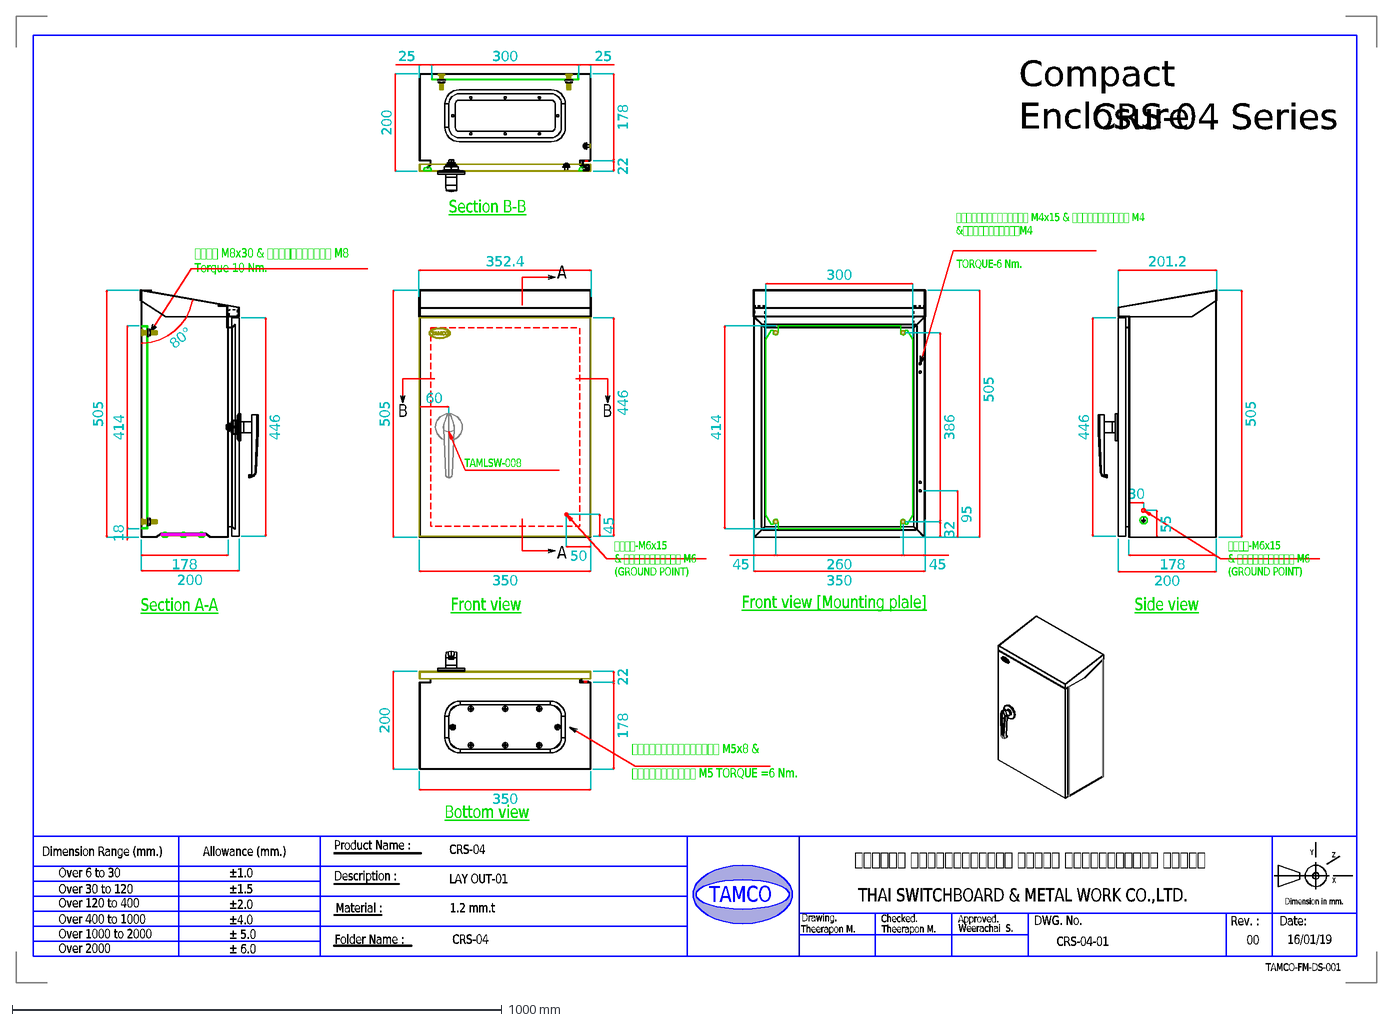
[picture p113: CAD file, 2026-10-07]
Panel_Layout/TAMCO_CRS_Series/Drawings_DXF/CRS-04-Layout.dxf
DWG. No.
THAI SWITCHBOARD & METAL WORK CO.,LTD.
Checked.
Approved.
16/01/19
Date:
Drawing.
Product Name :
Description :
Material :
Folder Name :
Rev. :
00
TAMCO-FM-DS-001
CRS-04-01
1.2 mm.t
CRS-04
Theerapon M.
Weerachai S.
LAY OUT-01
Dimension Range (mm.)
Over 6 to 30
Over 30 to 120
Over 120 to 400
Over 400 to 1000
Over 1000 to 2000
Over 2000
Allowance (mm.)
±1.5
±1.0
±2.0
±4.0
± 5.0
± 6.0
TAMCO
Z
X
Y
Dimension in mm.
Compact Enclosure
CRS-04 Series
200
505
201.2
60
TAMLSW-008
446
350
178
18
414
352.4
300
386
32
45
260
A
B
50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
