x92120/x260911-002-KalasinEngineering/02_Electrical_and_eDrawing/02_ePlan_Exports/SPRINT 18K SPRAY DRYER/8.dxf

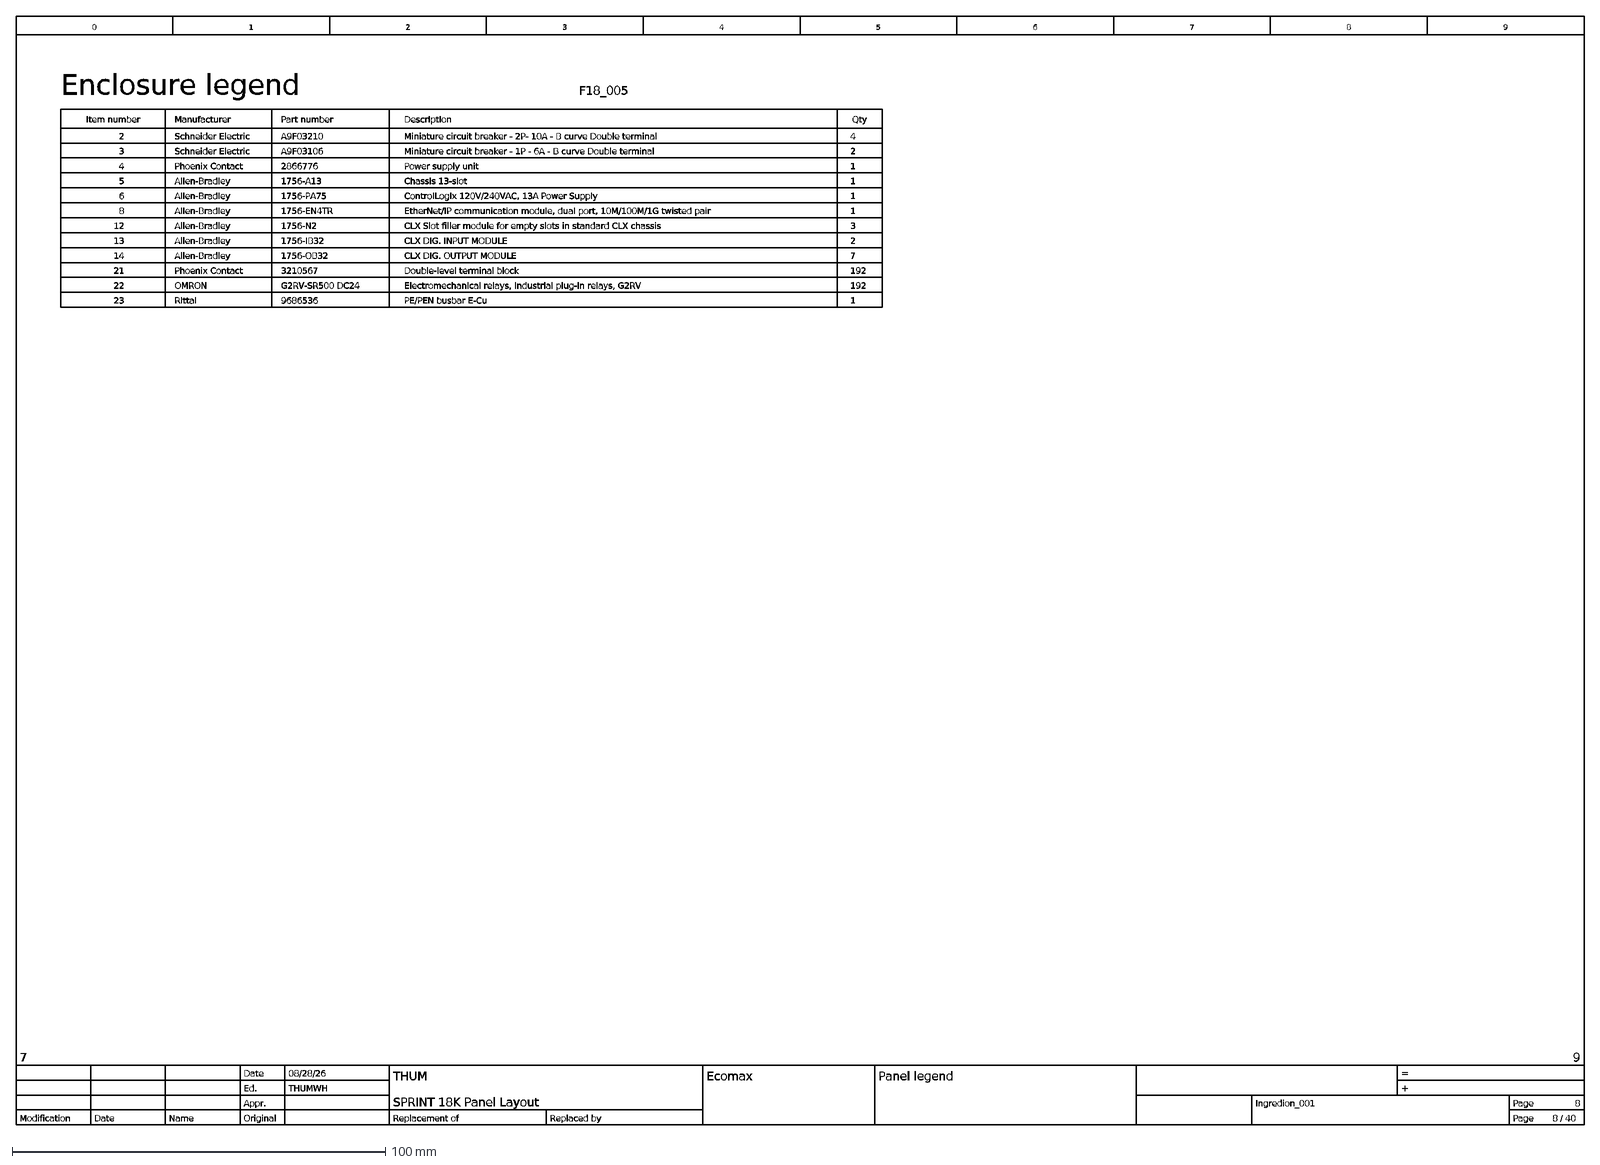
[picture p114: CAD file, 2026-10-07]
02_Electrical_and_eDrawing/02_ePlan_Exports/SPRINT 18K SPRAY DRYER/8.dxf
SPRINT 18K Panel Layout
7
Ingredion_001
THUM
THUMWH
Panel legend
1
0
6
8
9
3
40
4
08/28/26
Ecomax
2
5
Page
Ed.
Original
+
Date
Replaced by
Modification
Appr.
Replacement of
=
Name
/
Enclosure legend
F18_005
Part number
Manufacturer
Item number
Qty
Description
Schneider Electric
A9F03210
Miniature circuit breaker - 2P- 10A - B curve Double terminal
A9F03106
Miniature circuit breaker - 1P - 6A - B curve Double terminal
Phoenix Contact
2866776
Power supply unit
Allen-Bradley
1756-A13
Chassis 13-slot
1756-PA75
ControlLogix 120V/240VAC, 13A Power Supply
1756-EN4TR
EtherNet/IP communication module, dual port, 10M/100M/1G twisted pair
1756-N2
12
CLX Slot filler module for empty slots in standard CLX chassis
1756-IB32
13
CLX DIG. INPUT MODULE
1756-OB32
14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
