x92120/x260911-002-KalasinEngineering/02_Electrical_and_eDrawing/03_CAD_Exports_DXF_SVG/01_PLC_IO_Wiring_DXF/KAL-JC-WIR-20020_Sheet23_Chassis_C2_Slot_12_AI.dxf

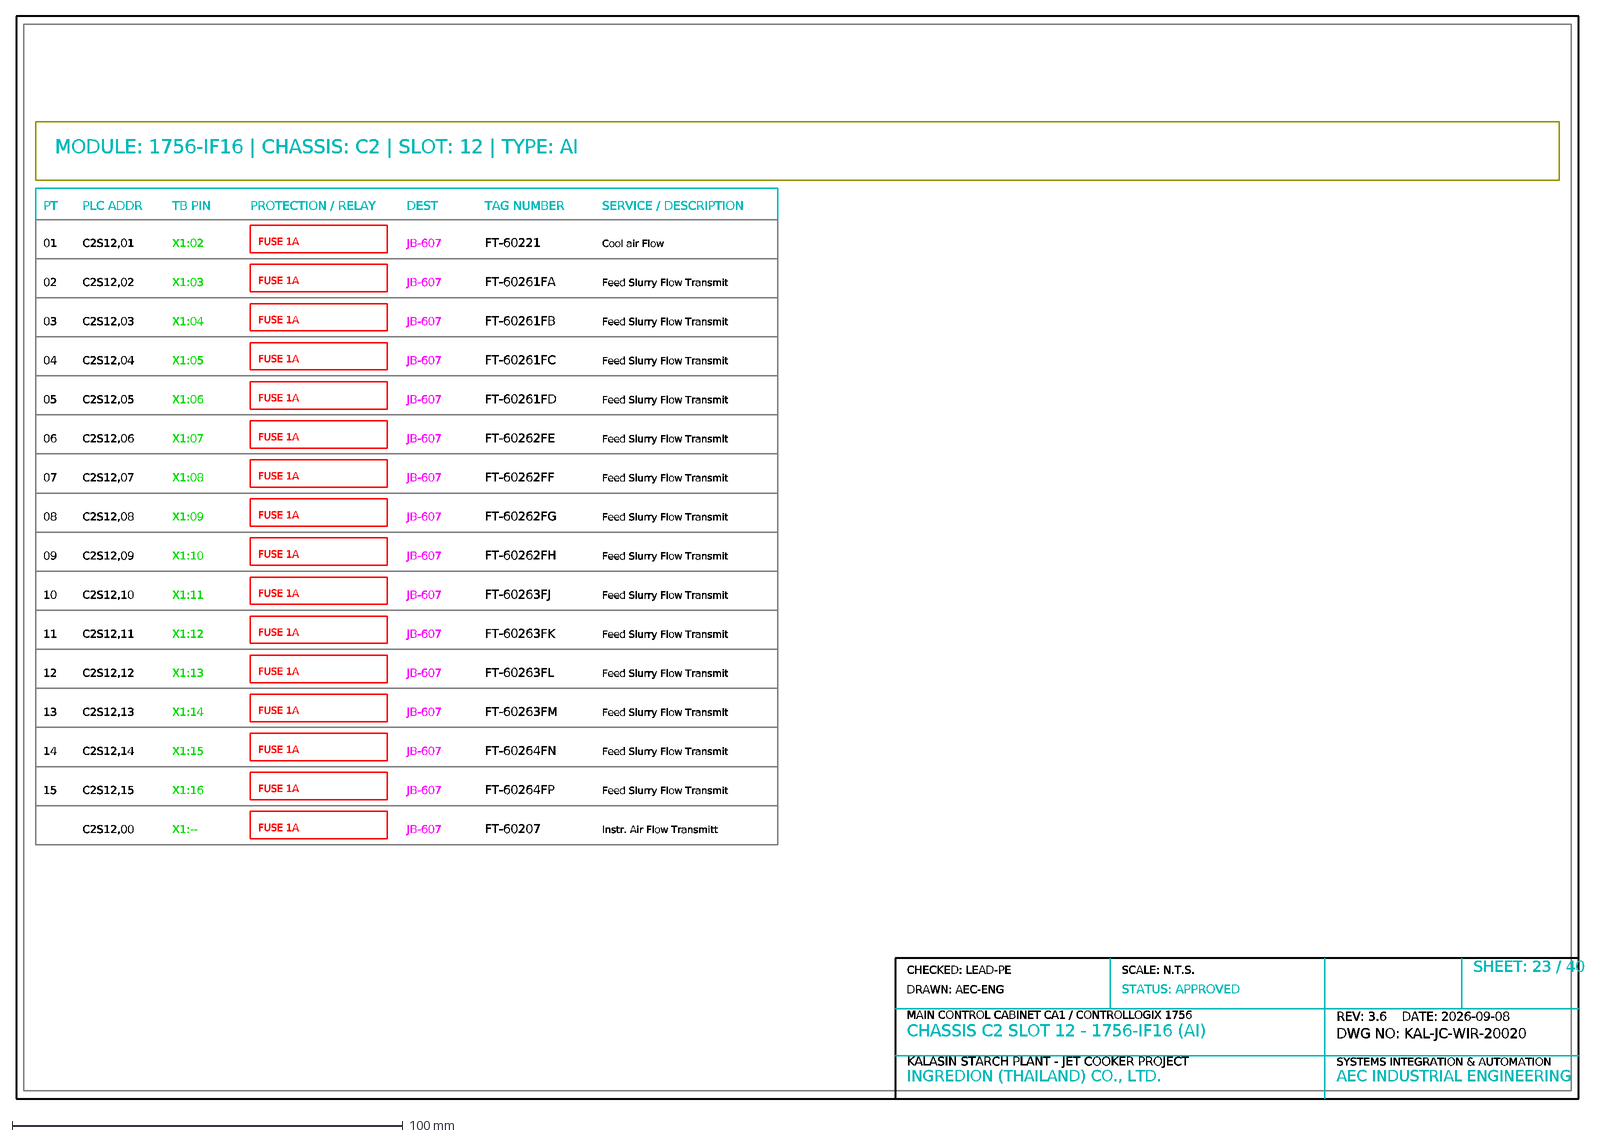
[picture p115: CAD file, 2026-09-29]
02_Electrical_and_eDrawing/03_CAD_Exports_DXF_SVG/01_PLC_IO_Wiring_DXF/KAL-JC-WIR-20020_Sheet23_Chassis_C2_Slot_12_AI.dxf
INGREDION (THAILAND) CO., LTD.
KALASIN STARCH PLANT - JET COOKER PROJECT
AEC INDUSTRIAL ENGINEERING
SYSTEMS INTEGRATION & AUTOMATION
CHASSIS C2 SLOT 12 - 1756-IF16 (AI)
MAIN CONTROL CABINET CA1 / CONTROLLOGIX 1756
DWG NO: KAL-JC-WIR-20020
REV: 3.6 DATE: 2026-09-08
DRAWN: AEC-ENG
CHECKED: LEAD-PE
STATUS: APPROVED
SCALE: N.T.S.
SHEET: 23 / 40
MODULE: 1756-IF16 | CHASSIS: C2 | SLOT: 12 | TYPE: AI
PT
PLC ADDR
TB PIN
PROTECTION / RELAY
DEST
TAG NUMBER
SERVICE / DESCRIPTION
01
C2S12,01
X1:02
FUSE 1A
JB-607
FT-60221
Cool air Flow
02
C2S12,02
X1:03
FT-60261FA
Feed Slurry Flow Transmit
03
C2S12,03
X1:04
FT-60261FB
04
C2S12,04
X1:05
FT-60261FC
05
C2S12,05
X1:06
FT-60261FD
06
C2S12,06
X1:07
FT-60262FE
07
C2S12,07
X1:08
FT-60262FF
08
C2S12,08
X1:09
FT-60262FG
09
C2S12,09
X1:10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
