x92120/x260911-002-KalasinEngineering/02_Electrical_and_eDrawing/03_CAD_Exports_DXF_SVG/02_Instrument_Typical_DXF/KAL-JC-TYP-005_Sheet07_TYP-05_Diff._Pressure_Transmitter.dxf

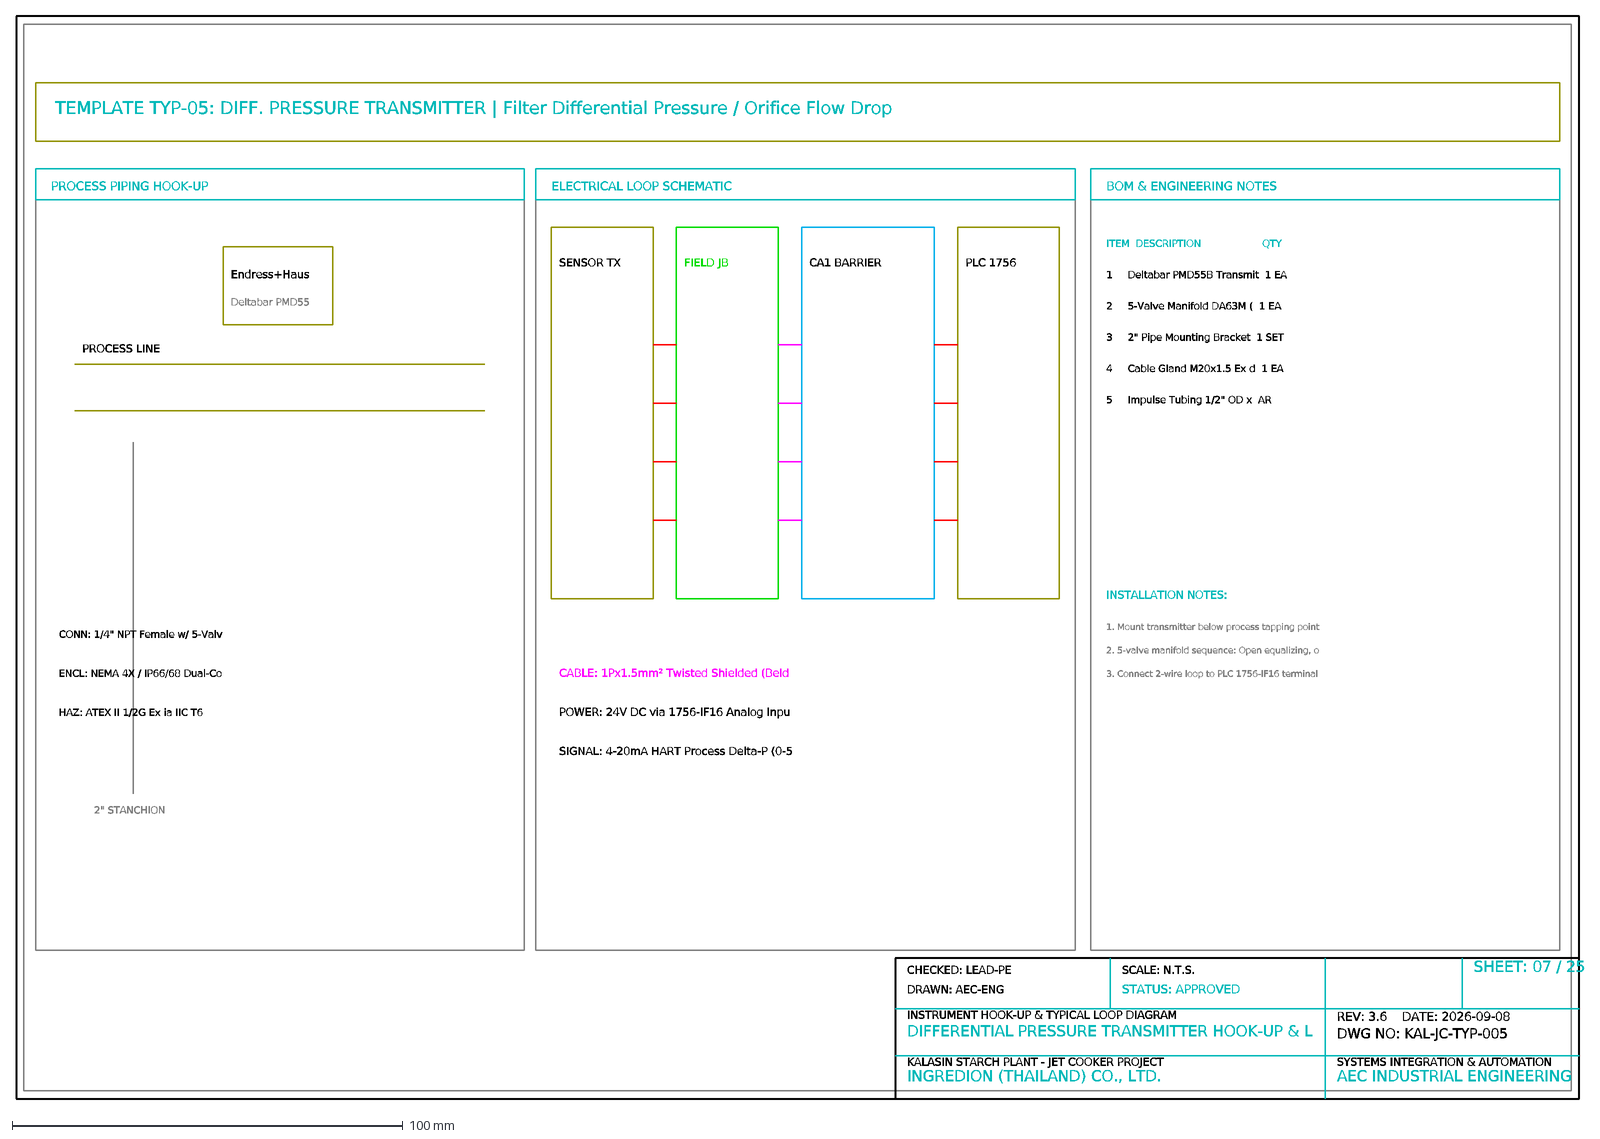
[picture p116: CAD file, 2026-09-29]
02_Electrical_and_eDrawing/03_CAD_Exports_DXF_SVG/02_Instrument_Typical_DXF/KAL-JC-TYP-005_Sheet07_TYP-05_Diff._Pressure_Transmitter.dxf
INGREDION (THAILAND) CO., LTD.
KALASIN STARCH PLANT - JET COOKER PROJECT
AEC INDUSTRIAL ENGINEERING
SYSTEMS INTEGRATION & AUTOMATION
DIFFERENTIAL PRESSURE TRANSMITTER HOOK-UP & L
INSTRUMENT HOOK-UP & TYPICAL LOOP DIAGRAM
DWG NO: KAL-JC-TYP-005
REV: 3.6 DATE: 2026-09-08
DRAWN: AEC-ENG
CHECKED: LEAD-PE
STATUS: APPROVED
SCALE: N.T.S.
SHEET: 07 / 25
TEMPLATE TYP-05: DIFF. PRESSURE TRANSMITTER | Filter Differential Pressure / Orifice Flow Drop
PROCESS PIPING HOOK-UP
PROCESS LINE
Endress+Haus
Deltabar PMD55
2" STANCHION
CONN: 1/4" NPT Female w/ 5-Valv
ENCL: NEMA 4X / IP66/68 Dual-Co
HAZ: ATEX II 1/2G Ex ia IIC T6
ELECTRICAL LOOP SCHEMATIC
SENSOR TX
FIELD JB
CA1 BARRIER
PLC 1756
CABLE: 1Px1.5mm² Twisted Shielded (Beld
POWER: 24V DC via 1756-IF16 Analog Inpu
SIGNAL: 4-20mA HART Process Delta-P (0-5
BOM & ENGINEERING NOTES
ITEM DESCRIPTION QTY
1 Deltabar PMD55B Transmit 1 EA
2 5-Valve Manifold DA63M ( 1 EA
3 2" Pipe Mounting Bracket 1 SET
4 Cable Gland M20x1.5 Ex d 1 EA
5 Impulse Tubing 1/2" OD x AR
INSTALLATION NOTES:
1. Mount transmitter below process tapping point
2. 5-valve manifold sequence: Open equalizing, o
3. Connect 2-wire loop to PLC 1756-IF16 terminal
