x92120/x260911-002-KalasinEngineering/02_Electrical_and_eDrawing/03_CAD_Exports_DXF_SVG/03_MCC_Panel_Layout/MCC_Panel_Layout_Sheet3_Panel_M1.dxf

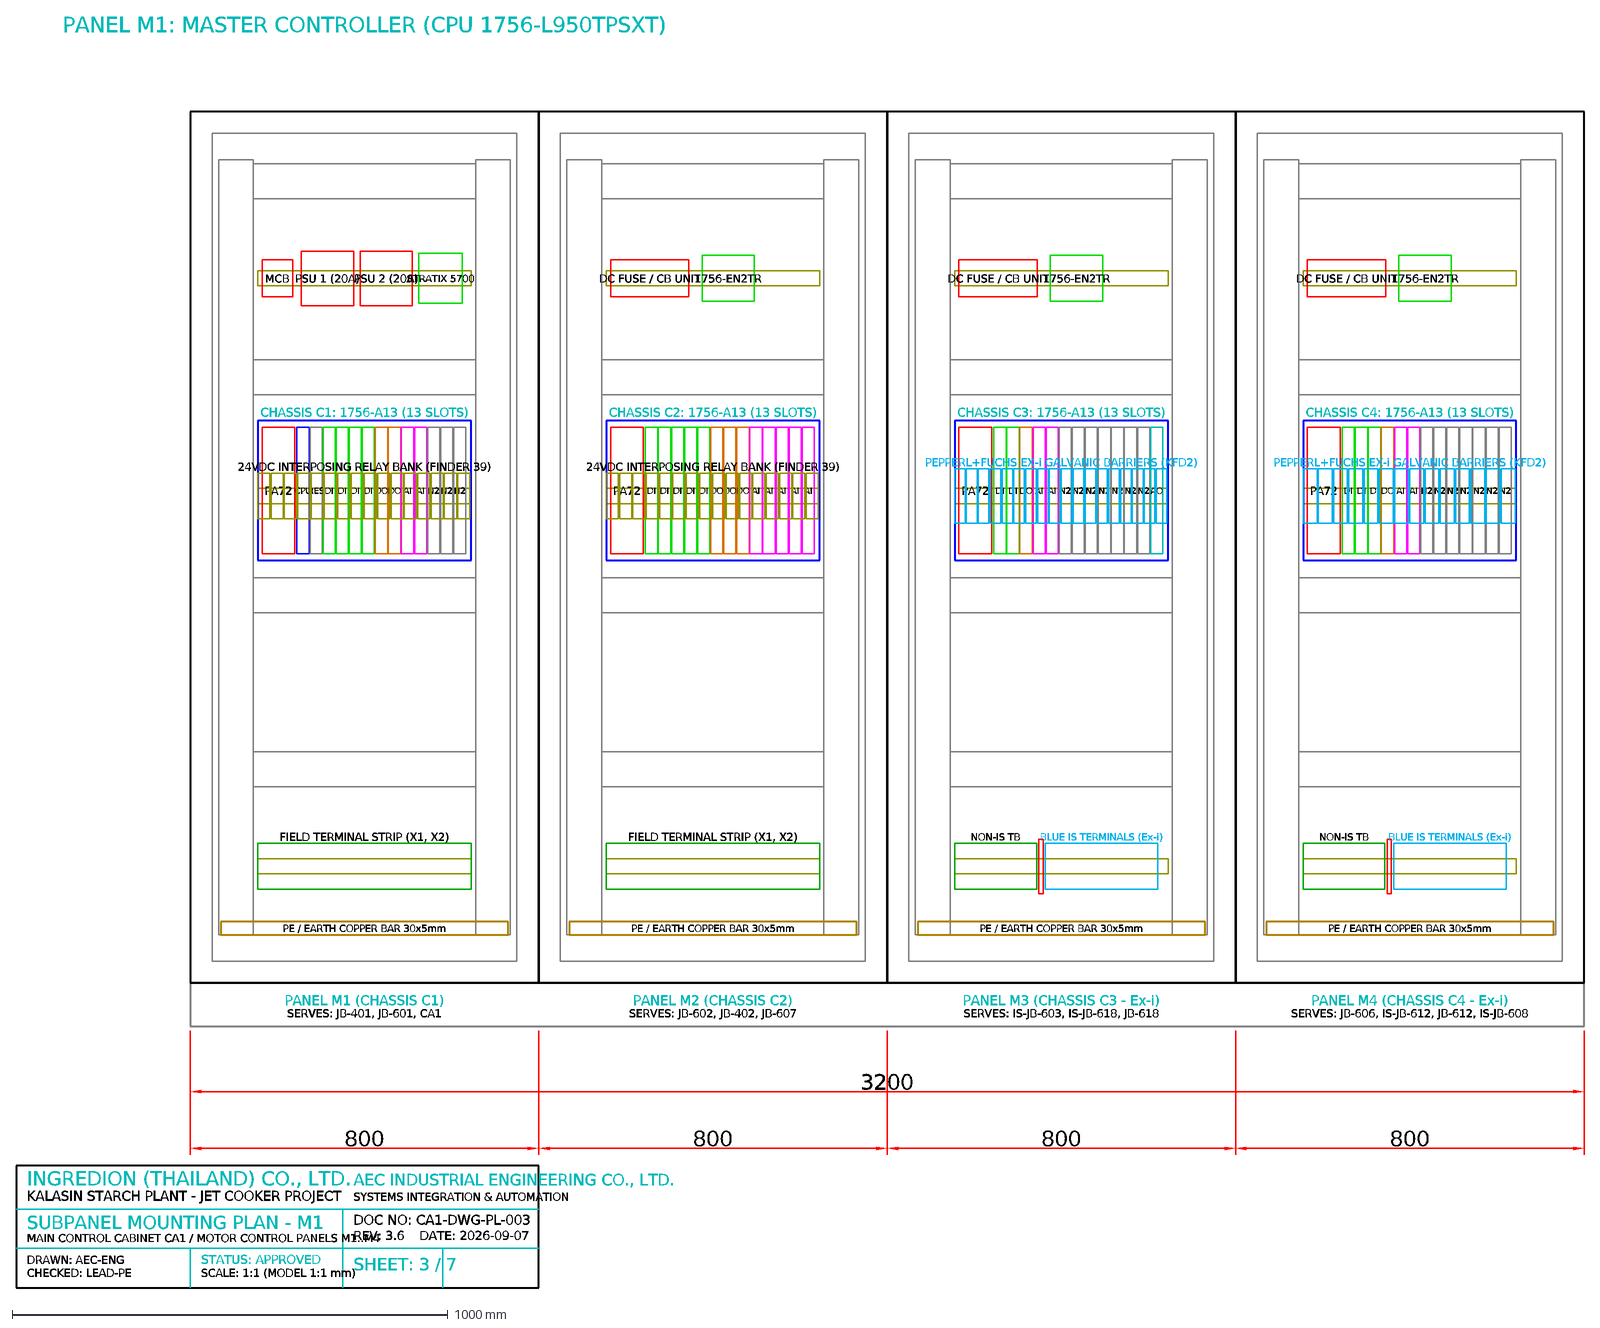
[picture p117: CAD file, 2026-09-29]
02_Electrical_and_eDrawing/03_CAD_Exports_DXF_SVG/03_MCC_Panel_Layout/MCC_Panel_Layout_Sheet3_Panel_M1.dxf
PE / EARTH COPPER BAR 30x5mm
MCB
PSU 1 (20A)
PSU 2 (20A)
STRATIX 5700
PA72
CPU
RES
DI
DO
AI
N2
CHASSIS C1: 1756-A13 (13 SLOTS)
24VDC INTERPOSING RELAY BANK (FINDER 39)
FIELD TERMINAL STRIP (X1, X2)
PANEL M1 (CHASSIS C1)
SERVES: JB-401, JB-601, CA1
DC FUSE / CB UNIT
1756-EN2TR
CHASSIS C2: 1756-A13 (13 SLOTS)
PANEL M2 (CHASSIS C2)
SERVES: JB-602, JB-402, JB-607
AO
CHASSIS C3: 1756-A13 (13 SLOTS)
PEPPERL+FUCHS EX-i GALVANIC BARRIERS (KFD2)
NON-IS TB
BLUE IS TERMINALS (Ex-i)
PANEL M3 (CHASSIS C3 - Ex-i)
SERVES: IS-JB-603, IS-JB-618, JB-618
CHASSIS C4: 1756-A13 (13 SLOTS)
PANEL M4 (CHASSIS C4 - Ex-i)
SERVES: JB-606, IS-JB-612, JB-612, IS-JB-608
3200
800
PANEL M1: MASTER CONTROLLER (CPU 1756-L950TPSXT)
INGREDION (THAILAND) CO., LTD.
KALASIN STARCH PLANT - JET COOKER PROJECT
AEC INDUSTRIAL ENGINEERING CO., LTD.
SYSTEMS INTEGRATION & AUTOMATION
SUBPANEL MOUNTING PLAN - M1
MAIN CONTROL CABINET CA1 / MOTOR CONTROL PANELS M1..M4
DOC NO: CA1-DWG-PL-003
REV: 3.6 DATE: 2026-09-07
DRAWN: AEC-ENG
CHECKED: LEAD-PE
STATUS: APPROVED
SCALE: 1:1 (MODEL 1:1 mm)
SHEET: 3 / 7
