x92120/x260911-002-KalasinEngineering/02_Electrical_and_eDrawing/05_Instrument_Manuals/Pepperl+Fuchs IS Barriers/KAL-JC-IS-004_HiCTB16_16Slot_Termination_Board.dxf

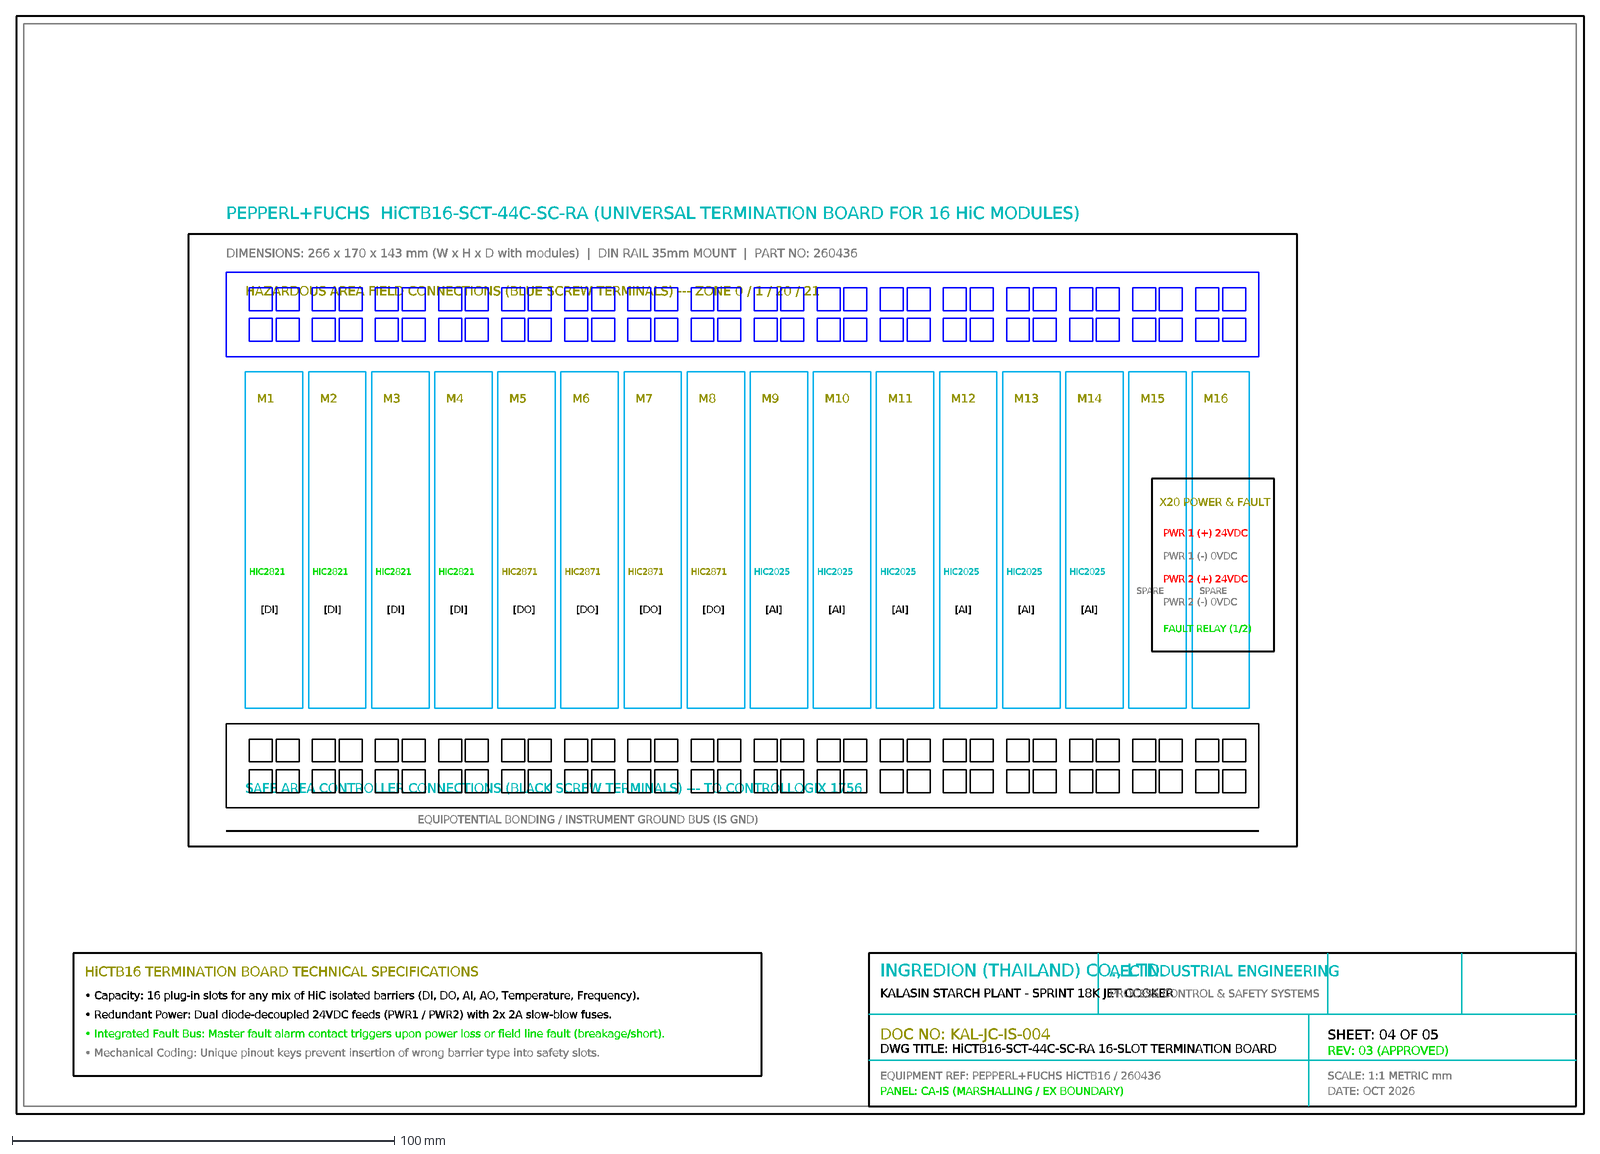
[picture p118: CAD file, 2026-10-05]
02_Electrical_and_eDrawing/05_Instrument_Manuals/Pepperl+Fuchs IS Barriers/KAL-JC-IS-004_HiCTB16_16Slot_Termination_Board.dxf
INGREDION (THAILAND) CO., LTD.
KALASIN STARCH PLANT - SPRINT 18K JET COOKER
AEC INDUSTRIAL ENGINEERING
PROCESS CONTROL & SAFETY SYSTEMS
DOC NO: KAL-JC-IS-004
DWG TITLE: HiCTB16-SCT-44C-SC-RA 16-SLOT TERMINATION BOARD
EQUIPMENT REF: PEPPERL+FUCHS HiCTB16 / 260436
PANEL: CA-IS (MARSHALLING / EX BOUNDARY)
SHEET: 04 OF 05
REV: 03 (APPROVED)
SCALE: 1:1 METRIC mm
DATE: OCT 2026
PEPPERL+FUCHS HiCTB16-SCT-44C-SC-RA (UNIVERSAL TERMINATION BOARD FOR 16 HiC MODULES)
DIMENSIONS: 266 x 170 x 143 mm (W x H x D with modules) | DIN RAIL 35mm MOUNT | PART NO: 260436
HAZARDOUS AREA FIELD CONNECTIONS (BLUE SCREW TERMINALS) --- ZONE 0 / 1 / 20 / 21
SAFE AREA CONTROLLER CONNECTIONS (BLACK SCREW TERMINALS) --- TO CONTROLLOGIX 1756
M1
HiC2821
[DI]
M2
M3
M4
M5
HiC2871
[DO]
M6
M7
M8
M9
HiC2025
[AI]
M10
M11
M12
M13
M14
M15
SPARE
M16
X20 POWER & FAULT
PWR 1 (+) 24VDC
PWR 1 (-) 0VDC
PWR 2 (+) 24VDC
PWR 2 (-) 0VDC
FAULT RELAY (1/2)
EQUIPOTENTIAL BONDING / INSTRUMENT GROUND BUS (IS GND)
HiCTB16 TERMINATION BOARD TECHNICAL SPECIFICATIONS
• Capacity: 16 plug-in slots for any mix of HiC isolated barriers (DI, DO, AI, AO, Temperature, Frequency).
• Redundant Power: Dual diode-decoupled 24VDC feeds (PWR1 / PWR2) with 2x 2A slow-blow fuses.
• Integrated Fault Bus: Master fault alarm contact triggers upon power loss or field line fault (breakage/short).
• Mechanical Coding: Unique pinout keys prevent insertion of wrong barrier type into safety slots.
