x92120/x260911-002-KalasinEngineering/02_Electrical_and_eDrawing/Panel_Layout/Panel_Legends_and_BOM/Sheet_09_Panel_Dimensions.dxf

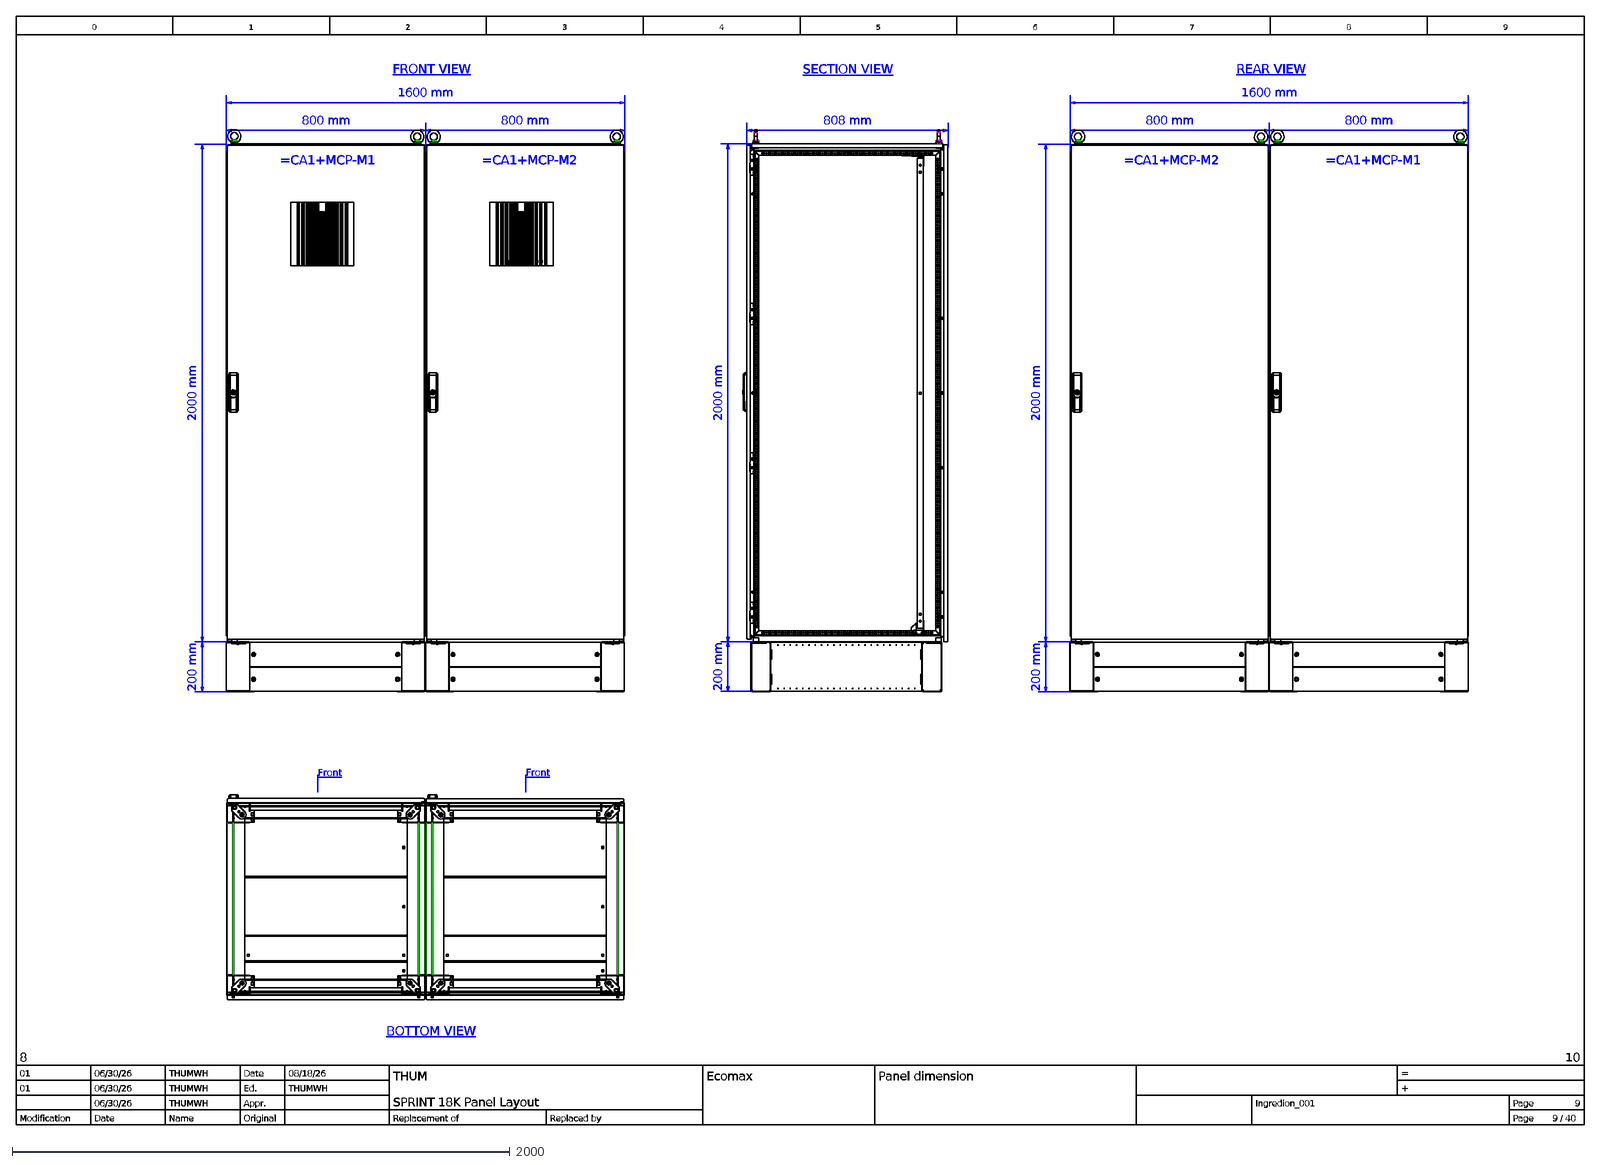
[picture p119: CAD file, 2026-10-07]
02_Electrical_and_eDrawing/Panel_Layout/Panel_Legends_and_BOM/Sheet_09_Panel_Dimensions.dxf
06/30/26
01
SPRINT 18K Panel Layout
THUMWH
8
Ingredion_001
THUM
Panel dimension
1
0
7
6
9
3
40
10
4
08/18/26
Ecomax
2
5
Page
Ed.
Original
+
Date
Replaced by
Modification
Appr.
Replacement of
=
Name
/
800 mm
1600 mm
200 mm
2000 mm
808 mm
FRONT VIEW
SECTION VIEW
BOTTOM VIEW
Front
=CA1+MCP-M1
=CA1+MCP-M2
REAR VIEW
