x92120/x260911-002-KalasinEngineering/Datasheet/PF/PF_321423_HiC2025_AI_Page_04.dxf

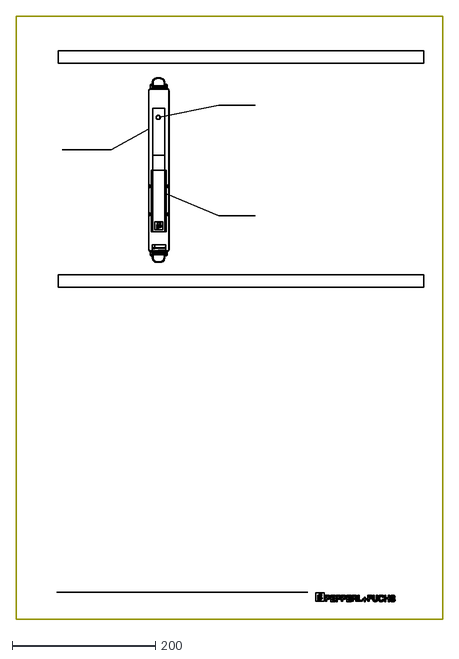
[picture p120: CAD file, 2026-10-05]
Datasheet/PF/PF_321423_HiC2025_AI_Page_04.dxf
595.3 x 841.9
