x92120/x260911-002-KalasinEngineering/Panel_Layout/Panel_Layout_IS-JB-603.dxf

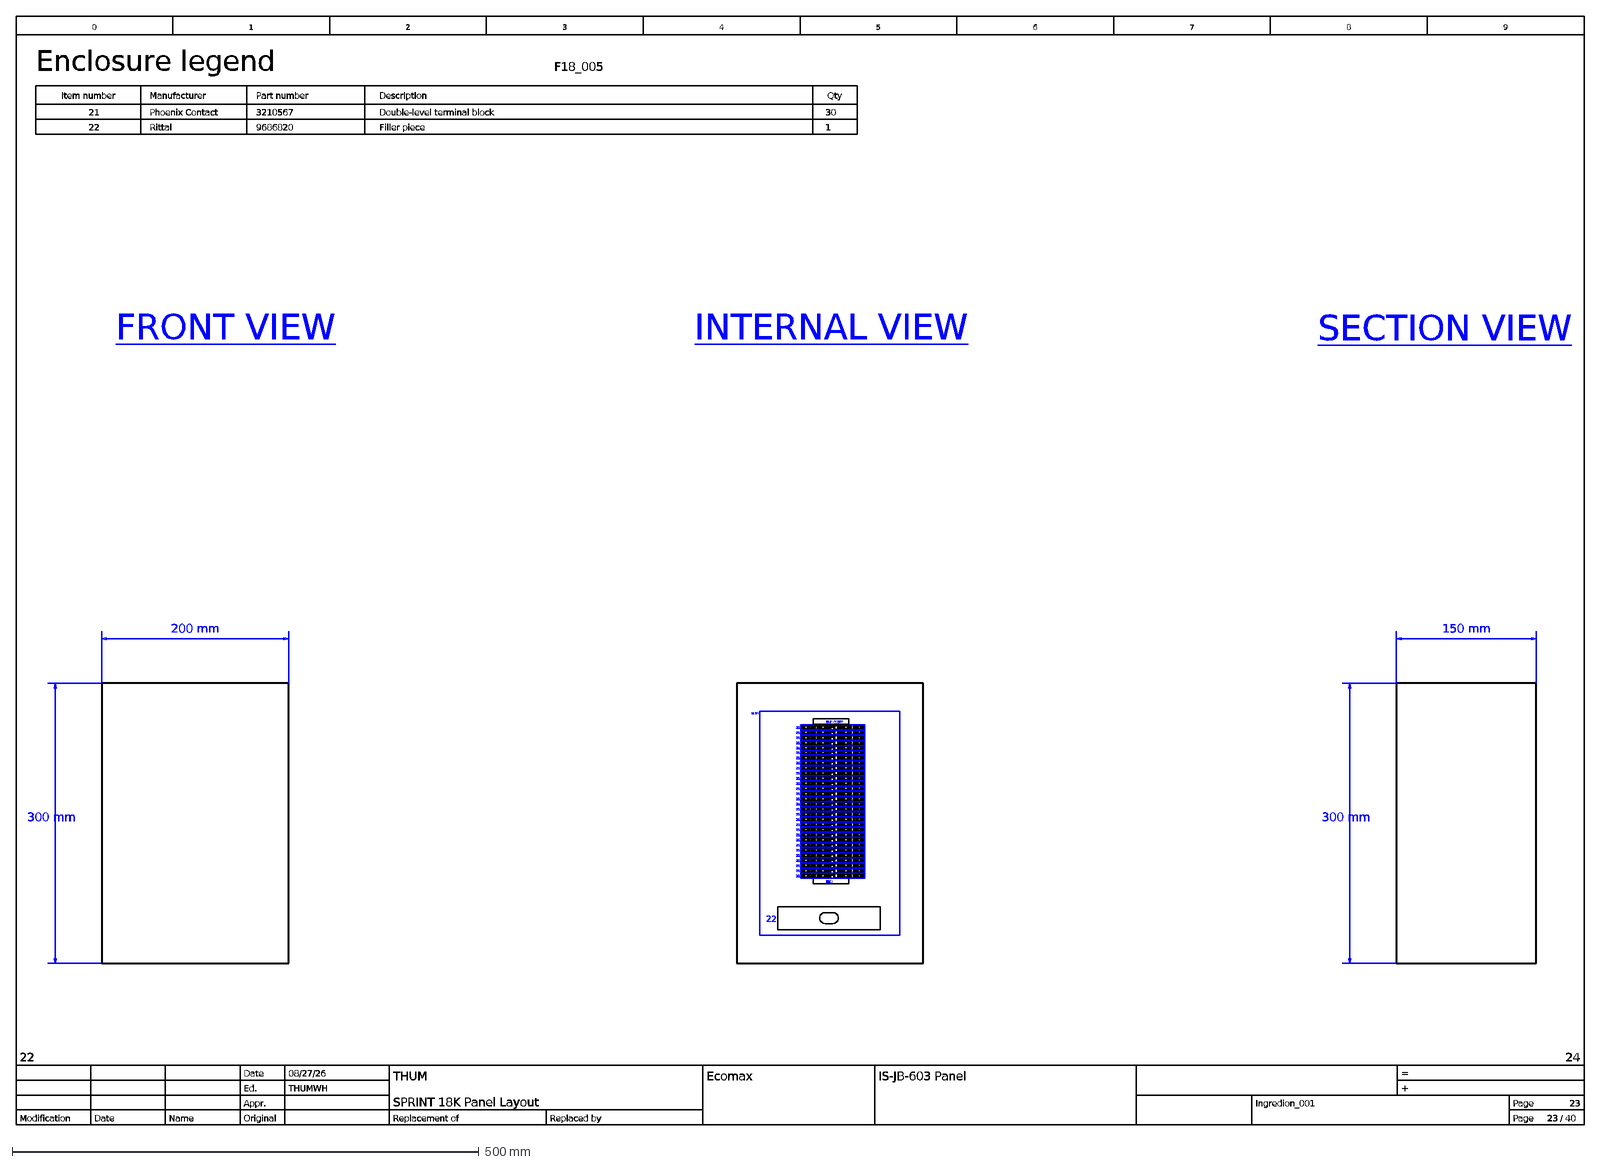
[picture p121: CAD file, 2026-10-07]
Panel_Layout/Panel_Layout_IS-JB-603.dxf
SPRINT 18K Panel Layout
22
Ingredion_001
THUM
THUMWH
IS-JB-603 Panel
1
0
7
6
8
9
3
40
24
4
08/27/26
Ecomax
23
2
5
Page
Ed.
Original
+
Date
Replaced by
Modification
Appr.
Replacement of
=
Name
/
Enclosure legend
F18_005
Part number
Manufacturer
Item number
Qty
Description
Phoenix Contact
3210567
21
30
Double-level terminal block
Rittal
9686820
Filler piece
END
FRONT VIEW
INTERNAL VIEW
SECTION VIEW
200 mm
300 mm
150 mm
IS-JB-603TB
M.28
