x92120/x260911-002-KalasinEngineering/Panel_Layout/Panel_Legends_and_BOM/Sheet_29_Panel_Legend.dxf

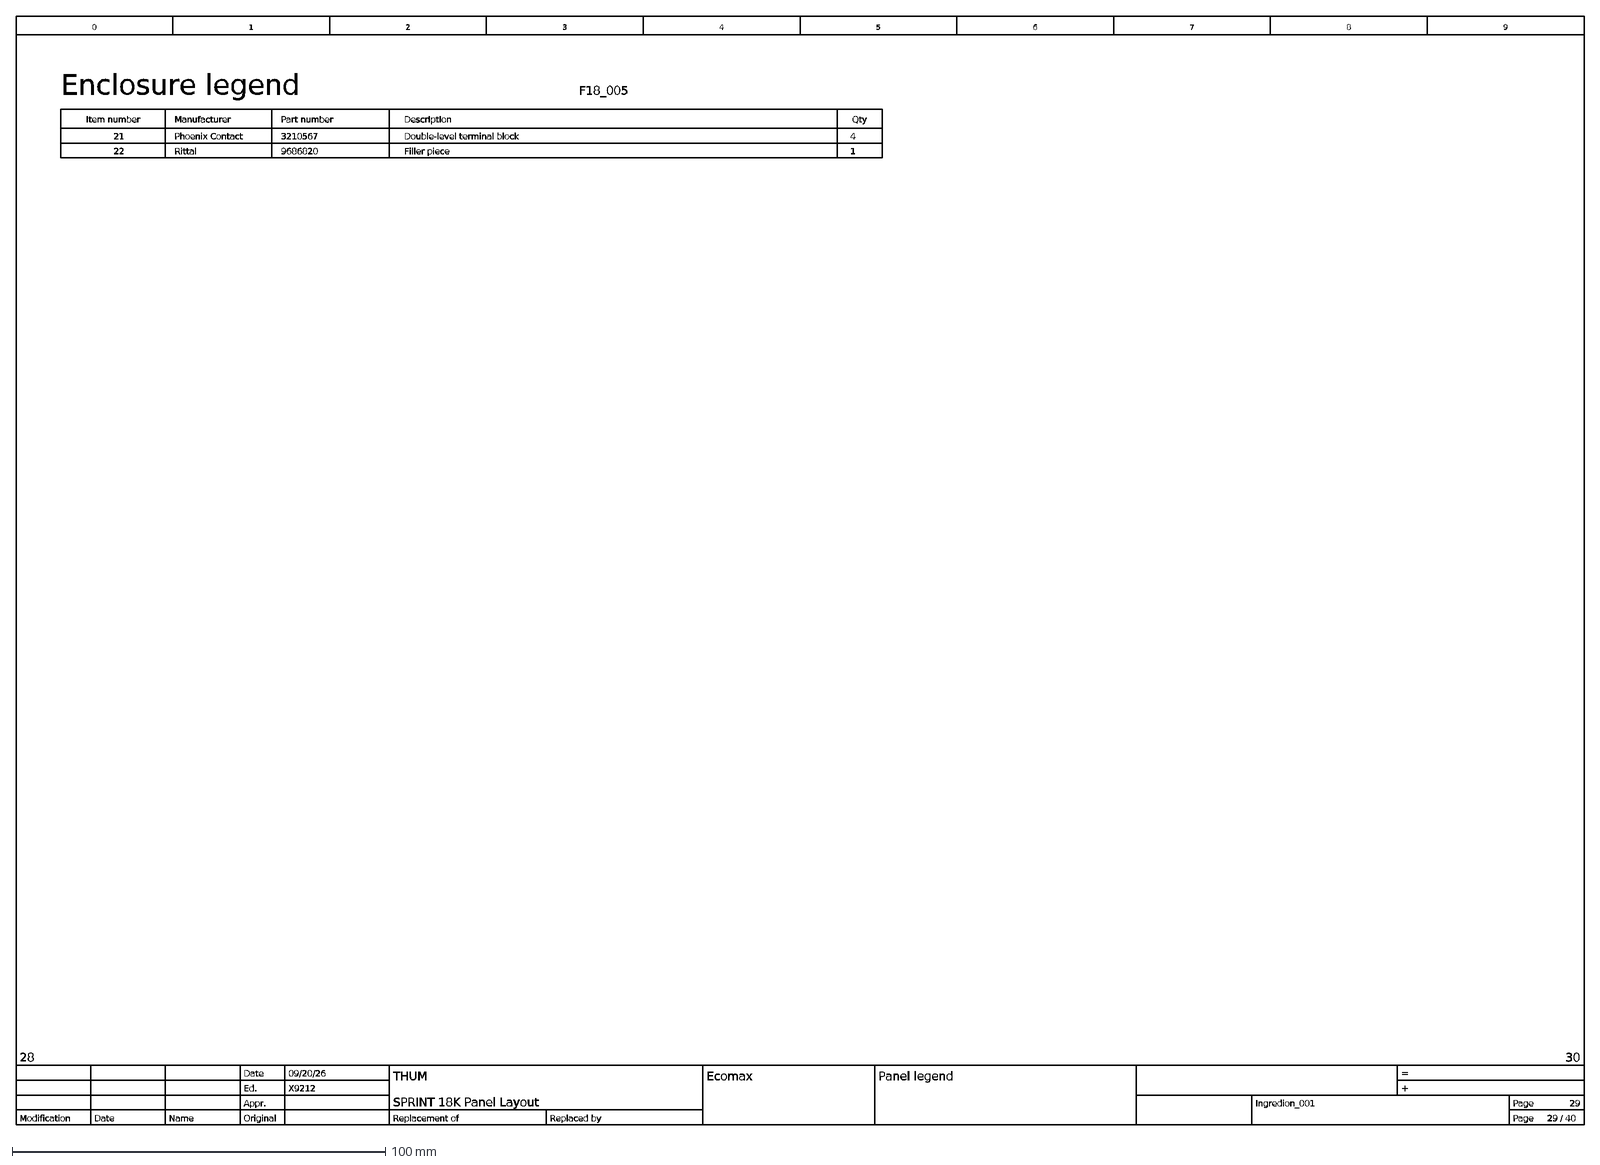
[picture p122: CAD file, 2026-10-07]
Panel_Layout/Panel_Legends_and_BOM/Sheet_29_Panel_Legend.dxf
SPRINT 18K Panel Layout
28
Ingredion_001
THUM
X9212
Panel legend
1
0
7
6
8
9
3
40
30
4
09/20/26
Ecomax
29
2
5
Page
Ed.
Original
+
Date
Replaced by
Modification
Appr.
Replacement of
=
Name
/
Enclosure legend
F18_005
Part number
Manufacturer
Item number
Qty
Description
Phoenix Contact
3210567
21
Double-level terminal block
Rittal
9686820
22
Filler piece
