x92120/x260911-002-KalasinEngineering/02_Electrical_and_eDrawing/05_Instrument_Manuals/README.md

# 05_Instrument_Manuals — Field Instrument Technical & User Manuals

This directory contains technical datasheets, user manuals, and wiring specs for all process instruments and intrinsically safe barriers deployed at the **Ingredion Kalasin Spray Dryer Plant**.

---

## 📁 Instrument Categories & Directory Register

| Category Directory | Instrument Type / Scope | Vendor / Manufacturers |
| :--- | :--- | :--- |
| **`CS-DS-01 Dust Analyzer`** | Starch Dust Concentration & Baghouse Monitoring | Sintrol / Sick |
| **`CS-DS-01 LEL gas Analyzer`** | Combustible Gas & LEL Safety Sensors | MSA / Crowcon |
| **`CS-DS-01 pH Analyzer`** | Slurry & CIP pH Probes | Mettler Toledo / Endress+Hauser |
| **`CS-DS-02 Diff Pressure Gauge`** | Filter Baghouse Differential Pressure Gauges | WIKA / Dwyer |
| **`CS-DS-03Diff Pressure Transmitter`**| DP Flow & Level Transmitters | Yokogawa / Rosemount |
| **`CS-DS-05 Flow meter`** | Coriolis, Magmeter, Thermal Mass & Vortex Flowmeters | Endress+Hauser / Micro Motion |
| **`CS-DS-07 Hand valve with positioner`**| Manual Valves with Limit Switch Boxes | Topworx / APL / Power-Genex |
| **`CS-DS-09 Level switch`** | Tuning Fork & Vibrating Level Switches | Endress+Hauser (Liquiphant/Soliphant) |
| **`CS-DS-10 Level transmitter`** | Guided Wave Radar & DP Level Transmitters | Vega / Endress+Hauser |
| **`CS-DS-11 Pressure Gauge`** | Stainless Steel Direct Dial Pressure Gauges | WIKA |
| **`CS-DS-12 Pressure Switch`** | High/Low Pressure Safety Switches | UE / Sor |
| **`CS-DS-13 Pressure Transmitter`** | Process Pressure Transmitters (4-20mA HART) | Yokogawa EJX / E+H |
| **`CS-DS-15 Temp gauge`** | Bi-metal Temperature Gauges | WIKA |
| **`CS-DS-16Temp transmitter`** | Head-mount RTD Temperature Transmitters | Endress+Hauser iTEMP |
| **`CS-DS-17 Pneumatic on-off valve`** | Automated On-Off Butterfly & Ball Valves | Keystone / TeroFox / Sanmax |
| **`CS-DS-20 Control valve Sanmax`** | Modulating Steam & Slurry Control Valves | Sanmax / Samson |
| **`CS-DS-22 Temp Switch`** | Temperature Limit Switches | UE |
| **[Pepperl+Fuchs IS Barriers](file:///e:/xApp-01/x260911-002-KalasinEngineering/02_Electrical_and_eDrawing/05_Instrument_Manuals/Pepperl%2BFuchs%20IS%20Barriers/README.md)** | Intrinsically Safe Galvanic Isolators & Baseplates | Pepperl+Fuchs K-System |
| **`Pneumatic Vibrating`** | Hopper & Cyclone Air Vibrators | Netter Vibration |
