x92120/x260911-002-KalasinEngineering/02_Electrical_and_eDrawing/05_Instrument_Manuals/Pepperl+Fuchs IS Barriers/README.md

# Pepperl+Fuchs Intrinsically Safe (IS) Isolated Barriers & Termination Boards
**Project:** Ingredion Kalasin Spray Dryer Plant — Sprint 18K TPA  
**Enclosure Location:** Panel `CA-IS` (Intrinsically Safe Marshaling Enclosure / Field Ex Area Boundary)  
**System Role:** Galvanic Isolation & Zener Barriers for Hazardous Area (Zone 0/1/20/21) Field Instruments and Actuators

---

## 📁 Technical Manuals & Datasheet Register

| Document File | Descriptive Alias | Manufacturer | Model / Type | Signal / Function | Safety Rating | Description |
| :--- | :--- | :--- | :--- | :--- | :---: | :--- |
| [216711_eng.pdf](file:///e:/xApp-01/x260911-002-KalasinEngineering/02_Electrical_and_eDrawing/05_Instrument_Manuals/Pepperl%2BFuchs%20IS%20Barriers/216711_eng.pdf) | [HiC2821_Switch_Amplifier_DI_Barrier.pdf](file:///e:/xApp-01/x260911-002-KalasinEngineering/02_Electrical_and_eDrawing/05_Instrument_Manuals/Pepperl%2BFuchs%20IS%20Barriers/HiC2821_Switch_Amplifier_DI_Barrier.pdf) | Pepperl+Fuchs | **HiC2821** | Digital Input (DI) / NAMUR / Dry Contact | **SIL 2** | 1-channel isolated switch amplifier, 24VDC bus powered, 2 relay outputs, fault relay contact output, line fault detection (LFD). |
| [233883_eng.pdf](file:///e:/xApp-01/x260911-002-KalasinEngineering/02_Electrical_and_eDrawing/05_Instrument_Manuals/Pepperl%2BFuchs%20IS%20Barriers/233883_eng.pdf) | [HiC2871_Solenoid_Driver_DO_Barrier.pdf](file:///e:/xApp-01/x260911-002-KalasinEngineering/02_Electrical_and_eDrawing/05_Instrument_Manuals/Pepperl%2BFuchs%20IS%20Barriers/HiC2871_Solenoid_Driver_DO_Barrier.pdf) | Pepperl+Fuchs | **HiC2871** | Digital Output (DO) / Solenoid Driver | **SIL 3** | 1-channel isolated solenoid driver, loop powered, output 45 mA at 12 V DC, supplies Ex-proof solenoid valves, audible alarms, and beacon LEDs. |
| [260436_eng.pdf](file:///e:/xApp-01/x260911-002-KalasinEngineering/02_Electrical_and_eDrawing/05_Instrument_Manuals/Pepperl%2BFuchs%20IS%20Barriers/260436_eng.pdf) | [HiCTB16-SCT-44C-SC-RA_16Slot_Termination_Board.pdf](file:///e:/xApp-01/x260911-002-KalasinEngineering/02_Electrical_and_eDrawing/05_Instrument_Manuals/Pepperl%2BFuchs%20IS%20Barriers/HiCTB16-SCT-44C-SC-RA_16Slot_Termination_Board.pdf) | Pepperl+Fuchs | **HiCTB16-SCT-44C-SC-RA** | 16-Slot Motherboard / Baseplate | **SIL 2 / SIL 3** | Universal 16-module termination board, redundant 24VDC power supply inputs, blue screw terminals (hazardous side), black screw terminals (safe side). |
| [321423_eng.pdf](file:///e:/xApp-01/x260911-002-KalasinEngineering/02_Electrical_and_eDrawing/05_Instrument_Manuals/Pepperl%2BFuchs%20IS%20Barriers/321423_eng.pdf) | [HiC2025_SMART_Transmitter_Power_Supply_AI_Barrier.pdf](file:///e:/xApp-01/x260911-002-KalasinEngineering/02_Electrical_and_eDrawing/05_Instrument_Manuals/Pepperl%2BFuchs%20IS%20Barriers/HiC2025_SMART_Transmitter_Power_Supply_AI_Barrier.pdf) | Pepperl+Fuchs | **HiC2025** | Analog Input (AI) / SMART Transmitter | **SIL 2 (SC 3)** | 1-channel SMART transmitter power supply, 2-wire transmitter excitation, 4-20 mA or 1-5 V output, bidirectional HART communication transparent. |

---

## 🛠️ Panel CA-IS Engineering Application Architecture

```text
[ Hazardous Area: Zone 0 / 1 / 20 / 21 ]
(Spray Dryer Tower, Baghouse Filter, Dust Extraction)
          │
          ├── Ex NAMUR Proximity / Dry Contact Limit Switches
          │         │
          ├── Ex 24VDC / 12VDC Pneumatic Solenoid Valves
          │         │
          └── Ex 4-20mA HART Temperature / Pressure Transmitters
                    │
════════════════════╪══════════════════════════════════════════════════════
                    ▼ [ Blue Terminals - Hazardous Side ]
       ┌────────────────────────────────────────────────────────┐
       │     Pepperl+Fuchs Termination Board                    │
       │     HiCTB16-SCT-44C-SC-RA (260436)                     │
       │  ┌──────────────┐  ┌──────────────┐  ┌──────────────┐  │
       │  │ HiC2821 (DI) │  │ HiC2871 (DO) │  │ HiC2025 (AI) │  │
       │  │ Part 216711  │  │ Part 233883  │  │ Part 321423  │  │
       │  │ Switch Amp   │  │ Solenoid Drv │  │ SMART Tx Pwr │  │
       │  │ (SIL 2)      │  │ (SIL 3)      │  │ (SIL 2)      │  │
       │  └──────────────┘  └──────────────┘  └──────────────┘  │
       │    Redundant 24VDC Power Feed (QUINT4-PS / DIODE)      │
       └────────────────────────────────────────────────────────┘
                    ▲ [ Black Terminals - Safe Area Side ]
════════════════════╪══════════════════════════════════════════════════════
                    │
[ Non-Hazardous Control Room / Panel CA1 & CA-RIO Drops ]
          ├── To 1756-IB32 (Digital Inputs)
          ├── To 1756-OB32 (Digital Outputs via PLC-RSC Relays)
          └── To 1756-IF16 (Analog Inputs 4-20mA HART)
```
