x92120/x260911-002-KalasinEngineering/02_Electrical_and_eDrawing/04_PDF_Reports_and_Drawings/Instrument_Installation_Hookup_and_Wiring_Templates.pdf

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
INGREDION (THAILAND) CO., LTD.
KALASIN STARCH PLANT - JET COOKER PROJECT

## AEC INDUSTRIAL ENGINEERING

SYSTEMS INTEGRATION & AUTOMATION

## INSTRUMENT HOOK-UP & LOOP DRAWING DIRECTORY

INSTRUMENT HOOK-UP & TYPICAL LOOP DIAGRAM

## DWG NO: KAL-JC-TYP-000

REV: 3.6 DATE: 2026-09-08

DRAWN: AEC-ENG

CHECKED: LEAD-PE

STATUS: APPROVED

SCALE: N.T.S.

PROJECT NO:

R5THS00138-JC

| SHEET NO: 01 / 25

# KALASIN STARCH PLANT - JET COOKER PROJECT

# STANDARD INSTRUMENT HOOK-UP & TYPICAL ELECTRICAL LOOP DRAWINGS

## Based on Equipment Packages in 11-instrument Manual/ & Master I/O Mapping Rev 3.6

## DRAWING PACKAGE OBJECTIVES & ENGINEERING STANDARDS

Project Scope: | Jet Cooker Slurry & Flash Tank Instrumentation
Client / Owner: | INGREDION (THAILAND) CO., LTD.
Plant Location: | Kalasin Starch Manufacturing Plant, Thailand
System Integrator: | AEC INDUSTRIAL ENGINEERING CO., LTD.
Covered Packages: | 23 Complete Equipment Types (CS-DS-01 to CS-DS-22)
Drawing Contents: | Piping Hook-Up, Loop Wiring Schematic & BOM
Electrical Standard: | Rockwell ControlLogix 1756 Architecture (24V DC / 4-20mA)
Hazardous Areas: | Ex ia / Ex d Classifications (937T Barriers & Glands)
CAD Standard: | 1:1 Metric Millimeters (AutoCAD DXF R2010 Layered)
Piping Standard: | ASME B16.5 Cl.150/300 RF Flanges & NPT Threads
Document Status: | APPROVED ENGINEERING TEMPLATES (Rev 3.6)

## DRAWING SYMBOLOGY & CAD LAYER CONVENTIONS

## Process Piping:

### Heavy solid line (0.7mm), showing process flow direction

## Impulse Tubing:

### Medium dashed line, 1/2" OD seamless SS316 tubing

## Instrument Air:

### Pneumatic air supply line, 6.0 bar dry filtered air

## Analog Signal (AI/AO):

### 4-20mA HART loop, shielded twisted pair (Belden 8761)

## Discrete Signal (DI/DO):

### 24V DC wetted contact or solenoid drive (Belden 9533)

## IS Barrier (Ex ia):

### Sky Blue block, Rockwell 937T Series Intrinsically Safe

## Interposing Relay:

### Orange block, Allen-Bradley 700-HL Series 24VDC Relay

## Terminal Strip:

### Green circle/box, Marshalling Panel CA1 (C#S##-X1)

## Earth Grounding:

### Protective Earth (PE) & Instrument Isolated Clean Earth (IE)

PREPARED BY

AEC INDUSTRIAL ENG.

Lead Instrumentation Eng.

CHECKED BY

## AEC AUTOMATION LEAD

System Architect & PE

VERIFIED BY

## PROJECT ELECTRICAL PE

Licensed Professional Eng.

APPROVED BY

INGREDION PROJECT MGR.

Client Automation Lead

A A

B B

C C

D D

E E

F F

INGREDION (THAILAND) CO., LTD.
KALASIN STARCH PLANT - JET COOKER PROJECT

## AEC INDUSTRIAL ENGINEERING

SYSTEMS INTEGRATION & AUTOMATION

## INSTRUMENT TEMPLATE DRAWING DIRECTORY

INSTRUMENT HOOK-UP & TYPICAL LOOP DIAGRAM

## DWG NO: KAL-JC-TYP-000-IDX

REV: 3.6 DATE: 2026-09-08

02 / 25

# MASTER DRAWING INDEX - 23 INSTRUMENT HOOK-UP & LOOP DIAGRAM TEMPLATES

SHT | DRAWING NO | EQUIPMENT CATEGORY / TEMPLATE TITLE | REV | STATUS
03 | KAL-JC-TYP-001 | DUST / PARTICULATE ANALYZER HOOK-UP & LO.. Mfr: ENVEA / PCME | Model: PCME QAL 991 (Electrodynamic | 3.6 | APPROVED
04 | KAL-JC-TYP-002 | COMBUSTIBLE LEL GAS DETECTOR HOOK-UP & L..
| | Mfr: Sensidyne / SmartGas | Model: 925FGD Explosionproof Hydroc
3.6 | APPROVED
05 | KAL-JC-TYP-003 | pH ANALYTICAL MEASUREMENT LOOP HOOK-UP &..
| | Mfr: Mettler Toledo | Model: M300G2 4-Wire Transmitter +
3.6 | APPROVED
06 | KAL-JC-TYP-004 | DIFFERENTIAL PRESSURE GAUGE HOOK-UP & ME..
| | Mfr: Ashcroft | Model: Model 1132 (Piston-Type Diff
3.6 | APPROVED
07 | KAL-JC-TYP-005 | DIFFERENTIAL PRESSURE TRANSMITTER HOOK-U..
| | Mfr: Endress+Hauser | Model: Deltabar PMD55B (Piezoresist
3.6 | APPROVED
08 | KAL-JC-TYP-006 | CORIOLIS MASS FLOWMETER HOOK-UP & LOOP D..
| | Mfr: Endress+Hauser | Model: Promass E 300 (8E3B50 / Dual
3.6 | APPROVED
09 | KAL-JC-TYP-007 | ELECTROMAGNETIC FLOWMETER HOOK-UP & LOOP..
| | Mfr: Endress+Hauser | Model: Promag P 300 (5P3B50 / 80 /
3.6 | APPROVED
10 | KAL-JC-TYP-008 | VORTEX STEAM FLOWMETER HOOK-UP & LOOP DI..
| | Mfr: Endress+Hauser | Model: Prowirl F 200 (7F2C80 / 1H w
3.6 | APPROVED
11 | KAL-JC-TYP-009 | THERMAL MASS GAS FLOWMETER HOOK-UP & LOO..
| | Mfr: Endress+Hauser | Model: t-mass F 300 / I 300 (6F3B /
3.6 | APPROVED
12 | KAL-JC-TYP-010 | ULTRASONIC CLAMP-ON FLOWMETER HOOK-UP & ..
| | Mfr: Keyence | Model: FD-H Series (FD-H20 / FD-H32
3.6 | APPROVED
13 | KAL-JC-TYP-011 | MANUAL HAND VALVE POSITION SWITCH HOOK-U..
| | Mfr: TeroFox / APL-HKC | Model: TF-20DFS Ball Valve + APL-21
3.6 | APPROVED
14 | KAL-JC-TYP-012 | LIQUID LEVEL SWITCH (VIBRATING FORK) HOO..
| | Mfr: Endress+Hauser | Model: Liquiphant FTL51B (Tuning Fo
3.6 | APPROVED
15 | KAL-JC-TYP-013 | SOLID LEVEL SWITCH (POWDER FORK) HOOK-UP..
| | Mfr: Endress+Hauser | Model: Soliphant FTM51 (Vibrating F
3.6 | APPROVED
SHT | DRAWING NO | EQUIPMENT CATEGORY / TEMPLATE TITLE | REV | STATUS
16 | KAL-JC-TYP-014 | RADAR LEVEL TRANSMITTER (80 GHz) HOOK-UP.. Mfr: Endress+Hauser | Model: Micropilot FMR67B (80 GHz Hi | 3.6 | APPROVED
17 | KAL-JC-TYP-015 | PRESSURE GAUGE & SIPHON HOOK-UP & MECHAN..
| | Mfr: Ashcroft | Model: Model T5500 (100mm Dial All-
3.6 | APPROVED
18 | KAL-JC-TYP-016 | ELECTRONIC PRESSURE SWITCH HOOK-UP & LOO..
| | Mfr: Endress+Hauser | Model: Ceraphant PTC31B (Ceramic Se
3.6 | APPROVED
19 | KAL-JC-TYP-017 | PRESSURE TRANSMITTER HOOK-UP & LOOP DIAG..
| | Mfr: Endress+Hauser | Model: Cerabar PMP51B / PMC51B (Met
3.6 | APPROVED
20 | KAL-JC-TYP-018 | BIMETAL TEMPERATURE GAUGE & THERMOWELL H..
| | Mfr: Ashcroft | Model: Model FI (100mm Dial Everyan
3.6 | APPROVED
21 | KAL-JC-TYP-019 | TEMPERATURE TRANSMITTER (RTD Pt100) HOOK..
| | Mfr: Endress+Hauser | Model: iTEMP TMT71 + Omnigrad M TM4
3.6 | APPROVED
22 | KAL-JC-TYP-020 | PNEUMATIC ON-OFF CONTROL VALVE HOOK-UP &..
| | Mfr: TeroFox / El-O-Matic | Model: TF-20DFS Ball Valve + F-Seri
3.6 | APPROVED
23 | KAL-JC-TYP-021 | MODULATING GLOBE CONTROL VALVE HOOK-UP &..
| | Mfr: Samson | Model: Type 3241 Globe Valve + Trov
3.6 | APPROVED
24 | KAL-JC-TYP-022 | ELECTRONIC TEMPERATURE SWITCH HOOK-UP & ..
| | Mfr: Endress+Hauser | Model: Thermophant TTR35 (Compact P
3.6 | APPROVED
25 | KAL-JC-TYP-023 | PNEUMATIC TURBINE VIBRATOR HOOK-UP & LOO..
| | Mfr: Netter Vibration | Model: NCT 5 Pneumatic Turbine Vibr
3.6 | APPROVED

DWG NO:; KAL-JC-TYP-001; REV: 3.6 DATE: 2026-09-08; TEMPLATE TYP-01: DUST / PARTICULATE ANALYZER; TYPICAL TAGS: AT-60241 Series; SERVICE: Exhaust Duct Dust Emission Monitoring | PLC I/O: 1756-IF16 (AI) & 1756-IB32 (DI Alarm); FLOW DIRECTION; ENVEA / PCME; Dust / Particu; Process Connection:; DN100 Flange w/ Purge Air (1..; Mounting Type:; Direct Flanged / 2" Pipe Stand; Enclosure Rating:; IP65 Weatherproof Cast Alumi..; Hazardous Class:; ATEX Zone 21/22 Dust Ex tb I..; Process Medium: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

SECTION A: PROCESS PIPING & MECHANICAL HOOK-UP

SECTION B: ELECTRICAL LOOP WIRING SCHEMATIC (FIELD TO PLC)

SECTION C: BILL OF MATERIALS (BOM) & NOTES

MANUFACTURER: ENVEA / PCME

MODEL: PCME QAL 991 (Electrodynamic / Optical)

SERVICE: Exhaust Duct Dust Emission Monitoring

1 Dust Transmitter Sensor Unit

PROCESS SLURRY / STEAM PIPE

2 Mating Counter-Flange DN100 PN

3 Purge Air Filter Regulator & G

SMC 1/4" BSP w/ Bracket

4 Cable Gland M20x1.5 Ex d/e

Nickel-plated Brass

5 Instrument Stand 2" Pipe & Bas

Hot-dip Galvanized Steel

ENGINEERING INSTALLATION NOTES

2Px1.5mm² IS Shielded Overal
CLEAN INSTRUMENT GROUND BUS (IE) - CONNECTED TO CA1 MASTER GROUND

1. Mount sensor on straight run min. 5D downstream, 2D upstream of duct bends.

2. Instrument air purge must remain continuously ON to prevent window fouling.

3. Shield drain wire must be isolated in field and grounded only at Marshalling Cabinet CA1 earth bar.

2" STANCHION PIPE STAND

ELECTRICAL & SIGNAL LOOP SPECIFICATIONS

MECHANICAL HOOK-UP SPECIFICATION

INGREDION (THAILAND) CO., LTD.
KALASIN STARCH PLANT - JET COOKER PROJECT

AEC INDUSTRIAL ENGINEERING
SYSTEMS INTEGRATION & AUTOMATION

DUST / PARTICULATE ANALYZER HOOK-UP & LOOP DIAGRAM

INSTRUMENT HOOK-UP & TYPICAL LOOP DIAGRAM

DWG NO:; KAL-JC-TYP-002; REV: 3.6 DATE: 2026-09-08; TEMPLATE TYP-02: COMBUSTIBLE LEL GAS ANALYZER; TYPICAL TAGS: AIT-60101 / AIT-60201; SERVICE: Explosion Hazard Lower Explosive Limit (LEL) Monitor | PLC I/O: 1756-IF16 (AI LEL) & 1756-IB32 (DI Alarm); FLOW DIRECTION; Sensidyne /; Combustible LE; Process Connection:; Ambient Air Diffusion / Spla..; Mounting Type:; Direct Flanged / 2" Pipe Stand; Enclosure Rating:; NEMA 4X / IP66 Heavy-duty Ex..; Hazardous Class:; Class I, Div 1, Grp BCD / Ex..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

SECTION A: PROCESS PIPING & MECHANICAL HOOK-UP

SECTION B: ELECTRICAL LOOP WIRING SCHEMATIC (FIELD TO PLC)

SECTION C: BILL OF MATERIALS (BOM) & NOTES

MANUFACTURER: SENSIDYNE / SMARTGAS

MODEL: 925FGD Explosionproof Hydrocarbon Gas Detector

SERVICE: Explosion Hazard Lower Explosive Limit (LEL) Monitor

1 Gas Detector Transmitter 925FG

PROCESS SLURRY / STEAM PIPE

Sensidyne Infrared / Catalytic

2 Weather Guard / Dust Protectio

3 Calibration Adapter & Cup

Molded PVC / Viton O-ring

4 Explosionproof Cable Gland 3/4

5 Wall / Stanchion Mounting Brac

ENGINEERING INSTALLATION NOTES

3Cx1.5mm² Shielded Fire-Resi
CLEAN INSTRUMENT GROUND BUS (IE) - CONNECTED TO CA1 MASTER GROUND

1. Install 0.3m to 0.5m above floor for gases heavier than air, or near ceiling for lighter gases.

2. Field sensor must undergo zero and span gas calibration prior to plant commissioning.

3. Wiring must run in rigid galvanized steel conduit or approved armored flameproof cable.

2" STANCHION PIPE STAND

ELECTRICAL & SIGNAL LOOP SPECIFICATIONS

MECHANICAL HOOK-UP SPECIFICATION

INGREDION (THAILAND) CO., LTD.
KALASIN STARCH PLANT - JET COOKER PROJECT

AEC INDUSTRIAL ENGINEERING
SYSTEMS INTEGRATION & AUTOMATION

COMBUSTIBLE LEL GAS DETECTOR HOOK-UP & LOOP DIAGRAM

INSTRUMENT HOOK-UP & TYPICAL LOOP DIAGRAM

DWG NO:; KAL-JC-TYP-003; REV: 3.6 DATE: 2026-09-08; TEMPLATE TYP-03: PH ANALYTICAL LOOP; TYPICAL TAGS: AIT-40101 / AIT-40201; SERVICE: Cooker Slurry & Flash Tank pH Neutralization | PLC I/O: 1756-IF16 (AI pH) & 1756-IB32 (DI Alarms); FLOW DIRECTION; Mettler Tole; pH Analytical; Process Connection:; DN25 Weld-in Socket (Incline..; Mounting Type:; Direct Flanged / 2" Pipe Stand; Enclosure Rating:; NEMA 4X / IP65 Polycarbonate..; Hazardous Class:; ATEX II 1/2G Ex ia IIC T6/T4..; Process Medium: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

SECTION A: PROCESS PIPING & MECHANICAL HOOK-UP

SECTION B: ELECTRICAL LOOP WIRING SCHEMATIC (FIELD TO PLC)

SECTION C: BILL OF MATERIALS (BOM) & NOTES

MANUFACTURER: METTLER TOLEDO

MODEL: M300G2 4-Wire Transmitter + InPro3250i + InTrac 777P

SERVICE: Cooker Slurry & Flash Tank pH Neutralization

1 pH Multi-Parameter Transmitter

PROCESS SLURRY / STEAM PIPE

Mettler Toledo M300 4-Wire

2 Intelligent pH Sensor InPro325

Pre-pressurized Liquid Gel

3 Retractable Housing InTrac 777

4 Weld-in Socket 40mm / DN25 (15

5 2" Pipe Mounting Kit for M300G

ENGINEERING INSTALLATION NOTES

VP6 High-Z Cable to Tx + 2Px
CLEAN INSTRUMENT GROUND BUS (IE) - CONNECTED TO CA1 MASTER GROUND

1. Weld socket must be installed inclined at min. 15° above horizontal to prevent air bubble entrapment.

2. Use retractable housing safety interlock valve before extracting probe during process operation.

3. Ground transmitter chassis directly to plant PE bar with min. 4mm² copper grounding strap.

2" STANCHION PIPE STAND

ELECTRICAL & SIGNAL LOOP SPECIFICATIONS

MECHANICAL HOOK-UP SPECIFICATION

INGREDION (THAILAND) CO., LTD.
KALASIN STARCH PLANT - JET COOKER PROJECT

AEC INDUSTRIAL ENGINEERING
SYSTEMS INTEGRATION & AUTOMATION

pH ANALYTICAL MEASUREMENT LOOP HOOK-UP & LOOP DIAGRAM

INSTRUMENT HOOK-UP & TYPICAL LOOP DIAGRAM

DWG NO:; KAL-JC-TYP-004; REV: 3.6 DATE: 2026-09-08; TEMPLATE TYP-04: DIFF. PRESSURE GAUGE; TYPICAL TAGS: PDI-40101 / PDI-60201; SERVICE: Bag Filter / Steam Strainer Differential Pressure | PLC I/O: None (Local Operator Readout); FLOW DIRECTION; Ashcroft; Diff. Pressure; Process Connection:; 1/4" NPT Female w/ 3-Valve D..; Mounting Type:; Direct Flanged / 2" Pipe Stand; Enclosure Rating:; IP65 Stainless Steel Case, G..; Hazardous Class:; Non-Electrical Apparatus / S..; Process Medium: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

SECTION A: PROCESS PIPING & MECHANICAL HOOK-UP

SECTION B: ELECTRICAL LOOP WIRING SCHEMATIC (FIELD TO PLC)

SECTION C: BILL OF MATERIALS (BOM) & NOTES

MODEL: Model 1132 (Piston-Type Differential Gauge)

SERVICE: Bag Filter / Steam Strainer Differential Pressure

1 Differential Pressure Gauge 11

PROCESS SLURRY / STEAM PIPE

2 3-Valve Instrument Manifold V0

3 Impulse Tubing 1/2" OD x 0.049

4 Compression Tube Fittings 1/2"

Double Ferrule SS316 (Swagelok)

5 Gauge Mounting Bracket 2" Pipe

SS304 Angle Bracket & Clamps

ENGINEERING INSTALLATION NOTES

N/A (Local Mechanical Dial)
CLEAN INSTRUMENT GROUND BUS (IE) - CONNECTED TO CA1 MASTER GROUND

1. High (HP) and Low (LP) pressure impulse lines must slope min. 1:12 downward toward drain pots.

2. Operate 3-valve manifold equalizing valve before opening process isolation valves to protect sensor.

3. Provide blow-down bleed valves on both impulse legs for routine cleaning and purging.

2" STANCHION PIPE STAND

ELECTRICAL & SIGNAL LOOP SPECIFICATIONS

MECHANICAL HOOK-UP SPECIFICATION

INGREDION (THAILAND) CO., LTD.
KALASIN STARCH PLANT - JET COOKER PROJECT

AEC INDUSTRIAL ENGINEERING
SYSTEMS INTEGRATION & AUTOMATION

DIFFERENTIAL PRESSURE GAUGE HOOK-UP & MECHANICAL DETAIL

INSTRUMENT HOOK-UP & TYPICAL LOOP DIAGRAM

DWG NO:; KAL-JC-TYP-005; REV: 3.6 DATE: 2026-09-08; TEMPLATE TYP-05: DIFF. PRESSURE TRANSMITTER; TYPICAL TAGS: DPT-60201 / DPT-60901; SERVICE: Filter Differential Pressure / Orifice Flow Drop | PLC I/O: 1756-IF16 (16-Point Diff Analog Input); FLOW DIRECTION; Endress+Haus; Diff. Pressure; Process Connection:; 1/4" NPT Female w/ 5-Valve M..; Mounting Type:; Direct Flanged / 2" Pipe Stand; Enclosure Rating:; NEMA 4X / IP66/68 Dual-Compa..; Hazardous Class:; ATEX II 1/2G Ex ia IIC T6 Ga..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

SECTION A: PROCESS PIPING & MECHANICAL HOOK-UP

SECTION B: ELECTRICAL LOOP WIRING SCHEMATIC (FIELD TO PLC)

SECTION C: BILL OF MATERIALS (BOM) & NOTES

MANUFACTURER: ENDRESS+HAUSER

MODEL: Deltabar PMD55B (Piezoresistive / Ceramic)

SERVICE: Filter Differential Pressure / Orifice Flow Drop

PROCESS SLURRY / STEAM PIPE

2 5-Valve Manifold DA63M (Flange

SS316 Integrated Bleed Valves

3 2" Pipe Mounting Bracket Kit

SS304 Stanchion Bracket & U-Bolt

4 Cable Gland M20x1.5 Ex d/e IP6

Nickel-Plated Brass Armored Glan

5 Impulse Tubing 1/2" OD x 0.049

ENGINEERING INSTALLATION NOTES

1Px1.5mm² Twisted Shielded (
CLEAN INSTRUMENT GROUND BUS (IE) - CONNECTED TO CA1 MASTER GROUND

1. Mount transmitter below process tapping points for liquid service to maintain filled impulse lines.

2. 5-valve manifold sequence: Open equalizing, open HP & LP blocks, close equalizing, check zero.

3. Connect 2-wire loop to PLC 1756-IF16 terminals: (+) to 24V loop power, (-) to Channel Input.

2" STANCHION PIPE STAND

ELECTRICAL & SIGNAL LOOP SPECIFICATIONS

MECHANICAL HOOK-UP SPECIFICATION

INGREDION (THAILAND) CO., LTD.
KALASIN STARCH PLANT - JET COOKER PROJECT

AEC INDUSTRIAL ENGINEERING
SYSTEMS INTEGRATION & AUTOMATION

DIFFERENTIAL PRESSURE TRANSMITTER HOOK-UP & LOOP DIAGRAM

INSTRUMENT HOOK-UP & TYPICAL LOOP DIAGRAM

DWG NO:; KAL-JC-TYP-006; REV: 3.6 DATE: 2026-09-08; TEMPLATE TYP-06: CORIOLIS FLOWMETER; TYPICAL TAGS: FT-40201 Series; SERVICE: Starch Slurry High-Accuracy Mass Flow & Density | PLC I/O: 1756-IF16 (Ch. 1 Mass Flow / Ch. 2 Density); FLOW DIRECTION; Endress+Haus; Coriolis Flowm; Process Connection:; DN50 (2") ASME B16.5 Cl.150 ..; Mounting Type:; Direct Flanged / 2" Pipe Stand; Enclosure Rating:; IP67 Die-cast Aluminum Trans..; Hazardous Class:; ATEX II 2G Ex db eb ia IIC T..; Process Medium: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

SECTION A: PROCESS PIPING & MECHANICAL HOOK-UP

SECTION B: ELECTRICAL LOOP WIRING SCHEMATIC (FIELD TO PLC)

SECTION C: BILL OF MATERIALS (BOM) & NOTES

MANUFACTURER: ENDRESS+HAUSER

MODEL: Promass E 300 (8E3B50 / Dual Tube SS316L)

SERVICE: Starch Slurry High-Accuracy Mass Flow & Density

1 Promass E 300 Coriolis Flowmet

PROCESS SLURRY / STEAM PIPE

E+H DN50 Cl.150 SS316L Dual Tube

2 Companion Counter-Flanges DN50

ASTM A182 F316 / RF Flanges

3 PTFE / Spiral Wound Gaskets

316SS with PTFE Filler

4 Cable Glands M20x1.5 Ex d/e

Nickel-plated Brass Armored Glan

5 Pipe Support Clamps & Structur

Heavy Duty Rigidity Anchors

ENGINEERING INSTALLATION NOTES

2Px1.5mm² Shielded Overall (
CLEAN INSTRUMENT GROUND BUS (IE) - CONNECTED TO CA1 MASTER GROUND

1. Sensor tubes must be installed pointing downwards (flag-down) for liquid slurry to prevent gas collection.

2. Support pipeline rigidly on both upstream and downstream sides within 2 pipe diameters of meter flanges.

3. Do not clamp or attach pipe supports directly to the Coriolis sensor housing.

2" STANCHION PIPE STAND

ELECTRICAL & SIGNAL LOOP SPECIFICATIONS

MECHANICAL HOOK-UP SPECIFICATION

INGREDION (THAILAND) CO., LTD.
KALASIN STARCH PLANT - JET COOKER PROJECT

AEC INDUSTRIAL ENGINEERING
SYSTEMS INTEGRATION & AUTOMATION

CORIOLIS MASS FLOWMETER HOOK-UP & LOOP DIAGRAM

INSTRUMENT HOOK-UP & TYPICAL LOOP DIAGRAM

DWG NO:; KAL-JC-TYP-007; REV: 3.6 DATE: 2026-09-08; TEMPLATE TYP-07: ELECTROMAGNETIC FLOWMETER; TYPICAL TAGS: FT-40202 / FT-60201; SERVICE: Slurry & Process Water Volumetric Flow Measurement | PLC I/O: 1756-IF16 (4-20mA Flow) & 1756-IB32 (Pulse Counter); FLOW DIRECTION; Endress+Haus; Electromagneti; Process Connection:; DN50/80/100 ASME Cl.150 RF F..; Mounting Type:; Direct Flanged / 2" Pipe Stand; Enclosure Rating:; NEMA 4X / IP67 Aluminum Tran..; Hazardous Class: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

SECTION A: PROCESS PIPING & MECHANICAL HOOK-UP

SECTION B: ELECTRICAL LOOP WIRING SCHEMATIC (FIELD TO PLC)

SECTION C: BILL OF MATERIALS (BOM) & NOTES

MANUFACTURER: ENDRESS+HAUSER

MODEL: Promag P 300 (5P3B50 / 80 / 1H PTFE Liner)

SERVICE: Slurry & Process Water Volumetric Flow Measurement

1 Promag P 300 Magmeter Sensor &

PROCESS SLURRY / STEAM PIPE

E+H PTFE Lined, Hastelloy C Elec

2 Grounding Rings / Discs SS316L

E+H Grounding Electrodes Kit

3 PTFE Envelope Flange Gaskets

Chemical Resistant Gaskets

4 Cable Glands M20x1.5 Ex d/e

Nickel-plated Brass Glands

5 Grounding Cables 6mm² Green/Ye

Copper Earthing Strap with Lugs

ENGINEERING INSTALLATION NOTES

1Px1.5mm² (Analog) + 1Px1.5m
CLEAN INSTRUMENT GROUND BUS (IE) - CONNECTED TO CA1 MASTER GROUND

1. Straight piping requirements: min. 5D upstream and 2D downstream of flowmeter.

2. Install grounding rings between meter flanges and pipe counter-flanges to ensure reference ground.

3. Pipe must always remain 100% full of conductive liquid for accurate flow measurement.

2" STANCHION PIPE STAND

ELECTRICAL & SIGNAL LOOP SPECIFICATIONS

MECHANICAL HOOK-UP SPECIFICATION

INGREDION (THAILAND) CO., LTD.
KALASIN STARCH PLANT - JET COOKER PROJECT

AEC INDUSTRIAL ENGINEERING
SYSTEMS INTEGRATION & AUTOMATION

ELECTROMAGNETIC FLOWMETER HOOK-UP & LOOP DIAGRAM

INSTRUMENT HOOK-UP & TYPICAL LOOP DIAGRAM

DWG NO:; KAL-JC-TYP-008; REV: 3.6 DATE: 2026-09-08; TEMPLATE TYP-08: VORTEX FLOWMETER; TYPICAL TAGS: FT-60101 / FT-60202; SERVICE: High-Pressure Saturated Steam Flow Measurement | PLC I/O: 1756-IF16 (Compensated Mass Flow Steam); FLOW DIRECTION; Endress+Haus; Vortex Flowmet; Process Connection:; DN80/100 (3"/4") ASME Cl.300..; Mounting Type:; Direct Flanged / 2" Pipe Stand; Enclosure Rating:; Dual-Compartment IP67 Die-ca..; Hazardous Class:; ATEX II 1/2G Ex ia IIC T6 Ga..; Process Medium: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

SECTION A: PROCESS PIPING & MECHANICAL HOOK-UP

SECTION B: ELECTRICAL LOOP WIRING SCHEMATIC (FIELD TO PLC)

SECTION C: BILL OF MATERIALS (BOM) & NOTES

MANUFACTURER: ENDRESS+HAUSER

MODEL: Prowirl F 200 (7F2C80 / 1H with Temp Sensor)

SERVICE: High-Pressure Saturated Steam Flow Measurement

1 Prowirl F 200 Flanged Vortex M

PROCESS SLURRY / STEAM PIPE

E+H SS316 Cast Body w/ DSC Senso

2 Counter-Flanges DN80 Cl.300 RF

3 Spiral Wound Gaskets Cl.300 Gr

Graphite Filled SS316 Rings

4 Cable Gland M20x1.5 Ex d/e Hig

Brass Nickel-Plated Gland

5 Pipeline Insulation Spacer & S

Thermal Extension Neck Jacket

ENGINEERING INSTALLATION NOTES

1Px1.5mm² Twisted Shielded (
CLEAN INSTRUMENT GROUND BUS (IE) - CONNECTED TO CA1 MASTER GROUND

1. Straight piping: min. 15D upstream and 5D downstream from flow disturbers (valves, reducers).

2. Insulate pipe line up to meter neck, but leave transmitter electronics housing uninsulated.

3. Verify that internal integrated Pt100 temperature compensation is activated in HART configuration.

2" STANCHION PIPE STAND

ELECTRICAL & SIGNAL LOOP SPECIFICATIONS

MECHANICAL HOOK-UP SPECIFICATION

INGREDION (THAILAND) CO., LTD.
KALASIN STARCH PLANT - JET COOKER PROJECT

AEC INDUSTRIAL ENGINEERING
SYSTEMS INTEGRATION & AUTOMATION

VORTEX STEAM FLOWMETER HOOK-UP & LOOP DIAGRAM

INSTRUMENT HOOK-UP & TYPICAL LOOP DIAGRAM

DWG NO:; KAL-JC-TYP-009; REV: 3.6 DATE: 2026-09-08; TEMPLATE TYP-09: THERMAL MASS FLOWMETER; TYPICAL TAGS: FT-80301 Series; SERVICE: LPG / Natural Gas Boiler Fuel Consumption | PLC I/O: 1756-IF16 (AI Gas Flow) & 1756-IB32 (DI Alarm); FLOW DIRECTION; Endress+Haus; Thermal Mass F; Process Connection:; DN100 Flange / 1" NPT Retrac..; Mounting Type:; Direct Flanged / 2" Pipe Stand; Enclosure Rating:; NEMA 4X / IP67 Aluminum Encl..; Hazardous Class:; ATEX II 2G Ex db eb ia IIC T..; Process Medium: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

SECTION A: PROCESS PIPING & MECHANICAL HOOK-UP

SECTION B: ELECTRICAL LOOP WIRING SCHEMATIC (FIELD TO PLC)

SECTION C: BILL OF MATERIALS (BOM) & NOTES

MANUFACTURER: ENDRESS+HAUSER

MODEL: t-mass F 300 / I 300 (6F3B / 6I3B Insertion)

SERVICE: LPG / Natural Gas Boiler Fuel Consumption

1 t-mass 300 Thermal Flowmeter T

PROCESS SLURRY / STEAM PIPE

E+H Insertion Probe w/ Hot-Tap

2 Weld-in Boss 1" NPT Female Thr

ASTM A105 / Carbon Steel Boss

3 Isolation Ball Valve 1" Full B

SS316 Cl.300 Gas Ball Valve

4 Cable Gland M20x1.5 Ex d Flame

Brass Gland for Armored Cable

5 Grounding Cable 6mm² w/ Lug

Copper Earthing Conductor

ENGINEERING INSTALLATION NOTES

2Px1.5mm² Shielded Armored (
CLEAN INSTRUMENT GROUND BUS (IE) - CONNECTED TO CA1 MASTER GROUND

1. Install probe at centerline of pipe (0.5 x Inside Diameter) matching flow direction arrow exactly.

2. Verify straight pipe run: min. 20D upstream and 5D downstream of insertion tap.

3. Equipotential bonding must be connected between meter body and gas piping system.

2" STANCHION PIPE STAND

ELECTRICAL & SIGNAL LOOP SPECIFICATIONS

MECHANICAL HOOK-UP SPECIFICATION

INGREDION (THAILAND) CO., LTD.
KALASIN STARCH PLANT - JET COOKER PROJECT

AEC INDUSTRIAL ENGINEERING
SYSTEMS INTEGRATION & AUTOMATION

THERMAL MASS GAS FLOWMETER HOOK-UP & LOOP DIAGRAM

INSTRUMENT HOOK-UP & TYPICAL LOOP DIAGRAM

DWG NO:; KAL-JC-TYP-010; REV: 3.6 DATE: 2026-09-08; TEMPLATE TYP-10: ULTRASONIC CLAMP-ON FLOWMETER; TYPICAL TAGS: FIT-40105 Series; SERVICE: Cooling Water & Non-Invasive Slurry Verification | PLC I/O: 1756-IF16 (AI Flow Rate) & 1756-IB32 (Pulse); FLOW DIRECTION; Keyence; Ultrasonic Cla; Process Connection:; External Pipe Surface Mount ..; Mounting Type:; Direct Flanged / 2" Pipe Stand; Enclosure Rating:; IP67 / IP69K Hygienic Stainl..; Hazardous Class:; General Industrial Area / No..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

SECTION A: PROCESS PIPING & MECHANICAL HOOK-UP

SECTION B: ELECTRICAL LOOP WIRING SCHEMATIC (FIELD TO PLC)

SECTION C: BILL OF MATERIALS (BOM) & NOTES

MODEL: FD-H Series (FD-H20 / FD-H32 Clamp-on)

SERVICE: Cooling Water & Non-Invasive Slurry Verification

1 Clamp-on Ultrasonic Sensor Hea

PROCESS SLURRY / STEAM PIPE

Keyence FD-H20 / H32 Unit

Direct 24V DC Fi

2 Acoustic Coupling Gel / Pad

High-Stability Silicone Couplant

3 Pipe Mounting Clamp Bands SS30

Adjustable Worm Gear Straps

4 M12 4-Pin Shielded Cable (5m)

PUR Oil-Resistant Flex Cable

5 Field Termination Box (Local)

IP66 Junction Box w/ DIN Rail

ENGINEERING INSTALLATION NOTES

4Cx0.75mm² Factory Pre-Wired
CLEAN INSTRUMENT GROUND BUS (IE) - CONNECTED TO CA1 MASTER GROUND

1. Clean pipe surface thoroughly with emery cloth to remove rust, paint, and scale before mounting.

2. Apply generous bead of acoustic coupling compound between sensor transducers and pipe wall.

3. Clamp unit securely on horizontal pipe at 3 o'clock or 9 o'clock position (never top or bottom).

2" STANCHION PIPE STAND

ELECTRICAL & SIGNAL LOOP SPECIFICATIONS

MECHANICAL HOOK-UP SPECIFICATION

INGREDION (THAILAND) CO., LTD.
KALASIN STARCH PLANT - JET COOKER PROJECT

AEC INDUSTRIAL ENGINEERING
SYSTEMS INTEGRATION & AUTOMATION

ULTRASONIC CLAMP-ON FLOWMETER HOOK-UP & LOOP DIAGRAM

INSTRUMENT HOOK-UP & TYPICAL LOOP DIAGRAM

DWG NO:; KAL-JC-TYP-011; REV: 3.6 DATE: 2026-09-08; TEMPLATE TYP-11: HAND VALVE WITH SWITCH BOX; TYPICAL TAGS: ZSO-40101 / ZSC-40101; SERVICE: Manual Safety Isolation Valve Open/Closed Status | PLC I/O: 1756-IB32 (32-Point 24VDC Digital Input); FLOW DIRECTION; TeroFox / AP; Process Connection:; Flange ASME B16.5 Cl.150 RF,..; Mounting Type:; Direct Flanged / 2" Pipe Stand; Enclosure Rating:; Die-cast Aluminum Powder Coa..; Hazardous Class:; Weatherproof IP67 (Option Ex..; Process Medium: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

SECTION A: PROCESS PIPING & MECHANICAL HOOK-UP

SECTION B: ELECTRICAL LOOP WIRING SCHEMATIC (FIELD TO PLC)

SECTION C: BILL OF MATERIALS (BOM) & NOTES

MANUFACTURER: TEROFOX / APL-HKC

MODEL: TF-20DFS Ball Valve + APL-210N Limit Switch Box

Hand Valve wit

SERVICE: Manual Safety Isolation Valve Open/Closed Status

1 Manual Ball Valve TF-20DFS (DN

PROCESS SLURRY / STEAM PIPE

TeroFox 2-Piece SS316 Cl.150

2 Limit Switch Box APL-210N

Yellow/Red Visual Indicator

3 ISO 5211 Mounting Bracket & Dr

4 Cable Gland M20x1.5 Brass IP66

Compression Weatherproof Gland

5 Flange Gaskets & Fasteners Kit

PTFE Gaskets & SS304 Studs/Nuts

ENGINEERING INSTALLATION NOTES

4Cx1.5mm² Shielded Instrumen
CLEAN INSTRUMENT GROUND BUS (IE) - CONNECTED TO CA1 MASTER GROUND

1. Adjust internal cam switches: Cam 1 trips at 90° (Fully Open), Cam 2 trips at 0° (Fully Closed).

2. High-visibility 3D indicator beacon shows YELLOW for OPEN, RED for CLOSED.

3. Seal unused M20 conduit entry port with certified IP67 threaded blanking plug.

2" STANCHION PIPE STAND

ELECTRICAL & SIGNAL LOOP SPECIFICATIONS

MECHANICAL HOOK-UP SPECIFICATION

INGREDION (THAILAND) CO., LTD.
KALASIN STARCH PLANT - JET COOKER PROJECT

AEC INDUSTRIAL ENGINEERING
SYSTEMS INTEGRATION & AUTOMATION

MANUAL HAND VALVE POSITION SWITCH HOOK-UP & LOOP DIAGRAM

INSTRUMENT HOOK-UP & TYPICAL LOOP DIAGRAM

DWG NO:; KAL-JC-TYP-012; REV: 3.6 DATE: 2026-09-08; TEMPLATE TYP-12: LIQUID LEVEL SWITCH; TYPICAL TAGS: LSH-40101 / LSL-40101; SERVICE: High / Low Slurry Level Interlock & Pump Protection | PLC I/O: 1756-IB32 (24V DC Sinking/Sourcing Digital Input); FLOW DIRECTION; Endress+Haus; Liquid Level S; Process Connection:; 3/4" NPT Male Threaded / Tri..; Mounting Type:; Direct Flanged / 2" Pipe Stand; Enclosure Rating:; NEMA 4X / IP66/68 Stainless ..; Hazardous Class:; ATEX II 1/2G Ex ia IIC T6.....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

SECTION A: PROCESS PIPING & MECHANICAL HOOK-UP

SECTION B: ELECTRICAL LOOP WIRING SCHEMATIC (FIELD TO PLC)

SECTION C: BILL OF MATERIALS (BOM) & NOTES

MANUFACTURER: ENDRESS+HAUSER

MODEL: Liquiphant FTL51B (Tuning Fork SS316L)

SERVICE: High / Low Slurry Level Interlock & Pump Protection

1 Liquiphant FTL51B Level Switch

PROCESS SLURRY / STEAM PIPE

2 Welding Boss 3/4" NPT Half Cou

SS316 Tank Welding Socket

3 Cable Gland M20x1.5 Ex d/e

Nickel-plated Brass Armored Glan

4 Viton / EPDM Thread Seal Ring

Process Sealing Gasket

5 Grounding Strap 4mm² with Lugs

Copper Flexible Earth Braid

ENGINEERING INSTALLATION NOTES

3Cx1.5mm² Shielded Instrumen
CLEAN INSTRUMENT GROUND BUS (IE) - CONNECTED TO CA1 MASTER GROUND

1. Install fork with tines aligned vertically to prevent slurry buildup on top of vibrating blades.

2. Set fail-safe mode switch: MAX (Overfill Protection) or MIN (Dry Run Pump Protection).

3. Keep fork at least 50mm away from tank walls, internal baffles, and agitator blades.

2" STANCHION PIPE STAND

ELECTRICAL & SIGNAL LOOP SPECIFICATIONS

MECHANICAL HOOK-UP SPECIFICATION

INGREDION (THAILAND) CO., LTD.
KALASIN STARCH PLANT - JET COOKER PROJECT

AEC INDUSTRIAL ENGINEERING
SYSTEMS INTEGRATION & AUTOMATION

LIQUID LEVEL SWITCH (VIBRATING FORK) HOOK-UP & LOOP DIAGRAM

INSTRUMENT HOOK-UP & TYPICAL LOOP DIAGRAM

DWG NO:; KAL-JC-TYP-013; REV: 3.6 DATE: 2026-09-08; TEMPLATE TYP-13: SOLID LEVEL SWITCH; TYPICAL TAGS: LSH-60101 Series; SERVICE: Starch Powder Silo High Level Overfill Alarm | PLC I/O: 1756-IB32 (24V DC Digital Input); FLOW DIRECTION; Endress+Haus; Process Connection:; 1-1/2" NPT Male / DN50 Cl.15..; Mounting Type:; Direct Flanged / 2" Pipe Stand; Enclosure Rating:; NEMA 4X / IP66 Cast Aluminum..; Hazardous Class:; ATEX II 1/2D Ex ta/tb IIIC T..; Process Medium: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

SECTION A: PROCESS PIPING & MECHANICAL HOOK-UP

SECTION B: ELECTRICAL LOOP WIRING SCHEMATIC (FIELD TO PLC)

SECTION C: BILL OF MATERIALS (BOM) & NOTES

MANUFACTURER: ENDRESS+HAUSER

MODEL: Soliphant FTM51 (Vibrating Fork for Fine Bulk Solids)

Solid Level Sw

SERVICE: Starch Powder Silo High Level Overfill Alarm

1 Soliphant FTM51 Powder Level S

PROCESS SLURRY / STEAM PIPE

2 Welding Flange DN50 PN16 / Cl.

Carbon Steel / SS316 Flange

3 Weather Protective Sun / Rain

4 Dust-Ex Cable Gland M20x1.5

Nickel-plated Brass ATEX Dust Gl

5 Grounding Wire 6mm² Green/Yell

Copper Earthing Strap

ENGINEERING INSTALLATION NOTES

4Cx1.5mm² Shielded Overall (
CLEAN INSTRUMENT GROUND BUS (IE) - CONNECTED TO CA1 MASTER GROUND

1. Install angled downward 20° to 30° on silo side wall to allow powder to slide off tines easily.

2. Do not mount directly in the filling stream or impact zone of falling starch powder.

3. Ensure housing earth terminal is connected to silo metal structure to dissipate electrostatic charge.

2" STANCHION PIPE STAND

ELECTRICAL & SIGNAL LOOP SPECIFICATIONS

MECHANICAL HOOK-UP SPECIFICATION

INGREDION (THAILAND) CO., LTD.
KALASIN STARCH PLANT - JET COOKER PROJECT

AEC INDUSTRIAL ENGINEERING
SYSTEMS INTEGRATION & AUTOMATION

SOLID LEVEL SWITCH (POWDER FORK) HOOK-UP & LOOP DIAGRAM

INSTRUMENT HOOK-UP & TYPICAL LOOP DIAGRAM

DWG NO:; KAL-JC-TYP-014; REV: 3.6 DATE: 2026-09-08; TEMPLATE TYP-14: RADAR LEVEL TRANSMITTER; TYPICAL TAGS: LT-40101 / LT-40201; SERVICE: Cooker Slurry & Flash Tank Non-Contact Continuous Level | PLC I/O: 1756-IF16 (16-Point Differential AI); FLOW DIRECTION; Endress+Haus; Process Connection:; DN80 (3") ASME Cl.150 RF Fla..; Mounting Type:; Direct Flanged / 2" Pipe Stand; Enclosure Rating:; NEMA 4X / IP66/68 Dual Compa..; Hazardous Class:; ATEX II 1/2G Ex ia IIC T6 Ga..; Process Medium: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

SECTION A: PROCESS PIPING & MECHANICAL HOOK-UP

SECTION B: ELECTRICAL LOOP WIRING SCHEMATIC (FIELD TO PLC)

SECTION C: BILL OF MATERIALS (BOM) & NOTES

MANUFACTURER: ENDRESS+HAUSER

MODEL: Micropilot FMR67B (80 GHz High-Frequency Radar)

Radar Level Tr

SERVICE: Cooker Slurry & Flash Tank Non-Contact Continuous Level

1 Micropilot FMR67B Radar Transm

PROCESS SLURRY / STEAM PIPE

E+H 80GHz w/ Drip-off PTFE Anten

2 Tank Nozzle Flange DN80 Cl.150

SS316 Tank Flange Neck

3 PTFE Envelope Gasket DN80 Cl.1

Chemical Resistant Gasket

4 Cable Gland M20x1.5 Ex d/e IP6

Nickel-plated Brass Gland

5 Air Purge Connection Kit 1/4"

Purge Connection for Condensate

ENGINEERING INSTALLATION NOTES

1Px1.5mm² Twisted Pair Shiel
CLEAN INSTRUMENT GROUND BUS (IE) - CONNECTED TO CA1 MASTER GROUND

1. Mount nozzle height must not exceed antenna length so horn protrudes clear into vessel interior.

2. Distance to vessel wall should be min. 1/6 of vessel diameter to prevent false sidewall echoes.

3. Activate Heartbeat Technology and mapping curves to mask agitator blade echoes during commissioning.

2" STANCHION PIPE STAND

ELECTRICAL & SIGNAL LOOP SPECIFICATIONS

MECHANICAL HOOK-UP SPECIFICATION

INGREDION (THAILAND) CO., LTD.
KALASIN STARCH PLANT - JET COOKER PROJECT

AEC INDUSTRIAL ENGINEERING
SYSTEMS INTEGRATION & AUTOMATION

RADAR LEVEL TRANSMITTER (80 GHz) HOOK-UP & LOOP DIAGRAM

INSTRUMENT HOOK-UP & TYPICAL LOOP DIAGRAM

DWG NO:; KAL-JC-TYP-015; REV: 3.6 DATE: 2026-09-08; TEMPLATE TYP-15: PRESSURE GAUGE; TYPICAL TAGS: PI-40101 / PI-60201; SERVICE: Steam Line & Cooker Chamber Direct Pressure Readout | PLC I/O: None (Local Operator Gauge); FLOW DIRECTION; Ashcroft; Pressure Gauge; Process Connection:; 1/2" NPT Male w/ Pigtail Sip..; Mounting Type:; Direct Flanged / 2" Pipe Stand; Enclosure Rating:; IP65 Stainless Steel Case, G..; Hazardous Class:; Non-Electrical Apparatus (St..; Process Medium: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

SECTION A: PROCESS PIPING & MECHANICAL HOOK-UP

SECTION B: ELECTRICAL LOOP WIRING SCHEMATIC (FIELD TO PLC)

SECTION C: BILL OF MATERIALS (BOM) & NOTES

MODEL: Model T5500 (100mm Dial All-Stainless Steel)

SERVICE: Steam Line & Cooker Chamber Direct Pressure Readout

1 Pressure Gauge T5500 (0-16 bar

PROCESS SLURRY / STEAM PIPE

Ashcroft 100mm Dial SS316 Bourdo

2 Pigtail Siphon Schedule 80 SS3

1/2" NPT Steam Condensate Loop

3 Needle Isolation Valve 1/2" NP

SS316 Cl.6000 Needle Valve

4 Gauge Snubber / Pulsation Damp

Porous SS316 Disc 1/2" NPT

5 Thread Sealant Tape (PTFE/Grap

High Temperature Steam Rated

ENGINEERING INSTALLATION NOTES

N/A (Direct Local Readout)
CLEAN INSTRUMENT GROUND BUS (IE) - CONNECTED TO CA1 MASTER GROUND

1. Pigtail siphon must be pre-filled with clean water prior to steam startup to protect Bourdon tube.

2. Orient dial facing primary walkway / operating platform for ease of operator reading.

3. Close needle valve slightly during excessive pulsating flow to protect internal linkage.

2" STANCHION PIPE STAND

ELECTRICAL & SIGNAL LOOP SPECIFICATIONS

MECHANICAL HOOK-UP SPECIFICATION

INGREDION (THAILAND) CO., LTD.
KALASIN STARCH PLANT - JET COOKER PROJECT

AEC INDUSTRIAL ENGINEERING
SYSTEMS INTEGRATION & AUTOMATION

PRESSURE GAUGE & SIPHON HOOK-UP & MECHANICAL DETAIL

INSTRUMENT HOOK-UP & TYPICAL LOOP DIAGRAM

DWG NO:; KAL-JC-TYP-016; REV: 3.6 DATE: 2026-09-08; TEMPLATE TYP-16: PRESSURE SWITCH; TYPICAL TAGS: PSH-60201 / PSL-60201; SERVICE: High / Low Pressure Safety Trip Interlock | PLC I/O: 1756-IB32 (24V DC Digital Input); FLOW DIRECTION; Endress+Haus; Pressure Switc; Process Connection:; 1/2" NPT Male Threaded / Tri..; Mounting Type:; Direct Flanged / 2" Pipe Stand; Enclosure Rating:; IP65 / IP67 Stainless Steel ..; Hazardous Class:; General Industrial Zone (Opt..; Process Medium: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

SECTION A: PROCESS PIPING & MECHANICAL HOOK-UP

SECTION B: ELECTRICAL LOOP WIRING SCHEMATIC (FIELD TO PLC)

SECTION C: BILL OF MATERIALS (BOM) & NOTES

MANUFACTURER: ENDRESS+HAUSER

MODEL: Ceraphant PTC31B (Ceramic Sensor Diaphragm)

SERVICE: High / Low Pressure Safety Trip Interlock

1 Ceraphant PTC31B Pressure Swit

PROCESS SLURRY / STEAM PIPE

E+H Ceramic Cell, LED Display

2 2-Valve Isolation Manifold 1/2

SS316 Block & Bleed Valve

3 M12 4-Pin Field Wireable Conne

4 Cable Gland M16x1.5 Brass

Nickel-plated Cable Gland

5 Impulse Adapter 1/2" NPT x 1/2

Swagelok SS316 Tube Fitting

ENGINEERING INSTALLATION NOTES

3Cx1.5mm² Shielded Instrumen
CLEAN INSTRUMENT GROUND BUS (IE) - CONNECTED TO CA1 MASTER GROUND

1. Program switch point and reset hysteresis via front push-buttons and LED display.

2. Configure output as Normally Closed (NC) fail-safe: circuit de-energizes on overpressure or power loss.

3. Provide block-and-bleed valve for routine verification with field calibrator.

2" STANCHION PIPE STAND

ELECTRICAL & SIGNAL LOOP SPECIFICATIONS

MECHANICAL HOOK-UP SPECIFICATION

INGREDION (THAILAND) CO., LTD.
KALASIN STARCH PLANT - JET COOKER PROJECT

AEC INDUSTRIAL ENGINEERING
SYSTEMS INTEGRATION & AUTOMATION

ELECTRONIC PRESSURE SWITCH HOOK-UP & LOOP DIAGRAM

INSTRUMENT HOOK-UP & TYPICAL LOOP DIAGRAM

DWG NO:; KAL-JC-TYP-017; REV: 3.6 DATE: 2026-09-08; TEMPLATE TYP-17: PRESSURE TRANSMITTER; TYPICAL TAGS: PT-40101 / PT-60202; SERVICE: Continuous Pressure Monitoring for Cooker & Flash Tank | PLC I/O: 1756-IF16 (16-Point Differential AI); FLOW DIRECTION; Endress+Haus; Pressure Trans; Process Connection:; 1/2" NPT Male Thread / 2" Tr..; Mounting Type:; Direct Flanged / 2" Pipe Stand; Enclosure Rating:; NEMA 4X / IP66/68 Dual Compa..; Hazardous Class:; ATEX II 1/2G Ex ia IIC T6 Ga..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

SECTION A: PROCESS PIPING & MECHANICAL HOOK-UP

SECTION B: ELECTRICAL LOOP WIRING SCHEMATIC (FIELD TO PLC)

SECTION C: BILL OF MATERIALS (BOM) & NOTES

MANUFACTURER: ENDRESS+HAUSER

MODEL: Cerabar PMP51B / PMC51B (Metallic / Ceramic)

SERVICE: Continuous Pressure Monitoring for Cooker & Flash Tank

1 Cerabar PMP51B Pressure Transm

PROCESS SLURRY / STEAM PIPE

2 2-Valve Block & Bleed Manifold

SS316 1/2" NPT Male x Female

3 2" Pipe Mounting Bracket Kit

SS304 Universal Bracket & U-Bolt

4 Cable Gland M20x1.5 Ex d/e IP6

Nickel-plated Brass Armored Glan

5 Siphon / Cooling Neck (Steam D

SS316 Pigtail Loop 1/2" NPT

ENGINEERING INSTALLATION NOTES

1Px1.5mm² Twisted Shielded (
CLEAN INSTRUMENT GROUND BUS (IE) - CONNECTED TO CA1 MASTER GROUND

1. Use flush diaphragm seal (PMC51B) for thick starch slurry to eliminate clogging in impulse ports.

2. Ground transmitter body to local pipe ground; shield wire grounded only at CA1 cabinet earth bar.

3. HART configuration: Set damping to 1.0s to filter process pump pulsations.

2" STANCHION PIPE STAND

ELECTRICAL & SIGNAL LOOP SPECIFICATIONS

MECHANICAL HOOK-UP SPECIFICATION

INGREDION (THAILAND) CO., LTD.
KALASIN STARCH PLANT - JET COOKER PROJECT

AEC INDUSTRIAL ENGINEERING
SYSTEMS INTEGRATION & AUTOMATION

PRESSURE TRANSMITTER HOOK-UP & LOOP DIAGRAM

INSTRUMENT HOOK-UP & TYPICAL LOOP DIAGRAM

DWG NO:; KAL-JC-TYP-018; REV: 3.6 DATE: 2026-09-08; TEMPLATE TYP-18: TEMPERATURE GAUGE; TYPICAL TAGS: TI-40101 / TI-60201; SERVICE: Direct Pipe & Tank Slurry Temperature Indicator | PLC I/O: None (Local Operator Readout); FLOW DIRECTION; Ashcroft; Temperature Ga; Process Connection:; 1/2" NPT Male Thread into Ba..; Mounting Type:; Direct Flanged / 2" Pipe Stand; Enclosure Rating:; IP65 Hermetically Sealed Sta..; Hazardous Class:; Non-Electrical Apparatus (St..; Process Medium: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

SECTION A: PROCESS PIPING & MECHANICAL HOOK-UP

SECTION B: ELECTRICAL LOOP WIRING SCHEMATIC (FIELD TO PLC)

SECTION C: BILL OF MATERIALS (BOM) & NOTES

MODEL: Model FI (100mm Dial Everyangle Bimetal) + Thermowell

SERVICE: Direct Pipe & Tank Slurry Temperature Indicator

1 Bimetal Thermometer Model FI (

PROCESS SLURRY / STEAM PIPE

Ashcroft 100mm Dial Everyangle S

1/2" NPT x 1" NPT Process Thread

3 Weldolet / Threadolet 1" NPT

ASTM A182 F316 Pipe Fitting

4 Thermal Conductive Paste

High Temperature Aluminum Oxide

5 Safety Wire & Tag Plate SS316

Laser Engraved Tag Plate

ENGINEERING INSTALLATION NOTES

N/A (Local Dial Readout)
CLEAN INSTRUMENT GROUND BUS (IE) - CONNECTED TO CA1 MASTER GROUND

1. Thermowell tip must be immersed into center third of process pipe for representative measurement.

2. Apply thermal conductive paste inside thermowell bore before inserting gauge stem to improve heat transfer.

3. Thermowell allows removal of thermometer for calibration without process shutdown.

2" STANCHION PIPE STAND

ELECTRICAL & SIGNAL LOOP SPECIFICATIONS

MECHANICAL HOOK-UP SPECIFICATION

INGREDION (THAILAND) CO., LTD.
KALASIN STARCH PLANT - JET COOKER PROJECT

AEC INDUSTRIAL ENGINEERING
SYSTEMS INTEGRATION & AUTOMATION

BIMETAL TEMPERATURE GAUGE & THERMOWELL HOOK-UP DETAIL

INSTRUMENT HOOK-UP & TYPICAL LOOP DIAGRAM

DWG NO:; KAL-JC-TYP-019; REV: 3.6 DATE: 2026-09-08; TEMPLATE TYP-19: TEMP TRANSMITTER (RTD); TYPICAL TAGS: TT-40101 / TT-60201; SERVICE: Precision Slurry Cooking Temperature Control | PLC I/O: 1756-IF16 (16-Point Differential AI); FLOW DIRECTION; Endress+Haus; Temp Transmitt; Process Connection:; 1/2" NPT Thread into Barstoc..; Mounting Type:; Direct Flanged / 2" Pipe Stand; Enclosure Rating:; IP66 / IP68 Form B Head Alum..; Hazardous Class:; ATEX II 1/2G Ex ia IIC T6.....; Process Medium: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

SECTION A: PROCESS PIPING & MECHANICAL HOOK-UP

SECTION B: ELECTRICAL LOOP WIRING SCHEMATIC (FIELD TO PLC)

SECTION C: BILL OF MATERIALS (BOM) & NOTES

MANUFACTURER: ENDRESS+HAUSER

MODEL: iTEMP TMT71 + Omnigrad M TM411 (Pt100 Class A)

SERVICE: Precision Slurry Cooking Temperature Control

1 Head Transmitter iTEMP TMT71

PROCESS SLURRY / STEAM PIPE

E+H 4-20mA HART Head Mounted Puc

2 RTD Sensor Assembly TM411 Pt10

Class A 3-Wire Mineral Insulated

3 Flanged / Threaded Thermowell

Drilled Barstock Tapered Well

4 Cable Gland M20x1.5 Ex d/e IP6

Nickel-plated Brass Gland

5 Grounding Strap 4mm² with Lugs

Flexible Copper Earthing Braid

ENGINEERING INSTALLATION NOTES

1Px1.5mm² Twisted Shielded (
CLEAN INSTRUMENT GROUND BUS (IE) - CONNECTED TO CA1 MASTER GROUND

1. Connect Pt100 RTD using 3-wire compensation circuit to eliminate field lead wire resistance error.

2. Install thermowell at elbow pointing upstream or inclined 45° if pipe diameter is under 4 inches.

3. Verify loop current with multimeter test points on TMT71 without interrupting signal loop.

2" STANCHION PIPE STAND

ELECTRICAL & SIGNAL LOOP SPECIFICATIONS

MECHANICAL HOOK-UP SPECIFICATION

INGREDION (THAILAND) CO., LTD.
KALASIN STARCH PLANT - JET COOKER PROJECT

AEC INDUSTRIAL ENGINEERING
SYSTEMS INTEGRATION & AUTOMATION

TEMPERATURE TRANSMITTER (RTD Pt100) HOOK-UP & LOOP DIAGRAM

INSTRUMENT HOOK-UP & TYPICAL LOOP DIAGRAM

DWG NO:; KAL-JC-TYP-020; REV: 3.6 DATE: 2026-09-08; TEMPLATE TYP-20: PNEUMATIC ON-OFF VALVE; TYPICAL TAGS: XV-40101 / XV-60201; SERVICE: Automated Slurry Routing & Emergency Process Isolation | PLC I/O: 1756-OB32 (DO Solenoid) & 1756-IB32 (DI Open/Closed); FLOW DIRECTION; TeroFox / El; Pneumatic On-O; Process Connection:; Flange ASME B16.5 Cl.150 RF,..; Mounting Type:; Direct Flanged / 2" Pipe Stand; Enclosure Rating:; Hard Anodized Aluminum Actua..; Hazardous Class: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

SECTION A: PROCESS PIPING & MECHANICAL HOOK-UP

SECTION B: ELECTRICAL LOOP WIRING SCHEMATIC (FIELD TO PLC)

SECTION C: BILL OF MATERIALS (BOM) & NOTES

MANUFACTURER: TEROFOX / EL-O-MATIC

MODEL: TF-20DFS Ball Valve + F-Series Actuator + Solenoid + APL-210N

SERVICE: Automated Slurry Routing & Emergency Process Isolation

1 Pneumatic Ball Valve Assembly

PROCESS SLURRY / STEAM PIPE

TeroFox TF-20DFS DN50 Cl.150

2 Pneumatic Spring-Return Actuat

El-O-Matic F-Series Rack & Pinio

3 Namur Solenoid Valve 5/2-Way (

Asco / SMC Low Power Solenoid

4 Limit Switch Box APL-210N (2x

Visual Yellow/Red Open/Close Bea

5 Air Filter Regulator & Gauge S

Modular AFR 1/4" w/ Auto-Drain

ENGINEERING INSTALLATION NOTES

3Cx1.5mm² (Solenoid) + 4Cx1.
CLEAN INSTRUMENT GROUND BUS (IE) - CONNECTED TO CA1 MASTER GROUND

1. Spring-return fail-safe action: Valve drives to CLOSED position on electrical power or air failure.

2. Interposing relay 700-HL at CA1 cabinet isolates PLC 1756-OB32 output from field coil inrush.

3. Air supply lines must use seamless SS316 1/4" or 3/8" tubing with Swagelok compression fittings.

2" STANCHION PIPE STAND

ELECTRICAL & SIGNAL LOOP SPECIFICATIONS

MECHANICAL HOOK-UP SPECIFICATION

INGREDION (THAILAND) CO., LTD.
KALASIN STARCH PLANT - JET COOKER PROJECT

AEC INDUSTRIAL ENGINEERING
SYSTEMS INTEGRATION & AUTOMATION

PNEUMATIC ON-OFF CONTROL VALVE HOOK-UP & LOOP DIAGRAM

INSTRUMENT HOOK-UP & TYPICAL LOOP DIAGRAM

DWG NO:; KAL-JC-TYP-021; REV: 3.6 DATE: 2026-09-08; TEMPLATE TYP-21: GLOBE CONTROL VALVE; TYPICAL TAGS: TCV-40222 / TV-60202; SERVICE: High-Precision Steam & Slurry Flow Modulation | PLC I/O: 1756-OF8 (AO Setpoint) & 1756-IF16 (AI Feedback); FLOW DIRECTION; Samson; Globe Control; Process Connection:; Flange ASME B16.5 Cl.150/300..; Mounting Type:; Direct Flanged / 2" Pipe Stand; Enclosure Rating:; IP66 Die-cast Aluminum Posit..; Hazardous Class:; ATEX II 2G Ex ia IIC T6 / Ex..; Process Medium: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

SECTION A: PROCESS PIPING & MECHANICAL HOOK-UP

SECTION B: ELECTRICAL LOOP WIRING SCHEMATIC (FIELD TO PLC)

SECTION C: BILL OF MATERIALS (BOM) & NOTES

MODEL: Type 3241 Globe Valve + Trovis 3730-1 Smart Positioner

SERVICE: High-Precision Steam & Slurry Flow Modulation

1 Globe Control Valve Type 3241

PROCESS SLURRY / STEAM PIPE

Samson Cast Steel / SS316 Body

2 Pneumatic Diaphragm Actuator T

Samson Multi-Spring Actuator

3 Smart Positioner Trovis 3730-1

HART Communication, Auto-Tuning

4 SMC Air Filter Regulator AW20

Clean Air 1/4" w/ Pressure Gauge

5 Cable Glands M20x1.5 Ex d/e IP

Nickel-plated Brass Glands

ENGINEERING INSTALLATION NOTES

2Px1.5mm² Twisted Shielded (
CLEAN INSTRUMENT GROUND BUS (IE) - CONNECTED TO CA1 MASTER GROUND

1. Perform Trovis 3730-1 automatic initialization routine after mechanical mounting is completed.

2. Connect 4-20mA setpoint from PLC 1756-OF8 to Positioner Terminals 11(+) and 12(-).

3. Ensure air supply pressure to positioner is regulated strictly between 4.0 and 6.0 bar.

2" STANCHION PIPE STAND

ELECTRICAL & SIGNAL LOOP SPECIFICATIONS

MECHANICAL HOOK-UP SPECIFICATION

INGREDION (THAILAND) CO., LTD.
KALASIN STARCH PLANT - JET COOKER PROJECT

AEC INDUSTRIAL ENGINEERING
SYSTEMS INTEGRATION & AUTOMATION

MODULATING GLOBE CONTROL VALVE HOOK-UP & LOOP DIAGRAM

INSTRUMENT HOOK-UP & TYPICAL LOOP DIAGRAM

DWG NO:; KAL-JC-TYP-022; REV: 3.6 DATE: 2026-09-08; TEMPLATE TYP-22: TEMPERATURE SWITCH; TYPICAL TAGS: TSH-40101 / TSH-60201; SERVICE: High Temperature Safety Trip & Alarm | PLC I/O: 1756-IB32 (24V DC Digital Input); FLOW DIRECTION; Endress+Haus; Temperature Sw; Process Connection:; 1/2" NPT Male Threaded / Hyg..; Mounting Type:; Direct Flanged / 2" Pipe Stand; Enclosure Rating:; IP65 / IP67 Stainless Steel ..; Hazardous Class:; General Industrial / Hygieni..; Process Medium: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

SECTION A: PROCESS PIPING & MECHANICAL HOOK-UP

SECTION B: ELECTRICAL LOOP WIRING SCHEMATIC (FIELD TO PLC)

SECTION C: BILL OF MATERIALS (BOM) & NOTES

MANUFACTURER: ENDRESS+HAUSER

MODEL: Thermophant TTR35 (Compact Pt100 Switch)

SERVICE: High Temperature Safety Trip & Alarm

1 Thermophant TTR35 Temp Switch

PROCESS SLURRY / STEAM PIPE

E+H Pt100 Class A, Digital Displ

1/2" NPT x 1/2" NPT Process Well

3 M12 4-Pin Female Cable Assembl

M12 Right Angle Molded Connector

4 Threadolet / Boss 1/2" NPT SS3

Pipe Welding Fitting

5 Grounding Clamp & Lug

Copper Earth Wire

ENGINEERING INSTALLATION NOTES

3Cx1.5mm² Shielded Instrumen
CLEAN INSTRUMENT GROUND BUS (IE) - CONNECTED TO CA1 MASTER GROUND

1. Configure switch point via optical touch keys on front cover without opening enclosure.

2. Normally closed (NC) contact output configuration guarantees fail-safe alarm on wire break.

3. Thermowell allows switch replacement without draining the process line.

2" STANCHION PIPE STAND

ELECTRICAL & SIGNAL LOOP SPECIFICATIONS

MECHANICAL HOOK-UP SPECIFICATION

INGREDION (THAILAND) CO., LTD.
KALASIN STARCH PLANT - JET COOKER PROJECT

AEC INDUSTRIAL ENGINEERING
SYSTEMS INTEGRATION & AUTOMATION

ELECTRONIC TEMPERATURE SWITCH HOOK-UP & LOOP DIAGRAM

INSTRUMENT HOOK-UP & TYPICAL LOOP DIAGRAM

DWG NO:; KAL-JC-TYP-023; REV: 3.6 DATE: 2026-09-08; TEMPLATE TYP-23: PNEUMATIC TURBINE VIBRATOR; TYPICAL TAGS: XV-60901 Series; SERVICE: Powder Silo & Hopper Wall Discharge Agitation | PLC I/O: 1756-OB32 (24V DC Digital Output); FLOW DIRECTION; Netter Vibra; Pneumatic Turb; Process Connection:; G 1/8" BSP Air Port / Rigid ..; Mounting Type:; Direct Flanged / 2" Pipe Stand; Enclosure Rating:; Extruded Aluminum Hard Anodi..; Hazardous Class:; ATEX II 2GD c T6 85°C (Mecha..; Process Medium: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

SECTION A: PROCESS PIPING & MECHANICAL HOOK-UP

SECTION B: ELECTRICAL LOOP WIRING SCHEMATIC (FIELD TO PLC)

SECTION C: BILL OF MATERIALS (BOM) & NOTES

MANUFACTURER: NETTER VIBRATION

MODEL: NCT 5 Pneumatic Turbine Vibrator

SERVICE: Powder Silo & Hopper Wall Discharge Agitation

1 Pneumatic Turbine Vibrator NCT

PROCESS SLURRY / STEAM PIPE

Netter Vibration High-Speed Unit

2 Solenoid Valve 3/2-Way 24VDC (

High Flow Fast-Cycling Solenoid

3 Silencer / Exhaust Air Filter

Sintered Bronze Sinter Filter

4 SMC Air Filter Regulator Kit

Modular AFR w/ Pressure Gauge

5 Weld-on Hopper Mounting Channe

Reinforced Channel Profile Steel

ENGINEERING INSTALLATION NOTES

3Cx1.5mm² Shielded Cable (Be
CLEAN INSTRUMENT GROUND BUS (IE) - CONNECTED TO CA1 MASTER GROUND

1. Mount vibrator on stiffened channel beam welded to hopper cone to transmit vibration into bulk powder.

2. Operate in intermittent pulse mode (e.g. 5 seconds ON, 30 seconds OFF) via PLC timer logic.

3. Interposing relay 700-HL at CA1 panel protects PLC output module from inductive flyback.

2" STANCHION PIPE STAND

ELECTRICAL & SIGNAL LOOP SPECIFICATIONS

MECHANICAL HOOK-UP SPECIFICATION

INGREDION (THAILAND) CO., LTD.
KALASIN STARCH PLANT - JET COOKER PROJECT

AEC INDUSTRIAL ENGINEERING
SYSTEMS INTEGRATION & AUTOMATION

PNEUMATIC TURBINE VIBRATOR HOOK-UP & LOOP DIAGRAM

INSTRUMENT HOOK-UP & TYPICAL LOOP DIAGRAM
