x92120/x260911-002-KalasinEngineering/02_Electrical_and_eDrawing/04_PDF_Reports_and_Drawings/jet_cooker_wiring_sheet_07.png

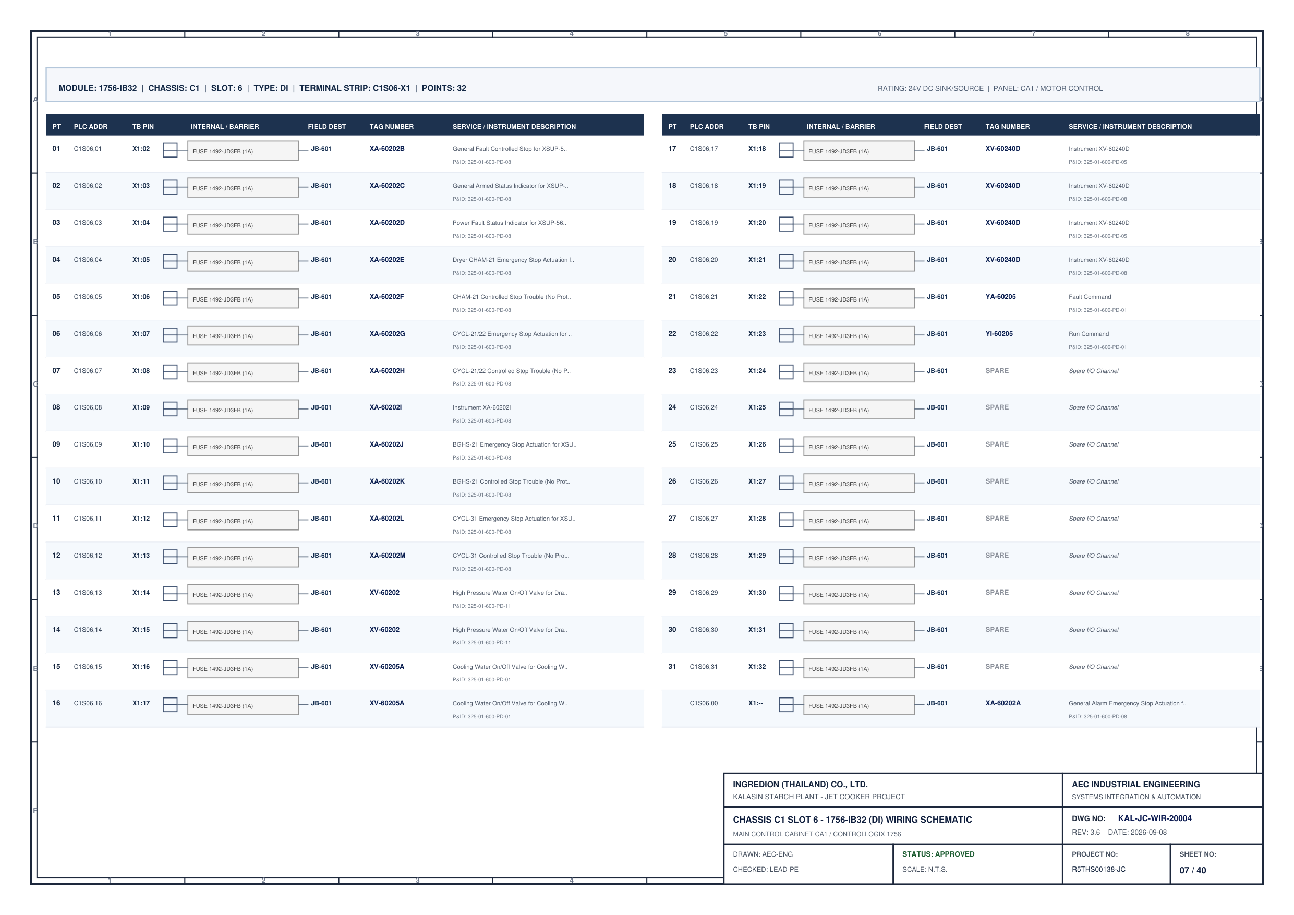
02_Electrical_and_eDrawing/04_PDF_Reports_and_Drawings/jet_cooker_wiring_sheet_07.png
