x92120/x260911-002-KalasinEngineering/02_Electrical_and_eDrawing/05_Instrument_Manuals/CS-DS-01 pH Analyzer/InTrac 777P_070_4404_D00_Vi_A00_52403208 (Dimension) (1).png

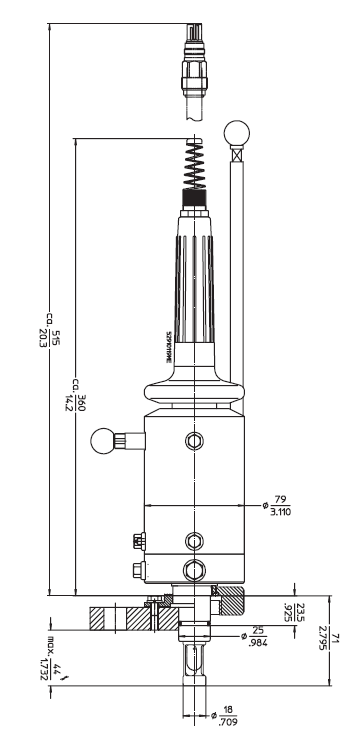
02_Electrical_and_eDrawing/05_Instrument_Manuals/CS-DS-01 pH Analyzer/InTrac 777P_070_4404_D00_Vi_A00_52403208 (Dimension) (1).png
