x92120/x260911-002-KalasinEngineering/02_Electrical_and_eDrawing/05_Instrument_Manuals/CS-DS-07 Hand valve with positioner switch/TeroFox valve/GN-SS-2_0.jpg

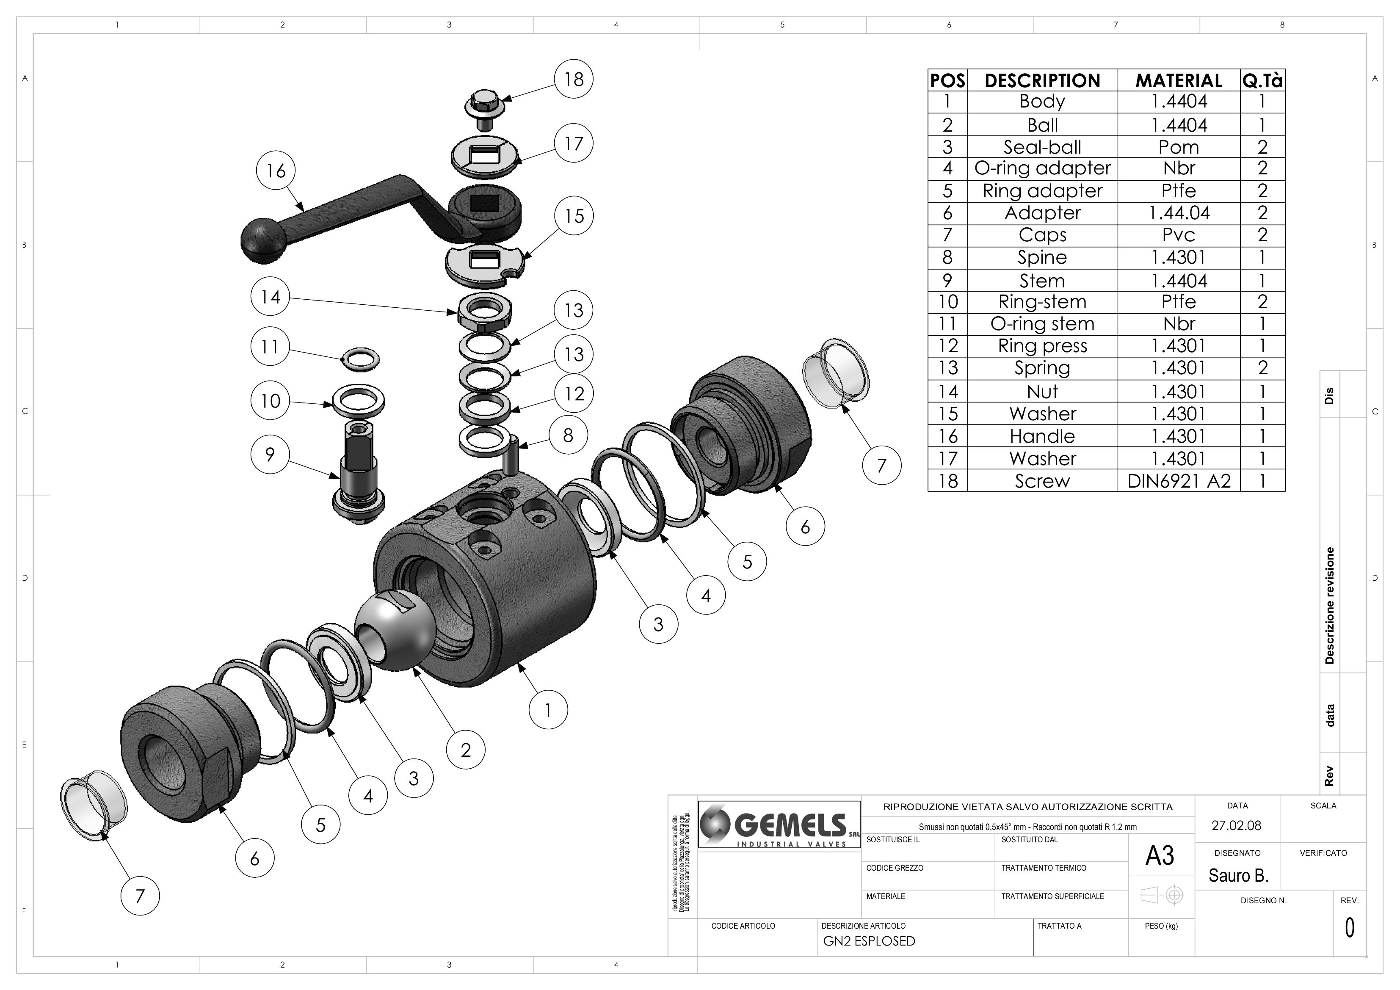
02_Electrical_and_eDrawing/05_Instrument_Manuals/CS-DS-07 Hand valve with positioner switch/TeroFox valve/GN-SS-2_0.jpg
