x92120/x260911-002-KalasinEngineering/02_Electrical_and_eDrawing/05_Instrument_Manuals/CS-DS-10 Level transmitter/ts-40101 40102  40201/messageImage_1770990494628.jpg

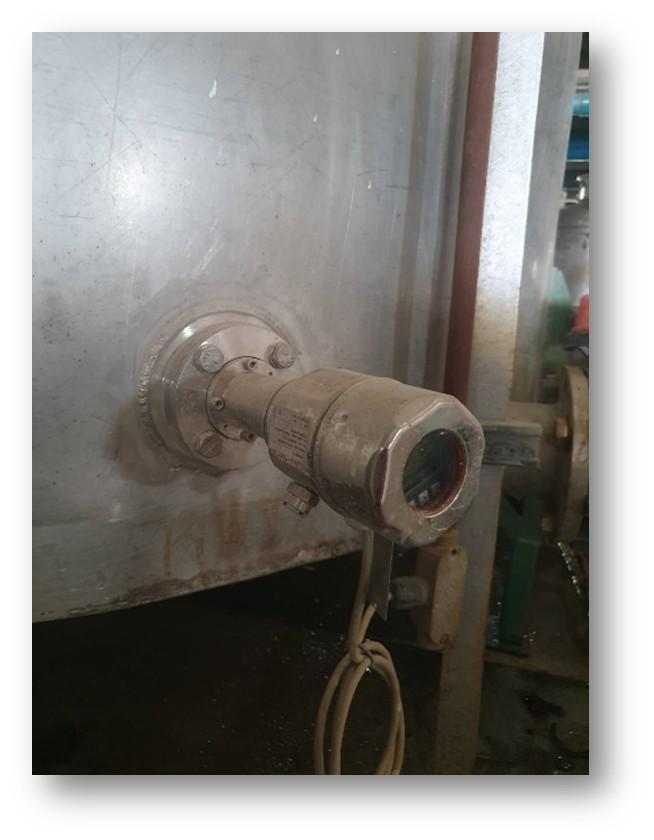
02_Electrical_and_eDrawing/05_Instrument_Manuals/CS-DS-10 Level transmitter/ts-40101 40102 40201/messageImage_1770990494628.jpg
