x92120/x260911-002-KalasinEngineering/02_Electrical_and_eDrawing/05_Instrument_Manuals/Pneumatic Vibrating/Installation Manual NCT5.jpg

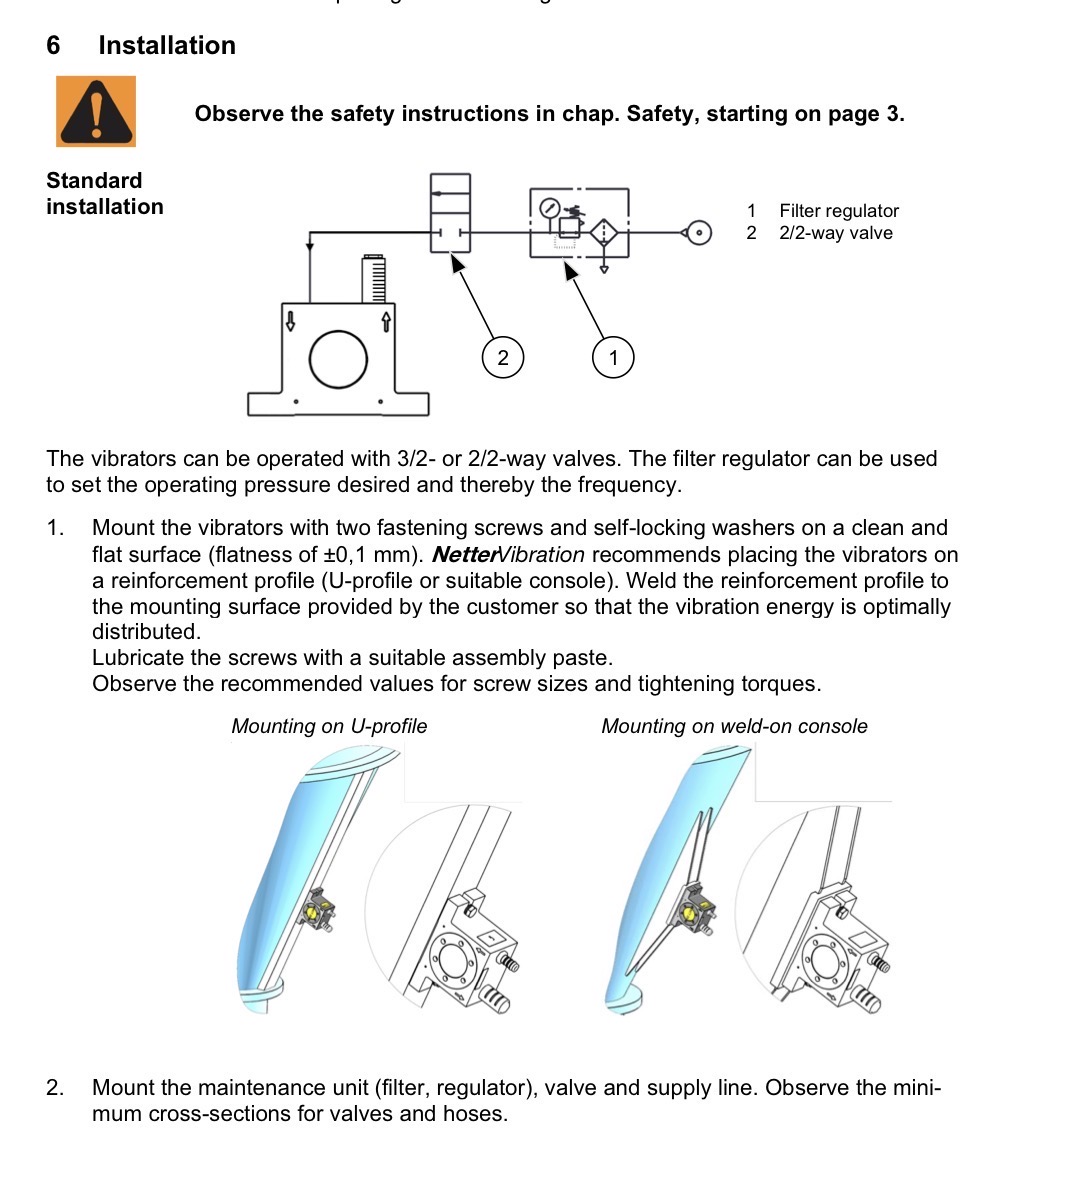
02_Electrical_and_eDrawing/05_Instrument_Manuals/Pneumatic Vibrating/Installation Manual NCT5.jpg
