x92120/x260911-002-KalasinEngineering/FAT/PreFAT-xDevWorkShop/C1_DIDO_FAT_Test_Report.pdf

## CHASSIS C1 DI/DO FACTORY ACCEPTANCE TEST (FAT) MASTER REPORT

Project: SPRINT 18K Spray Dryer | Target: MCP-01 Chassis C1 | Document: KAL-FAT-TR-C1-2608 | Rev 1.0
TOTAL CHANNELS | PASSED CHANNELS
192 192 (100%)
64 DO + 128 DI Channels | Zero Faults Detected

## 1. CHASSIS C1 HARDWARE CONFIGURATION & TEST COVERAGE

Slot # | Module Model | Description / Function | Channel Count
C1S0 | 1756-L950TPSXT | ControlLogix 5580 Master Processor (20MB) | 1x CPU
C1S1 | 1756-EN4TR | EtherNet/IP 1Gbps DLR Supervisor Port | 2x DLR Ports
C1S2 | 1756-EN4TR | EtherNet/IP 1Gbps Plant Network Uplink | 2x Ports
C1S3 | 1756-EN4TR | EtherNet/IP 1Gbps SCADA Communication | 2x Ports
C1S4 | 1756-IB32 | 24VDC Digital Input Module (DI Group 1) | 32 Channels
C1S5 | 1756-IB32 | 24VDC Digital Input Module (DI Group 2) | 32 Channels
C1S6 | 1756-IB32 | 24VDC Digital Input Module (DI Group 3) | 32 Channels
C1S7 | 1756-IB32 | 24VDC Digital Input Module (DI Group 4) | 32 Channels
C1S8 | 1756-OB32 | 24VDC Digital Output Module (DO Group 1) | 32 Channels
C1S9 | 1756-OB32 | 24VDC Digital Output Module (DO Group 2) | 32 Channels
C1S10 | 1756-IF16 | Analog Input 4-20mA (Slurry & Spray Feed) | 16 Channels
C1S11 | 1756-IF16 | Analog Input 4-20mA (Burner & Chamber Temp) | 16 Channels
C1S12 | 1756-N2 | Unpopulated Slot Position | -

## CHASSIS C1 DI/DO FACTORY ACCEPTANCE TEST (FAT) MASTER REPORT

Project: SPRINT 18K Spray Dryer | Target: MCP-01 Chassis C1 | Document: KAL-FAT-TR-C1-2608 | Rev 1.0
FAILED CHANNELS | AVG SWITCH LATENCY
0 (0.0%) | 28.9 ms
100% Signal Integrity | Standard Spec: < 200 ms
Field Destination | FAT Test Methodology | Test Status
Central Area (CA1) | Firmware v34, memory & CPU diagnostics | 100% Verified
DLR Ring & Cisco 9300 | Ring break recovery test (<3ms) | 100% Verified
Plant Core Backbone | VLAN tagging & HSRP ping test | 100% Verified
FactoryTalk View SE Server | SCADA poll rate & packet latency check | 100% Verified
CA1, JB-401 (TBDI1) | Closed-Loop Cross-Wiring from C1S8 Relays | 32/32 Tested
JB-401 (TBDI2) | Closed-Loop Cross-Wiring from C1S9 Relays | 32/32 Tested
JB-401, JB-601 (TBDI3) | Direct 24VDC Dry Contact Simulation | 32/32 Tested
JB-601 (TBDI4) | Direct 24VDC Dry Contact Simulation | 32/32 Tested
Relays P1-TBRL1 (1-32) | Force DO -> Relay A1 -> NO 11/14 -> C1S4 | 32/32 Tested
Relays P1-TBRL2 (1-32) | Force DO -> Relay A1 -> NO 11/14 -> C1S5 | 32/32 Tested
JB-401 (TBAI1) | Differential 5-Point Calibration (Fluke 789) | 16/16 Tested
JB-601 (TBAI2) | Differential 5-Point Calibration (Fluke 789) | 16/16 Tested
Spare Slot | Slot Cover Installed | N/A

Verdict

PASS

PASS

PASS

PASS

PASS

PASS

PASS

PASS

PASS

PASS

PASS

PASS

PASS

## CHASSIS C1 — DI/DO CLOSED-LOOP CROSS-WIRING VERIFICATION (64 LOOPS)

Verification: C1S8 DO -> P1-TBRL1 Relay -> C1S4 DI (Loops 1-32) | C1S9 DO -> P1-TBRL2 Relay -> C1S5 DI (Loops 33-64)
Loop # | DO Slot & Pin | Interposing Relay Coil | Relay Contact NO
C1-LPB-001 | C1S8.1 | P1-TBRL-1 (A1/A2) | P1-TBRL-1 (11/14)
C1-LPB-002 | C1S8.2 | P1-TBRL-2 (A1/A2) | P1-TBRL-2 (11/14)
C1-LPB-003 | C1S8.3 | P1-TBRL-3 (A1/A2) | P1-TBRL-3 (11/14)
C1-LPB-004 | C1S8.4 | P1-TBRL-4 (A1/A2) | P1-TBRL-4 (11/14)
C1-LPB-005 | C1S8.5 | P1-TBRL-5 (A1/A2) | P1-TBRL-5 (11/14)
C1-LPB-006 | C1S8.6 | P1-TBRL-6 (A1/A2) | P1-TBRL-6 (11/14)
C1-LPB-007 | C1S8.7 | P1-TBRL-7 (A1/A2) | P1-TBRL-7 (11/14)
C1-LPB-008 | C1S8.8 | P1-TBRL-8 (A1/A2) | P1-TBRL-8 (11/14)
C1-LPB-009 | C1S8.9 | P1-TBRL-9 (A1/A2) | P1-TBRL-9 (11/14)
C1-LPB-010 | C1S8.10 | P1-TBRL-10 (A1/A2) | P1-TBRL-10 (11/14)
C1-LPB-011 | C1S8.11 | P1-TBRL-11 (A1/A2) | P1-TBRL-11 (11/14)
C1-LPB-012 | C1S8.12 | P1-TBRL-12 (A1/A2) | P1-TBRL-12 (11/14)
C1-LPB-013 | C1S8.13 | P1-TBRL-13 (A1/A2) | P1-TBRL-13 (11/14)
C1-LPB-014 | C1S8.14 | P1-TBRL-14 (A1/A2) | P1-TBRL-14 (11/14)
C1-LPB-015 | C1S8.15 | P1-TBRL-15 (A1/A2) | P1-TBRL-15 (11/14)
C1-LPB-016 | C1S8.16 | P1-TBRL-16 (A1/A2) | P1-TBRL-16 (11/14)
C1-LPB-017 | C1S8.19 | P1-TBRL-17 (A1/A2) | P1-TBRL-17 (11/14)
C1-LPB-018 | C1S8.20 | P1-TBRL-18 (A1/A2) | P1-TBRL-18 (11/14)
C1-LPB-019 | C1S8.21 | P1-TBRL-19 (A1/A2) | P1-TBRL-19 (11/14)
C1-LPB-020 | C1S8.22 | P1-TBRL-20 (A1/A2) | P1-TBRL-20 (11/14)
C1-LPB-021 | C1S8.23 | P1-TBRL-21 (A1/A2) | P1-TBRL-21 (11/14)
C1-LPB-022 | C1S8.24 | P1-TBRL-22 (A1/A2) | P1-TBRL-22 (11/14)
C1-LPB-023 | C1S8.25 | P1-TBRL-23 (A1/A2) | P1-TBRL-23 (11/14)
C1-LPB-024 | C1S8.26 | P1-TBRL-24 (A1/A2) | P1-TBRL-24 (11/14)
C1-LPB-025 | C1S8.27 | P1-TBRL-25 (A1/A2) | P1-TBRL-25 (11/14)
C1-LPB-026 | C1S8.28 | P1-TBRL-26 (A1/A2) | P1-TBRL-26 (11/14)
C1-LPB-027 | C1S8.29 | P1-TBRL-27 (A1/A2) | P1-TBRL-27 (11/14)

C1-LPB-028 | C1S8.30 | P1-TBRL-28 (A1/A2) | P1-TBRL-28 (11/14)
C1-LPB-029 | C1S8.31 | P1-TBRL-29 (A1/A2) | P1-TBRL-29 (11/14)
C1-LPB-030 | C1S8.32 | P1-TBRL-30 (A1/A2) | P1-TBRL-30 (11/14)
C1-LPB-031 | C1S8.33 | P1-TBRL-31 (A1/A2) | P1-TBRL-31 (11/14)
C1-LPB-032 | C1S8.34 | P1-TBRL-32 (A1/A2) | P1-TBRL-32 (11/14)
C1-LPB-033 | C1S9.1 | P1-TBRL-33 (A1/A2) | P1-TBRL-33 (11/14)
C1-LPB-034 | C1S9.2 | P1-TBRL-34 (A1/A2) | P1-TBRL-34 (11/14)
C1-LPB-035 | C1S9.3 | P1-TBRL-35 (A1/A2) | P1-TBRL-35 (11/14)
C1-LPB-036 | C1S9.4 | P1-TBRL-36 (A1/A2) | P1-TBRL-36 (11/14)
C1-LPB-037 | C1S9.5 | P1-TBRL-37 (A1/A2) | P1-TBRL-37 (11/14)
C1-LPB-038 | C1S9.6 | P1-TBRL-38 (A1/A2) | P1-TBRL-38 (11/14)
C1-LPB-039 | C1S9.7 | P1-TBRL-39 (A1/A2) | P1-TBRL-39 (11/14)
C1-LPB-040 | C1S9.8 | P1-TBRL-40 (A1/A2) | P1-TBRL-40 (11/14)
C1-LPB-041 | C1S9.9 | P1-TBRL-41 (A1/A2) | P1-TBRL-41 (11/14)
C1-LPB-042 | C1S9.10 | P1-TBRL-42 (A1/A2) | P1-TBRL-42 (11/14)
C1-LPB-043 | C1S9.11 | P1-TBRL-43 (A1/A2) | P1-TBRL-43 (11/14)
C1-LPB-044 | C1S9.12 | P1-TBRL-44 (A1/A2) | P1-TBRL-44 (11/14)
C1-LPB-045 | C1S9.13 | P1-TBRL-45 (A1/A2) | P1-TBRL-45 (11/14)
C1-LPB-046 | C1S9.14 | P1-TBRL-46 (A1/A2) | P1-TBRL-46 (11/14)
C1-LPB-047 | C1S9.15 | P1-TBRL-47 (A1/A2) | P1-TBRL-47 (11/14)
C1-LPB-048 | C1S9.16 | P1-TBRL-48 (A1/A2) | P1-TBRL-48 (11/14)
C1-LPB-049 | C1S9.19 | P1-TBRL-49 (A1/A2) | P1-TBRL-49 (11/14)
C1-LPB-050 | C1S9.20 | P1-TBRL-50 (A1/A2) | P1-TBRL-50 (11/14)
C1-LPB-051 | C1S9.21 | P1-TBRL-51 (A1/A2) | P1-TBRL-51 (11/14)
C1-LPB-052 | C1S9.22 | P1-TBRL-52 (A1/A2) | P1-TBRL-52 (11/14)
C1-LPB-053 | C1S9.23 | P1-TBRL-53 (A1/A2) | P1-TBRL-53 (11/14)
C1-LPB-054 | C1S9.24 | P1-TBRL-54 (A1/A2) | P1-TBRL-54 (11/14)
C1-LPB-055 | C1S9.25 | P1-TBRL-55 (A1/A2) | P1-TBRL-55 (11/14)
C1-LPB-056 | C1S9.26 | P1-TBRL-56 (A1/A2) | P1-TBRL-56 (11/14)
C1-LPB-057 | C1S9.27 | P1-TBRL-57 (A1/A2) | P1-TBRL-57 (11/14)
C1-LPB-058 | C1S9.28 | P1-TBRL-58 (A1/A2) | P1-TBRL-58 (11/14)
C1-LPB-059 | C1S9.29 | P1-TBRL-59 (A1/A2) | P1-TBRL-59 (11/14)
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
