x92120/x260911-002-KalasinEngineering/02_Electrical_and_eDrawing/04_PDF_Reports_and_Drawings/Chassis_C1_Slots_IO_Report.pdf

# KALASIN ENGINEERING — C1 (MAIN CONTROLLERRACK (CHASSIS1))

C1

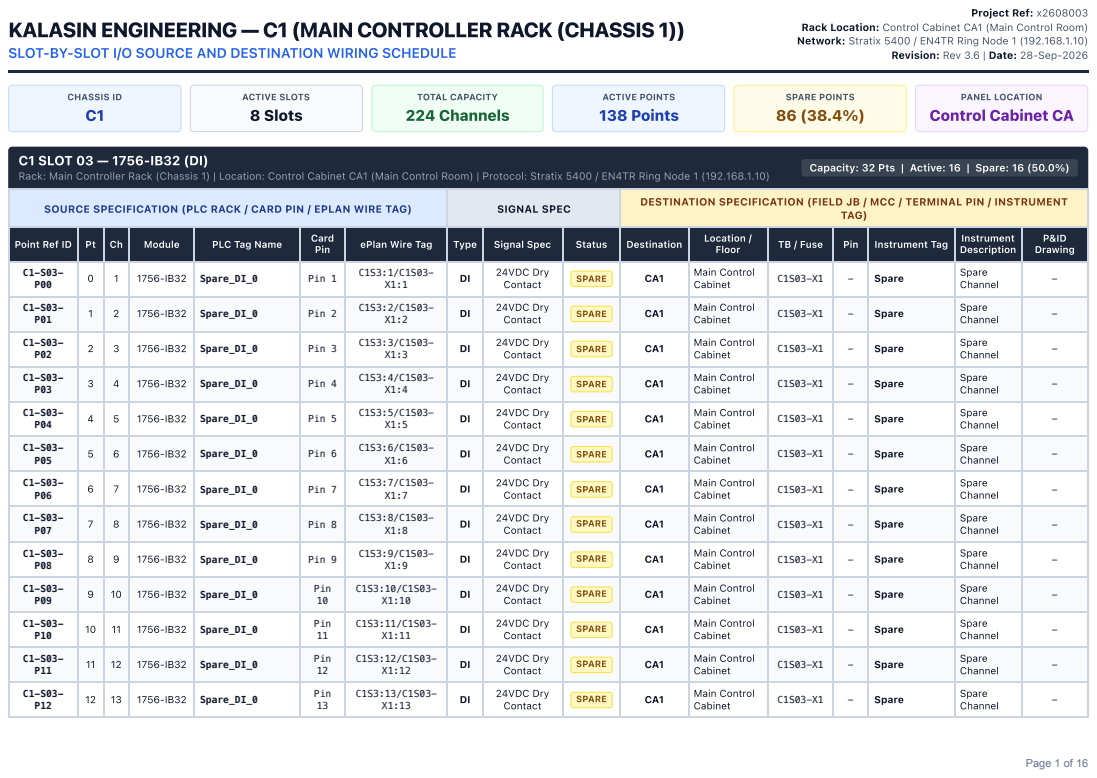
[picture p141: page 1]
Project Ref: x2608003; CHASSIS ID; ACTIVE SLOTS 8 Slots; TOTAL CAPACITY 224 Channels; ACTIVE POINTS 138 Points; SPARE POINTS 86 (38.4%)

Rack Location: Control Cabinet CA1 (Main Control Room)
Network: Stratix 5400 / EN4TR Ring Node 1 (192.168.1.10)

SLOT-BY-SLOT I/O SOURCE AND DESTINATION WIRING SCHEDULE

Revision: Rev 3.6 | Date: 28-Sep-2026

PANEL LOCATION
Control Cabinet CA

C1 SLOT 03 — 1756-IB32 (DI)
Rack: Main Controller Rack (Chassis 1) | Location: Control Cabinet CA1 (Main Control Room) | Protocol: Stratix 5400 / EN4TR Ring Node 1 (192.168.1.10)

Capacity: 32 Pts | Active: 16 | Spare: 16 (50.0%)

SOURCE SPECIFICATION (PLC RACK / CARD PIN / EPLAN WIRE TAG) | SIGNAL SPEC | DESTINATION SPECIFICATION (FIELD JB / MCC / TERMINAL PIN / INSTRUMENT TAG)

Point Ref ID | Pt | Ch | Module | PLC Tag Name | Card Pin | ePlan Wire Tag | Type | Signal Spec | Status | Destination | Location / Floor | TB / Fuse | Pin | Instrument Tag | Instrument Description | P&ID Drawing

C1-S03-P00 | 0 | 1 | 1756-IB32 | Spare_DI_0 | Pin 1 | C1S3:1/C1S03-X1:1 | DI | 24VDC Dry Contact | SPARE | CA1 | Main Control Cabinet | C1S03-X1 | - | Spare | Spare Channel | -

C1-S03-P01 | 1 | 2 | 1756-IB32 | Spare_DI_0 | Pin 2 | C1S3:2/C1S03-X1:2 | DI | 24VDC Dry Contact | SPARE | CA1 | Main Control Cabinet | C1S03-X1 | - | Spare | Spare Channel | -

C1-S03-P02 | 2 | 3 | 1756-IB32 | Spare_DI_0 | Pin 3 | C1S3:3/C1S03-X1:3 | DI | 24VDC Dry Contact | SPARE | CA1 | Main Control Cabinet | C1S03-X1 | - | Spare | Spare Channel | -

C1-S03-P03 | 3 | 4 | 1756-IB32 | Spare_DI_0 | Pin 4 | C1S3:4/C1S03-X1:4 | DI | 24VDC Dry Contact | SPARE | CA1 | Main Control Cabinet | C1S03-X1 | - | Spare | Spare Channel | -

C1-S03-P04 | 4 | 5 | 1756-IB32 | Spare_DI_0 | Pin 5 | C1S3:5/C1S03-X1:5 | DI | 24VDC Dry Contact | SPARE | CA1 | Main Control Cabinet | C1S03-X1 | - | Spare | Spare Channel | -

C1-S03-P05 | 5 | 6 | 1756-IB32 | Spare_DI_0 | Pin 6 | C1S3:6/C1S03-X1:6 | DI | 24VDC Dry Contact | SPARE | CA1 | Main Control Cabinet | C1S03-X1 | - | Spare | Spare Channel | -

C1-S03-P06 | 6 | 7 | 1756-IB32 | Spare_DI_0 | Pin 7 | C1S3:7/C1S03-X1:7 | DI | 24VDC Dry Contact | SPARE | CA1 | Main Control Cabinet | C1S03-X1 | - | Spare | Spare Channel | -

C1-S03-P07 | 7 | 8 | 1756-IB32 | Spare_DI_0 | Pin 8 | C1S3:8/C1S03-X1:8 | DI | 24VDC Dry Contact | SPARE | CA1 | Main Control Cabinet | C1S03-X1 | - | Spare | Spare Channel | -

C1-S03-P08 | 8 | 9 | 1756-IB32 | Spare_DI_0 | Pin 9 | C1S3:9/C1S03-X1:9 | DI | 24VDC Dry Contact | SPARE | CA1 | Main Control Cabinet | C1S03-X1 | - | Spare | Spare Channel | -

C1-S03-P09 | 9 | 10 | 1756-IB32 | Spare_DI_0 | Pin 10 | C1S3:10/C1S03-X1:10 | DI | 24VDC Dry Contact | SPARE | CA1 | Main Control Cabinet | C1S03-X1 | - | Spare | Spare Channel | -

C1-S03-P10 | 10 | 11 | 1756-IB32 | Spare_DI_0 | Pin 11 | C1S3:11/C1S03-X1:11 | DI | 24VDC Dry Contact | SPARE | CA1 | Main Control Cabinet | C1S03-X1 | - | Spare | Spare Channel | -

C1-S03-P11 | 11 | 12 | 1756-IB32 | Spare_DI_0 | Pin 12 | C1S3:12/C1S03-X1:12 | DI | 24VDC Dry Contact | SPARE | CA1 | Main Control Cabinet | C1S03-X1 | - | Spare | Spare Channel | -

C1-S03-P12 | 12 | 13 | 1756-IB32 | Spare_DI_0 | Pin 13 | C1S3:13/C1S03-X1:13 | DI | 24VDC Dry Contact | SPARE | CA1 | Main Control Cabinet | C1S03-X1 | - | Spare | Spare Channel | -

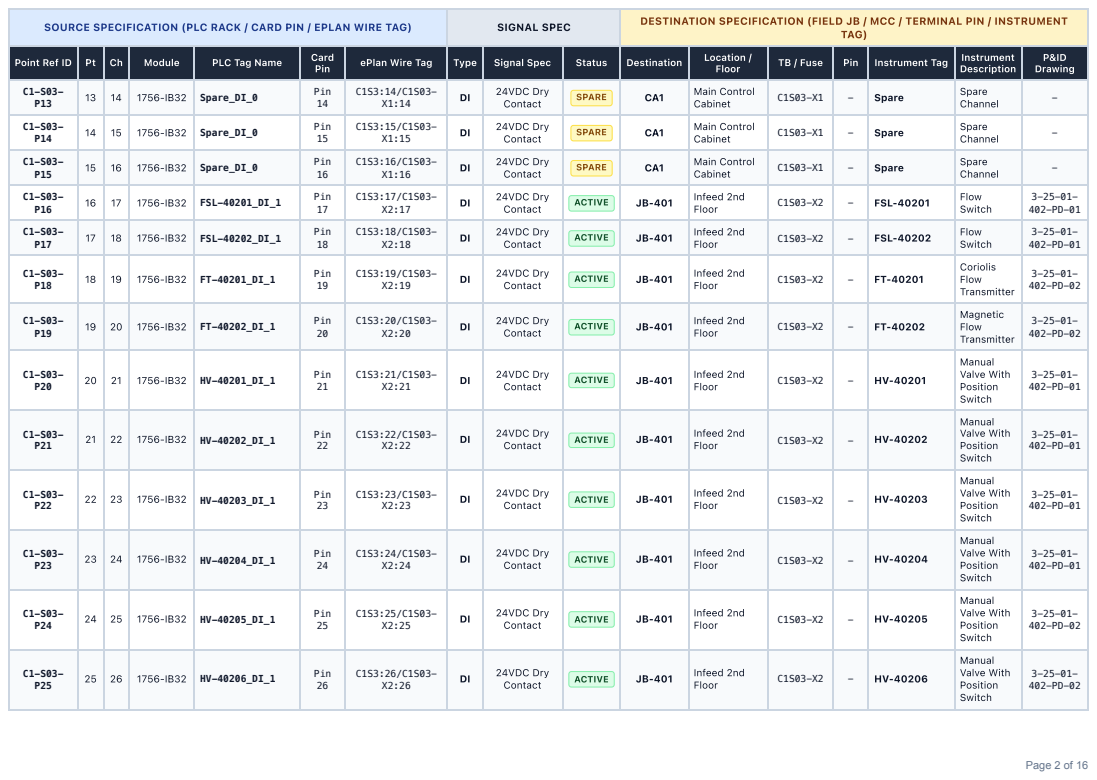
[picture p142: page 2]
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

C1-S03-P13 | 13 | 14 | 1756-IB32 | Spare_DI_0 | Pin 14 | C1S3:14/C1S03-X1:14 | DI | 24VDC Dry Contact | SPARE | CA1 | Main Control Cabinet | C1S03-X1 | - | Spare | Spare Channel | -

C1-S03-P14 | 14 | 15 | 1756-IB32 | Spare_DI_0 | Pin 15 | C1S3:15/C1S03-X1:15 | DI | 24VDC Dry Contact | SPARE | CA1 | Main Control Cabinet | C1S03-X1 | - | Spare | Spare Channel | -

C1-S03-P15 | 15 | 16 | 1756-IB32 | Spare_DI_0 | Pin 16 | C1S3:16/C1S03-X1:16 | DI | 24VDC Dry Contact | SPARE | CA1 | Main Control Cabinet | C1S03-X1 | - | Spare | Spare Channel | -

C1-S03-P16 | 16 | 17 | 1756-IB32 | FSL-40201_DI_1 | Pin 17 | C1S3:17/C1S03-X2:17 | DI | 24VDC Dry Contact | ACTIVE | JB-401 | Infeed 2nd Floor | C1S03-X2 | - | FSL-40201 | Flow Switch | 3-25-01-402-PD-01

C1-S03-P17 | 17 | 18 | 1756-IB32 | FSL-40202_DI_1 | Pin 18 | C1S3:18/C1S03-X2:18 | DI | 24VDC Dry Contact | ACTIVE | JB-401 | Infeed 2nd Floor | C1S03-X2 | - | FSL-40202 | Flow Switch | 3-25-01-402-PD-01

C1-S03-P18 | 18 | 19 | 1756-IB32 | FT-40201_DI_1 | Pin 19 | C1S3:19/C1S03-X2:19 | DI | 24VDC Dry Contact | ACTIVE | JB-401 | Infeed 2nd Floor | C1S03-X2 | - | FT-40201 | Coriolis Flow Transmitter | 3-25-01-402-PD-02

C1-S03-P19 | 19 | 20 | 1756-IB32 | FT-40202_DI_1 | Pin 20 | C1S3:20/C1S03-X2:20 | DI | 24VDC Dry Contact | ACTIVE | JB-401 | Infeed 2nd Floor | C1S03-X2 | - | FT-40202 | Magnetic Flow Transmitter | 3-25-01-402-PD-02

C1-S03-P20 | 20 | 21 | 1756-IB32 | HV-40201_DI_1 | Pin 21 | C1S3:21/C1S03-X2:21 | DI | 24VDC Dry Contact | ACTIVE | JB-401 | Infeed 2nd Floor | C1S03-X2 | - | HV-40201 | Manual Valve With Position Switch | 3-25-01-402-PD-01

C1-S03-P21 | 21 | 22 | 1756-IB32 | HV-40202_DI_1 | Pin 22 | C1S3:22/C1S03-X2:22 | DI | 24VDC Dry Contact | ACTIVE | JB-401 | Infeed 2nd Floor | C1S03-X2 | - | HV-40202 | Manual Valve With Position Switch | 3-25-01-402-PD-01

C1-S03-P22 | 22 | 23 | 1756-IB32 | HV-40203_DI_1 | Pin 23 | C1S3:23/C1S03-X2:23 | DI | 24VDC Dry Contact | ACTIVE | JB-401 | Infeed 2nd Floor | C1S03-X2 | - | HV-40203 | Manual Valve With Position Switch | 3-25-01-402-PD-01

C1-S03-P23 | 23 | 24 | 1756-IB32 | HV-40204_DI_1 | Pin 24 | C1S3:24/C1S03-X2:24 | DI | 24VDC Dry Contact | ACTIVE | JB-401 | Infeed 2nd Floor | C1S03-X2 | - | HV-40204 | Manual Valve With Position Switch | 3-25-01-402-PD-01

C1-S03-P24 | 24 | 25 | 1756-IB32 | HV-40205_DI_1 | Pin 25 | C1S3:25/C1S03-X2:25 | DI | 24VDC Dry Contact | ACTIVE | JB-401 | Infeed 2nd Floor | C1S03-X2 | - | HV-40205 | Manual Valve With Position Switch | 3-25-01-402-PD-02

C1-S03-P25 | 25 | 26 | 1756-IB32 | HV-40206_DI_1 | Pin 26 | C1S3:26/C1S03-X2:26 | DI | 24VDC Dry Contact | ACTIVE | JB-401 | Infeed 2nd Floor | C1S03-X2 | - | HV-40206 | Manual Valve With Position Switch | 3-25-01-402-PD-02

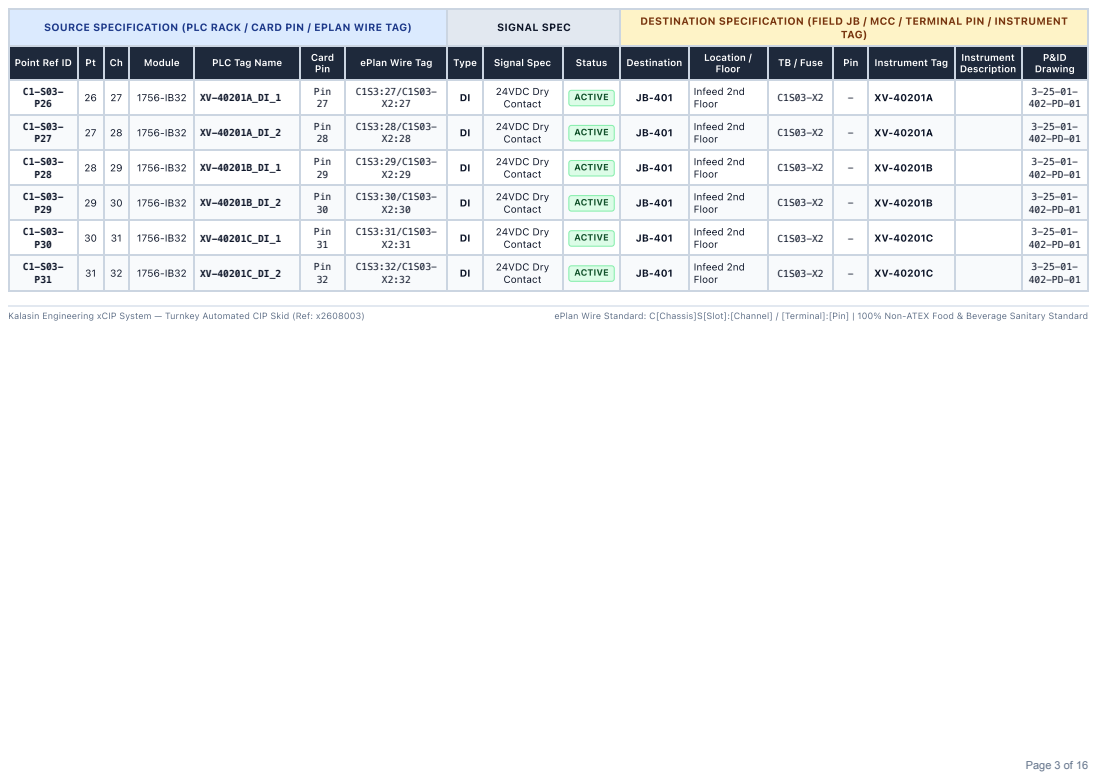
[picture p143: page 3]
Kalasin Engineering xCIP System — Turnkey Automated CIP Skid (Ref: x2608003); ePlan Wire Standard: C[Chassis]S[Slot]:[Channel] / [Terminal]:[Pin] | 100% Non-ATEX Food & Beverage Sanitary Standard

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

C1-S03-P26 | 26 | 27 | 1756-IB32 | XV-40201A_DI_1 | Pin 27 | C1S3:27/C1S03-X2:27 | DI | 24VDC Dry Contact | ACTIVE | JB-401 | Infeed 2nd Floor | C1S03-X2 | - | XV-40201A | | 3-25-01-402-PD-01

C1-S03-P27 | 27 | 28 | 1756-IB32 | XV-40201A_DI_2 | Pin 28 | C1S3:28/C1S03-X2:28 | DI | 24VDC Dry Contact | ACTIVE | JB-401 | Infeed 2nd Floor | C1S03-X2 | - | XV-40201A | | 3-25-01-402-PD-01

C1-S03-P28 | 28 | 29 | 1756-IB32 | XV-40201B_DI_1 | Pin 29 | C1S3:29/C1S03-X2:29 | DI | 24VDC Dry Contact | ACTIVE | JB-401 | Infeed 2nd Floor | C1S03-X2 | - | XV-40201B | | 3-25-01-402-PD-01

C1-S03-P29 | 29 | 30 | 1756-IB32 | XV-40201B_DI_2 | Pin 30 | C1S3:30/C1S03-X2:30 | DI | 24VDC Dry Contact | ACTIVE | JB-401 | Infeed 2nd Floor | C1S03-X2 | - | XV-40201B | | 3-25-01-402-PD-01

C1-S03-P30 | 30 | 31 | 1756-IB32 | XV-40201C_DI_1 | Pin 31 | C1S3:31/C1S03-X2:31 | DI | 24VDC Dry Contact | ACTIVE | JB-401 | Infeed 2nd Floor | C1S03-X2 | - | XV-40201C | | 3-25-01-402-PD-01

C1-S03-P31 | 31 | 32 | 1756-IB32 | XV-40201C_DI_2 | Pin 32 | C1S3:32/C1S03-X2:32 | DI | 24VDC Dry Contact | ACTIVE | JB-401 | Infeed 2nd Floor | C1S03-X2 | - | XV-40201C | | 3-25-01-402-PD-01

## C1 SLOT 04 — 1756-IB32 (DI)

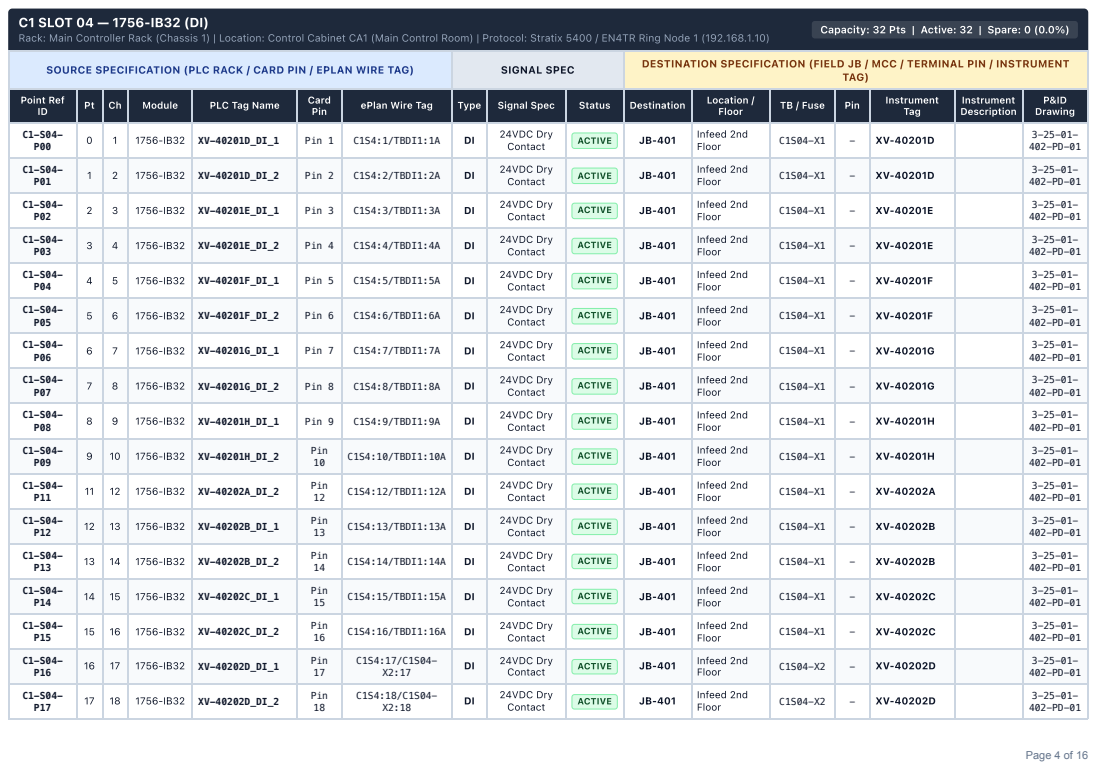
[picture p144: page 4]

Capacity: 32 Pts | Active: 32 | Spare: 0 (0.0%)

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

C1-S04-P00 | 0 | 1 | 1756-IB32 | XV-40201D_DI_1 | Pin 1 | C1S4:1/TBDI1:1A | DI | 24VDC Dry Contact | ACTIVE | JB-401 | Infeed 2nd Floor | C1S04-X1 | - | XV-40201D | | 3-25-01-402-PD-01

C1-S04-P01 | 1 | 2 | 1756-IB32 | XV-40201D_DI_2 | Pin 2 | C1S4:2/TBDI1:2A | DI | 24VDC Dry Contact | ACTIVE | JB-401 | Infeed 2nd Floor | C1S04-X1 | - | XV-40201D | | 3-25-01-402-PD-01

C1-S04-P02 | 2 | 3 | 1756-IB32 | XV-40201E_DI_1 | Pin 3 | C1S4:3/TBDI1:3A | DI | 24VDC Dry Contact | ACTIVE | JB-401 | Infeed 2nd Floor | C1S04-X1 | - | XV-40201E | | 3-25-01-402-PD-01

C1-S04-P03 | 3 | 4 | 1756-IB32 | XV-40201E_DI_2 | Pin 4 | C1S4:4/TBDI1:4A | DI | 24VDC Dry Contact | ACTIVE | JB-401 | Infeed 2nd Floor | C1S04-X1 | - | XV-40201E | | 3-25-01-402-PD-01

C1-S04-P04 | 4 | 5 | 1756-IB32 | XV-40201F_DI_1 | Pin 5 | C1S4:5/TBDI1:5A | DI | 24VDC Dry Contact | ACTIVE | JB-401 | Infeed 2nd Floor | C1S04-X1 | - | XV-40201F | | 3-25-01-402-PD-01

C1-S04-P05 | 5 | 6 | 1756-IB32 | XV-40201F_DI_2 | Pin 6 | C1S4:6/TBDI1:6A | DI | 24VDC Dry Contact | ACTIVE | JB-401 | Infeed 2nd Floor | C1S04-X1 | - | XV-40201F | | 3-25-01-402-PD-01

C1-S04-P06 | 6 | 7 | 1756-IB32 | XV-40201G_DI_1 | Pin 7 | C1S4:7/TBDI1:7A | DI | 24VDC Dry Contact | ACTIVE | JB-401 | Infeed 2nd Floor | C1S04-X1 | - | XV-40201G | | 3-25-01-402-PD-01

C1-S04-P07 | 7 | 8 | 1756-IB32 | XV-40201G_DI_2 | Pin 8 | C1S4:8/TBDI1:8A | DI | 24VDC Dry Contact | ACTIVE | JB-401 | Infeed 2nd Floor | C1S04-X1 | - | XV-40201G | | 3-25-01-402-PD-01

C1-S04-P08 | 8 | 9 | 1756-IB32 | XV-40201H_DI_1 | Pin 9 | C1S4:9/TBDI1:9A | DI | 24VDC Dry Contact | ACTIVE | JB-401 | Infeed 2nd Floor | C1S04-X1 | - | XV-40201H | | 3-25-01-402-PD-01

C1-S04-P09 | 9 | 10 | 1756-IB32 | XV-40201H_DI_2 | Pin 10 | C1S4:10/TBDI1:10A | DI | 24VDC Dry Contact | ACTIVE | JB-401 | Infeed 2nd Floor | C1S04-X1 | - | XV-40201H | | 3-25-01-402-PD-01

C1-S04-P11 | 11 | 12 | 1756-IB32 | XV-40202A_DI_2 | Pin 12 | C1S4:12/TBDI1:12A | DI | 24VDC Dry Contact | ACTIVE | JB-401 | Infeed 2nd Floor | C1S04-X1 | - | XV-40202A | | 3-25-01-402-PD-01

C1-S04-P12 | 12 | 13 | 1756-IB32 | XV-40202B_DI_1 | Pin 13 | C1S4:13/TBDI1:13A | DI | 24VDC Dry Contact | ACTIVE | JB-401 | Infeed 2nd Floor | C1S04-X1 | - | XV-40202B | | 3-25-01-402-PD-01

C1-S04-P13 | 13 | 14 | 1756-IB32 | XV-40202B_DI_2 | Pin 14 | C1S4:14/TBDI1:14A | DI | 24VDC Dry Contact | ACTIVE | JB-401 | Infeed 2nd Floor | C1S04-X1 | - | XV-40202B | | 3-25-01-402-PD-01

C1-S04-P14 | 14 | 15 | 1756-IB32 | XV-40202C_DI_1 | Pin 15 | C1S4:15/TBDI1:15A | DI | 24VDC Dry Contact | ACTIVE | JB-401 | Infeed 2nd Floor | C1S04-X1 | - | XV-40202C | | 3-25-01-402-PD-01

C1-S04-P15 | 15 | 16 | 1756-IB32 | XV-40202C_DI_2 | Pin 16 | C1S4:16/TBDI1:16A | DI | 24VDC Dry Contact | ACTIVE | JB-401 | Infeed 2nd Floor | C1S04-X1 | - | XV-40202C | | 3-25-01-402-PD-01

C1-S04-P16 | 16 | 17 | 1756-IB32 | XV-40202D_DI_1 | Pin 17 | C1S4:17/C1S04-X2:17 | DI | 24VDC Dry Contact | ACTIVE | JB-401 | Infeed 2nd Floor | C1S04-X2 | - | XV-40202D | | 3-25-01-402-PD-01

C1-S04-P17 | 17 | 18 | 1756-IB32 | XV-40202D_DI_2 | Pin 18 | C1S4:18/C1S04-X2:18 | DI | 24VDC Dry Contact | ACTIVE | JB-401 | Infeed 2nd Floor | C1S04-X2 | - | XV-40202D | | 3-25-01-402-PD-01

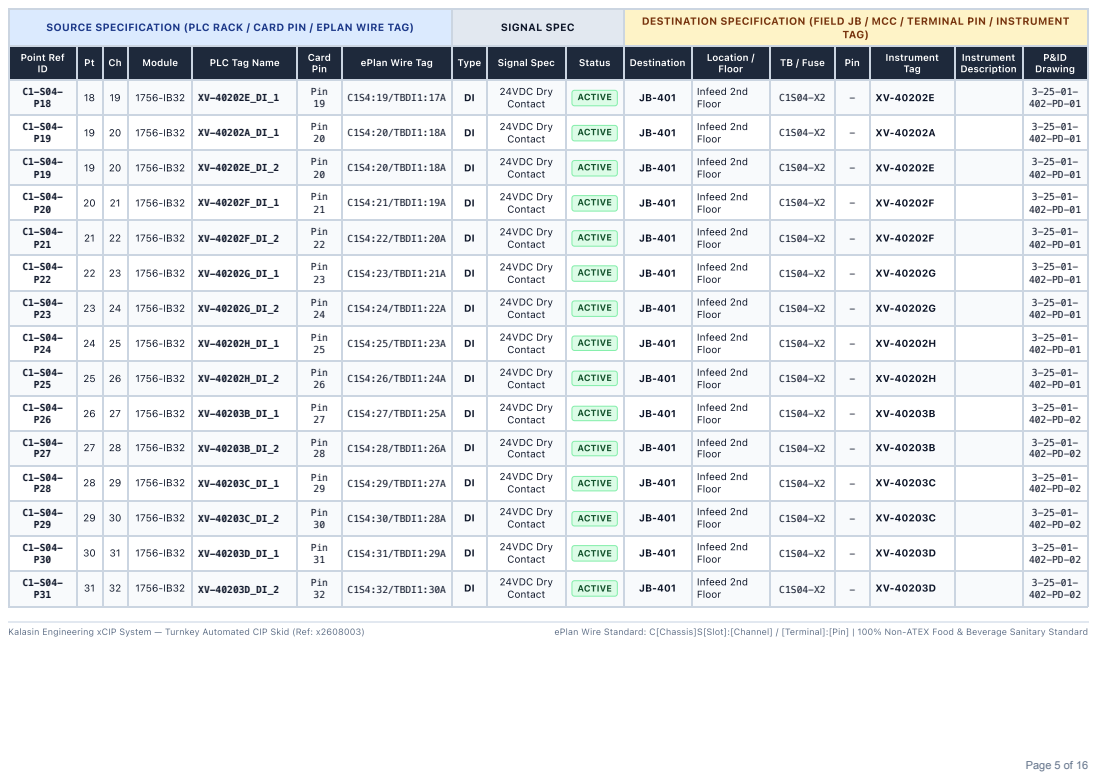
[picture p145: page 5]
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

C1-S04-P18 | 18 | 19 | 1756-IB32 | XV-40202E_DI_1 | Pin 19 | C1S4:19/TBDI1:17A | DI | 24VDC Dry Contact | ACTIVE | JB-401 | Infeed 2nd Floor | C1S04-X2 | - | XV-40202E | | 3-25-01-402-PD-01

C1-S04-P19 | 19 | 20 | 1756-IB32 | XV-40202A_DI_1 | Pin 20 | C1S4:20/TBDI1:18A | DI | 24VDC Dry Contact | ACTIVE | JB-401 | Infeed 2nd Floor | C1S04-X2 | - | XV-40202A | | 3-25-01-402-PD-01

C1-S04-P19 | 19 | 20 | 1756-IB32 | XV-40202E_DI_2 | Pin 20 | C1S4:20/TBDI1:18A | DI | 24VDC Dry Contact | ACTIVE | JB-401 | Infeed 2nd Floor | C1S04-X2 | - | XV-40202E | | 3-25-01-402-PD-01

C1-S04-P20 | 20 | 21 | 1756-IB32 | XV-40202F_DI_1 | Pin 21 | C1S4:21/TBDI1:19A | DI | 24VDC Dry Contact | ACTIVE | JB-401 | Infeed 2nd Floor | C1S04-X2 | - | XV-40202F | | 3-25-01-402-PD-01

C1-S04-P21 | 21 | 22 | 1756-IB32 | XV-40202F_DI_2 | Pin 22 | C1S4:22/TBDI1:20A | DI | 24VDC Dry Contact | ACTIVE | JB-401 | Infeed 2nd Floor | C1S04-X2 | - | XV-40202F | | 3-25-01-402-PD-01

C1-S04-P22 | 22 | 23 | 1756-IB32 | XV-40202G_DI_1 | Pin 23 | C1S4:23/TBDI1:21A | DI | 24VDC Dry Contact | ACTIVE | JB-401 | Infeed 2nd Floor | C1S04-X2 | - | XV-40202G | | 3-25-01-402-PD-01

C1-S04-P23 | 23 | 24 | 1756-IB32 | XV-40202G_DI_2 | Pin 24 | C1S4:24/TBDI1:22A | DI | 24VDC Dry Contact | ACTIVE | JB-401 | Infeed 2nd Floor | C1S04-X2 | - | XV-40202G | | 3-25-01-402-PD-01

C1-S04-P24 | 24 | 25 | 1756-IB32 | XV-40202H_DI_1 | Pin 25 | C1S4:25/TBDI1:23A | DI | 24VDC Dry Contact | ACTIVE | JB-401 | Infeed 2nd Floor | C1S04-X2 | - | XV-40202H | | 3-25-01-402-PD-01

C1-S04-P25 | 25 | 26 | 1756-IB32 | XV-40202H_DI_2 | Pin 26 | C1S4:26/TBDI1:24A | DI | 24VDC Dry Contact | ACTIVE | JB-401 | Infeed 2nd Floor | C1S04-X2 | - | XV-40202H | | 3-25-01-402-PD-01

C1-S04-P26 | 26 | 27 | 1756-IB32 | XV-40203B_DI_1 | Pin 27 | C1S4:27/TBDI1:25A | DI | 24VDC Dry Contact | ACTIVE | JB-401 | Infeed 2nd Floor | C1S04-X2 | - | XV-40203B | | 3-25-01-402-PD-02

C1-S04-P27 | 27 | 28 | 1756-IB32 | XV-40203B_DI_2 | Pin 28 | C1S4:28/TBDI1:26A | DI | 24VDC Dry Contact | ACTIVE | JB-401 | Infeed 2nd Floor | C1S04-X2 | - | XV-40203B | | 3-25-01-402-PD-02

C1-S04-P28 | 28 | 29 | 1756-IB32 | XV-40203C_DI_1 | Pin 29 | C1S4:29/TBDI1:27A | DI | 24VDC Dry Contact | ACTIVE | JB-401 | Infeed 2nd Floor | C1S04-X2 | - | XV-40203C | | 3-25-01-402-PD-02

C1-S04-P29 | 29 | 30 | 1756-IB32 | XV-40203C_DI_2 | Pin 30 | C1S4:30/TBDI1:28A | DI | 24VDC Dry Contact | ACTIVE | JB-401 | Infeed 2nd Floor | C1S04-X2 | - | XV-40203C | | 3-25-01-402-PD-02

C1-S04-P30 | 30 | 31 | 1756-IB32 | XV-40203D_DI_1 | Pin 31 | C1S4:31/TBDI1:29A | DI | 24VDC Dry Contact | ACTIVE | JB-401 | Infeed 2nd Floor | C1S04-X2 | - | XV-40203D | | 3-25-01-402-PD-02

C1-S04-P31 | 31 | 32 | 1756-IB32 | XV-40203D_DI_2 | Pin 32 | C1S4:32/TBDI1:30A | DI | 24VDC Dry Contact | ACTIVE | JB-401 | Infeed 2nd Floor | C1S04-X2 | - | XV-40203D | | 3-25-01-402-PD-02

## C1 SLOT 05 — 1756-IB32 (DI)

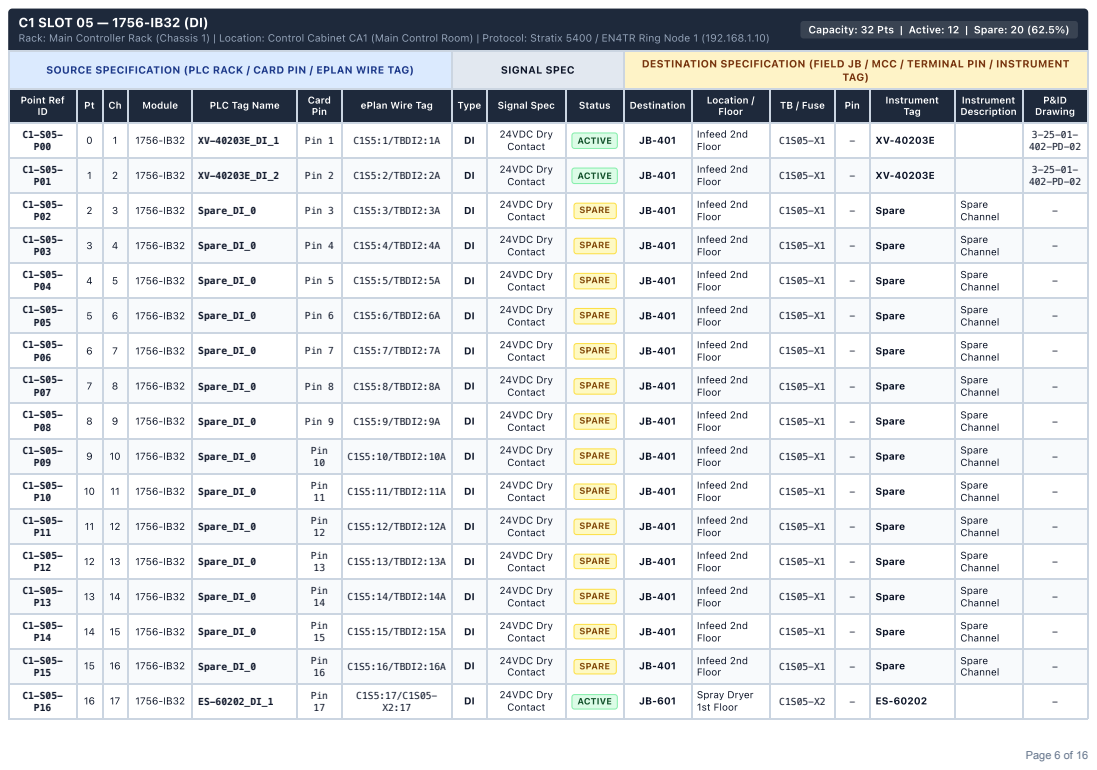
[picture p146: page 6]

Capacity: 32 Pts | Active: 12 | Spare: 20 (62.5%)

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

C1-S05-P00 | 0 | 1 | 1756-IB32 | XV-40203E_DI_1 | Pin 1 | C1S5:1/TBDI2:1A | DI | 24VDC Dry Contact | ACTIVE | JB-401 | Infeed 2nd Floor | C1S05-X1 | - | XV-40203E | | 3-25-01-402-PD-02

C1-S05-P01 | 1 | 2 | 1756-IB32 | XV-40203E_DI_2 | Pin 2 | C1S5:2/TBDI2:2A | DI | 24VDC Dry Contact | ACTIVE | JB-401 | Infeed 2nd Floor | C1S05-X1 | - | XV-40203E | | 3-25-01-402-PD-02

C1-S05-P02 | 2 | 3 | 1756-IB32 | Spare_DI_0 | Pin 3 | C1S5:3/TBDI2:3A | DI | 24VDC Dry Contact | SPARE | JB-401 | Infeed 2nd Floor | C1S05-X1 | - | Spare | Spare Channel | -

C1-S05-P03 | 3 | 4 | 1756-IB32 | Spare_DI_0 | Pin 4 | C1S5:4/TBDI2:4A | DI | 24VDC Dry Contact | SPARE | JB-401 | Infeed 2nd Floor | C1S05-X1 | - | Spare | Spare Channel | -

C1-S05-P04 | 4 | 5 | 1756-IB32 | Spare_DI_0 | Pin 5 | C1S5:5/TBDI2:5A | DI | 24VDC Dry Contact | SPARE | JB-401 | Infeed 2nd Floor | C1S05-X1 | - | Spare | Spare Channel | -

C1-S05-P05 | 5 | 6 | 1756-IB32 | Spare_DI_0 | Pin 6 | C1S5:6/TBDI2:6A | DI | 24VDC Dry Contact | SPARE | JB-401 | Infeed 2nd Floor | C1S05-X1 | - | Spare | Spare Channel | -

C1-S05-P06 | 6 | 7 | 1756-IB32 | Spare_DI_0 | Pin 7 | C1S5:7/TBDI2:7A | DI | 24VDC Dry Contact | SPARE | JB-401 | Infeed 2nd Floor | C1S05-X1 | - | Spare | Spare Channel | -

C1-S05-P07 | 7 | 8 | 1756-IB32 | Spare_DI_0 | Pin 8 | C1S5:8/TBDI2:8A | DI | 24VDC Dry Contact | SPARE | JB-401 | Infeed 2nd Floor | C1S05-X1 | - | Spare | Spare Channel | -

C1-S05-P08 | 8 | 9 | 1756-IB32 | Spare_DI_0 | Pin 9 | C1S5:9/TBDI2:9A | DI | 24VDC Dry Contact | SPARE | JB-401 | Infeed 2nd Floor | C1S05-X1 | - | Spare | Spare Channel | -

C1-S05-P09 | 9 | 10 | 1756-IB32 | Spare_DI_0 | Pin 10 | C1S5:10/TBDI2:10A | DI | 24VDC Dry Contact | SPARE | JB-401 | Infeed 2nd Floor | C1S05-X1 | - | Spare | Spare Channel | -

C1-S05-P10 | 10 | 11 | 1756-IB32 | Spare_DI_0 | Pin 11 | C1S5:11/TBDI2:11A | DI | 24VDC Dry Contact | SPARE | JB-401 | Infeed 2nd Floor | C1S05-X1 | - | Spare | Spare Channel | -

C1-S05-P11 | 11 | 12 | 1756-IB32 | Spare_DI_0 | Pin 12 | C1S5:12/TBDI2:12A | DI | 24VDC Dry Contact | SPARE | JB-401 | Infeed 2nd Floor | C1S05-X1 | - | Spare | Spare Channel | -

C1-S05-P12 | 12 | 13 | 1756-IB32 | Spare_DI_0 | Pin 13 | C1S5:13/TBDI2:13A | DI | 24VDC Dry Contact | SPARE | JB-401 | Infeed 2nd Floor | C1S05-X1 | - | Spare | Spare Channel | -

C1-S05-P13 | 13 | 14 | 1756-IB32 | Spare_DI_0 | Pin 14 | C1S5:14/TBDI2:14A | DI | 24VDC Dry Contact | SPARE | JB-401 | Infeed 2nd Floor | C1S05-X1 | - | Spare | Spare Channel | -

C1-S05-P14 | 14 | 15 | 1756-IB32 | Spare_DI_0 | Pin 15 | C1S5:15/TBDI2:15A | DI | 24VDC Dry Contact | SPARE | JB-401 | Infeed 2nd Floor | C1S05-X1 | - | Spare | Spare Channel | -

C1-S05-P15 | 15 | 16 | 1756-IB32 | Spare_DI_0 | Pin 16 | C1S5:16/TBDI2:16A | DI | 24VDC Dry Contact | SPARE | JB-401 | Infeed 2nd Floor | C1S05-X1 | - | Spare | Spare Channel | -

C1-S05-P16 | 16 | 17 | 1756-IB32 | ES-60202_DI_1 | Pin 17 | C1S5:17/C1S05-X2:17 | DI | 24VDC Dry Contact | ACTIVE | JB-601 | Spray Dryer 1st Floor | C1S05-X2 | - | ES-60202 | | -

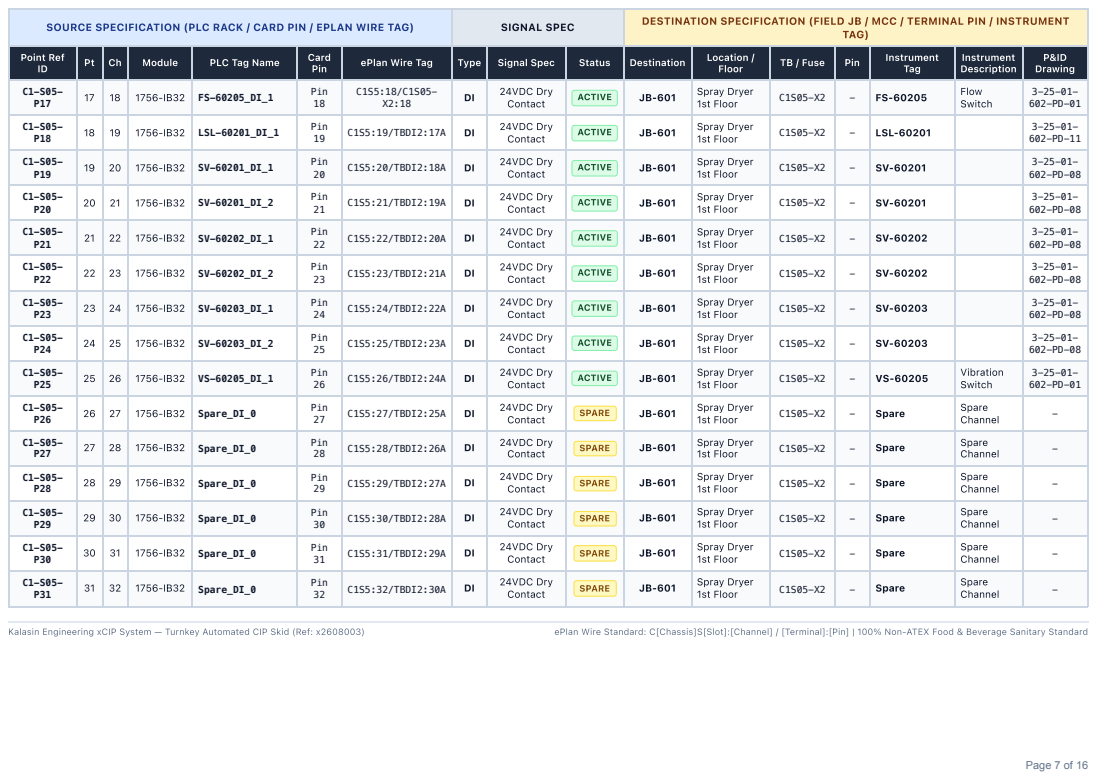
[picture p147: page 7]
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

C1-S05-P17 | 17 | 18 | 1756-IB32 | FS-60205_DI_1 | Pin 18 | C1S5:18/C1S05-X2:18 | DI | 24VDC Dry Contact | ACTIVE | JB-601 | Spray Dryer 1st Floor | C1S05-X2 | - | FS-60205 | Flow Switch | 3-25-01-602-PD-01

C1-S05-P18 | 18 | 19 | 1756-IB32 | LSL-60201_DI_1 | Pin 19 | C1S5:19/TBDI2:17A | DI | 24VDC Dry Contact | ACTIVE | JB-601 | Spray Dryer 1st Floor | C1S05-X2 | - | LSL-60201 | | 3-25-01-602-PD-11

C1-S05-P19 | 19 | 20 | 1756-IB32 | SV-60201_DI_1 | Pin 20 | C1S5:20/TBDI2:18A | DI | 24VDC Dry Contact | ACTIVE | JB-601 | Spray Dryer 1st Floor | C1S05-X2 | - | SV-60201 | | 3-25-01-602-PD-08

C1-S05-P20 | 20 | 21 | 1756-IB32 | SV-60201_DI_2 | Pin 21 | C1S5:21/TBDI2:19A | DI | 24VDC Dry Contact | ACTIVE | JB-601 | Spray Dryer 1st Floor | C1S05-X2 | - | SV-60201 | | 3-25-01-602-PD-08

C1-S05-P21 | 21 | 22 | 1756-IB32 | SV-60202_DI_1 | Pin 22 | C1S5:22/TBDI2:20A | DI | 24VDC Dry Contact | ACTIVE | JB-601 | Spray Dryer 1st Floor | C1S05-X2 | - | SV-60202 | | 3-25-01-602-PD-08

C1-S05-P22 | 22 | 23 | 1756-IB32 | SV-60202_DI_2 | Pin 23 | C1S5:23/TBDI2:21A | DI | 24VDC Dry Contact | ACTIVE | JB-601 | Spray Dryer 1st Floor | C1S05-X2 | - | SV-60202 | | 3-25-01-602-PD-08

C1-S05-P23 | 23 | 24 | 1756-IB32 | SV-60203_DI_1 | Pin 24 | C1S5:24/TBDI2:22A | DI | 24VDC Dry Contact | ACTIVE | JB-601 | Spray Dryer 1st Floor | C1S05-X2 | - | SV-60203 | | 3-25-01-602-PD-08

C1-S05-P24 | 24 | 25 | 1756-IB32 | SV-60203_DI_2 | Pin 25 | C1S5:25/TBDI2:23A | DI | 24VDC Dry Contact | ACTIVE | JB-601 | Spray Dryer 1st Floor | C1S05-X2 | - | SV-60203 | | 3-25-01-602-PD-08

C1-S05-P25 | 25 | 26 | 1756-IB32 | VS-60205_DI_1 | Pin 26 | C1S5:26/TBDI2:24A | DI | 24VDC Dry Contact | ACTIVE | JB-601 | Spray Dryer 1st Floor | C1S05-X2 | - | VS-60205 | Vibration Switch | 3-25-01-602-PD-01

C1-S05-P26 | 26 | 27 | 1756-IB32 | Spare_DI_0 | Pin 27 | C1S5:27/TBDI2:25A | DI | 24VDC Dry Contact | SPARE | JB-601 | Spray Dryer 1st Floor | C1S05-X2 | - | Spare | Spare Channel | -

C1-S05-P27 | 27 | 28 | 1756-IB32 | Spare_DI_0 | Pin 28 | C1S5:28/TBDI2:26A | DI | 24VDC Dry Contact | SPARE | JB-601 | Spray Dryer 1st Floor | C1S05-X2 | - | Spare | Spare Channel | -

C1-S05-P28 | 28 | 29 | 1756-IB32 | Spare_DI_0 | Pin 29 | C1S5:29/TBDI2:27A | DI | 24VDC Dry Contact | SPARE | JB-601 | Spray Dryer 1st Floor | C1S05-X2 | - | Spare | Spare Channel | -

C1-S05-P29 | 29 | 30 | 1756-IB32 | Spare_DI_0 | Pin 30 | C1S5:30/TBDI2:28A | DI | 24VDC Dry Contact | SPARE | JB-601 | Spray Dryer 1st Floor | C1S05-X2 | - | Spare | Spare Channel | -

C1-S05-P30 | 30 | 31 | 1756-IB32 | Spare_DI_0 | Pin 31 | C1S5:31/TBDI2:29A | DI | 24VDC Dry Contact | SPARE | JB-601 | Spray Dryer 1st Floor | C1S05-X2 | - | Spare | Spare Channel | -

C1-S05-P31 | 31 | 32 | 1756-IB32 | Spare_DI_0 | Pin 32 | C1S5:32/TBDI2:30A | DI | 24VDC Dry Contact | SPARE | JB-601 | Spray Dryer 1st Floor | C1S05-X2 | - | Spare | Spare Channel | -

## C1 SLOT 06 — 1756-IB32 (DI)

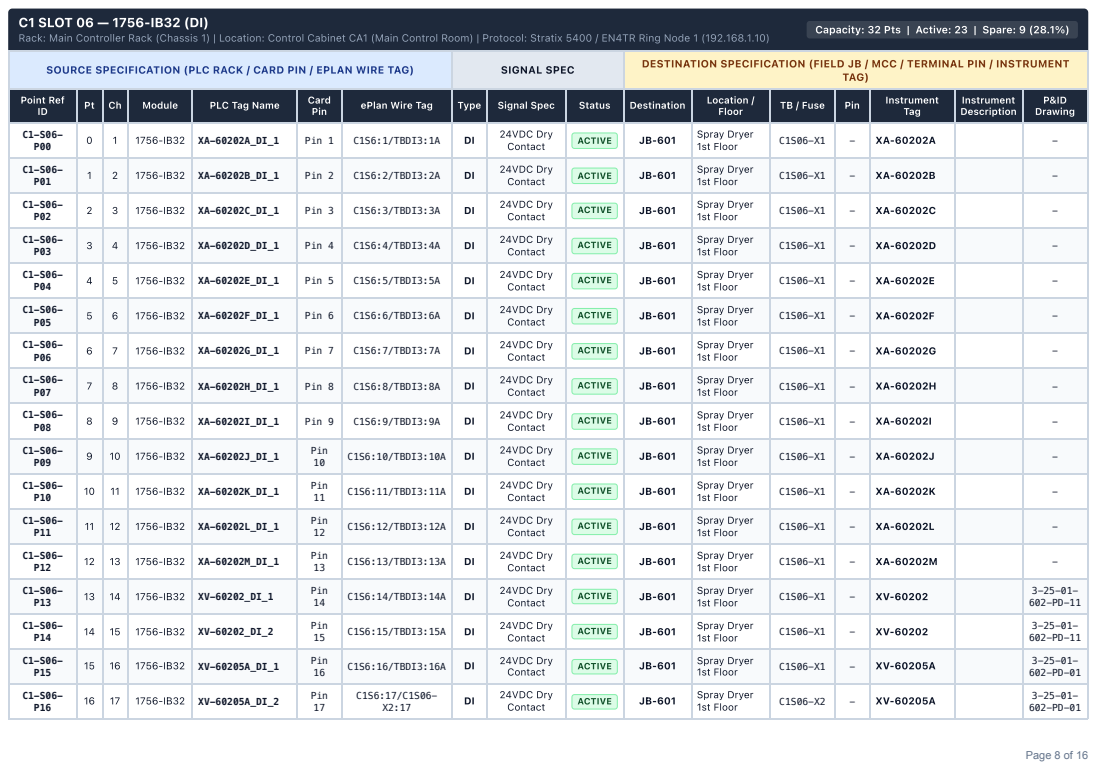
[picture p148: page 8]

Capacity: 32 Pts | Active: 23 | Spare: 9 (28.1%)

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

C1-S06-P00 | 0 | 1 | 1756-IB32 | XA-60202A_DI_1 | Pin 1 | C1S6:1/TBDI3:1A | DI | 24VDC Dry Contact | ACTIVE | JB-601 | Spray Dryer 1st Floor | C1S06-X1 | - | XA-60202A | | -

C1-S06-P01 | 1 | 2 | 1756-IB32 | XA-60202B_DI_1 | Pin 2 | C1S6:2/TBDI3:2A | DI | 24VDC Dry Contact | ACTIVE | JB-601 | Spray Dryer 1st Floor | C1S06-X1 | - | XA-60202B | | -

C1-S06-P02 | 2 | 3 | 1756-IB32 | XA-60202C_DI_1 | Pin 3 | C1S6:3/TBDI3:3A | DI | 24VDC Dry Contact | ACTIVE | JB-601 | Spray Dryer 1st Floor | C1S06-X1 | - | XA-60202C | | -

C1-S06-P03 | 3 | 4 | 1756-IB32 | XA-60202D_DI_1 | Pin 4 | C1S6:4/TBDI3:4A | DI | 24VDC Dry Contact | ACTIVE | JB-601 | Spray Dryer 1st Floor | C1S06-X1 | - | XA-60202D | | -

C1-S06-P04 | 4 | 5 | 1756-IB32 | XA-60202E_DI_1 | Pin 5 | C1S6:5/TBDI3:5A | DI | 24VDC Dry Contact | ACTIVE | JB-601 | Spray Dryer 1st Floor | C1S06-X1 | - | XA-60202E | | -

C1-S06-P05 | 5 | 6 | 1756-IB32 | XA-60202F_DI_1 | Pin 6 | C1S6:6/TBDI3:6A | DI | 24VDC Dry Contact | ACTIVE | JB-601 | Spray Dryer 1st Floor | C1S06-X1 | - | XA-60202F | | -

C1-S06-P06 | 6 | 7 | 1756-IB32 | XA-60202G_DI_1 | Pin 7 | C1S6:7/TBDI3:7A | DI | 24VDC Dry Contact | ACTIVE | JB-601 | Spray Dryer 1st Floor | C1S06-X1 | - | XA-60202G | | -

C1-S06-P07 | 7 | 8 | 1756-IB32 | XA-60202H_DI_1 | Pin 8 | C1S6:8/TBDI3:8A | DI | 24VDC Dry Contact | ACTIVE | JB-601 | Spray Dryer 1st Floor | C1S06-X1 | - | XA-60202H | | -

C1-S06-P08 | 8 | 9 | 1756-IB32 | XA-60202I_DI_1 | Pin 9 | C1S6:9/TBDI3:9A | DI | 24VDC Dry Contact | ACTIVE | JB-601 | Spray Dryer 1st Floor | C1S06-X1 | - | XA-60202I | | -

C1-S06-P09 | 9 | 10 | 1756-IB32 | XA-60202J_DI_1 | Pin 10 | C1S6:10/TBDI3:10A | DI | 24VDC Dry Contact | ACTIVE | JB-601 | Spray Dryer 1st Floor | C1S06-X1 | - | XA-60202J | | -

C1-S06-P10 | 10 | 11 | 1756-IB32 | XA-60202K_DI_1 | Pin 11 | C1S6:11/TBDI3:11A | DI | 24VDC Dry Contact | ACTIVE | JB-601 | Spray Dryer 1st Floor | C1S06-X1 | - | XA-60202K | | -

C1-S06-P11 | 11 | 12 | 1756-IB32 | XA-60202L_DI_1 | Pin 12 | C1S6:12/TBDI3:12A | DI | 24VDC Dry Contact | ACTIVE | JB-601 | Spray Dryer 1st Floor | C1S06-X1 | - | XA-60202L | | -

C1-S06-P12 | 12 | 13 | 1756-IB32 | XA-60202M_DI_1 | Pin 13 | C1S6:13/TBDI3:13A | DI | 24VDC Dry Contact | ACTIVE | JB-601 | Spray Dryer 1st Floor | C1S06-X1 | - | XA-60202M | | -

C1-S06-P13 | 13 | 14 | 1756-IB32 | XV-60202_DI_1 | Pin 14 | C1S6:14/TBDI3:14A | DI | 24VDC Dry Contact | ACTIVE | JB-601 | Spray Dryer 1st Floor | C1S06-X1 | - | XV-60202 | | 3-25-01-602-PD-11

C1-S06-P14 | 14 | 15 | 1756-IB32 | XV-60202_DI_2 | Pin 15 | C1S6:15/TBDI3:15A | DI | 24VDC Dry Contact | ACTIVE | JB-601 | Spray Dryer 1st Floor | C1S06-X1 | - | XV-60202 | | 3-25-01-602-PD-11

C1-S06-P15 | 15 | 16 | 1756-IB32 | XV-60205A_DI_1 | Pin 16 | C1S6:16/TBDI3:16A | DI | 24VDC Dry Contact | ACTIVE | JB-601 | Spray Dryer 1st Floor | C1S06-X1 | - | XV-60205A | | 3-25-01-602-PD-01

C1-S06-P16 | 16 | 17 | 1756-IB32 | XV-60205A_DI_2 | Pin 17 | C1S6:17/C1S06-X2:17 | DI | 24VDC Dry Contact | ACTIVE | JB-601 | Spray Dryer 1st Floor | C1S06-X2 | - | XV-60205A | | 3-25-01-602-PD-01

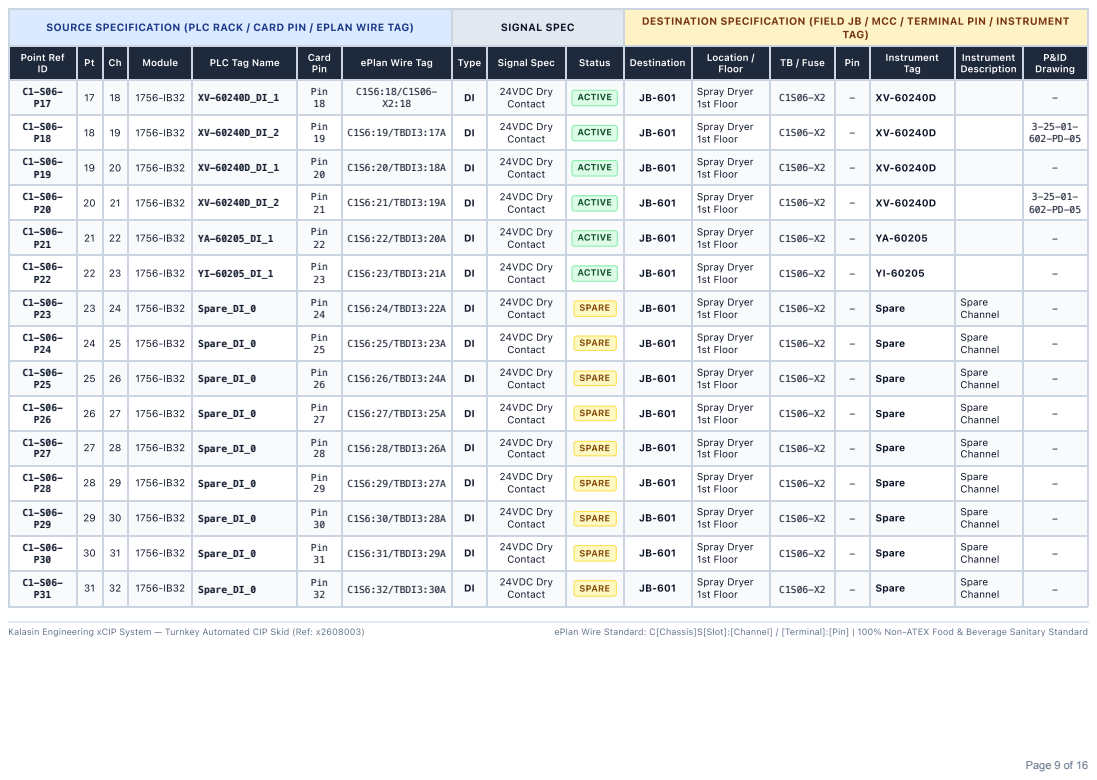
[picture p149: page 9]
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

C1-S06-P17 | 17 | 18 | 1756-IB32 | XV-60240D_DI_1 | Pin 18 | C1S6:18/C1S06-X2:18 | DI | 24VDC Dry Contact | ACTIVE | JB-601 | Spray Dryer 1st Floor | C1S06-X2 | - | XV-60240D | | -

C1-S06-P18 | 18 | 19 | 1756-IB32 | XV-60240D_DI_2 | Pin 19 | C1S6:19/TBDI3:17A | DI | 24VDC Dry Contact | ACTIVE | JB-601 | Spray Dryer 1st Floor | C1S06-X2 | - | XV-60240D | | 3-25-01-602-PD-05

C1-S06-P19 | 19 | 20 | 1756-IB32 | XV-60240D_DI_1 | Pin 20 | C1S6:20/TBDI3:18A | DI | 24VDC Dry Contact | ACTIVE | JB-601 | Spray Dryer 1st Floor | C1S06-X2 | - | XV-60240D | | -

C1-S06-P20 | 20 | 21 | 1756-IB32 | XV-60240D_DI_2 | Pin 21 | C1S6:21/TBDI3:19A | DI | 24VDC Dry Contact | ACTIVE | JB-601 | Spray Dryer 1st Floor | C1S06-X2 | - | XV-60240D | | 3-25-01-602-PD-05

C1-S06-P21 | 21 | 22 | 1756-IB32 | YA-60205_DI_1 | Pin 22 | C1S6:22/TBDI3:20A | DI | 24VDC Dry Contact | ACTIVE | JB-601 | Spray Dryer 1st Floor | C1S06-X2 | - | YA-60205 | | -

C1-S06-P22 | 22 | 23 | 1756-IB32 | YI-60205_DI_1 | Pin 23 | C1S6:23/TBDI3:21A | DI | 24VDC Dry Contact | ACTIVE | JB-601 | Spray Dryer 1st Floor | C1S06-X2 | - | YI-60205 | | -

C1-S06-P23 | 23 | 24 | 1756-IB32 | Spare_DI_0 | Pin 24 | C1S6:24/TBDI3:22A | DI | 24VDC Dry Contact | SPARE | JB-601 | Spray Dryer 1st Floor | C1S06-X2 | - | Spare | Spare Channel | -

C1-S06-P24 | 24 | 25 | 1756-IB32 | Spare_DI_0 | Pin 25 | C1S6:25/TBDI3:23A | DI | 24VDC Dry Contact | SPARE | JB-601 | Spray Dryer 1st Floor | C1S06-X2 | - | Spare | Spare Channel | -

C1-S06-P25 | 25 | 26 | 1756-IB32 | Spare_DI_0 | Pin 26 | C1S6:26/TBDI3:24A | DI | 24VDC Dry Contact | SPARE | JB-601 | Spray Dryer 1st Floor | C1S06-X2 | - | Spare | Spare Channel | -

C1-S06-P26 | 26 | 27 | 1756-IB32 | Spare_DI_0 | Pin 27 | C1S6:27/TBDI3:25A | DI | 24VDC Dry Contact | SPARE | JB-601 | Spray Dryer 1st Floor | C1S06-X2 | - | Spare | Spare Channel | -

C1-S06-P27 | 27 | 28 | 1756-IB32 | Spare_DI_0 | Pin 28 | C1S6:28/TBDI3:26A | DI | 24VDC Dry Contact | SPARE | JB-601 | Spray Dryer 1st Floor | C1S06-X2 | - | Spare | Spare Channel | -

C1-S06-P28 | 28 | 29 | 1756-IB32 | Spare_DI_0 | Pin 29 | C1S6:29/TBDI3:27A | DI | 24VDC Dry Contact | SPARE | JB-601 | Spray Dryer 1st Floor | C1S06-X2 | - | Spare | Spare Channel | -

C1-S06-P29 | 29 | 30 | 1756-IB32 | Spare_DI_0 | Pin 30 | C1S6:30/TBDI3:28A | DI | 24VDC Dry Contact | SPARE | JB-601 | Spray Dryer 1st Floor | C1S06-X2 | - | Spare | Spare Channel | -

C1-S06-P30 | 30 | 31 | 1756-IB32 | Spare_DI_0 | Pin 31 | C1S6:31/TBDI3:29A | DI | 24VDC Dry Contact | SPARE | JB-601 | Spray Dryer 1st Floor | C1S06-X2 | - | Spare | Spare Channel | -

C1-S06-P31 | 31 | 32 | 1756-IB32 | Spare_DI_0 | Pin 32 | C1S6:32/TBDI3:30A | DI | 24VDC Dry Contact | SPARE | JB-601 | Spray Dryer 1st Floor | C1S06-X2 | - | Spare | Spare Channel | -
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
