x92120/x260911-002-KalasinEngineering/02_Electrical_and_eDrawing/04_PDF_Reports_and_Drawings/Chassis_C2_Slots_IO_Report.pdf

# KALASIN ENGINEERING — C2 (I/O EXPANSION RACK 1 (CHASSIS2))

C2

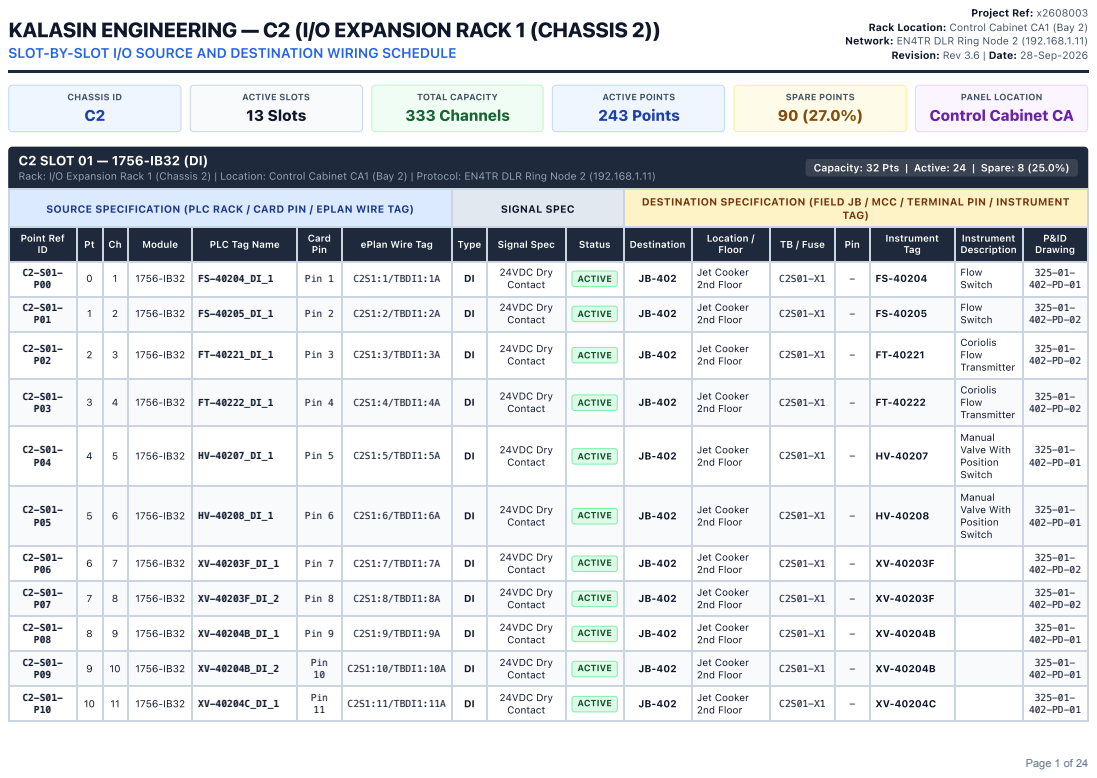
[picture p150: page 1]
Project Ref: x2608003; CHASSIS ID; ACTIVE SLOTS 13 Slots; TOTAL CAPACITY 333 Channels; ACTIVE POINTS 243 Points; SPARE POINTS 90 (27.0%)

Rack Location: Control Cabinet CA1 (Bay 2)
Network: EN4TR DLR Ring Node 2 (192.168.1.11)

SLOT-BY-SLOT I/O SOURCE AND DESTINATION WIRING SCHEDULE

Revision: Rev 3.6 | Date: 28-Sep-2026

PANEL LOCATION
Control Cabinet CA

C2 SLOT 01 — 1756-IB32 (DI)
Rack: I/O Expansion Rack 1 (Chassis 2) | Location: Control Cabinet CA1 (Bay 2) | Protocol: EN4TR DLR Ring Node 2 (192.168.1.11)

Capacity: 32 Pts | Active: 24 | Spare: 8 (25.0%)

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

C2-S01-P00 | 0 | 1 | 1756-IB32 | FS-40204_DI_1 | Pin 1 | C2S1:1/TBDI1:1A | DI | 24VDC Dry Contact | ACTIVE | JB-402 | Jet Cooker 2nd Floor | C2S01-X1 | - | FS-40204 | Flow Switch | 325-01-402-PD-01

C2-S01-P01 | 1 | 2 | 1756-IB32 | FS-40205_DI_1 | Pin 2 | C2S1:2/TBDI1:2A | DI | 24VDC Dry Contact | ACTIVE | JB-402 | Jet Cooker 2nd Floor | C2S01-X1 | - | FS-40205 | Flow Switch | 325-01-402-PD-02

C2-S01-P02 | 2 | 3 | 1756-IB32 | FT-40221_DI_1 | Pin 3 | C2S1:3/TBDI1:3A | DI | 24VDC Dry Contact | ACTIVE | JB-402 | Jet Cooker 2nd Floor | C2S01-X1 | - | FT-40221 | Coriolis Flow Transmitter | 325-01-402-PD-02

C2-S01-P03 | 3 | 4 | 1756-IB32 | FT-40222_DI_1 | Pin 4 | C2S1:4/TBDI1:4A | DI | 24VDC Dry Contact | ACTIVE | JB-402 | Jet Cooker 2nd Floor | C2S01-X1 | - | FT-40222 | Coriolis Flow Transmitter | 325-01-402-PD-02

C2-S01-P04 | 4 | 5 | 1756-IB32 | HV-40207_DI_1 | Pin 5 | C2S1:5/TBDI1:5A | DI | 24VDC Dry Contact | ACTIVE | JB-402 | Jet Cooker 2nd Floor | C2S01-X1 | - | HV-40207 | Manual Valve With Position Switch | 325-01-402-PD-01

C2-S01-P05 | 5 | 6 | 1756-IB32 | HV-40208_DI_1 | Pin 6 | C2S1:6/TBDI1:6A | DI | 24VDC Dry Contact | ACTIVE | JB-402 | Jet Cooker 2nd Floor | C2S01-X1 | - | HV-40208 | Manual Valve With Position Switch | 325-01-402-PD-01

C2-S01-P06 | 6 | 7 | 1756-IB32 | XV-40203F_DI_1 | Pin 7 | C2S1:7/TBDI1:7A | DI | 24VDC Dry Contact | ACTIVE | JB-402 | Jet Cooker 2nd Floor | C2S01-X1 | - | XV-40203F | | 325-01-402-PD-02

C2-S01-P07 | 7 | 8 | 1756-IB32 | XV-40203F_DI_2 | Pin 8 | C2S1:8/TBDI1:8A | DI | 24VDC Dry Contact | ACTIVE | JB-402 | Jet Cooker 2nd Floor | C2S01-X1 | - | XV-40203F | | 325-01-402-PD-02

C2-S01-P08 | 8 | 9 | 1756-IB32 | XV-40204B_DI_1 | Pin 9 | C2S1:9/TBDI1:9A | DI | 24VDC Dry Contact | ACTIVE | JB-402 | Jet Cooker 2nd Floor | C2S01-X1 | - | XV-40204B | | 325-01-402-PD-01

C2-S01-P09 | 9 | 10 | 1756-IB32 | XV-40204B_DI_2 | Pin 10 | C2S1:10/TBDI1:10A | DI | 24VDC Dry Contact | ACTIVE | JB-402 | Jet Cooker 2nd Floor | C2S01-X1 | - | XV-40204B | | 325-01-402-PD-01

C2-S01-P10 | 10 | 11 | 1756-IB32 | XV-40204C_DI_1 | Pin 11 | C2S1:11/TBDI1:11A | DI | 24VDC Dry Contact | ACTIVE | JB-402 | Jet Cooker 2nd Floor | C2S01-X1 | - | XV-40204C | | 325-01-402-PD-01

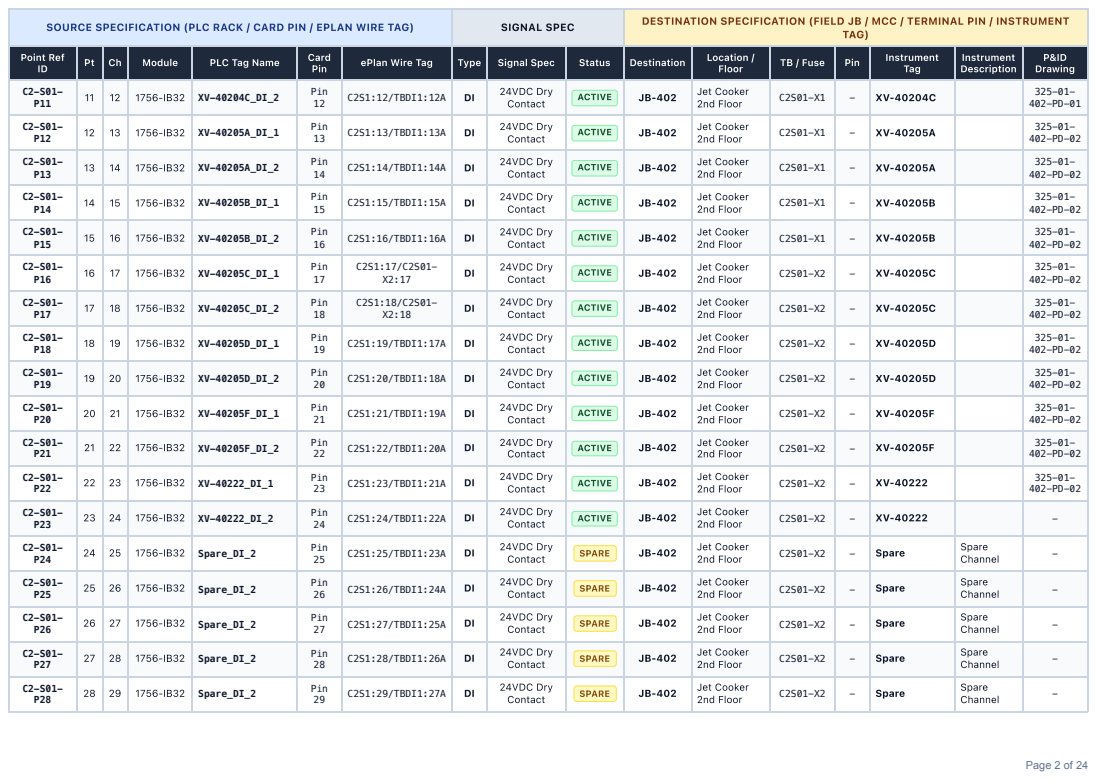
[picture p151: page 2]
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

C2-S01-P11 | 11 | 12 | 1756-IB32 | XV-40204C_DI_2 | Pin 12 | C2S1:12/TBDI1:12A | DI | 24VDC Dry Contact | ACTIVE | JB-402 | Jet Cooker 2nd Floor | C2S01-X1 | - | XV-40204C | | 325-01-402-PD-01

C2-S01-P12 | 12 | 13 | 1756-IB32 | XV-40205A_DI_1 | Pin 13 | C2S1:13/TBDI1:13A | DI | 24VDC Dry Contact | ACTIVE | JB-402 | Jet Cooker 2nd Floor | C2S01-X1 | - | XV-40205A | | 325-01-402-PD-02

C2-S01-P13 | 13 | 14 | 1756-IB32 | XV-40205A_DI_2 | Pin 14 | C2S1:14/TBDI1:14A | DI | 24VDC Dry Contact | ACTIVE | JB-402 | Jet Cooker 2nd Floor | C2S01-X1 | - | XV-40205A | | 325-01-402-PD-02

C2-S01-P14 | 14 | 15 | 1756-IB32 | XV-40205B_DI_1 | Pin 15 | C2S1:15/TBDI1:15A | DI | 24VDC Dry Contact | ACTIVE | JB-402 | Jet Cooker 2nd Floor | C2S01-X1 | - | XV-40205B | | 325-01-402-PD-02

C2-S01-P15 | 15 | 16 | 1756-IB32 | XV-40205B_DI_2 | Pin 16 | C2S1:16/TBDI1:16A | DI | 24VDC Dry Contact | ACTIVE | JB-402 | Jet Cooker 2nd Floor | C2S01-X1 | - | XV-40205B | | 325-01-402-PD-02

C2-S01-P16 | 16 | 17 | 1756-IB32 | XV-40205C_DI_1 | Pin 17 | C2S1:17/C2S01-X2:17 | DI | 24VDC Dry Contact | ACTIVE | JB-402 | Jet Cooker 2nd Floor | C2S01-X2 | - | XV-40205C | | 325-01-402-PD-02

C2-S01-P17 | 17 | 18 | 1756-IB32 | XV-40205C_DI_2 | Pin 18 | C2S1:18/C2S01-X2:18 | DI | 24VDC Dry Contact | ACTIVE | JB-402 | Jet Cooker 2nd Floor | C2S01-X2 | - | XV-40205C | | 325-01-402-PD-02

C2-S01-P18 | 18 | 19 | 1756-IB32 | XV-40205D_DI_1 | Pin 19 | C2S1:19/TBDI1:17A | DI | 24VDC Dry Contact | ACTIVE | JB-402 | Jet Cooker 2nd Floor | C2S01-X2 | - | XV-40205D | | 325-01-402-PD-02

C2-S01-P19 | 19 | 20 | 1756-IB32 | XV-40205D_DI_2 | Pin 20 | C2S1:20/TBDI1:18A | DI | 24VDC Dry Contact | ACTIVE | JB-402 | Jet Cooker 2nd Floor | C2S01-X2 | - | XV-40205D | | 325-01-402-PD-02

C2-S01-P20 | 20 | 21 | 1756-IB32 | XV-40205F_DI_1 | Pin 21 | C2S1:21/TBDI1:19A | DI | 24VDC Dry Contact | ACTIVE | JB-402 | Jet Cooker 2nd Floor | C2S01-X2 | - | XV-40205F | | 325-01-402-PD-02

C2-S01-P21 | 21 | 22 | 1756-IB32 | XV-40205F_DI_2 | Pin 22 | C2S1:22/TBDI1:20A | DI | 24VDC Dry Contact | ACTIVE | JB-402 | Jet Cooker 2nd Floor | C2S01-X2 | - | XV-40205F | | 325-01-402-PD-02

C2-S01-P22 | 22 | 23 | 1756-IB32 | XV-40222_DI_1 | Pin 23 | C2S1:23/TBDI1:21A | DI | 24VDC Dry Contact | ACTIVE | JB-402 | Jet Cooker 2nd Floor | C2S01-X2 | - | XV-40222 | | 325-01-402-PD-02

C2-S01-P23 | 23 | 24 | 1756-IB32 | XV-40222_DI_2 | Pin 24 | C2S1:24/TBDI1:22A | DI | 24VDC Dry Contact | ACTIVE | JB-402 | Jet Cooker 2nd Floor | C2S01-X2 | - | XV-40222 | | -

C2-S01-P24 | 24 | 25 | 1756-IB32 | Spare_DI_2 | Pin 25 | C2S1:25/TBDI1:23A | DI | 24VDC Dry Contact | SPARE | JB-402 | Jet Cooker 2nd Floor | C2S01-X2 | - | Spare | Spare Channel | -

C2-S01-P25 | 25 | 26 | 1756-IB32 | Spare_DI_2 | Pin 26 | C2S1:26/TBDI1:24A | DI | 24VDC Dry Contact | SPARE | JB-402 | Jet Cooker 2nd Floor | C2S01-X2 | - | Spare | Spare Channel | -

C2-S01-P26 | 26 | 27 | 1756-IB32 | Spare_DI_2 | Pin 27 | C2S1:27/TBDI1:25A | DI | 24VDC Dry Contact | SPARE | JB-402 | Jet Cooker 2nd Floor | C2S01-X2 | - | Spare | Spare Channel | -

C2-S01-P27 | 27 | 28 | 1756-IB32 | Spare_DI_2 | Pin 28 | C2S1:28/TBDI1:26A | DI | 24VDC Dry Contact | SPARE | JB-402 | Jet Cooker 2nd Floor | C2S01-X2 | - | Spare | Spare Channel | -

C2-S01-P28 | 28 | 29 | 1756-IB32 | Spare_DI_2 | Pin 29 | C2S1:29/TBDI1:27A | DI | 24VDC Dry Contact | SPARE | JB-402 | Jet Cooker 2nd Floor | C2S01-X2 | - | Spare | Spare Channel | -

Point Ref ID | Pt | Ch | Module | PLC Tag Name | Card Pin | ePlan Wire Tag | Type | Signal Spec | Status | Destination | Location / Floor | TB / Fuse | Pin | Instrument Tag | Instrument Description | P&ID Drawing
C2-S01-P29 | 29 | 30 | 1756-IB32 | Spare_DI_2 | Pin 30 | C2S1:30/TBDI1:28A | DI | 24VDC Dry Contact | SPARE | JB-402 | Jet Cooker 2nd Floor | C2S01-X2 | - | Spare | Spare Channel | -
C2-S01-P30 | 30 | 31 | 1756-IB32 | Spare_DI_2 | Pin 31 | C2S1:31/TBDI1:29A | DI | 24VDC Dry Contact | SPARE | JB-402 | Jet Cooker 2nd Floor | C2S01-X2 | - | Spare | Spare Channel | -
C2-S01-P31 | 31 | 32 | 1756-IB32 | Spare_DI_2 | Pin 32 | C2S1:32/TBDI1:30A | DI | 24VDC Dry Contact | SPARE | JB-402 | Jet Cooker 2nd Floor | C2S01-X2 | - | Spare | Spare Channel | -
Kalasin Engineering xCIP System — Turnkey Automated CIP Skid (Ref: x2608003) | ePlan Wire Standard: C[Chassis]S[Slot]:[Channel] / [Terminal]:[Pin] | 100% Non-ATEX Food & Beverage Sanitary Standard

## C2 SLOT 02 — 1756-IB32 (DI)

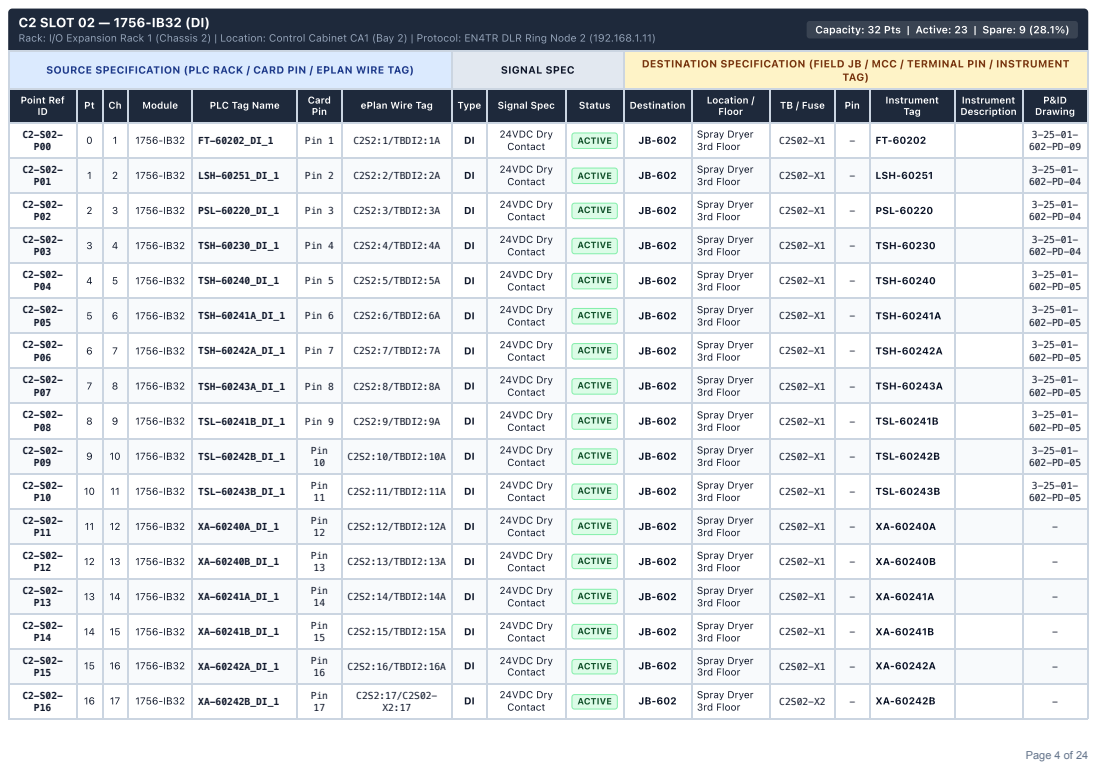
[picture p152: page 4]

Capacity: 32 Pts | Active: 23 | Spare: 9 (28.1%)

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

C2-S02-P00 | 0 | 1 | 1756-IB32 | FT-60202_DI_1 | Pin 1 | C2S2:1/TBDI2:1A | DI | 24VDC Dry Contact | ACTIVE | JB-602 | Spray Dryer 3rd Floor | C2S02-X1 | - | FT-60202 | | 3-25-01-602-PD-09

C2-S02-P01 | 1 | 2 | 1756-IB32 | LSH-60251_DI_1 | Pin 2 | C2S2:2/TBDI2:2A | DI | 24VDC Dry Contact | ACTIVE | JB-602 | Spray Dryer 3rd Floor | C2S02-X1 | - | LSH-60251 | | 3-25-01-602-PD-04

C2-S02-P02 | 2 | 3 | 1756-IB32 | PSL-60220_DI_1 | Pin 3 | C2S2:3/TBDI2:3A | DI | 24VDC Dry Contact | ACTIVE | JB-602 | Spray Dryer 3rd Floor | C2S02-X1 | - | PSL-60220 | | 3-25-01-602-PD-04

C2-S02-P03 | 3 | 4 | 1756-IB32 | TSH-60230_DI_1 | Pin 4 | C2S2:4/TBDI2:4A | DI | 24VDC Dry Contact | ACTIVE | JB-602 | Spray Dryer 3rd Floor | C2S02-X1 | - | TSH-60230 | | 3-25-01-602-PD-04

C2-S02-P04 | 4 | 5 | 1756-IB32 | TSH-60240_DI_1 | Pin 5 | C2S2:5/TBDI2:5A | DI | 24VDC Dry Contact | ACTIVE | JB-602 | Spray Dryer 3rd Floor | C2S02-X1 | - | TSH-60240 | | 3-25-01-602-PD-05

C2-S02-P05 | 5 | 6 | 1756-IB32 | TSH-60241A_DI_1 | Pin 6 | C2S2:6/TBDI2:6A | DI | 24VDC Dry Contact | ACTIVE | JB-602 | Spray Dryer 3rd Floor | C2S02-X1 | - | TSH-60241A | | 3-25-01-602-PD-05

C2-S02-P06 | 6 | 7 | 1756-IB32 | TSH-60242A_DI_1 | Pin 7 | C2S2:7/TBDI2:7A | DI | 24VDC Dry Contact | ACTIVE | JB-602 | Spray Dryer 3rd Floor | C2S02-X1 | - | TSH-60242A | | 3-25-01-602-PD-05

C2-S02-P07 | 7 | 8 | 1756-IB32 | TSH-60243A_DI_1 | Pin 8 | C2S2:8/TBDI2:8A | DI | 24VDC Dry Contact | ACTIVE | JB-602 | Spray Dryer 3rd Floor | C2S02-X1 | - | TSH-60243A | | 3-25-01-602-PD-05

C2-S02-P08 | 8 | 9 | 1756-IB32 | TSL-60241B_DI_1 | Pin 9 | C2S2:9/TBDI2:9A | DI | 24VDC Dry Contact | ACTIVE | JB-602 | Spray Dryer 3rd Floor | C2S02-X1 | - | TSL-60241B | | 3-25-01-602-PD-05

C2-S02-P09 | 9 | 10 | 1756-IB32 | TSL-60242B_DI_1 | Pin 10 | C2S2:10/TBDI2:10A | DI | 24VDC Dry Contact | ACTIVE | JB-602 | Spray Dryer 3rd Floor | C2S02-X1 | - | TSL-60242B | | 3-25-01-602-PD-05

C2-S02-P10 | 10 | 11 | 1756-IB32 | TSL-60243B_DI_1 | Pin 11 | C2S2:11/TBDI2:11A | DI | 24VDC Dry Contact | ACTIVE | JB-602 | Spray Dryer 3rd Floor | C2S02-X1 | - | TSL-60243B | | 3-25-01-602-PD-05

C2-S02-P11 | 11 | 12 | 1756-IB32 | XA-60240A_DI_1 | Pin 12 | C2S2:12/TBDI2:12A | DI | 24VDC Dry Contact | ACTIVE | JB-602 | Spray Dryer 3rd Floor | C2S02-X1 | - | XA-60240A | | -

C2-S02-P12 | 12 | 13 | 1756-IB32 | XA-60240B_DI_1 | Pin 13 | C2S2:13/TBDI2:13A | DI | 24VDC Dry Contact | ACTIVE | JB-602 | Spray Dryer 3rd Floor | C2S02-X1 | - | XA-60240B | | -

C2-S02-P13 | 13 | 14 | 1756-IB32 | XA-60241A_DI_1 | Pin 14 | C2S2:14/TBDI2:14A | DI | 24VDC Dry Contact | ACTIVE | JB-602 | Spray Dryer 3rd Floor | C2S02-X1 | - | XA-60241A | | -

C2-S02-P14 | 14 | 15 | 1756-IB32 | XA-60241B_DI_1 | Pin 15 | C2S2:15/TBDI2:15A | DI | 24VDC Dry Contact | ACTIVE | JB-602 | Spray Dryer 3rd Floor | C2S02-X1 | - | XA-60241B | | -

C2-S02-P15 | 15 | 16 | 1756-IB32 | XA-60242A_DI_1 | Pin 16 | C2S2:16/TBDI2:16A | DI | 24VDC Dry Contact | ACTIVE | JB-602 | Spray Dryer 3rd Floor | C2S02-X1 | - | XA-60242A | | -

C2-S02-P16 | 16 | 17 | 1756-IB32 | XA-60242B_DI_1 | Pin 17 | C2S2:17/C2S02-X2:17 | DI | 24VDC Dry Contact | ACTIVE | JB-602 | Spray Dryer 3rd Floor | C2S02-X2 | - | XA-60242B | | -

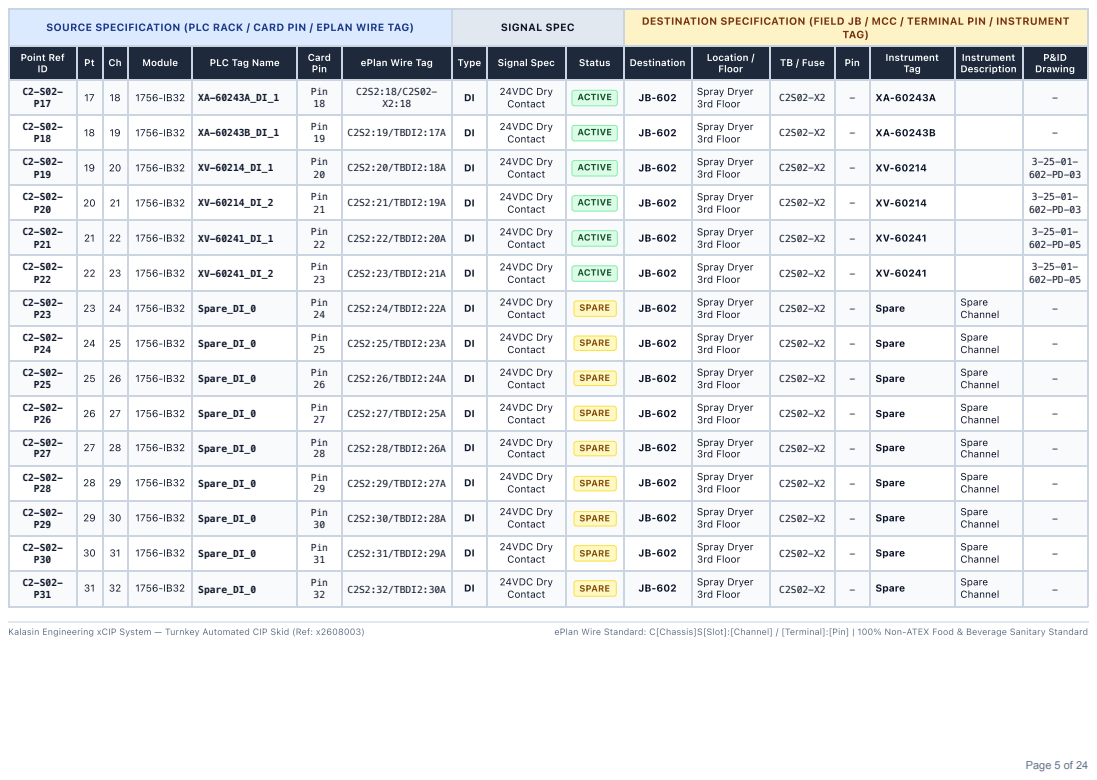
[picture p153: page 5]
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

C2-S02-P17 | 17 | 18 | 1756-IB32 | XA-60243A_DI_1 | Pin 18 | C2S2:18/C2S02-X2:18 | DI | 24VDC Dry Contact | ACTIVE | JB-602 | Spray Dryer 3rd Floor | C2S02-X2 | - | XA-60243A | | -

C2-S02-P18 | 18 | 19 | 1756-IB32 | XA-60243B_DI_1 | Pin 19 | C2S2:19/TBDI2:17A | DI | 24VDC Dry Contact | ACTIVE | JB-602 | Spray Dryer 3rd Floor | C2S02-X2 | - | XA-60243B | | -

C2-S02-P19 | 19 | 20 | 1756-IB32 | XV-60214_DI_1 | Pin 20 | C2S2:20/TBDI2:18A | DI | 24VDC Dry Contact | ACTIVE | JB-602 | Spray Dryer 3rd Floor | C2S02-X2 | - | XV-60214 | | 3-25-01-602-PD-03

C2-S02-P20 | 20 | 21 | 1756-IB32 | XV-60214_DI_2 | Pin 21 | C2S2:21/TBDI2:19A | DI | 24VDC Dry Contact | ACTIVE | JB-602 | Spray Dryer 3rd Floor | C2S02-X2 | - | XV-60214 | | 3-25-01-602-PD-03

C2-S02-P21 | 21 | 22 | 1756-IB32 | XV-60241_DI_1 | Pin 22 | C2S2:22/TBDI2:20A | DI | 24VDC Dry Contact | ACTIVE | JB-602 | Spray Dryer 3rd Floor | C2S02-X2 | - | XV-60241 | | 3-25-01-602-PD-05

C2-S02-P22 | 22 | 23 | 1756-IB32 | XV-60241_DI_2 | Pin 23 | C2S2:23/TBDI2:21A | DI | 24VDC Dry Contact | ACTIVE | JB-602 | Spray Dryer 3rd Floor | C2S02-X2 | - | XV-60241 | | 3-25-01-602-PD-05

C2-S02-P23 | 23 | 24 | 1756-IB32 | Spare_DI_0 | Pin 24 | C2S2:24/TBDI2:22A | DI | 24VDC Dry Contact | SPARE | JB-602 | Spray Dryer 3rd Floor | C2S02-X2 | - | Spare | Spare Channel | -

C2-S02-P24 | 24 | 25 | 1756-IB32 | Spare_DI_0 | Pin 25 | C2S2:25/TBDI2:23A | DI | 24VDC Dry Contact | SPARE | JB-602 | Spray Dryer 3rd Floor | C2S02-X2 | - | Spare | Spare Channel | -

C2-S02-P25 | 25 | 26 | 1756-IB32 | Spare_DI_0 | Pin 26 | C2S2:26/TBDI2:24A | DI | 24VDC Dry Contact | SPARE | JB-602 | Spray Dryer 3rd Floor | C2S02-X2 | - | Spare | Spare Channel | -

C2-S02-P26 | 26 | 27 | 1756-IB32 | Spare_DI_0 | Pin 27 | C2S2:27/TBDI2:25A | DI | 24VDC Dry Contact | SPARE | JB-602 | Spray Dryer 3rd Floor | C2S02-X2 | - | Spare | Spare Channel | -

C2-S02-P27 | 27 | 28 | 1756-IB32 | Spare_DI_0 | Pin 28 | C2S2:28/TBDI2:26A | DI | 24VDC Dry Contact | SPARE | JB-602 | Spray Dryer 3rd Floor | C2S02-X2 | - | Spare | Spare Channel | -

C2-S02-P28 | 28 | 29 | 1756-IB32 | Spare_DI_0 | Pin 29 | C2S2:29/TBDI2:27A | DI | 24VDC Dry Contact | SPARE | JB-602 | Spray Dryer 3rd Floor | C2S02-X2 | - | Spare | Spare Channel | -

C2-S02-P29 | 29 | 30 | 1756-IB32 | Spare_DI_0 | Pin 30 | C2S2:30/TBDI2:28A | DI | 24VDC Dry Contact | SPARE | JB-602 | Spray Dryer 3rd Floor | C2S02-X2 | - | Spare | Spare Channel | -

C2-S02-P30 | 30 | 31 | 1756-IB32 | Spare_DI_0 | Pin 31 | C2S2:31/TBDI2:29A | DI | 24VDC Dry Contact | SPARE | JB-602 | Spray Dryer 3rd Floor | C2S02-X2 | - | Spare | Spare Channel | -

C2-S02-P31 | 31 | 32 | 1756-IB32 | Spare_DI_0 | Pin 32 | C2S2:32/TBDI2:30A | DI | 24VDC Dry Contact | SPARE | JB-602 | Spray Dryer 3rd Floor | C2S02-X2 | - | Spare | Spare Channel | -

## C2 SLOT 03 — 1756-IB32 (DI)

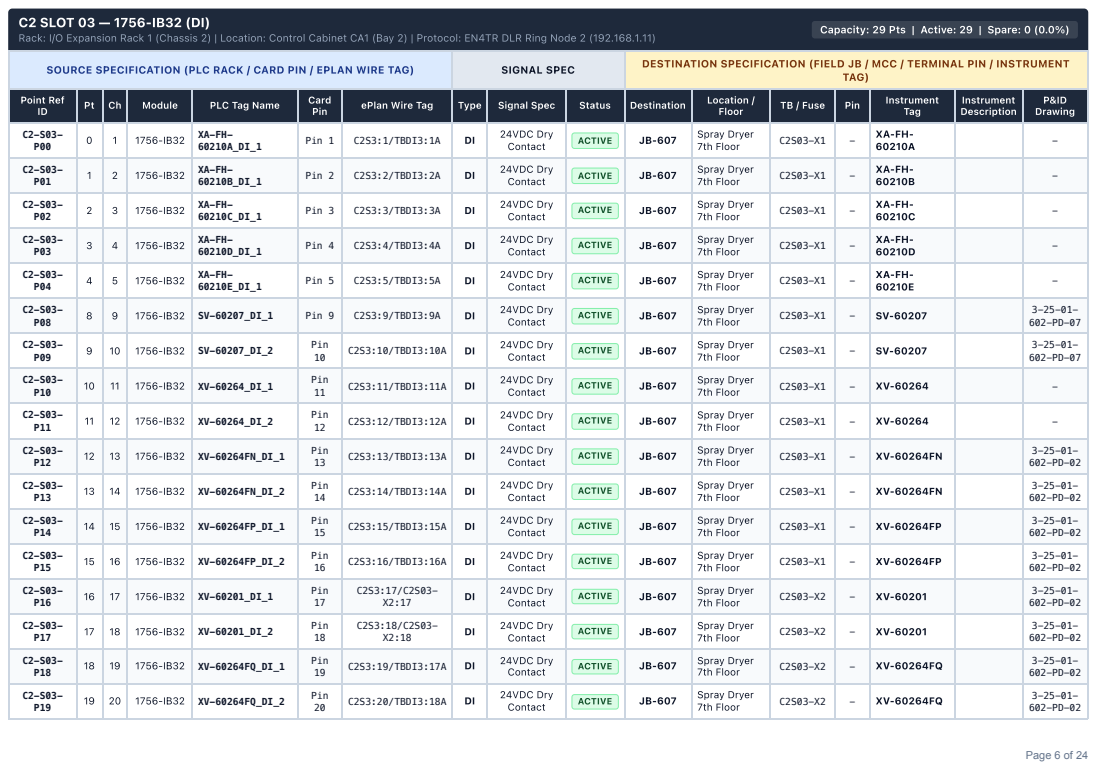
[picture p154: page 6]

Capacity: 29 Pts | Active: 29 | Spare: 0 (0.0%)

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

C2-S03-P00 | 0 | 1 | 1756-IB32 | XA-FH-60210A_DI_1 | Pin 1 | C2S3:1/TBDI3:1A | DI | 24VDC Dry Contact | ACTIVE | JB-607 | Spray Dryer 7th Floor | C2S03-X1 | - | XA-FH-60210A | | -

C2-S03-P01 | 1 | 2 | 1756-IB32 | XA-FH-60210B_DI_1 | Pin 2 | C2S3:2/TBDI3:2A | DI | 24VDC Dry Contact | ACTIVE | JB-607 | Spray Dryer 7th Floor | C2S03-X1 | - | XA-FH-60210B | | -

C2-S03-P02 | 2 | 3 | 1756-IB32 | XA-FH-60210C_DI_1 | Pin 3 | C2S3:3/TBDI3:3A | DI | 24VDC Dry Contact | ACTIVE | JB-607 | Spray Dryer 7th Floor | C2S03-X1 | - | XA-FH-60210C | | -

C2-S03-P03 | 3 | 4 | 1756-IB32 | XA-FH-60210D_DI_1 | Pin 4 | C2S3:4/TBDI3:4A | DI | 24VDC Dry Contact | ACTIVE | JB-607 | Spray Dryer 7th Floor | C2S03-X1 | - | XA-FH-60210D | | -

C2-S03-P04 | 4 | 5 | 1756-IB32 | XA-FH-60210E_DI_1 | Pin 5 | C2S3:5/TBDI3:5A | DI | 24VDC Dry Contact | ACTIVE | JB-607 | Spray Dryer 7th Floor | C2S03-X1 | - | XA-FH-60210E | | -

C2-S03-P08 | 8 | 9 | 1756-IB32 | SV-60207_DI_1 | Pin 9 | C2S3:9/TBDI3:9A | DI | 24VDC Dry Contact | ACTIVE | JB-607 | Spray Dryer 7th Floor | C2S03-X1 | - | SV-60207 | | 3-25-01-602-PD-07

C2-S03-P09 | 9 | 10 | 1756-IB32 | SV-60207_DI_2 | Pin 10 | C2S3:10/TBDI3:10A | DI | 24VDC Dry Contact | ACTIVE | JB-607 | Spray Dryer 7th Floor | C2S03-X1 | - | SV-60207 | | 3-25-01-602-PD-07

C2-S03-P10 | 10 | 11 | 1756-IB32 | XV-60264_DI_1 | Pin 11 | C2S3:11/TBDI3:11A | DI | 24VDC Dry Contact | ACTIVE | JB-607 | Spray Dryer 7th Floor | C2S03-X1 | - | XV-60264 | | -

C2-S03-P11 | 11 | 12 | 1756-IB32 | XV-60264_DI_2 | Pin 12 | C2S3:12/TBDI3:12A | DI | 24VDC Dry Contact | ACTIVE | JB-607 | Spray Dryer 7th Floor | C2S03-X1 | - | XV-60264 | | -

C2-S03-P12 | 12 | 13 | 1756-IB32 | XV-60264FN_DI_1 | Pin 13 | C2S3:13/TBDI3:13A | DI | 24VDC Dry Contact | ACTIVE | JB-607 | Spray Dryer 7th Floor | C2S03-X1 | - | XV-60264FN | | 3-25-01-602-PD-02

C2-S03-P13 | 13 | 14 | 1756-IB32 | XV-60264FN_DI_2 | Pin 14 | C2S3:14/TBDI3:14A | DI | 24VDC Dry Contact | ACTIVE | JB-607 | Spray Dryer 7th Floor | C2S03-X1 | - | XV-60264FN | | 3-25-01-602-PD-02

C2-S03-P14 | 14 | 15 | 1756-IB32 | XV-60264FP_DI_1 | Pin 15 | C2S3:15/TBDI3:15A | DI | 24VDC Dry Contact | ACTIVE | JB-607 | Spray Dryer 7th Floor | C2S03-X1 | - | XV-60264FP | | 3-25-01-602-PD-02

C2-S03-P15 | 15 | 16 | 1756-IB32 | XV-60264FP_DI_2 | Pin 16 | C2S3:16/TBDI3:16A | DI | 24VDC Dry Contact | ACTIVE | JB-607 | Spray Dryer 7th Floor | C2S03-X1 | - | XV-60264FP | | 3-25-01-602-PD-02

C2-S03-P16 | 16 | 17 | 1756-IB32 | XV-60201_DI_1 | Pin 17 | C2S3:17/C2S03-X2:17 | DI | 24VDC Dry Contact | ACTIVE | JB-607 | Spray Dryer 7th Floor | C2S03-X2 | - | XV-60201 | | 3-25-01-602-PD-02

C2-S03-P17 | 17 | 18 | 1756-IB32 | XV-60201_DI_2 | Pin 18 | C2S3:18/C2S03-X2:18 | DI | 24VDC Dry Contact | ACTIVE | JB-607 | Spray Dryer 7th Floor | C2S03-X2 | - | XV-60201 | | 3-25-01-602-PD-02

C2-S03-P18 | 18 | 19 | 1756-IB32 | XV-60264FQ_DI_1 | Pin 19 | C2S3:19/TBDI3:17A | DI | 24VDC Dry Contact | ACTIVE | JB-607 | Spray Dryer 7th Floor | C2S03-X2 | - | XV-60264FQ | | 3-25-01-602-PD-02

C2-S03-P19 | 19 | 20 | 1756-IB32 | XV-60264FQ_DI_2 | Pin 20 | C2S3:20/TBDI3:18A | DI | 24VDC Dry Contact | ACTIVE | JB-607 | Spray Dryer 7th Floor | C2S03-X2 | - | XV-60264FQ | | 3-25-01-602-PD-02

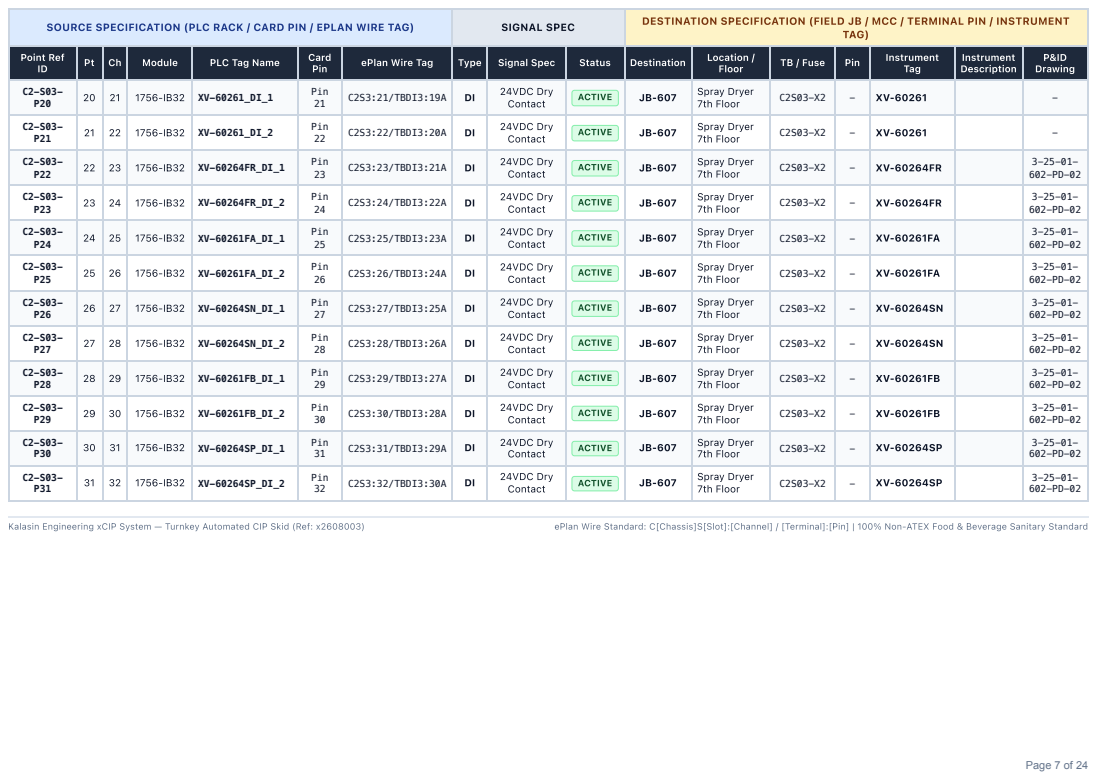
[picture p155: page 7]
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

C2-S03-P20 | 20 | 21 | 1756-IB32 | XV-60261_DI_1 | Pin 21 | C2S3:21/TBDI3:19A | DI | 24VDC Dry Contact | ACTIVE | JB-607 | Spray Dryer 7th Floor | C2S03-X2 | - | XV-60261 | | -

C2-S03-P21 | 21 | 22 | 1756-IB32 | XV-60261_DI_2 | Pin 22 | C2S3:22/TBDI3:20A | DI | 24VDC Dry Contact | ACTIVE | JB-607 | Spray Dryer 7th Floor | C2S03-X2 | - | XV-60261 | | -

C2-S03-P22 | 22 | 23 | 1756-IB32 | XV-60264FR_DI_1 | Pin 23 | C2S3:23/TBDI3:21A | DI | 24VDC Dry Contact | ACTIVE | JB-607 | Spray Dryer 7th Floor | C2S03-X2 | - | XV-60264FR | | 3-25-01-602-PD-02

C2-S03-P23 | 23 | 24 | 1756-IB32 | XV-60264FR_DI_2 | Pin 24 | C2S3:24/TBDI3:22A | DI | 24VDC Dry Contact | ACTIVE | JB-607 | Spray Dryer 7th Floor | C2S03-X2 | - | XV-60264FR | | 3-25-01-602-PD-02

C2-S03-P24 | 24 | 25 | 1756-IB32 | XV-60261FA_DI_1 | Pin 25 | C2S3:25/TBDI3:23A | DI | 24VDC Dry Contact | ACTIVE | JB-607 | Spray Dryer 7th Floor | C2S03-X2 | - | XV-60261FA | | 3-25-01-602-PD-02

C2-S03-P25 | 25 | 26 | 1756-IB32 | XV-60261FA_DI_2 | Pin 26 | C2S3:26/TBDI3:24A | DI | 24VDC Dry Contact | ACTIVE | JB-607 | Spray Dryer 7th Floor | C2S03-X2 | - | XV-60261FA | | 3-25-01-602-PD-02

C2-S03-P26 | 26 | 27 | 1756-IB32 | XV-60264SN_DI_1 | Pin 27 | C2S3:27/TBDI3:25A | DI | 24VDC Dry Contact | ACTIVE | JB-607 | Spray Dryer 7th Floor | C2S03-X2 | - | XV-60264SN | | 3-25-01-602-PD-02

C2-S03-P27 | 27 | 28 | 1756-IB32 | XV-60264SN_DI_2 | Pin 28 | C2S3:28/TBDI3:26A | DI | 24VDC Dry Contact | ACTIVE | JB-607 | Spray Dryer 7th Floor | C2S03-X2 | - | XV-60264SN | | 3-25-01-602-PD-02

C2-S03-P28 | 28 | 29 | 1756-IB32 | XV-60261FB_DI_1 | Pin 29 | C2S3:29/TBDI3:27A | DI | 24VDC Dry Contact | ACTIVE | JB-607 | Spray Dryer 7th Floor | C2S03-X2 | - | XV-60261FB | | 3-25-01-602-PD-02

C2-S03-P29 | 29 | 30 | 1756-IB32 | XV-60261FB_DI_2 | Pin 30 | C2S3:30/TBDI3:28A | DI | 24VDC Dry Contact | ACTIVE | JB-607 | Spray Dryer 7th Floor | C2S03-X2 | - | XV-60261FB | | 3-25-01-602-PD-02

C2-S03-P30 | 30 | 31 | 1756-IB32 | XV-60264SP_DI_1 | Pin 31 | C2S3:31/TBDI3:29A | DI | 24VDC Dry Contact | ACTIVE | JB-607 | Spray Dryer 7th Floor | C2S03-X2 | - | XV-60264SP | | 3-25-01-602-PD-02

C2-S03-P31 | 31 | 32 | 1756-IB32 | XV-60264SP_DI_2 | Pin 32 | C2S3:32/TBDI3:30A | DI | 24VDC Dry Contact | ACTIVE | JB-607 | Spray Dryer 7th Floor | C2S03-X2 | - | XV-60264SP | | 3-25-01-602-PD-02

## C2 SLOT 04 — 1756-IB32 (DI)

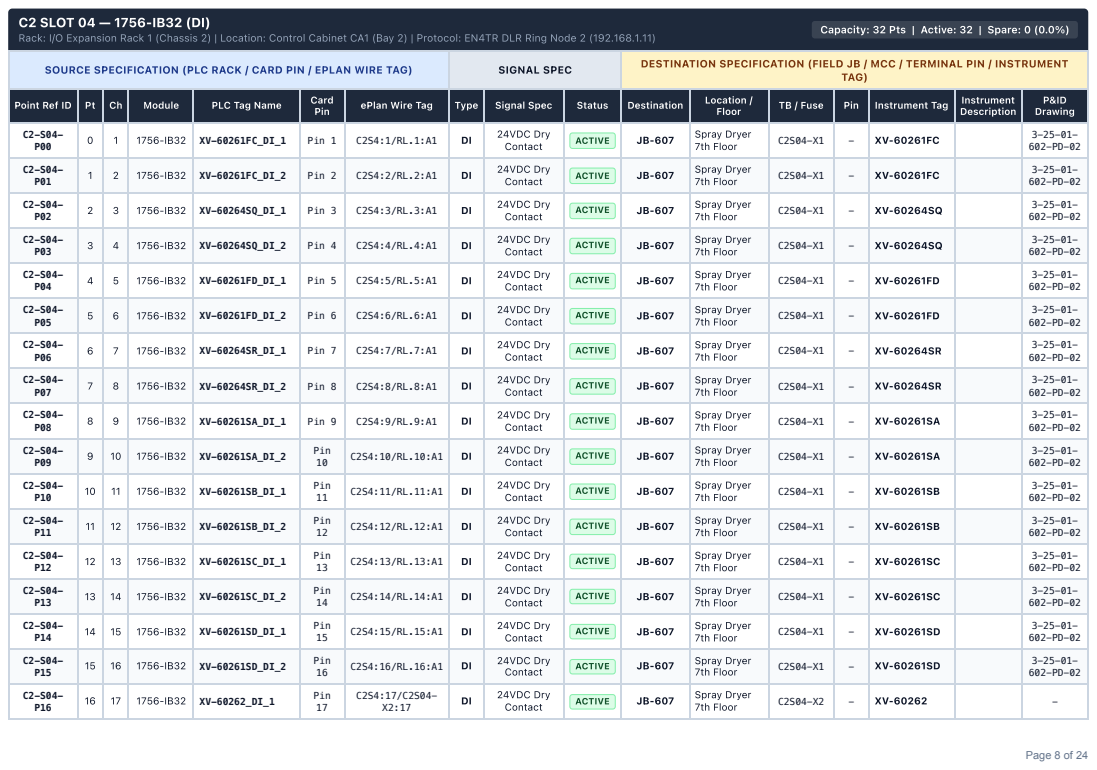
[picture p156: page 8]

Capacity: 32 Pts | Active: 32 | Spare: 0 (0.0%)

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

C2-S04-P00 | 0 | 1 | 1756-IB32 | XV-60261FC_DI_1 | Pin 1 | C2S4:1/RL.1:A1 | DI | 24VDC Dry Contact | ACTIVE | JB-607 | Spray Dryer 7th Floor | C2S04-X1 | - | XV-60261FC | | 3-25-01-602-PD-02

C2-S04-P01 | 1 | 2 | 1756-IB32 | XV-60261FC_DI_2 | Pin 2 | C2S4:2/RL.2:A1 | DI | 24VDC Dry Contact | ACTIVE | JB-607 | Spray Dryer 7th Floor | C2S04-X1 | - | XV-60261FC | | 3-25-01-602-PD-02

C2-S04-P02 | 2 | 3 | 1756-IB32 | XV-60264SQ_DI_1 | Pin 3 | C2S4:3/RL.3:A1 | DI | 24VDC Dry Contact | ACTIVE | JB-607 | Spray Dryer 7th Floor | C2S04-X1 | - | XV-60264SQ | | 3-25-01-602-PD-02

C2-S04-P03 | 3 | 4 | 1756-IB32 | XV-60264SQ_DI_2 | Pin 4 | C2S4:4/RL.4:A1 | DI | 24VDC Dry Contact | ACTIVE | JB-607 | Spray Dryer 7th Floor | C2S04-X1 | - | XV-60264SQ | | 3-25-01-602-PD-02

C2-S04-P04 | 4 | 5 | 1756-IB32 | XV-60261FD_DI_1 | Pin 5 | C2S4:5/RL.5:A1 | DI | 24VDC Dry Contact | ACTIVE | JB-607 | Spray Dryer 7th Floor | C2S04-X1 | - | XV-60261FD | | 3-25-01-602-PD-02

C2-S04-P05 | 5 | 6 | 1756-IB32 | XV-60261FD_DI_2 | Pin 6 | C2S4:6/RL.6:A1 | DI | 24VDC Dry Contact | ACTIVE | JB-607 | Spray Dryer 7th Floor | C2S04-X1 | - | XV-60261FD | | 3-25-01-602-PD-02

C2-S04-P06 | 6 | 7 | 1756-IB32 | XV-60264SR_DI_1 | Pin 7 | C2S4:7/RL.7:A1 | DI | 24VDC Dry Contact | ACTIVE | JB-607 | Spray Dryer 7th Floor | C2S04-X1 | - | XV-60264SR | | 3-25-01-602-PD-02

C2-S04-P07 | 7 | 8 | 1756-IB32 | XV-60264SR_DI_2 | Pin 8 | C2S4:8/RL.8:A1 | DI | 24VDC Dry Contact | ACTIVE | JB-607 | Spray Dryer 7th Floor | C2S04-X1 | - | XV-60264SR | | 3-25-01-602-PD-02

C2-S04-P08 | 8 | 9 | 1756-IB32 | XV-60261SA_DI_1 | Pin 9 | C2S4:9/RL.9:A1 | DI | 24VDC Dry Contact | ACTIVE | JB-607 | Spray Dryer 7th Floor | C2S04-X1 | - | XV-60261SA | | 3-25-01-602-PD-02

C2-S04-P09 | 9 | 10 | 1756-IB32 | XV-60261SA_DI_2 | Pin 10 | C2S4:10/RL.10:A1 | DI | 24VDC Dry Contact | ACTIVE | JB-607 | Spray Dryer 7th Floor | C2S04-X1 | - | XV-60261SA | | 3-25-01-602-PD-02

C2-S04-P10 | 10 | 11 | 1756-IB32 | XV-60261SB_DI_1 | Pin 11 | C2S4:11/RL.11:A1 | DI | 24VDC Dry Contact | ACTIVE | JB-607 | Spray Dryer 7th Floor | C2S04-X1 | - | XV-60261SB | | 3-25-01-602-PD-02

C2-S04-P11 | 11 | 12 | 1756-IB32 | XV-60261SB_DI_2 | Pin 12 | C2S4:12/RL.12:A1 | DI | 24VDC Dry Contact | ACTIVE | JB-607 | Spray Dryer 7th Floor | C2S04-X1 | - | XV-60261SB | | 3-25-01-602-PD-02

C2-S04-P12 | 12 | 13 | 1756-IB32 | XV-60261SC_DI_1 | Pin 13 | C2S4:13/RL.13:A1 | DI | 24VDC Dry Contact | ACTIVE | JB-607 | Spray Dryer 7th Floor | C2S04-X1 | - | XV-60261SC | | 3-25-01-602-PD-02

C2-S04-P13 | 13 | 14 | 1756-IB32 | XV-60261SC_DI_2 | Pin 14 | C2S4:14/RL.14:A1 | DI | 24VDC Dry Contact | ACTIVE | JB-607 | Spray Dryer 7th Floor | C2S04-X1 | - | XV-60261SC | | 3-25-01-602-PD-02

C2-S04-P14 | 14 | 15 | 1756-IB32 | XV-60261SD_DI_1 | Pin 15 | C2S4:15/RL.15:A1 | DI | 24VDC Dry Contact | ACTIVE | JB-607 | Spray Dryer 7th Floor | C2S04-X1 | - | XV-60261SD | | 3-25-01-602-PD-02

C2-S04-P15 | 15 | 16 | 1756-IB32 | XV-60261SD_DI_2 | Pin 16 | C2S4:16/RL.16:A1 | DI | 24VDC Dry Contact | ACTIVE | JB-607 | Spray Dryer 7th Floor | C2S04-X1 | - | XV-60261SD | | 3-25-01-602-PD-02

C2-S04-P16 | 16 | 17 | 1756-IB32 | XV-60262_DI_1 | Pin 17 | C2S4:17/C2S04-X2:17 | DI | 24VDC Dry Contact | ACTIVE | JB-607 | Spray Dryer 7th Floor | C2S04-X2 | - | XV-60262 | | -

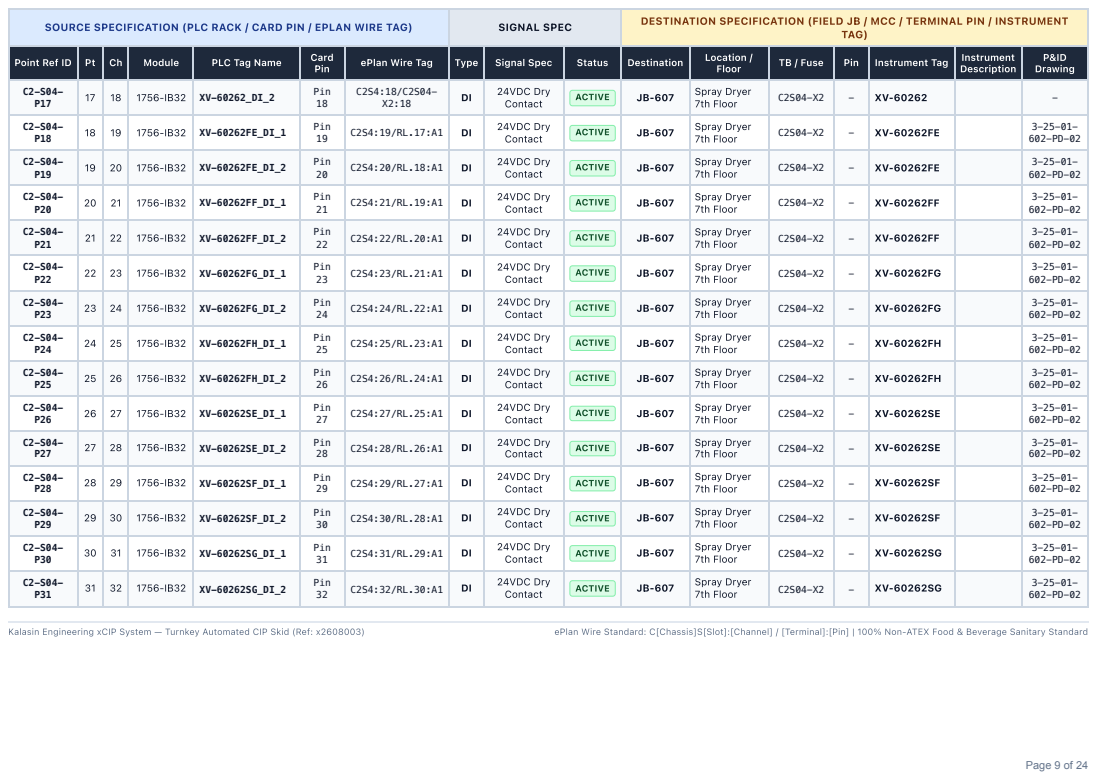
[picture p157: page 9]
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

C2-S04-P17 | 17 | 18 | 1756-IB32 | XV-60262_DI_2 | Pin 18 | C2S4:18/C2S04-X2:18 | DI | 24VDC Dry Contact | ACTIVE | JB-607 | Spray Dryer 7th Floor | C2S04-X2 | - | XV-60262 | | -

C2-S04-P18 | 18 | 19 | 1756-IB32 | XV-60262FE_DI_1 | Pin 19 | C2S4:19/RL.17:A1 | DI | 24VDC Dry Contact | ACTIVE | JB-607 | Spray Dryer 7th Floor | C2S04-X2 | - | XV-60262FE | | 3-25-01-602-PD-02

C2-S04-P19 | 19 | 20 | 1756-IB32 | XV-60262FE_DI_2 | Pin 20 | C2S4:20/RL.18:A1 | DI | 24VDC Dry Contact | ACTIVE | JB-607 | Spray Dryer 7th Floor | C2S04-X2 | - | XV-60262FE | | 3-25-01-602-PD-02

C2-S04-P20 | 20 | 21 | 1756-IB32 | XV-60262FF_DI_1 | Pin 21 | C2S4:21/RL.19:A1 | DI | 24VDC Dry Contact | ACTIVE | JB-607 | Spray Dryer 7th Floor | C2S04-X2 | - | XV-60262FF | | 3-25-01-602-PD-02

C2-S04-P21 | 21 | 22 | 1756-IB32 | XV-60262FF_DI_2 | Pin 22 | C2S4:22/RL.20:A1 | DI | 24VDC Dry Contact | ACTIVE | JB-607 | Spray Dryer 7th Floor | C2S04-X2 | - | XV-60262FF | | 3-25-01-602-PD-02

C2-S04-P22 | 22 | 23 | 1756-IB32 | XV-60262FG_DI_1 | Pin 23 | C2S4:23/RL.21:A1 | DI | 24VDC Dry Contact | ACTIVE | JB-607 | Spray Dryer 7th Floor | C2S04-X2 | - | XV-60262FG | | 3-25-01-602-PD-02

C2-S04-P23 | 23 | 24 | 1756-IB32 | XV-60262FG_DI_2 | Pin 24 | C2S4:24/RL.22:A1 | DI | 24VDC Dry Contact | ACTIVE | JB-607 | Spray Dryer 7th Floor | C2S04-X2 | - | XV-60262FG | | 3-25-01-602-PD-02

C2-S04-P24 | 24 | 25 | 1756-IB32 | XV-60262FH_DI_1 | Pin 25 | C2S4:25/RL.23:A1 | DI | 24VDC Dry Contact | ACTIVE | JB-607 | Spray Dryer 7th Floor | C2S04-X2 | - | XV-60262FH | | 3-25-01-602-PD-02

C2-S04-P25 | 25 | 26 | 1756-IB32 | XV-60262FH_DI_2 | Pin 26 | C2S4:26/RL.24:A1 | DI | 24VDC Dry Contact | ACTIVE | JB-607 | Spray Dryer 7th Floor | C2S04-X2 | - | XV-60262FH | | 3-25-01-602-PD-02

C2-S04-P26 | 26 | 27 | 1756-IB32 | XV-60262SE_DI_1 | Pin 27 | C2S4:27/RL.25:A1 | DI | 24VDC Dry Contact | ACTIVE | JB-607 | Spray Dryer 7th Floor | C2S04-X2 | - | XV-60262SE | | 3-25-01-602-PD-02

C2-S04-P27 | 27 | 28 | 1756-IB32 | XV-60262SE_DI_2 | Pin 28 | C2S4:28/RL.26:A1 | DI | 24VDC Dry Contact | ACTIVE | JB-607 | Spray Dryer 7th Floor | C2S04-X2 | - | XV-60262SE | | 3-25-01-602-PD-02

C2-S04-P28 | 28 | 29 | 1756-IB32 | XV-60262SF_DI_1 | Pin 29 | C2S4:29/RL.27:A1 | DI | 24VDC Dry Contact | ACTIVE | JB-607 | Spray Dryer 7th Floor | C2S04-X2 | - | XV-60262SF | | 3-25-01-602-PD-02

C2-S04-P29 | 29 | 30 | 1756-IB32 | XV-60262SF_DI_2 | Pin 30 | C2S4:30/RL.28:A1 | DI | 24VDC Dry Contact | ACTIVE | JB-607 | Spray Dryer 7th Floor | C2S04-X2 | - | XV-60262SF | | 3-25-01-602-PD-02

C2-S04-P30 | 30 | 31 | 1756-IB32 | XV-60262SG_DI_1 | Pin 31 | C2S4:31/RL.29:A1 | DI | 24VDC Dry Contact | ACTIVE | JB-607 | Spray Dryer 7th Floor | C2S04-X2 | - | XV-60262SG | | 3-25-01-602-PD-02

C2-S04-P31 | 31 | 32 | 1756-IB32 | XV-60262SG_DI_2 | Pin 32 | C2S4:32/RL.30:A1 | DI | 24VDC Dry Contact | ACTIVE | JB-607 | Spray Dryer 7th Floor | C2S04-X2 | - | XV-60262SG | | 3-25-01-602-PD-02
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
