x92120/x260911-002-KalasinEngineering/02_Electrical_and_eDrawing/04_PDF_Reports_and_Drawings/Chassis_C3_Slots_IO_Report.pdf

# KALASIN ENGINEERING — C3(I/O EXPANSION RACK 2 (CHASSIS3))

C3

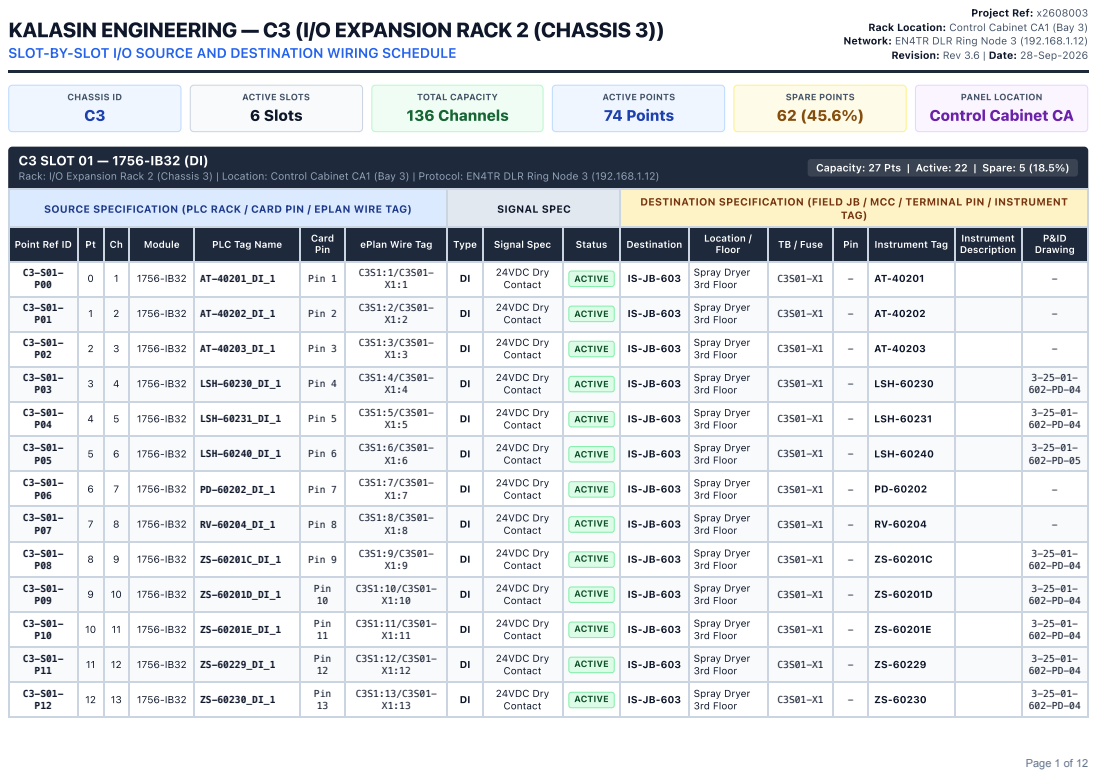
[picture p158: page 1]
Project Ref: x2608003; CHASSIS ID; ACTIVE SLOTS 6 Slots; TOTAL CAPACITY 136 Channels; ACTIVE POINTS 74 Points; SPARE POINTS 62 (45.6%)

Rack Location: Control Cabinet CA1 (Bay 3)
Network: EN4TR DLR Ring Node 3 (192.168.1.12)

SLOT-BY-SLOT I/O SOURCE AND DESTINATION WIRING SCHEDULE

Revision: Rev 3.6 | Date: 28-Sep-2026

PANEL LOCATION
Control Cabinet CA

C3 SLOT 01 — 1756-IB32 (DI)
Rack: I/O Expansion Rack 2 (Chassis 3) | Location: Control Cabinet CA1 (Bay 3) | Protocol: EN4TR DLR Ring Node 3 (192.168.1.12)

Capacity: 27 Pts | Active: 22 | Spare: 5 (18.5%)

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

C3-S01-P00 | 0 | 1 | 1756-IB32 | AT-40201_DI_1 | Pin 1 | C3S1:1/C3S01-X1:1 | DI | 24VDC Dry Contact | ACTIVE | IS-JB-603 | Spray Dryer 3rd Floor | C3S01-X1 | - | AT-40201 | | -

C3-S01-P01 | 1 | 2 | 1756-IB32 | AT-40202_DI_1 | Pin 2 | C3S1:2/C3S01-X1:2 | DI | 24VDC Dry Contact | ACTIVE | IS-JB-603 | Spray Dryer 3rd Floor | C3S01-X1 | - | AT-40202 | | -

C3-S01-P02 | 2 | 3 | 1756-IB32 | AT-40203_DI_1 | Pin 3 | C3S1:3/C3S01-X1:3 | DI | 24VDC Dry Contact | ACTIVE | IS-JB-603 | Spray Dryer 3rd Floor | C3S01-X1 | - | AT-40203 | | -

C3-S01-P03 | 3 | 4 | 1756-IB32 | LSH-60230_DI_1 | Pin 4 | C3S1:4/C3S01-X1:4 | DI | 24VDC Dry Contact | ACTIVE | IS-JB-603 | Spray Dryer 3rd Floor | C3S01-X1 | - | LSH-60230 | | 3-25-01-602-PD-04

C3-S01-P04 | 4 | 5 | 1756-IB32 | LSH-60231_DI_1 | Pin 5 | C3S1:5/C3S01-X1:5 | DI | 24VDC Dry Contact | ACTIVE | IS-JB-603 | Spray Dryer 3rd Floor | C3S01-X1 | - | LSH-60231 | | 3-25-01-602-PD-04

C3-S01-P05 | 5 | 6 | 1756-IB32 | LSH-60240_DI_1 | Pin 6 | C3S1:6/C3S01-X1:6 | DI | 24VDC Dry Contact | ACTIVE | IS-JB-603 | Spray Dryer 3rd Floor | C3S01-X1 | - | LSH-60240 | | 3-25-01-602-PD-05

C3-S01-P06 | 6 | 7 | 1756-IB32 | PD-60202_DI_1 | Pin 7 | C3S1:7/C3S01-X1:7 | DI | 24VDC Dry Contact | ACTIVE | IS-JB-603 | Spray Dryer 3rd Floor | C3S01-X1 | - | PD-60202 | | -

C3-S01-P07 | 7 | 8 | 1756-IB32 | RV-60204_DI_1 | Pin 8 | C3S1:8/C3S01-X1:8 | DI | 24VDC Dry Contact | ACTIVE | IS-JB-603 | Spray Dryer 3rd Floor | C3S01-X1 | - | RV-60204 | | -

C3-S01-P08 | 8 | 9 | 1756-IB32 | ZS-60201C_DI_1 | Pin 9 | C3S1:9/C3S01-X1:9 | DI | 24VDC Dry Contact | ACTIVE | IS-JB-603 | Spray Dryer 3rd Floor | C3S01-X1 | - | ZS-60201C | | 3-25-01-602-PD-04

C3-S01-P09 | 9 | 10 | 1756-IB32 | ZS-60201D_DI_1 | Pin 10 | C3S1:10/C3S01-X1:10 | DI | 24VDC Dry Contact | ACTIVE | IS-JB-603 | Spray Dryer 3rd Floor | C3S01-X1 | - | ZS-60201D | | 3-25-01-602-PD-04

C3-S01-P10 | 10 | 11 | 1756-IB32 | ZS-60201E_DI_1 | Pin 11 | C3S1:11/C3S01-X1:11 | DI | 24VDC Dry Contact | ACTIVE | IS-JB-603 | Spray Dryer 3rd Floor | C3S01-X1 | - | ZS-60201E | | 3-25-01-602-PD-04

C3-S01-P11 | 11 | 12 | 1756-IB32 | ZS-60229_DI_1 | Pin 12 | C3S1:12/C3S01-X1:12 | DI | 24VDC Dry Contact | ACTIVE | IS-JB-603 | Spray Dryer 3rd Floor | C3S01-X1 | - | ZS-60229 | | 3-25-01-602-PD-04

C3-S01-P12 | 12 | 13 | 1756-IB32 | ZS-60230_DI_1 | Pin 13 | C3S1:13/C3S01-X1:13 | DI | 24VDC Dry Contact | ACTIVE | IS-JB-603 | Spray Dryer 3rd Floor | C3S01-X1 | - | ZS-60230 | | 3-25-01-602-PD-04

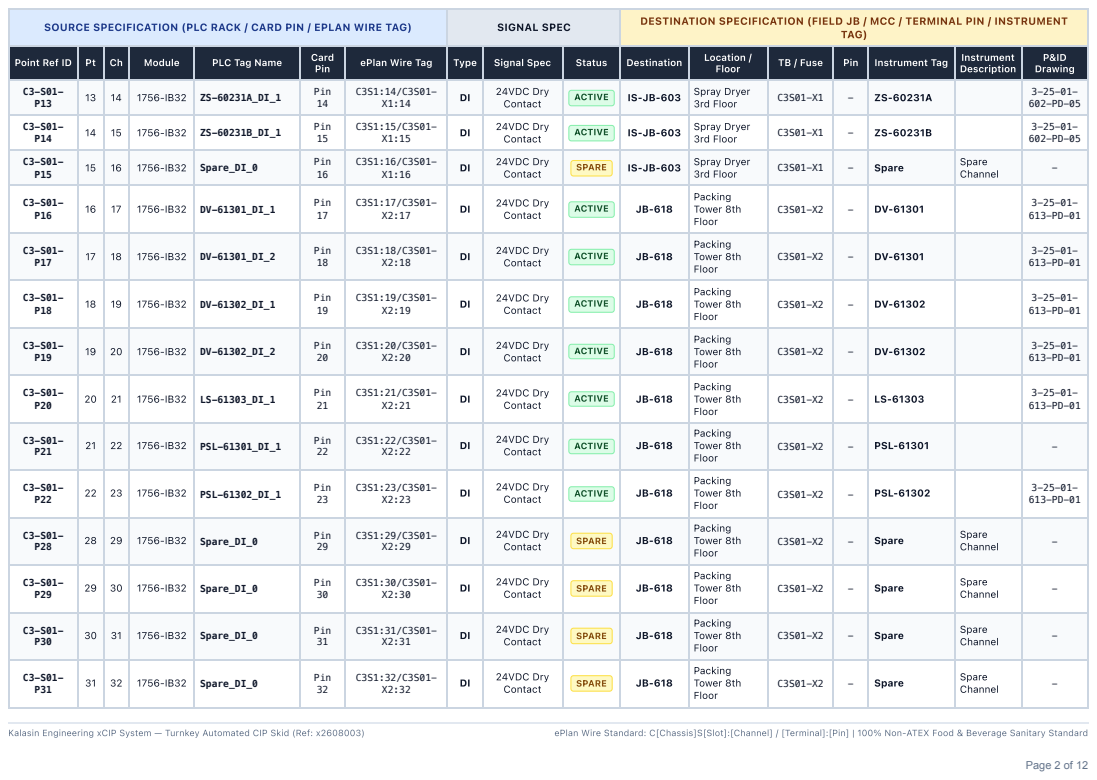
[picture p159: page 2]
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

C3-S01-P13 | 13 | 14 | 1756-IB32 | ZS-60231A_DI_1 | Pin 14 | C3S1:14/C3S01-X1:14 | DI | 24VDC Dry Contact | ACTIVE | IS-JB-603 | Spray Dryer 3rd Floor | C3S01-X1 | - | ZS-60231A | | 3-25-01-602-PD-05

C3-S01-P14 | 14 | 15 | 1756-IB32 | ZS-60231B_DI_1 | Pin 15 | C3S1:15/C3S01-X1:15 | DI | 24VDC Dry Contact | ACTIVE | IS-JB-603 | Spray Dryer 3rd Floor | C3S01-X1 | - | ZS-60231B | | 3-25-01-602-PD-05

C3-S01-P15 | 15 | 16 | 1756-IB32 | Spare_DI_0 | Pin 16 | C3S1:16/C3S01-X1:16 | DI | 24VDC Dry Contact | SPARE | IS-JB-603 | Spray Dryer 3rd Floor | C3S01-X1 | - | Spare | Spare Channel | -

C3-S01-P16 | 16 | 17 | 1756-IB32 | DV-61301_DI_1 | Pin 17 | C3S1:17/C3S01-X2:17 | DI | 24VDC Dry Contact | ACTIVE | JB-618 | Packing Tower 8th Floor | C3S01-X2 | - | DV-61301 | | 3-25-01-613-PD-01

C3-S01-P17 | 17 | 18 | 1756-IB32 | DV-61301_DI_2 | Pin 18 | C3S1:18/C3S01-X2:18 | DI | 24VDC Dry Contact | ACTIVE | JB-618 | Packing Tower 8th Floor | C3S01-X2 | - | DV-61301 | | 3-25-01-613-PD-01

C3-S01-P18 | 18 | 19 | 1756-IB32 | DV-61302_DI_1 | Pin 19 | C3S1:19/C3S01-X2:19 | DI | 24VDC Dry Contact | ACTIVE | JB-618 | Packing Tower 8th Floor | C3S01-X2 | - | DV-61302 | | 3-25-01-613-PD-01

C3-S01-P19 | 19 | 20 | 1756-IB32 | DV-61302_DI_2 | Pin 20 | C3S1:20/C3S01-X2:20 | DI | 24VDC Dry Contact | ACTIVE | JB-618 | Packing Tower 8th Floor | C3S01-X2 | - | DV-61302 | | 3-25-01-613-PD-01

C3-S01-P20 | 20 | 21 | 1756-IB32 | LS-61303_DI_1 | Pin 21 | C3S1:21/C3S01-X2:21 | DI | 24VDC Dry Contact | ACTIVE | JB-618 | Packing Tower 8th Floor | C3S01-X2 | - | LS-61303 | | 3-25-01-613-PD-01

C3-S01-P21 | 21 | 22 | 1756-IB32 | PSL-61301_DI_1 | Pin 22 | C3S1:22/C3S01-X2:22 | DI | 24VDC Dry Contact | ACTIVE | JB-618 | Packing Tower 8th Floor | C3S01-X2 | - | PSL-61301 | | -

C3-S01-P22 | 22 | 23 | 1756-IB32 | PSL-61302_DI_1 | Pin 23 | C3S1:23/C3S01-X2:23 | DI | 24VDC Dry Contact | ACTIVE | JB-618 | Packing Tower 8th Floor | C3S01-X2 | - | PSL-61302 | | 3-25-01-613-PD-01

C3-S01-P28 | 28 | 29 | 1756-IB32 | Spare_DI_0 | Pin 29 | C3S1:29/C3S01-X2:29 | DI | 24VDC Dry Contact | SPARE | JB-618 | Packing Tower 8th Floor | C3S01-X2 | - | Spare | Spare Channel | -

C3-S01-P29 | 29 | 30 | 1756-IB32 | Spare_DI_0 | Pin 30 | C3S1:30/C3S01-X2:30 | DI | 24VDC Dry Contact | SPARE | JB-618 | Packing Tower 8th Floor | C3S01-X2 | - | Spare | Spare Channel | -

C3-S01-P30 | 30 | 31 | 1756-IB32 | Spare_DI_0 | Pin 31 | C3S1:31/C3S01-X2:31 | DI | 24VDC Dry Contact | SPARE | JB-618 | Packing Tower 8th Floor | C3S01-X2 | - | Spare | Spare Channel | -

C3-S01-P31 | 31 | 32 | 1756-IB32 | Spare_DI_0 | Pin 32 | C3S1:32/C3S01-X2:32 | DI | 24VDC Dry Contact | SPARE | JB-618 | Packing Tower 8th Floor | C3S01-X2 | - | Spare | Spare Channel | -

## C3 SLOT 02 — 1756-IB32 (DI)

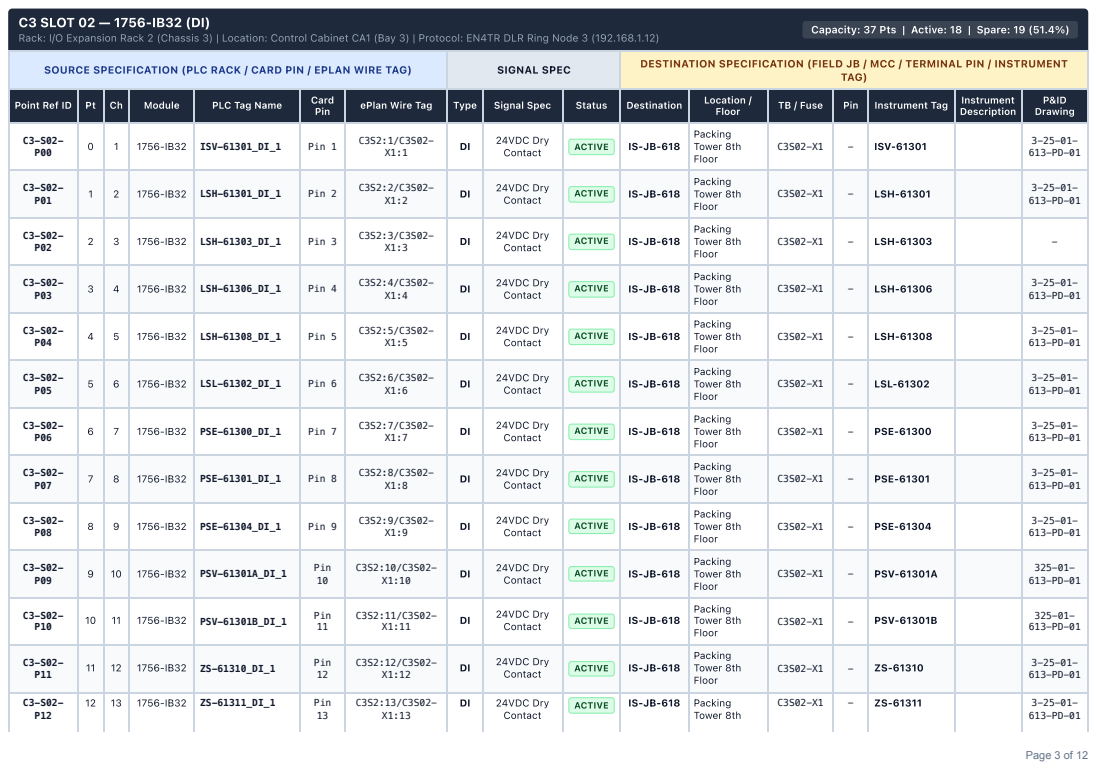
[picture p160: page 3]
Pin; 24VDC Dry; Contact; ACTIVE; Packing; Tower 8th

Capacity: 37 Pts | Active: 18 | Spare: 19 (51.4%)

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

C3-S02-P00 | 0 | 1 | 1756-IB32 | ISV-61301_DI_1 | Pin 1 | C3S2:1/C3S02-X1:1 | DI | 24VDC Dry Contact | ACTIVE | IS-JB-618 | Packing Tower 8th Floor | C3S02-X1 | - | ISV-61301 | | 3-25-01-613-PD-01

C3-S02-P01 | 1 | 2 | 1756-IB32 | LSH-61301_DI_1 | Pin 2 | C3S2:2/C3S02-X1:2 | DI | 24VDC Dry Contact | ACTIVE | IS-JB-618 | Packing Tower 8th Floor | C3S02-X1 | - | LSH-61301 | | 3-25-01-613-PD-01

C3-S02-P02 | 2 | 3 | 1756-IB32 | LSH-61303_DI_1 | Pin 3 | C3S2:3/C3S02-X1:3 | DI | 24VDC Dry Contact | ACTIVE | IS-JB-618 | Packing Tower 8th Floor | C3S02-X1 | - | LSH-61303 | | -

C3-S02-P03 | 3 | 4 | 1756-IB32 | LSH-61306_DI_1 | Pin 4 | C3S2:4/C3S02-X1:4 | DI | 24VDC Dry Contact | ACTIVE | IS-JB-618 | Packing Tower 8th Floor | C3S02-X1 | - | LSH-61306 | | 3-25-01-613-PD-01

C3-S02-P04 | 4 | 5 | 1756-IB32 | LSH-61308_DI_1 | Pin 5 | C3S2:5/C3S02-X1:5 | DI | 24VDC Dry Contact | ACTIVE | IS-JB-618 | Packing Tower 8th Floor | C3S02-X1 | - | LSH-61308 | | 3-25-01-613-PD-01

C3-S02-P05 | 5 | 6 | 1756-IB32 | LSL-61302_DI_1 | Pin 6 | C3S2:6/C3S02-X1:6 | DI | 24VDC Dry Contact | ACTIVE | IS-JB-618 | Packing Tower 8th Floor | C3S02-X1 | - | LSL-61302 | | 3-25-01-613-PD-01

C3-S02-P06 | 6 | 7 | 1756-IB32 | PSE-61300_DI_1 | Pin 7 | C3S2:7/C3S02-X1:7 | DI | 24VDC Dry Contact | ACTIVE | IS-JB-618 | Packing Tower 8th Floor | C3S02-X1 | - | PSE-61300 | | 3-25-01-613-PD-01

C3-S02-P07 | 7 | 8 | 1756-IB32 | PSE-61301_DI_1 | Pin 8 | C3S2:8/C3S02-X1:8 | DI | 24VDC Dry Contact | ACTIVE | IS-JB-618 | Packing Tower 8th Floor | C3S02-X1 | - | PSE-61301 | | 3-25-01-613-PD-01

C3-S02-P08 | 8 | 9 | 1756-IB32 | PSE-61304_DI_1 | Pin 9 | C3S2:9/C3S02-X1:9 | DI | 24VDC Dry Contact | ACTIVE | IS-JB-618 | Packing Tower 8th Floor | C3S02-X1 | - | PSE-61304 | | 3-25-01-613-PD-01

C3-S02-P09 | 9 | 10 | 1756-IB32 | PSV-61301A_DI_1 | Pin 10 | C3S2:10/C3S02-X1:10 | DI | 24VDC Dry Contact | ACTIVE | IS-JB-618 | Packing Tower 8th Floor | C3S02-X1 | - | PSV-61301A | | 325-01-613-PD-01

C3-S02-P10 | 10 | 11 | 1756-IB32 | PSV-61301B_DI_1 | Pin 11 | C3S2:11/C3S02-X1:11 | DI | 24VDC Dry Contact | ACTIVE | IS-JB-618 | Packing Tower 8th Floor | C3S02-X1 | - | PSV-61301B | | 325-01-613-PD-01

C3-S02-P11 | 11 | 12 | 1756-IB32 | ZS-61310_DI_1 | Pin 12 | C3S2:12/C3S02-X1:12 | DI | 24VDC Dry Contact | ACTIVE | IS-JB-618 | Packing Tower 8th Floor | C3S02-X1 | - | ZS-61310 | | 3-25-01-613-PD-01

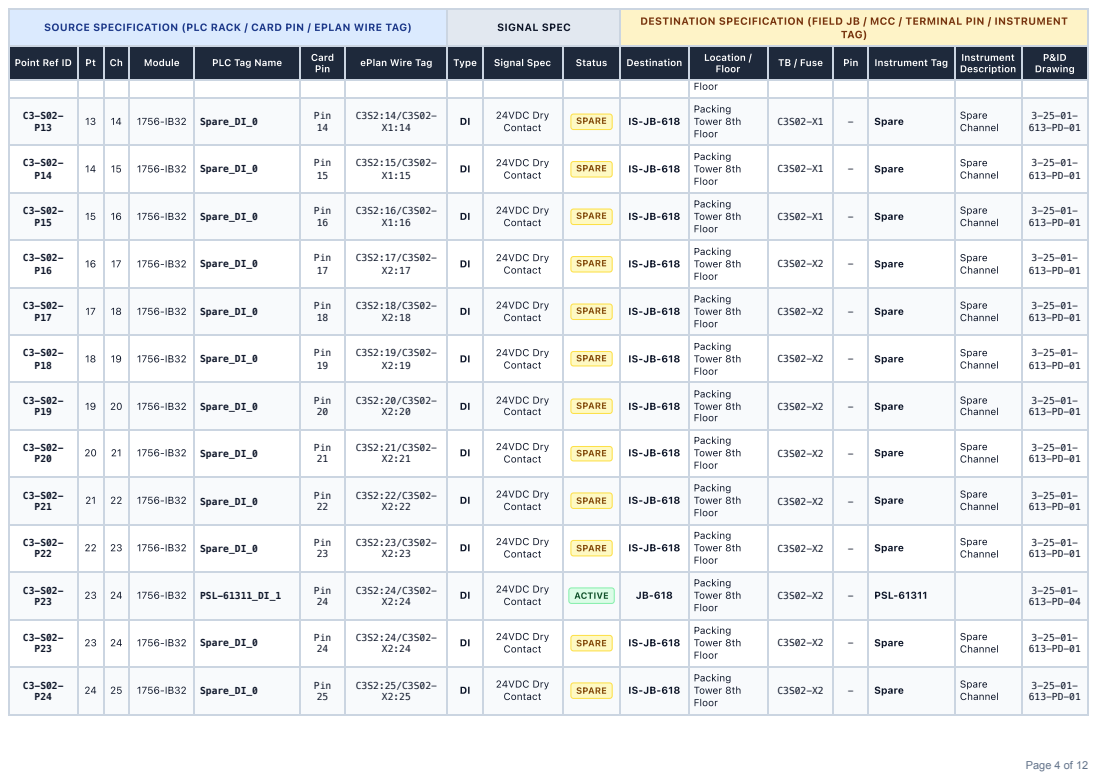
[picture p161: page 4]
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

Floor

C3-S02-P13 | 13 | 14 | 1756-IB32 | Spare_DI_0 | Pin 14 | C3S2:14/C3S02-X1:14 | DI | 24VDC Dry Contact | SPARE | IS-JB-618 | Packing Tower 8th Floor | C3S02-X1 | - | Spare | Spare Channel | 3-25-01-613-PD-01

C3-S02-P14 | 14 | 15 | 1756-IB32 | Spare_DI_0 | Pin 15 | C3S2:15/C3S02-X1:15 | DI | 24VDC Dry Contact | SPARE | IS-JB-618 | Packing Tower 8th Floor | C3S02-X1 | - | Spare | Spare Channel | 3-25-01-613-PD-01

C3-S02-P15 | 15 | 16 | 1756-IB32 | Spare_DI_0 | Pin 16 | C3S2:16/C3S02-X1:16 | DI | 24VDC Dry Contact | SPARE | IS-JB-618 | Packing Tower 8th Floor | C3S02-X1 | - | Spare | Spare Channel | 3-25-01-613-PD-01

C3-S02-P16 | 16 | 17 | 1756-IB32 | Spare_DI_0 | Pin 17 | C3S2:17/C3S02-X2:17 | DI | 24VDC Dry Contact | SPARE | IS-JB-618 | Packing Tower 8th Floor | C3S02-X2 | - | Spare | Spare Channel | 3-25-01-613-PD-01

C3-S02-P17 | 17 | 18 | 1756-IB32 | Spare_DI_0 | Pin 18 | C3S2:18/C3S02-X2:18 | DI | 24VDC Dry Contact | SPARE | IS-JB-618 | Packing Tower 8th Floor | C3S02-X2 | - | Spare | Spare Channel | 3-25-01-613-PD-01

C3-S02-P18 | 18 | 19 | 1756-IB32 | Spare_DI_0 | Pin 19 | C3S2:19/C3S02-X2:19 | DI | 24VDC Dry Contact | SPARE | IS-JB-618 | Packing Tower 8th Floor | C3S02-X2 | - | Spare | Spare Channel | 3-25-01-613-PD-01

C3-S02-P19 | 19 | 20 | 1756-IB32 | Spare_DI_0 | Pin 20 | C3S2:20/C3S02-X2:20 | DI | 24VDC Dry Contact | SPARE | IS-JB-618 | Packing Tower 8th Floor | C3S02-X2 | - | Spare | Spare Channel | 3-25-01-613-PD-01

C3-S02-P20 | 20 | 21 | 1756-IB32 | Spare_DI_0 | Pin 21 | C3S2:21/C3S02-X2:21 | DI | 24VDC Dry Contact | SPARE | IS-JB-618 | Packing Tower 8th Floor | C3S02-X2 | - | Spare | Spare Channel | 3-25-01-613-PD-01

C3-S02-P21 | 21 | 22 | 1756-IB32 | Spare_DI_0 | Pin 22 | C3S2:22/C3S02-X2:22 | DI | 24VDC Dry Contact | SPARE | IS-JB-618 | Packing Tower 8th Floor | C3S02-X2 | - | Spare | Spare Channel | 3-25-01-613-PD-01

C3-S02-P22 | 22 | 23 | 1756-IB32 | Spare_DI_0 | Pin 23 | C3S2:23/C3S02-X2:23 | DI | 24VDC Dry Contact | SPARE | IS-JB-618 | Packing Tower 8th Floor | C3S02-X2 | - | Spare | Spare Channel | 3-25-01-613-PD-01

C3-S02-P23 | 23 | 24 | 1756-IB32 | PSL-61311_DI_1 | Pin 24 | C3S2:24/C3S02-X2:24 | DI | 24VDC Dry Contact | ACTIVE | JB-618 | Packing Tower 8th Floor | C3S02-X2 | - | PSL-61311 | | 3-25-01-613-PD-04

C3-S02-P23 | 23 | 24 | 1756-IB32 | Spare_DI_0 | Pin 24 | C3S2:24/C3S02-X2:24 | DI | 24VDC Dry Contact | SPARE | IS-JB-618 | Packing Tower 8th Floor | C3S02-X2 | - | Spare | Spare Channel | 3-25-01-613-PD-01

C3-S02-P24 | 24 | 25 | 1756-IB32 | Spare_DI_0 | Pin 25 | C3S2:25/C3S02-X2:25 | DI | 24VDC Dry Contact | SPARE | IS-JB-618 | Packing Tower 8th Floor | C3S02-X2 | - | Spare | Spare Channel | 3-25-01-613-PD-01

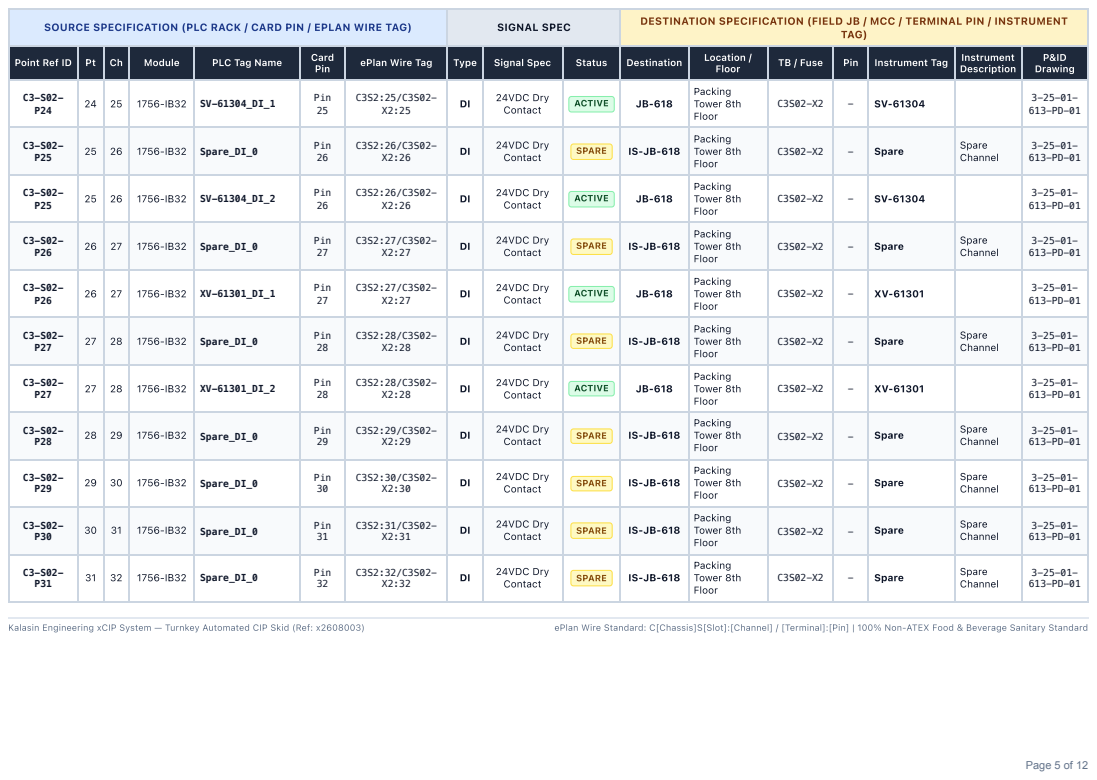
[picture p162: page 5]
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

C3-S02-P24 | 24 | 25 | 1756-IB32 | SV-61304_DI_1 | Pin 25 | C3S2:25/C3S02-X2:25 | DI | 24VDC Dry Contact | ACTIVE | JB-618 | Packing Tower 8th Floor | C3S02-X2 | - | SV-61304 | | 3-25-01-613-PD-01

C3-S02-P25 | 25 | 26 | 1756-IB32 | Spare_DI_0 | Pin 26 | C3S2:26/C3S02-X2:26 | DI | 24VDC Dry Contact | SPARE | IS-JB-618 | Packing Tower 8th Floor | C3S02-X2 | - | Spare | Spare Channel | 3-25-01-613-PD-01

C3-S02-P25 | 25 | 26 | 1756-IB32 | SV-61304_DI_2 | Pin 26 | C3S2:26/C3S02-X2:26 | DI | 24VDC Dry Contact | ACTIVE | JB-618 | Packing Tower 8th Floor | C3S02-X2 | - | SV-61304 | | 3-25-01-613-PD-01

C3-S02-P26 | 26 | 27 | 1756-IB32 | Spare_DI_0 | Pin 27 | C3S2:27/C3S02-X2:27 | DI | 24VDC Dry Contact | SPARE | IS-JB-618 | Packing Tower 8th Floor | C3S02-X2 | - | Spare | Spare Channel | 3-25-01-613-PD-01

C3-S02-P26 | 26 | 27 | 1756-IB32 | XV-61301_DI_1 | Pin 27 | C3S2:27/C3S02-X2:27 | DI | 24VDC Dry Contact | ACTIVE | JB-618 | Packing Tower 8th Floor | C3S02-X2 | - | XV-61301 | | 3-25-01-613-PD-01

C3-S02-P27 | 27 | 28 | 1756-IB32 | Spare_DI_0 | Pin 28 | C3S2:28/C3S02-X2:28 | DI | 24VDC Dry Contact | SPARE | IS-JB-618 | Packing Tower 8th Floor | C3S02-X2 | - | Spare | Spare Channel | 3-25-01-613-PD-01

C3-S02-P27 | 27 | 28 | 1756-IB32 | XV-61301_DI_2 | Pin 28 | C3S2:28/C3S02-X2:28 | DI | 24VDC Dry Contact | ACTIVE | JB-618 | Packing Tower 8th Floor | C3S02-X2 | - | XV-61301 | | 3-25-01-613-PD-01

C3-S02-P28 | 28 | 29 | 1756-IB32 | Spare_DI_0 | Pin 29 | C3S2:29/C3S02-X2:29 | DI | 24VDC Dry Contact | SPARE | IS-JB-618 | Packing Tower 8th Floor | C3S02-X2 | - | Spare | Spare Channel | 3-25-01-613-PD-01

C3-S02-P29 | 29 | 30 | 1756-IB32 | Spare_DI_0 | Pin 30 | C3S2:30/C3S02-X2:30 | DI | 24VDC Dry Contact | SPARE | IS-JB-618 | Packing Tower 8th Floor | C3S02-X2 | - | Spare | Spare Channel | 3-25-01-613-PD-01

C3-S02-P30 | 30 | 31 | 1756-IB32 | Spare_DI_0 | Pin 31 | C3S2:31/C3S02-X2:31 | DI | 24VDC Dry Contact | SPARE | IS-JB-618 | Packing Tower 8th Floor | C3S02-X2 | - | Spare | Spare Channel | 3-25-01-613-PD-01

C3-S02-P31 | 31 | 32 | 1756-IB32 | Spare_DI_0 | Pin 32 | C3S2:32/C3S02-X2:32 | DI | 24VDC Dry Contact | SPARE | IS-JB-618 | Packing Tower 8th Floor | C3S02-X2 | - | Spare | Spare Channel | 3-25-01-613-PD-01

## C3 SLOT 03 — 1756-OB32 (DO)

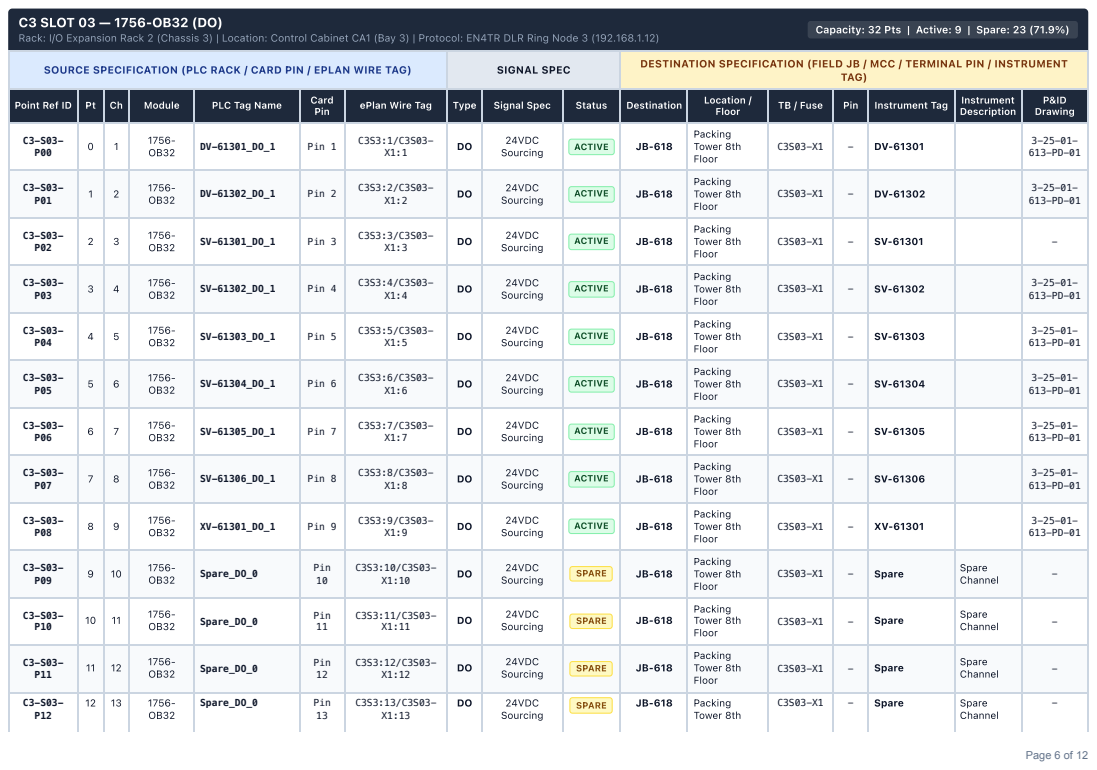
[picture p163: page 6]
Spare_DO_0; Pin; 24VDC; Sourcing; SPARE; Packing; Tower 8th; Spare; Channel

Capacity: 32 Pts | Active: 9 | Spare: 23 (71.9%)

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

C3-S03-P00 | 0 | 1 | 1756-OB32 | DV-61301_DO_1 | Pin 1 | C3S3:1/C3S03-X1:1 | DO | 24VDC Sourcing | ACTIVE | JB-618 | Packing Tower 8th Floor | C3S03-X1 | - | DV-61301 | | 3-25-01-613-PD-01

C3-S03-P01 | 1 | 2 | 1756-OB32 | DV-61302_DO_1 | Pin 2 | C3S3:2/C3S03-X1:2 | DO | 24VDC Sourcing | ACTIVE | JB-618 | Packing Tower 8th Floor | C3S03-X1 | - | DV-61302 | | 3-25-01-613-PD-01

C3-S03-P02 | 2 | 3 | 1756-OB32 | SV-61301_DO_1 | Pin 3 | C3S3:3/C3S03-X1:3 | DO | 24VDC Sourcing | ACTIVE | JB-618 | Packing Tower 8th Floor | C3S03-X1 | - | SV-61301 | | -

C3-S03-P03 | 3 | 4 | 1756-OB32 | SV-61302_DO_1 | Pin 4 | C3S3:4/C3S03-X1:4 | DO | 24VDC Sourcing | ACTIVE | JB-618 | Packing Tower 8th Floor | C3S03-X1 | - | SV-61302 | | 3-25-01-613-PD-01

C3-S03-P04 | 4 | 5 | 1756-OB32 | SV-61303_DO_1 | Pin 5 | C3S3:5/C3S03-X1:5 | DO | 24VDC Sourcing | ACTIVE | JB-618 | Packing Tower 8th Floor | C3S03-X1 | - | SV-61303 | | 3-25-01-613-PD-01

C3-S03-P05 | 5 | 6 | 1756-OB32 | SV-61304_DO_1 | Pin 6 | C3S3:6/C3S03-X1:6 | DO | 24VDC Sourcing | ACTIVE | JB-618 | Packing Tower 8th Floor | C3S03-X1 | - | SV-61304 | | 3-25-01-613-PD-01

C3-S03-P06 | 6 | 7 | 1756-OB32 | SV-61305_DO_1 | Pin 7 | C3S3:7/C3S03-X1:7 | DO | 24VDC Sourcing | ACTIVE | JB-618 | Packing Tower 8th Floor | C3S03-X1 | - | SV-61305 | | 3-25-01-613-PD-01

C3-S03-P07 | 7 | 8 | 1756-OB32 | SV-61306_DO_1 | Pin 8 | C3S3:8/C3S03-X1:8 | DO | 24VDC Sourcing | ACTIVE | JB-618 | Packing Tower 8th Floor | C3S03-X1 | - | SV-61306 | | 3-25-01-613-PD-01

C3-S03-P08 | 8 | 9 | 1756-OB32 | XV-61301_DO_1 | Pin 9 | C3S3:9/C3S03-X1:9 | DO | 24VDC Sourcing | ACTIVE | JB-618 | Packing Tower 8th Floor | C3S03-X1 | - | XV-61301 | | 3-25-01-613-PD-01

C3-S03-P09 | 9 | 10 | 1756-OB32 | Spare_DO_0 | Pin 10 | C3S3:10/C3S03-X1:10 | DO | 24VDC Sourcing | SPARE | JB-618 | Packing Tower 8th Floor | C3S03-X1 | - | Spare | Spare Channel | -

C3-S03-P10 | 10 | 11 | 1756-OB32 | Spare_DO_0 | Pin 11 | C3S3:11/C3S03-X1:11 | DO | 24VDC Sourcing | SPARE | JB-618 | Packing Tower 8th Floor | C3S03-X1 | - | Spare | Spare Channel | -

C3-S03-P11 | 11 | 12 | 1756-OB32 | Spare_DO_0 | Pin 12 | C3S3:12/C3S03-X1:12 | DO | 24VDC Sourcing | SPARE | JB-618 | Packing Tower 8th Floor | C3S03-X1 | - | Spare | Spare Channel | -

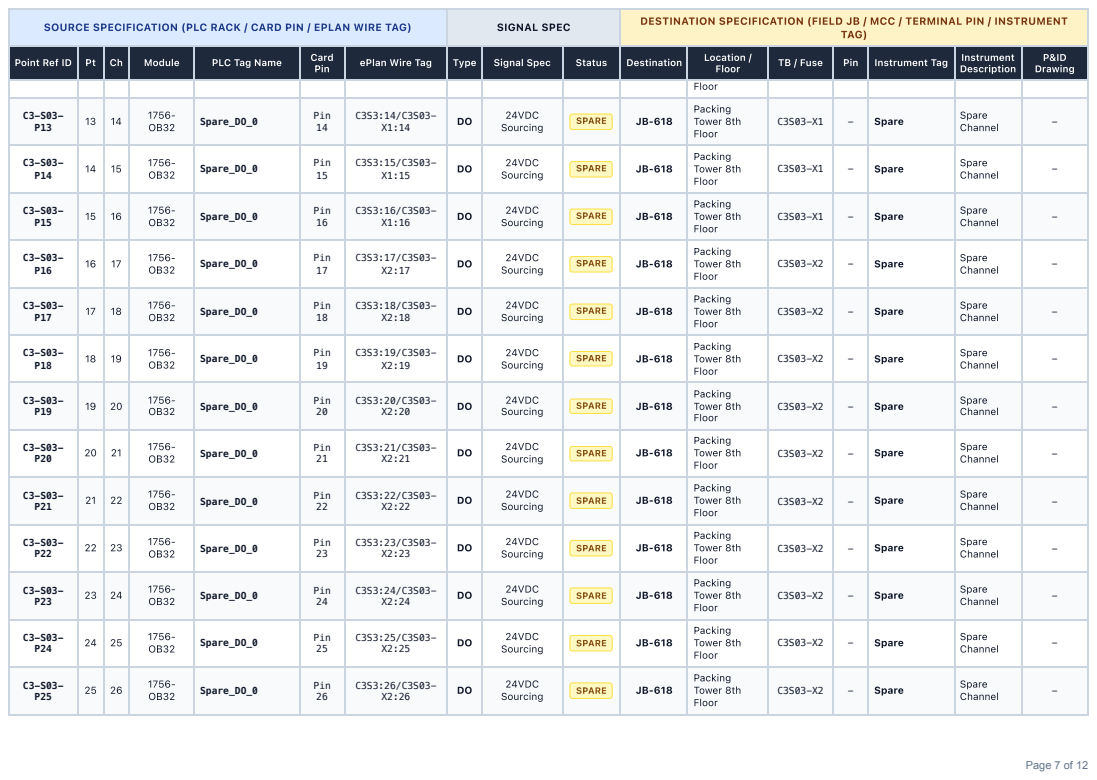
[picture p164: page 7]
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

Floor

C3-S03-P13 | 13 | 14 | 1756-OB32 | Spare_DO_0 | Pin 14 | C3S3:14/C3S03-X1:14 | DO | 24VDC Sourcing | SPARE | JB-618 | Packing Tower 8th Floor | C3S03-X1 | - | Spare | Spare Channel | -

C3-S03-P14 | 14 | 15 | 1756-OB32 | Spare_DO_0 | Pin 15 | C3S3:15/C3S03-X1:15 | DO | 24VDC Sourcing | SPARE | JB-618 | Packing Tower 8th Floor | C3S03-X1 | - | Spare | Spare Channel | -

C3-S03-P15 | 15 | 16 | 1756-OB32 | Spare_DO_0 | Pin 16 | C3S3:16/C3S03-X1:16 | DO | 24VDC Sourcing | SPARE | JB-618 | Packing Tower 8th Floor | C3S03-X1 | - | Spare | Spare Channel | -

C3-S03-P16 | 16 | 17 | 1756-OB32 | Spare_DO_0 | Pin 17 | C3S3:17/C3S03-X2:17 | DO | 24VDC Sourcing | SPARE | JB-618 | Packing Tower 8th Floor | C3S03-X2 | - | Spare | Spare Channel | -

C3-S03-P17 | 17 | 18 | 1756-OB32 | Spare_DO_0 | Pin 18 | C3S3:18/C3S03-X2:18 | DO | 24VDC Sourcing | SPARE | JB-618 | Packing Tower 8th Floor | C3S03-X2 | - | Spare | Spare Channel | -

C3-S03-P18 | 18 | 19 | 1756-OB32 | Spare_DO_0 | Pin 19 | C3S3:19/C3S03-X2:19 | DO | 24VDC Sourcing | SPARE | JB-618 | Packing Tower 8th Floor | C3S03-X2 | - | Spare | Spare Channel | -

C3-S03-P19 | 19 | 20 | 1756-OB32 | Spare_DO_0 | Pin 20 | C3S3:20/C3S03-X2:20 | DO | 24VDC Sourcing | SPARE | JB-618 | Packing Tower 8th Floor | C3S03-X2 | - | Spare | Spare Channel | -

C3-S03-P20 | 20 | 21 | 1756-OB32 | Spare_DO_0 | Pin 21 | C3S3:21/C3S03-X2:21 | DO | 24VDC Sourcing | SPARE | JB-618 | Packing Tower 8th Floor | C3S03-X2 | - | Spare | Spare Channel | -

C3-S03-P21 | 21 | 22 | 1756-OB32 | Spare_DO_0 | Pin 22 | C3S3:22/C3S03-X2:22 | DO | 24VDC Sourcing | SPARE | JB-618 | Packing Tower 8th Floor | C3S03-X2 | - | Spare | Spare Channel | -

C3-S03-P22 | 22 | 23 | 1756-OB32 | Spare_DO_0 | Pin 23 | C3S3:23/C3S03-X2:23 | DO | 24VDC Sourcing | SPARE | JB-618 | Packing Tower 8th Floor | C3S03-X2 | - | Spare | Spare Channel | -

C3-S03-P23 | 23 | 24 | 1756-OB32 | Spare_DO_0 | Pin 24 | C3S3:24/C3S03-X2:24 | DO | 24VDC Sourcing | SPARE | JB-618 | Packing Tower 8th Floor | C3S03-X2 | - | Spare | Spare Channel | -

C3-S03-P24 | 24 | 25 | 1756-OB32 | Spare_DO_0 | Pin 25 | C3S3:25/C3S03-X2:25 | DO | 24VDC Sourcing | SPARE | JB-618 | Packing Tower 8th Floor | C3S03-X2 | - | Spare | Spare Channel | -

C3-S03-P25 | 25 | 26 | 1756-OB32 | Spare_DO_0 | Pin 26 | C3S3:26/C3S03-X2:26 | DO | 24VDC Sourcing | SPARE | JB-618 | Packing Tower 8th Floor | C3S03-X2 | - | Spare | Spare Channel | -

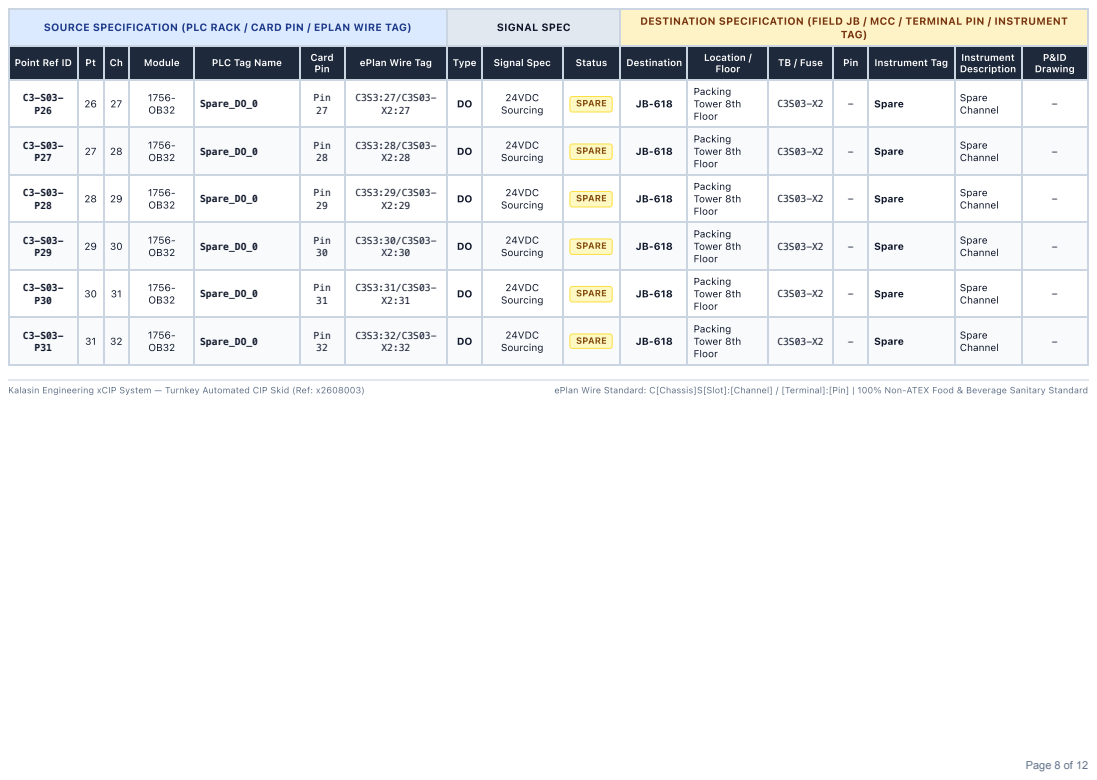
[picture p165: page 8]
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

C3-S03-P26 | 26 | 27 | 1756-OB32 | Spare_DO_0 | Pin 27 | C3S3:27/C3S03-X2:27 | DO | 24VDC Sourcing | SPARE | JB-618 | Packing Tower 8th Floor | C3S03-X2 | - | Spare | Spare Channel | -

C3-S03-P27 | 27 | 28 | 1756-OB32 | Spare_DO_0 | Pin 28 | C3S3:28/C3S03-X2:28 | DO | 24VDC Sourcing | SPARE | JB-618 | Packing Tower 8th Floor | C3S03-X2 | - | Spare | Spare Channel | -

C3-S03-P28 | 28 | 29 | 1756-OB32 | Spare_DO_0 | Pin 29 | C3S3:29/C3S03-X2:29 | DO | 24VDC Sourcing | SPARE | JB-618 | Packing Tower 8th Floor | C3S03-X2 | - | Spare | Spare Channel | -

C3-S03-P29 | 29 | 30 | 1756-OB32 | Spare_DO_0 | Pin 30 | C3S3:30/C3S03-X2:30 | DO | 24VDC Sourcing | SPARE | JB-618 | Packing Tower 8th Floor | C3S03-X2 | - | Spare | Spare Channel | -

C3-S03-P30 | 30 | 31 | 1756-OB32 | Spare_DO_0 | Pin 31 | C3S3:31/C3S03-X2:31 | DO | 24VDC Sourcing | SPARE | JB-618 | Packing Tower 8th Floor | C3S03-X2 | - | Spare | Spare Channel | -

C3-S03-P31 | 31 | 32 | 1756-OB32 | Spare_DO_0 | Pin 32 | C3S3:32/C3S03-X2:32 | DO | 24VDC Sourcing | SPARE | JB-618 | Packing Tower 8th Floor | C3S03-X2 | - | Spare | Spare Channel | -

## C3 SLOT 04 — 1756-IF16 (AI)

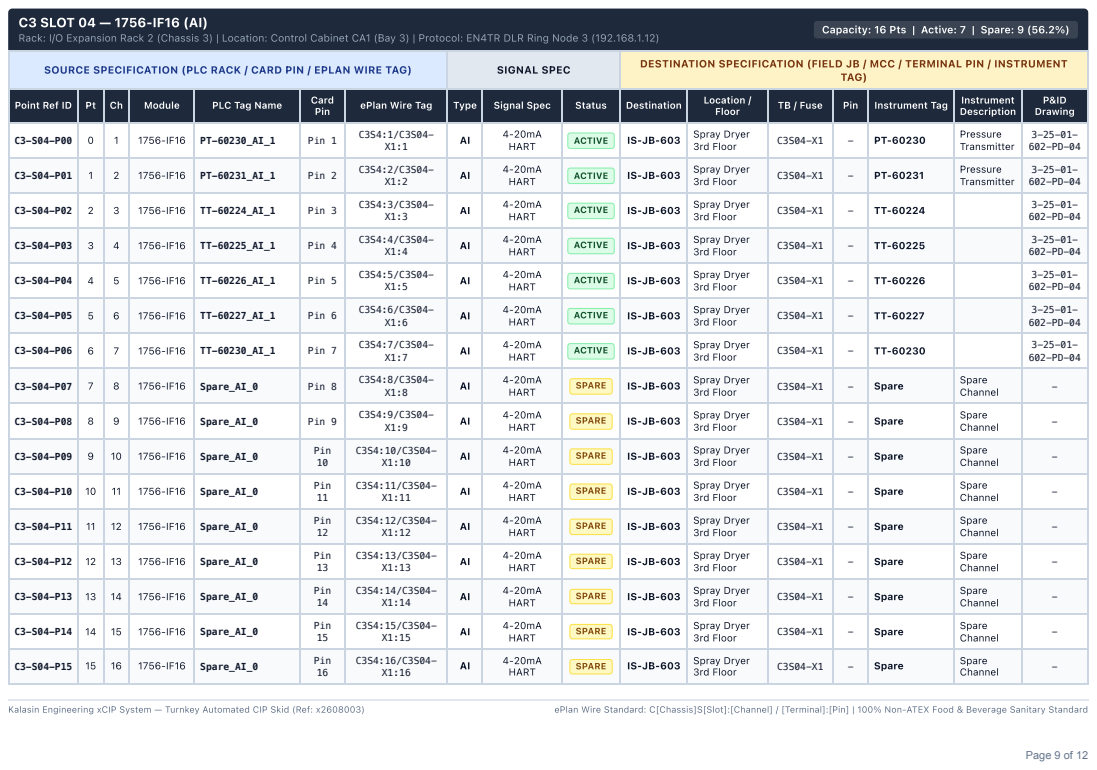
[picture p166: page 9]
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

Capacity: 16 Pts | Active: 7 | Spare: 9 (56.2%)

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

C3-S04-P00 | 0 | 1 | 1756-IF16 | PT-60230_AI_1 | Pin 1 | C3S4:1/C3S04-X1:1 | AI | 4-20mA HART | ACTIVE | IS-JB-603 | Spray Dryer 3rd Floor | C3S04-X1 | - | PT-60230 | Pressure Transmitter | 3-25-01-602-PD-04

C3-S04-P01 | 1 | 2 | 1756-IF16 | PT-60231_AI_1 | Pin 2 | C3S4:2/C3S04-X1:2 | AI | 4-20mA HART | ACTIVE | IS-JB-603 | Spray Dryer 3rd Floor | C3S04-X1 | - | PT-60231 | Pressure Transmitter | 3-25-01-602-PD-04

C3-S04-P02 | 2 | 3 | 1756-IF16 | TT-60224_AI_1 | Pin 3 | C3S4:3/C3S04-X1:3 | AI | 4-20mA HART | ACTIVE | IS-JB-603 | Spray Dryer 3rd Floor | C3S04-X1 | - | TT-60224 | | 3-25-01-602-PD-04

C3-S04-P03 | 3 | 4 | 1756-IF16 | TT-60225_AI_1 | Pin 4 | C3S4:4/C3S04-X1:4 | AI | 4-20mA HART | ACTIVE | IS-JB-603 | Spray Dryer 3rd Floor | C3S04-X1 | - | TT-60225 | | 3-25-01-602-PD-04

C3-S04-P04 | 4 | 5 | 1756-IF16 | TT-60226_AI_1 | Pin 5 | C3S4:5/C3S04-X1:5 | AI | 4-20mA HART | ACTIVE | IS-JB-603 | Spray Dryer 3rd Floor | C3S04-X1 | - | TT-60226 | | 3-25-01-602-PD-04

C3-S04-P05 | 5 | 6 | 1756-IF16 | TT-60227_AI_1 | Pin 6 | C3S4:6/C3S04-X1:6 | AI | 4-20mA HART | ACTIVE | IS-JB-603 | Spray Dryer 3rd Floor | C3S04-X1 | - | TT-60227 | | 3-25-01-602-PD-04

C3-S04-P06 | 6 | 7 | 1756-IF16 | TT-60230_AI_1 | Pin 7 | C3S4:7/C3S04-X1:7 | AI | 4-20mA HART | ACTIVE | IS-JB-603 | Spray Dryer 3rd Floor | C3S04-X1 | - | TT-60230 | | 3-25-01-602-PD-04

C3-S04-P07 | 7 | 8 | 1756-IF16 | Spare_AI_0 | Pin 8 | C3S4:8/C3S04-X1:8 | AI | 4-20mA HART | SPARE | IS-JB-603 | Spray Dryer 3rd Floor | C3S04-X1 | - | Spare | Spare Channel | -

C3-S04-P08 | 8 | 9 | 1756-IF16 | Spare_AI_0 | Pin 9 | C3S4:9/C3S04-X1:9 | AI | 4-20mA HART | SPARE | IS-JB-603 | Spray Dryer 3rd Floor | C3S04-X1 | - | Spare | Spare Channel | -

C3-S04-P09 | 9 | 10 | 1756-IF16 | Spare_AI_0 | Pin 10 | C3S4:10/C3S04-X1:10 | AI | 4-20mA HART | SPARE | IS-JB-603 | Spray Dryer 3rd Floor | C3S04-X1 | - | Spare | Spare Channel | -

C3-S04-P10 | 10 | 11 | 1756-IF16 | Spare_AI_0 | Pin 11 | C3S4:11/C3S04-X1:11 | AI | 4-20mA HART | SPARE | IS-JB-603 | Spray Dryer 3rd Floor | C3S04-X1 | - | Spare | Spare Channel | -

C3-S04-P11 | 11 | 12 | 1756-IF16 | Spare_AI_0 | Pin 12 | C3S4:12/C3S04-X1:12 | AI | 4-20mA HART | SPARE | IS-JB-603 | Spray Dryer 3rd Floor | C3S04-X1 | - | Spare | Spare Channel | -

C3-S04-P12 | 12 | 13 | 1756-IF16 | Spare_AI_0 | Pin 13 | C3S4:13/C3S04-X1:13 | AI | 4-20mA HART | SPARE | IS-JB-603 | Spray Dryer 3rd Floor | C3S04-X1 | - | Spare | Spare Channel | -

C3-S04-P13 | 13 | 14 | 1756-IF16 | Spare_AI_0 | Pin 14 | C3S4:14/C3S04-X1:14 | AI | 4-20mA HART | SPARE | IS-JB-603 | Spray Dryer 3rd Floor | C3S04-X1 | - | Spare | Spare Channel | -

C3-S04-P14 | 14 | 15 | 1756-IF16 | Spare_AI_0 | Pin 15 | C3S4:15/C3S04-X1:15 | AI | 4-20mA HART | SPARE | IS-JB-603 | Spray Dryer 3rd Floor | C3S04-X1 | - | Spare | Spare Channel | -

C3-S04-P15 | 15 | 16 | 1756-IF16 | Spare_AI_0 | Pin 16 | C3S4:16/C3S04-X1:16 | AI | 4-20mA HART | SPARE | IS-JB-603 | Spray Dryer 3rd Floor | C3S04-X1 | - | Spare | Spare Channel | -
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
