x92120/x260911-002-KalasinEngineering/02_Electrical_and_eDrawing/04_PDF_Reports_and_Drawings/Chassis_C4_Slots_IO_Report.pdf

# KALASIN ENGINEERING — C4(I/O EXPANSION RACK 3(CHASSIS4))

C4

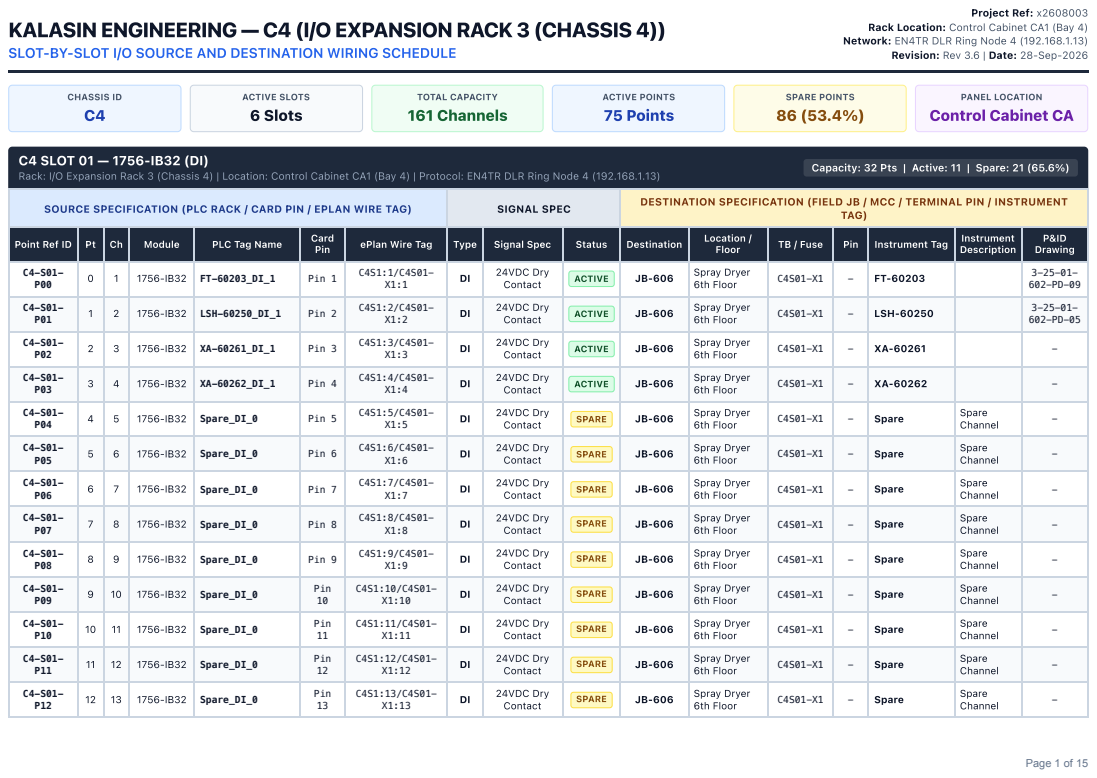
[picture p167: page 1]
Project Ref: x2608003; CHASSIS ID; ACTIVE SLOTS 6 Slots; TOTAL CAPACITY 161 Channels; ACTIVE POINTS 75 Points; SPARE POINTS 86 (53.4%)

Rack Location: Control Cabinet CA1 (Bay 4)
Network: EN4TR DLR Ring Node 4 (192.168.1.13)

SLOT-BY-SLOT I/O SOURCE AND DESTINATION WIRING SCHEDULE

Revision: Rev 3.6 | Date: 28-Sep-2026

PANEL LOCATION
Control Cabinet CA

C4 SLOT 01 — 1756-IB32 (DI)
Rack: I/O Expansion Rack 3 (Chassis 4) | Location: Control Cabinet CA1 (Bay 4) | Protocol: EN4TR DLR Ring Node 4 (192.168.1.13)

Capacity: 32 Pts | Active: 11 | Spare: 21 (65.6%)

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

C4-S01-P00 | 0 | 1 | 1756-IB32 | FT-60203_DI_1 | Pin 1 | C4S1:1/C4S01-X1:1 | DI | 24VDC Dry Contact | ACTIVE | JB-606 | Spray Dryer 6th Floor | C4S01-X1 | - | FT-60203 | | 3-25-01-602-PD-09

C4-S01-P01 | 1 | 2 | 1756-IB32 | LSH-60250_DI_1 | Pin 2 | C4S1:2/C4S01-X1:2 | DI | 24VDC Dry Contact | ACTIVE | JB-606 | Spray Dryer 6th Floor | C4S01-X1 | - | LSH-60250 | | 3-25-01-602-PD-05

C4-S01-P02 | 2 | 3 | 1756-IB32 | XA-60261_DI_1 | Pin 3 | C4S1:3/C4S01-X1:3 | DI | 24VDC Dry Contact | ACTIVE | JB-606 | Spray Dryer 6th Floor | C4S01-X1 | - | XA-60261 | | -

C4-S01-P03 | 3 | 4 | 1756-IB32 | XA-60262_DI_1 | Pin 4 | C4S1:4/C4S01-X1:4 | DI | 24VDC Dry Contact | ACTIVE | JB-606 | Spray Dryer 6th Floor | C4S01-X1 | - | XA-60262 | | -

C4-S01-P04 | 4 | 5 | 1756-IB32 | Spare_DI_0 | Pin 5 | C4S1:5/C4S01-X1:5 | DI | 24VDC Dry Contact | SPARE | JB-606 | Spray Dryer 6th Floor | C4S01-X1 | - | Spare | Spare Channel | -

C4-S01-P05 | 5 | 6 | 1756-IB32 | Spare_DI_0 | Pin 6 | C4S1:6/C4S01-X1:6 | DI | 24VDC Dry Contact | SPARE | JB-606 | Spray Dryer 6th Floor | C4S01-X1 | - | Spare | Spare Channel | -

C4-S01-P06 | 6 | 7 | 1756-IB32 | Spare_DI_0 | Pin 7 | C4S1:7/C4S01-X1:7 | DI | 24VDC Dry Contact | SPARE | JB-606 | Spray Dryer 6th Floor | C4S01-X1 | - | Spare | Spare Channel | -

C4-S01-P07 | 7 | 8 | 1756-IB32 | Spare_DI_0 | Pin 8 | C4S1:8/C4S01-X1:8 | DI | 24VDC Dry Contact | SPARE | JB-606 | Spray Dryer 6th Floor | C4S01-X1 | - | Spare | Spare Channel | -

C4-S01-P08 | 8 | 9 | 1756-IB32 | Spare_DI_0 | Pin 9 | C4S1:9/C4S01-X1:9 | DI | 24VDC Dry Contact | SPARE | JB-606 | Spray Dryer 6th Floor | C4S01-X1 | - | Spare | Spare Channel | -

C4-S01-P09 | 9 | 10 | 1756-IB32 | Spare_DI_0 | Pin 10 | C4S1:10/C4S01-X1:10 | DI | 24VDC Dry Contact | SPARE | JB-606 | Spray Dryer 6th Floor | C4S01-X1 | - | Spare | Spare Channel | -

C4-S01-P10 | 10 | 11 | 1756-IB32 | Spare_DI_0 | Pin 11 | C4S1:11/C4S01-X1:11 | DI | 24VDC Dry Contact | SPARE | JB-606 | Spray Dryer 6th Floor | C4S01-X1 | - | Spare | Spare Channel | -

C4-S01-P11 | 11 | 12 | 1756-IB32 | Spare_DI_0 | Pin 12 | C4S1:12/C4S01-X1:12 | DI | 24VDC Dry Contact | SPARE | JB-606 | Spray Dryer 6th Floor | C4S01-X1 | - | Spare | Spare Channel | -

C4-S01-P12 | 12 | 13 | 1756-IB32 | Spare_DI_0 | Pin 13 | C4S1:13/C4S01-X1:13 | DI | 24VDC Dry Contact | SPARE | JB-606 | Spray Dryer 6th Floor | C4S01-X1 | - | Spare | Spare Channel | -

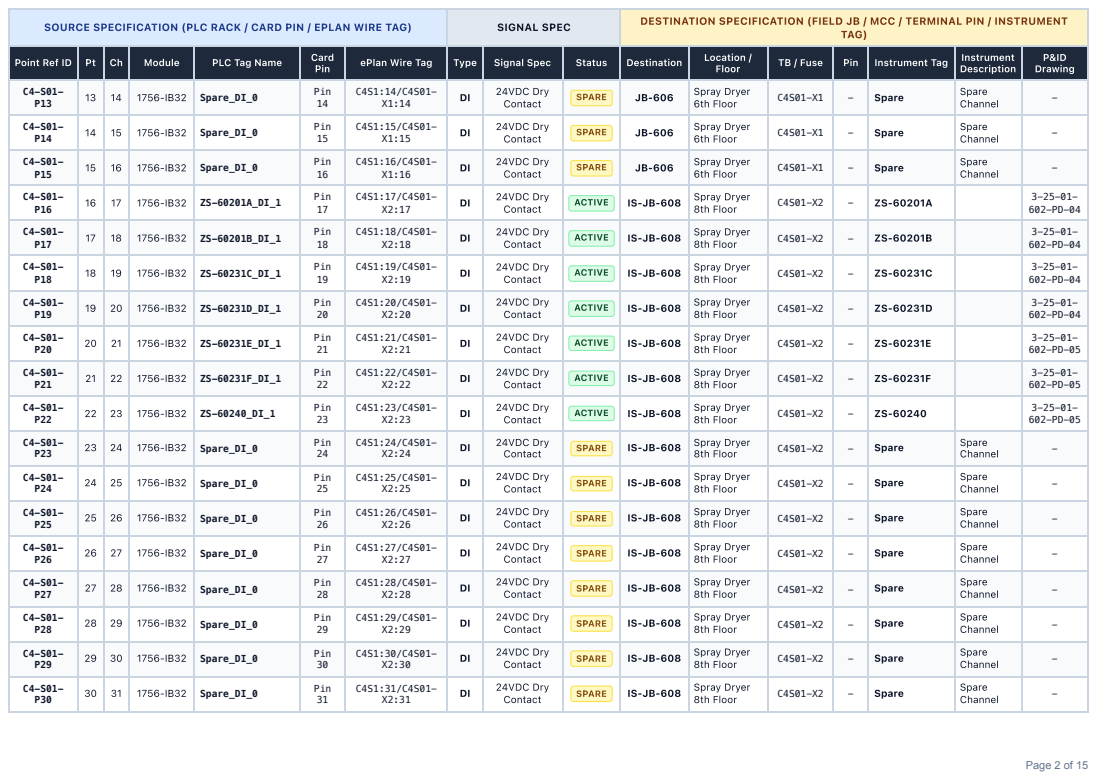
[picture p168: page 2]
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

C4-S01-P13 | 13 | 14 | 1756-IB32 | Spare_DI_0 | Pin 14 | C4S1:14/C4S01-X1:14 | DI | 24VDC Dry Contact | SPARE | JB-606 | Spray Dryer 6th Floor | C4S01-X1 | - | Spare | Spare Channel | -

C4-S01-P14 | 14 | 15 | 1756-IB32 | Spare_DI_0 | Pin 15 | C4S1:15/C4S01-X1:15 | DI | 24VDC Dry Contact | SPARE | JB-606 | Spray Dryer 6th Floor | C4S01-X1 | - | Spare | Spare Channel | -

C4-S01-P15 | 15 | 16 | 1756-IB32 | Spare_DI_0 | Pin 16 | C4S1:16/C4S01-X1:16 | DI | 24VDC Dry Contact | SPARE | JB-606 | Spray Dryer 6th Floor | C4S01-X1 | - | Spare | Spare Channel | -

C4-S01-P16 | 16 | 17 | 1756-IB32 | ZS-60201A_DI_1 | Pin 17 | C4S1:17/C4S01-X2:17 | DI | 24VDC Dry Contact | ACTIVE | IS-JB-608 | Spray Dryer 8th Floor | C4S01-X2 | - | ZS-60201A | | 3-25-01-602-PD-04

C4-S01-P17 | 17 | 18 | 1756-IB32 | ZS-60201B_DI_1 | Pin 18 | C4S1:18/C4S01-X2:18 | DI | 24VDC Dry Contact | ACTIVE | IS-JB-608 | Spray Dryer 8th Floor | C4S01-X2 | - | ZS-60201B | | 3-25-01-602-PD-04

C4-S01-P18 | 18 | 19 | 1756-IB32 | ZS-60231C_DI_1 | Pin 19 | C4S1:19/C4S01-X2:19 | DI | 24VDC Dry Contact | ACTIVE | IS-JB-608 | Spray Dryer 8th Floor | C4S01-X2 | - | ZS-60231C | | 3-25-01-602-PD-04

C4-S01-P19 | 19 | 20 | 1756-IB32 | ZS-60231D_DI_1 | Pin 20 | C4S1:20/C4S01-X2:20 | DI | 24VDC Dry Contact | ACTIVE | IS-JB-608 | Spray Dryer 8th Floor | C4S01-X2 | - | ZS-60231D | | 3-25-01-602-PD-04

C4-S01-P20 | 20 | 21 | 1756-IB32 | ZS-60231E_DI_1 | Pin 21 | C4S1:21/C4S01-X2:21 | DI | 24VDC Dry Contact | ACTIVE | IS-JB-608 | Spray Dryer 8th Floor | C4S01-X2 | - | ZS-60231E | | 3-25-01-602-PD-05

C4-S01-P21 | 21 | 22 | 1756-IB32 | ZS-60231F_DI_1 | Pin 22 | C4S1:22/C4S01-X2:22 | DI | 24VDC Dry Contact | ACTIVE | IS-JB-608 | Spray Dryer 8th Floor | C4S01-X2 | - | ZS-60231F | | 3-25-01-602-PD-05

C4-S01-P22 | 22 | 23 | 1756-IB32 | ZS-60240_DI_1 | Pin 23 | C4S1:23/C4S01-X2:23 | DI | 24VDC Dry Contact | ACTIVE | IS-JB-608 | Spray Dryer 8th Floor | C4S01-X2 | - | ZS-60240 | | 3-25-01-602-PD-05

C4-S01-P23 | 23 | 24 | 1756-IB32 | Spare_DI_0 | Pin 24 | C4S1:24/C4S01-X2:24 | DI | 24VDC Dry Contact | SPARE | IS-JB-608 | Spray Dryer 8th Floor | C4S01-X2 | - | Spare | Spare Channel | -

C4-S01-P24 | 24 | 25 | 1756-IB32 | Spare_DI_0 | Pin 25 | C4S1:25/C4S01-X2:25 | DI | 24VDC Dry Contact | SPARE | IS-JB-608 | Spray Dryer 8th Floor | C4S01-X2 | - | Spare | Spare Channel | -

C4-S01-P25 | 25 | 26 | 1756-IB32 | Spare_DI_0 | Pin 26 | C4S1:26/C4S01-X2:26 | DI | 24VDC Dry Contact | SPARE | IS-JB-608 | Spray Dryer 8th Floor | C4S01-X2 | - | Spare | Spare Channel | -

C4-S01-P26 | 26 | 27 | 1756-IB32 | Spare_DI_0 | Pin 27 | C4S1:27/C4S01-X2:27 | DI | 24VDC Dry Contact | SPARE | IS-JB-608 | Spray Dryer 8th Floor | C4S01-X2 | - | Spare | Spare Channel | -

C4-S01-P27 | 27 | 28 | 1756-IB32 | Spare_DI_0 | Pin 28 | C4S1:28/C4S01-X2:28 | DI | 24VDC Dry Contact | SPARE | IS-JB-608 | Spray Dryer 8th Floor | C4S01-X2 | - | Spare | Spare Channel | -

C4-S01-P28 | 28 | 29 | 1756-IB32 | Spare_DI_0 | Pin 29 | C4S1:29/C4S01-X2:29 | DI | 24VDC Dry Contact | SPARE | IS-JB-608 | Spray Dryer 8th Floor | C4S01-X2 | - | Spare | Spare Channel | -

C4-S01-P29 | 29 | 30 | 1756-IB32 | Spare_DI_0 | Pin 30 | C4S1:30/C4S01-X2:30 | DI | 24VDC Dry Contact | SPARE | IS-JB-608 | Spray Dryer 8th Floor | C4S01-X2 | - | Spare | Spare Channel | -

C4-S01-P30 | 30 | 31 | 1756-IB32 | Spare_DI_0 | Pin 31 | C4S1:31/C4S01-X2:31 | DI | 24VDC Dry Contact | SPARE | IS-JB-608 | Spray Dryer 8th Floor | C4S01-X2 | - | Spare | Spare Channel | -

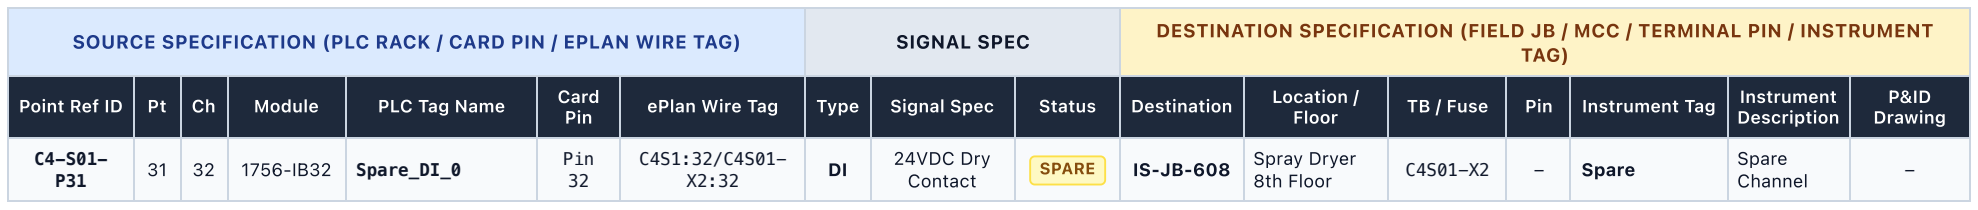
[picture p169: figure]
Point Ref ID; Module; PLC Tag Name; Card Pin; ePlan Wire Tag; Type; Signal Spec; Status; Destination; Location / Floor; TB / Fuse; Pin; Instrument Tag; Instrument Description; P&ID Drawing; Spare_DI_0; Pin 32; 24VDC Dry Contact; SPARE; Spray Dryer 8th Floor; Spare; Spare Channel

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

## C4 SLOT 02 — 1756-IB32 (DI)

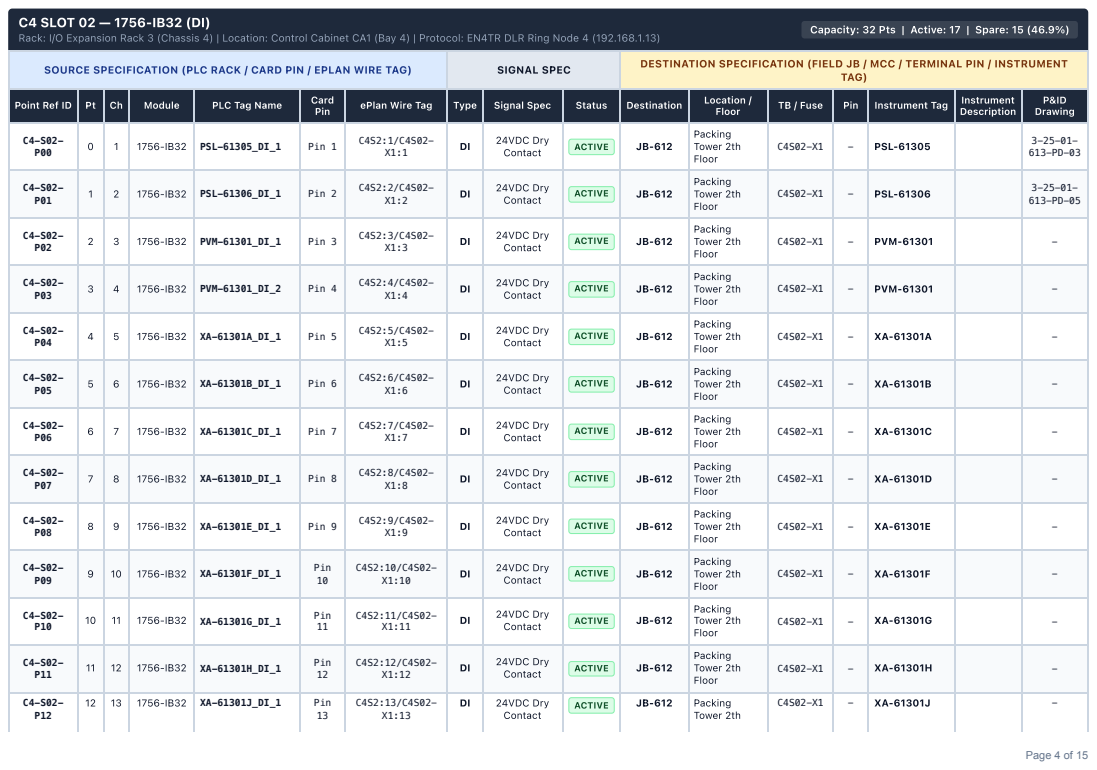
[picture p170: page 4]
Pin; 24VDC Dry; Contact; ACTIVE; Packing; Tower 2th

Capacity: 32 Pts | Active: 17 | Spare: 15 (46.9%)

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

C4-S02-P00 | 0 | 1 | 1756-IB32 | PSL-61305_DI_1 | Pin 1 | C4S2:1/C4S02-X1:1 | DI | 24VDC Dry Contact | ACTIVE | JB-612 | Packing Tower 2th Floor | C4S02-X1 | - | PSL-61305 | | 3-25-01-613-PD-03

C4-S02-P01 | 1 | 2 | 1756-IB32 | PSL-61306_DI_1 | Pin 2 | C4S2:2/C4S02-X1:2 | DI | 24VDC Dry Contact | ACTIVE | JB-612 | Packing Tower 2th Floor | C4S02-X1 | - | PSL-61306 | | 3-25-01-613-PD-05

C4-S02-P02 | 2 | 3 | 1756-IB32 | PVM-61301_DI_1 | Pin 3 | C4S2:3/C4S02-X1:3 | DI | 24VDC Dry Contact | ACTIVE | JB-612 | Packing Tower 2th Floor | C4S02-X1 | - | PVM-61301 | | -

C4-S02-P03 | 3 | 4 | 1756-IB32 | PVM-61301_DI_2 | Pin 4 | C4S2:4/C4S02-X1:4 | DI | 24VDC Dry Contact | ACTIVE | JB-612 | Packing Tower 2th Floor | C4S02-X1 | - | PVM-61301 | | -

C4-S02-P04 | 4 | 5 | 1756-IB32 | XA-61301A_DI_1 | Pin 5 | C4S2:5/C4S02-X1:5 | DI | 24VDC Dry Contact | ACTIVE | JB-612 | Packing Tower 2th Floor | C4S02-X1 | - | XA-61301A | | -

C4-S02-P05 | 5 | 6 | 1756-IB32 | XA-61301B_DI_1 | Pin 6 | C4S2:6/C4S02-X1:6 | DI | 24VDC Dry Contact | ACTIVE | JB-612 | Packing Tower 2th Floor | C4S02-X1 | - | XA-61301B | | -

C4-S02-P06 | 6 | 7 | 1756-IB32 | XA-61301C_DI_1 | Pin 7 | C4S2:7/C4S02-X1:7 | DI | 24VDC Dry Contact | ACTIVE | JB-612 | Packing Tower 2th Floor | C4S02-X1 | - | XA-61301C | | -

C4-S02-P07 | 7 | 8 | 1756-IB32 | XA-61301D_DI_1 | Pin 8 | C4S2:8/C4S02-X1:8 | DI | 24VDC Dry Contact | ACTIVE | JB-612 | Packing Tower 2th Floor | C4S02-X1 | - | XA-61301D | | -

C4-S02-P08 | 8 | 9 | 1756-IB32 | XA-61301E_DI_1 | Pin 9 | C4S2:9/C4S02-X1:9 | DI | 24VDC Dry Contact | ACTIVE | JB-612 | Packing Tower 2th Floor | C4S02-X1 | - | XA-61301E | | -

C4-S02-P09 | 9 | 10 | 1756-IB32 | XA-61301F_DI_1 | Pin 10 | C4S2:10/C4S02-X1:10 | DI | 24VDC Dry Contact | ACTIVE | JB-612 | Packing Tower 2th Floor | C4S02-X1 | - | XA-61301F | | -

C4-S02-P10 | 10 | 11 | 1756-IB32 | XA-61301G_DI_1 | Pin 11 | C4S2:11/C4S02-X1:11 | DI | 24VDC Dry Contact | ACTIVE | JB-612 | Packing Tower 2th Floor | C4S02-X1 | - | XA-61301G | | -

C4-S02-P11 | 11 | 12 | 1756-IB32 | XA-61301H_DI_1 | Pin 12 | C4S2:12/C4S02-X1:12 | DI | 24VDC Dry Contact | ACTIVE | JB-612 | Packing Tower 2th Floor | C4S02-X1 | - | XA-61301H | | -

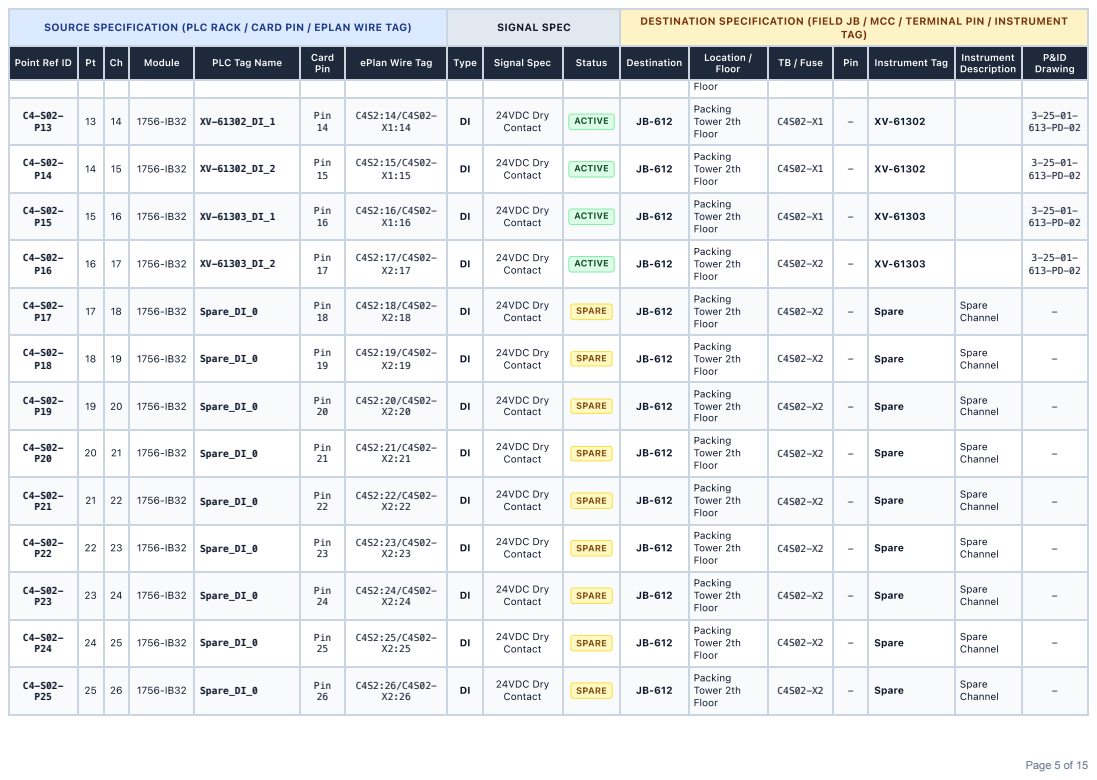
[picture p171: page 5]
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

Floor

C4-S02-P13 | 13 | 14 | 1756-IB32 | XV-61302_DI_1 | Pin 14 | C4S2:14/C4S02-X1:14 | DI | 24VDC Dry Contact | ACTIVE | JB-612 | Packing Tower 2th Floor | C4S02-X1 | - | XV-61302 | | 3-25-01-613-PD-02

C4-S02-P14 | 14 | 15 | 1756-IB32 | XV-61302_DI_2 | Pin 15 | C4S2:15/C4S02-X1:15 | DI | 24VDC Dry Contact | ACTIVE | JB-612 | Packing Tower 2th Floor | C4S02-X1 | - | XV-61302 | | 3-25-01-613-PD-02

C4-S02-P15 | 15 | 16 | 1756-IB32 | XV-61303_DI_1 | Pin 16 | C4S2:16/C4S02-X1:16 | DI | 24VDC Dry Contact | ACTIVE | JB-612 | Packing Tower 2th Floor | C4S02-X1 | - | XV-61303 | | 3-25-01-613-PD-02

C4-S02-P16 | 16 | 17 | 1756-IB32 | XV-61303_DI_2 | Pin 17 | C4S2:17/C4S02-X2:17 | DI | 24VDC Dry Contact | ACTIVE | JB-612 | Packing Tower 2th Floor | C4S02-X2 | - | XV-61303 | | 3-25-01-613-PD-02

C4-S02-P17 | 17 | 18 | 1756-IB32 | Spare_DI_0 | Pin 18 | C4S2:18/C4S02-X2:18 | DI | 24VDC Dry Contact | SPARE | JB-612 | Packing Tower 2th Floor | C4S02-X2 | - | Spare | Spare Channel | -

C4-S02-P18 | 18 | 19 | 1756-IB32 | Spare_DI_0 | Pin 19 | C4S2:19/C4S02-X2:19 | DI | 24VDC Dry Contact | SPARE | JB-612 | Packing Tower 2th Floor | C4S02-X2 | - | Spare | Spare Channel | -

C4-S02-P19 | 19 | 20 | 1756-IB32 | Spare_DI_0 | Pin 20 | C4S2:20/C4S02-X2:20 | DI | 24VDC Dry Contact | SPARE | JB-612 | Packing Tower 2th Floor | C4S02-X2 | - | Spare | Spare Channel | -

C4-S02-P20 | 20 | 21 | 1756-IB32 | Spare_DI_0 | Pin 21 | C4S2:21/C4S02-X2:21 | DI | 24VDC Dry Contact | SPARE | JB-612 | Packing Tower 2th Floor | C4S02-X2 | - | Spare | Spare Channel | -

C4-S02-P21 | 21 | 22 | 1756-IB32 | Spare_DI_0 | Pin 22 | C4S2:22/C4S02-X2:22 | DI | 24VDC Dry Contact | SPARE | JB-612 | Packing Tower 2th Floor | C4S02-X2 | - | Spare | Spare Channel | -

C4-S02-P22 | 22 | 23 | 1756-IB32 | Spare_DI_0 | Pin 23 | C4S2:23/C4S02-X2:23 | DI | 24VDC Dry Contact | SPARE | JB-612 | Packing Tower 2th Floor | C4S02-X2 | - | Spare | Spare Channel | -

C4-S02-P23 | 23 | 24 | 1756-IB32 | Spare_DI_0 | Pin 24 | C4S2:24/C4S02-X2:24 | DI | 24VDC Dry Contact | SPARE | JB-612 | Packing Tower 2th Floor | C4S02-X2 | - | Spare | Spare Channel | -

C4-S02-P24 | 24 | 25 | 1756-IB32 | Spare_DI_0 | Pin 25 | C4S2:25/C4S02-X2:25 | DI | 24VDC Dry Contact | SPARE | JB-612 | Packing Tower 2th Floor | C4S02-X2 | - | Spare | Spare Channel | -

C4-S02-P25 | 25 | 26 | 1756-IB32 | Spare_DI_0 | Pin 26 | C4S2:26/C4S02-X2:26 | DI | 24VDC Dry Contact | SPARE | JB-612 | Packing Tower 2th Floor | C4S02-X2 | - | Spare | Spare Channel | -

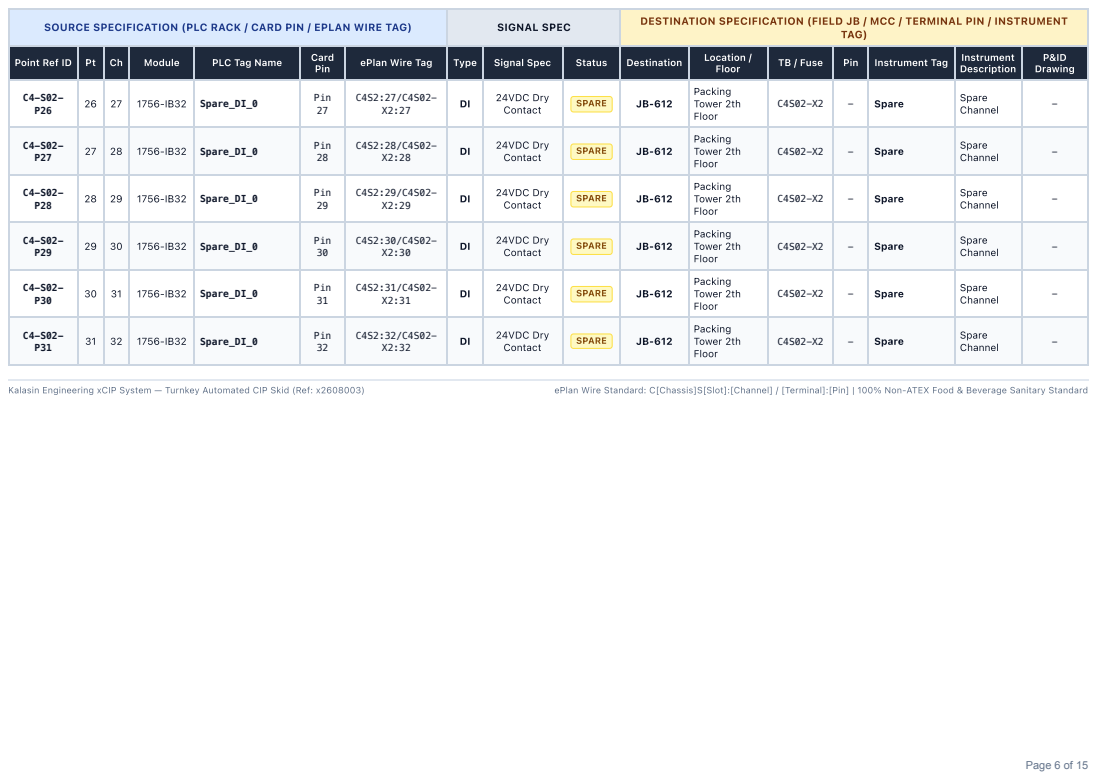
[picture p172: page 6]
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

C4-S02-P26 | 26 | 27 | 1756-IB32 | Spare_DI_0 | Pin 27 | C4S2:27/C4S02-X2:27 | DI | 24VDC Dry Contact | SPARE | JB-612 | Packing Tower 2th Floor | C4S02-X2 | - | Spare | Spare Channel | -

C4-S02-P27 | 27 | 28 | 1756-IB32 | Spare_DI_0 | Pin 28 | C4S2:28/C4S02-X2:28 | DI | 24VDC Dry Contact | SPARE | JB-612 | Packing Tower 2th Floor | C4S02-X2 | - | Spare | Spare Channel | -

C4-S02-P28 | 28 | 29 | 1756-IB32 | Spare_DI_0 | Pin 29 | C4S2:29/C4S02-X2:29 | DI | 24VDC Dry Contact | SPARE | JB-612 | Packing Tower 2th Floor | C4S02-X2 | - | Spare | Spare Channel | -

C4-S02-P29 | 29 | 30 | 1756-IB32 | Spare_DI_0 | Pin 30 | C4S2:30/C4S02-X2:30 | DI | 24VDC Dry Contact | SPARE | JB-612 | Packing Tower 2th Floor | C4S02-X2 | - | Spare | Spare Channel | -

C4-S02-P30 | 30 | 31 | 1756-IB32 | Spare_DI_0 | Pin 31 | C4S2:31/C4S02-X2:31 | DI | 24VDC Dry Contact | SPARE | JB-612 | Packing Tower 2th Floor | C4S02-X2 | - | Spare | Spare Channel | -

C4-S02-P31 | 31 | 32 | 1756-IB32 | Spare_DI_0 | Pin 32 | C4S2:32/C4S02-X2:32 | DI | 24VDC Dry Contact | SPARE | JB-612 | Packing Tower 2th Floor | C4S02-X2 | - | Spare | Spare Channel | -

## C4 SLOT 03 — 1756-IB32 (DI)

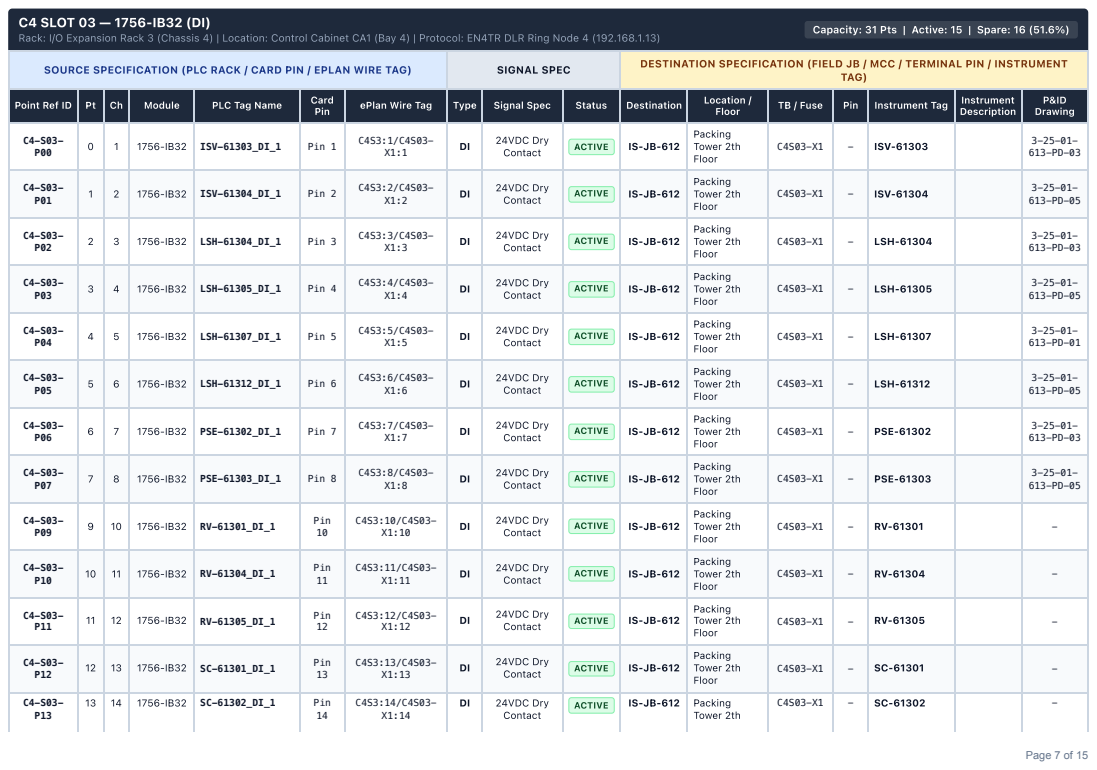
[picture p173: page 7]
Pin; 24VDC Dry; Contact; ACTIVE; Packing; Tower 2th

Capacity: 31 Pts | Active: 15 | Spare: 16 (51.6%)

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

C4-S03-P00 | 0 | 1 | 1756-IB32 | ISV-61303_DI_1 | Pin 1 | C4S3:1/C4S03-X1:1 | DI | 24VDC Dry Contact | ACTIVE | IS-JB-612 | Packing Tower 2th Floor | C4S03-X1 | - | ISV-61303 | | 3-25-01-613-PD-03

C4-S03-P01 | 1 | 2 | 1756-IB32 | ISV-61304_DI_1 | Pin 2 | C4S3:2/C4S03-X1:2 | DI | 24VDC Dry Contact | ACTIVE | IS-JB-612 | Packing Tower 2th Floor | C4S03-X1 | - | ISV-61304 | | 3-25-01-613-PD-05

C4-S03-P02 | 2 | 3 | 1756-IB32 | LSH-61304_DI_1 | Pin 3 | C4S3:3/C4S03-X1:3 | DI | 24VDC Dry Contact | ACTIVE | IS-JB-612 | Packing Tower 2th Floor | C4S03-X1 | - | LSH-61304 | | 3-25-01-613-PD-03

C4-S03-P03 | 3 | 4 | 1756-IB32 | LSH-61305_DI_1 | Pin 4 | C4S3:4/C4S03-X1:4 | DI | 24VDC Dry Contact | ACTIVE | IS-JB-612 | Packing Tower 2th Floor | C4S03-X1 | - | LSH-61305 | | 3-25-01-613-PD-05

C4-S03-P04 | 4 | 5 | 1756-IB32 | LSH-61307_DI_1 | Pin 5 | C4S3:5/C4S03-X1:5 | DI | 24VDC Dry Contact | ACTIVE | IS-JB-612 | Packing Tower 2th Floor | C4S03-X1 | - | LSH-61307 | | 3-25-01-613-PD-01

C4-S03-P05 | 5 | 6 | 1756-IB32 | LSH-61312_DI_1 | Pin 6 | C4S3:6/C4S03-X1:6 | DI | 24VDC Dry Contact | ACTIVE | IS-JB-612 | Packing Tower 2th Floor | C4S03-X1 | - | LSH-61312 | | 3-25-01-613-PD-05

C4-S03-P06 | 6 | 7 | 1756-IB32 | PSE-61302_DI_1 | Pin 7 | C4S3:7/C4S03-X1:7 | DI | 24VDC Dry Contact | ACTIVE | IS-JB-612 | Packing Tower 2th Floor | C4S03-X1 | - | PSE-61302 | | 3-25-01-613-PD-03

C4-S03-P07 | 7 | 8 | 1756-IB32 | PSE-61303_DI_1 | Pin 8 | C4S3:8/C4S03-X1:8 | DI | 24VDC Dry Contact | ACTIVE | IS-JB-612 | Packing Tower 2th Floor | C4S03-X1 | - | PSE-61303 | | 3-25-01-613-PD-05

C4-S03-P09 | 9 | 10 | 1756-IB32 | RV-61301_DI_1 | Pin 10 | C4S3:10/C4S03-X1:10 | DI | 24VDC Dry Contact | ACTIVE | IS-JB-612 | Packing Tower 2th Floor | C4S03-X1 | - | RV-61301 | | -

C4-S03-P10 | 10 | 11 | 1756-IB32 | RV-61304_DI_1 | Pin 11 | C4S3:11/C4S03-X1:11 | DI | 24VDC Dry Contact | ACTIVE | IS-JB-612 | Packing Tower 2th Floor | C4S03-X1 | - | RV-61304 | | -

C4-S03-P11 | 11 | 12 | 1756-IB32 | RV-61305_DI_1 | Pin 12 | C4S3:12/C4S03-X1:12 | DI | 24VDC Dry Contact | ACTIVE | IS-JB-612 | Packing Tower 2th Floor | C4S03-X1 | - | RV-61305 | | -

C4-S03-P12 | 12 | 13 | 1756-IB32 | SC-61301_DI_1 | Pin 13 | C4S3:13/C4S03-X1:13 | DI | 24VDC Dry Contact | ACTIVE | IS-JB-612 | Packing Tower 2th Floor | C4S03-X1 | - | SC-61301 | | -

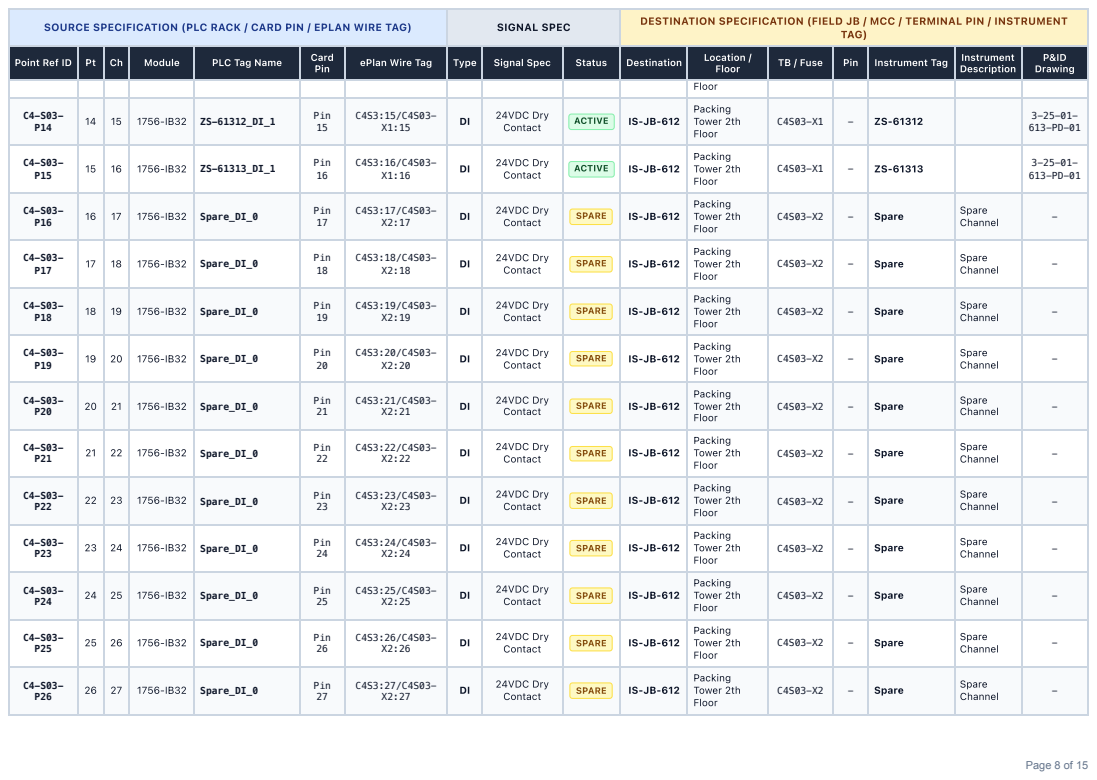
[picture p174: page 8]
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

Floor

C4-S03-P14 | 14 | 15 | 1756-IB32 | ZS-61312_DI_1 | Pin 15 | C4S3:15/C4S03-X1:15 | DI | 24VDC Dry Contact | ACTIVE | IS-JB-612 | Packing Tower 2th Floor | C4S03-X1 | - | ZS-61312 | | 3-25-01-613-PD-01

C4-S03-P15 | 15 | 16 | 1756-IB32 | ZS-61313_DI_1 | Pin 16 | C4S3:16/C4S03-X1:16 | DI | 24VDC Dry Contact | ACTIVE | IS-JB-612 | Packing Tower 2th Floor | C4S03-X1 | - | ZS-61313 | | 3-25-01-613-PD-01

C4-S03-P16 | 16 | 17 | 1756-IB32 | Spare_DI_0 | Pin 17 | C4S3:17/C4S03-X2:17 | DI | 24VDC Dry Contact | SPARE | IS-JB-612 | Packing Tower 2th Floor | C4S03-X2 | - | Spare | Spare Channel | -

C4-S03-P17 | 17 | 18 | 1756-IB32 | Spare_DI_0 | Pin 18 | C4S3:18/C4S03-X2:18 | DI | 24VDC Dry Contact | SPARE | IS-JB-612 | Packing Tower 2th Floor | C4S03-X2 | - | Spare | Spare Channel | -

C4-S03-P18 | 18 | 19 | 1756-IB32 | Spare_DI_0 | Pin 19 | C4S3:19/C4S03-X2:19 | DI | 24VDC Dry Contact | SPARE | IS-JB-612 | Packing Tower 2th Floor | C4S03-X2 | - | Spare | Spare Channel | -

C4-S03-P19 | 19 | 20 | 1756-IB32 | Spare_DI_0 | Pin 20 | C4S3:20/C4S03-X2:20 | DI | 24VDC Dry Contact | SPARE | IS-JB-612 | Packing Tower 2th Floor | C4S03-X2 | - | Spare | Spare Channel | -

C4-S03-P20 | 20 | 21 | 1756-IB32 | Spare_DI_0 | Pin 21 | C4S3:21/C4S03-X2:21 | DI | 24VDC Dry Contact | SPARE | IS-JB-612 | Packing Tower 2th Floor | C4S03-X2 | - | Spare | Spare Channel | -

C4-S03-P21 | 21 | 22 | 1756-IB32 | Spare_DI_0 | Pin 22 | C4S3:22/C4S03-X2:22 | DI | 24VDC Dry Contact | SPARE | IS-JB-612 | Packing Tower 2th Floor | C4S03-X2 | - | Spare | Spare Channel | -

C4-S03-P22 | 22 | 23 | 1756-IB32 | Spare_DI_0 | Pin 23 | C4S3:23/C4S03-X2:23 | DI | 24VDC Dry Contact | SPARE | IS-JB-612 | Packing Tower 2th Floor | C4S03-X2 | - | Spare | Spare Channel | -

C4-S03-P23 | 23 | 24 | 1756-IB32 | Spare_DI_0 | Pin 24 | C4S3:24/C4S03-X2:24 | DI | 24VDC Dry Contact | SPARE | IS-JB-612 | Packing Tower 2th Floor | C4S03-X2 | - | Spare | Spare Channel | -

C4-S03-P24 | 24 | 25 | 1756-IB32 | Spare_DI_0 | Pin 25 | C4S3:25/C4S03-X2:25 | DI | 24VDC Dry Contact | SPARE | IS-JB-612 | Packing Tower 2th Floor | C4S03-X2 | - | Spare | Spare Channel | -

C4-S03-P25 | 25 | 26 | 1756-IB32 | Spare_DI_0 | Pin 26 | C4S3:26/C4S03-X2:26 | DI | 24VDC Dry Contact | SPARE | IS-JB-612 | Packing Tower 2th Floor | C4S03-X2 | - | Spare | Spare Channel | -

C4-S03-P26 | 26 | 27 | 1756-IB32 | Spare_DI_0 | Pin 27 | C4S3:27/C4S03-X2:27 | DI | 24VDC Dry Contact | SPARE | IS-JB-612 | Packing Tower 2th Floor | C4S03-X2 | - | Spare | Spare Channel | -

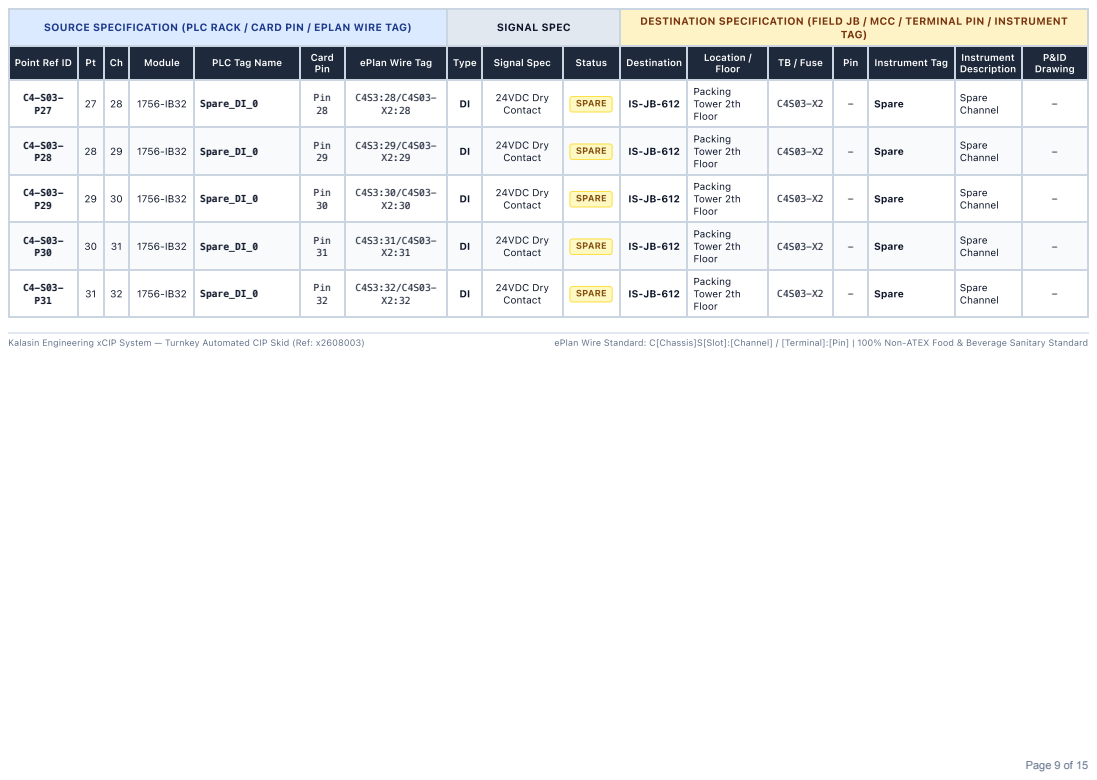
[picture p175: page 9]
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

C4-S03-P27 | 27 | 28 | 1756-IB32 | Spare_DI_0 | Pin 28 | C4S3:28/C4S03-X2:28 | DI | 24VDC Dry Contact | SPARE | IS-JB-612 | Packing Tower 2th Floor | C4S03-X2 | - | Spare | Spare Channel | -

C4-S03-P28 | 28 | 29 | 1756-IB32 | Spare_DI_0 | Pin 29 | C4S3:29/C4S03-X2:29 | DI | 24VDC Dry Contact | SPARE | IS-JB-612 | Packing Tower 2th Floor | C4S03-X2 | - | Spare | Spare Channel | -

C4-S03-P29 | 29 | 30 | 1756-IB32 | Spare_DI_0 | Pin 30 | C4S3:30/C4S03-X2:30 | DI | 24VDC Dry Contact | SPARE | IS-JB-612 | Packing Tower 2th Floor | C4S03-X2 | - | Spare | Spare Channel | -

C4-S03-P30 | 30 | 31 | 1756-IB32 | Spare_DI_0 | Pin 31 | C4S3:31/C4S03-X2:31 | DI | 24VDC Dry Contact | SPARE | IS-JB-612 | Packing Tower 2th Floor | C4S03-X2 | - | Spare | Spare Channel | -

C4-S03-P31 | 31 | 32 | 1756-IB32 | Spare_DI_0 | Pin 32 | C4S3:32/C4S03-X2:32 | DI | 24VDC Dry Contact | SPARE | IS-JB-612 | Packing Tower 2th Floor | C4S03-X2 | - | Spare | Spare Channel | -

## C4 SLOT 04 — 1756-OB32 (DO)

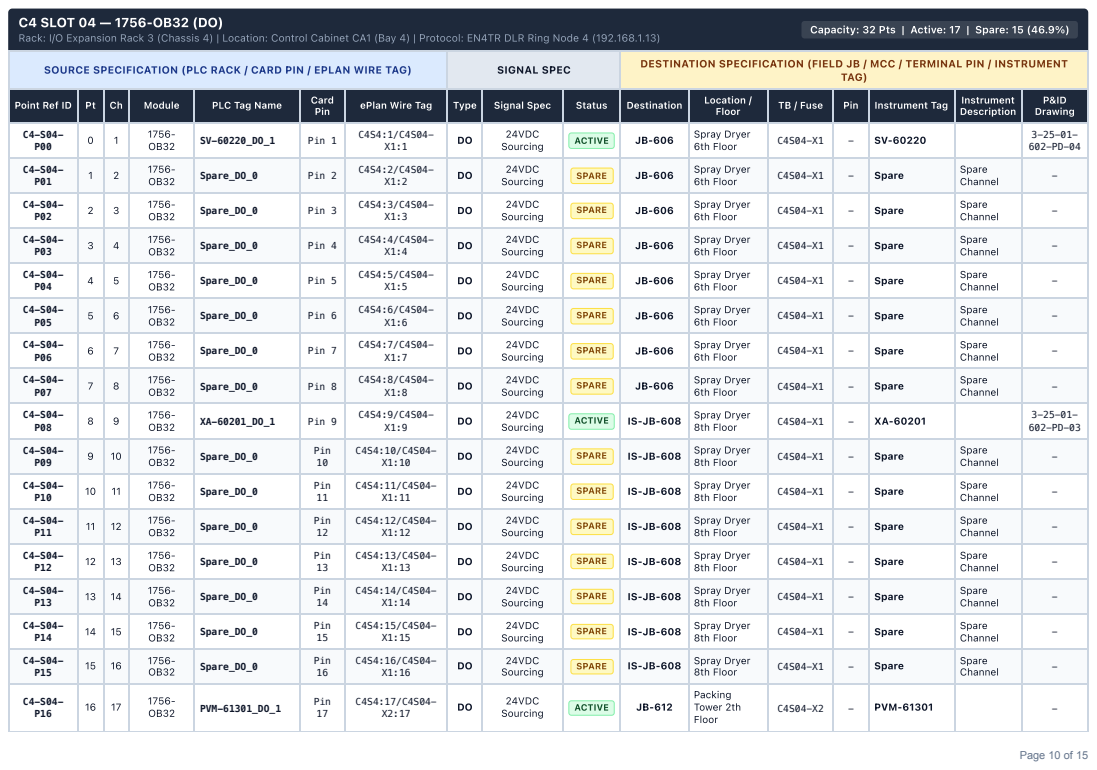
[picture p176: page 10]

Capacity: 32 Pts | Active: 17 | Spare: 15 (46.9%)

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

C4-S04-P00 | 0 | 1 | 1756-OB32 | SV-60220_DO_1 | Pin 1 | C4S4:1/C4S04-X1:1 | DO | 24VDC Sourcing | ACTIVE | JB-606 | Spray Dryer 6th Floor | C4S04-X1 | - | SV-60220 | | 3-25-01-602-PD-04

C4-S04-P01 | 1 | 2 | 1756-OB32 | Spare_DO_0 | Pin 2 | C4S4:2/C4S04-X1:2 | DO | 24VDC Sourcing | SPARE | JB-606 | Spray Dryer 6th Floor | C4S04-X1 | - | Spare | Spare Channel | -

C4-S04-P02 | 2 | 3 | 1756-OB32 | Spare_DO_0 | Pin 3 | C4S4:3/C4S04-X1:3 | DO | 24VDC Sourcing | SPARE | JB-606 | Spray Dryer 6th Floor | C4S04-X1 | - | Spare | Spare Channel | -

C4-S04-P03 | 3 | 4 | 1756-OB32 | Spare_DO_0 | Pin 4 | C4S4:4/C4S04-X1:4 | DO | 24VDC Sourcing | SPARE | JB-606 | Spray Dryer 6th Floor | C4S04-X1 | - | Spare | Spare Channel | -

C4-S04-P04 | 4 | 5 | 1756-OB32 | Spare_DO_0 | Pin 5 | C4S4:5/C4S04-X1:5 | DO | 24VDC Sourcing | SPARE | JB-606 | Spray Dryer 6th Floor | C4S04-X1 | - | Spare | Spare Channel | -

C4-S04-P05 | 5 | 6 | 1756-OB32 | Spare_DO_0 | Pin 6 | C4S4:6/C4S04-X1:6 | DO | 24VDC Sourcing | SPARE | JB-606 | Spray Dryer 6th Floor | C4S04-X1 | - | Spare | Spare Channel | -

C4-S04-P06 | 6 | 7 | 1756-OB32 | Spare_DO_0 | Pin 7 | C4S4:7/C4S04-X1:7 | DO | 24VDC Sourcing | SPARE | JB-606 | Spray Dryer 6th Floor | C4S04-X1 | - | Spare | Spare Channel | -

C4-S04-P07 | 7 | 8 | 1756-OB32 | Spare_DO_0 | Pin 8 | C4S4:8/C4S04-X1:8 | DO | 24VDC Sourcing | SPARE | JB-606 | Spray Dryer 6th Floor | C4S04-X1 | - | Spare | Spare Channel | -

C4-S04-P08 | 8 | 9 | 1756-OB32 | XA-60201_DO_1 | Pin 9 | C4S4:9/C4S04-X1:9 | DO | 24VDC Sourcing | ACTIVE | IS-JB-608 | Spray Dryer 8th Floor | C4S04-X1 | - | XA-60201 | | 3-25-01-602-PD-03

C4-S04-P09 | 9 | 10 | 1756-OB32 | Spare_DO_0 | Pin 10 | C4S4:10/C4S04-X1:10 | DO | 24VDC Sourcing | SPARE | IS-JB-608 | Spray Dryer 8th Floor | C4S04-X1 | - | Spare | Spare Channel | -

C4-S04-P10 | 10 | 11 | 1756-OB32 | Spare_DO_0 | Pin 11 | C4S4:11/C4S04-X1:11 | DO | 24VDC Sourcing | SPARE | IS-JB-608 | Spray Dryer 8th Floor | C4S04-X1 | - | Spare | Spare Channel | -

C4-S04-P11 | 11 | 12 | 1756-OB32 | Spare_DO_0 | Pin 12 | C4S4:12/C4S04-X1:12 | DO | 24VDC Sourcing | SPARE | IS-JB-608 | Spray Dryer 8th Floor | C4S04-X1 | - | Spare | Spare Channel | -

C4-S04-P12 | 12 | 13 | 1756-OB32 | Spare_DO_0 | Pin 13 | C4S4:13/C4S04-X1:13 | DO | 24VDC Sourcing | SPARE | IS-JB-608 | Spray Dryer 8th Floor | C4S04-X1 | - | Spare | Spare Channel | -

C4-S04-P13 | 13 | 14 | 1756-OB32 | Spare_DO_0 | Pin 14 | C4S4:14/C4S04-X1:14 | DO | 24VDC Sourcing | SPARE | IS-JB-608 | Spray Dryer 8th Floor | C4S04-X1 | - | Spare | Spare Channel | -

C4-S04-P14 | 14 | 15 | 1756-OB32 | Spare_DO_0 | Pin 15 | C4S4:15/C4S04-X1:15 | DO | 24VDC Sourcing | SPARE | IS-JB-608 | Spray Dryer 8th Floor | C4S04-X1 | - | Spare | Spare Channel | -

C4-S04-P15 | 15 | 16 | 1756-OB32 | Spare_DO_0 | Pin 16 | C4S4:16/C4S04-X1:16 | DO | 24VDC Sourcing | SPARE | IS-JB-608 | Spray Dryer 8th Floor | C4S04-X1 | - | Spare | Spare Channel | -

C4-S04-P16 | 16 | 17 | 1756-OB32 | PVM-61301_DO_1 | Pin 17 | C4S4:17/C4S04-X2:17 | DO | 24VDC Sourcing | ACTIVE | JB-612 | Packing Tower 2th Floor | C4S04-X2 | - | PVM-61301 | | -

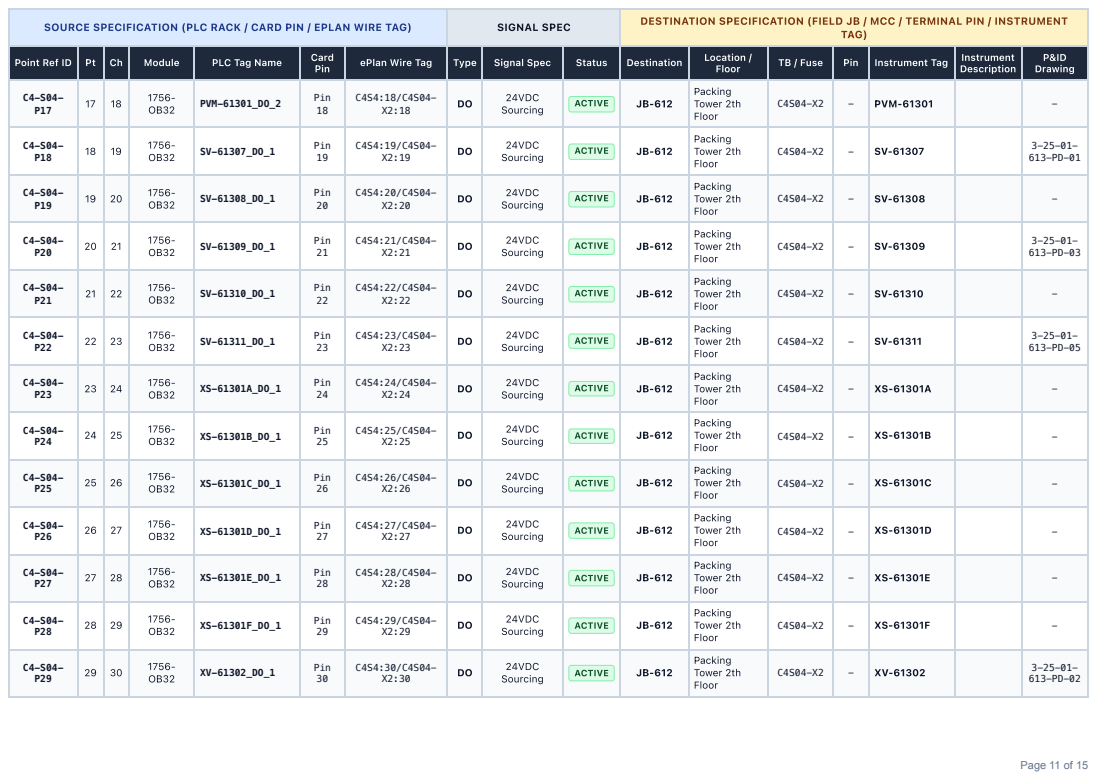
[picture p177: page 11]
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

C4-S04-P17 | 17 | 18 | 1756-OB32 | PVM-61301_DO_2 | Pin 18 | C4S4:18/C4S04-X2:18 | DO | 24VDC Sourcing | ACTIVE | JB-612 | Packing Tower 2th Floor | C4S04-X2 | - | PVM-61301 | | -

C4-S04-P18 | 18 | 19 | 1756-OB32 | SV-61307_DO_1 | Pin 19 | C4S4:19/C4S04-X2:19 | DO | 24VDC Sourcing | ACTIVE | JB-612 | Packing Tower 2th Floor | C4S04-X2 | - | SV-61307 | | 3-25-01-613-PD-01

C4-S04-P19 | 19 | 20 | 1756-OB32 | SV-61308_DO_1 | Pin 20 | C4S4:20/C4S04-X2:20 | DO | 24VDC Sourcing | ACTIVE | JB-612 | Packing Tower 2th Floor | C4S04-X2 | - | SV-61308 | | -

C4-S04-P20 | 20 | 21 | 1756-OB32 | SV-61309_DO_1 | Pin 21 | C4S4:21/C4S04-X2:21 | DO | 24VDC Sourcing | ACTIVE | JB-612 | Packing Tower 2th Floor | C4S04-X2 | - | SV-61309 | | 3-25-01-613-PD-03

C4-S04-P21 | 21 | 22 | 1756-OB32 | SV-61310_DO_1 | Pin 22 | C4S4:22/C4S04-X2:22 | DO | 24VDC Sourcing | ACTIVE | JB-612 | Packing Tower 2th Floor | C4S04-X2 | - | SV-61310 | | -

C4-S04-P22 | 22 | 23 | 1756-OB32 | SV-61311_DO_1 | Pin 23 | C4S4:23/C4S04-X2:23 | DO | 24VDC Sourcing | ACTIVE | JB-612 | Packing Tower 2th Floor | C4S04-X2 | - | SV-61311 | | 3-25-01-613-PD-05

C4-S04-P23 | 23 | 24 | 1756-OB32 | XS-61301A_DO_1 | Pin 24 | C4S4:24/C4S04-X2:24 | DO | 24VDC Sourcing | ACTIVE | JB-612 | Packing Tower 2th Floor | C4S04-X2 | - | XS-61301A | | -

C4-S04-P24 | 24 | 25 | 1756-OB32 | XS-61301B_DO_1 | Pin 25 | C4S4:25/C4S04-X2:25 | DO | 24VDC Sourcing | ACTIVE | JB-612 | Packing Tower 2th Floor | C4S04-X2 | - | XS-61301B | | -

C4-S04-P25 | 25 | 26 | 1756-OB32 | XS-61301C_DO_1 | Pin 26 | C4S4:26/C4S04-X2:26 | DO | 24VDC Sourcing | ACTIVE | JB-612 | Packing Tower 2th Floor | C4S04-X2 | - | XS-61301C | | -

C4-S04-P26 | 26 | 27 | 1756-OB32 | XS-61301D_DO_1 | Pin 27 | C4S4:27/C4S04-X2:27 | DO | 24VDC Sourcing | ACTIVE | JB-612 | Packing Tower 2th Floor | C4S04-X2 | - | XS-61301D | | -

C4-S04-P27 | 27 | 28 | 1756-OB32 | XS-61301E_DO_1 | Pin 28 | C4S4:28/C4S04-X2:28 | DO | 24VDC Sourcing | ACTIVE | JB-612 | Packing Tower 2th Floor | C4S04-X2 | - | XS-61301E | | -

C4-S04-P28 | 28 | 29 | 1756-OB32 | XS-61301F_DO_1 | Pin 29 | C4S4:29/C4S04-X2:29 | DO | 24VDC Sourcing | ACTIVE | JB-612 | Packing Tower 2th Floor | C4S04-X2 | - | XS-61301F | | -

C4-S04-P29 | 29 | 30 | 1756-OB32 | XV-61302_DO_1 | Pin 30 | C4S4:30/C4S04-X2:30 | DO | 24VDC Sourcing | ACTIVE | JB-612 | Packing Tower 2th Floor | C4S04-X2 | - | XV-61302 | | 3-25-01-613-PD-02

Point Ref ID | Pt | Ch | Module | PLC Tag Name | Card Pin | ePlan Wire Tag | Type | Signal Spec | Status | Destination | Location / Floor | TB / Fuse | Pin | Instrument Tag | Instrument Description | P&ID Drawing
C4-S04-P30 | 30 | 31 | 1756-OB32 | XV-61303_DO_1 | Pin 31 | C4S4:31/C4S04-X2:31 | DO | 24VDC Sourcing | ACTIVE | JB-612 | Packing Tower 2th Floor | C4S04-X2 | - | XV-61303 | | 3-25-01-613-PD-02
C4-S04-P31 | 31 | 32 | 1756-OB32 | Spare_DO_0 | Pin 32 | C4S4:32/C4S04-X2:32 | DO | 24VDC Sourcing | SPARE | JB-612 | Packing Tower 2th Floor | C4S04-X2 | - | Spare | Spare Channel | -
Kalasin Engineering xCIP System — Turnkey Automated CIP Skid (Ref: x2608003) | ePlan Wire Standard: C[Chassis]S[Slot]:[Channel] / [Terminal]:[Pin] | 100% Non-ATEX Food & Beverage Sanitary Standard
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
