x92120/x260911-002-KalasinEngineering/02_Electrical_and_eDrawing/04_PDF_Reports_and_Drawings/Chassis_C5_Slots_IO_Report.pdf

# KALASIN ENGINEERING — C5(REMOTE I/O SKID RIO-200(CHASSIS5))

C5

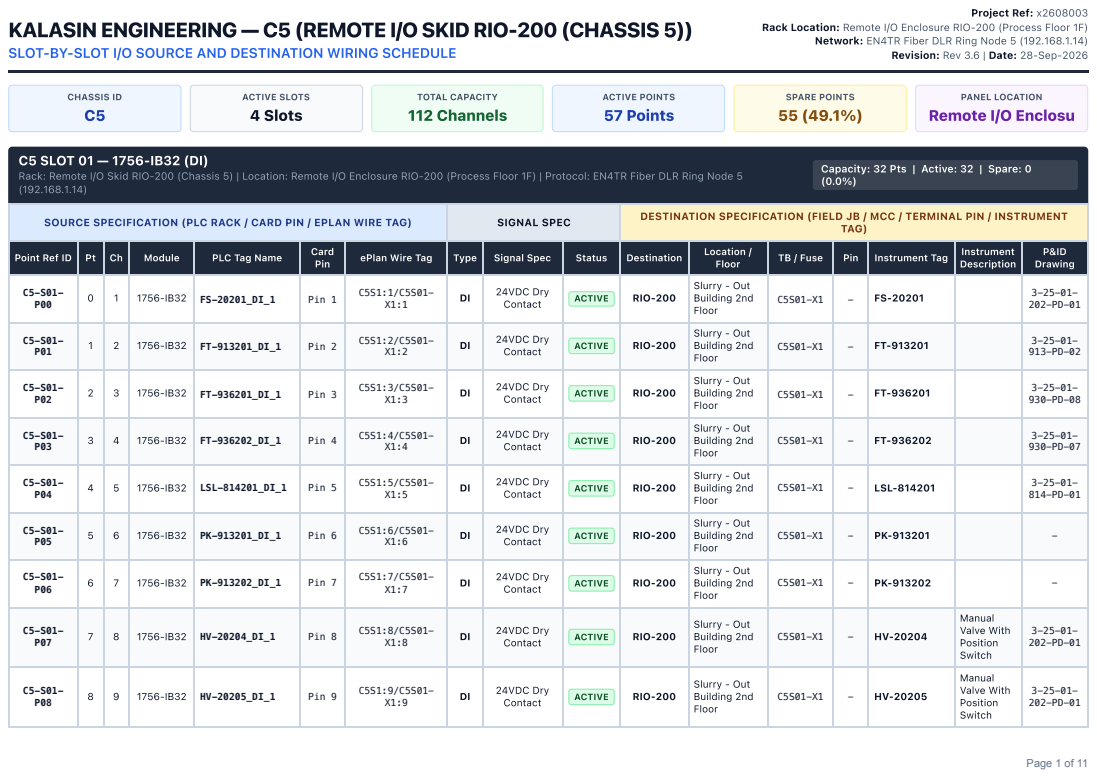
[picture p178: page 1]
Project Ref: x2608003; CHASSIS ID; ACTIVE SLOTS 4 Slots; TOTAL CAPACITY 112 Channels; ACTIVE POINTS 57 Points; SPARE POINTS 55 (49.1%); PANEL LOCATION Remote I/O Enclosu

Rack Location: Remote I/O Enclosure RIO-200 (Process Floor 1F)

Network: EN4TR Fiber DLR Ring Node 5 (192.168.1.14)

SLOT-BY-SLOT I/O SOURCE AND DESTINATION WIRING SCHEDULE

Revision: Rev 3.6 | Date: 28-Sep-2026

C5 SLOT 01 — 1756-IB32 (DI)
Rack: Remote I/O Skid RIO-200 (Chassis 5) | Location: Remote I/O Enclosure RIO-200 (Process Floor 1F) | Protocol: EN4TR Fiber DLR Ring Node 5

Capacity: 32 Pts | Active: 32 | Spare: 0

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

C5-S01-P00 | 0 | 1 | 1756-IB32 | FS-20201_DI_1 | Pin 1 | C5S1:1/C5S01-X1:1 | DI | 24VDC Dry Contact | ACTIVE | RIO-200 | Slurry - Out Building 2nd Floor | C5S01-X1 | - | FS-20201 | | 3-25-01-202-PD-01

C5-S01-P01 | 1 | 2 | 1756-IB32 | FT-913201_DI_1 | Pin 2 | C5S1:2/C5S01-X1:2 | DI | 24VDC Dry Contact | ACTIVE | RIO-200 | Slurry - Out Building 2nd Floor | C5S01-X1 | - | FT-913201 | | 3-25-01-913-PD-02

C5-S01-P02 | 2 | 3 | 1756-IB32 | FT-936201_DI_1 | Pin 3 | C5S1:3/C5S01-X1:3 | DI | 24VDC Dry Contact | ACTIVE | RIO-200 | Slurry - Out Building 2nd Floor | C5S01-X1 | - | FT-936201 | | 3-25-01-930-PD-08

C5-S01-P03 | 3 | 4 | 1756-IB32 | FT-936202_DI_1 | Pin 4 | C5S1:4/C5S01-X1:4 | DI | 24VDC Dry Contact | ACTIVE | RIO-200 | Slurry - Out Building 2nd Floor | C5S01-X1 | - | FT-936202 | | 3-25-01-930-PD-07

C5-S01-P04 | 4 | 5 | 1756-IB32 | LSL-814201_DI_1 | Pin 5 | C5S1:5/C5S01-X1:5 | DI | 24VDC Dry Contact | ACTIVE | RIO-200 | Slurry - Out Building 2nd Floor | C5S01-X1 | - | LSL-814201 | | 3-25-01-814-PD-01

C5-S01-P05 | 5 | 6 | 1756-IB32 | PK-913201_DI_1 | Pin 6 | C5S1:6/C5S01-X1:6 | DI | 24VDC Dry Contact | ACTIVE | RIO-200 | Slurry - Out Building 2nd Floor | C5S01-X1 | - | PK-913201 | | -

C5-S01-P06 | 6 | 7 | 1756-IB32 | PK-913202_DI_1 | Pin 7 | C5S1:7/C5S01-X1:7 | DI | 24VDC Dry Contact | ACTIVE | RIO-200 | Slurry - Out Building 2nd Floor | C5S01-X1 | - | PK-913202 | | -

C5-S01-P07 | 7 | 8 | 1756-IB32 | HV-20204_DI_1 | Pin 8 | C5S1:8/C5S01-X1:8 | DI | 24VDC Dry Contact | ACTIVE | RIO-200 | Slurry - Out Building 2nd Floor | C5S01-X1 | - | HV-20204 | Manual Valve With Position Switch | 3-25-01-202-PD-01

C5-S01-P08 | 8 | 9 | 1756-IB32 | HV-20205_DI_1 | Pin 9 | C5S1:9/C5S01-X1:9 | DI | 24VDC Dry Contact | ACTIVE | RIO-200 | Slurry - Out Building 2nd Floor | C5S01-X1 | - | HV-20205 | Manual Valve With Position Switch | 3-25-01-202-PD-01

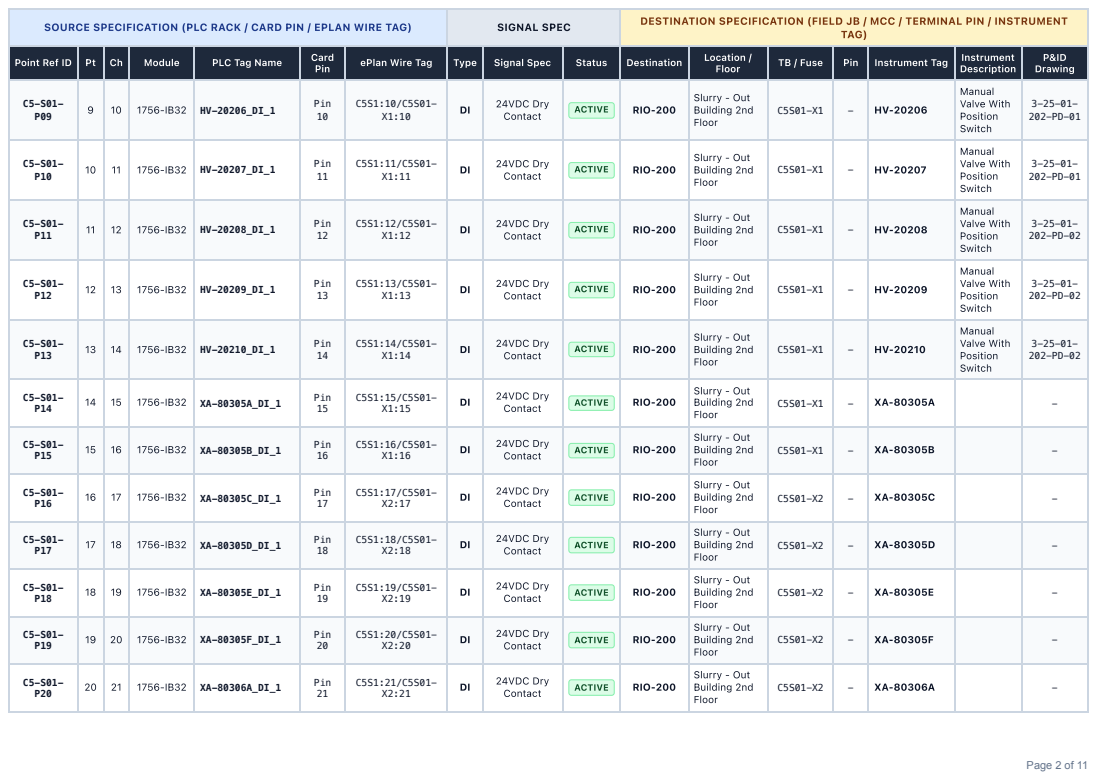
[picture p179: page 2]
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

C5-S01-P09 | 9 | 10 | 1756-IB32 | HV-20206_DI_1 | Pin 10 | C5S1:10/C5S01-X1:10 | DI | 24VDC Dry Contact | ACTIVE | RIO-200 | Slurry - Out Building 2nd Floor | C5S01-X1 | - | HV-20206 | Manual Valve With Position Switch | 3-25-01-202-PD-01

C5-S01-P10 | 10 | 11 | 1756-IB32 | HV-20207_DI_1 | Pin 11 | C5S1:11/C5S01-X1:11 | DI | 24VDC Dry Contact | ACTIVE | RIO-200 | Slurry - Out Building 2nd Floor | C5S01-X1 | - | HV-20207 | Manual Valve With Position Switch | 3-25-01-202-PD-01

C5-S01-P11 | 11 | 12 | 1756-IB32 | HV-20208_DI_1 | Pin 12 | C5S1:12/C5S01-X1:12 | DI | 24VDC Dry Contact | ACTIVE | RIO-200 | Slurry - Out Building 2nd Floor | C5S01-X1 | - | HV-20208 | Manual Valve With Position Switch | 3-25-01-202-PD-02

C5-S01-P12 | 12 | 13 | 1756-IB32 | HV-20209_DI_1 | Pin 13 | C5S1:13/C5S01-X1:13 | DI | 24VDC Dry Contact | ACTIVE | RIO-200 | Slurry - Out Building 2nd Floor | C5S01-X1 | - | HV-20209 | Manual Valve With Position Switch | 3-25-01-202-PD-02

C5-S01-P13 | 13 | 14 | 1756-IB32 | HV-20210_DI_1 | Pin 14 | C5S1:14/C5S01-X1:14 | DI | 24VDC Dry Contact | ACTIVE | RIO-200 | Slurry - Out Building 2nd Floor | C5S01-X1 | - | HV-20210 | Manual Valve With Position Switch | 3-25-01-202-PD-02

C5-S01-P14 | 14 | 15 | 1756-IB32 | XA-80305A_DI_1 | Pin 15 | C5S1:15/C5S01-X1:15 | DI | 24VDC Dry Contact | ACTIVE | RIO-200 | Slurry - Out Building 2nd Floor | C5S01-X1 | - | XA-80305A | | -

C5-S01-P15 | 15 | 16 | 1756-IB32 | XA-80305B_DI_1 | Pin 16 | C5S1:16/C5S01-X1:16 | DI | 24VDC Dry Contact | ACTIVE | RIO-200 | Slurry - Out Building 2nd Floor | C5S01-X1 | - | XA-80305B | | -

C5-S01-P16 | 16 | 17 | 1756-IB32 | XA-80305C_DI_1 | Pin 17 | C5S1:17/C5S01-X2:17 | DI | 24VDC Dry Contact | ACTIVE | RIO-200 | Slurry - Out Building 2nd Floor | C5S01-X2 | - | XA-80305C | | -

C5-S01-P17 | 17 | 18 | 1756-IB32 | XA-80305D_DI_1 | Pin 18 | C5S1:18/C5S01-X2:18 | DI | 24VDC Dry Contact | ACTIVE | RIO-200 | Slurry - Out Building 2nd Floor | C5S01-X2 | - | XA-80305D | | -

C5-S01-P18 | 18 | 19 | 1756-IB32 | XA-80305E_DI_1 | Pin 19 | C5S1:19/C5S01-X2:19 | DI | 24VDC Dry Contact | ACTIVE | RIO-200 | Slurry - Out Building 2nd Floor | C5S01-X2 | - | XA-80305E | | -

C5-S01-P19 | 19 | 20 | 1756-IB32 | XA-80305F_DI_1 | Pin 20 | C5S1:20/C5S01-X2:20 | DI | 24VDC Dry Contact | ACTIVE | RIO-200 | Slurry - Out Building 2nd Floor | C5S01-X2 | - | XA-80305F | | -

C5-S01-P20 | 20 | 21 | 1756-IB32 | XA-80306A_DI_1 | Pin 21 | C5S1:21/C5S01-X2:21 | DI | 24VDC Dry Contact | ACTIVE | RIO-200 | Slurry - Out Building 2nd Floor | C5S01-X2 | - | XA-80306A | | -

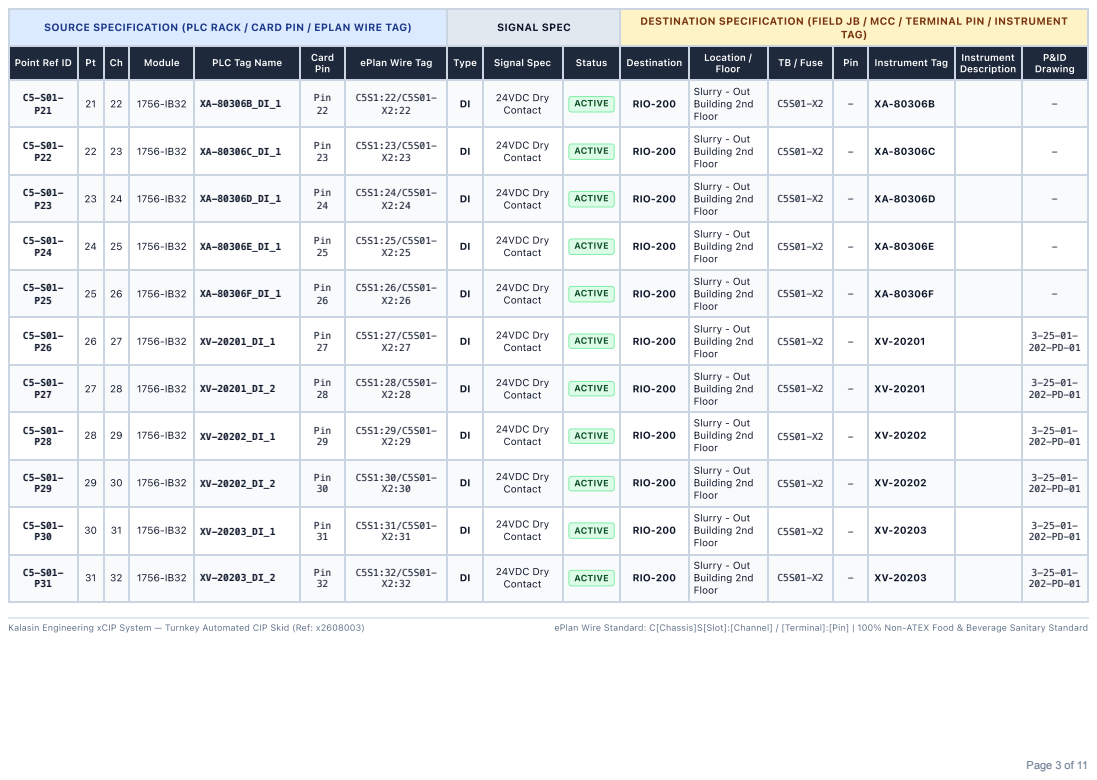
[picture p180: page 3]
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

C5-S01-P21 | 21 | 22 | 1756-IB32 | XA-80306B_DI_1 | Pin 22 | C5S1:22/C5S01-X2:22 | DI | 24VDC Dry Contact | ACTIVE | RIO-200 | Slurry - Out Building 2nd Floor | C5S01-X2 | - | XA-80306B | | -

C5-S01-P22 | 22 | 23 | 1756-IB32 | XA-80306C_DI_1 | Pin 23 | C5S1:23/C5S01-X2:23 | DI | 24VDC Dry Contact | ACTIVE | RIO-200 | Slurry - Out Building 2nd Floor | C5S01-X2 | - | XA-80306C | | -

C5-S01-P23 | 23 | 24 | 1756-IB32 | XA-80306D_DI_1 | Pin 24 | C5S1:24/C5S01-X2:24 | DI | 24VDC Dry Contact | ACTIVE | RIO-200 | Slurry - Out Building 2nd Floor | C5S01-X2 | - | XA-80306D | | -

C5-S01-P24 | 24 | 25 | 1756-IB32 | XA-80306E_DI_1 | Pin 25 | C5S1:25/C5S01-X2:25 | DI | 24VDC Dry Contact | ACTIVE | RIO-200 | Slurry - Out Building 2nd Floor | C5S01-X2 | - | XA-80306E | | -

C5-S01-P25 | 25 | 26 | 1756-IB32 | XA-80306F_DI_1 | Pin 26 | C5S1:26/C5S01-X2:26 | DI | 24VDC Dry Contact | ACTIVE | RIO-200 | Slurry - Out Building 2nd Floor | C5S01-X2 | - | XA-80306F | | -

C5-S01-P26 | 26 | 27 | 1756-IB32 | XV-20201_DI_1 | Pin 27 | C5S1:27/C5S01-X2:27 | DI | 24VDC Dry Contact | ACTIVE | RIO-200 | Slurry - Out Building 2nd Floor | C5S01-X2 | - | XV-20201 | | 3-25-01-202-PD-01

C5-S01-P27 | 27 | 28 | 1756-IB32 | XV-20201_DI_2 | Pin 28 | C5S1:28/C5S01-X2:28 | DI | 24VDC Dry Contact | ACTIVE | RIO-200 | Slurry - Out Building 2nd Floor | C5S01-X2 | - | XV-20201 | | 3-25-01-202-PD-01

C5-S01-P28 | 28 | 29 | 1756-IB32 | XV-20202_DI_1 | Pin 29 | C5S1:29/C5S01-X2:29 | DI | 24VDC Dry Contact | ACTIVE | RIO-200 | Slurry - Out Building 2nd Floor | C5S01-X2 | - | XV-20202 | | 3-25-01-202-PD-01

C5-S01-P29 | 29 | 30 | 1756-IB32 | XV-20202_DI_2 | Pin 30 | C5S1:30/C5S01-X2:30 | DI | 24VDC Dry Contact | ACTIVE | RIO-200 | Slurry - Out Building 2nd Floor | C5S01-X2 | - | XV-20202 | | 3-25-01-202-PD-01

C5-S01-P30 | 30 | 31 | 1756-IB32 | XV-20203_DI_1 | Pin 31 | C5S1:31/C5S01-X2:31 | DI | 24VDC Dry Contact | ACTIVE | RIO-200 | Slurry - Out Building 2nd Floor | C5S01-X2 | - | XV-20203 | | 3-25-01-202-PD-01

C5-S01-P31 | 31 | 32 | 1756-IB32 | XV-20203_DI_2 | Pin 32 | C5S1:32/C5S01-X2:32 | DI | 24VDC Dry Contact | ACTIVE | RIO-200 | Slurry - Out Building 2nd Floor | C5S01-X2 | - | XV-20203 | | 3-25-01-202-PD-01

## C5 SLOT 02 — 1756-IB32 (DI)

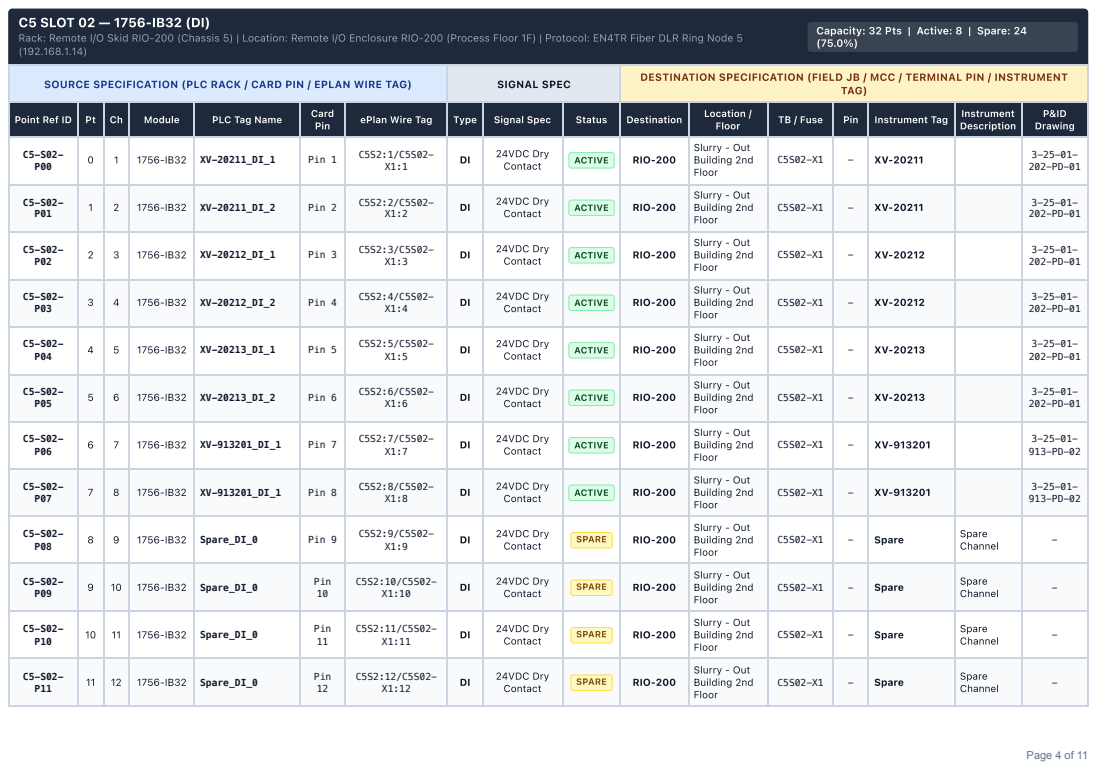
[picture p181: page 4]

Capacity: 32 Pts | Active: 8 | Spare: 24

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

C5-S02-P00 | 0 | 1 | 1756-IB32 | XV-20211_DI_1 | Pin 1 | C5S2:1/C5S02-X1:1 | DI | 24VDC Dry Contact | ACTIVE | RIO-200 | Slurry - Out Building 2nd Floor | C5S02-X1 | - | XV-20211 | | 3-25-01-202-PD-01

C5-S02-P01 | 1 | 2 | 1756-IB32 | XV-20211_DI_2 | Pin 2 | C5S2:2/C5S02-X1:2 | DI | 24VDC Dry Contact | ACTIVE | RIO-200 | Slurry - Out Building 2nd Floor | C5S02-X1 | - | XV-20211 | | 3-25-01-202-PD-01

C5-S02-P02 | 2 | 3 | 1756-IB32 | XV-20212_DI_1 | Pin 3 | C5S2:3/C5S02-X1:3 | DI | 24VDC Dry Contact | ACTIVE | RIO-200 | Slurry - Out Building 2nd Floor | C5S02-X1 | - | XV-20212 | | 3-25-01-202-PD-01

C5-S02-P03 | 3 | 4 | 1756-IB32 | XV-20212_DI_2 | Pin 4 | C5S2:4/C5S02-X1:4 | DI | 24VDC Dry Contact | ACTIVE | RIO-200 | Slurry - Out Building 2nd Floor | C5S02-X1 | - | XV-20212 | | 3-25-01-202-PD-01

C5-S02-P04 | 4 | 5 | 1756-IB32 | XV-20213_DI_1 | Pin 5 | C5S2:5/C5S02-X1:5 | DI | 24VDC Dry Contact | ACTIVE | RIO-200 | Slurry - Out Building 2nd Floor | C5S02-X1 | - | XV-20213 | | 3-25-01-202-PD-01

C5-S02-P05 | 5 | 6 | 1756-IB32 | XV-20213_DI_2 | Pin 6 | C5S2:6/C5S02-X1:6 | DI | 24VDC Dry Contact | ACTIVE | RIO-200 | Slurry - Out Building 2nd Floor | C5S02-X1 | - | XV-20213 | | 3-25-01-202-PD-01

C5-S02-P06 | 6 | 7 | 1756-IB32 | XV-913201_DI_1 | Pin 7 | C5S2:7/C5S02-X1:7 | DI | 24VDC Dry Contact | ACTIVE | RIO-200 | Slurry - Out Building 2nd Floor | C5S02-X1 | - | XV-913201 | | 3-25-01-913-PD-02

C5-S02-P07 | 7 | 8 | 1756-IB32 | XV-913201_DI_1 | Pin 8 | C5S2:8/C5S02-X1:8 | DI | 24VDC Dry Contact | ACTIVE | RIO-200 | Slurry - Out Building 2nd Floor | C5S02-X1 | - | XV-913201 | | 3-25-01-913-PD-02

C5-S02-P08 | 8 | 9 | 1756-IB32 | Spare_DI_0 | Pin 9 | C5S2:9/C5S02-X1:9 | DI | 24VDC Dry Contact | SPARE | RIO-200 | Slurry - Out Building 2nd Floor | C5S02-X1 | - | Spare | Spare Channel | -

C5-S02-P09 | 9 | 10 | 1756-IB32 | Spare_DI_0 | Pin 10 | C5S2:10/C5S02-X1:10 | DI | 24VDC Dry Contact | SPARE | RIO-200 | Slurry - Out Building 2nd Floor | C5S02-X1 | - | Spare | Spare Channel | -

C5-S02-P10 | 10 | 11 | 1756-IB32 | Spare_DI_0 | Pin 11 | C5S2:11/C5S02-X1:11 | DI | 24VDC Dry Contact | SPARE | RIO-200 | Slurry - Out Building 2nd Floor | C5S02-X1 | - | Spare | Spare Channel | -

C5-S02-P11 | 11 | 12 | 1756-IB32 | Spare_DI_0 | Pin 12 | C5S2:12/C5S02-X1:12 | DI | 24VDC Dry Contact | SPARE | RIO-200 | Slurry - Out Building 2nd Floor | C5S02-X1 | - | Spare | Spare Channel | -

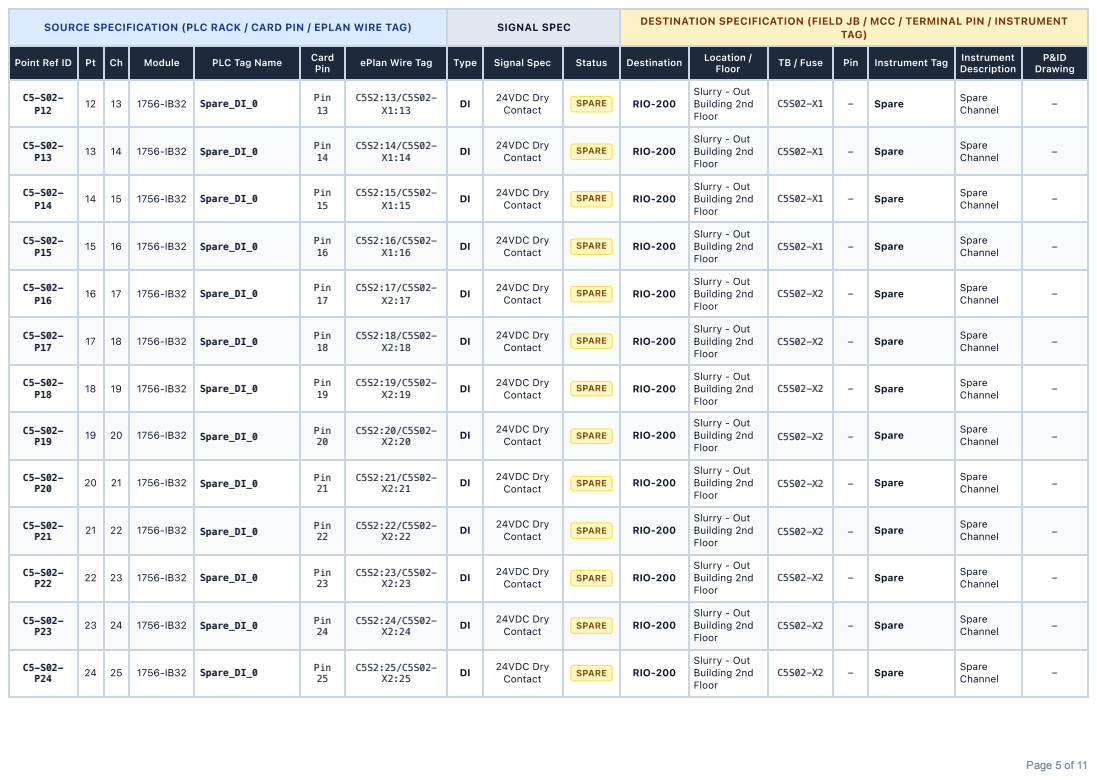
[picture p182: page 5]
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

C5-S02-P12 | 12 | 13 | 1756-IB32 | Spare_DI_0 | Pin 13 | C5S2:13/C5S02-X1:13 | DI | 24VDC Dry Contact | SPARE | RIO-200 | Slurry - Out Building 2nd Floor | C5S02-X1 | - | Spare | Spare Channel | -

C5-S02-P13 | 13 | 14 | 1756-IB32 | Spare_DI_0 | Pin 14 | C5S2:14/C5S02-X1:14 | DI | 24VDC Dry Contact | SPARE | RIO-200 | Slurry - Out Building 2nd Floor | C5S02-X1 | - | Spare | Spare Channel | -

C5-S02-P14 | 14 | 15 | 1756-IB32 | Spare_DI_0 | Pin 15 | C5S2:15/C5S02-X1:15 | DI | 24VDC Dry Contact | SPARE | RIO-200 | Slurry - Out Building 2nd Floor | C5S02-X1 | - | Spare | Spare Channel | -

C5-S02-P15 | 15 | 16 | 1756-IB32 | Spare_DI_0 | Pin 16 | C5S2:16/C5S02-X1:16 | DI | 24VDC Dry Contact | SPARE | RIO-200 | Slurry - Out Building 2nd Floor | C5S02-X1 | - | Spare | Spare Channel | -

C5-S02-P16 | 16 | 17 | 1756-IB32 | Spare_DI_0 | Pin 17 | C5S2:17/C5S02-X2:17 | DI | 24VDC Dry Contact | SPARE | RIO-200 | Slurry - Out Building 2nd Floor | C5S02-X2 | - | Spare | Spare Channel | -

C5-S02-P17 | 17 | 18 | 1756-IB32 | Spare_DI_0 | Pin 18 | C5S2:18/C5S02-X2:18 | DI | 24VDC Dry Contact | SPARE | RIO-200 | Slurry - Out Building 2nd Floor | C5S02-X2 | - | Spare | Spare Channel | -

C5-S02-P18 | 18 | 19 | 1756-IB32 | Spare_DI_0 | Pin 19 | C5S2:19/C5S02-X2:19 | DI | 24VDC Dry Contact | SPARE | RIO-200 | Slurry - Out Building 2nd Floor | C5S02-X2 | - | Spare | Spare Channel | -

C5-S02-P19 | 19 | 20 | 1756-IB32 | Spare_DI_0 | Pin 20 | C5S2:20/C5S02-X2:20 | DI | 24VDC Dry Contact | SPARE | RIO-200 | Slurry - Out Building 2nd Floor | C5S02-X2 | - | Spare | Spare Channel | -

C5-S02-P20 | 20 | 21 | 1756-IB32 | Spare_DI_0 | Pin 21 | C5S2:21/C5S02-X2:21 | DI | 24VDC Dry Contact | SPARE | RIO-200 | Slurry - Out Building 2nd Floor | C5S02-X2 | - | Spare | Spare Channel | -

C5-S02-P21 | 21 | 22 | 1756-IB32 | Spare_DI_0 | Pin 22 | C5S2:22/C5S02-X2:22 | DI | 24VDC Dry Contact | SPARE | RIO-200 | Slurry - Out Building 2nd Floor | C5S02-X2 | - | Spare | Spare Channel | -

C5-S02-P22 | 22 | 23 | 1756-IB32 | Spare_DI_0 | Pin 23 | C5S2:23/C5S02-X2:23 | DI | 24VDC Dry Contact | SPARE | RIO-200 | Slurry - Out Building 2nd Floor | C5S02-X2 | - | Spare | Spare Channel | -

C5-S02-P23 | 23 | 24 | 1756-IB32 | Spare_DI_0 | Pin 24 | C5S2:24/C5S02-X2:24 | DI | 24VDC Dry Contact | SPARE | RIO-200 | Slurry - Out Building 2nd Floor | C5S02-X2 | - | Spare | Spare Channel | -

C5-S02-P24 | 24 | 25 | 1756-IB32 | Spare_DI_0 | Pin 25 | C5S2:25/C5S02-X2:25 | DI | 24VDC Dry Contact | SPARE | RIO-200 | Slurry - Out Building 2nd Floor | C5S02-X2 | - | Spare | Spare Channel | -

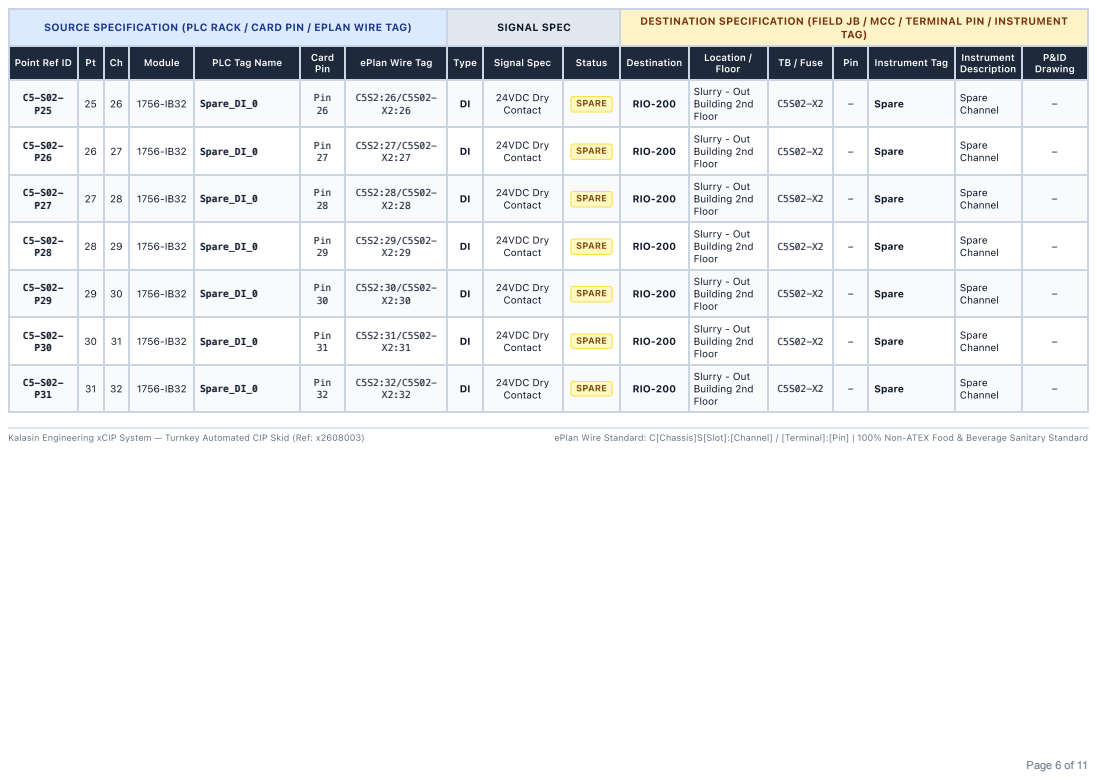
[picture p183: page 6]
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

C5-S02-P25 | 25 | 26 | 1756-IB32 | Spare_DI_0 | Pin 26 | C5S2:26/C5S02-X2:26 | DI | 24VDC Dry Contact | SPARE | RIO-200 | Slurry - Out Building 2nd Floor | C5S02-X2 | - | Spare | Spare Channel | -

C5-S02-P26 | 26 | 27 | 1756-IB32 | Spare_DI_0 | Pin 27 | C5S2:27/C5S02-X2:27 | DI | 24VDC Dry Contact | SPARE | RIO-200 | Slurry - Out Building 2nd Floor | C5S02-X2 | - | Spare | Spare Channel | -

C5-S02-P27 | 27 | 28 | 1756-IB32 | Spare_DI_0 | Pin 28 | C5S2:28/C5S02-X2:28 | DI | 24VDC Dry Contact | SPARE | RIO-200 | Slurry - Out Building 2nd Floor | C5S02-X2 | - | Spare | Spare Channel | -

C5-S02-P28 | 28 | 29 | 1756-IB32 | Spare_DI_0 | Pin 29 | C5S2:29/C5S02-X2:29 | DI | 24VDC Dry Contact | SPARE | RIO-200 | Slurry - Out Building 2nd Floor | C5S02-X2 | - | Spare | Spare Channel | -

C5-S02-P29 | 29 | 30 | 1756-IB32 | Spare_DI_0 | Pin 30 | C5S2:30/C5S02-X2:30 | DI | 24VDC Dry Contact | SPARE | RIO-200 | Slurry - Out Building 2nd Floor | C5S02-X2 | - | Spare | Spare Channel | -

C5-S02-P30 | 30 | 31 | 1756-IB32 | Spare_DI_0 | Pin 31 | C5S2:31/C5S02-X2:31 | DI | 24VDC Dry Contact | SPARE | RIO-200 | Slurry - Out Building 2nd Floor | C5S02-X2 | - | Spare | Spare Channel | -

C5-S02-P31 | 31 | 32 | 1756-IB32 | Spare_DI_0 | Pin 32 | C5S2:32/C5S02-X2:32 | DI | 24VDC Dry Contact | SPARE | RIO-200 | Slurry - Out Building 2nd Floor | C5S02-X2 | - | Spare | Spare Channel | -

## C5 SLOT 03 — 1756-OB32 (DO)

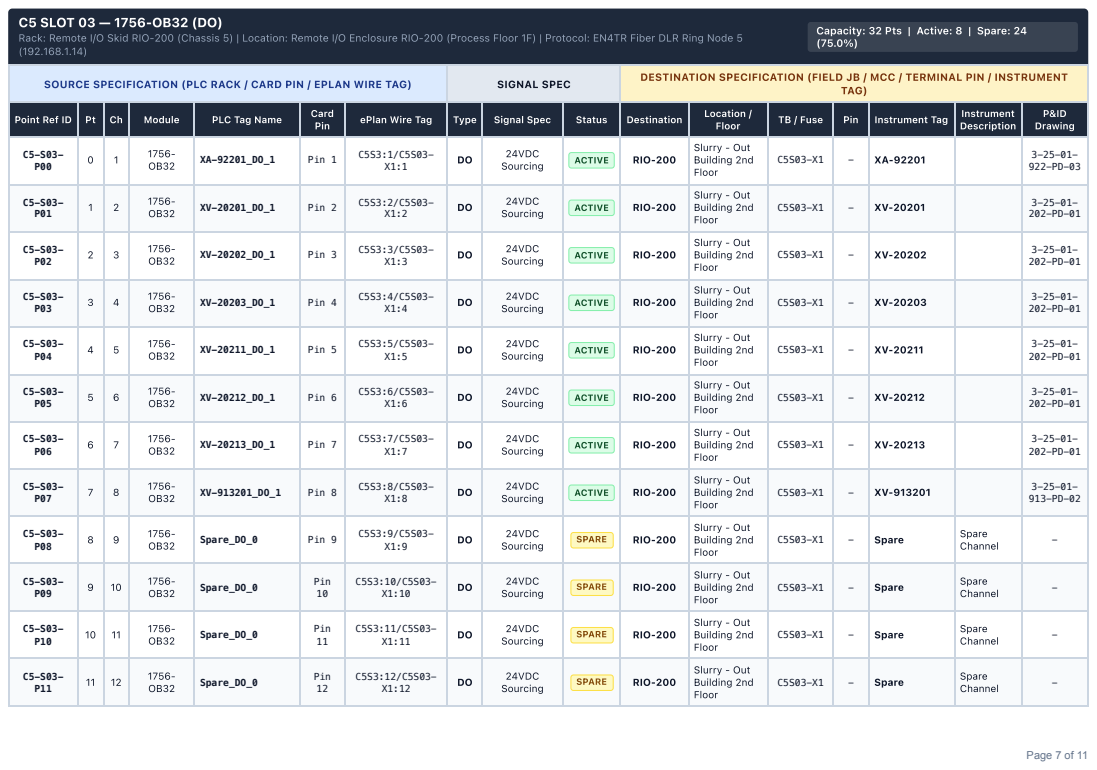
[picture p184: page 7]

Capacity: 32 Pts | Active: 8 | Spare: 24

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

C5-S03-P00 | 0 | 1 | 1756-OB32 | XA-92201_DO_1 | Pin 1 | C5S3:1/C5S03-X1:1 | DO | 24VDC Sourcing | ACTIVE | RIO-200 | Slurry - Out Building 2nd Floor | C5S03-X1 | - | XA-92201 | | 3-25-01-922-PD-03

C5-S03-P01 | 1 | 2 | 1756-OB32 | XV-20201_DO_1 | Pin 2 | C5S3:2/C5S03-X1:2 | DO | 24VDC Sourcing | ACTIVE | RIO-200 | Slurry - Out Building 2nd Floor | C5S03-X1 | - | XV-20201 | | 3-25-01-202-PD-01

C5-S03-P02 | 2 | 3 | 1756-OB32 | XV-20202_DO_1 | Pin 3 | C5S3:3/C5S03-X1:3 | DO | 24VDC Sourcing | ACTIVE | RIO-200 | Slurry - Out Building 2nd Floor | C5S03-X1 | - | XV-20202 | | 3-25-01-202-PD-01

C5-S03-P03 | 3 | 4 | 1756-OB32 | XV-20203_DO_1 | Pin 4 | C5S3:4/C5S03-X1:4 | DO | 24VDC Sourcing | ACTIVE | RIO-200 | Slurry - Out Building 2nd Floor | C5S03-X1 | - | XV-20203 | | 3-25-01-202-PD-01

C5-S03-P04 | 4 | 5 | 1756-OB32 | XV-20211_DO_1 | Pin 5 | C5S3:5/C5S03-X1:5 | DO | 24VDC Sourcing | ACTIVE | RIO-200 | Slurry - Out Building 2nd Floor | C5S03-X1 | - | XV-20211 | | 3-25-01-202-PD-01

C5-S03-P05 | 5 | 6 | 1756-OB32 | XV-20212_DO_1 | Pin 6 | C5S3:6/C5S03-X1:6 | DO | 24VDC Sourcing | ACTIVE | RIO-200 | Slurry - Out Building 2nd Floor | C5S03-X1 | - | XV-20212 | | 3-25-01-202-PD-01

C5-S03-P06 | 6 | 7 | 1756-OB32 | XV-20213_DO_1 | Pin 7 | C5S3:7/C5S03-X1:7 | DO | 24VDC Sourcing | ACTIVE | RIO-200 | Slurry - Out Building 2nd Floor | C5S03-X1 | - | XV-20213 | | 3-25-01-202-PD-01

C5-S03-P07 | 7 | 8 | 1756-OB32 | XV-913201_DO_1 | Pin 8 | C5S3:8/C5S03-X1:8 | DO | 24VDC Sourcing | ACTIVE | RIO-200 | Slurry - Out Building 2nd Floor | C5S03-X1 | - | XV-913201 | | 3-25-01-913-PD-02

C5-S03-P08 | 8 | 9 | 1756-OB32 | Spare_DO_0 | Pin 9 | C5S3:9/C5S03-X1:9 | DO | 24VDC Sourcing | SPARE | RIO-200 | Slurry - Out Building 2nd Floor | C5S03-X1 | - | Spare | Spare Channel | -

C5-S03-P09 | 9 | 10 | 1756-OB32 | Spare_DO_0 | Pin 10 | C5S3:10/C5S03-X1:10 | DO | 24VDC Sourcing | SPARE | RIO-200 | Slurry - Out Building 2nd Floor | C5S03-X1 | - | Spare | Spare Channel | -

C5-S03-P10 | 10 | 11 | 1756-OB32 | Spare_DO_0 | Pin 11 | C5S3:11/C5S03-X1:11 | DO | 24VDC Sourcing | SPARE | RIO-200 | Slurry - Out Building 2nd Floor | C5S03-X1 | - | Spare | Spare Channel | -

C5-S03-P11 | 11 | 12 | 1756-OB32 | Spare_DO_0 | Pin 12 | C5S3:12/C5S03-X1:12 | DO | 24VDC Sourcing | SPARE | RIO-200 | Slurry - Out Building 2nd Floor | C5S03-X1 | - | Spare | Spare Channel | -

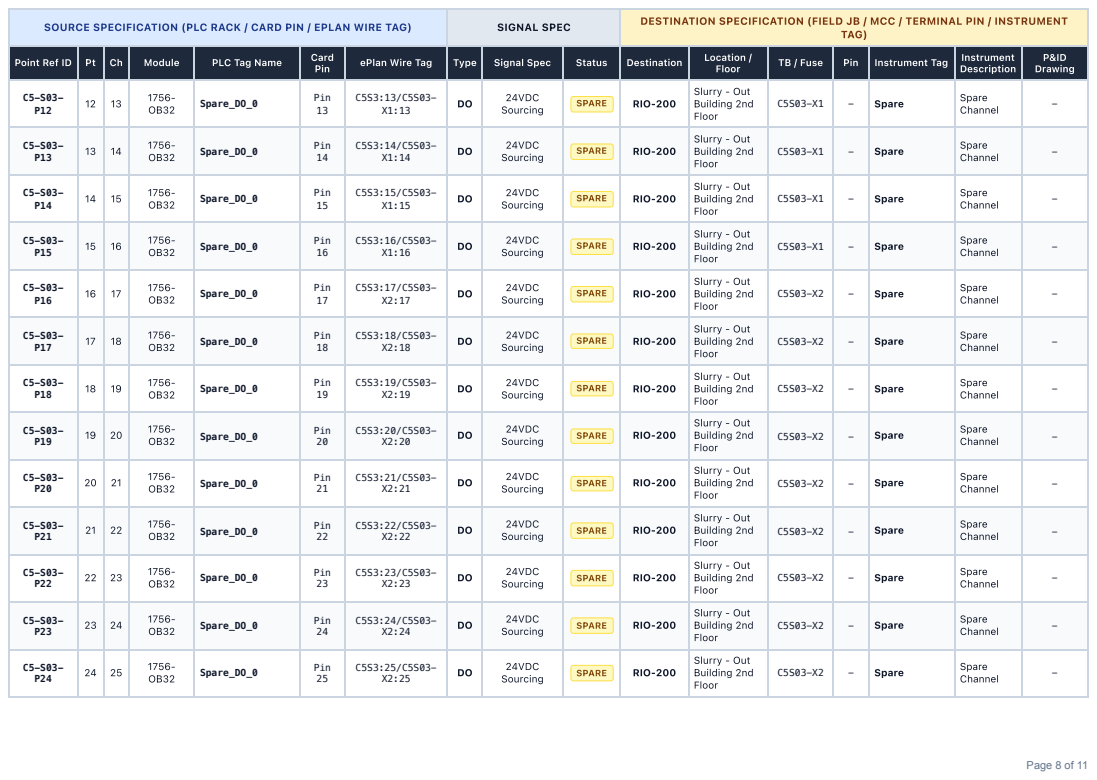
[picture p185: page 8]
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

C5-S03-P12 | 12 | 13 | 1756-OB32 | Spare_DO_0 | Pin 13 | C5S3:13/C5S03-X1:13 | DO | 24VDC Sourcing | SPARE | RIO-200 | Slurry - Out Building 2nd Floor | C5S03-X1 | - | Spare | Spare Channel | -

C5-S03-P13 | 13 | 14 | 1756-OB32 | Spare_DO_0 | Pin 14 | C5S3:14/C5S03-X1:14 | DO | 24VDC Sourcing | SPARE | RIO-200 | Slurry - Out Building 2nd Floor | C5S03-X1 | - | Spare | Spare Channel | -

C5-S03-P14 | 14 | 15 | 1756-OB32 | Spare_DO_0 | Pin 15 | C5S3:15/C5S03-X1:15 | DO | 24VDC Sourcing | SPARE | RIO-200 | Slurry - Out Building 2nd Floor | C5S03-X1 | - | Spare | Spare Channel | -

C5-S03-P15 | 15 | 16 | 1756-OB32 | Spare_DO_0 | Pin 16 | C5S3:16/C5S03-X1:16 | DO | 24VDC Sourcing | SPARE | RIO-200 | Slurry - Out Building 2nd Floor | C5S03-X1 | - | Spare | Spare Channel | -

C5-S03-P16 | 16 | 17 | 1756-OB32 | Spare_DO_0 | Pin 17 | C5S3:17/C5S03-X2:17 | DO | 24VDC Sourcing | SPARE | RIO-200 | Slurry - Out Building 2nd Floor | C5S03-X2 | - | Spare | Spare Channel | -

C5-S03-P17 | 17 | 18 | 1756-OB32 | Spare_DO_0 | Pin 18 | C5S3:18/C5S03-X2:18 | DO | 24VDC Sourcing | SPARE | RIO-200 | Slurry - Out Building 2nd Floor | C5S03-X2 | - | Spare | Spare Channel | -

C5-S03-P18 | 18 | 19 | 1756-OB32 | Spare_DO_0 | Pin 19 | C5S3:19/C5S03-X2:19 | DO | 24VDC Sourcing | SPARE | RIO-200 | Slurry - Out Building 2nd Floor | C5S03-X2 | - | Spare | Spare Channel | -

C5-S03-P19 | 19 | 20 | 1756-OB32 | Spare_DO_0 | Pin 20 | C5S3:20/C5S03-X2:20 | DO | 24VDC Sourcing | SPARE | RIO-200 | Slurry - Out Building 2nd Floor | C5S03-X2 | - | Spare | Spare Channel | -

C5-S03-P20 | 20 | 21 | 1756-OB32 | Spare_DO_0 | Pin 21 | C5S3:21/C5S03-X2:21 | DO | 24VDC Sourcing | SPARE | RIO-200 | Slurry - Out Building 2nd Floor | C5S03-X2 | - | Spare | Spare Channel | -

C5-S03-P21 | 21 | 22 | 1756-OB32 | Spare_DO_0 | Pin 22 | C5S3:22/C5S03-X2:22 | DO | 24VDC Sourcing | SPARE | RIO-200 | Slurry - Out Building 2nd Floor | C5S03-X2 | - | Spare | Spare Channel | -

C5-S03-P22 | 22 | 23 | 1756-OB32 | Spare_DO_0 | Pin 23 | C5S3:23/C5S03-X2:23 | DO | 24VDC Sourcing | SPARE | RIO-200 | Slurry - Out Building 2nd Floor | C5S03-X2 | - | Spare | Spare Channel | -

C5-S03-P23 | 23 | 24 | 1756-OB32 | Spare_DO_0 | Pin 24 | C5S3:24/C5S03-X2:24 | DO | 24VDC Sourcing | SPARE | RIO-200 | Slurry - Out Building 2nd Floor | C5S03-X2 | - | Spare | Spare Channel | -

C5-S03-P24 | 24 | 25 | 1756-OB32 | Spare_DO_0 | Pin 25 | C5S3:25/C5S03-X2:25 | DO | 24VDC Sourcing | SPARE | RIO-200 | Slurry - Out Building 2nd Floor | C5S03-X2 | - | Spare | Spare Channel | -

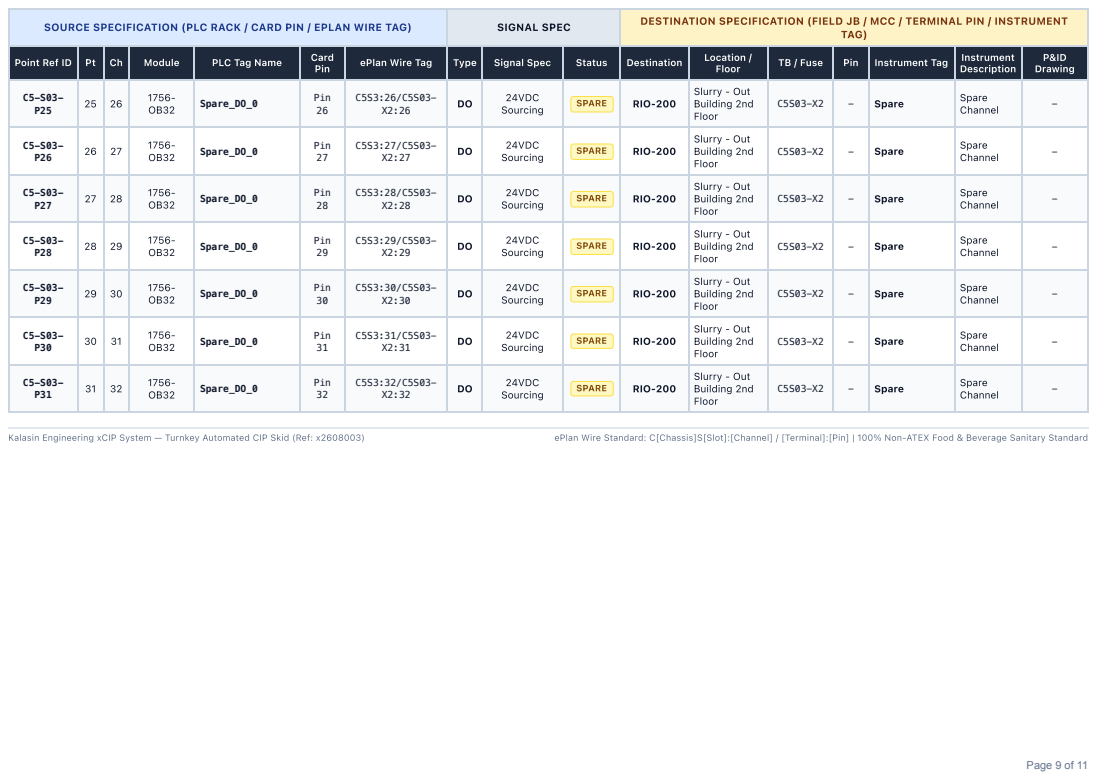
[picture p186: page 9]
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

C5-S03-P25 | 25 | 26 | 1756-OB32 | Spare_DO_0 | Pin 26 | C5S3:26/C5S03-X2:26 | DO | 24VDC Sourcing | SPARE | RIO-200 | Slurry - Out Building 2nd Floor | C5S03-X2 | - | Spare | Spare Channel | -

C5-S03-P26 | 26 | 27 | 1756-OB32 | Spare_DO_0 | Pin 27 | C5S3:27/C5S03-X2:27 | DO | 24VDC Sourcing | SPARE | RIO-200 | Slurry - Out Building 2nd Floor | C5S03-X2 | - | Spare | Spare Channel | -

C5-S03-P27 | 27 | 28 | 1756-OB32 | Spare_DO_0 | Pin 28 | C5S3:28/C5S03-X2:28 | DO | 24VDC Sourcing | SPARE | RIO-200 | Slurry - Out Building 2nd Floor | C5S03-X2 | - | Spare | Spare Channel | -

C5-S03-P28 | 28 | 29 | 1756-OB32 | Spare_DO_0 | Pin 29 | C5S3:29/C5S03-X2:29 | DO | 24VDC Sourcing | SPARE | RIO-200 | Slurry - Out Building 2nd Floor | C5S03-X2 | - | Spare | Spare Channel | -

C5-S03-P29 | 29 | 30 | 1756-OB32 | Spare_DO_0 | Pin 30 | C5S3:30/C5S03-X2:30 | DO | 24VDC Sourcing | SPARE | RIO-200 | Slurry - Out Building 2nd Floor | C5S03-X2 | - | Spare | Spare Channel | -

C5-S03-P30 | 30 | 31 | 1756-OB32 | Spare_DO_0 | Pin 31 | C5S3:31/C5S03-X2:31 | DO | 24VDC Sourcing | SPARE | RIO-200 | Slurry - Out Building 2nd Floor | C5S03-X2 | - | Spare | Spare Channel | -

C5-S03-P31 | 31 | 32 | 1756-OB32 | Spare_DO_0 | Pin 32 | C5S3:32/C5S03-X2:32 | DO | 24VDC Sourcing | SPARE | RIO-200 | Slurry - Out Building 2nd Floor | C5S03-X2 | - | Spare | Spare Channel | -

## C5 SLOT 04 — 1756-IF16 (AI)

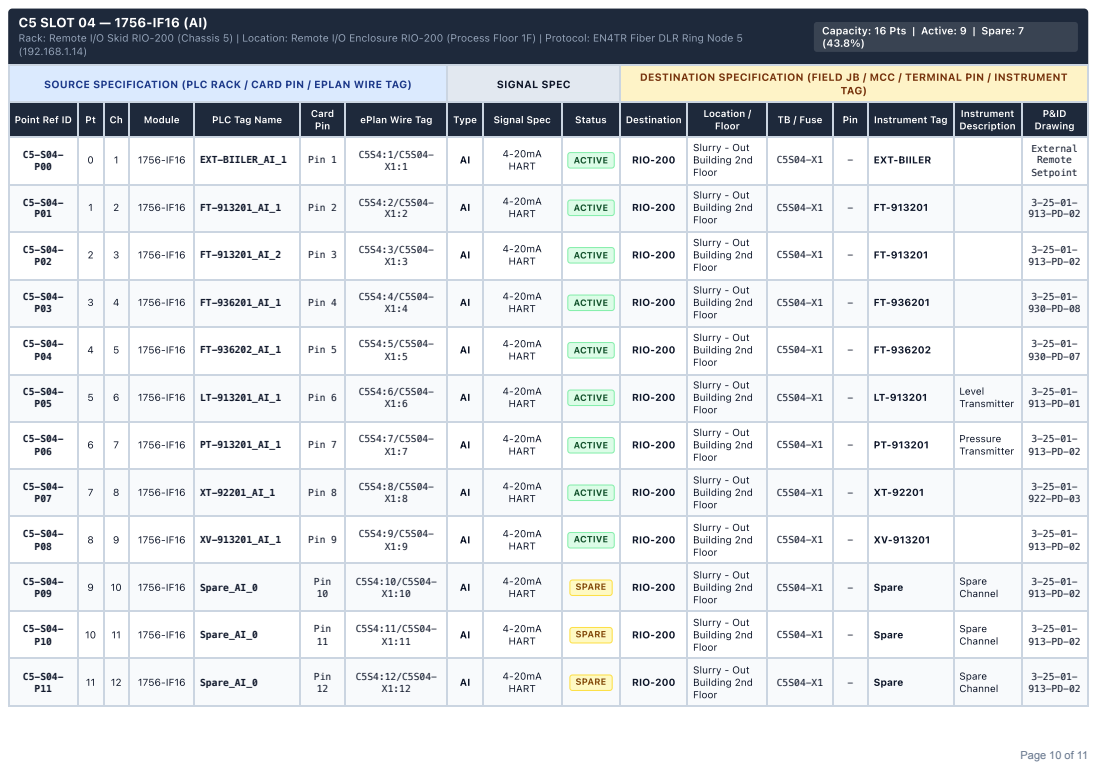
[picture p187: page 10]

Capacity: 16 Pts | Active: 9 | Spare: 7

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

C5-S04-P00 | 0 | 1 | 1756-IF16 | EXT-BIILER_AI_1 | Pin 1 | C5S4:1/C5S04-X1:1 | AI | 4-20mA HART | ACTIVE | RIO-200 | Slurry - Out Building 2nd Floor | C5S04-X1 | - | EXT-BIILER | | External Remote Setpoint

C5-S04-P01 | 1 | 2 | 1756-IF16 | FT-913201_AI_1 | Pin 2 | C5S4:2/C5S04-X1:2 | AI | 4-20mA HART | ACTIVE | RIO-200 | Slurry - Out Building 2nd Floor | C5S04-X1 | - | FT-913201 | | 3-25-01-913-PD-02

C5-S04-P02 | 2 | 3 | 1756-IF16 | FT-913201_AI_2 | Pin 3 | C5S4:3/C5S04-X1:3 | AI | 4-20mA HART | ACTIVE | RIO-200 | Slurry - Out Building 2nd Floor | C5S04-X1 | - | FT-913201 | | 3-25-01-913-PD-02

C5-S04-P03 | 3 | 4 | 1756-IF16 | FT-936201_AI_1 | Pin 4 | C5S4:4/C5S04-X1:4 | AI | 4-20mA HART | ACTIVE | RIO-200 | Slurry - Out Building 2nd Floor | C5S04-X1 | - | FT-936201 | | 3-25-01-930-PD-08

C5-S04-P04 | 4 | 5 | 1756-IF16 | FT-936202_AI_1 | Pin 5 | C5S4:5/C5S04-X1:5 | AI | 4-20mA HART | ACTIVE | RIO-200 | Slurry - Out Building 2nd Floor | C5S04-X1 | - | FT-936202 | | 3-25-01-930-PD-07

C5-S04-P05 | 5 | 6 | 1756-IF16 | LT-913201_AI_1 | Pin 6 | C5S4:6/C5S04-X1:6 | AI | 4-20mA HART | ACTIVE | RIO-200 | Slurry - Out Building 2nd Floor | C5S04-X1 | - | LT-913201 | Level Transmitter | 3-25-01-913-PD-01

C5-S04-P06 | 6 | 7 | 1756-IF16 | PT-913201_AI_1 | Pin 7 | C5S4:7/C5S04-X1:7 | AI | 4-20mA HART | ACTIVE | RIO-200 | Slurry - Out Building 2nd Floor | C5S04-X1 | - | PT-913201 | Pressure Transmitter | 3-25-01-913-PD-02

C5-S04-P07 | 7 | 8 | 1756-IF16 | XT-92201_AI_1 | Pin 8 | C5S4:8/C5S04-X1:8 | AI | 4-20mA HART | ACTIVE | RIO-200 | Slurry - Out Building 2nd Floor | C5S04-X1 | - | XT-92201 | | 3-25-01-922-PD-03

C5-S04-P08 | 8 | 9 | 1756-IF16 | XV-913201_AI_1 | Pin 9 | C5S4:9/C5S04-X1:9 | AI | 4-20mA HART | ACTIVE | RIO-200 | Slurry - Out Building 2nd Floor | C5S04-X1 | - | XV-913201 | | 3-25-01-913-PD-02

C5-S04-P09 | 9 | 10 | 1756-IF16 | Spare_AI_0 | Pin 10 | C5S4:10/C5S04-X1:10 | AI | 4-20mA HART | SPARE | RIO-200 | Slurry - Out Building 2nd Floor | C5S04-X1 | - | Spare | Spare Channel | 3-25-01-913-PD-02

C5-S04-P10 | 10 | 11 | 1756-IF16 | Spare_AI_0 | Pin 11 | C5S4:11/C5S04-X1:11 | AI | 4-20mA HART | SPARE | RIO-200 | Slurry - Out Building 2nd Floor | C5S04-X1 | - | Spare | Spare Channel | 3-25-01-913-PD-02

C5-S04-P11 | 11 | 12 | 1756-IF16 | Spare_AI_0 | Pin 12 | C5S4:12/C5S04-X1:12 | AI | 4-20mA HART | SPARE | RIO-200 | Slurry - Out Building 2nd Floor | C5S04-X1 | - | Spare | Spare Channel | 3-25-01-913-PD-02

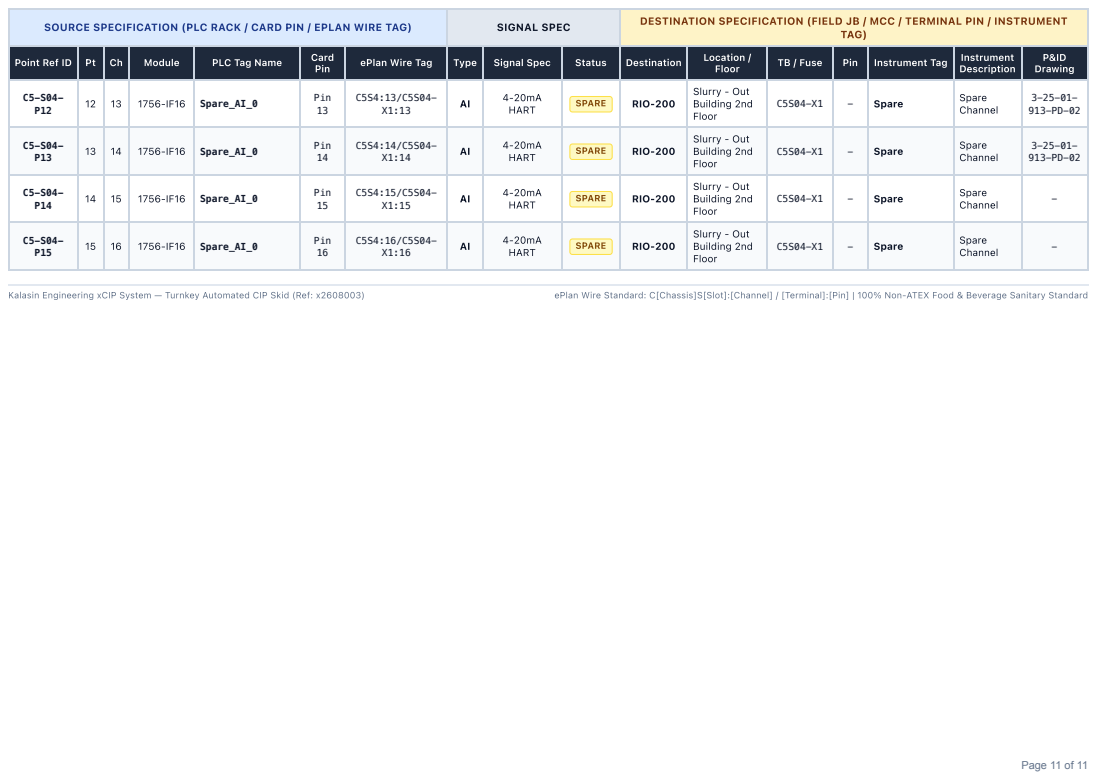
[picture p188: page 11]
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

C5-S04-P12 | 12 | 13 | 1756-IF16 | Spare_AI_0 | Pin 13 | C5S4:13/C5S04-X1:13 | AI | 4-20mA HART | SPARE | RIO-200 | Slurry - Out Building 2nd Floor | C5S04-X1 | - | Spare | Spare Channel | 3-25-01-913-PD-02

C5-S04-P13 | 13 | 14 | 1756-IF16 | Spare_AI_0 | Pin 14 | C5S4:14/C5S04-X1:14 | AI | 4-20mA HART | SPARE | RIO-200 | Slurry - Out Building 2nd Floor | C5S04-X1 | - | Spare | Spare Channel | 3-25-01-913-PD-02

C5-S04-P14 | 14 | 15 | 1756-IF16 | Spare_AI_0 | Pin 15 | C5S4:15/C5S04-X1:15 | AI | 4-20mA HART | SPARE | RIO-200 | Slurry - Out Building 2nd Floor | C5S04-X1 | - | Spare | Spare Channel | -

C5-S04-P15 | 15 | 16 | 1756-IF16 | Spare_AI_0 | Pin 16 | C5S4:16/C5S04-X1:16 | AI | 4-20mA HART | SPARE | RIO-200 | Slurry - Out Building 2nd Floor | C5S04-X1 | - | Spare | Spare Channel | -
