x92120/x260911-002-KalasinEngineering/02_Electrical_and_eDrawing/04_PDF_Reports_and_Drawings/Chassis_C6_Slots_IO_Report.pdf

# KALASIN ENGINEERING — C6(MCC AUXILIARY I/O (CHASSIS6))

C6

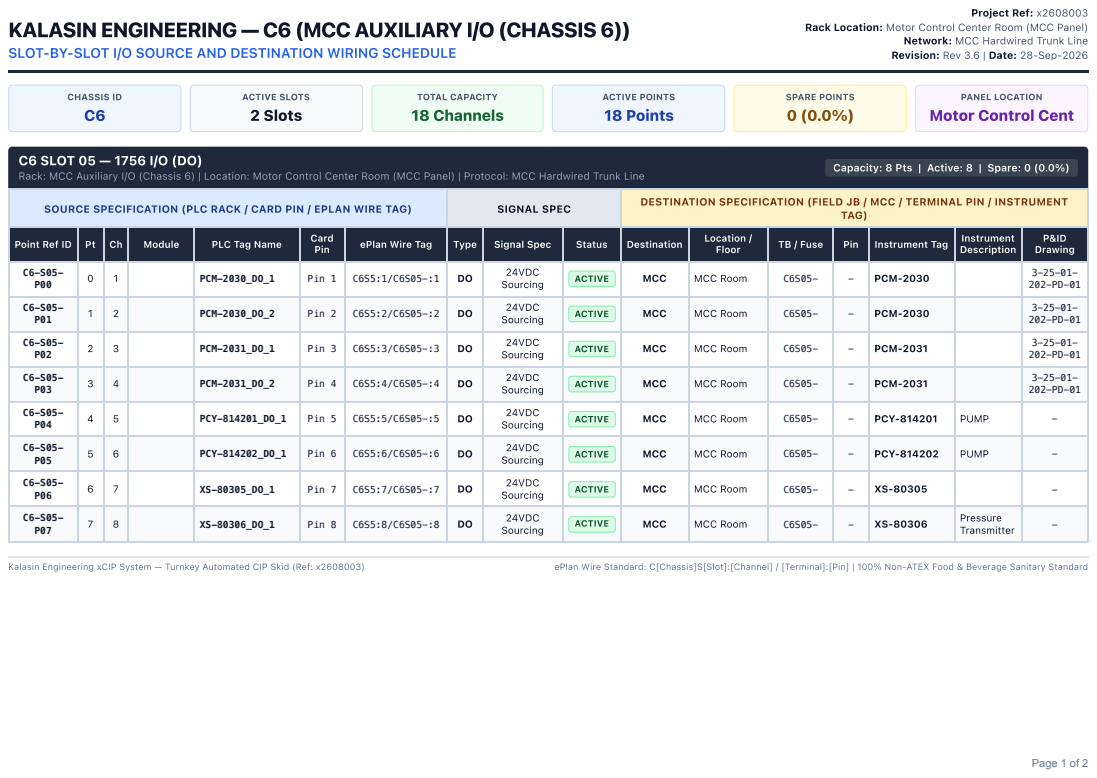
[picture p189: page 1]
Project Ref: x2608003; CHASSIS ID; ACTIVE SLOTS 2 Slots; TOTAL CAPACITY 18 Channels; ACTIVE POINTS 18 Points; SPARE POINTS 0 (0.0%); Kalasin Engineering xCIP System — Turnkey Automated CIP Skid (Ref: x2608003); ePlan Wire Standard: C[Chassis]S[Slot]:[Channel] / [Terminal]:[Pin] | 100% Non-ATEX Food & Beverage Sanitary Standard

Rack Location: Motor Control Center Room (MCC Panel)

Network: MCC Hardwired Trunk Line
Revision: Rev 3.6 | Date: 28-Sep-2026

SLOT-BY-SLOT I/O SOURCE AND DESTINATION WIRING SCHEDULE

PANEL LOCATION
Motor Control Cent

C6 SLOT 05 — 1756 I/O (DO)
Rack: MCC Auxiliary I/O (Chassis 6) | Location: Motor Control Center Room (MCC Panel) | Protocol: MCC Hardwired Trunk Line

Capacity: 8 Pts | Active: 8 | Spare: 0 (0.0%)

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

C6-S05-P00 | 0 | 1 | | PCM-2030_DO_1 | Pin 1 | C6S5:1/C6S05-:1 | DO | 24VDC Sourcing | ACTIVE | MCC | MCC Room | C6S05- | - | PCM-2030 | | 3-25-01-202-PD-01

C6-S05-P01 | 1 | 2 | | PCM-2030_DO_2 | Pin 2 | C6S5:2/C6S05-:2 | DO | 24VDC Sourcing | ACTIVE | MCC | MCC Room | C6S05- | - | PCM-2030 | | 3-25-01-202-PD-01

C6-S05-P02 | 2 | 3 | | PCM-2031_DO_1 | Pin 3 | C6S5:3/C6S05-:3 | DO | 24VDC Sourcing | ACTIVE | MCC | MCC Room | C6S05- | - | PCM-2031 | | 3-25-01-202-PD-01

C6-S05-P03 | 3 | 4 | | PCM-2031_DO_2 | Pin 4 | C6S5:4/C6S05-:4 | DO | 24VDC Sourcing | ACTIVE | MCC | MCC Room | C6S05- | - | PCM-2031 | | 3-25-01-202-PD-01

C6-S05-P04 | 4 | 5 | | PCY-814201_DO_1 | Pin 5 | C6S5:5/C6S05-:5 | DO | 24VDC Sourcing | ACTIVE | MCC | MCC Room | C6S05- | - | PCY-814201 | PUMP | -

C6-S05-P05 | 5 | 6 | | PCY-814202_DO_1 | Pin 6 | C6S5:6/C6S05-:6 | DO | 24VDC Sourcing | ACTIVE | MCC | MCC Room | C6S05- | - | PCY-814202 | PUMP | -

C6-S05-P06 | 6 | 7 | | XS-80305_DO_1 | Pin 7 | C6S5:7/C6S05-:7 | DO | 24VDC Sourcing | ACTIVE | MCC | MCC Room | C6S05- | - | XS-80305 | | -

C6-S05-P07 | 7 | 8 | | XS-80306_DO_1 | Pin 8 | C6S5:8/C6S05-:8 | DO | 24VDC Sourcing | ACTIVE | MCC | MCC Room | C6S05- | - | XS-80306 | Pressure Transmitter | -

## C6 SLOT 06 — 1756 I/O (DI)

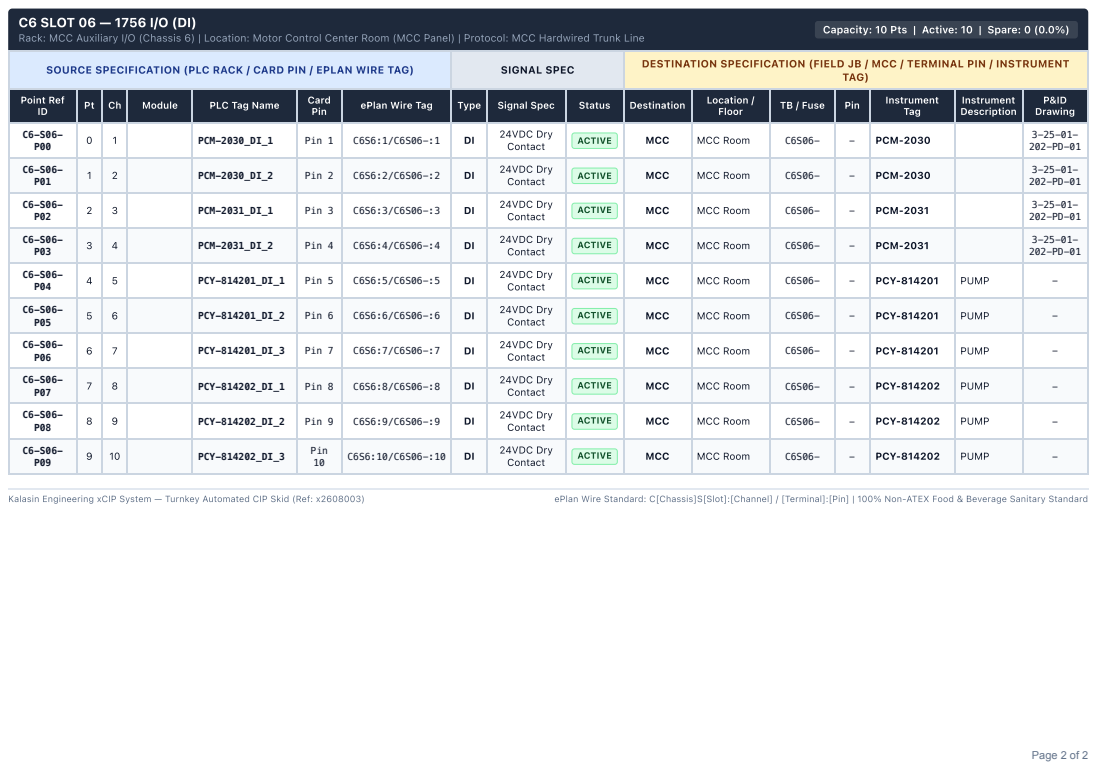
[picture p190: page 2]
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

Capacity: 10 Pts | Active: 10 | Spare: 0 (0.0%)

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

C6-S06-P00 | 0 | 1 | | PCM-2030_DI_1 | Pin 1 | C6S6:1/C6S06-:1 | DI | 24VDC Dry Contact | ACTIVE | MCC | MCC Room | C6S06- | - | PCM-2030 | | 3-25-01-202-PD-01

C6-S06-P01 | 1 | 2 | | PCM-2030_DI_2 | Pin 2 | C6S6:2/C6S06-:2 | DI | 24VDC Dry Contact | ACTIVE | MCC | MCC Room | C6S06- | - | PCM-2030 | | 3-25-01-202-PD-01

C6-S06-P02 | 2 | 3 | | PCM-2031_DI_1 | Pin 3 | C6S6:3/C6S06-:3 | DI | 24VDC Dry Contact | ACTIVE | MCC | MCC Room | C6S06- | - | PCM-2031 | | 3-25-01-202-PD-01

C6-S06-P03 | 3 | 4 | | PCM-2031_DI_2 | Pin 4 | C6S6:4/C6S06-:4 | DI | 24VDC Dry Contact | ACTIVE | MCC | MCC Room | C6S06- | - | PCM-2031 | | 3-25-01-202-PD-01

C6-S06-P04 | 4 | 5 | | PCY-814201_DI_1 | Pin 5 | C6S6:5/C6S06-:5 | DI | 24VDC Dry Contact | ACTIVE | MCC | MCC Room | C6S06- | - | PCY-814201 | PUMP | -

C6-S06-P05 | 5 | 6 | | PCY-814201_DI_2 | Pin 6 | C6S6:6/C6S06-:6 | DI | 24VDC Dry Contact | ACTIVE | MCC | MCC Room | C6S06- | - | PCY-814201 | PUMP | -

C6-S06-P06 | 6 | 7 | | PCY-814201_DI_3 | Pin 7 | C6S6:7/C6S06-:7 | DI | 24VDC Dry Contact | ACTIVE | MCC | MCC Room | C6S06- | - | PCY-814201 | PUMP | -

C6-S06-P07 | 7 | 8 | | PCY-814202_DI_1 | Pin 8 | C6S6:8/C6S06-:8 | DI | 24VDC Dry Contact | ACTIVE | MCC | MCC Room | C6S06- | - | PCY-814202 | PUMP | -

C6-S06-P08 | 8 | 9 | | PCY-814202_DI_2 | Pin 9 | C6S6:9/C6S06-:9 | DI | 24VDC Dry Contact | ACTIVE | MCC | MCC Room | C6S06- | - | PCY-814202 | PUMP | -

C6-S06-P09 | 9 | 10 | | PCY-814202_DI_3 | Pin 10 | C6S6:10/C6S06-:10 | DI | 24VDC Dry Contact | ACTIVE | MCC | MCC Room | C6S06- | - | PCY-814202 | PUMP | -
