x92120/x260911-002-KalasinEngineering/02_Electrical_and_eDrawing/04_PDF_Reports_and_Drawings/Chassis_C7_Slots_IO_Report.pdf

# KALASIN ENGINEERING — C7 (MCC FIELDBUS & NETWORK INTERFACE (CHASSIS7))

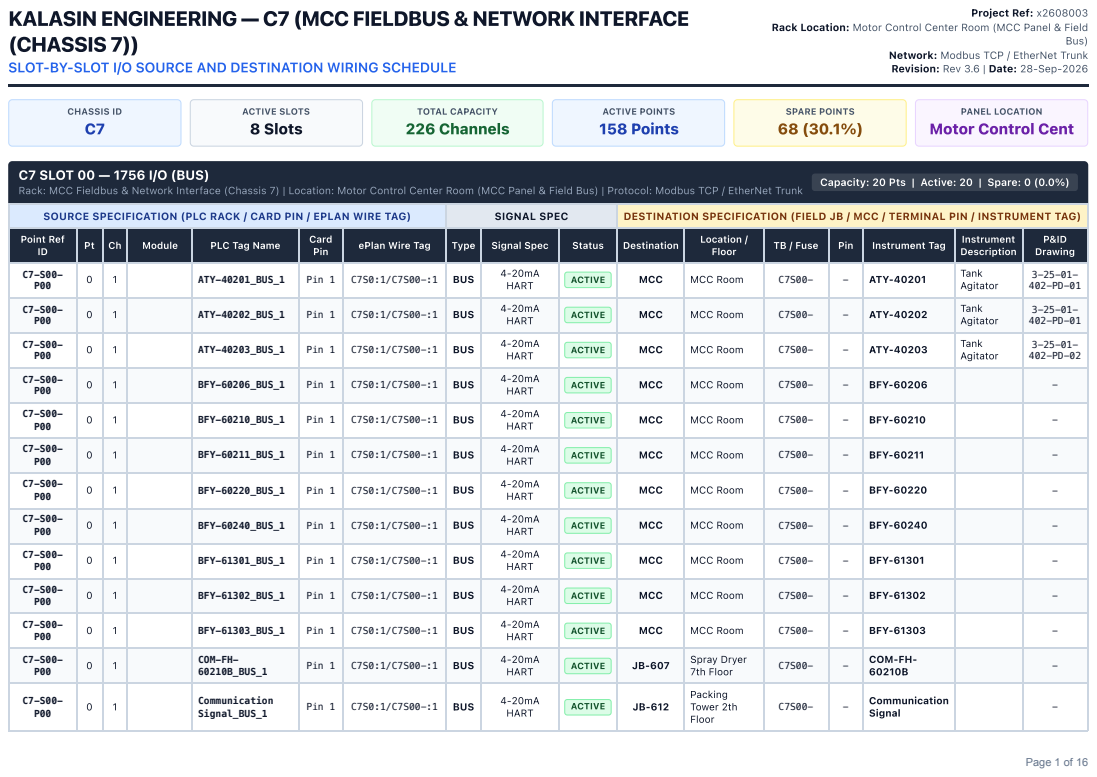
[picture p191: page 1]
Project Ref: x2608003; Bus); CHASSIS ID C7; ACTIVE SLOTS 8 Slots; TOTAL CAPACITY 226 Channels; ACTIVE POINTS 158 Points; SPARE POINTS 68 (30.1%)

Rack Location: Motor Control Center Room (MCC Panel & Field

SLOT-BY-SLOT I/O SOURCE AND DESTINATION WIRING SCHEDULE

Network: Modbus TCP / EtherNet Trunk
Revision: Rev 3.6 | Date: 28-Sep-2026

PANEL LOCATION
Motor Control Cent

C7 SLOT 00 — 1756 I/O (BUS)
Rack: MCC Fieldbus & Network Interface (Chassis 7) | Location: Motor Control Center Room (MCC Panel & Field Bus) | Protocol: Modbus TCP / EtherNet Trunk

Capacity: 20 Pts | Active: 20 | Spare: 0 (0.0%)

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

C7-S00-P00 | 0 | 1 | | ATY-40201_BUS_1 | Pin 1 | C7S0:1/C7S00-:1 | BUS | 4-20mA HART | ACTIVE | MCC | MCC Room | C7S00- | - | ATY-40201 | Tank Agitator | 3-25-01-402-PD-01

C7-S00-P00 | 0 | 1 | | ATY-40202_BUS_1 | Pin 1 | C7S0:1/C7S00-:1 | BUS | 4-20mA HART | ACTIVE | MCC | MCC Room | C7S00- | - | ATY-40202 | Tank Agitator | 3-25-01-402-PD-01

C7-S00-P00 | 0 | 1 | | ATY-40203_BUS_1 | Pin 1 | C7S0:1/C7S00-:1 | BUS | 4-20mA HART | ACTIVE | MCC | MCC Room | C7S00- | - | ATY-40203 | Tank Agitator | 3-25-01-402-PD-02

C7-S00-P00 | 0 | 1 | | BFY-60206_BUS_1 | Pin 1 | C7S0:1/C7S00-:1 | BUS | 4-20mA HART | ACTIVE | MCC | MCC Room | C7S00- | - | BFY-60206 | | -

C7-S00-P00 | 0 | 1 | | BFY-60210_BUS_1 | Pin 1 | C7S0:1/C7S00-:1 | BUS | 4-20mA HART | ACTIVE | MCC | MCC Room | C7S00- | - | BFY-60210 | | -

C7-S00-P00 | 0 | 1 | | BFY-60211_BUS_1 | Pin 1 | C7S0:1/C7S00-:1 | BUS | 4-20mA HART | ACTIVE | MCC | MCC Room | C7S00- | - | BFY-60211 | | -

C7-S00-P00 | 0 | 1 | | BFY-60220_BUS_1 | Pin 1 | C7S0:1/C7S00-:1 | BUS | 4-20mA HART | ACTIVE | MCC | MCC Room | C7S00- | - | BFY-60220 | | -

C7-S00-P00 | 0 | 1 | | BFY-60240_BUS_1 | Pin 1 | C7S0:1/C7S00-:1 | BUS | 4-20mA HART | ACTIVE | MCC | MCC Room | C7S00- | - | BFY-60240 | | -

C7-S00-P00 | 0 | 1 | | BFY-61301_BUS_1 | Pin 1 | C7S0:1/C7S00-:1 | BUS | 4-20mA HART | ACTIVE | MCC | MCC Room | C7S00- | - | BFY-61301 | | -

C7-S00-P00 | 0 | 1 | | BFY-61302_BUS_1 | Pin 1 | C7S0:1/C7S00-:1 | BUS | 4-20mA HART | ACTIVE | MCC | MCC Room | C7S00- | - | BFY-61302 | | -

C7-S00-P00 | 0 | 1 | | BFY-61303_BUS_1 | Pin 1 | C7S0:1/C7S00-:1 | BUS | 4-20mA HART | ACTIVE | MCC | MCC Room | C7S00- | - | BFY-61303 | | -

C7-S00-P00 | 0 | 1 | | COM-FH-60210B_BUS_1 | Pin 1 | C7S0:1/C7S00-:1 | BUS | 4-20mA HART | ACTIVE | JB-607 | Spray Dryer 7th Floor | C7S00- | - | COM-FH-60210B | | -

C7-S00-P00 | 0 | 1 | | Communication Signal_BUS_1 | Pin 1 | C7S0:1/C7S00-:1 | BUS | 4-20mA HART | ACTIVE | JB-612 | Packing Tower 2th Floor | C7S00- | - | Communication Signal | | -

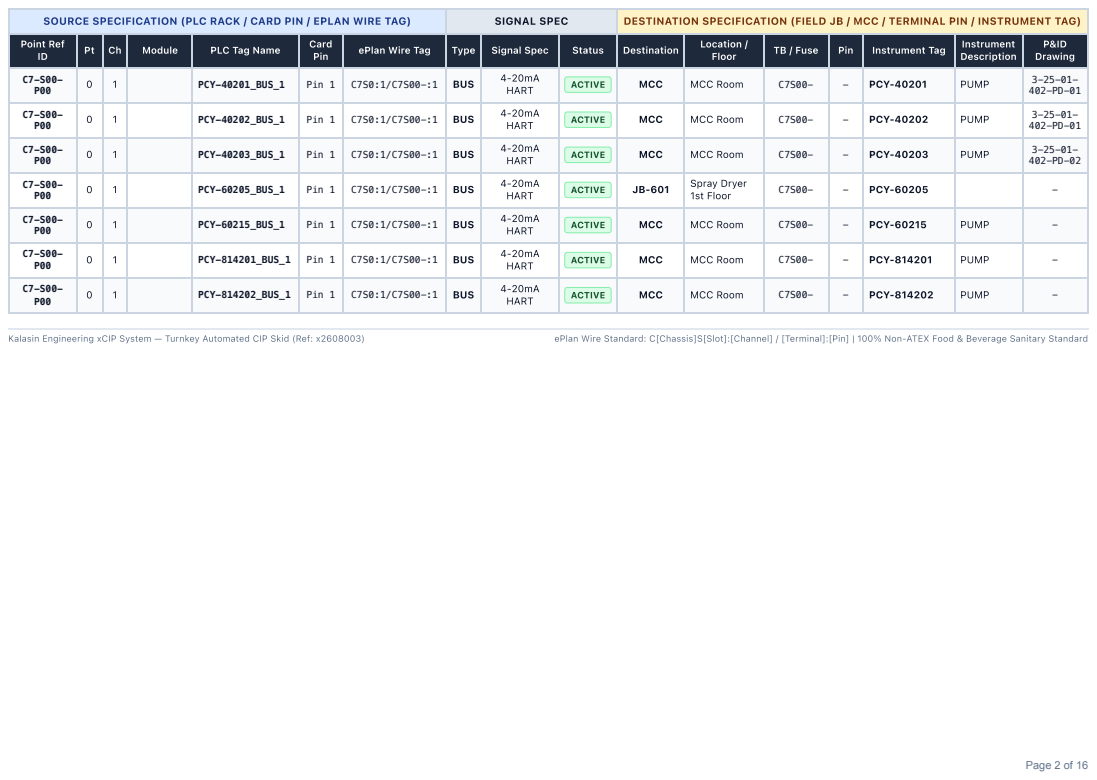
[picture p192: page 2]
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

C7-S00-P00 | 0 | 1 | | PCY-40201_BUS_1 | Pin 1 | C7S0:1/C7S00-:1 | BUS | 4-20mA HART | ACTIVE | MCC | MCC Room | C7S00- | - | PCY-40201 | PUMP | 3-25-01-402-PD-01

C7-S00-P00 | 0 | 1 | | PCY-40202_BUS_1 | Pin 1 | C7S0:1/C7S00-:1 | BUS | 4-20mA HART | ACTIVE | MCC | MCC Room | C7S00- | - | PCY-40202 | PUMP | 3-25-01-402-PD-01

C7-S00-P00 | 0 | 1 | | PCY-40203_BUS_1 | Pin 1 | C7S0:1/C7S00-:1 | BUS | 4-20mA HART | ACTIVE | MCC | MCC Room | C7S00- | - | PCY-40203 | PUMP | 3-25-01-402-PD-02

C7-S00-P00 | 0 | 1 | | PCY-60205_BUS_1 | Pin 1 | C7S0:1/C7S00-:1 | BUS | 4-20mA HART | ACTIVE | JB-601 | Spray Dryer 1st Floor | C7S00- | - | PCY-60205 | | -

C7-S00-P00 | 0 | 1 | | PCY-60215_BUS_1 | Pin 1 | C7S0:1/C7S00-:1 | BUS | 4-20mA HART | ACTIVE | MCC | MCC Room | C7S00- | - | PCY-60215 | PUMP | -

C7-S00-P00 | 0 | 1 | | PCY-814201_BUS_1 | Pin 1 | C7S0:1/C7S00-:1 | BUS | 4-20mA HART | ACTIVE | MCC | MCC Room | C7S00- | - | PCY-814201 | PUMP | -

C7-S00-P00 | 0 | 1 | | PCY-814202_BUS_1 | Pin 1 | C7S0:1/C7S00-:1 | BUS | 4-20mA HART | ACTIVE | MCC | MCC Room | C7S00- | - | PCY-814202 | PUMP | -

## C7 SLOT 01 — 1756 I/O (DI)

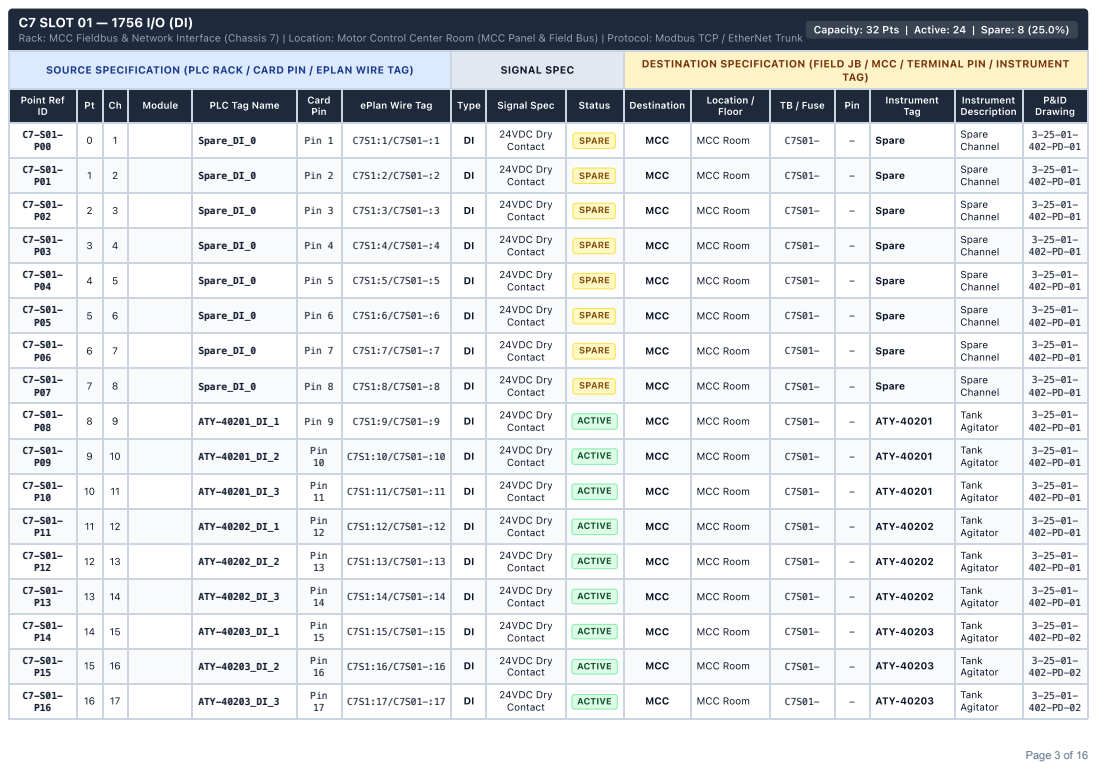
[picture p193: page 3]

Capacity: 32 Pts | Active: 24 | Spare: 8 (25.0%)

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

C7-S01-P00 | 0 | 1 | | Spare_DI_0 | Pin 1 | C7S1:1/C7S01-:1 | DI | 24VDC Dry Contact | SPARE | MCC | MCC Room | C7S01- | - | Spare | Spare Channel | 3-25-01-402-PD-01

C7-S01-P01 | 1 | 2 | | Spare_DI_0 | Pin 2 | C7S1:2/C7S01-:2 | DI | 24VDC Dry Contact | SPARE | MCC | MCC Room | C7S01- | - | Spare | Spare Channel | 3-25-01-402-PD-01

C7-S01-P02 | 2 | 3 | | Spare_DI_0 | Pin 3 | C7S1:3/C7S01-:3 | DI | 24VDC Dry Contact | SPARE | MCC | MCC Room | C7S01- | - | Spare | Spare Channel | 3-25-01-402-PD-01

C7-S01-P03 | 3 | 4 | | Spare_DI_0 | Pin 4 | C7S1:4/C7S01-:4 | DI | 24VDC Dry Contact | SPARE | MCC | MCC Room | C7S01- | - | Spare | Spare Channel | 3-25-01-402-PD-01

C7-S01-P04 | 4 | 5 | | Spare_DI_0 | Pin 5 | C7S1:5/C7S01-:5 | DI | 24VDC Dry Contact | SPARE | MCC | MCC Room | C7S01- | - | Spare | Spare Channel | 3-25-01-402-PD-01

C7-S01-P05 | 5 | 6 | | Spare_DI_0 | Pin 6 | C7S1:6/C7S01-:6 | DI | 24VDC Dry Contact | SPARE | MCC | MCC Room | C7S01- | - | Spare | Spare Channel | 3-25-01-402-PD-01

C7-S01-P06 | 6 | 7 | | Spare_DI_0 | Pin 7 | C7S1:7/C7S01-:7 | DI | 24VDC Dry Contact | SPARE | MCC | MCC Room | C7S01- | - | Spare | Spare Channel | 3-25-01-402-PD-01

C7-S01-P07 | 7 | 8 | | Spare_DI_0 | Pin 8 | C7S1:8/C7S01-:8 | DI | 24VDC Dry Contact | SPARE | MCC | MCC Room | C7S01- | - | Spare | Spare Channel | 3-25-01-402-PD-01

C7-S01-P08 | 8 | 9 | | ATY-40201_DI_1 | Pin 9 | C7S1:9/C7S01-:9 | DI | 24VDC Dry Contact | ACTIVE | MCC | MCC Room | C7S01- | - | ATY-40201 | Tank Agitator | 3-25-01-402-PD-01

C7-S01-P09 | 9 | 10 | | ATY-40201_DI_2 | Pin 10 | C7S1:10/C7S01-:10 | DI | 24VDC Dry Contact | ACTIVE | MCC | MCC Room | C7S01- | - | ATY-40201 | Tank Agitator | 3-25-01-402-PD-01

C7-S01-P10 | 10 | 11 | | ATY-40201_DI_3 | Pin 11 | C7S1:11/C7S01-:11 | DI | 24VDC Dry Contact | ACTIVE | MCC | MCC Room | C7S01- | - | ATY-40201 | Tank Agitator | 3-25-01-402-PD-01

C7-S01-P11 | 11 | 12 | | ATY-40202_DI_1 | Pin 12 | C7S1:12/C7S01-:12 | DI | 24VDC Dry Contact | ACTIVE | MCC | MCC Room | C7S01- | - | ATY-40202 | Tank Agitator | 3-25-01-402-PD-01

C7-S01-P12 | 12 | 13 | | ATY-40202_DI_2 | Pin 13 | C7S1:13/C7S01-:13 | DI | 24VDC Dry Contact | ACTIVE | MCC | MCC Room | C7S01- | - | ATY-40202 | Tank Agitator | 3-25-01-402-PD-01

C7-S01-P13 | 13 | 14 | | ATY-40202_DI_3 | Pin 14 | C7S1:14/C7S01-:14 | DI | 24VDC Dry Contact | ACTIVE | MCC | MCC Room | C7S01- | - | ATY-40202 | Tank Agitator | 3-25-01-402-PD-01

C7-S01-P14 | 14 | 15 | | ATY-40203_DI_1 | Pin 15 | C7S1:15/C7S01-:15 | DI | 24VDC Dry Contact | ACTIVE | MCC | MCC Room | C7S01- | - | ATY-40203 | Tank Agitator | 3-25-01-402-PD-02

C7-S01-P15 | 15 | 16 | | ATY-40203_DI_2 | Pin 16 | C7S1:16/C7S01-:16 | DI | 24VDC Dry Contact | ACTIVE | MCC | MCC Room | C7S01- | - | ATY-40203 | Tank Agitator | 3-25-01-402-PD-02

C7-S01-P16 | 16 | 17 | | ATY-40203_DI_3 | Pin 17 | C7S1:17/C7S01-:17 | DI | 24VDC Dry Contact | ACTIVE | MCC | MCC Room | C7S01- | - | ATY-40203 | Tank Agitator | 3-25-01-402-PD-02

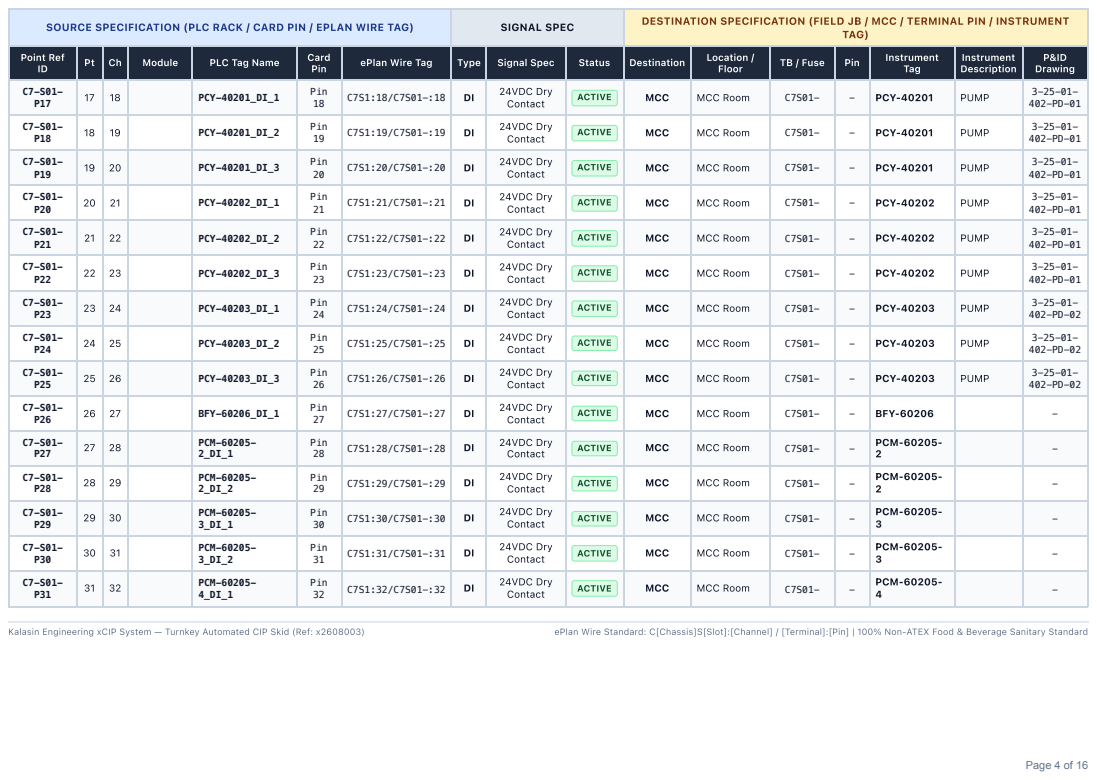
[picture p194: page 4]
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

C7-S01-P17 | 17 | 18 | | PCY-40201_DI_1 | Pin 18 | C7S1:18/C7S01-:18 | DI | 24VDC Dry Contact | ACTIVE | MCC | MCC Room | C7S01- | - | PCY-40201 | PUMP | 3-25-01-402-PD-01

C7-S01-P18 | 18 | 19 | | PCY-40201_DI_2 | Pin 19 | C7S1:19/C7S01-:19 | DI | 24VDC Dry Contact | ACTIVE | MCC | MCC Room | C7S01- | - | PCY-40201 | PUMP | 3-25-01-402-PD-01

C7-S01-P19 | 19 | 20 | | PCY-40201_DI_3 | Pin 20 | C7S1:20/C7S01-:20 | DI | 24VDC Dry Contact | ACTIVE | MCC | MCC Room | C7S01- | - | PCY-40201 | PUMP | 3-25-01-402-PD-01

C7-S01-P20 | 20 | 21 | | PCY-40202_DI_1 | Pin 21 | C7S1:21/C7S01-:21 | DI | 24VDC Dry Contact | ACTIVE | MCC | MCC Room | C7S01- | - | PCY-40202 | PUMP | 3-25-01-402-PD-01

C7-S01-P21 | 21 | 22 | | PCY-40202_DI_2 | Pin 22 | C7S1:22/C7S01-:22 | DI | 24VDC Dry Contact | ACTIVE | MCC | MCC Room | C7S01- | - | PCY-40202 | PUMP | 3-25-01-402-PD-01

C7-S01-P22 | 22 | 23 | | PCY-40202_DI_3 | Pin 23 | C7S1:23/C7S01-:23 | DI | 24VDC Dry Contact | ACTIVE | MCC | MCC Room | C7S01- | - | PCY-40202 | PUMP | 3-25-01-402-PD-01

C7-S01-P23 | 23 | 24 | | PCY-40203_DI_1 | Pin 24 | C7S1:24/C7S01-:24 | DI | 24VDC Dry Contact | ACTIVE | MCC | MCC Room | C7S01- | - | PCY-40203 | PUMP | 3-25-01-402-PD-02

C7-S01-P24 | 24 | 25 | | PCY-40203_DI_2 | Pin 25 | C7S1:25/C7S01-:25 | DI | 24VDC Dry Contact | ACTIVE | MCC | MCC Room | C7S01- | - | PCY-40203 | PUMP | 3-25-01-402-PD-02

C7-S01-P25 | 25 | 26 | | PCY-40203_DI_3 | Pin 26 | C7S1:26/C7S01-:26 | DI | 24VDC Dry Contact | ACTIVE | MCC | MCC Room | C7S01- | - | PCY-40203 | PUMP | 3-25-01-402-PD-02

C7-S01-P26 | 26 | 27 | | BFY-60206_DI_1 | Pin 27 | C7S1:27/C7S01-:27 | DI | 24VDC Dry Contact | ACTIVE | MCC | MCC Room | C7S01- | - | BFY-60206 | | -

C7-S01-P27 | 27 | 28 | | PCM-60205-2_DI_1 | Pin 28 | C7S1:28/C7S01-:28 | DI | 24VDC Dry Contact | ACTIVE | MCC | MCC Room | C7S01- | - | PCM-60205-2 | | -

C7-S01-P28 | 28 | 29 | | PCM-60205-2_DI_2 | Pin 29 | C7S1:29/C7S01-:29 | DI | 24VDC Dry Contact | ACTIVE | MCC | MCC Room | C7S01- | - | PCM-60205-2 | | -

C7-S01-P29 | 29 | 30 | | PCM-60205-3_DI_1 | Pin 30 | C7S1:30/C7S01-:30 | DI | 24VDC Dry Contact | ACTIVE | MCC | MCC Room | C7S01- | - | PCM-60205-3 | | -

C7-S01-P30 | 30 | 31 | | PCM-60205-3_DI_2 | Pin 31 | C7S1:31/C7S01-:31 | DI | 24VDC Dry Contact | ACTIVE | MCC | MCC Room | C7S01- | - | PCM-60205-3 | | -

C7-S01-P31 | 31 | 32 | | PCM-60205-4_DI_1 | Pin 32 | C7S1:32/C7S01-:32 | DI | 24VDC Dry Contact | ACTIVE | MCC | MCC Room | C7S01- | - | PCM-60205-4 | | -

## C7 SLOT 02 — 1756 I/O (DI)

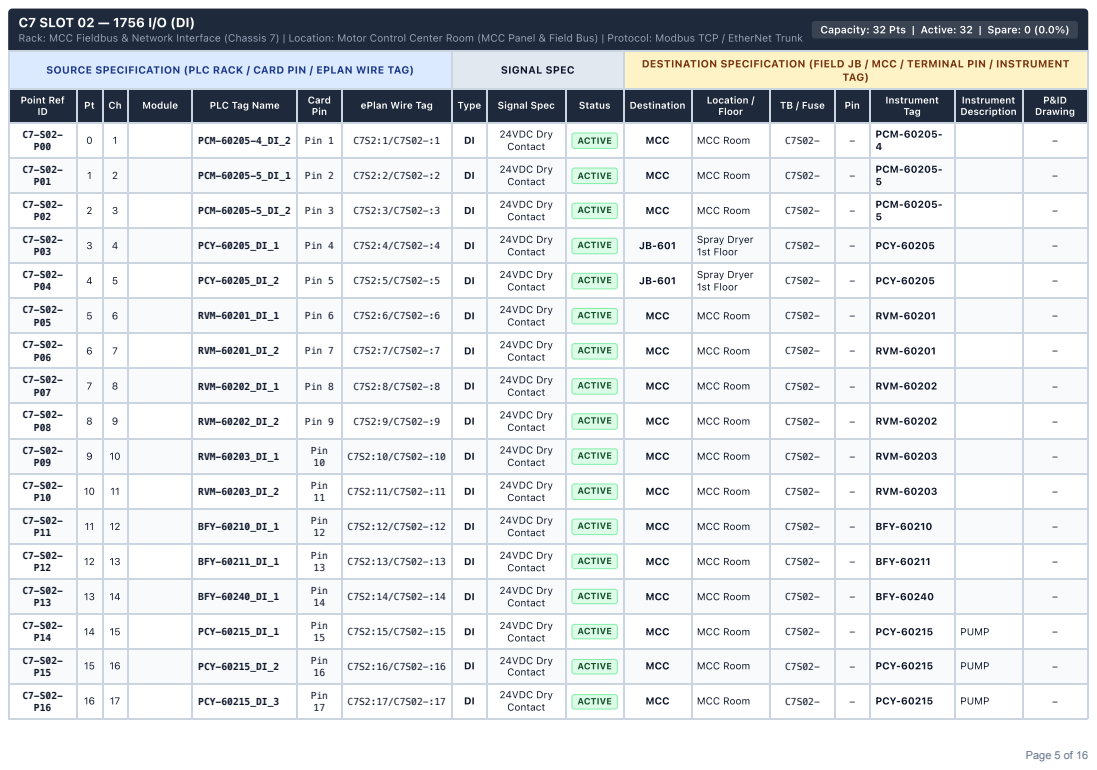
[picture p195: page 5]

Capacity: 32 Pts | Active: 32 | Spare: 0 (0.0%)

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

C7-S02-P00 | 0 | 1 | | PCM-60205-4_DI_2 | Pin 1 | C7S2:1/C7S02-:1 | DI | 24VDC Dry Contact | ACTIVE | MCC | MCC Room | C7S02- | - | PCM-60205-4 | | -

C7-S02-P01 | 1 | 2 | | PCM-60205-5_DI_1 | Pin 2 | C7S2:2/C7S02-:2 | DI | 24VDC Dry Contact | ACTIVE | MCC | MCC Room | C7S02- | - | PCM-60205-5 | | -

C7-S02-P02 | 2 | 3 | | PCM-60205-5_DI_2 | Pin 3 | C7S2:3/C7S02-:3 | DI | 24VDC Dry Contact | ACTIVE | MCC | MCC Room | C7S02- | - | PCM-60205-5 | | -

C7-S02-P03 | 3 | 4 | | PCY-60205_DI_1 | Pin 4 | C7S2:4/C7S02-:4 | DI | 24VDC Dry Contact | ACTIVE | JB-601 | Spray Dryer 1st Floor | C7S02- | - | PCY-60205 | | -

C7-S02-P04 | 4 | 5 | | PCY-60205_DI_2 | Pin 5 | C7S2:5/C7S02-:5 | DI | 24VDC Dry Contact | ACTIVE | JB-601 | Spray Dryer 1st Floor | C7S02- | - | PCY-60205 | | -

C7-S02-P05 | 5 | 6 | | RVM-60201_DI_1 | Pin 6 | C7S2:6/C7S02-:6 | DI | 24VDC Dry Contact | ACTIVE | MCC | MCC Room | C7S02- | - | RVM-60201 | | -

C7-S02-P06 | 6 | 7 | | RVM-60201_DI_2 | Pin 7 | C7S2:7/C7S02-:7 | DI | 24VDC Dry Contact | ACTIVE | MCC | MCC Room | C7S02- | - | RVM-60201 | | -

C7-S02-P07 | 7 | 8 | | RVM-60202_DI_1 | Pin 8 | C7S2:8/C7S02-:8 | DI | 24VDC Dry Contact | ACTIVE | MCC | MCC Room | C7S02- | - | RVM-60202 | | -

C7-S02-P08 | 8 | 9 | | RVM-60202_DI_2 | Pin 9 | C7S2:9/C7S02-:9 | DI | 24VDC Dry Contact | ACTIVE | MCC | MCC Room | C7S02- | - | RVM-60202 | | -

C7-S02-P09 | 9 | 10 | | RVM-60203_DI_1 | Pin 10 | C7S2:10/C7S02-:10 | DI | 24VDC Dry Contact | ACTIVE | MCC | MCC Room | C7S02- | - | RVM-60203 | | -

C7-S02-P10 | 10 | 11 | | RVM-60203_DI_2 | Pin 11 | C7S2:11/C7S02-:11 | DI | 24VDC Dry Contact | ACTIVE | MCC | MCC Room | C7S02- | - | RVM-60203 | | -

C7-S02-P11 | 11 | 12 | | BFY-60210_DI_1 | Pin 12 | C7S2:12/C7S02-:12 | DI | 24VDC Dry Contact | ACTIVE | MCC | MCC Room | C7S02- | - | BFY-60210 | | -

C7-S02-P12 | 12 | 13 | | BFY-60211_DI_1 | Pin 13 | C7S2:13/C7S02-:13 | DI | 24VDC Dry Contact | ACTIVE | MCC | MCC Room | C7S02- | - | BFY-60211 | | -

C7-S02-P13 | 13 | 14 | | BFY-60240_DI_1 | Pin 14 | C7S2:14/C7S02-:14 | DI | 24VDC Dry Contact | ACTIVE | MCC | MCC Room | C7S02- | - | BFY-60240 | | -

C7-S02-P14 | 14 | 15 | | PCY-60215_DI_1 | Pin 15 | C7S2:15/C7S02-:15 | DI | 24VDC Dry Contact | ACTIVE | MCC | MCC Room | C7S02- | - | PCY-60215 | PUMP | -

C7-S02-P15 | 15 | 16 | | PCY-60215_DI_2 | Pin 16 | C7S2:16/C7S02-:16 | DI | 24VDC Dry Contact | ACTIVE | MCC | MCC Room | C7S02- | - | PCY-60215 | PUMP | -

C7-S02-P16 | 16 | 17 | | PCY-60215_DI_3 | Pin 17 | C7S2:17/C7S02-:17 | DI | 24VDC Dry Contact | ACTIVE | MCC | MCC Room | C7S02- | - | PCY-60215 | PUMP | -

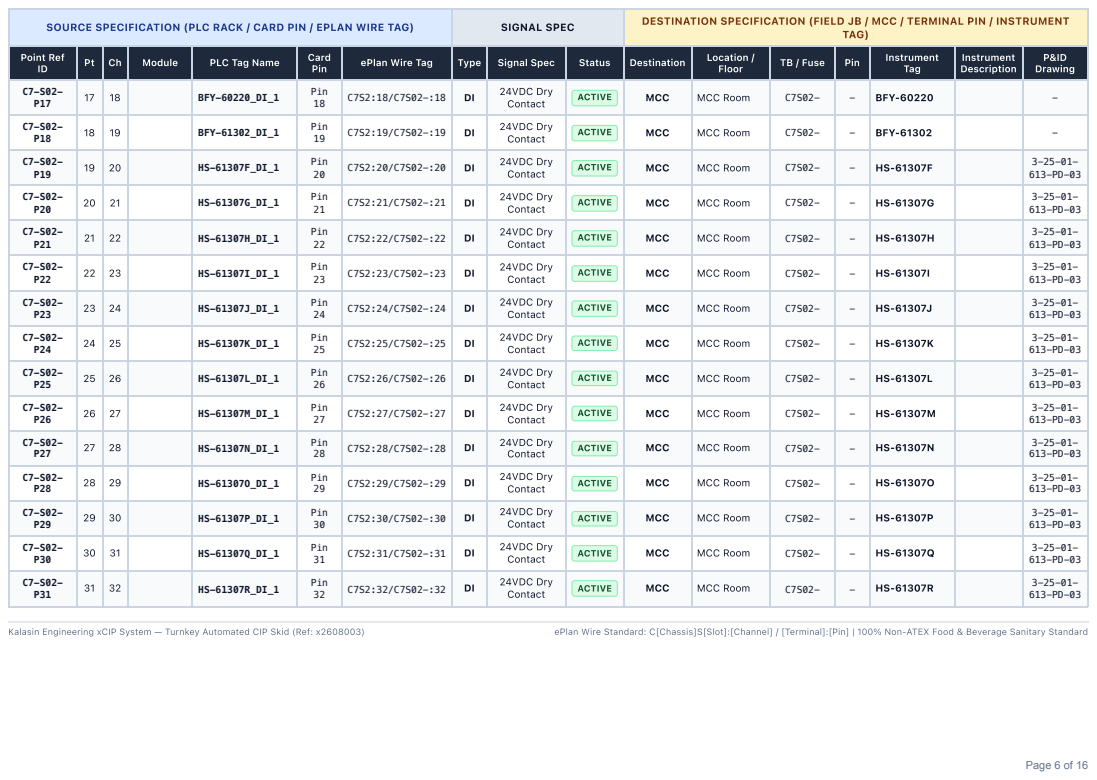
[picture p196: page 6]
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

C7-S02-P17 | 17 | 18 | | BFY-60220_DI_1 | Pin 18 | C7S2:18/C7S02-:18 | DI | 24VDC Dry Contact | ACTIVE | MCC | MCC Room | C7S02- | - | BFY-60220 | | -

C7-S02-P18 | 18 | 19 | | BFY-61302_DI_1 | Pin 19 | C7S2:19/C7S02-:19 | DI | 24VDC Dry Contact | ACTIVE | MCC | MCC Room | C7S02- | - | BFY-61302 | | -

C7-S02-P19 | 19 | 20 | | HS-61307F_DI_1 | Pin 20 | C7S2:20/C7S02-:20 | DI | 24VDC Dry Contact | ACTIVE | MCC | MCC Room | C7S02- | - | HS-61307F | | 3-25-01-613-PD-03

C7-S02-P20 | 20 | 21 | | HS-61307G_DI_1 | Pin 21 | C7S2:21/C7S02-:21 | DI | 24VDC Dry Contact | ACTIVE | MCC | MCC Room | C7S02- | - | HS-61307G | | 3-25-01-613-PD-03

C7-S02-P21 | 21 | 22 | | HS-61307H_DI_1 | Pin 22 | C7S2:22/C7S02-:22 | DI | 24VDC Dry Contact | ACTIVE | MCC | MCC Room | C7S02- | - | HS-61307H | | 3-25-01-613-PD-03

C7-S02-P22 | 22 | 23 | | HS-61307I_DI_1 | Pin 23 | C7S2:23/C7S02-:23 | DI | 24VDC Dry Contact | ACTIVE | MCC | MCC Room | C7S02- | - | HS-61307I | | 3-25-01-613-PD-03

C7-S02-P23 | 23 | 24 | | HS-61307J_DI_1 | Pin 24 | C7S2:24/C7S02-:24 | DI | 24VDC Dry Contact | ACTIVE | MCC | MCC Room | C7S02- | - | HS-61307J | | 3-25-01-613-PD-03

C7-S02-P24 | 24 | 25 | | HS-61307K_DI_1 | Pin 25 | C7S2:25/C7S02-:25 | DI | 24VDC Dry Contact | ACTIVE | MCC | MCC Room | C7S02- | - | HS-61307K | | 3-25-01-613-PD-03

C7-S02-P25 | 25 | 26 | | HS-61307L_DI_1 | Pin 26 | C7S2:26/C7S02-:26 | DI | 24VDC Dry Contact | ACTIVE | MCC | MCC Room | C7S02- | - | HS-61307L | | 3-25-01-613-PD-03

C7-S02-P26 | 26 | 27 | | HS-61307M_DI_1 | Pin 27 | C7S2:27/C7S02-:27 | DI | 24VDC Dry Contact | ACTIVE | MCC | MCC Room | C7S02- | - | HS-61307M | | 3-25-01-613-PD-03

C7-S02-P27 | 27 | 28 | | HS-61307N_DI_1 | Pin 28 | C7S2:28/C7S02-:28 | DI | 24VDC Dry Contact | ACTIVE | MCC | MCC Room | C7S02- | - | HS-61307N | | 3-25-01-613-PD-03

C7-S02-P28 | 28 | 29 | | HS-61307O_DI_1 | Pin 29 | C7S2:29/C7S02-:29 | DI | 24VDC Dry Contact | ACTIVE | MCC | MCC Room | C7S02- | - | HS-61307O | | 3-25-01-613-PD-03

C7-S02-P29 | 29 | 30 | | HS-61307P_DI_1 | Pin 30 | C7S2:30/C7S02-:30 | DI | 24VDC Dry Contact | ACTIVE | MCC | MCC Room | C7S02- | - | HS-61307P | | 3-25-01-613-PD-03

C7-S02-P30 | 30 | 31 | | HS-61307Q_DI_1 | Pin 31 | C7S2:31/C7S02-:31 | DI | 24VDC Dry Contact | ACTIVE | MCC | MCC Room | C7S02- | - | HS-61307Q | | 3-25-01-613-PD-03

C7-S02-P31 | 31 | 32 | | HS-61307R_DI_1 | Pin 32 | C7S2:32/C7S02-:32 | DI | 24VDC Dry Contact | ACTIVE | MCC | MCC Room | C7S02- | - | HS-61307R | | 3-25-01-613-PD-03

## C7 SLOT 03 — 1756 I/O (DI)

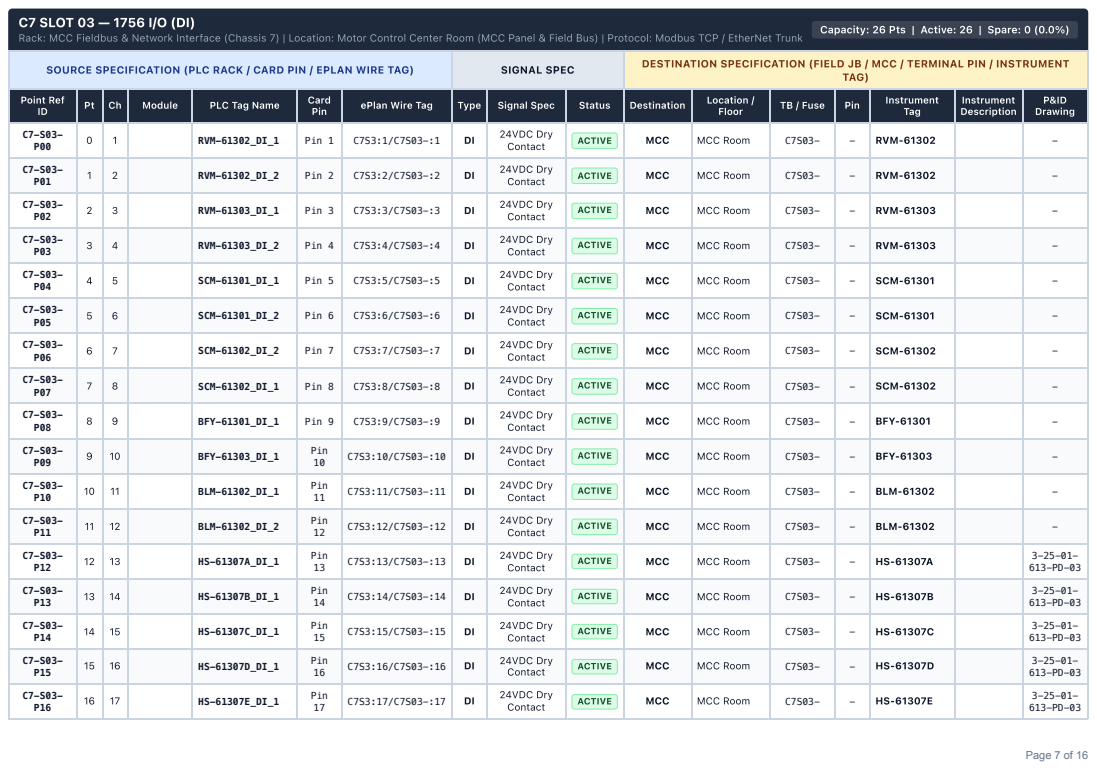
[picture p197: page 7]

Capacity: 26 Pts | Active: 26 | Spare: 0 (0.0%)

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

C7-S03-P00 | 0 | 1 | | RVM-61302_DI_1 | Pin 1 | C7S3:1/C7S03-:1 | DI | 24VDC Dry Contact | ACTIVE | MCC | MCC Room | C7S03- | - | RVM-61302 | | -

C7-S03-P01 | 1 | 2 | | RVM-61302_DI_2 | Pin 2 | C7S3:2/C7S03-:2 | DI | 24VDC Dry Contact | ACTIVE | MCC | MCC Room | C7S03- | - | RVM-61302 | | -

C7-S03-P02 | 2 | 3 | | RVM-61303_DI_1 | Pin 3 | C7S3:3/C7S03-:3 | DI | 24VDC Dry Contact | ACTIVE | MCC | MCC Room | C7S03- | - | RVM-61303 | | -

C7-S03-P03 | 3 | 4 | | RVM-61303_DI_2 | Pin 4 | C7S3:4/C7S03-:4 | DI | 24VDC Dry Contact | ACTIVE | MCC | MCC Room | C7S03- | - | RVM-61303 | | -

C7-S03-P04 | 4 | 5 | | SCM-61301_DI_1 | Pin 5 | C7S3:5/C7S03-:5 | DI | 24VDC Dry Contact | ACTIVE | MCC | MCC Room | C7S03- | - | SCM-61301 | | -

C7-S03-P05 | 5 | 6 | | SCM-61301_DI_2 | Pin 6 | C7S3:6/C7S03-:6 | DI | 24VDC Dry Contact | ACTIVE | MCC | MCC Room | C7S03- | - | SCM-61301 | | -

C7-S03-P06 | 6 | 7 | | SCM-61302_DI_2 | Pin 7 | C7S3:7/C7S03-:7 | DI | 24VDC Dry Contact | ACTIVE | MCC | MCC Room | C7S03- | - | SCM-61302 | | -

C7-S03-P07 | 7 | 8 | | SCM-61302_DI_1 | Pin 8 | C7S3:8/C7S03-:8 | DI | 24VDC Dry Contact | ACTIVE | MCC | MCC Room | C7S03- | - | SCM-61302 | | -

C7-S03-P08 | 8 | 9 | | BFY-61301_DI_1 | Pin 9 | C7S3:9/C7S03-:9 | DI | 24VDC Dry Contact | ACTIVE | MCC | MCC Room | C7S03- | - | BFY-61301 | | -

C7-S03-P09 | 9 | 10 | | BFY-61303_DI_1 | Pin 10 | C7S3:10/C7S03-:10 | DI | 24VDC Dry Contact | ACTIVE | MCC | MCC Room | C7S03- | - | BFY-61303 | | -

C7-S03-P10 | 10 | 11 | | BLM-61302_DI_1 | Pin 11 | C7S3:11/C7S03-:11 | DI | 24VDC Dry Contact | ACTIVE | MCC | MCC Room | C7S03- | - | BLM-61302 | | -

C7-S03-P11 | 11 | 12 | | BLM-61302_DI_2 | Pin 12 | C7S3:12/C7S03-:12 | DI | 24VDC Dry Contact | ACTIVE | MCC | MCC Room | C7S03- | - | BLM-61302 | | -

C7-S03-P12 | 12 | 13 | | HS-61307A_DI_1 | Pin 13 | C7S3:13/C7S03-:13 | DI | 24VDC Dry Contact | ACTIVE | MCC | MCC Room | C7S03- | - | HS-61307A | | 3-25-01-613-PD-03

C7-S03-P13 | 13 | 14 | | HS-61307B_DI_1 | Pin 14 | C7S3:14/C7S03-:14 | DI | 24VDC Dry Contact | ACTIVE | MCC | MCC Room | C7S03- | - | HS-61307B | | 3-25-01-613-PD-03

C7-S03-P14 | 14 | 15 | | HS-61307C_DI_1 | Pin 15 | C7S3:15/C7S03-:15 | DI | 24VDC Dry Contact | ACTIVE | MCC | MCC Room | C7S03- | - | HS-61307C | | 3-25-01-613-PD-03

C7-S03-P15 | 15 | 16 | | HS-61307D_DI_1 | Pin 16 | C7S3:16/C7S03-:16 | DI | 24VDC Dry Contact | ACTIVE | MCC | MCC Room | C7S03- | - | HS-61307D | | 3-25-01-613-PD-03

C7-S03-P16 | 16 | 17 | | HS-61307E_DI_1 | Pin 17 | C7S3:17/C7S03-:17 | DI | 24VDC Dry Contact | ACTIVE | MCC | MCC Room | C7S03- | - | HS-61307E | | 3-25-01-613-PD-03

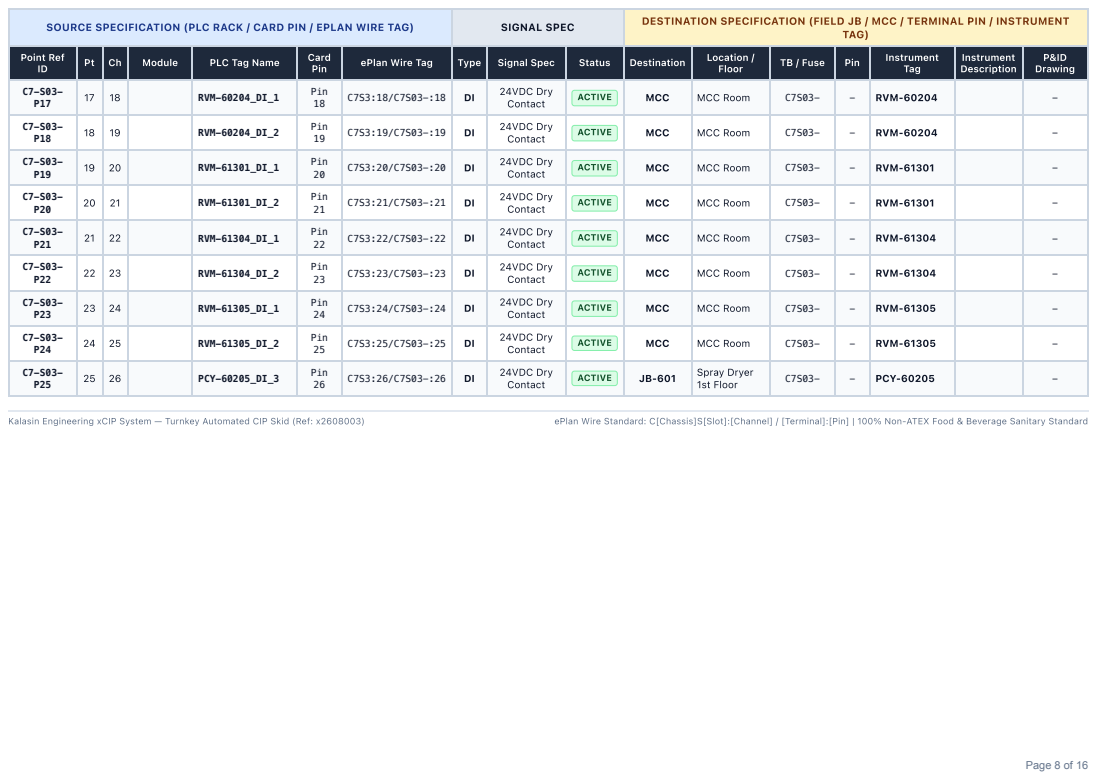
[picture p198: page 8]
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

C7-S03-P17 | 17 | 18 | | RVM-60204_DI_1 | Pin 18 | C7S3:18/C7S03-:18 | DI | 24VDC Dry Contact | ACTIVE | MCC | MCC Room | C7S03- | - | RVM-60204 | | -

C7-S03-P18 | 18 | 19 | | RVM-60204_DI_2 | Pin 19 | C7S3:19/C7S03-:19 | DI | 24VDC Dry Contact | ACTIVE | MCC | MCC Room | C7S03- | - | RVM-60204 | | -

C7-S03-P19 | 19 | 20 | | RVM-61301_DI_1 | Pin 20 | C7S3:20/C7S03-:20 | DI | 24VDC Dry Contact | ACTIVE | MCC | MCC Room | C7S03- | - | RVM-61301 | | -

C7-S03-P20 | 20 | 21 | | RVM-61301_DI_2 | Pin 21 | C7S3:21/C7S03-:21 | DI | 24VDC Dry Contact | ACTIVE | MCC | MCC Room | C7S03- | - | RVM-61301 | | -

C7-S03-P21 | 21 | 22 | | RVM-61304_DI_1 | Pin 22 | C7S3:22/C7S03-:22 | DI | 24VDC Dry Contact | ACTIVE | MCC | MCC Room | C7S03- | - | RVM-61304 | | -

C7-S03-P22 | 22 | 23 | | RVM-61304_DI_2 | Pin 23 | C7S3:23/C7S03-:23 | DI | 24VDC Dry Contact | ACTIVE | MCC | MCC Room | C7S03- | - | RVM-61304 | | -

C7-S03-P23 | 23 | 24 | | RVM-61305_DI_1 | Pin 24 | C7S3:24/C7S03-:24 | DI | 24VDC Dry Contact | ACTIVE | MCC | MCC Room | C7S03- | - | RVM-61305 | | -

C7-S03-P24 | 24 | 25 | | RVM-61305_DI_2 | Pin 25 | C7S3:25/C7S03-:25 | DI | 24VDC Dry Contact | ACTIVE | MCC | MCC Room | C7S03- | - | RVM-61305 | | -

C7-S03-P25 | 25 | 26 | | PCY-60205_DI_3 | Pin 26 | C7S3:26/C7S03-:26 | DI | 24VDC Dry Contact | ACTIVE | JB-601 | Spray Dryer 1st Floor | C7S03- | - | PCY-60205 | | -

## C7 SLOT 04 — 1756 I/O (DI)

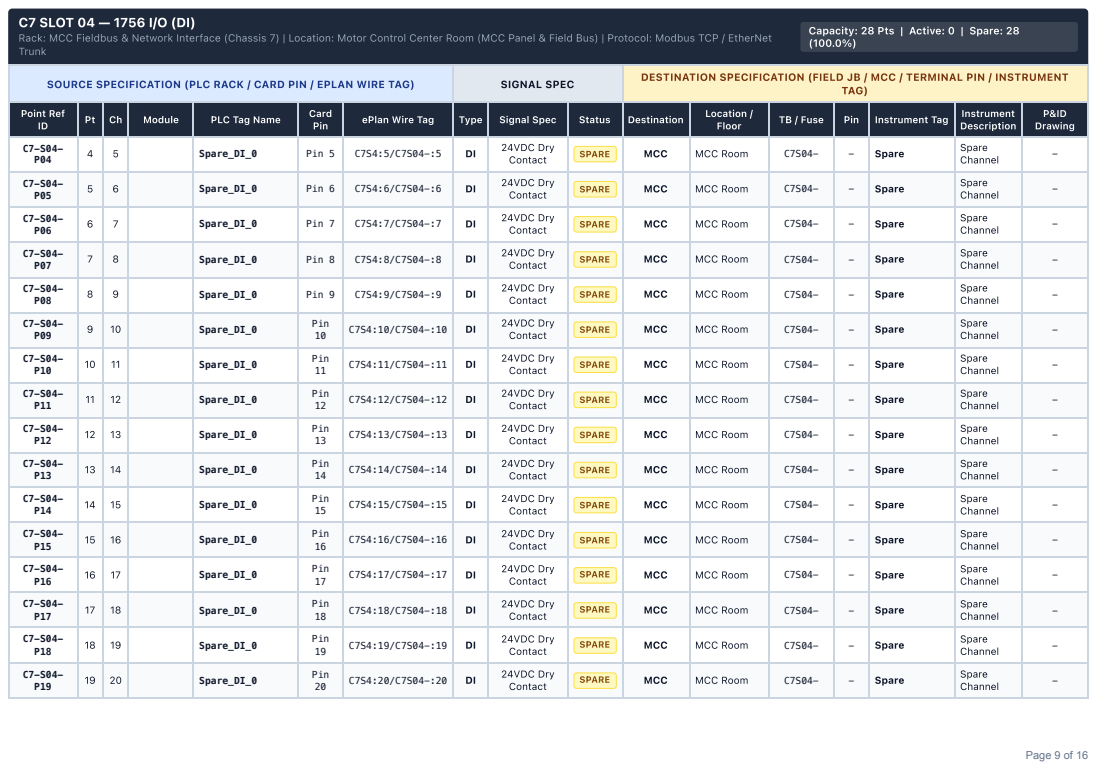
[picture p199: page 9]

Capacity: 28 Pts | Active: 0 | Spare: 28

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

C7-S04-P04 | 4 | 5 | | Spare_DI_0 | Pin 5 | C7S4:5/C7S04-:5 | DI | 24VDC Dry Contact | SPARE | MCC | MCC Room | C7S04- | - | Spare | Spare Channel | -

C7-S04-P05 | 5 | 6 | | Spare_DI_0 | Pin 6 | C7S4:6/C7S04-:6 | DI | 24VDC Dry Contact | SPARE | MCC | MCC Room | C7S04- | - | Spare | Spare Channel | -

C7-S04-P06 | 6 | 7 | | Spare_DI_0 | Pin 7 | C7S4:7/C7S04-:7 | DI | 24VDC Dry Contact | SPARE | MCC | MCC Room | C7S04- | - | Spare | Spare Channel | -

C7-S04-P07 | 7 | 8 | | Spare_DI_0 | Pin 8 | C7S4:8/C7S04-:8 | DI | 24VDC Dry Contact | SPARE | MCC | MCC Room | C7S04- | - | Spare | Spare Channel | -

C7-S04-P08 | 8 | 9 | | Spare_DI_0 | Pin 9 | C7S4:9/C7S04-:9 | DI | 24VDC Dry Contact | SPARE | MCC | MCC Room | C7S04- | - | Spare | Spare Channel | -

C7-S04-P09 | 9 | 10 | | Spare_DI_0 | Pin 10 | C7S4:10/C7S04-:10 | DI | 24VDC Dry Contact | SPARE | MCC | MCC Room | C7S04- | - | Spare | Spare Channel | -

C7-S04-P10 | 10 | 11 | | Spare_DI_0 | Pin 11 | C7S4:11/C7S04-:11 | DI | 24VDC Dry Contact | SPARE | MCC | MCC Room | C7S04- | - | Spare | Spare Channel | -

C7-S04-P11 | 11 | 12 | | Spare_DI_0 | Pin 12 | C7S4:12/C7S04-:12 | DI | 24VDC Dry Contact | SPARE | MCC | MCC Room | C7S04- | - | Spare | Spare Channel | -

C7-S04-P12 | 12 | 13 | | Spare_DI_0 | Pin 13 | C7S4:13/C7S04-:13 | DI | 24VDC Dry Contact | SPARE | MCC | MCC Room | C7S04- | - | Spare | Spare Channel | -

C7-S04-P13 | 13 | 14 | | Spare_DI_0 | Pin 14 | C7S4:14/C7S04-:14 | DI | 24VDC Dry Contact | SPARE | MCC | MCC Room | C7S04- | - | Spare | Spare Channel | -

C7-S04-P14 | 14 | 15 | | Spare_DI_0 | Pin 15 | C7S4:15/C7S04-:15 | DI | 24VDC Dry Contact | SPARE | MCC | MCC Room | C7S04- | - | Spare | Spare Channel | -

C7-S04-P15 | 15 | 16 | | Spare_DI_0 | Pin 16 | C7S4:16/C7S04-:16 | DI | 24VDC Dry Contact | SPARE | MCC | MCC Room | C7S04- | - | Spare | Spare Channel | -

C7-S04-P16 | 16 | 17 | | Spare_DI_0 | Pin 17 | C7S4:17/C7S04-:17 | DI | 24VDC Dry Contact | SPARE | MCC | MCC Room | C7S04- | - | Spare | Spare Channel | -

C7-S04-P17 | 17 | 18 | | Spare_DI_0 | Pin 18 | C7S4:18/C7S04-:18 | DI | 24VDC Dry Contact | SPARE | MCC | MCC Room | C7S04- | - | Spare | Spare Channel | -

C7-S04-P18 | 18 | 19 | | Spare_DI_0 | Pin 19 | C7S4:19/C7S04-:19 | DI | 24VDC Dry Contact | SPARE | MCC | MCC Room | C7S04- | - | Spare | Spare Channel | -

C7-S04-P19 | 19 | 20 | | Spare_DI_0 | Pin 20 | C7S4:20/C7S04-:20 | DI | 24VDC Dry Contact | SPARE | MCC | MCC Room | C7S04- | - | Spare | Spare Channel | -

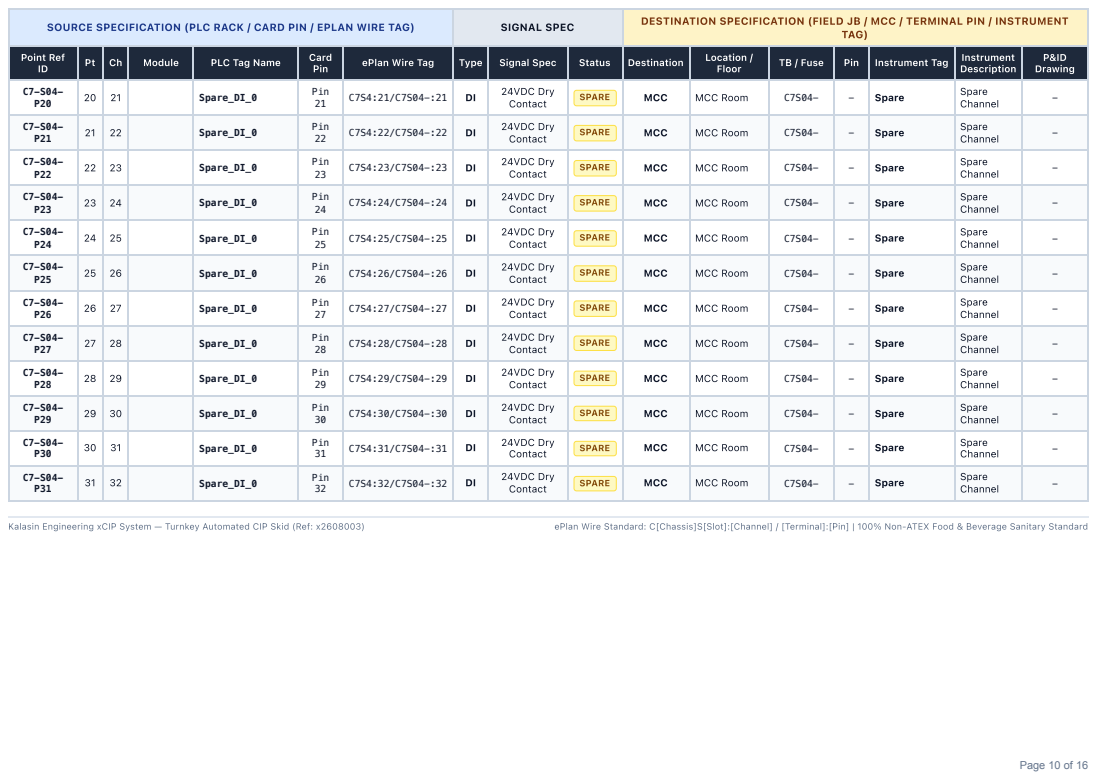
[picture p200: page 10]
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

C7-S04-P20 | 20 | 21 | | Spare_DI_0 | Pin 21 | C7S4:21/C7S04-:21 | DI | 24VDC Dry Contact | SPARE | MCC | MCC Room | C7S04- | - | Spare | Spare Channel | -

C7-S04-P21 | 21 | 22 | | Spare_DI_0 | Pin 22 | C7S4:22/C7S04-:22 | DI | 24VDC Dry Contact | SPARE | MCC | MCC Room | C7S04- | - | Spare | Spare Channel | -

C7-S04-P22 | 22 | 23 | | Spare_DI_0 | Pin 23 | C7S4:23/C7S04-:23 | DI | 24VDC Dry Contact | SPARE | MCC | MCC Room | C7S04- | - | Spare | Spare Channel | -

C7-S04-P23 | 23 | 24 | | Spare_DI_0 | Pin 24 | C7S4:24/C7S04-:24 | DI | 24VDC Dry Contact | SPARE | MCC | MCC Room | C7S04- | - | Spare | Spare Channel | -

C7-S04-P24 | 24 | 25 | | Spare_DI_0 | Pin 25 | C7S4:25/C7S04-:25 | DI | 24VDC Dry Contact | SPARE | MCC | MCC Room | C7S04- | - | Spare | Spare Channel | -

C7-S04-P25 | 25 | 26 | | Spare_DI_0 | Pin 26 | C7S4:26/C7S04-:26 | DI | 24VDC Dry Contact | SPARE | MCC | MCC Room | C7S04- | - | Spare | Spare Channel | -

C7-S04-P26 | 26 | 27 | | Spare_DI_0 | Pin 27 | C7S4:27/C7S04-:27 | DI | 24VDC Dry Contact | SPARE | MCC | MCC Room | C7S04- | - | Spare | Spare Channel | -

C7-S04-P27 | 27 | 28 | | Spare_DI_0 | Pin 28 | C7S4:28/C7S04-:28 | DI | 24VDC Dry Contact | SPARE | MCC | MCC Room | C7S04- | - | Spare | Spare Channel | -

C7-S04-P28 | 28 | 29 | | Spare_DI_0 | Pin 29 | C7S4:29/C7S04-:29 | DI | 24VDC Dry Contact | SPARE | MCC | MCC Room | C7S04- | - | Spare | Spare Channel | -

C7-S04-P29 | 29 | 30 | | Spare_DI_0 | Pin 30 | C7S4:30/C7S04-:30 | DI | 24VDC Dry Contact | SPARE | MCC | MCC Room | C7S04- | - | Spare | Spare Channel | -

C7-S04-P30 | 30 | 31 | | Spare_DI_0 | Pin 31 | C7S4:31/C7S04-:31 | DI | 24VDC Dry Contact | SPARE | MCC | MCC Room | C7S04- | - | Spare | Spare Channel | -

C7-S04-P31 | 31 | 32 | | Spare_DI_0 | Pin 32 | C7S4:32/C7S04-:32 | DI | 24VDC Dry Contact | SPARE | MCC | MCC Room | C7S04- | - | Spare | Spare Channel | -
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
