x92120/x260911-002-KalasinEngineering/03_IO_Lists_and_Schedules/IO_List-Bak/Chassis_and_Slot_IO_Source_Destination_Report.pdf

# KALASIN ENGINEERING — XCIP AUTOMATION SYSTEM

## MASTER CHASSIS & SLOT I/O SOURCE-TO-DESTINATION SCHEDULE

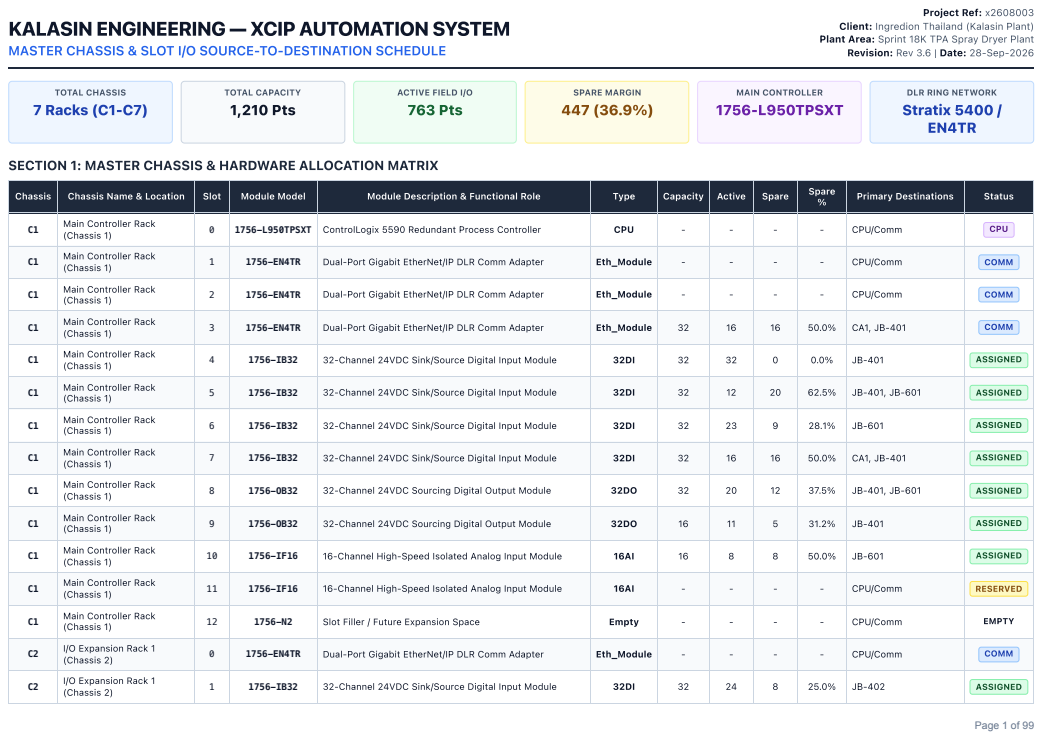
[picture p201: page 1]
Project Ref: x2608003; TOTAL CHASSIS 7 Racks (C1-C7); TOTAL CAPACITY 1,210 Pts; ACTIVE FIELD I/O 763 Pts; SPARE MARGIN 447 (36.9%); MAIN CONTROLLER 1756-L950TPSXT; DLR RING NETWORK Stratix 5400 / EN4TR

Client: Ingredion Thailand (Kalasin Plant)
Plant Area: Sprint 18K TPA Spray Dryer Plant
Revision: Rev 3.6 | Date: 28-Sep-2026

SECTION 1: MASTER CHASSIS & HARDWARE ALLOCATION MATRIX

Chassis | Chassis Name & Location | Slot | Module Model | Module Description & Functional Role | Type | Capacity | Active | Spare | Spare % | Primary Destinations | Status

C1 | Main Controller Rack (Chassis 1) | 0 | 1756-L950TPSXT | ControlLogix 5590 Redundant Process Controller | CPU | - | - | - | - | CPU/Comm | CPU

C1 | Main Controller Rack (Chassis 1) | 1 | 1756-EN4TR | Dual-Port Gigabit EtherNet/IP DLR Comm Adapter | Eth_Module | - | - | - | - | CPU/Comm | COMM

C1 | Main Controller Rack (Chassis 1) | 2 | 1756-EN4TR | Dual-Port Gigabit EtherNet/IP DLR Comm Adapter | Eth_Module | - | - | - | - | CPU/Comm | COMM

C1 | Main Controller Rack (Chassis 1) | 3 | 1756-EN4TR | Dual-Port Gigabit EtherNet/IP DLR Comm Adapter | Eth_Module | 32 | 16 | 16 | 50.0% | CA1, JB-401 | COMM

C1 | Main Controller Rack (Chassis 1) | 4 | 1756-IB32 | 32-Channel 24VDC Sink/Source Digital Input Module | 32DI | 32 | 32 | 0 | 0.0% | JB-401 | ASSIGNED

C1 | Main Controller Rack (Chassis 1) | 5 | 1756-IB32 | 32-Channel 24VDC Sink/Source Digital Input Module | 32DI | 32 | 12 | 20 | 62.5% | JB-401, JB-601 | ASSIGNED

C1 | Main Controller Rack (Chassis 1) | 6 | 1756-IB32 | 32-Channel 24VDC Sink/Source Digital Input Module | 32DI | 32 | 23 | 9 | 28.1% | JB-601 | ASSIGNED

C1 | Main Controller Rack (Chassis 1) | 7 | 1756-IB32 | 32-Channel 24VDC Sink/Source Digital Input Module | 32DI | 32 | 16 | 16 | 50.0% | CA1, JB-401 | ASSIGNED

C1 | Main Controller Rack (Chassis 1) | 8 | 1756-OB32 | 32-Channel 24VDC Sourcing Digital Output Module | 32DO | 32 | 20 | 12 | 37.5% | JB-401, JB-601 | ASSIGNED

C1 | Main Controller Rack (Chassis 1) | 9 | 1756-OB32 | 32-Channel 24VDC Sourcing Digital Output Module | 32DO | 16 | 11 | 5 | 31.2% | JB-401 | ASSIGNED

C1 | Main Controller Rack (Chassis 1) | 10 | 1756-IF16 | 16-Channel High-Speed Isolated Analog Input Module | 16AI | 16 | 8 | 8 | 50.0% | JB-601 | ASSIGNED

C1 | Main Controller Rack (Chassis 1) | 11 | 1756-IF16 | 16-Channel High-Speed Isolated Analog Input Module | 16AI | - | - | - | - | CPU/Comm | RESERVED

C1 | Main Controller Rack (Chassis 1) | 12 | 1756-N2 | Slot Filler / Future Expansion Space | Empty | - | - | - | - | CPU/Comm | EMPTY

C2 | I/O Expansion Rack 1 (Chassis 2) | 0 | 1756-EN4TR | Dual-Port Gigabit EtherNet/IP DLR Comm Adapter | Eth_Module | - | - | - | - | CPU/Comm | COMM

C2 | I/O Expansion Rack 1 (Chassis 2) | 1 | 1756-IB32 | 32-Channel 24VDC Sink/Source Digital Input Module | 32DI | 32 | 24 | 8 | 25.0% | JB-402 | ASSIGNED

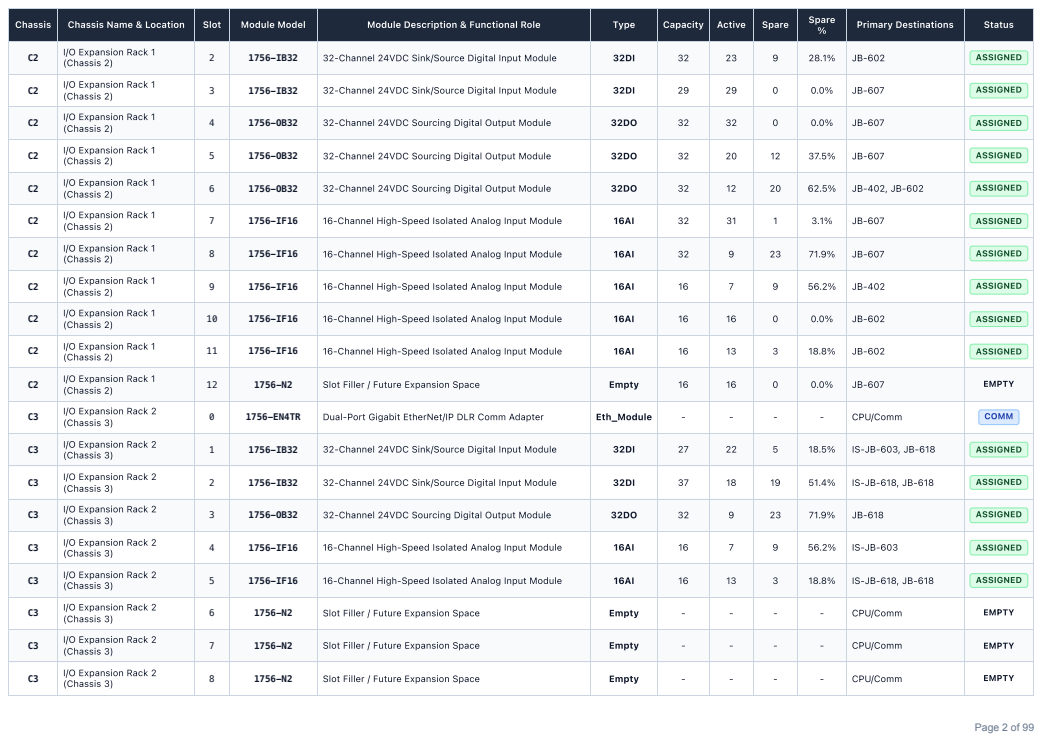
[picture p202: page 2]
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

C2 | I/O Expansion Rack 1 (Chassis 2) | 2 | 1756-IB32 | 32-Channel 24VDC Sink/Source Digital Input Module | 32DI | 32 | 23 | 9 | 28.1% | JB-602 | ASSIGNED

C2 | I/O Expansion Rack 1 (Chassis 2) | 3 | 1756-IB32 | 32-Channel 24VDC Sink/Source Digital Input Module | 32DI | 29 | 29 | 0 | 0.0% | JB-607 | ASSIGNED

C2 | I/O Expansion Rack 1 (Chassis 2) | 4 | 1756-OB32 | 32-Channel 24VDC Sourcing Digital Output Module | 32DO | 32 | 32 | 0 | 0.0% | JB-607 | ASSIGNED

C2 | I/O Expansion Rack 1 (Chassis 2) | 5 | 1756-OB32 | 32-Channel 24VDC Sourcing Digital Output Module | 32DO | 32 | 20 | 12 | 37.5% | JB-607 | ASSIGNED

C2 | I/O Expansion Rack 1 (Chassis 2) | 6 | 1756-OB32 | 32-Channel 24VDC Sourcing Digital Output Module | 32DO | 32 | 12 | 20 | 62.5% | JB-402, JB-602 | ASSIGNED

C2 | I/O Expansion Rack 1 (Chassis 2) | 7 | 1756-IF16 | 16-Channel High-Speed Isolated Analog Input Module | 16AI | 32 | 31 | 1 | 3.1% | JB-607 | ASSIGNED

C2 | I/O Expansion Rack 1 (Chassis 2) | 8 | 1756-IF16 | 16-Channel High-Speed Isolated Analog Input Module | 16AI | 32 | 9 | 23 | 71.9% | JB-607 | ASSIGNED

C2 | I/O Expansion Rack 1 (Chassis 2) | 9 | 1756-IF16 | 16-Channel High-Speed Isolated Analog Input Module | 16AI | 16 | 7 | 9 | 56.2% | JB-402 | ASSIGNED

C2 | I/O Expansion Rack 1 (Chassis 2) | 10 | 1756-IF16 | 16-Channel High-Speed Isolated Analog Input Module | 16AI | 16 | 16 | 0 | 0.0% | JB-602 | ASSIGNED

C2 | I/O Expansion Rack 1 (Chassis 2) | 11 | 1756-IF16 | 16-Channel High-Speed Isolated Analog Input Module | 16AI | 16 | 13 | 3 | 18.8% | JB-602 | ASSIGNED

C2 | I/O Expansion Rack 1 (Chassis 2) | 12 | 1756-N2 | Slot Filler / Future Expansion Space | Empty | 16 | 16 | 0 | 0.0% | JB-607 | EMPTY

C3 | I/O Expansion Rack 2 (Chassis 3) | 0 | 1756-EN4TR | Dual-Port Gigabit EtherNet/IP DLR Comm Adapter | Eth_Module | - | - | - | - | CPU/Comm | COMM

C3 | I/O Expansion Rack 2 (Chassis 3) | 1 | 1756-IB32 | 32-Channel 24VDC Sink/Source Digital Input Module | 32DI | 27 | 22 | 5 | 18.5% | IS-JB-603, JB-618 | ASSIGNED
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
